sakshampan733-cloud/a-study-in-teak/assets/catalog/9116.jpg

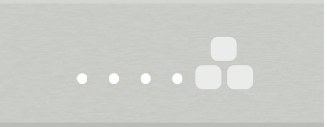
assets/catalog/9116.jpg
