sakshampan733-cloud/a-study-in-teak/assets/catalog/9126.jpg

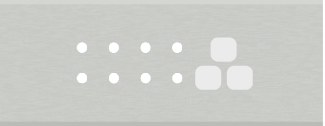
assets/catalog/9126.jpg
