sakshampan733-cloud/a-study-in-teak/assets/catalog/9148.jpg

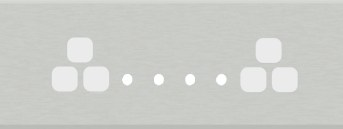
assets/catalog/9148.jpg
