sakshampan733-cloud/a-study-in-teak/assets/catalog/9156.jpg

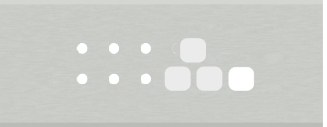
assets/catalog/9156.jpg
