sakshampan733-cloud/a-study-in-teak/assets/catalog/9188.jpg

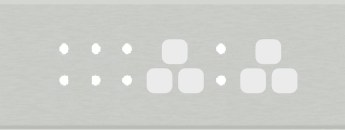
assets/catalog/9188.jpg
