sakshampan733-cloud/a-study-in-teak/assets/catalog/9198.jpg

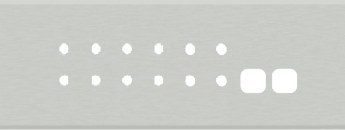
assets/catalog/9198.jpg
