sakshampan733-cloud/a-study-in-teak/assets/catalog/9212.jpg

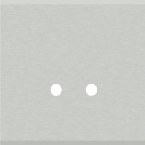
assets/catalog/9212.jpg
