sakshampan733-cloud/a-study-in-teak/assets/catalog/9323.jpg

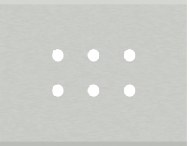
assets/catalog/9323.jpg
