sakshampan733-cloud/a-study-in-teak/assets/catalog/9424.jpg

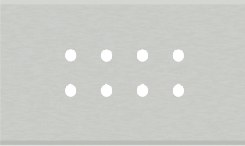
assets/catalog/9424.jpg
