sakshampan733-cloud/a-study-in-teak/assets/catalog/9818.jpg

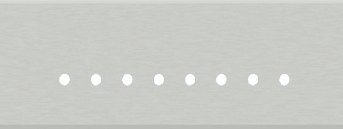
assets/catalog/9818.jpg
