sakshampan733-cloud/a-study-in-teak/assets/refs/moulding-ref-2-brownstone-head-detail.jpg

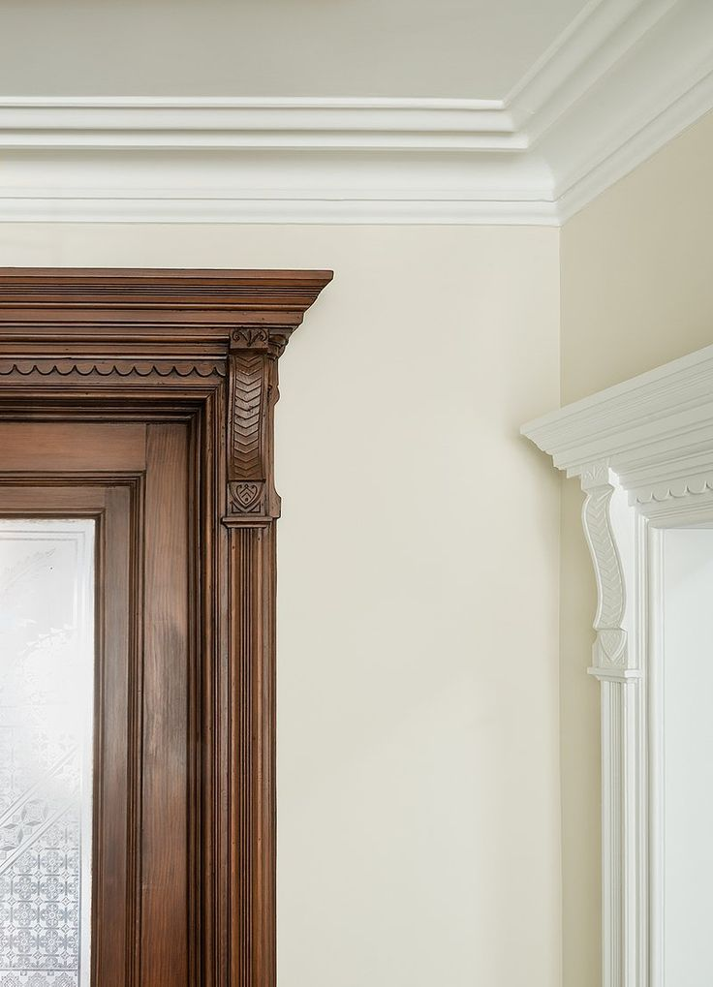
assets/refs/moulding-ref-2-brownstone-head-detail.jpg
