sakshampan733-cloud/a-study-in-teak/assets/refs/partition-ref-2-backlit-glass-grid-panels.jpg

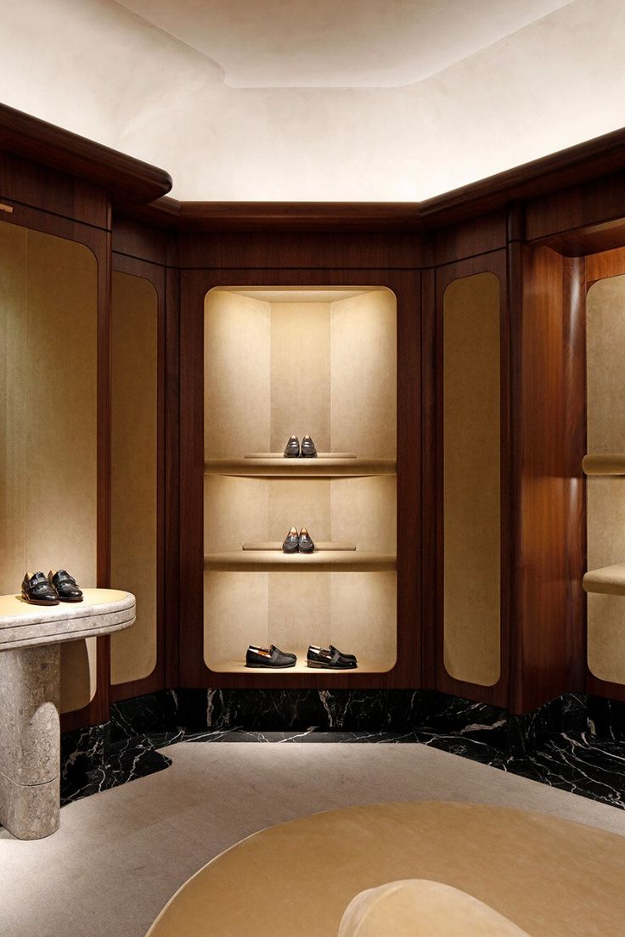
assets/refs/partition-ref-2-backlit-glass-grid-panels.jpg
