sakshampan733-cloud/a-study-in-teak/assets/refs/rightwall-iter-1-rail-2ft3.jpg

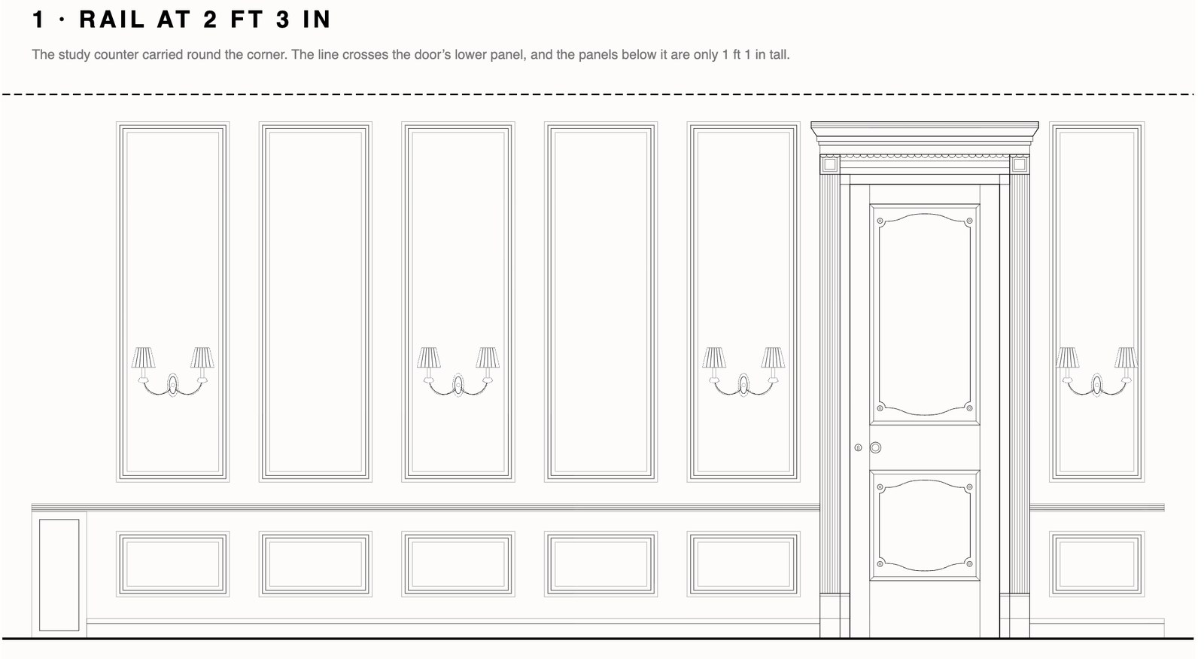
assets/refs/rightwall-iter-1-rail-2ft3.jpg
