sakshampan733-cloud/a-study-in-teak/assets/refs/veneer-9292-cream-burl.jpg

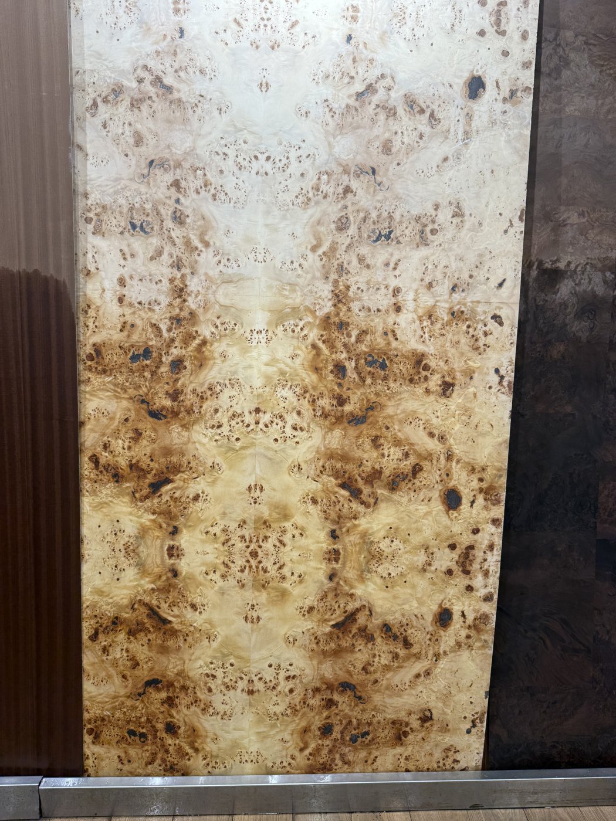
assets/refs/veneer-9292-cream-burl.jpg
