sakshampan733-cloud/a-study-in-teak/assets/refs/veneer-dark-diva-crown-OHBF-607-color-target.jpg

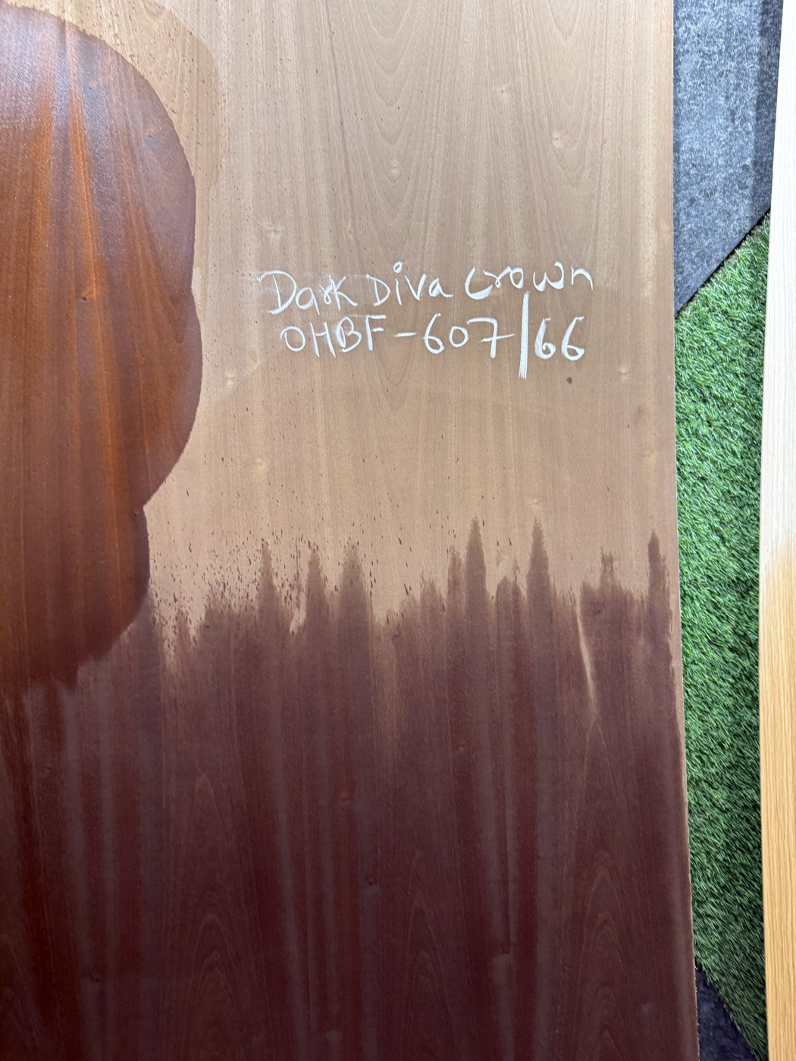
assets/refs/veneer-dark-diva-crown-OHBF-607-color-target.jpg
