sakshampan733-cloud/a-study-in-teak/assets/refs/veneer-ref-1-curved-walnut-gloss.jpg

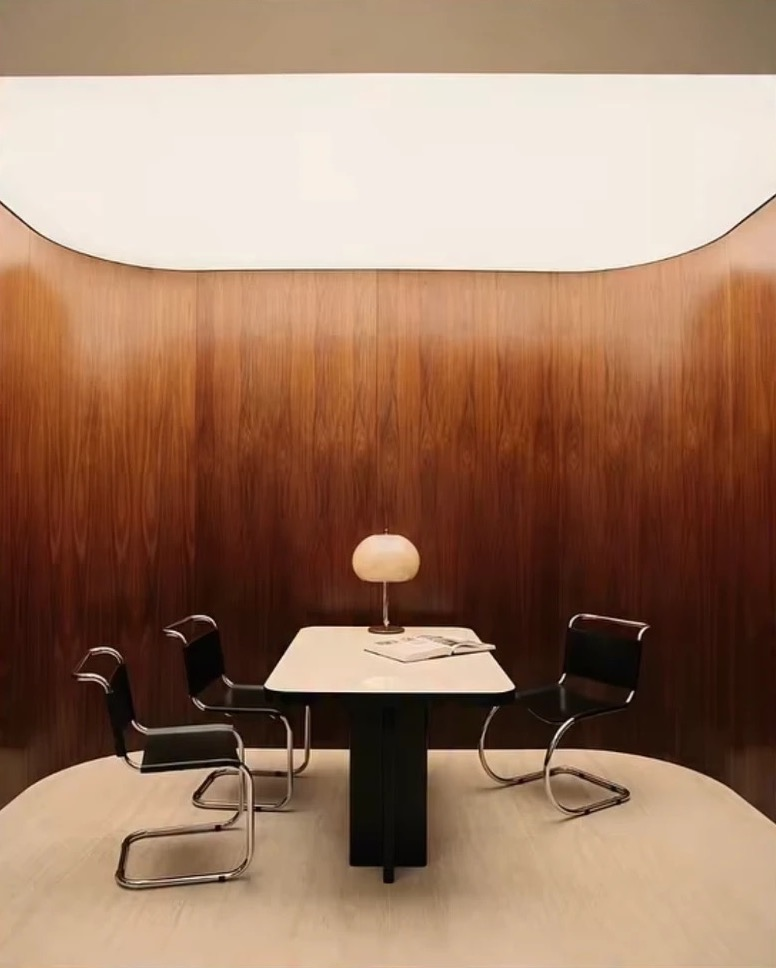
assets/refs/veneer-ref-1-curved-walnut-gloss.jpg
