sakshampan733-cloud/a-study-in-teak/assets/refs/wall-ref-1-library-pilasters.jpg

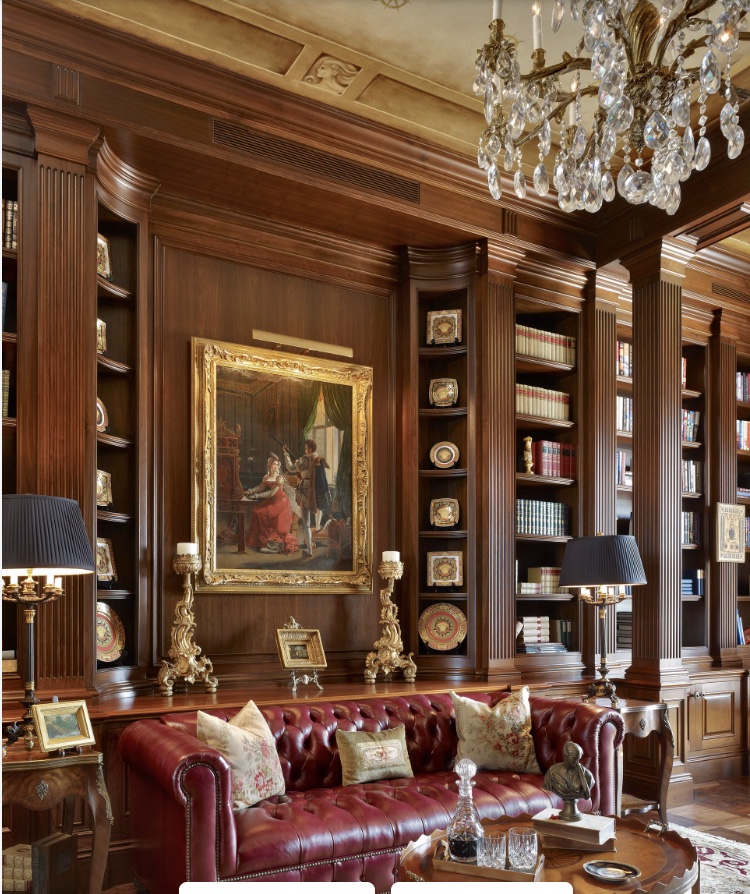
assets/refs/wall-ref-1-library-pilasters.jpg
