sakshampan733-cloud/a-study-in-teak/assets/refs/wall-ref-2-cornice-closeup.jpg

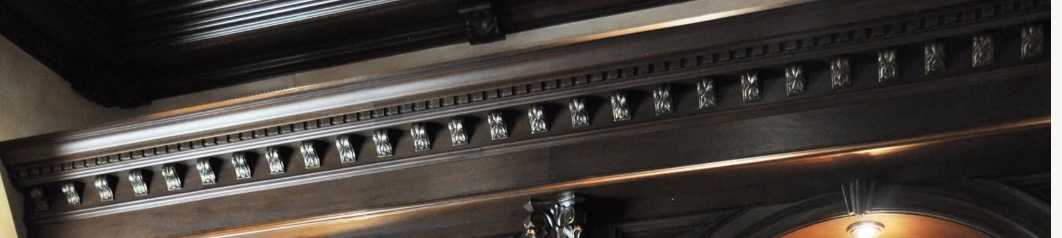
assets/refs/wall-ref-2-cornice-closeup.jpg
