sakshampan733-cloud/a-study-in-teak/assets/refs/wall-ref-3-arched-bookcases.jpg

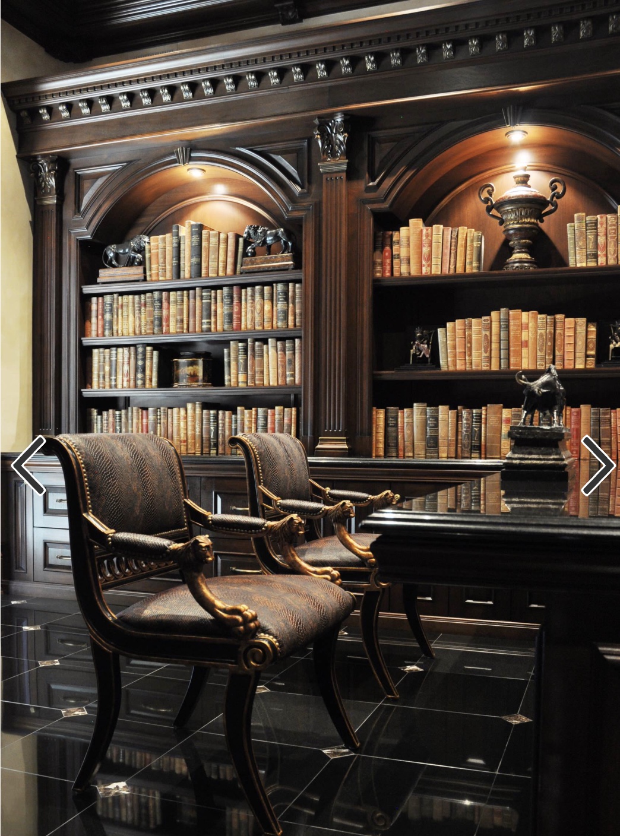
assets/refs/wall-ref-3-arched-bookcases.jpg
