sakshampan733-cloud/a-study-in-teak/assets/refs/wall-ref-4-dark-study-bands-sconces.jpg

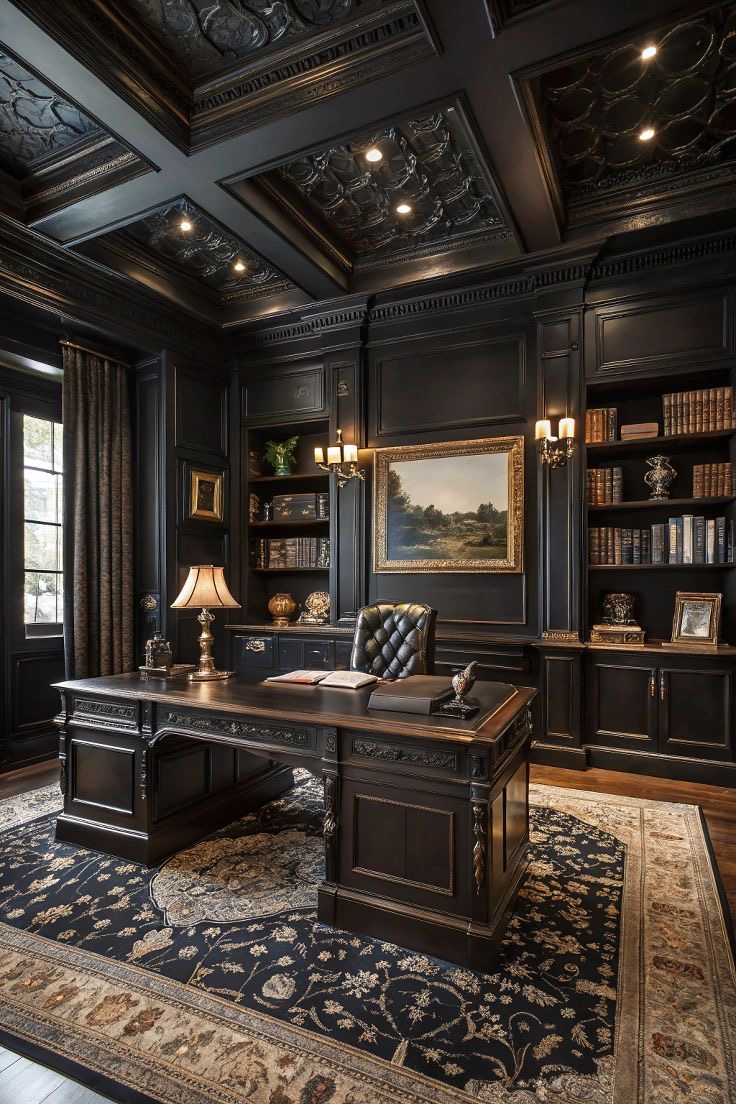
assets/refs/wall-ref-4-dark-study-bands-sconces.jpg
