sakshampan733-cloud/a-study-in-teak/assets/refs/wardrobe-ref-2-steel-leaded-doors-wide.jpg

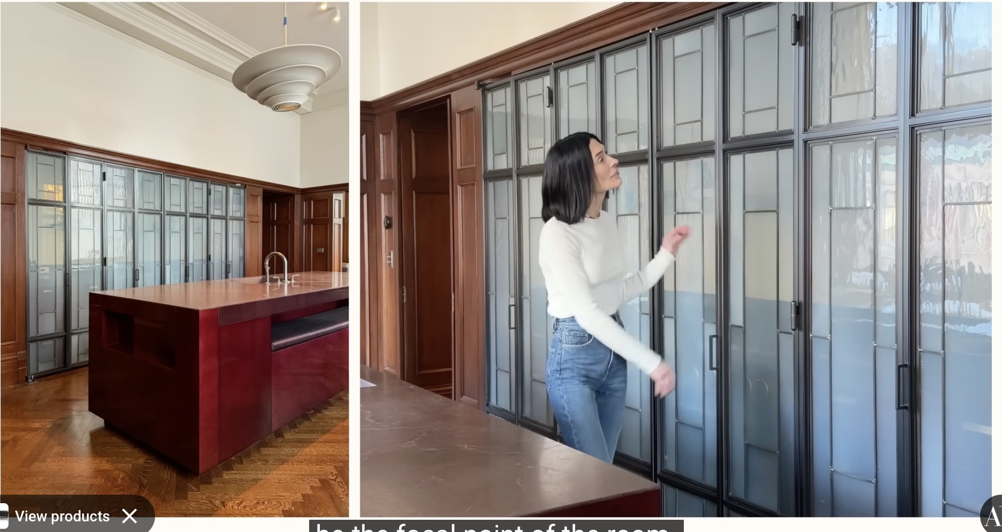
assets/refs/wardrobe-ref-2-steel-leaded-doors-wide.jpg
