sakshampan733-cloud/a-study-in-teak/assets/refs/wardrobe-ref-4-inside-finish-lit-niche.jpg

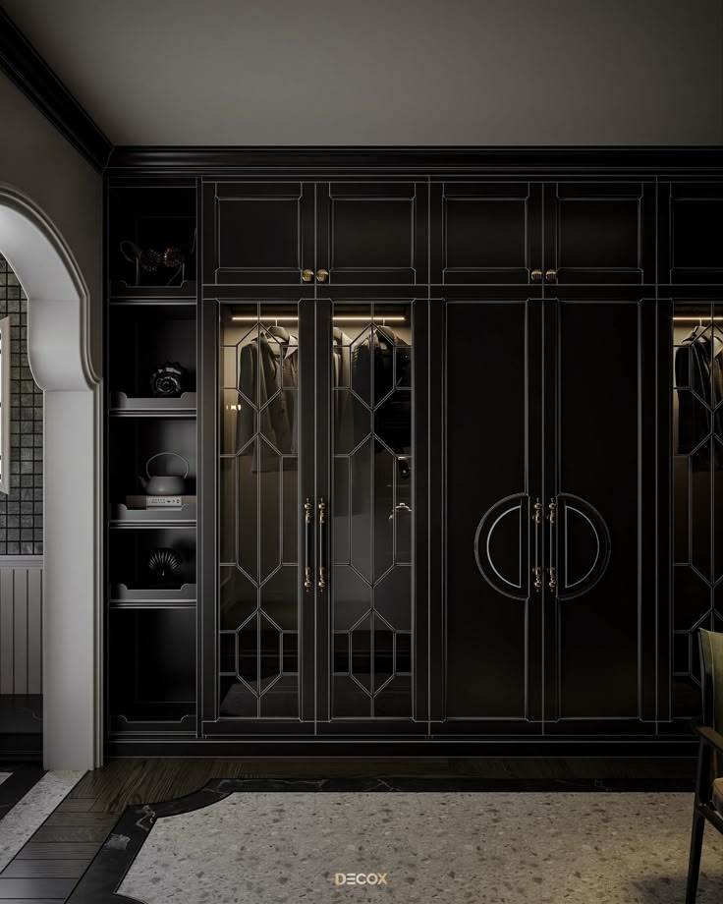
assets/refs/wardrobe-ref-4-inside-finish-lit-niche.jpg
