sakshampan733-cloud/a-study-in-teak/assets/renders/b_cove.jpg

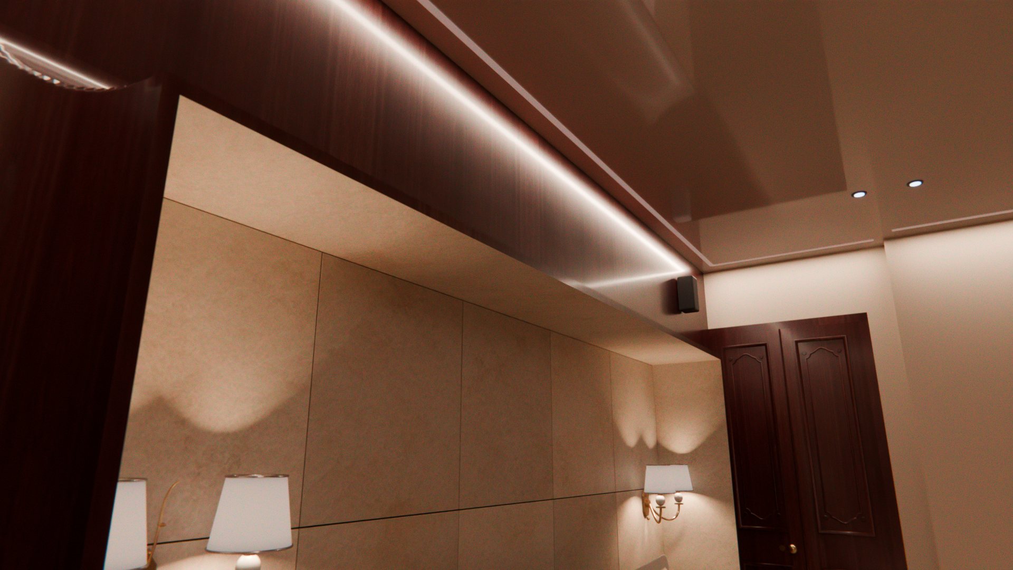
assets/renders/b_cove.jpg
