sakshampan733-cloud/a-study-in-teak/assets/renders/h_wardrobe.jpg

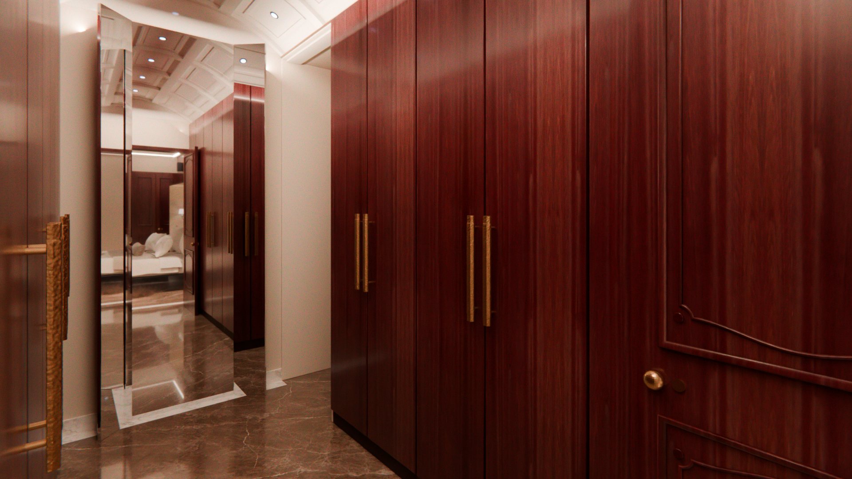
assets/renders/h_wardrobe.jpg
