sakshampan733-cloud/a-study-in-teak/assets/renders/r_desk.jpg

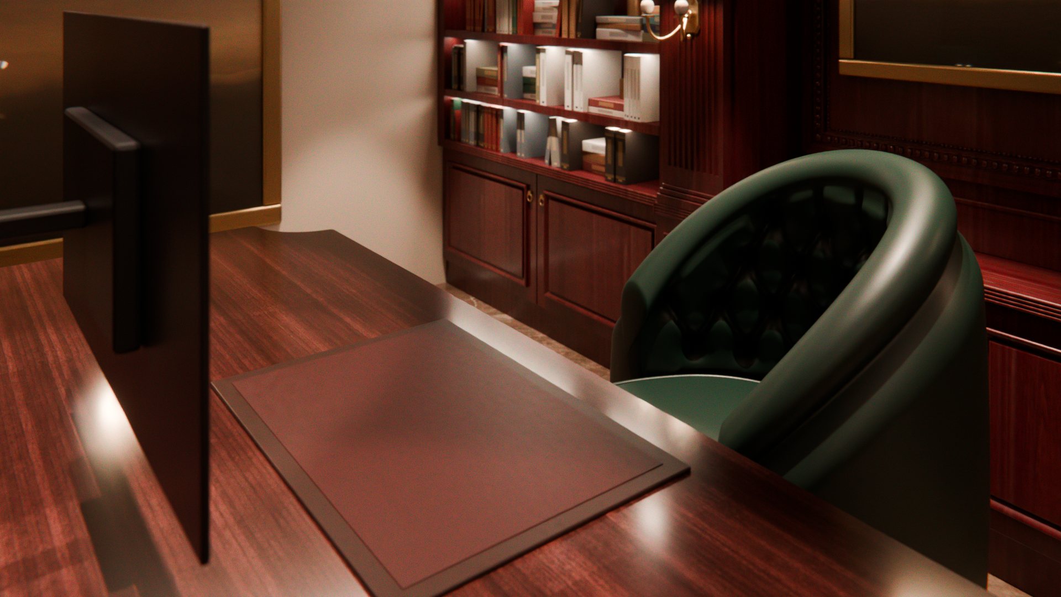
assets/renders/r_desk.jpg
