sakshampan733-cloud/a-study-in-teak/assets/renders/st_chair.jpg

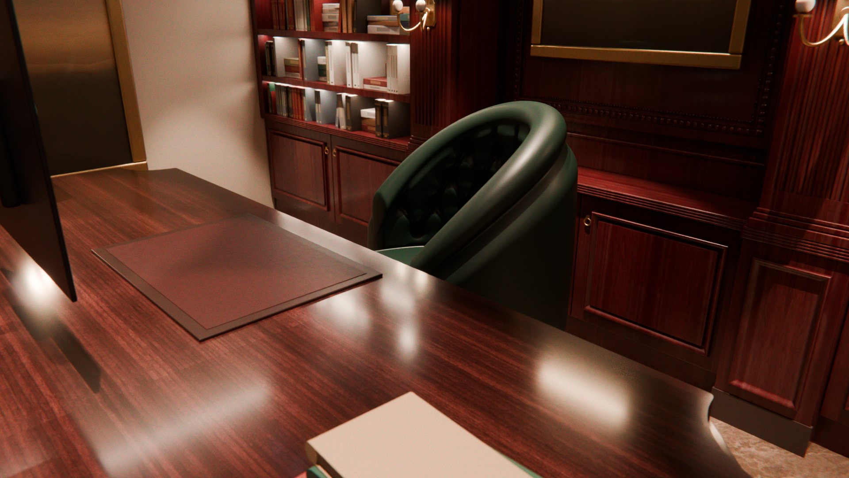
assets/renders/st_chair.jpg
