sakshampan733-cloud/a-study-in-teak/assets/renders/st_lamp.jpg

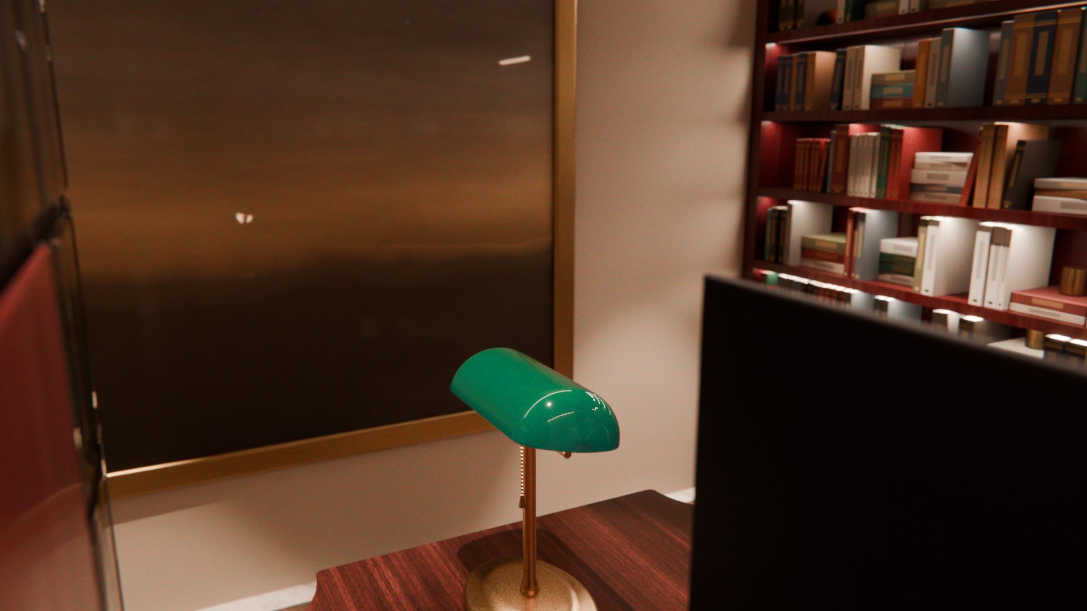
assets/renders/st_lamp.jpg
