sakshampan733-cloud/a-study-in-teak/assets/renders/st_wall.jpg

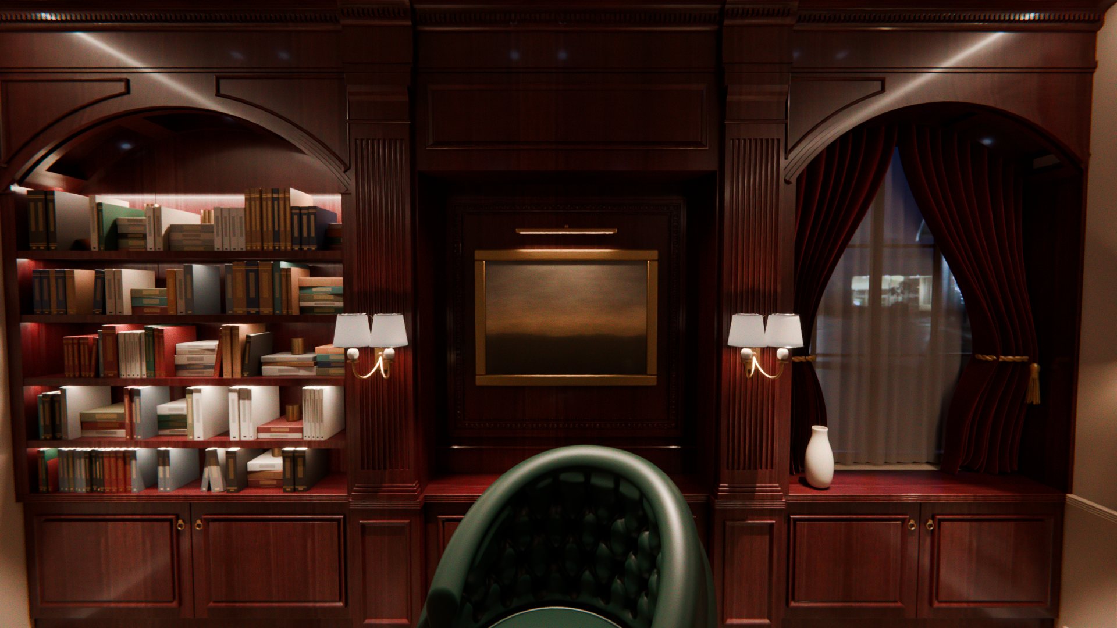
assets/renders/st_wall.jpg
