sakshampan733-cloud/a-study-in-teak/assets/renders/window.jpg

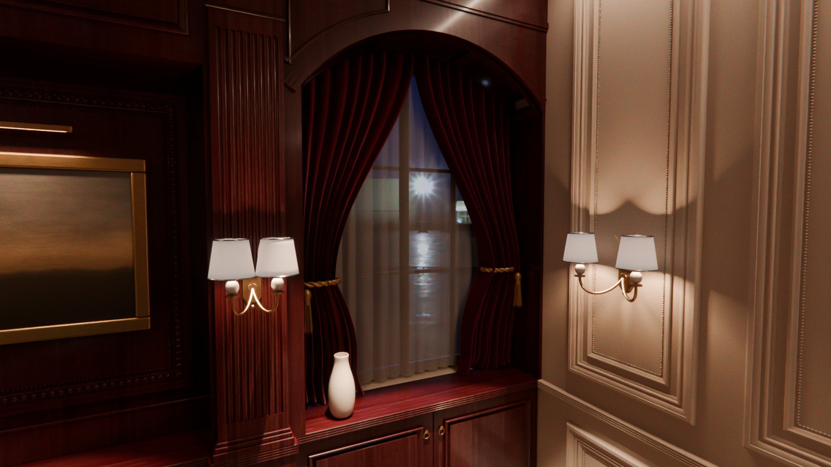
assets/renders/window.jpg
