sakshampan733-cloud/a-study-in-teak/assets/video/dressing-endbay-foldin.jpg

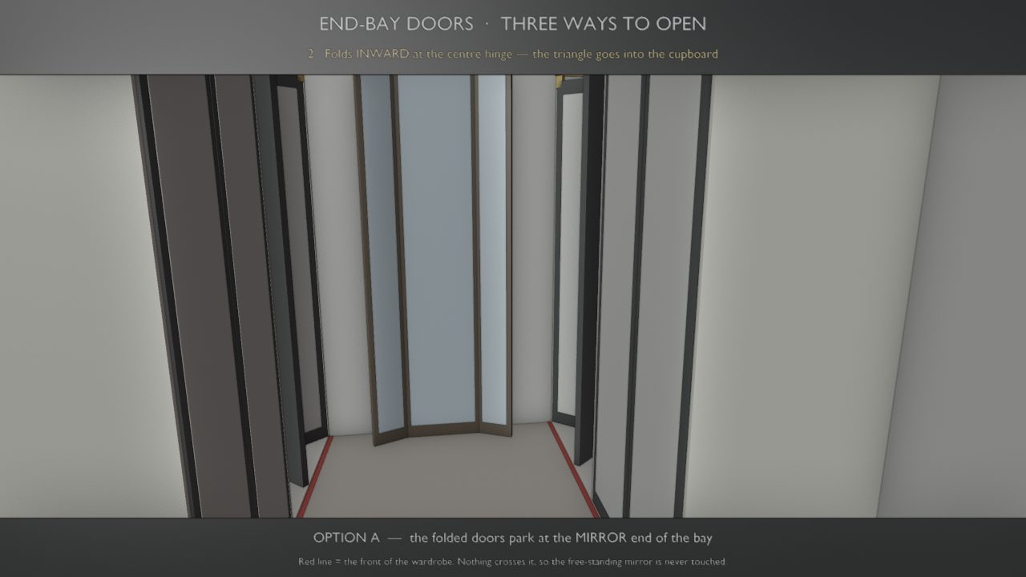
assets/video/dressing-endbay-foldin.jpg
