sakshampan733-cloud/a-study-in-teak/v2/media/blur/desk-ref-1.jpg

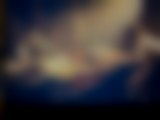
v2/media/blur/desk-ref-1.jpg
