sakshampan733-cloud/a-study-in-teak/cad/partitionglass-model.dxf

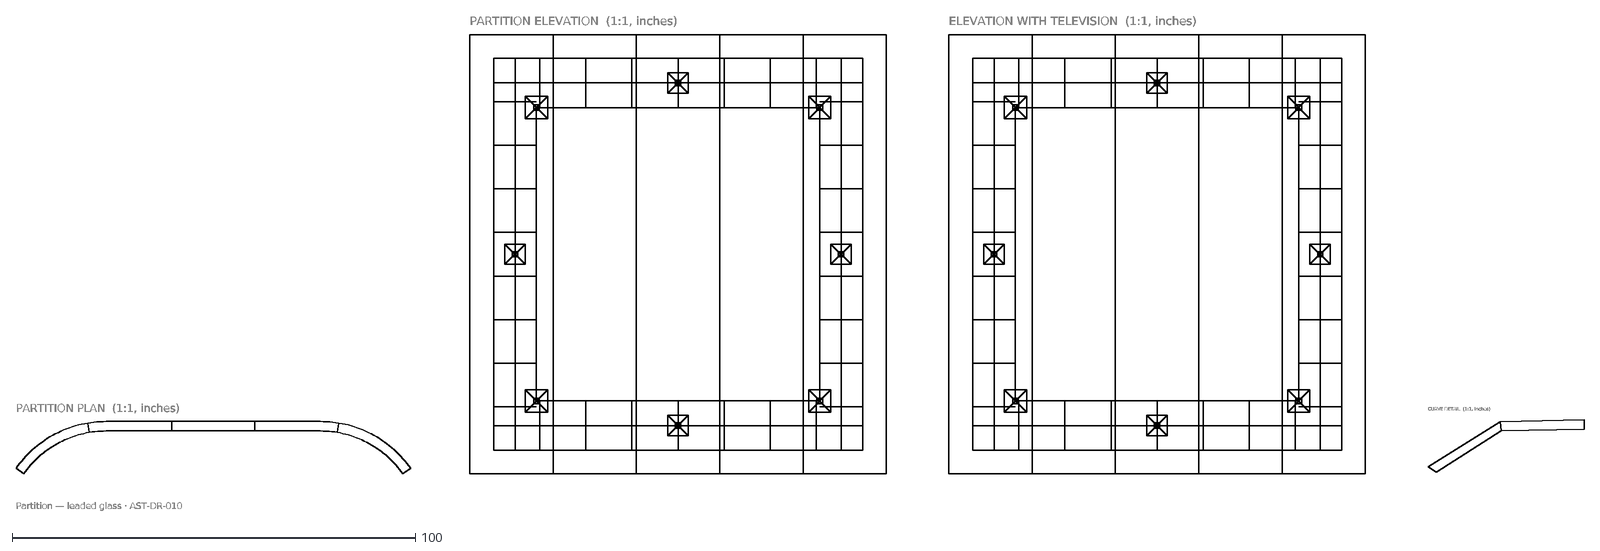
[picture p43: CAD file, 2026-10-09]
cad/partitionglass-model.dxf
PARTITION PLAN (1:1, inches)
PARTITION ELEVATION (1:1, inches)
ELEVATION WITH TELEVISION (1:1, inches)
CURVE DETAIL (1:1, inches)
Partition — leaded glass · AST-DR-010
