sakshampan733-cloud/a-study-in-teak/cad/bathroom-model.dxf

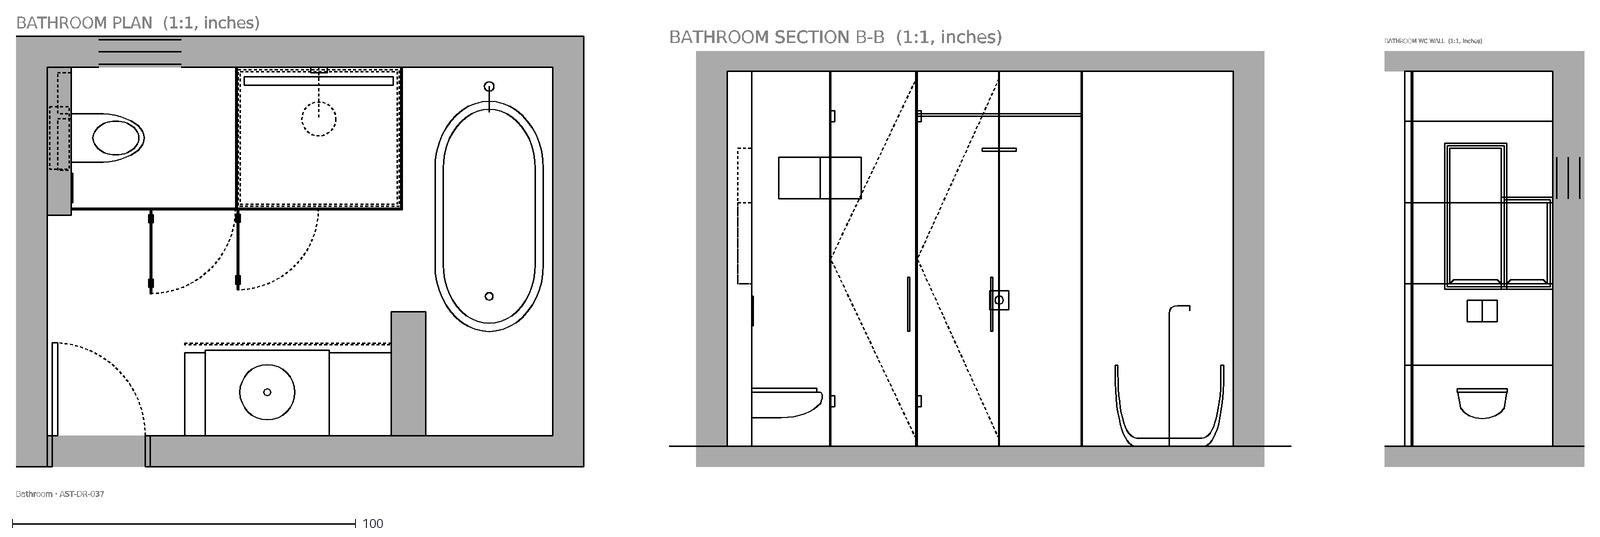
[picture p44: CAD file, 2026-10-09]
cad/bathroom-model.dxf
BATHROOM PLAN (1:1, inches)
BATHROOM SECTION B-B (1:1, inches)
BATHROOM WC WALL (1:1, inches)
Bathroom · AST-DR-037
