sakshampan733-cloud/a-study-in-teak/cad/roomshell-model.dxf

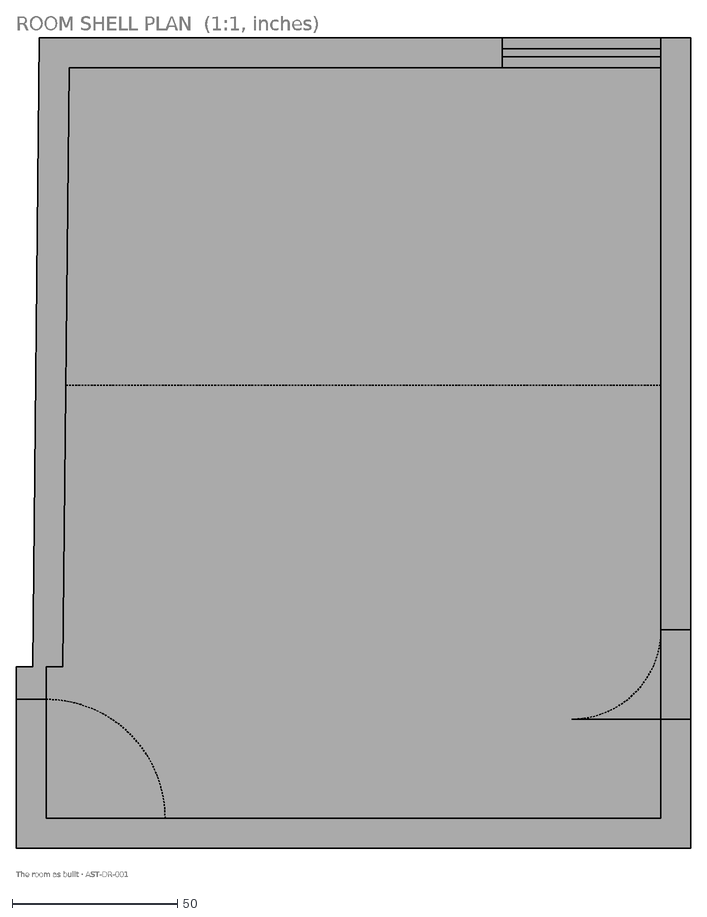
[picture p45: CAD file, 2026-10-09]
cad/roomshell-model.dxf
ROOM SHELL PLAN (1:1, inches)
The room as built · AST-DR-001
