sakshampan733-cloud/a-study-in-teak/cad/studywall-model.dxf

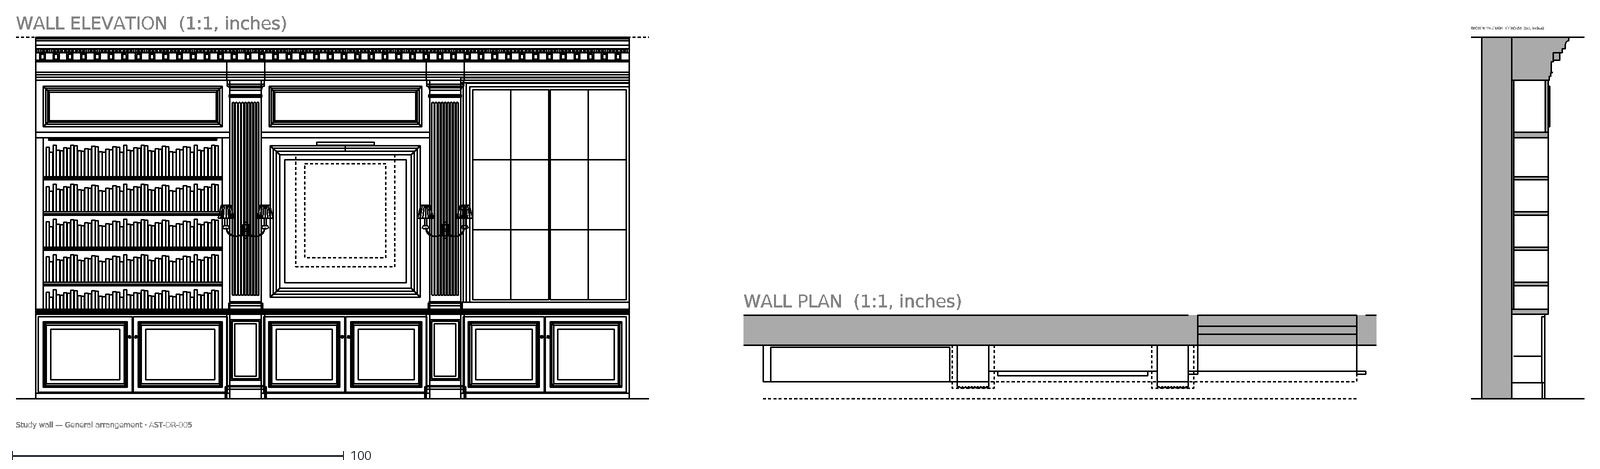
[picture p46: CAD file, 2026-10-09]
cad/studywall-model.dxf
WALL ELEVATION (1:1, inches)
WALL PLAN (1:1, inches)
SECTION THROUGH BOOKCASE (1:1, inches)
Study wall — General arrangement · AST-DR-005
