sakshampan733-cloud/a-study-in-teak/cad/bed-model.dxf

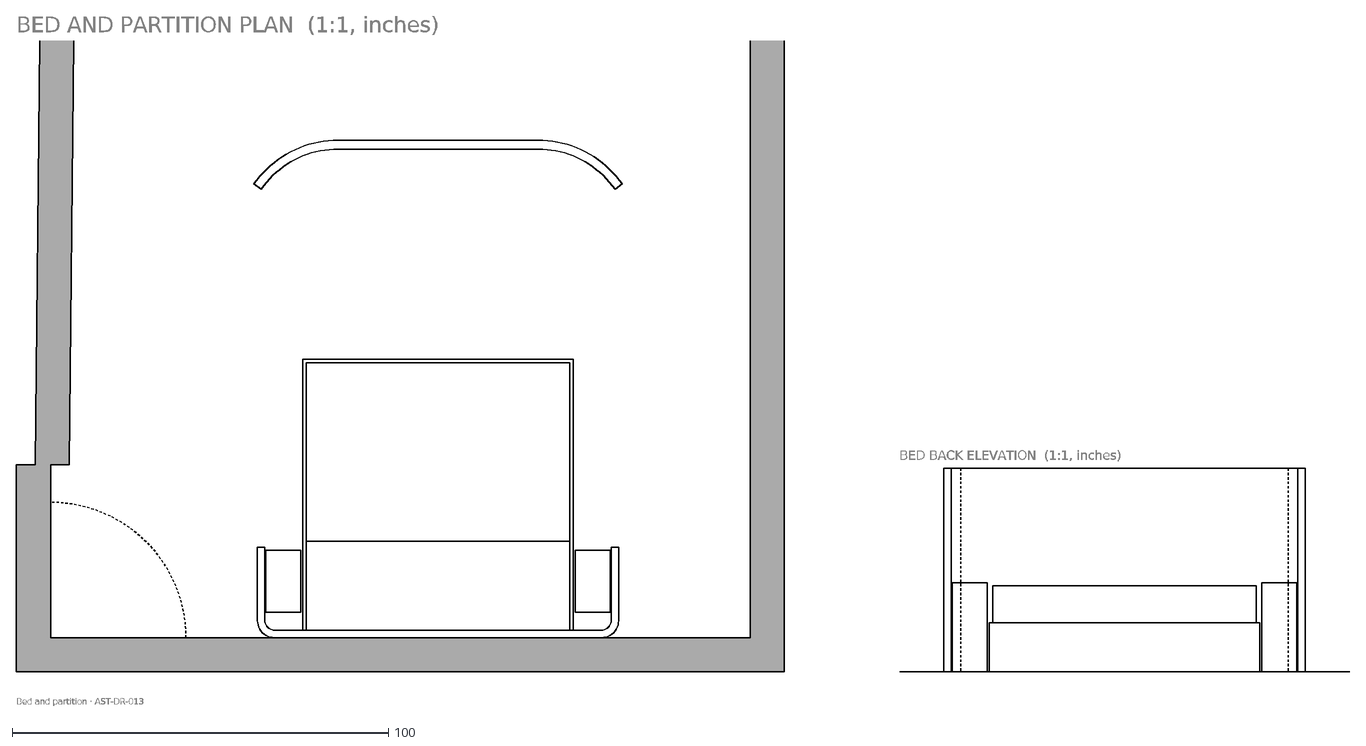
[picture p47: CAD file, 2026-10-09]
cad/bed-model.dxf
BED AND PARTITION PLAN (1:1, inches)
BED BACK ELEVATION (1:1, inches)
Bed and partition · AST-DR-013
