sakshampan733-cloud/a-study-in-teak/cad/leftwall-model.dxf

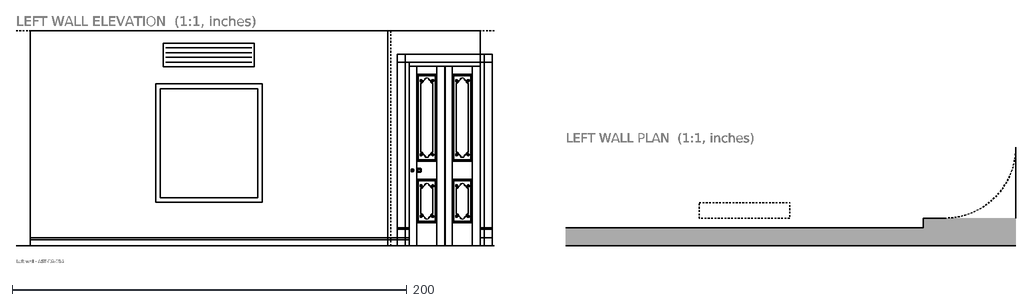
[picture p48: CAD file, 2026-10-09]
cad/leftwall-model.dxf
LEFT WALL ELEVATION (1:1, inches)
LEFT WALL PLAN (1:1, inches)
Left wall · AST-DR-014
