sakshampan733-cloud/a-study-in-teak/cad/desk-square-model.dxf

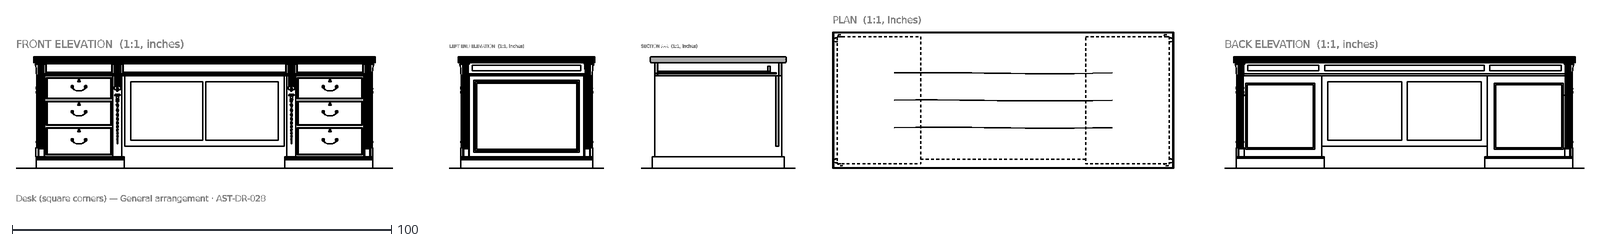
[picture p49: CAD file, 2026-10-09]
cad/desk-square-model.dxf
FRONT ELEVATION (1:1, inches)
LEFT END ELEVATION (1:1, inches)
SECTION A-A (1:1, inches)
PLAN (1:1, inches)
BACK ELEVATION (1:1, inches)
Desk (square corners) — General arrangement · AST-DR-028
