sakshampan733-cloud/a-study-in-teak/cad/desk-plain-model.dxf

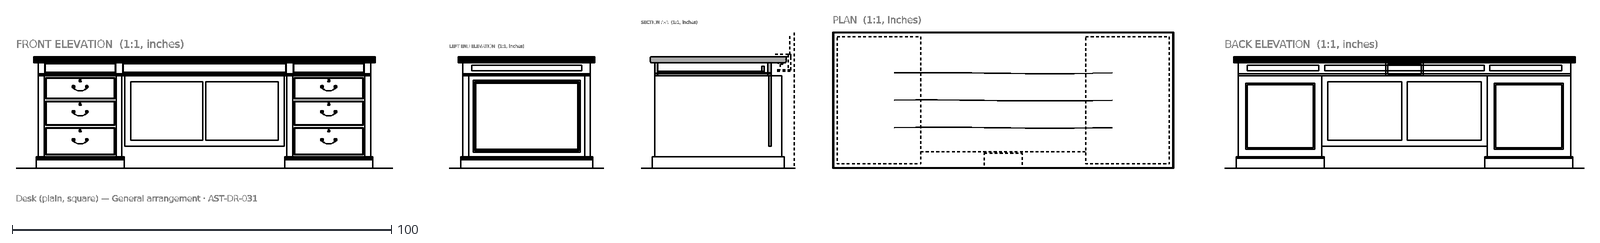
[picture p50: CAD file, 2026-10-09]
cad/desk-plain-model.dxf
FRONT ELEVATION (1:1, inches)
LEFT END ELEVATION (1:1, inches)
SECTION A-A (1:1, inches)
PLAN (1:1, inches)
BACK ELEVATION (1:1, inches)
Desk (plain, square) — General arrangement · AST-DR-031
