sakshampan733-cloud/a-study-in-teak/cad/sharedwall-model.dxf

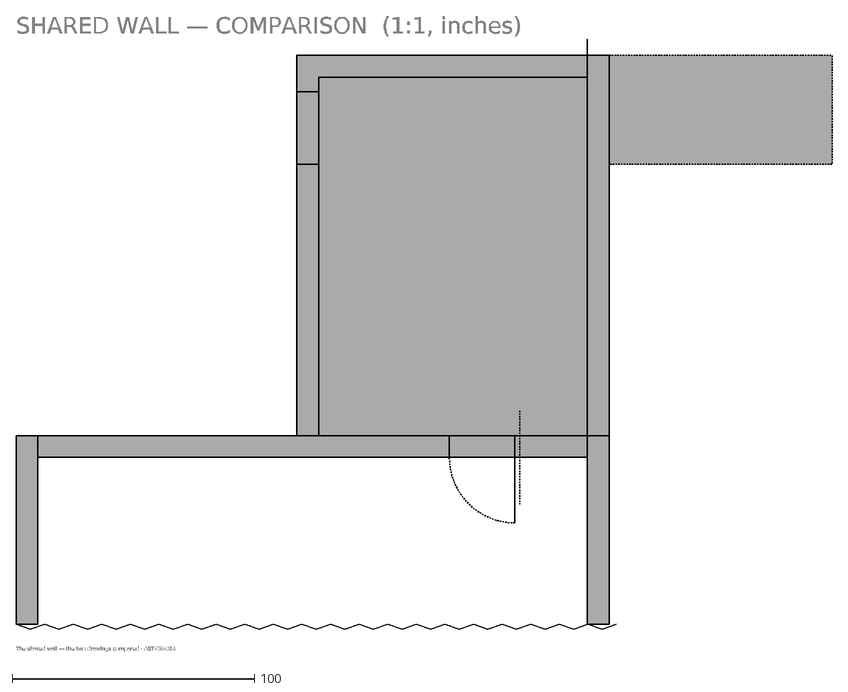
[picture p51: CAD file, 2026-10-09]
cad/sharedwall-model.dxf
SHARED WALL — COMPARISON (1:1, inches)
The shared wall — the two drawings compared · AST-DR-024
