sakshampan733-cloud/a-study-in-teak/cad/wardrobes-model.dxf

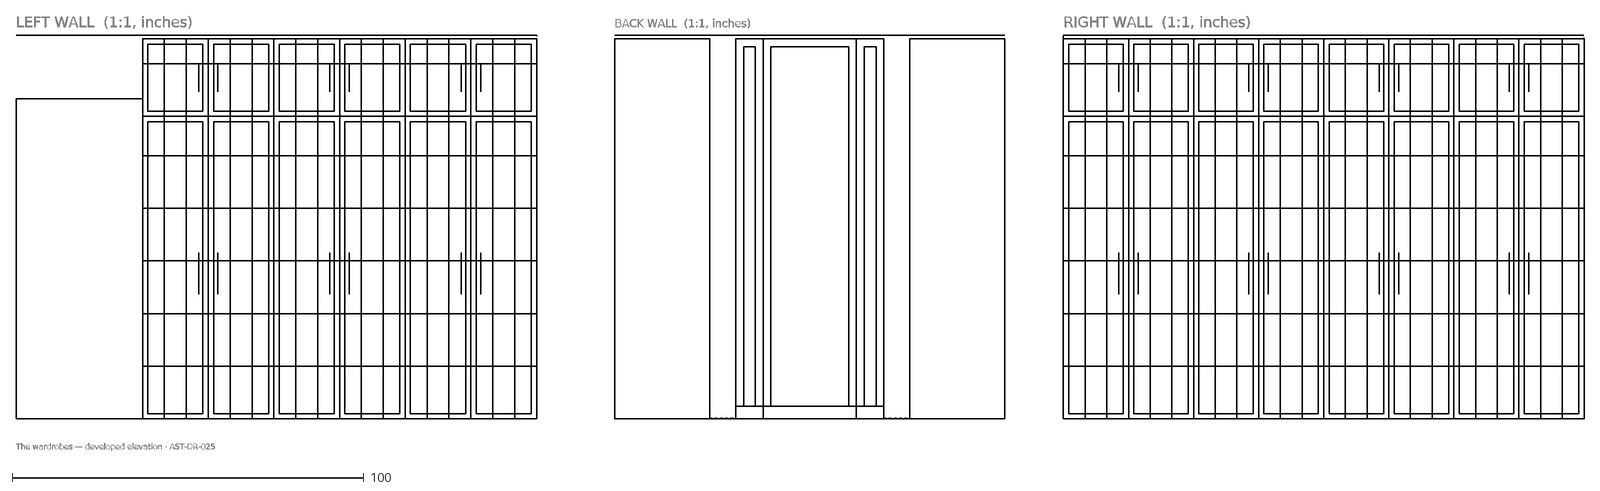
[picture p52: CAD file, 2026-10-09]
cad/wardrobes-model.dxf
LEFT WALL (1:1, inches)
BACK WALL (1:1, inches)
RIGHT WALL (1:1, inches)
The wardrobes — developed elevation · AST-DR-025
