sakshampan733-cloud/a-study-in-teak/cad/desk-model.dxf

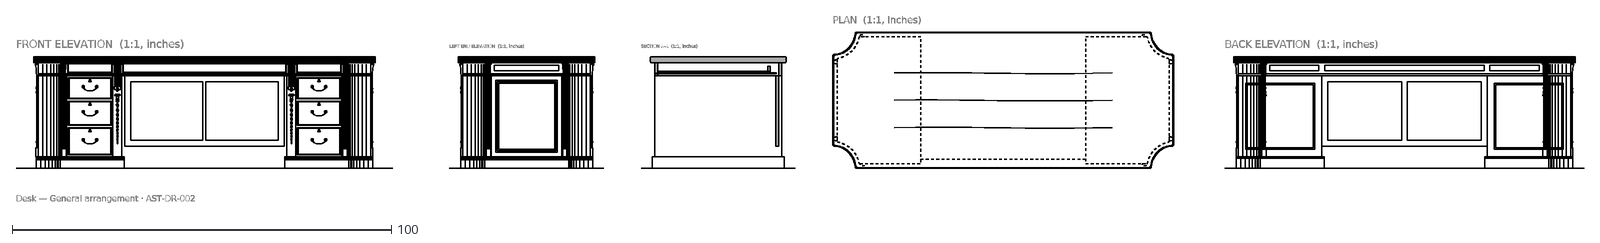
[picture p53: CAD file, 2026-10-09]
cad/desk-model.dxf
FRONT ELEVATION (1:1, inches)
LEFT END ELEVATION (1:1, inches)
SECTION A-A (1:1, inches)
PLAN (1:1, inches)
BACK ELEVATION (1:1, inches)
Desk — General arrangement · AST-DR-002
