sakshampan733-cloud/a-study-in-teak/cad/bedframe-model.dxf

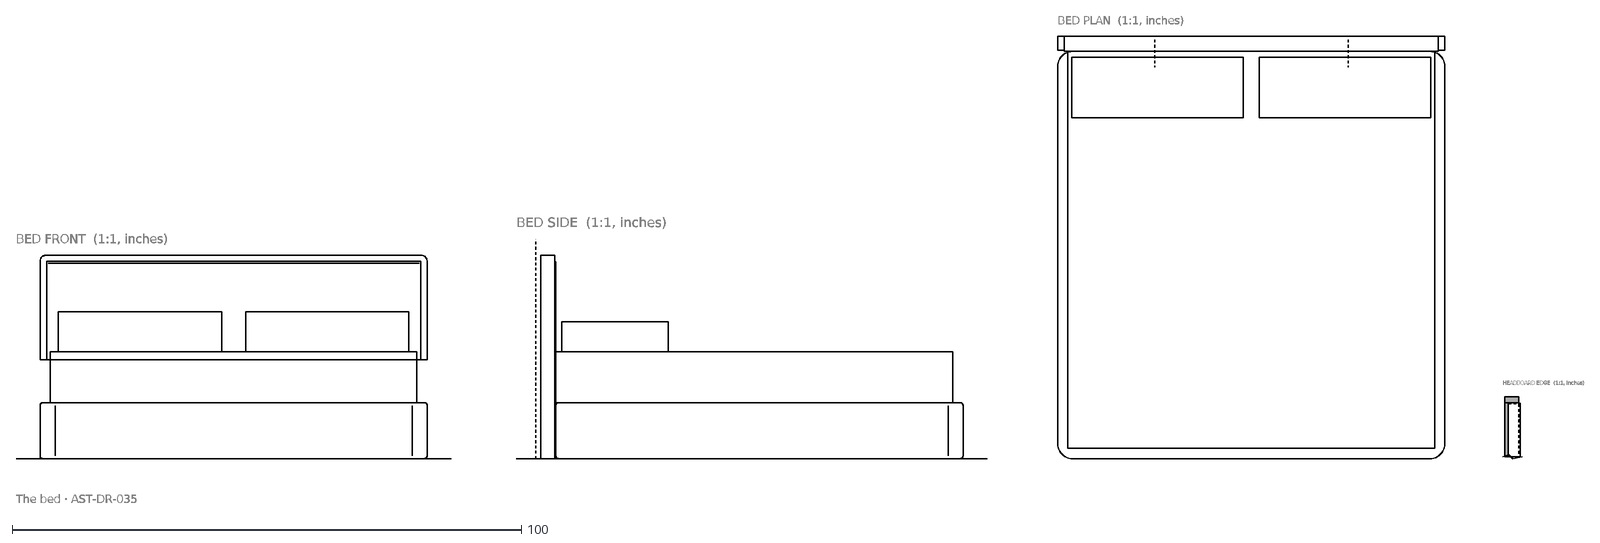
[picture p54: CAD file, 2026-10-09]
cad/bedframe-model.dxf
BED FRONT (1:1, inches)
BED SIDE (1:1, inches)
BED PLAN (1:1, inches)
HEADBOARD EDGE (1:1, inches)
The bed · AST-DR-035
