sakshampan733-cloud/a-study-in-teak/cad/print/vanity-c-a4.pdf

FRONT

FINAL · 1 FT 6 LEFT, 6 IN RIGHT · 3 FT MARBLE BANK ON THE FAUCET · THE ROW WALL-HUNG 6 IN OFF THE FLOOR, A DRAIN BELOW

SECTION A–A

ON THE FAUCET AXIS

2'-1" DEEP

1'-6" 2⅜"
A

B

C

E

F

G

DETAIL 2 · THE BIG DRAWER

PLAN · INNER DRAWER DASHED

7⅞"

9⅜"

DETAIL 1 · THE MARBLE EDGE

SECTION · ONE MITRED CORNER, FRONTS FLUSH

¾" ¾"

1½"

3" STRIP

MARBLE SLAB ¾", MITRED

BWP PLY SUB-TOP ¾"

FIXED MARBLE STRIP ¾" × 3"

CARCASS TOP ¾"

TOP DRAWER, FLUSH

FRONTS

SIZES ARE THE FRONT ITSELF · ⅛" GAP ALL ROUND

No. | WHAT | W × H | FT-IN
1 | Pull-out cabinet, cup pull | 1'-2¾" × 1'-10¼" | 1'-2¾" × 1'-10¼"
2 | Pull-out cabinet, cup pull | 4¼" × 1'-10¼" | 4¼" × 1'-10¼"
3 | Top drawer, push-open · marble | 1'-3¾" × 6½" | 1'-3¾" × 6½"
4 | Top drawer, push-open · marble | 1'-3¾" × 6½" | 1'-3¾" × 6½"
5 | Big drawer, U-box, push-open · marble | 2'-8¾" × 1'-2⅝" | 2'-8¾" × 1'-2⅝"
5a | Inner drawer, finger scoop | 2'-6½" × 4¼" | 2'-6½" × 4¼"

MATERIALS

THE ROOM'S PALETTE — NOTHING NEW

Top | Beige-gold marble, the bathroom stone. ¾" slab
| on a ¾" BWP sub-top, mitred at the front edge into
| a fixed ¾" marble strip: one corner, fronts flush.
Bank | The same beige marble on the face frame and on
| every drawer front, bonded to BWP boxes. It stops
| 6 in off the floor, level with the ends: a drain below.
Ends | Two pull-out cabinets, 9292 burl veneer, polished
| dark and red (the owner's photo), gloss, edges sealed.
Hanging | ¾" ply cleat 2'-3½"–2'-5⅞" and concealed steel brackets
| into the wall: the stone is heavy. Nothing on the floor.
Ledges | The two veneer tops: solid nosing, sealed.
Runners | Drawers: undermount, push-to-open. Pull-outs:
| heavy full-extension runners, cup pull.
Fittings | Chrome — already bought.

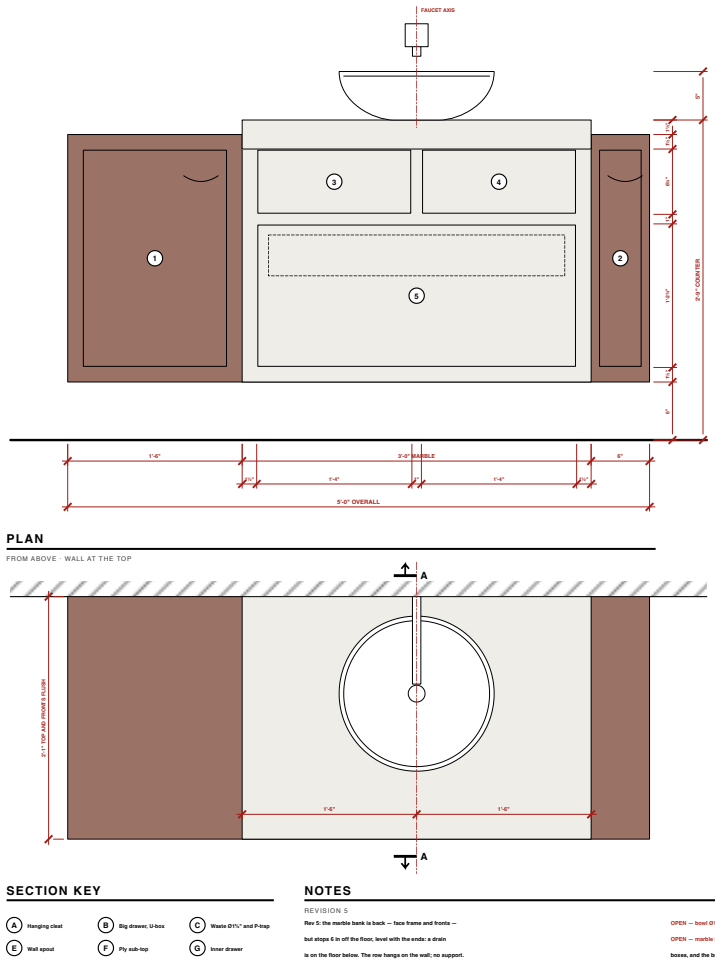
[picture p128: figure]
3'-0" MARBLE; 5'-0" OVERALL; 2'-9" COUNTER 5"; FAUCET AXIS; PLAN; FROM ABOVE · WALL AT THE TOP; 2'-1" TOP AND FRONTS FLUSH; SECTION KEY; Hanging cleat; Big drawer, U-box; Waste Ø1⅝" and P-trap; Wall spout; Ply sub-top; Inner drawer; NOTES; REVISION 5

Rev 5: the marble bank is back — face frame and fronts —

but stops 6 in off the floor, level with the ends: a drain

is on the floor below. The row hangs on the wall; no support.

Top drawers 6½ in; the big drawer 14½ in, a 4 in inner one.

OPEN — bowl Ø1'-4" × 5" and the spout are assumed.

OPEN — marble front thickness and its bond to the drawer

boxes, and the brackets' size: stone supplier to confirm.

Rev 3: top and front meet in one mitred corner, flush.

A S T U D Y I N T E A K

Particulars of the room

VANITY — SCHEME C

Final · marble bank and top · dark red burl pull-outs · wall-hung, 6 in clear

SCALE

AS NOTED @ A3

DATE

08.10.2026

REV

5 — marble bank 6 in off the floor (a drain below), wall-hung; ends in dark red burl

DWG

AST-DR-021

PROJECT

# A Study in Teak — Vanity — Scheme C

SHEET

# General arrangement — the whole sheet

each view follows at its own scale, pages 2 to 10

SCALE

# NTS

DATE
08.10.2026

REV

DRAWING

# AST-DR-021 · 1 of 10

ALL DIMENSIONS IN FEET & INCHES. PRINT ON A4 AT 100% / “ACTUAL SIZE” — NOT “FIT TO PAGE” — AND CHECK THE SCALE BAR. DO NOT SCALE; WORK TO FIGURED DIMENSIONS. VERIFY ON SITE.

## FRONT

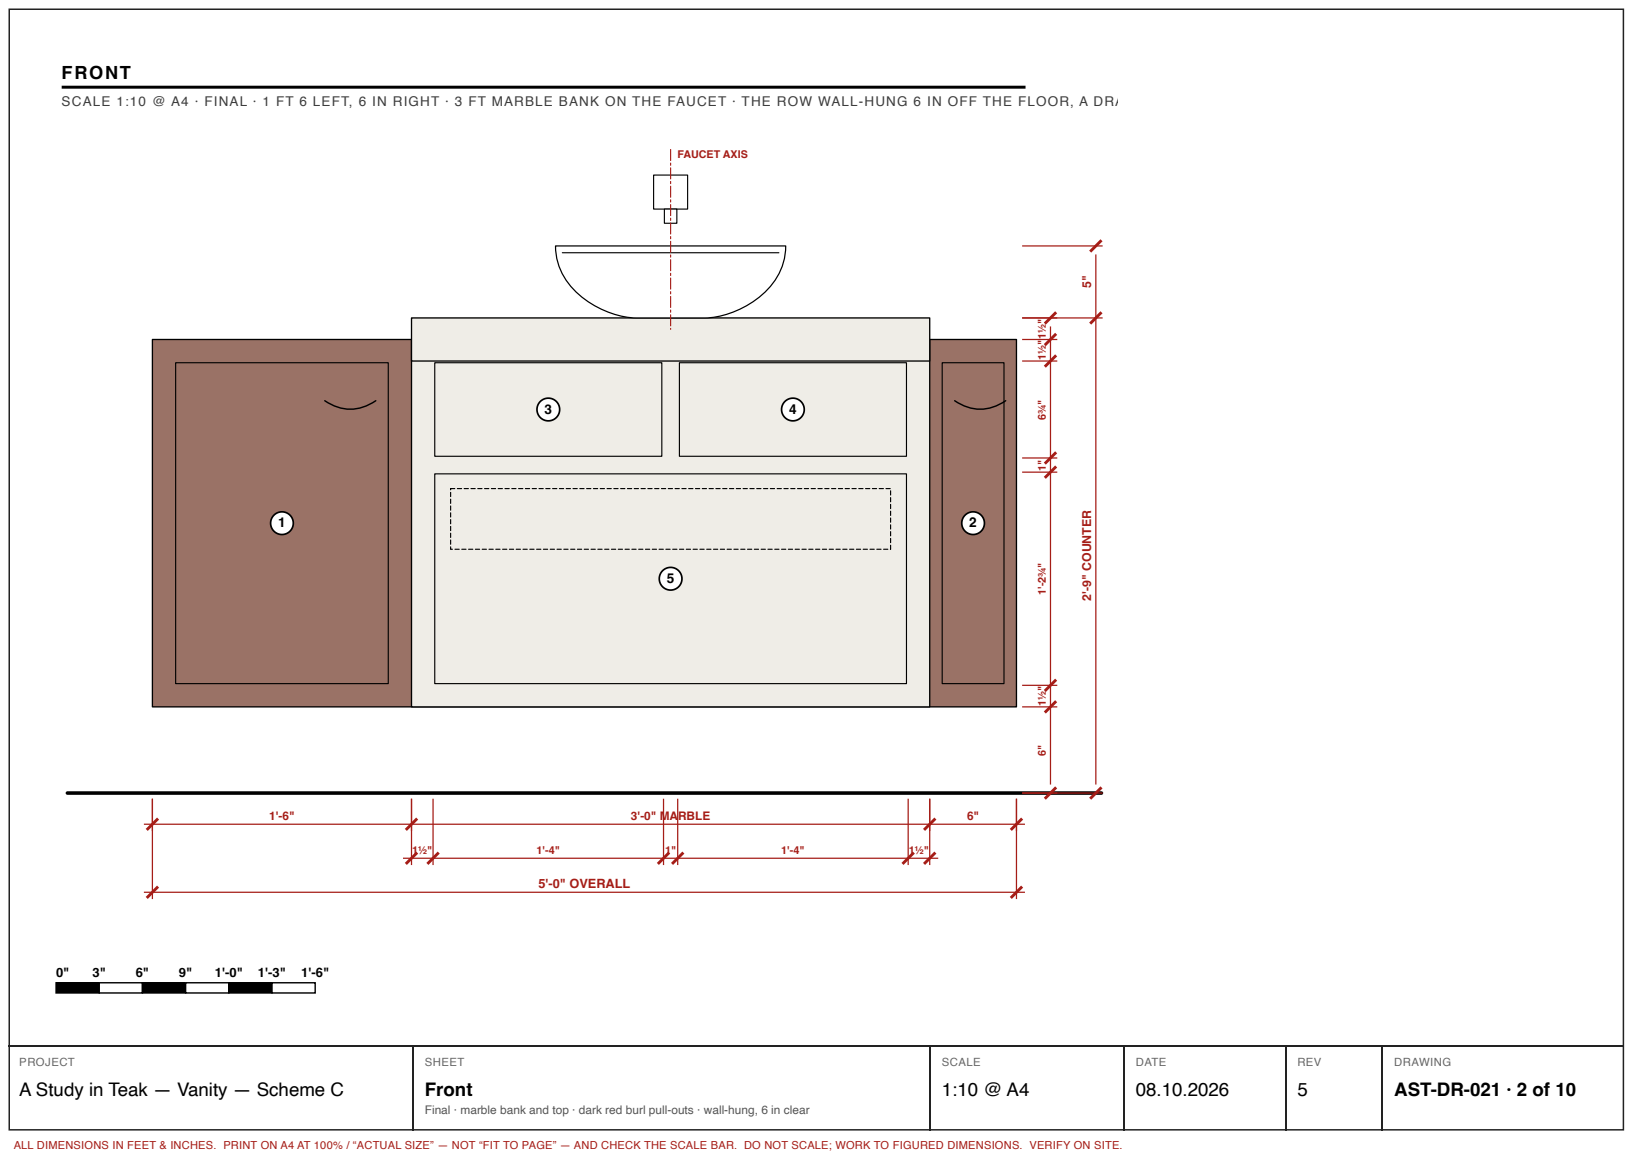
[picture p129: page 2]
3'-0" MARBLE; 5'-0" OVERALL; 2'-9" COUNTER 5"; FAUCET AXIS; Front

SCALE 1:10 @ A4 · FINAL · 1 FT 6 LEFT, 6 IN RIGHT · 3 FT MARBLE BANK ON THE FAUCET · THE ROW WALL-HUNG 6 IN OFF THE FLOOR, A DRA

AST-DR-021 · 2 of 10

Final · marble bank and top · dark red burl pull-outs · wall-hung, 6 in clear

## SECTION A–A

E

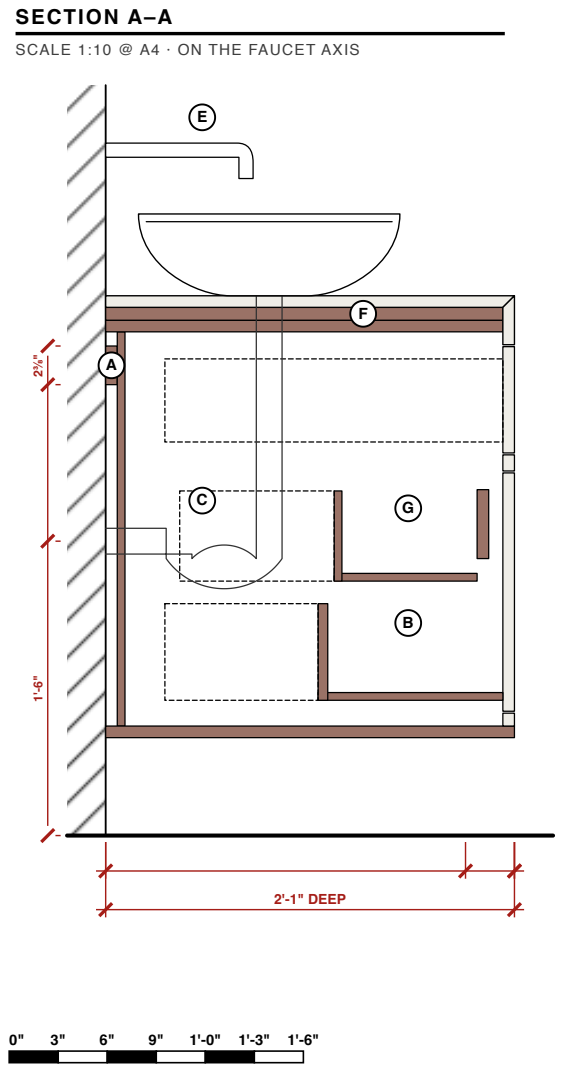
[picture p130: page 3]
2'-1" DEEP; Section A–A

SCALE 1:10 @ A4 · ON THE FAUCET AXIS

AST-DR-021 · 3 of 10

# DETAIL 1 · THE MARBLE EDGE

# SCALE 1:1 (FULL SIZE) @ A4 · SECTION · ONE MITRED CORNER, FRONTS FLUSH

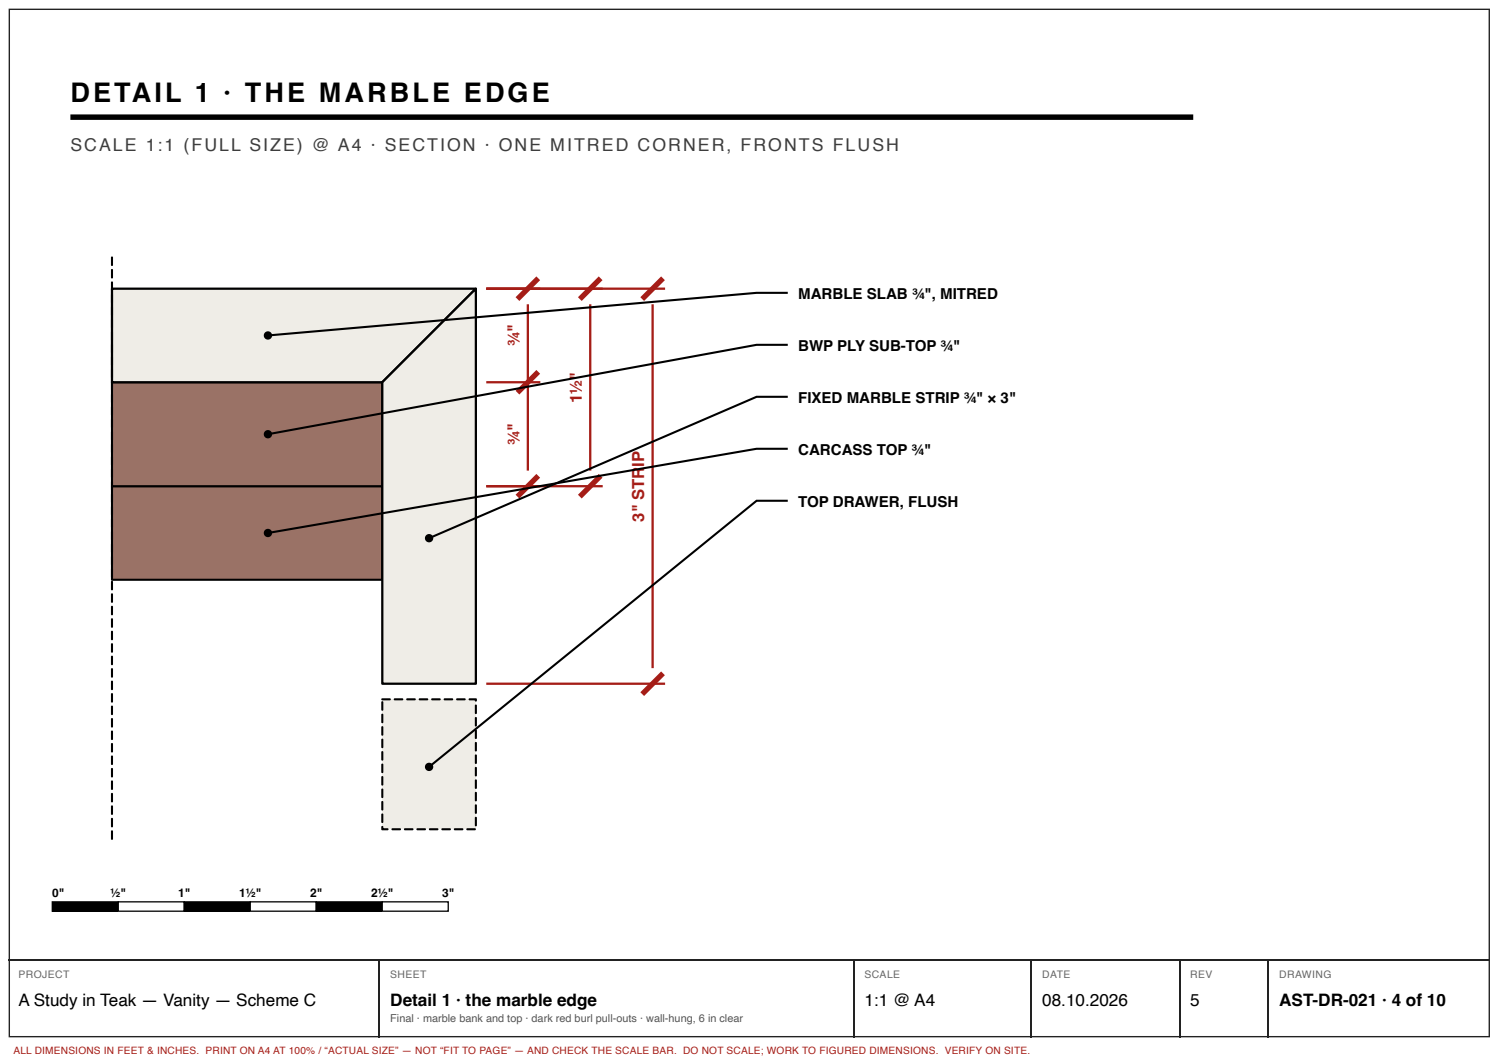
[picture p131: page 4]
RIP; CARCASS TOP ¾"

MARBLE SLAB ¾", MITRED

BWP PLY SUB-TOP ¾"

FIXED MARBLE STRIP ¾" × 3"

TOP DRAWER, FLUSH

Detail 1 · the marble edge

AST-DR-021 · 4 of 10

# FRONTS

# SIZES ARE THE FRONT ITSELF · ⅛" GAP ALL ROUND

No. | WHAT | W × H | FT-IN
1 | Pull-out cabinet, cup pull | 1'-2¾" × 1'-10¼" | 1'-2¾" × 1'-10¼"
2 | Pull-out cabinet, cup pull | 4¼" × 1'-10¼" | 4¼" × 1'-10¼"
3 | Top drawer, push-open · marble | 1'-3¾" × 6½" | 1'-3¾" × 6½"
4 | Top drawer, push-open · marble | 1'-3¾" × 6½" | 1'-3¾" × 6½"
5 | Big drawer, U-box, push-open · marble | 2'-8¾" × 1'-2⅝" | 2'-8¾" × 1'-2⅝"
5a | Inner drawer, finger scoop | 2'-6½" × 4¼" | 2'-6½" × 4¼"

# Fronts

# AST-DR-021 · 5 of 10

# MATERIALS

# THE ROOM'S PALETTE — NOTHING NEW

Top | Beige-gold marble, the bathroom stone. ¾" slab
| on a ¾" BWP sub-top, mitred at the front edge into
| a fixed ¾" marble strip: one corner, fronts flush.
Bank | The same beige marble on the face frame and on
| every drawer front, bonded to BWP boxes. It stops
| 6 in off the floor, level with the ends: a drain below.
Ends | Two pull-out cabinets, 9292 burl veneer, polished
| dark and red (the owner's photo), gloss, edges sealed.
Hanging | ¾" ply cleat 2'-3½"–2'-5⅞" and concealed steel brackets
| into the wall: the stone is heavy. Nothing on the floor.
Ledges | The two veneer tops: solid nosing, sealed.
Runners | Drawers: undermount, push-to-open. Pull-outs:
| heavy full-extension runners, cup pull.
Fittings | Chrome — already bought.

# Materials

# AST-DR-021 · 6 of 10

# PLAN

### SCALE 1:8 (1½" = 1'-0") @ A4 · FROM ABOVE · WALL AT THE TOP

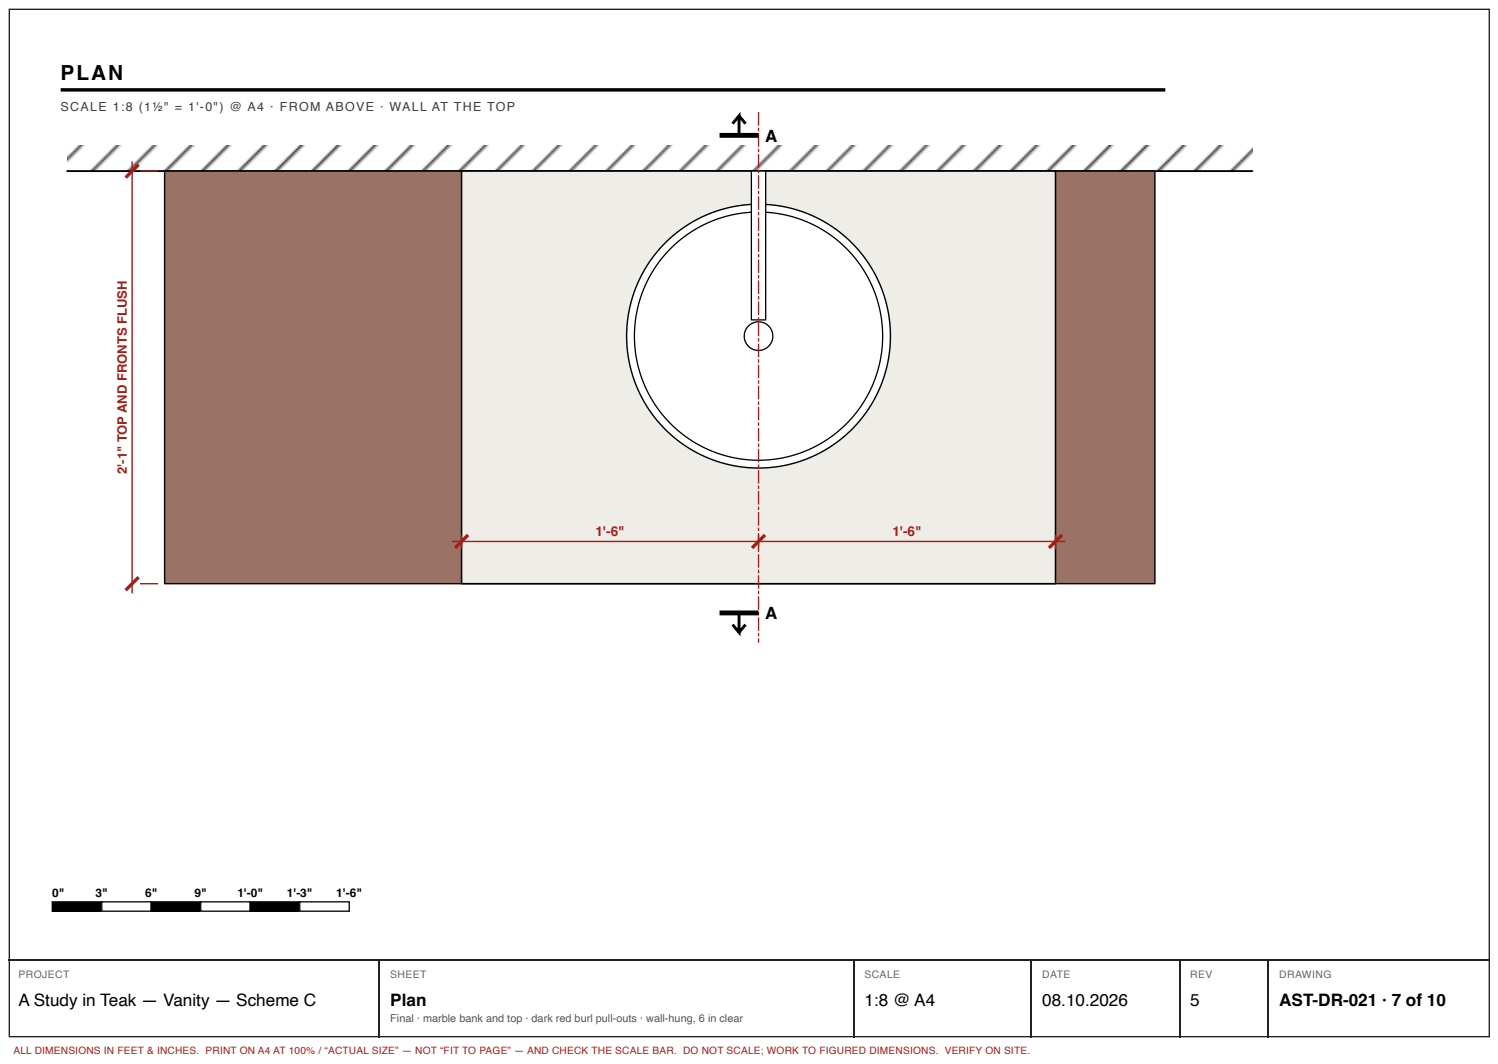
[picture p132: page 7]
Plan

2'-1" TOP AND FRONTS FLUSH

AST-DR-021 · 7 of 10

# DETAIL 2 · THE BIG DRAWER

## SCALE 1:8 (1½" = 1'-0") @ A4 · PLAN · INNER DRAWER DASHED

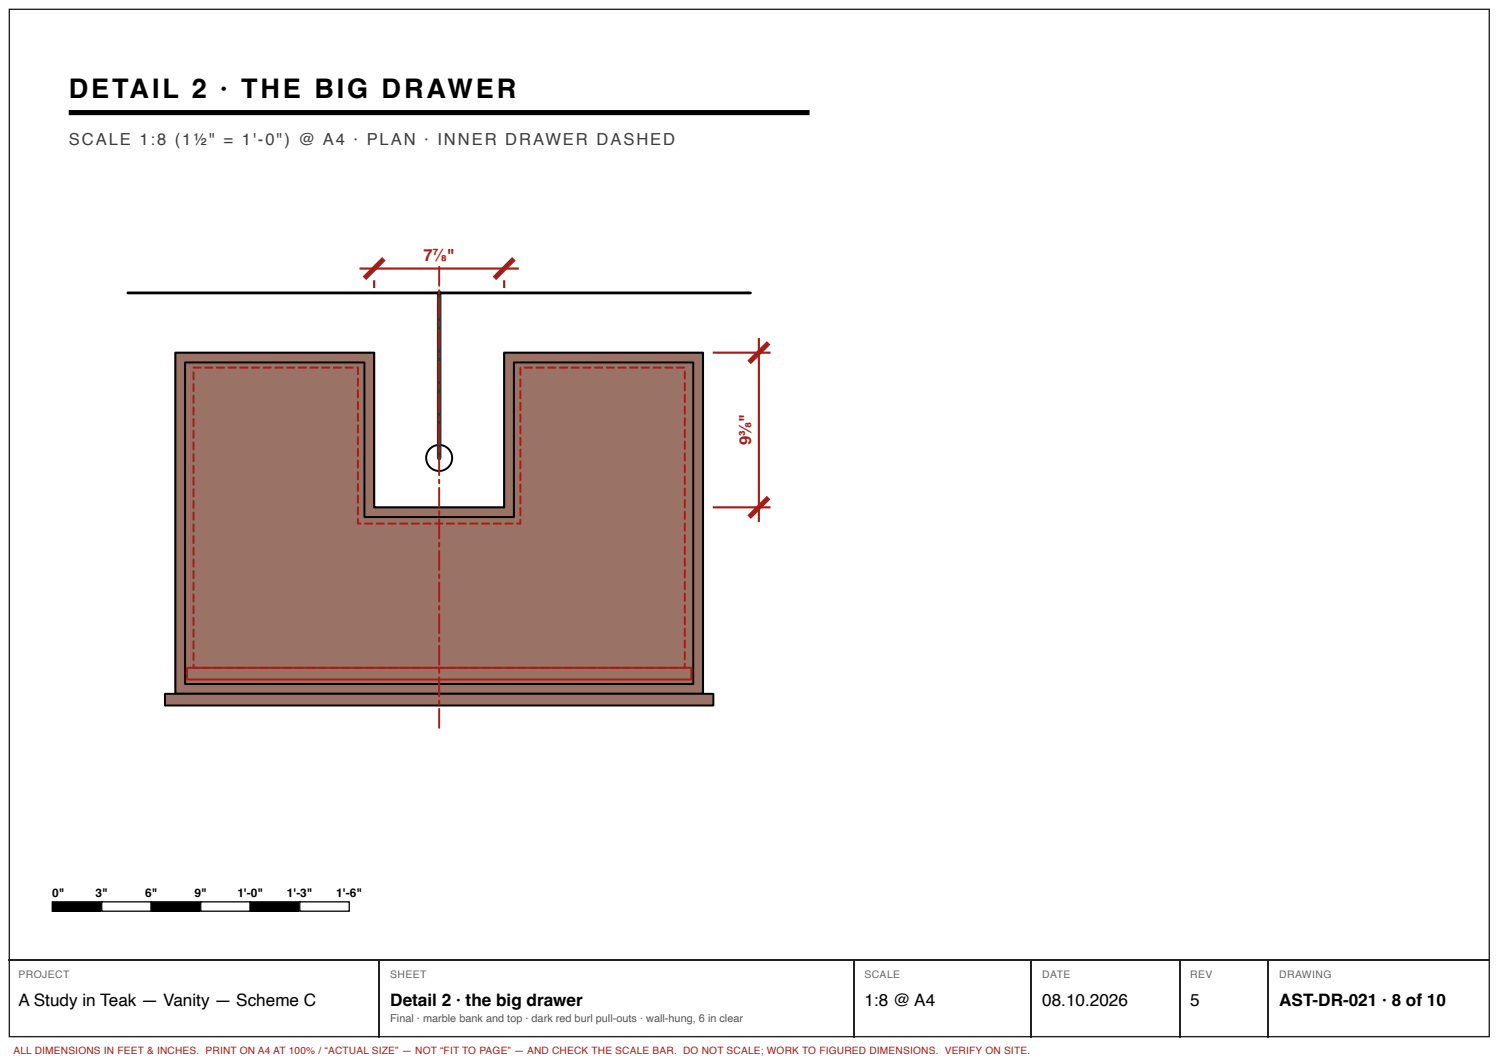
[picture p133: page 8]

Detail 2 · the big drawer

AST-DR-021 · 8 of 10

# S E C T I O N K E Y

A | Hanging cleat | B | Big drawer, U-box | C | Waste Ø1⅝" and P-trap

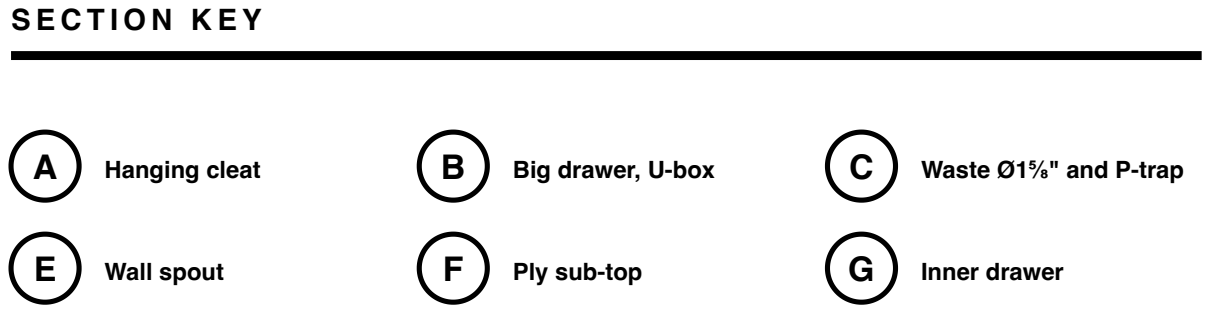
[picture p134: page 9]
Wall spout; Ply sub-top; Inner drawer; Section key

AST-DR-021 · 9 of 10

# NOTES

### REVISION 5

### Rev 5: the marble bank is back — face frame and fronts —

### but stops 6 in off the floor, level with the ends: a drain

is on the floor below. The row hangs on the wall; no support.

Top drawers 6½ in; the big drawer 14½ in, a 4 in inner one.

OPEN — bowl Ø1'-4" × 5" and the spout are assumed.

### OPEN — marble front thickness and its bond to the drawer

boxes, and the brackets' size: stone supplier to confirm.

Rev 3: top and front meet in one mitred corner, flush.

# Notes

# AST-DR-021 · 10 of 10
