sakshampan733-cloud/a-study-in-teak/cad/print/wardrobe-interiors.pdf

WARDROBE INTERIORS — DOORS OFF

SEEN FROM THE ROOM · EVERY BAY 3'-⅝" WIDE, 9 FT HIGH, 2 FT 3 IN DEEP

LEFT RUN — L1 TO L3, L3 BESIDE THE MIRROR

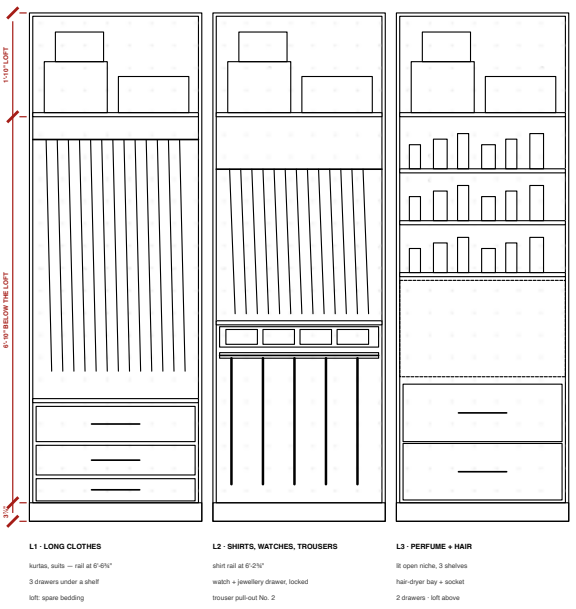
[picture p146: figure]
L1 · LONG CLOTHES; kurtas, suits — rail at 6'-6¾"; 3 drawers under a shelf; loft: spare bedding; L2 · SHIRTS, WATCHES, TROUSERS; shirt rail at 6'-2¾"; watch + jewellery drawer, locked; trouser pull-out No. 2; L3 · PERFUME + HAIR; lit open niche, 3 shelves; hair-dryer bay + socket; 2 drawers · loft above

3⅞" 6'-10" BELOW THE LOFT 1'-10" LOFT

RIGHT RUN — R 0" TO R ⅛", R ⅛" THE TUNNEL DOOR

1 · THE LIT BACK

PLAN AT A BAY'S BACK CORNER · NOT THE TUNNEL DOOR

⅜" 1¾"

⅛"

2⅛" IN ALL

THE WALL

⅜" PLY BACKER

PAINTED WHITE, TO THROW THE LIGHT

LED STRIP, 3⅞" APART

WARM WHITE 8'-10¼" K, DIMMABLE

1⅝" AIR GAP

SO THE GLOW IS EVEN, NO DOTS

⅛" OPAL ACRYLIC — NOT GLASS

IN A GROOVE IN EACH SIDE, LIFTS OUT

SHELF, ⅞"

STOPS AT THE ACRYLIC

SIDE PANEL, ¾" PLY

THE SAME VENEER BOTH FACES

INSIDE (OWNER, 7 OCT)

The inside is a laminate the owner has chosen; its sample is still to

come. Until then it is drawn and modelled as the SAME VENEER as the

doors, on every face inside — sides, shelves, drawer fronts, the loft.

The back of every bay glows: an opal acrylic panel lit from behind

(detail 1) — the tunnel door R ⅛" excepted. One dimmer for both runs.

LED strips also down the door edges, as before (not drawn).

NOTES

REVISION 1

The layout the owner approved in chat (7 Oct), set out as built. Every bay has a loft at

### 7 ft 2 in — one open 1 ft 10 in space, no middle shelf; a step stool reaches it. Rails at

6'-6¾" (L1) and 6'-2¾" (L2). Two trouser pull-outs: No. 1 in R ⅛", No. 2 in L2. Shelves ⅞" thick,

soft-close runners everywhere, no glass inside. Shoe trays in R ⅛" tilt out as the owner's

photo; 5 spare trays for later. L3's open niche is lit for the perfumes (about ⅜" to ½").

Doors, end bays and the tunnel door: AST-DR-025, -026 and the hidden-door drawings.

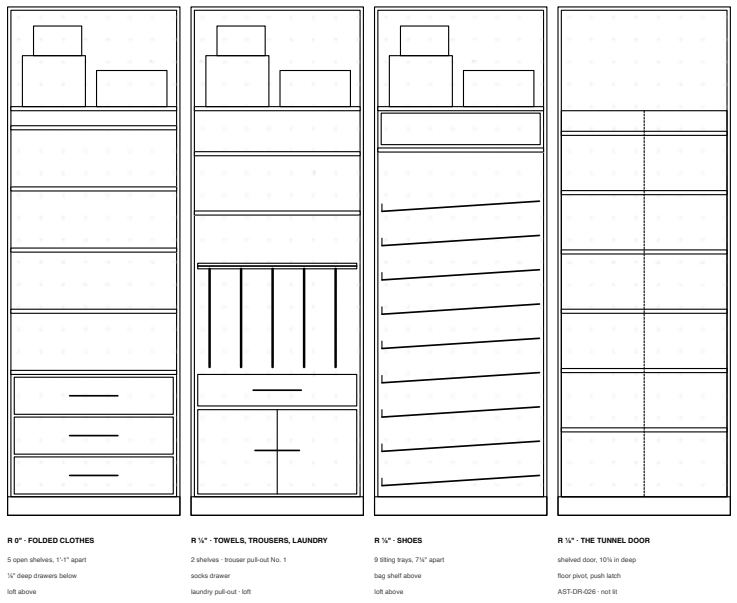
[picture p147: figure]
R 0" · FOLDED CLOTHES; 5 open shelves, 1'-1" apart; ⅛" deep drawers below; loft above; R ⅛" · TOWELS, TROUSERS, LAUNDRY; 2 shelves · trouser pull-out No. 1; socks drawer; laundry pull-out · loft; R ⅛" · SHOES; 9 tilting trays, 7¼" apart; bag shelf above; R ⅛" · THE TUNNEL DOOR; shelved door, 10¼ in deep; floor pivot, push latch; AST-DR-026 · not lit

TO MEASURE ON SITE

The bay widths: 3'-⅝" each as drawn, set out to the

real runs on site. The sockets: L3's hair-dryer bay

and one LED driver per run, in the plinth.

A S T U D Y I N T E A K

Particulars of the room

WARDROBE INTERIORS

Both runs, doors off · The lit back

SCALE
AS NOTED @ A3

DATE
07.10.2026

REV

1 — the approved layout; the same veneer inside, backlit backs

DWG
AST-DR-048

PROJECT

## A Study in Teak — Wardrobe Interiors

SHEET

## General arrangement — the whole sheet

each view follows at its own scale, pages 2 to 6

SCALE

## NTS

DATE
07.10.2026

REV

DRAWING

## AST-DR-048 · 1 of 6

ALL DIMENSIONS IN FEET & INCHES. PRINT ON A3 AT 100% / “ACTUAL SIZE” — NOT “FIT TO PAGE” — AND CHECK THE SCALE BAR. DO NOT SCALE; WORK TO FIGURED DIMENSIONS. VERIFY ON SITE.

# WARDROBE INTERIORS — DOORS OFF

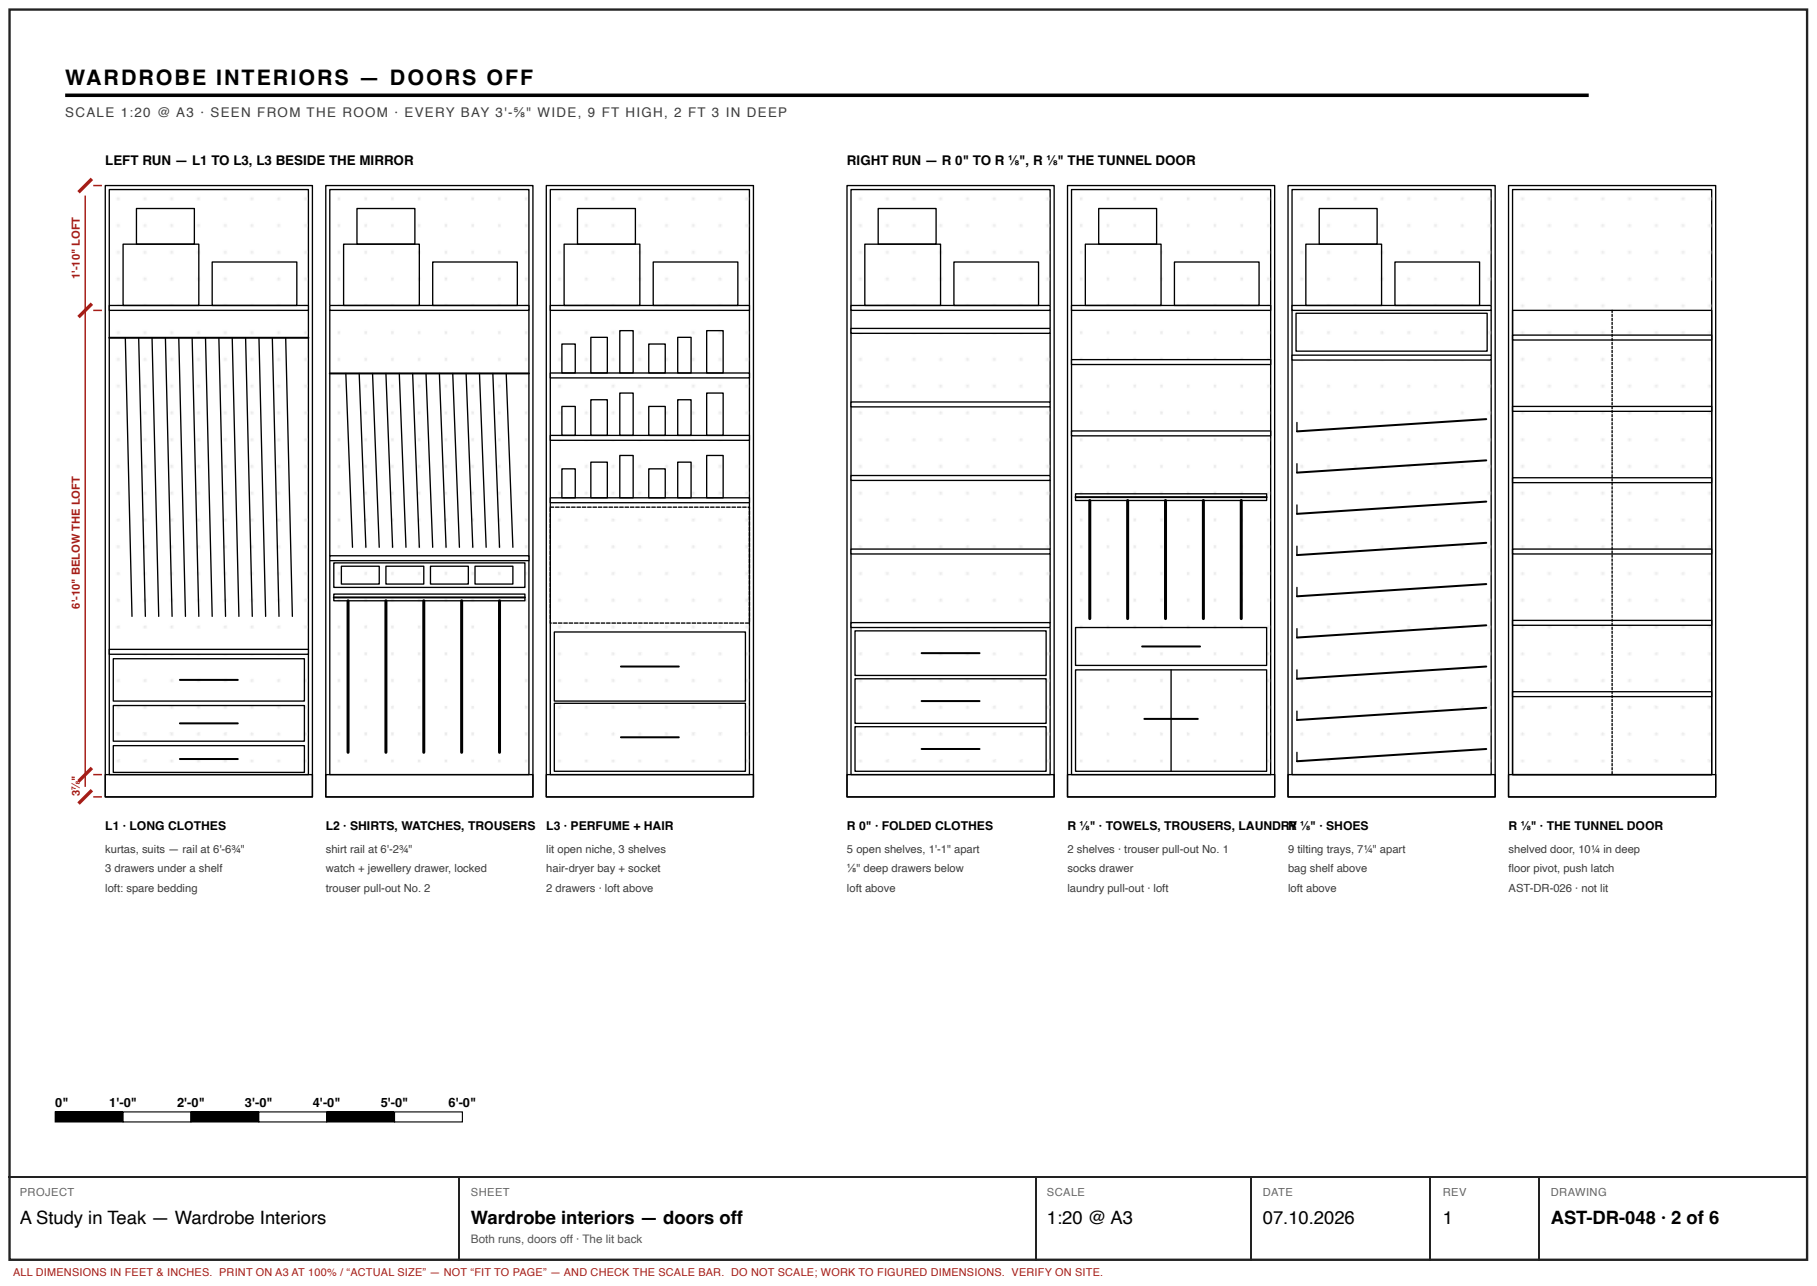
[picture p148: page 2]
L1 · LONG CLOTHES; L3 · PERFUME + HAIR; 3⅞" 6'-10" BELO; R 0" · FOLDED CLOTHES; R ⅛" · SHOES

SCALE 1:20 @ A3 · SEEN FROM THE ROOM · EVERY BAY 3'-⅝" WIDE, 9 FT HIGH, 2 FT 3 IN DEEP

LEFT RUN — L1 TO L3, L3 BESIDE THE MIRROR

RIGHT RUN — R 0" TO R ⅛", R ⅛" THE TUNNEL DOOR

W THE LOFT 1'-10" LOFT

L2 · SHIRTS, WATCHES, TROUSERS

R ⅛" · TOWELS, TROUSERS, LAUNDRY

R ⅛" · THE TUNNEL DOOR

kurtas, suits — rail at 6'-6¾"
3 drawers under a shelf
loft: spare bedding

shirt rail at 6'-2¾"
watch + jewellery drawer, locked
trouser pull-out No. 2

lit open niche, 3 shelves
hair-dryer bay + socket
2 drawers · loft above

5 open shelves, 1'-1" apart
⅛" deep drawers below
loft above

2 shelves · trouser pull-out No. 1
socks drawer
laundry pull-out · loft

9 tilting trays, 7¼" apart
bag shelf above

shelved door, 10¼ in deep
floor pivot, push latch
AST-DR-026 · not lit

Wardrobe interiors — doors off

AST-DR-048 · 2 of 6

Both runs, doors off · The lit back

# 1 · THE LIT BACK

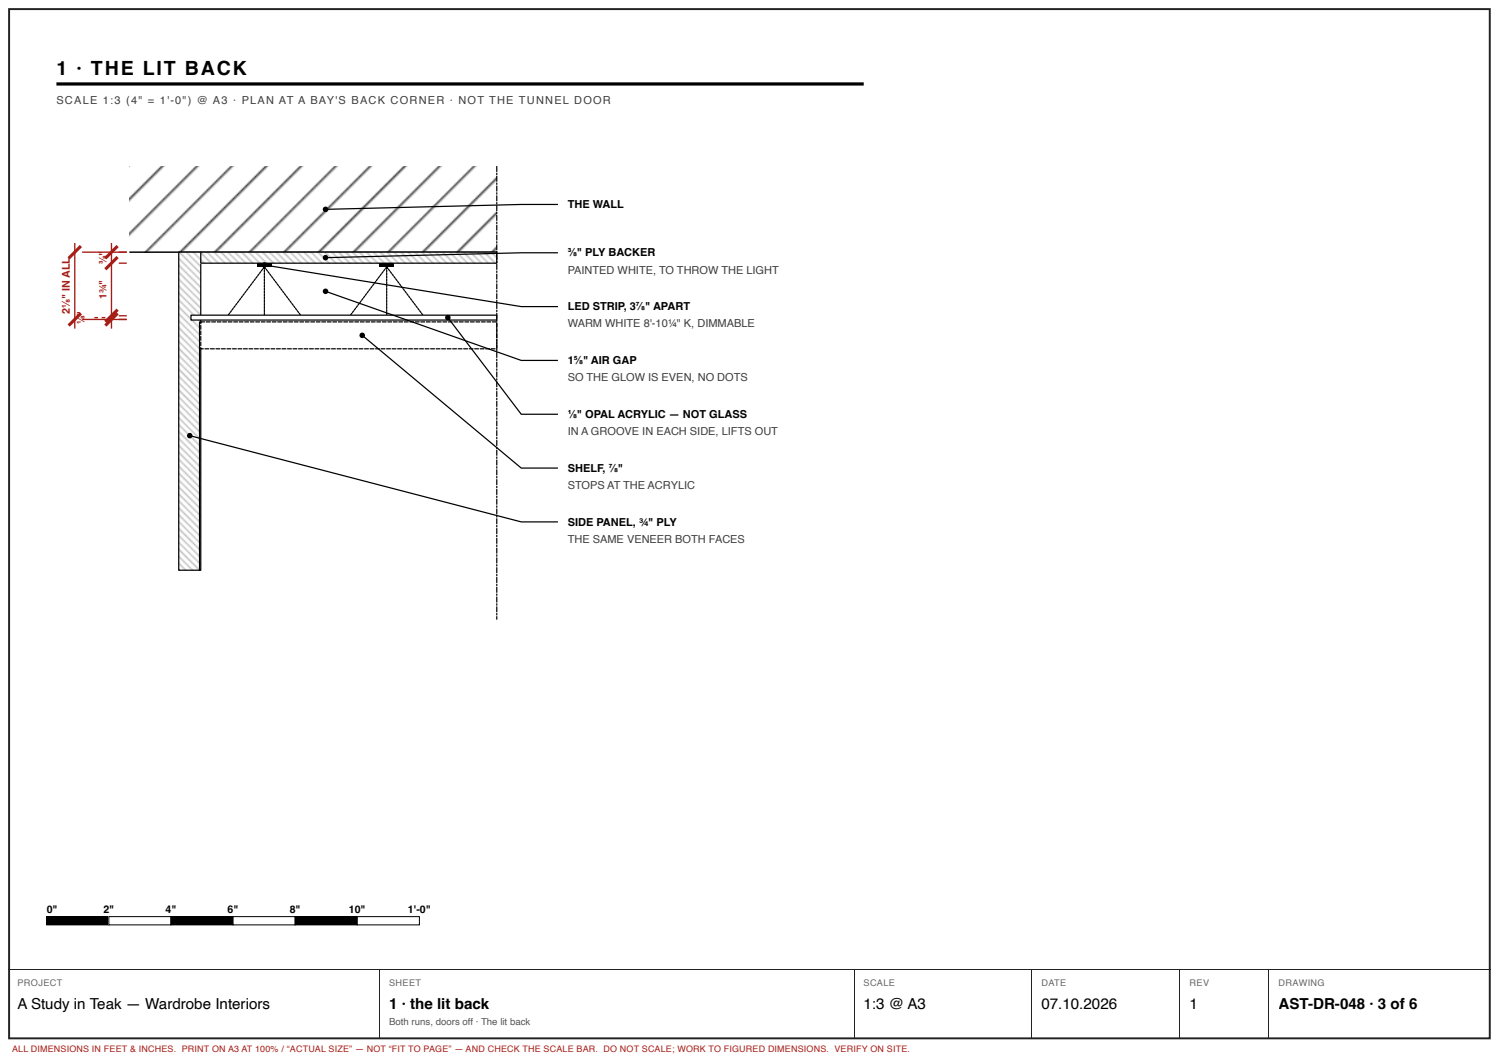
[picture p149: page 3]
ALL; THE WALL

SCALE 1:3 (4" = 1'-0") @ A3 · PLAN AT A BAY'S BACK CORNER · NOT THE TUNNEL DOOR

⅜" PLY BACKER
PAINTED WHITE, TO THROW THE LIGHT

LED STRIP, 3⅞" APART
WARM WHITE 8'-10¼" K, DIMMABLE

1⅝" AIR GAP
SO THE GLOW IS EVEN, NO DOTS

⅛" OPAL ACRYLIC — NOT GLASS
IN A GROOVE IN EACH SIDE, LIFTS OUT

SHELF, ⅞"
STOPS AT THE ACRYLIC

SIDE PANEL, ¾" PLY
THE SAME VENEER BOTH FACES

1 · the lit back

AST-DR-048 · 3 of 6

# NOTES

# REVISION 1

# The layout the owner approved in chat (7 Oct), set out as built. Every bay has a loft at

# 7 ft 2 in — one open 1 ft 10 in space, no middle shelf; a step stool reaches it. Rails at

6'-6¾" (L1) and 6'-2¾" (L2). Two trouser pull-outs: No. 1 in R ⅛", No. 2 in L2. Shelves ⅞" thick,

soft-close runners everywhere, no glass inside. Shoe trays in R ⅛" tilt out as the owner's

photo; 5 spare trays for later. L3's open niche is lit for the perfumes (about ⅜" to ½").

Doors, end bays and the tunnel door: AST-DR-025, -026 and the hidden-door drawings.

## Notes

## AST-DR-048 · 4 of 6

# TO MEASURE ON SITE

# The bay widths: 3'-⅝" each as drawn, set out to the

# real runs on site. The sockets: L3's hair-dryer bay

and one LED driver per run, in the plinth.

## To measure on site

## AST-DR-048 · 5 of 6

# INSIDE (OWNER, 7 OCT)

## The inside is a laminate the owner has chosen; its sample is still to

## come. Until then it is drawn and modelled as the SAME VENEER as the

doors, on every face inside — sides, shelves, drawer fronts, the loft.

## The back of every bay glows: an opal acrylic panel lit from behind

(detail 1) — the tunnel door R ⅛" excepted. One dimmer for both runs.

LED strips also down the door edges, as before (not drawn).

## Inside (owner, 7 oct)

## AST-DR-048 · 6 of 6
