sakshampan733-cloud/a-study-in-teak/cad/print/tvunit-a4.pdf

PLAN

CUT THROUGH THE UPPER DRAWERS · THE PARTITION AT THE TOP, THE BED BELOW · TOP AND PLINTH DASHED

1'-5¾" | 1'-5¾" | 1'-5¾" | 1'-5¾"
10½" | 5'-10⅞" STRAIGHT FRONT | 10½"

1'-4"

▼ THE FOOT OF THE BED, 2 ft 6⅜ in FROM THE FRONTS — 1 ft 4⅝ in WITH A DRAWER OUT

GLASS-BLOCK PARTITION

AS BUILT IN THE 3D — NOT CHANGED

TV ABOVE (DASHED) | WOOD COLUMN, 1 FT

BACK PANEL, VENEERED BOTH FACES

IT READS THROUGH THE GLASS FROM THE DESK

DRAWER BOX ON 1'-1¾" RUNNERS

FULL EXTENSION, SOFT CLOSE

ROUND END, FIXED

DETAIL 1

DOORS HINGE ON THE DRAWER SIDE

THEY SWING CLEAR OF THE ROUND ENDS

A

A

FRONT

SEEN FROM THE BED · THE GLASS BROKEN OFF ABOVE

CABINET | DRAWERS | DRAWERS | CABINET

2⅜" 7⅛" 7⅛" 1"

1'-5¾" — KEPT LOW

BULLNOSE TOP, 1 IN

CABINET — ONE DOOR, TWO DRAWERS TALL

ONE ADJUSTABLE SHELF

DRAWERS, TWO HIGH

SLIM BRASS BAR, AS BEFORE

ROUND END — FIXED

BENT PLY, VENEERED

PLINTH, DARK, 2 IN BACK

SECTION A–A

THROUGH A DRAWER STACK

2⅜" 7⅛" 7⅛" 1"

3¾" | 1'-4"

BULLNOSE TOP

1", SOLID TEAK LIP

BRASS BAR

ON TWO POSTS

FRONT, ¾"

EDGES EASED 5

1'-1¾" RUNNER

UNDERMOUNT

PLINTH

SET BACK 2 IN

GLASS | BACK, 9

DETAIL 1 · THE ROUND END

PLAN

R ⅜"½ in

SCRIBED TO THE CHANNEL

AT THE PARTITION'S TIP

TOP OVERSAILS ⅜"

DASHED

¾" BENT PLY

3 × 6, VENEERED BOTH FACES

SHELF

INTO THE ROUND END

⅛" GAP

THE DOOR SWINGS CLEAR

DOOR, FLAT

UPRIGHT BRASS BAR

NOTES

REVISION 1

From the owner's sketch. The run of 4 × 2 drawers that followed the

partition's curve could not open at its curved ends. Now the unit is a pill:

a straight front across the middle, a quarter-round at each end wrapping

back to the partition's tip, and nothing that moves is curved.

Four equal bays, 17¾ in: two stacks of two drawers in the middle, and at

each end one cabinet two drawers tall behind a flat door (owner).

Doors hinge on the drawer side, so they open away from the round ends.

ASSUMED

TELL ME IF ANY OF THESE IS WRONG

Height 1 ft 5¾ in and depth 1 ft 3¾ in, as the last run.

The same veneer as before: the 9292 burl in the Dark Diva

colour, the grain running on across all four bays.

The slim brass bar kept; an upright one on each door.

Every edge eased ¼"; the top a full bullnose.

Concealed soft-close hinges; one shelf in each cabinet.

TO DECIDE

Fronts: eased edges as drawn, or rounder —

each front a small pill of its own?

Pulls: the brass bar, or push-to-open with none.

With a drawer out, 1 ft 4⅝ in is left to the bed's

foot — fine to pass, tight to kneel at.

A S T U D Y I N T E A K

Particulars of the room

TV UNIT — DRAWERS

Plan · Front · Section A–A · Round end

SCALE

AS NOTED @ A3

DATE

03.10.2026

REV

1 — a pill in plan: two drawer stacks, two cabinets

DWG

AST-DR-036

PROJECT

# A Study in Teak — Tv Unit — Drawers

SHEET

# General arrangement — the whole sheet

each view follows at its own scale, pages 2 to 8

SCALE

# NTS

DATE
03.10.2026

REV

DRAWING

# AST-DR-036 · 1 of 8

ALL DIMENSIONS IN FEET & INCHES. PRINT ON A4 AT 100% / “ACTUAL SIZE” — NOT “FIT TO PAGE” — AND CHECK THE SCALE BAR. DO NOT SCALE; WORK TO FIGURED DIMENSIONS. VERIFY ON SITE.

## PLAN

A

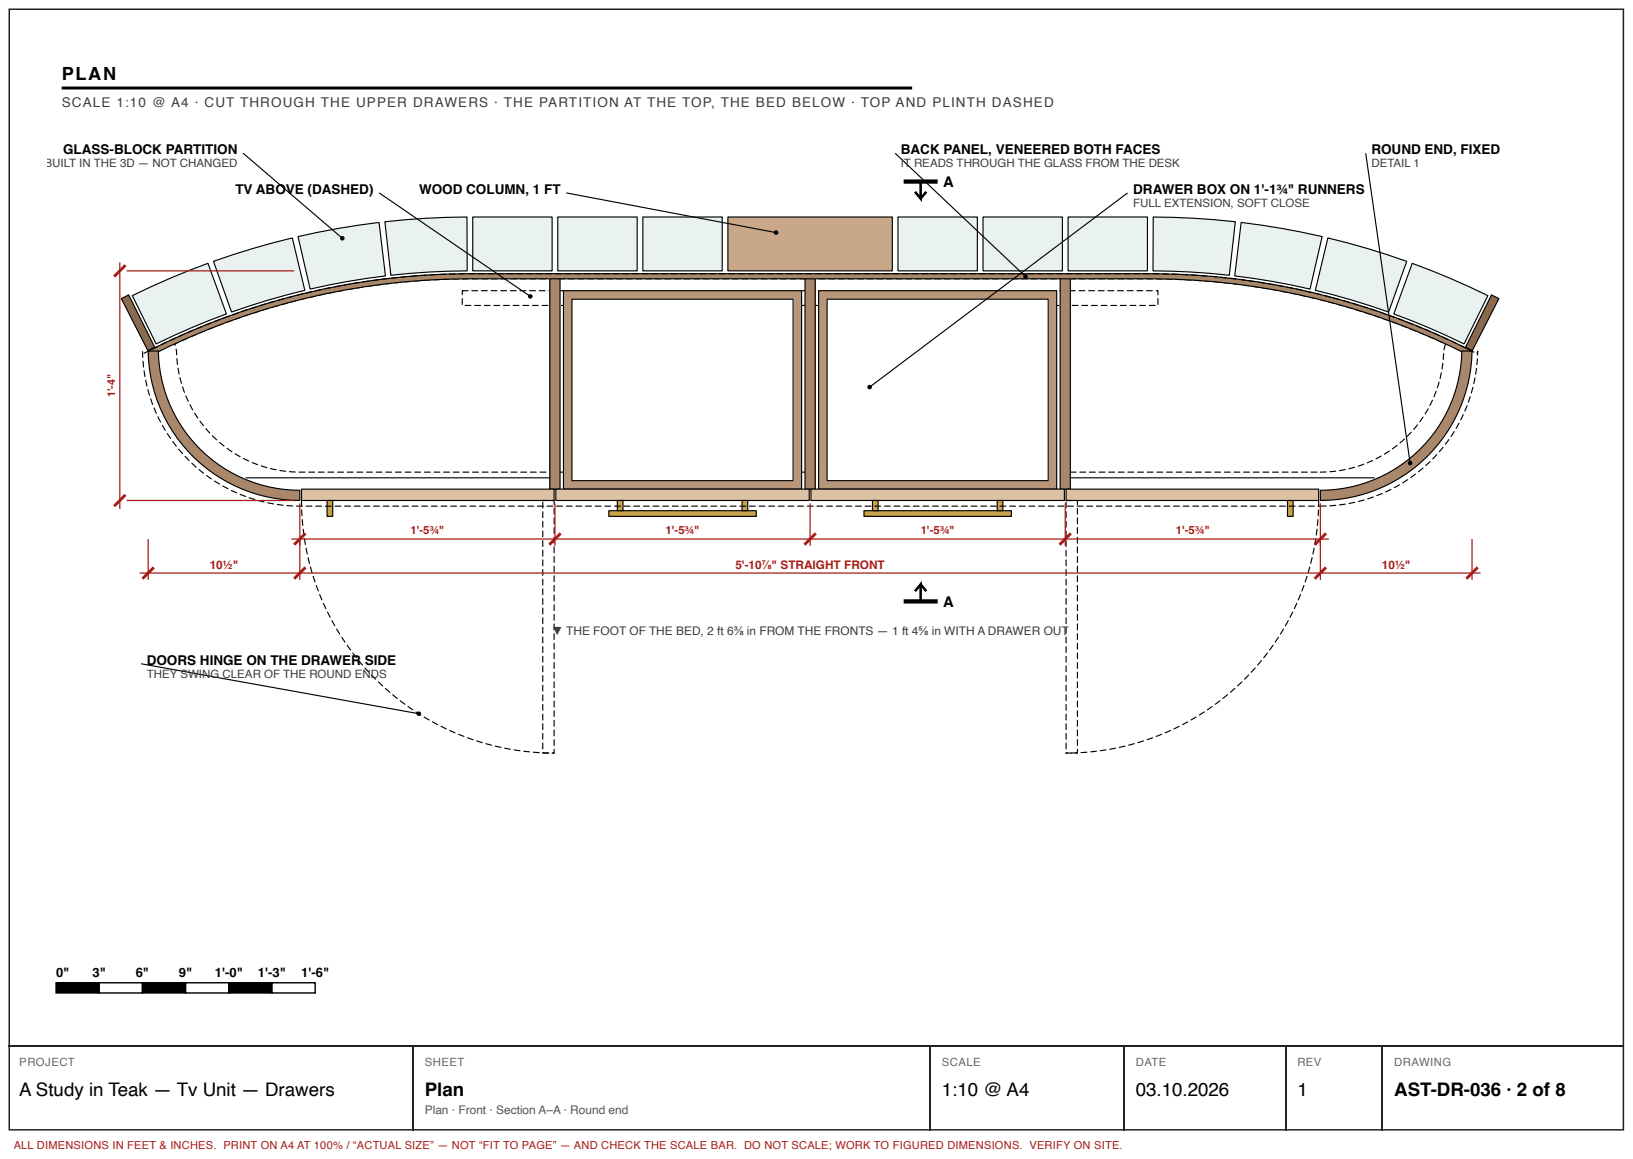
[picture p150: page 2]
5'-10⅞" STRAIGHT FRONT; TV ABOVE (DASHED); WOOD COLUMN, 1 FT; Plan

SCALE 1:10 @ A4 · CUT THROUGH THE UPPER DRAWERS · THE PARTITION AT THE TOP, THE BED BELOW · TOP AND PLINTH DASHED

GLASS-BLOCK PARTITION
BUILT IN THE 3D — NOT CHANGED

BACK PANEL, VENEERED BOTH FACES
IT READS THROUGH THE GLASS FROM THE DESK

ROUND END, FIXED
DETAIL 1

DRAWER BOX ON 1'-1¾" RUNNERS
FULL EXTENSION, SOFT CLOSE

▼ THE FOOT OF THE BED, 2 ft 6⅜ in FROM THE FRONTS — 1 ft 4⅝ in WITH A DRAWER OUT

DOORS HINGE ON THE DRAWER SIDE
THEY SWING CLEAR OF THE ROUND ENDS

AST-DR-036 · 2 of 8

Plan · Front · Section A–A · Round end

# SECTION A–A

### SCALE 1:5 @ A4 · THROUGH A DRAWER STACK

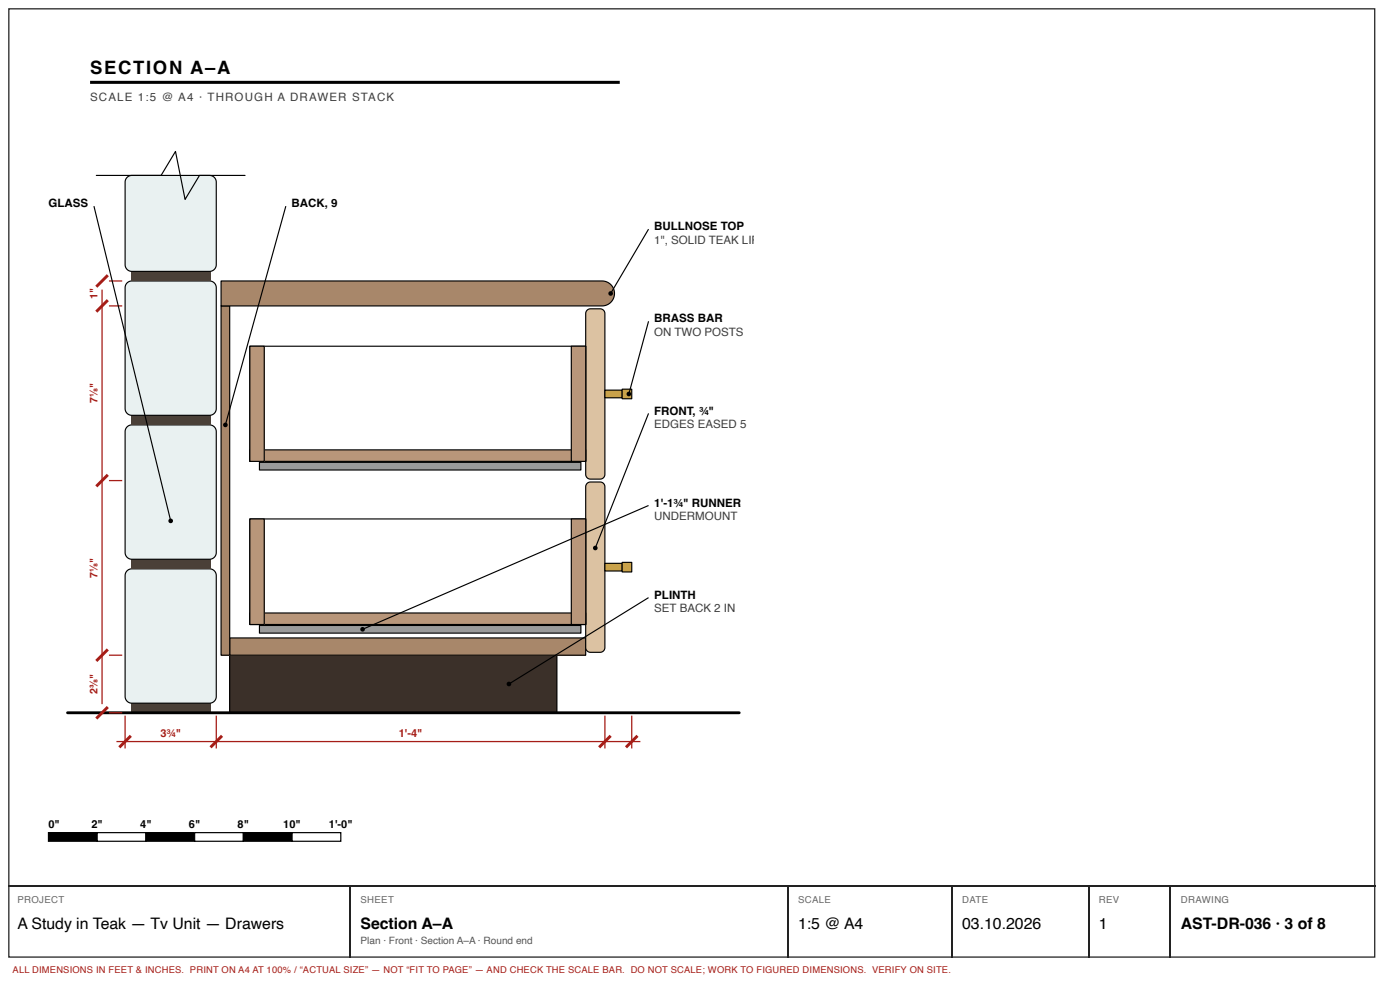
[picture p151: page 3]
FRONT, ¾" EDGES EASED 5; 1'-1¾" RUNNER UNDERMOUNT; GLASS; BACK, 9; Section A–A

BULLNOSE TOP
1", SOLID TEAK LIP

BRASS BAR
ON TWO POSTS

PLINTH
SET BACK 2 IN

AST-DR-036 · 3 of 8

## FRONT

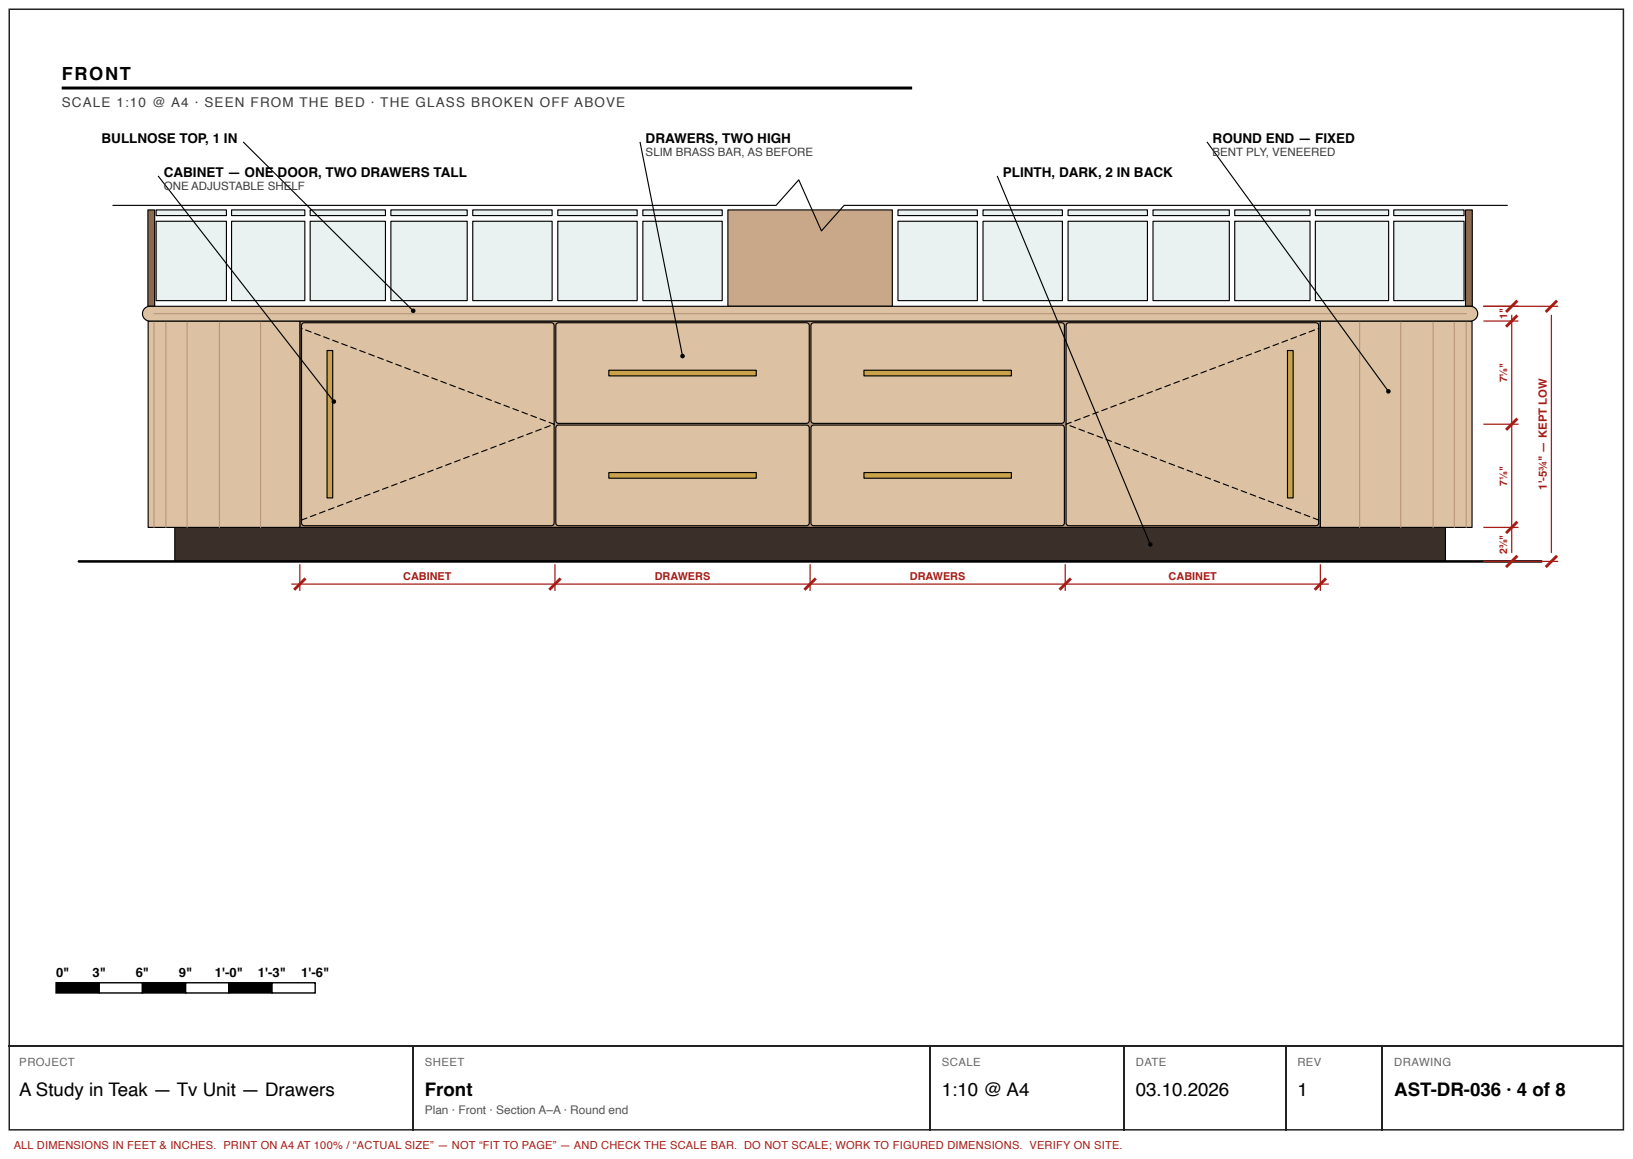
[picture p152: page 4]
CABINET; DRAWERS; 1'-5¾" — KEPT LOW; Front

SCALE 1:10 @ A4 · SEEN FROM THE BED · THE GLASS BROKEN OFF ABOVE

BULLNOSE TOP, 1 IN

DRAWERS, TWO HIGH
SLIM BRASS BAR, AS BEFORE

ROUND END — FIXED
BENT PLY, VENEERED

CABINET — ONE DOOR, TWO DRAWERS TALL
ONE ADJUSTABLE SHELF

PLINTH, DARK, 2 IN BACK

AST-DR-036 · 4 of 8

# DETAIL 1 · THE ROUND END

## SCALE 1:3 (4" = 1'-0") @ A4 · PLAN

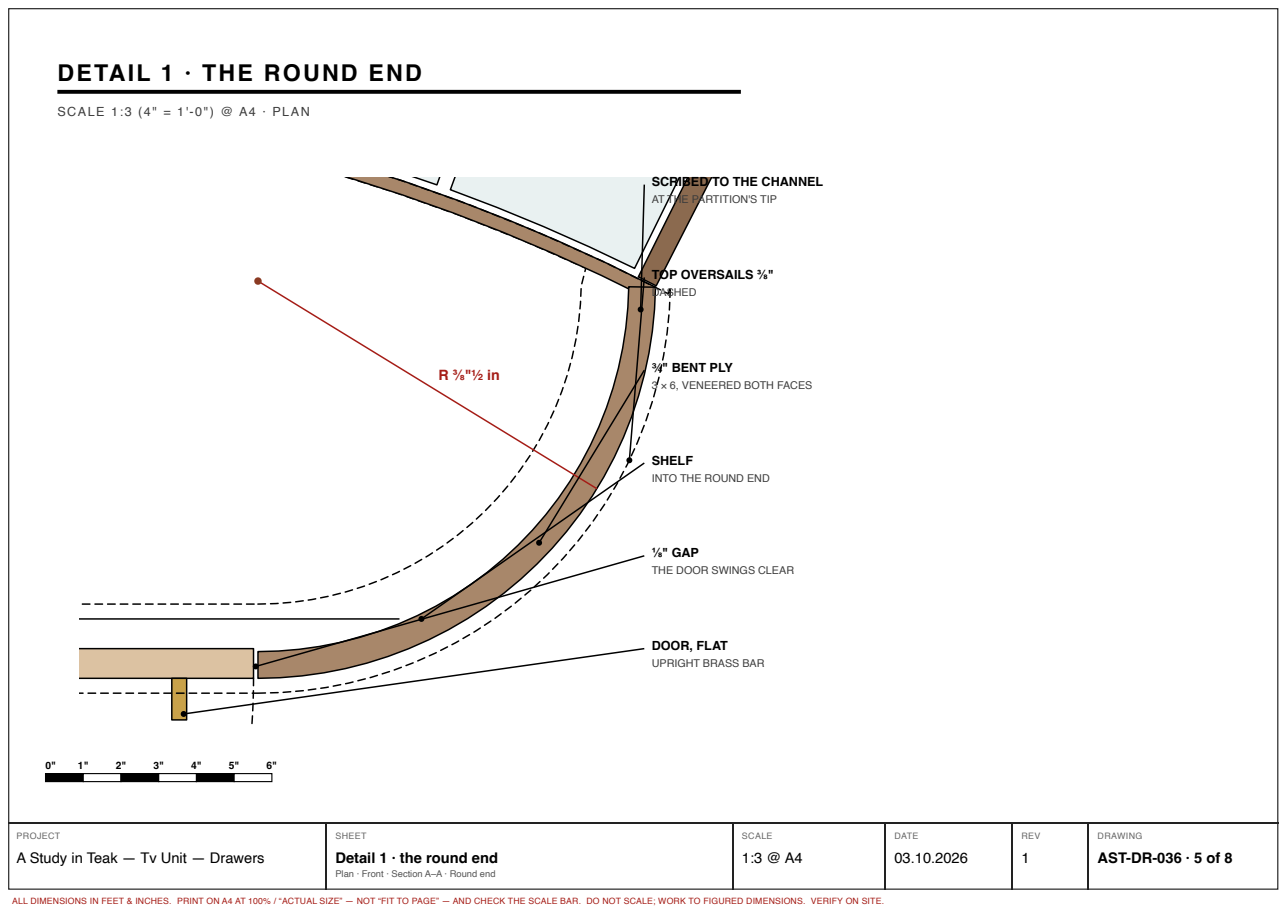
[picture p153: page 5]
TOP OVERSAILS ⅜"; DASHED

SCRIBED TO THE CHANNEL
AT THE PARTITION'S TIP

¾" BENT PLY
3 × 6, VENEERED BOTH FACES

SHELF
INTO THE ROUND END

⅛" GAP
THE DOOR SWINGS CLEAR

DOOR, FLAT
UPRIGHT BRASS BAR

Detail 1 · the round end

AST-DR-036 · 5 of 8

# N O T E S

# REVISION 1

# From the owner's sketch. The run of 4 × 2 drawers that followed the

# partition's curve could not open at its curved ends. Now the unit is a pill:

# a straight front across the middle, a quarter-round at each end wrapping

back to the partition's tip, and nothing that moves is curved.

# Four equal bays, 17¾ in: two stacks of two drawers in the middle, and at

each end one cabinet two drawers tall behind a flat door (owner).

Doors hinge on the drawer side, so they open away from the round ends.

# Notes

# AST-DR-036 · 6 of 8

# A S S U M E D

# TELL ME IF ANY OF THESE IS WRONG

Height 1 ft 5¾ in and depth 1 ft 3¾ in, as the last run.

# The same veneer as before: the 9292 burl in the Dark Diva

colour, the grain running on across all four bays.

The slim brass bar kept; an upright one on each door.

Every edge eased ¼"; the top a full bullnose.

Concealed soft-close hinges; one shelf in each cabinet.

# Assumed

# AST-DR-036 · 7 of 8

# T O D E C I D E

# Fronts: eased edges as drawn, or rounder —

# each front a small pill of its own?

Pulls: the brass bar, or push-to-open with none.

# With a drawer out, 1 ft 4⅝ in is left to the bed's

foot — fine to pass, tight to kneel at.

# To decide

# AST-DR-036 · 8 of 8
