sakshampan733-cloud/a-study-in-teak/cad/print/tvunit.pdf

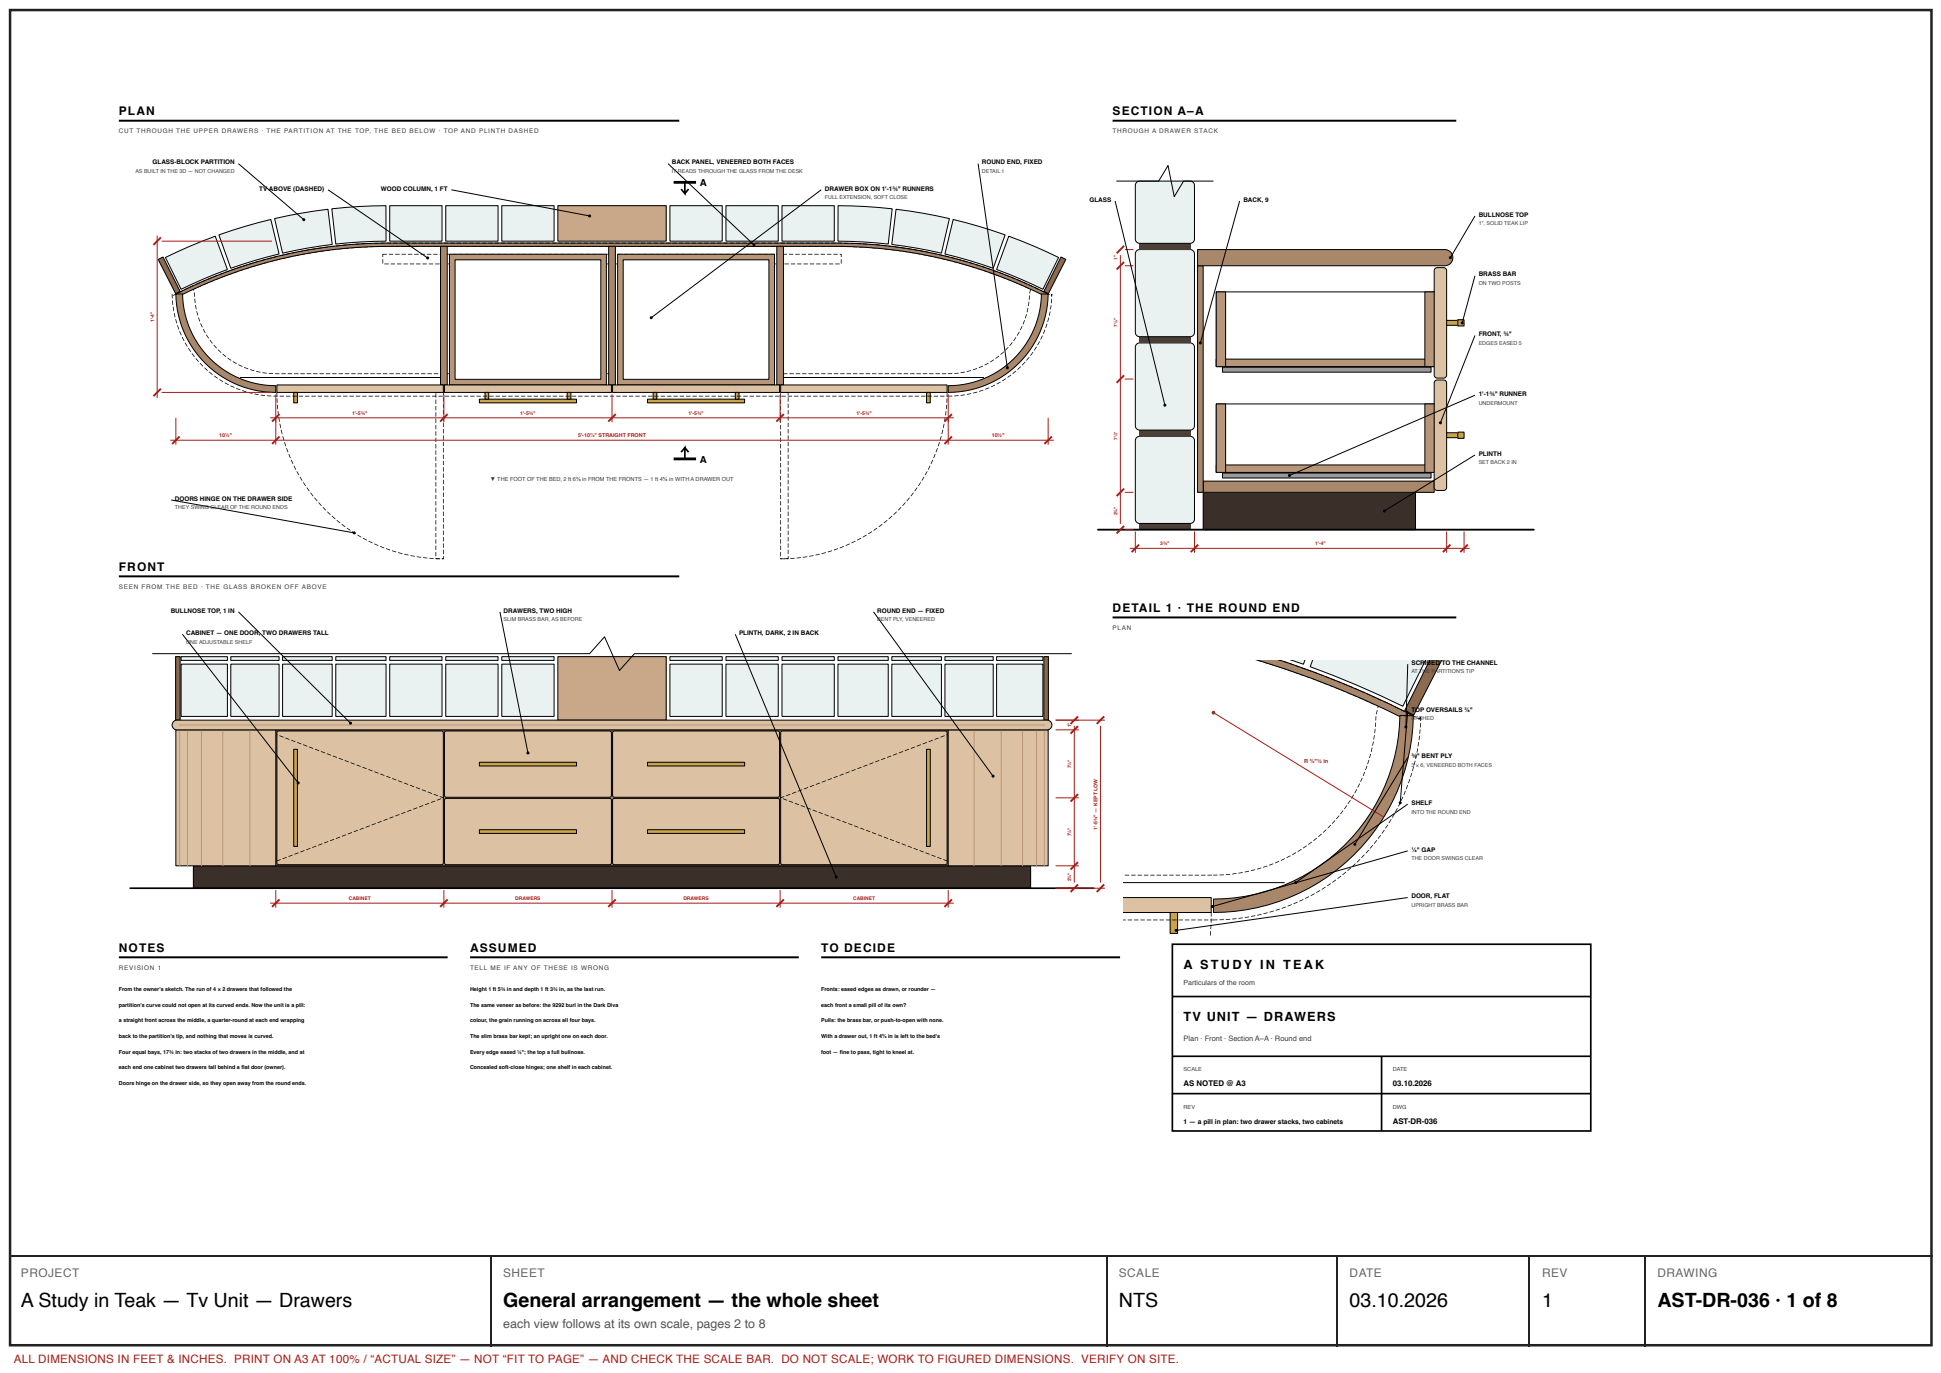
[picture p154: page 1]
PLAN; 5'-10⅞" STRAIGHT FRONT; TV ABOVE (DASHED); WOOD COLUMN, 1 FT; FRONT; CABINET; DRAWERS; 1'-5¾" — KEPT LOW; SECTION A–A; FRONT, ¾"; EDGES EASED 5; 1'-1¾" RUNNER; UNDERMOUNT; GLASS; BACK, 9; TOP OVERSAILS ⅜"; DASHED; ⅛" GAP; NOTES; REVISION 1; ASSUMED; TO DECIDE; SCALE; AS NOTED @ A3; DATE; REV; DWG; AST-DR-036; SCALE NTS; DATE 03.10.2026

CUT THROUGH THE UPPER DRAWERS · THE PARTITION AT THE TOP, THE BED BELOW · TOP AND PLINTH DASHED

THROUGH A DRAWER STACK

GLASS-BLOCK PARTITION

BACK PANEL, VENEERED BOTH FACES
IT READS THROUGH THE GLASS FROM THE DESK

ROUND END, FIXED
DETAIL 1

AS BUILT IN THE 3D — NOT CHANGED

DRAWER BOX ON 1'-1¾" RUNNERS
FULL EXTENSION, SOFT CLOSE

BULLNOSE TOP
1", SOLID TEAK LIP

BRASS BAR
ON TWO POSTS

PLINTH
SET BACK 2 IN

▼ THE FOOT OF THE BED, 2 ft 6⅜ in FROM THE FRONTS — 1 ft 4⅝ in WITH A DRAWER OUT

DOORS HINGE ON THE DRAWER SIDE
THEY SWING CLEAR OF THE ROUND ENDS

SEEN FROM THE BED · THE GLASS BROKEN OFF ABOVE

BULLNOSE TOP, 1 IN

DRAWERS, TWO HIGH
SLIM BRASS BAR, AS BEFORE

ROUND END — FIXED
BENT PLY, VENEERED

DETAIL 1 · THE ROUND END

CABINET — ONE DOOR, TWO DRAWERS TALL
ONE ADJUSTABLE SHELF

PLINTH, DARK, 2 IN BACK

SCRIBED TO THE CHANNEL
AT THE PARTITION'S TIP

¾" BENT PLY
3 × 6, VENEERED BOTH FACES

SHELF
INTO THE ROUND END

THE DOOR SWINGS CLEAR

DOOR, FLAT
UPRIGHT BRASS BAR

TELL ME IF ANY OF THESE IS WRONG

Particulars of the room

From the owner's sketch. The run of 4 × 2 drawers that followed the

Height 1 ft 5¾ in and depth 1 ft 3¾ in, as the last run.

Fronts: eased edges as drawn, or rounder —

partition's curve could not open at its curved ends. Now the unit is a pill:

The same veneer as before: the 9292 burl in the Dark Diva

each front a small pill of its own?

TV UNIT — DRAWERS

a straight front across the middle, a quarter-round at each end wrapping

colour, the grain running on across all four bays.

Pulls: the brass bar, or push-to-open with none.

back to the partition's tip, and nothing that moves is curved.

The slim brass bar kept; an upright one on each door.

With a drawer out, 1 ft 4⅝ in is left to the bed's

Plan · Front · Section A–A · Round end

Four equal bays, 17¾ in: two stacks of two drawers in the middle, and at

Every edge eased ¼"; the top a full bullnose.

foot — fine to pass, tight to kneel at.

each end one cabinet two drawers tall behind a flat door (owner).

Concealed soft-close hinges; one shelf in each cabinet.

Doors hinge on the drawer side, so they open away from the round ends.

1 — a pill in plan: two drawer stacks, two cabinets

PROJECT
A Study in Teak — Tv Unit — Drawers

SHEET
General arrangement — the whole sheet

DRAWING
AST-DR-036 · 1 of 8

each view follows at its own scale, pages 2 to 8

ALL DIMENSIONS IN FEET & INCHES. PRINT ON A3 AT 100% / “ACTUAL SIZE” — NOT “FIT TO PAGE” — AND CHECK THE SCALE BAR. DO NOT SCALE; WORK TO FIGURED DIMENSIONS. VERIFY ON SITE.

## PLAN

A

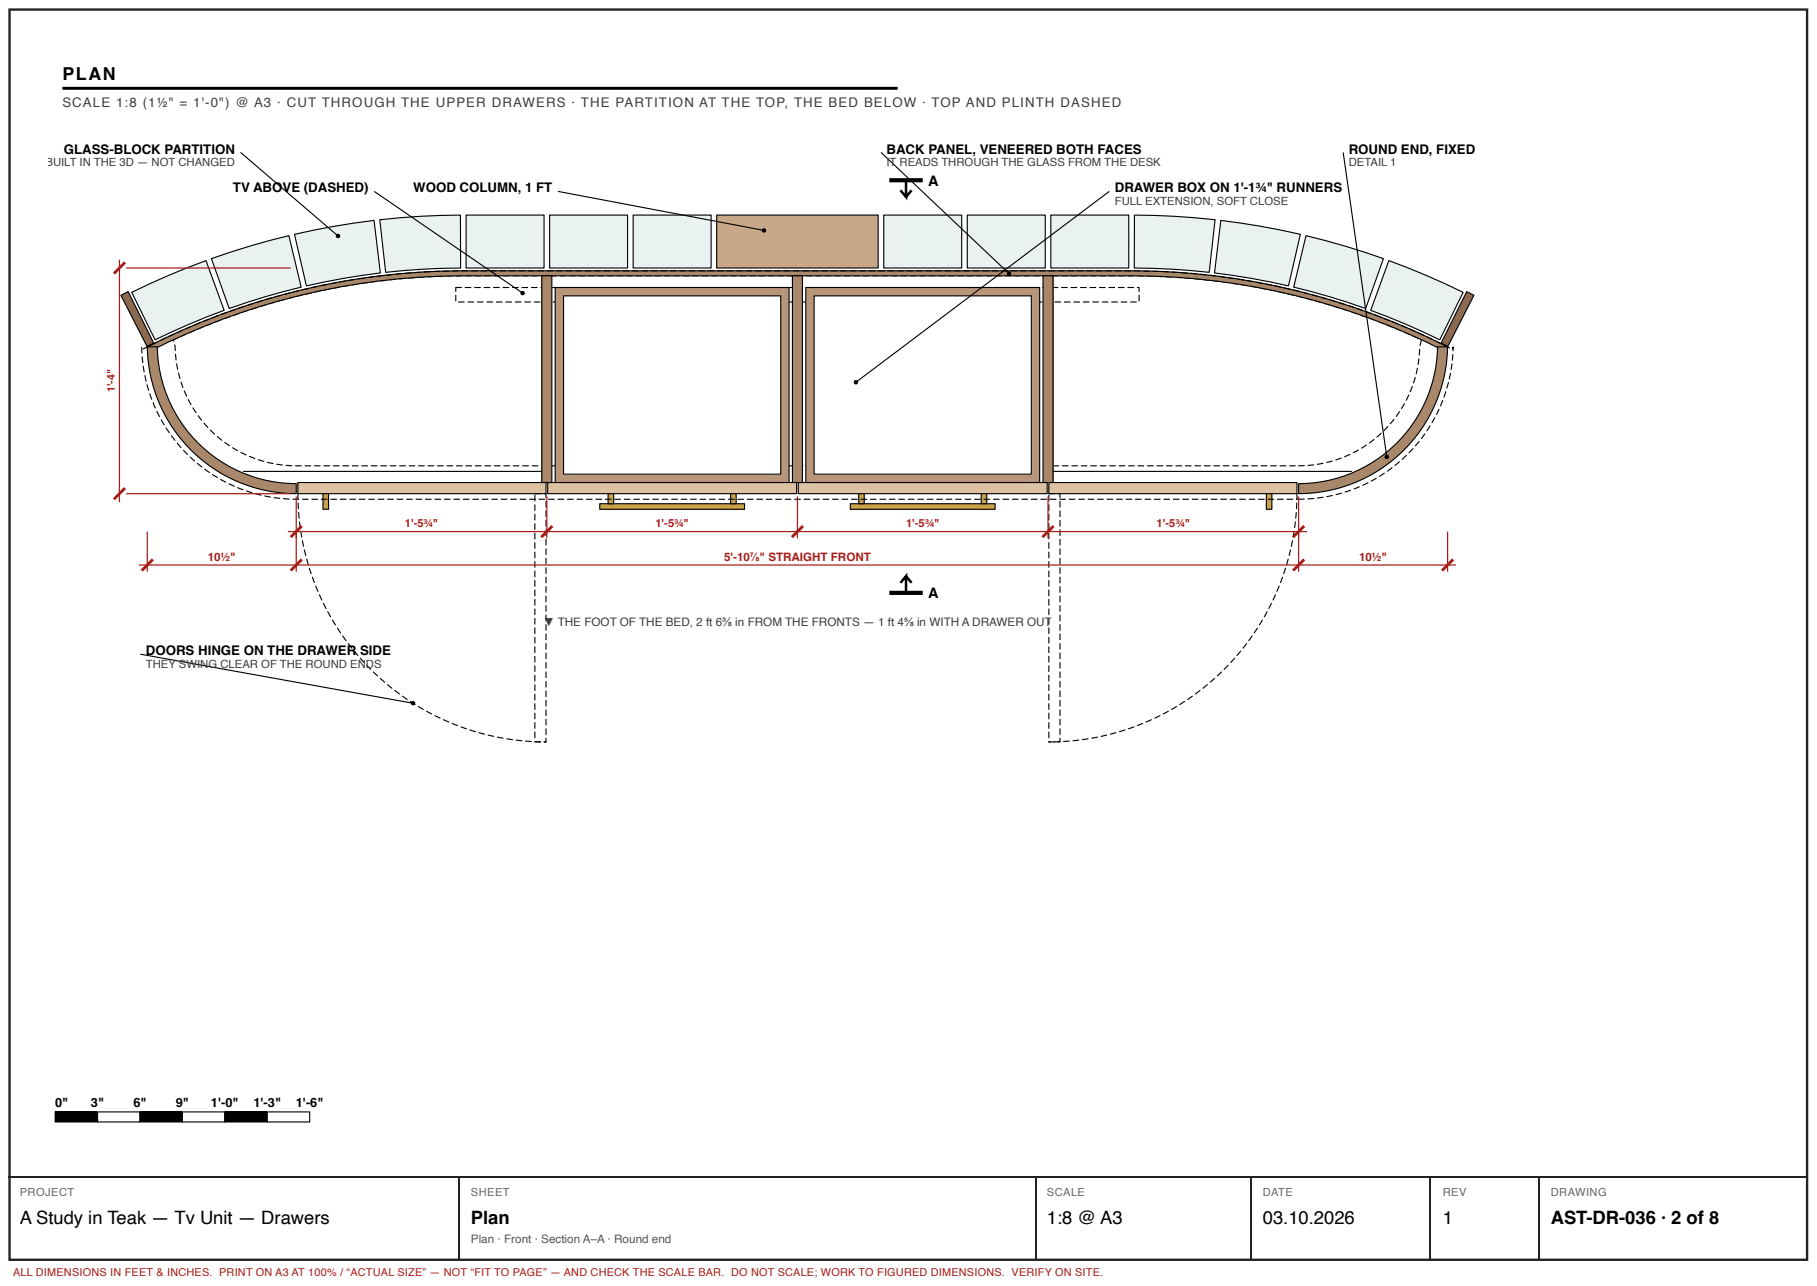
[picture p155: page 2]
5'-10⅞" STRAIGHT FRONT; TV ABOVE (DASHED); WOOD COLUMN, 1 FT; Plan

SCALE 1:8 (1½" = 1'-0") @ A3 · CUT THROUGH THE UPPER DRAWERS · THE PARTITION AT THE TOP, THE BED BELOW · TOP AND PLINTH DASHED

GLASS-BLOCK PARTITION
BUILT IN THE 3D — NOT CHANGED

BACK PANEL, VENEERED BOTH FACES
IT READS THROUGH THE GLASS FROM THE DESK

ROUND END, FIXED
DETAIL 1

DRAWER BOX ON 1'-1¾" RUNNERS
FULL EXTENSION, SOFT CLOSE

▼ THE FOOT OF THE BED, 2 ft 6⅜ in FROM THE FRONTS — 1 ft 4⅝ in WITH A DRAWER OUT

DOORS HINGE ON THE DRAWER SIDE
THEY SWING CLEAR OF THE ROUND ENDS

AST-DR-036 · 2 of 8

Plan · Front · Section A–A · Round end

# SECTION A–A

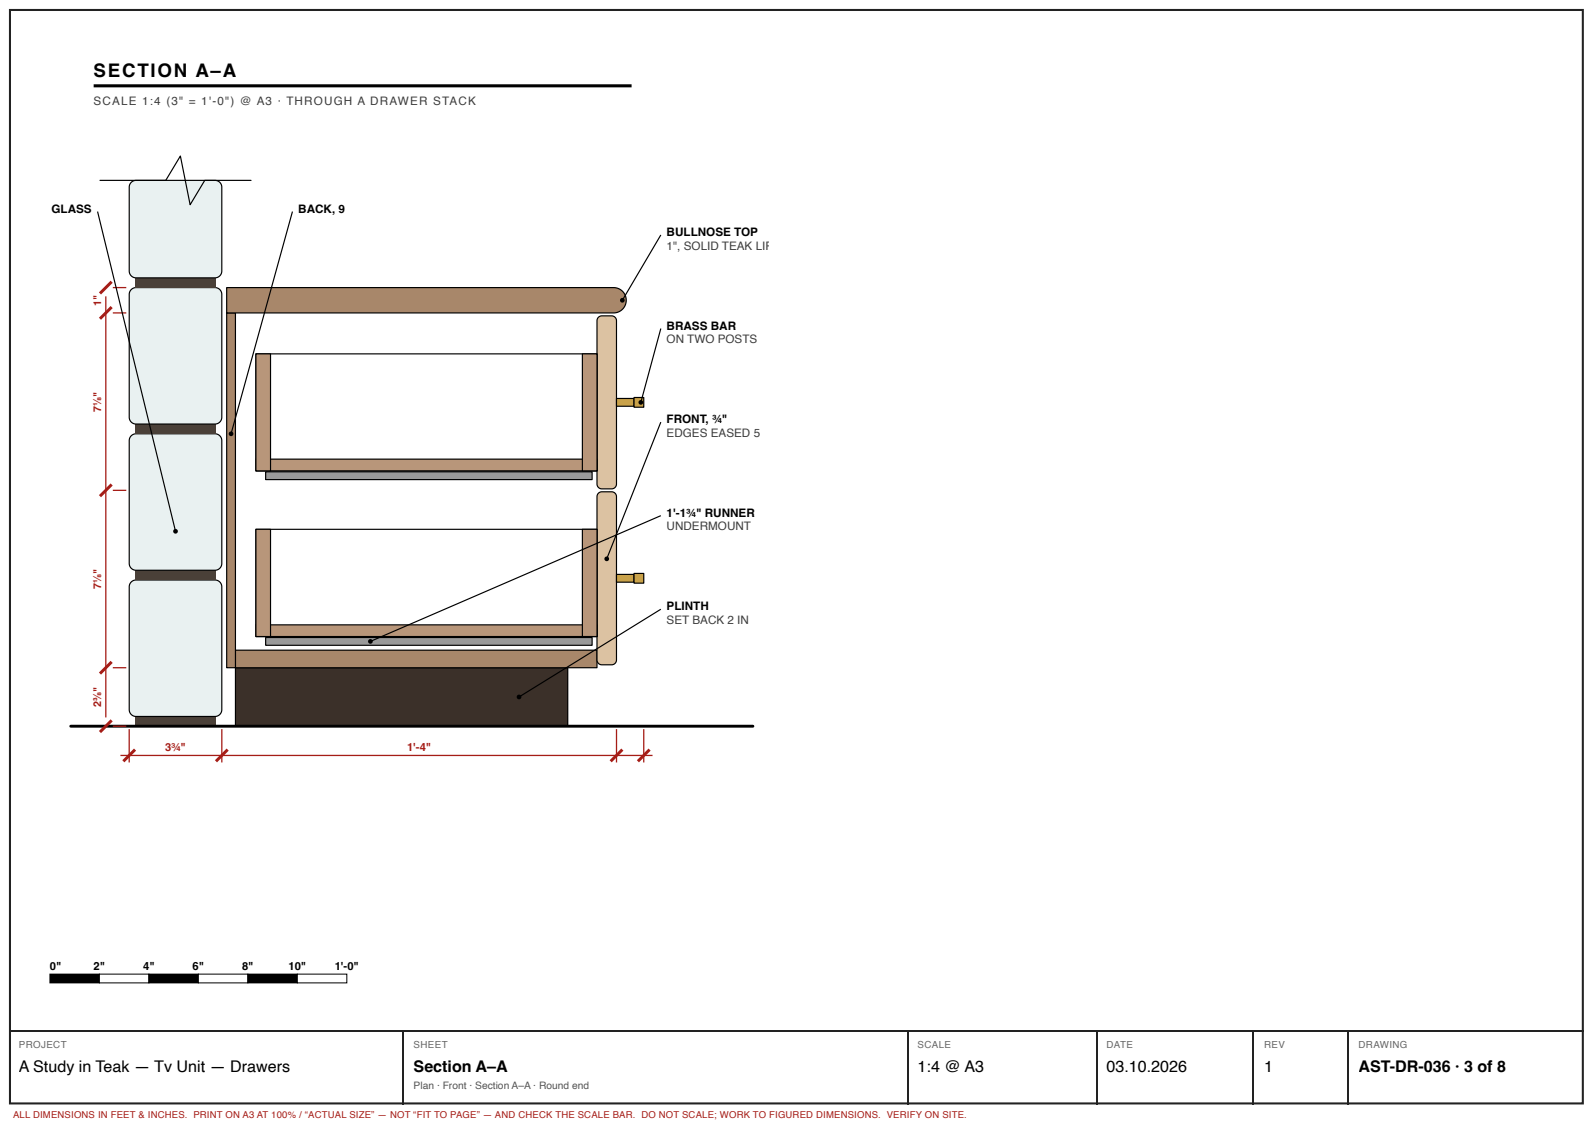
[picture p156: page 3]
FRONT, ¾" EDGES EASED 5; 1'-1¾" RUNNER UNDERMOUNT; GLASS; BACK, 9; Section A–A

SCALE 1:4 (3" = 1'-0") @ A3 · THROUGH A DRAWER STACK

BULLNOSE TOP
1", SOLID TEAK LIP

BRASS BAR
ON TWO POSTS

PLINTH
SET BACK 2 IN

AST-DR-036 · 3 of 8

## FRONT

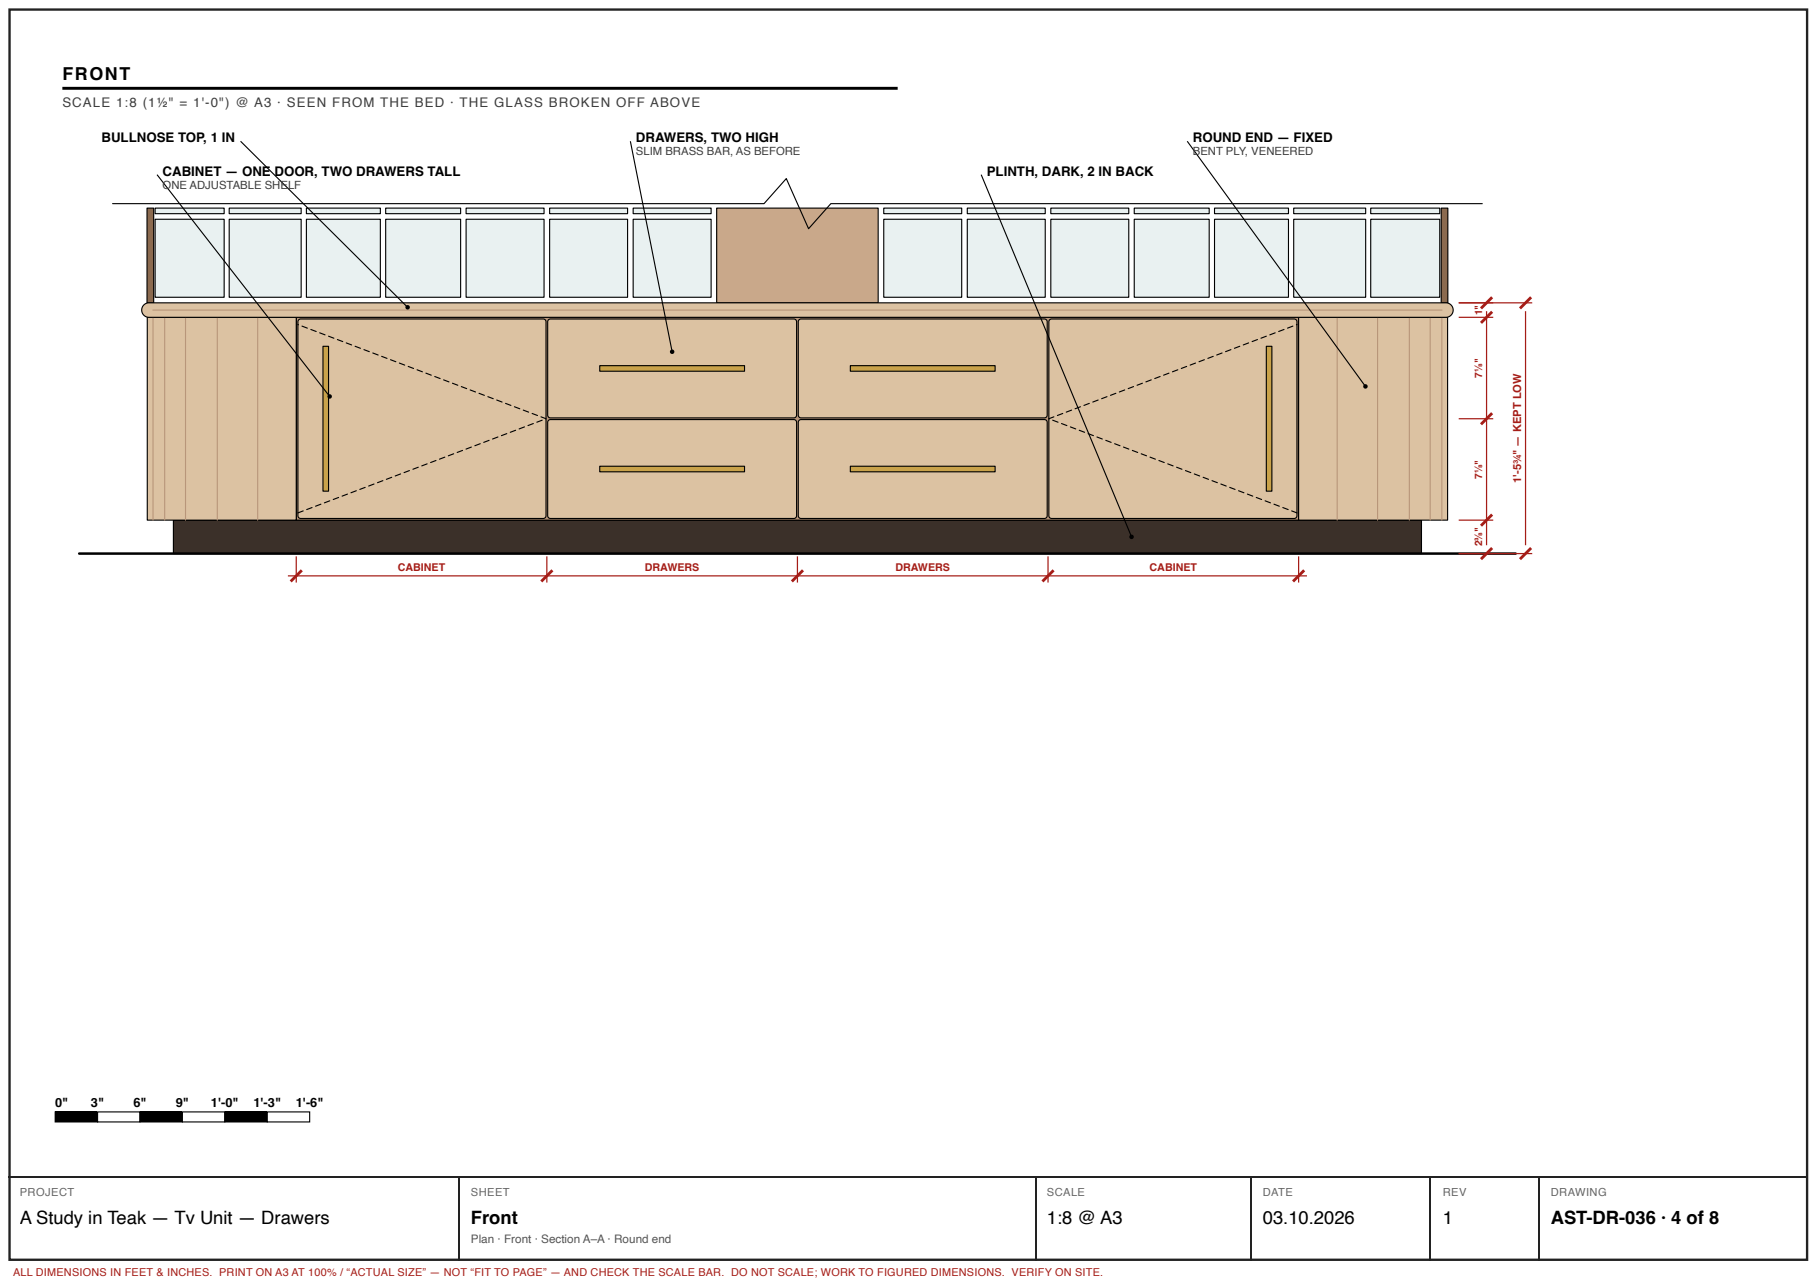
[picture p157: page 4]
CABINET; DRAWERS; KEPT LO; Front

SCALE 1:8 (1½" = 1'-0") @ A3 · SEEN FROM THE BED · THE GLASS BROKEN OFF ABOVE

BULLNOSE TOP, 1 IN

DRAWERS, TWO HIGH
SLIM BRASS BAR, AS BEFORE

ROUND END — FIXED
BENT PLY, VENEERED

CABINET — ONE DOOR, TWO DRAWERS TALL
ONE ADJUSTABLE SHELF

PLINTH, DARK, 2 IN BACK

AST-DR-036 · 4 of 8

# DETAIL 1 · THE ROUND END

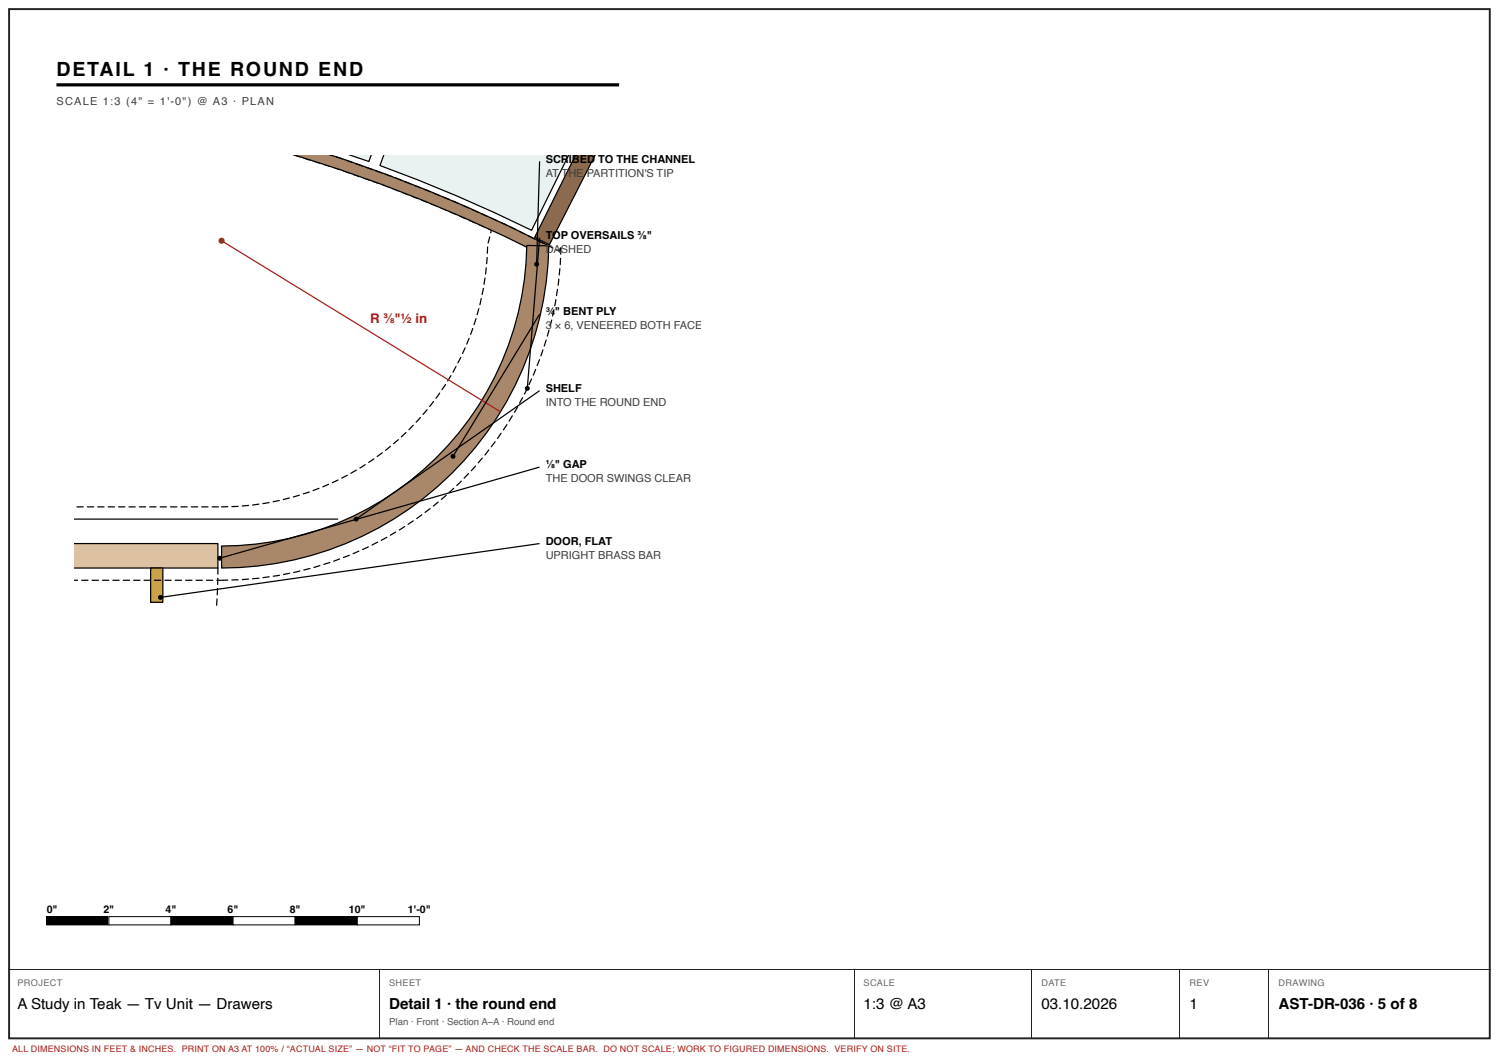
[picture p158: page 5]
SCALE 1:3 (4" = 1'-0") @ A3 · PLAN; TOP OVERSAILS ⅜" DASHED

SCRIBED TO THE CHANNEL
AT THE PARTITION'S TIP

¾" BENT PLY
3 × 6, VENEERED BOTH FACE

SHELF
INTO THE ROUND END

⅛" GAP
THE DOOR SWINGS CLEAR

DOOR, FLAT
UPRIGHT BRASS BAR

Detail 1 · the round end

AST-DR-036 · 5 of 8

# NOTES

# REVISION 1

# From the owner's sketch. The run of 4 × 2 drawers that followed the

# partition's curve could not open at its curved ends. Now the unit is a pill:

# a straight front across the middle, a quarter-round at each end wrapping

back to the partition's tip, and nothing that moves is curved.

# Four equal bays, 17¾ in: two stacks of two drawers in the middle, and at

each end one cabinet two drawers tall behind a flat door (owner).

Doors hinge on the drawer side, so they open away from the round ends.

## Notes

## AST-DR-036 · 6 of 8

# ASSUMED

# TELL ME IF ANY OF THESE IS WRONG

Height 1 ft 5¾ in and depth 1 ft 3¾ in, as the last run.

# The same veneer as before: the 9292 burl in the Dark Diva

colour, the grain running on across all four bays.

The slim brass bar kept; an upright one on each door.

Every edge eased ¼"; the top a full bullnose.

Concealed soft-close hinges; one shelf in each cabinet.

## Assumed

## AST-DR-036 · 7 of 8

# TO DECIDE

# Fronts: eased edges as drawn, or rounder —

# each front a small pill of its own?

Pulls: the brass bar, or push-to-open with none.

# With a drawer out, 1 ft 4⅝ in is left to the bed's

foot — fine to pass, tight to kneel at.

## To decide

## AST-DR-036 · 8 of 8
