sakshampan733-cloud/a-study-in-teak/cad/print/bedwall-a4.pdf

ELEVATION — THE BED WALL

SEEN FROM THE ROOM · DRESSING CORNER LEFT, ENTRANCE CORNER RIGHT

2'-0"

7" COVE

9'-4" NICHE

7" COVE

3'-0"

15'-6" BED WALL

4" 6'-2" PANELS

7" COVE

2'-0"

9'-1" CEILING

DARK DIVA VENEER — WHOLE WALL, DARKER POLISH

### 6 IN COVE + 1 IN EDGE ROUND THE NICHE — 3 IN OUT TO ⅝" IN

PARCHMENT PLASTER — BACK IN 5 × 3 PANELS

THE NICHE'S SIDES AND SOFFIT PLAIN PARCHMENT TOO

LONG WHITE CUSHION

NO HEADBOARD — AST-DR-035

ENTRANCE DOOR OPEN (DASHED)

LIES IN FRONT OF THE 3 IN ZONE

SIDE TABLE

WALL LAMP, EACH SIDE

BRASS TWIN-ARM, AS THE RIGHT WALL

A

PLAN

CUT AT 4 FT · THE BED WALL AT THE TOP, THE ROOM BELOW

3"

1'-4"

7"

CLASH — SEE DETAIL 2

DOOR LEAF vs THE 3 IN FACE

ENTRANCE DOOR, 3 FT

OPENS FLAT ALONG THIS WALL

DRESSING DOOR

2 FT 3 IN FROM THE CORNER

BED 6 FT × 6 FT 6

A

SECTION A–A

THROUGH THE BED

2'-0" 7" 6'-6" NICHE

3" | 6"

7" 4" 10" 1'-4⅝"

6'-11¾" WALL TO FOOT

COVE OVER THE NICHE, 6 IN RADIUS

BENT PLY ON FORMERS, VENEERED

PARCHMENT PLASTER

BACK, SIDES AND SOFFIT, ON ½" BOARD

LONG WHITE CUSHION

LOOSE · LEANS ON THE PLASTER

DETAIL 2 · THE ENTRANCE CORNER

PLAN · THE DOOR vs THE 3 IN FACE

⅛" IN
0" IN

1

2

3

4

### 1 AS SKETCHED — the open leaf hits the 3 in face: its hinge pin

stands only 2 in off the wall (red).

2 FIX A — projecting (parliament) hinges throw the pin out 1¼ in;

the leaf clears and still opens flat (dashed).

3 Floor stop — keeps the knob off the veneer.

4 FIX B — 1½ in at this corner instead of 3 in: ordinary hinges clear.

ASSUMED

TELL ME IF ANY OF THESE IS WRONG

Niche 9 ft 4 in wide — the old bed-back span — and ⅝" in deep.

Five panels across and three up, as sketched:

each about 1 ft 10⅜ × 2 ft ⅝ in — nearly square.

The 4 in white marble skirting runs along the build-out

and into the niche.

The build-out runs to the ceiling.

Side tables ⅝" in wide, ⅝" in deep, 1" in high, all wood.

Bed and cushion heights: AST-DR-035.
NOTES

REVISION 4

From the owner's sketches and photo. The whole wall is built out 3 in in Dark Diva

veneer, polished darker, on a ply carcase. Round the niche it sweeps forward in a

6 in concave cove to ⅝" in at the niche's edge — up both sides and across the top.

The niche — bed and both tables — is ⅝" in deep, all parchment plaster: its back in

5 × 3 panels, its two sides and soffit plain (owner).

The build-out is set square to the bed's centre line and scribed at both corners,

so it also hides the room's 2 in splay. The niche is the old bed-back span, centred

on the TV; the cove stops where the open door's leaf ends. Cove light: in the ceiling.

No headboard: a long white cushion along the back (owner). A brass wall lamp each side.

The bed is drawn on AST-DR-035.

PROBLEMS FOUND

TO DECIDE

1 · DOOR — not its 3 ft, which is kept clear, but the DEPTH: D1's hinge pin

is 2 in off this wall, so a 3 in face there stops it opening flat (detail 2).

Projecting hinges (A), or 1½ in deep at that corner (B).

2 · The bed comes 3½ in further out (its frame runs 2 in past the mattress

all round): 2 ft 6⅜ in left to the TV drawers instead of 2 ft 9¾ in.

3 · Lamp sockets and switches go through the plaster panels — fix their

places (list item B2) before the panels are made.

DECIDED: the cove light stays in the ceiling; no other light on this wall

but the two wall lamps over the side tables (owner).

A S T U D Y I N T E A K

Particulars of the room

BED WALL — THE NICHE

Elevation · Plan · Section · The entrance corner

SCALE

AS NOTED @ A3

DATE

03.10.2026

REV

4 — niche 16 in deep, the side tables inside it; no headboard

DWG

AST-DR-034

PROJECT

# A Study in Teak — Bed Wall — the Niche

SHEET

# General arrangement — the whole sheet

each view follows at its own scale, pages 2 to 8

SCALE

# NTS

DATE
03.10.2026

REV

DRAWING

# AST-DR-034 · 1 of 8

ALL DIMENSIONS IN FEET & INCHES. PRINT ON A4 AT 100% / “ACTUAL SIZE” — NOT “FIT TO PAGE” — AND CHECK THE SCALE BAR. DO NOT SCALE; WORK TO FIGURED DIMENSIONS. VERIFY ON SITE.

## ELEVATION — THE BED WALL

A

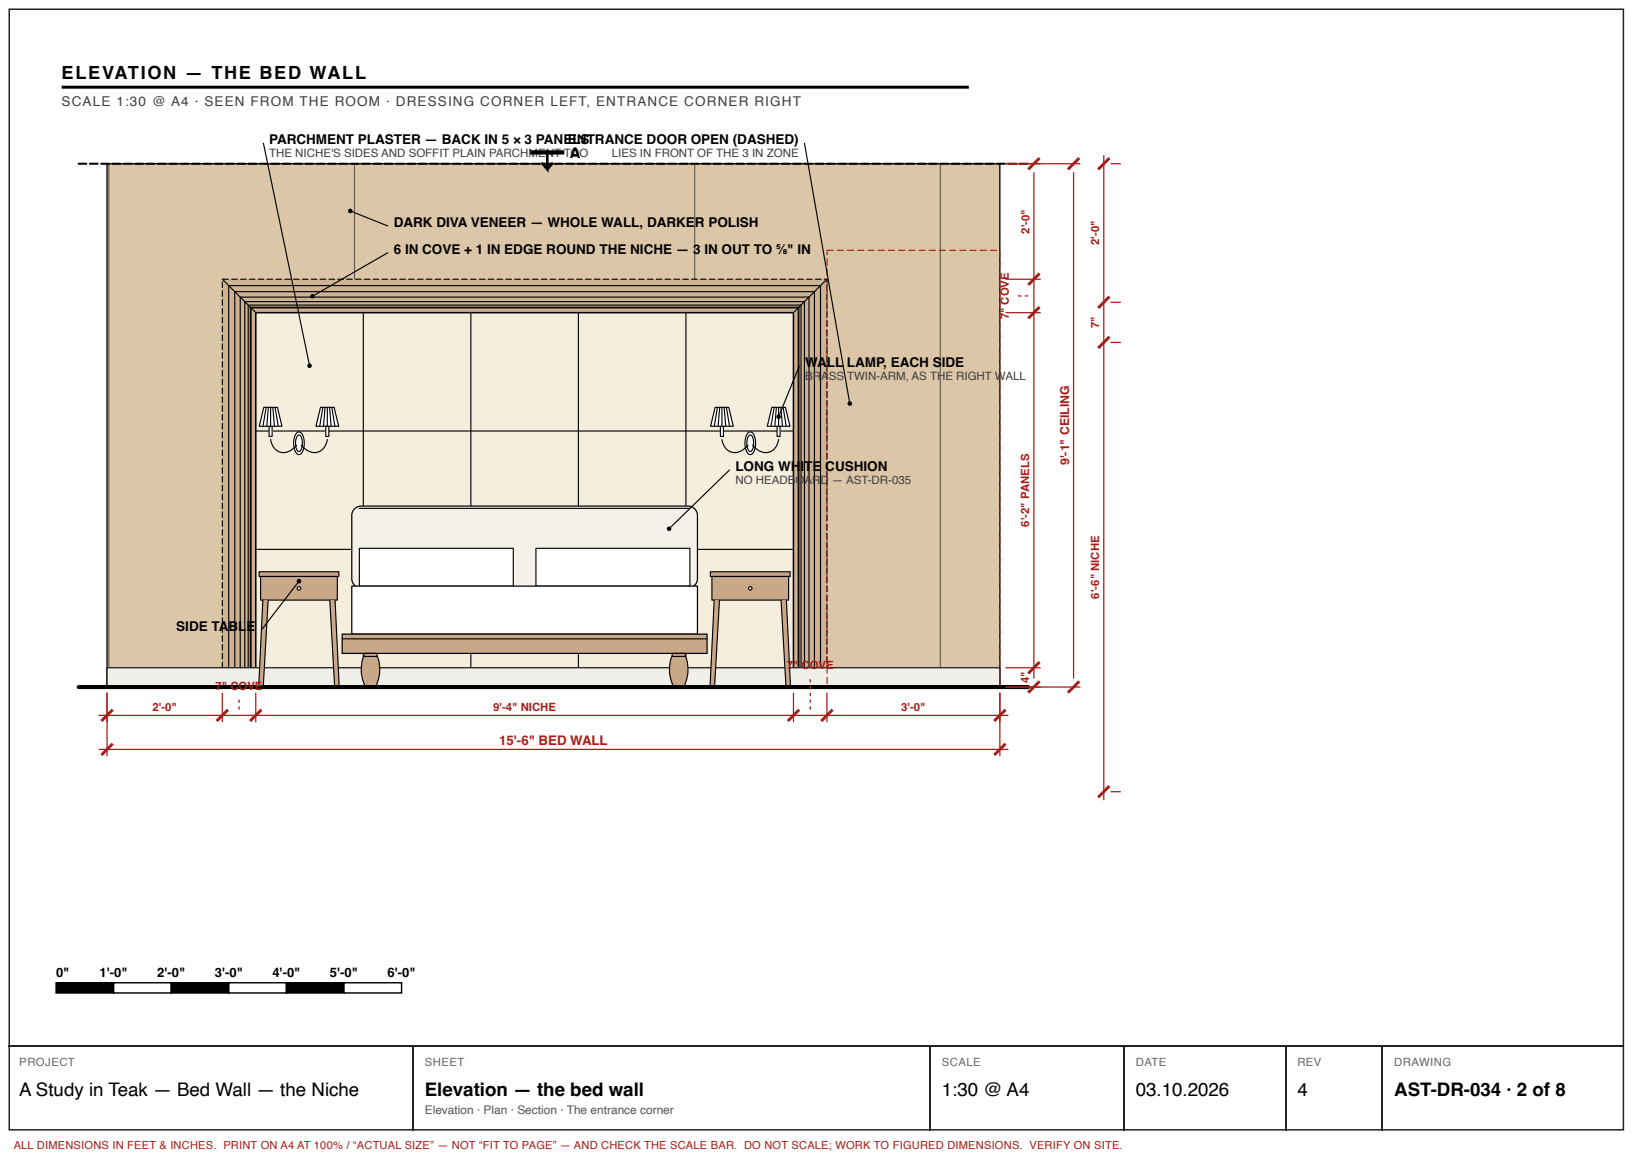
[picture p159: page 2]
7" COVE; 9'-4" NICHE; 15'-6" BED WALL; 4" 6'-2" PANELS; 9'-1" CEILING; SIDE TABLE; 2'-0" 7" 6'-6" NICHE

SCALE 1:30 @ A4 · SEEN FROM THE ROOM · DRESSING CORNER LEFT, ENTRANCE CORNER RIGHT

PARCHMENT PLASTER — BACK IN 5 × 3 PANELS
THE NICHE'S SIDES AND SOFFIT PLAIN PARCHMENT TOO

ENTRANCE DOOR OPEN (DASHED)

LIES IN FRONT OF THE 3 IN ZONE

DARK DIVA VENEER — WHOLE WALL, DARKER POLISH
6 IN COVE + 1 IN EDGE ROUND THE NICHE — 3 IN OUT TO ⅝" IN

WALL LAMP, EACH SIDE
BRASS TWIN-ARM, AS THE RIGHT WALL

LONG WHITE CUSHION
NO HEADBOARD — AST-DR-035

Elevation — the bed wall

AST-DR-034 · 2 of 8

Elevation · Plan · Section · The entrance corner

# SECTION A–A

### SCALE 1:24 (½" = 1'-0") @ A4 · THROUGH THE BED

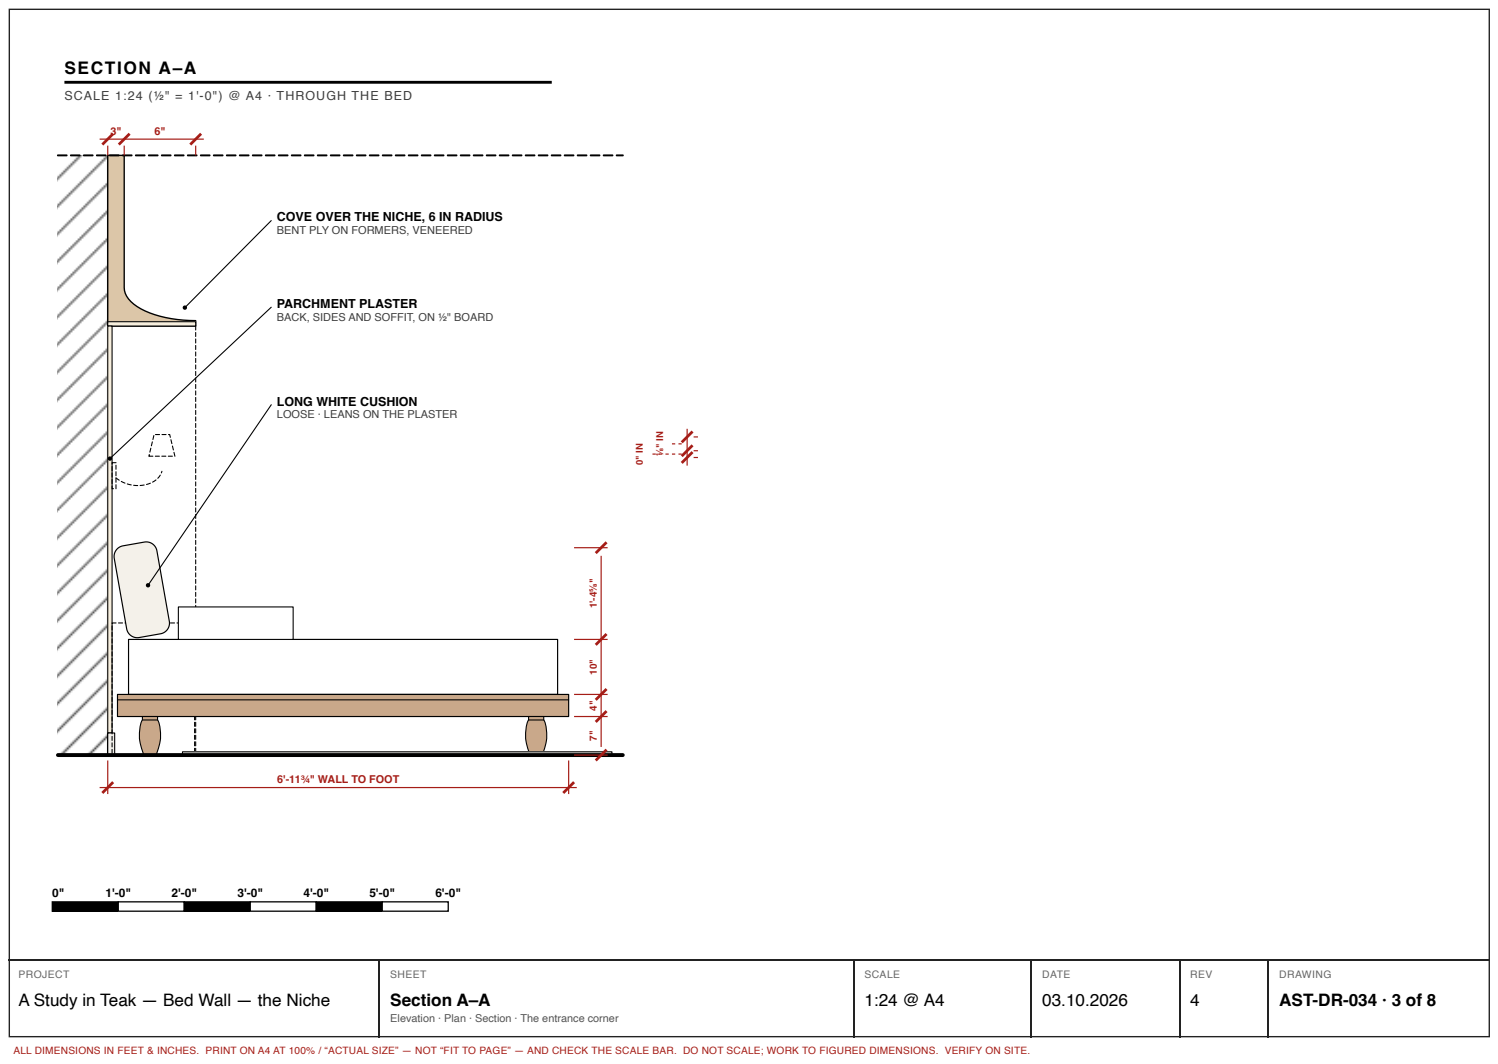
[picture p160: page 3]
Section A–A

COVE OVER THE NICHE, 6 IN RADIUS
BENT PLY ON FORMERS, VENEERED

PARCHMENT PLASTER
BACK, SIDES AND SOFFIT, ON ½" BOARD

LONG WHITE CUSHION
LOOSE · LEANS ON THE PLASTER

6'-11¾" WALL TO FOOT

AST-DR-034 · 3 of 8

# P R O B L E M S F O U N D

# TO DECIDE

# 1 · DOOR — not its 3 ft, which is kept clear, but the DEPTH: D1's hinge pin

is 2 in off this wall, so a 3 in face there stops it opening flat (detail 2).

Projecting hinges (A), or 1½ in deep at that corner (B).

# 2 · The bed comes 3½ in further out (its frame runs 2 in past the mattress

all round): 2 ft 6⅜ in left to the TV drawers instead of 2 ft 9¾ in.

# 3 · Lamp sockets and switches go through the plaster panels — fix their

places (list item B2) before the panels are made.

# DECIDED: the cove light stays in the ceiling; no other light on this wall

but the two wall lamps over the side tables (owner).

# Problems found

# AST-DR-034 · 4 of 8

# DETAIL 2 · THE ENTRANCE CORNER

### SCALE 1:15 @ A4 · PLAN · THE DOOR vs THE 3 IN FACE

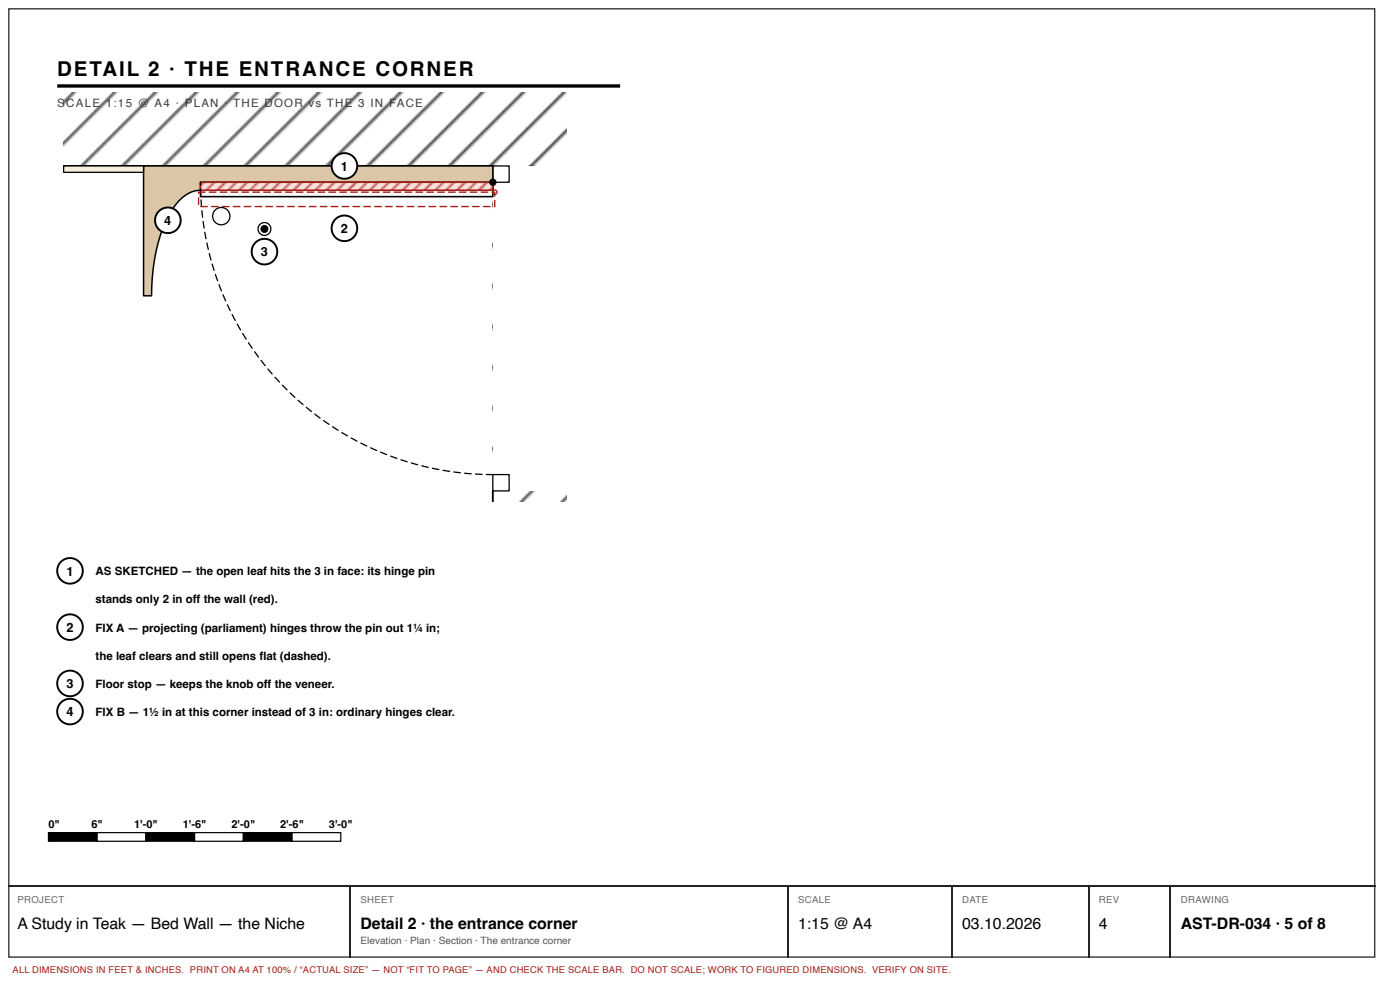
[picture p161: page 5]

1 AS SKETCHED — the open leaf hits the 3 in face: its hinge pin

stands only 2 in off the wall (red).

2 FIX A — projecting (parliament) hinges throw the pin out 1¼ in;

the leaf clears and still opens flat (dashed).

3 Floor stop — keeps the knob off the veneer.

4 FIX B — 1½ in at this corner instead of 3 in: ordinary hinges clear.

Detail 2 · the entrance corner

AST-DR-034 · 5 of 8

# PLAN

### SCALE 1:24 (½" = 1'-0") @ A4 · CUT AT 4 FT · THE BED WALL AT THE TOP, THE ROOM BELOW

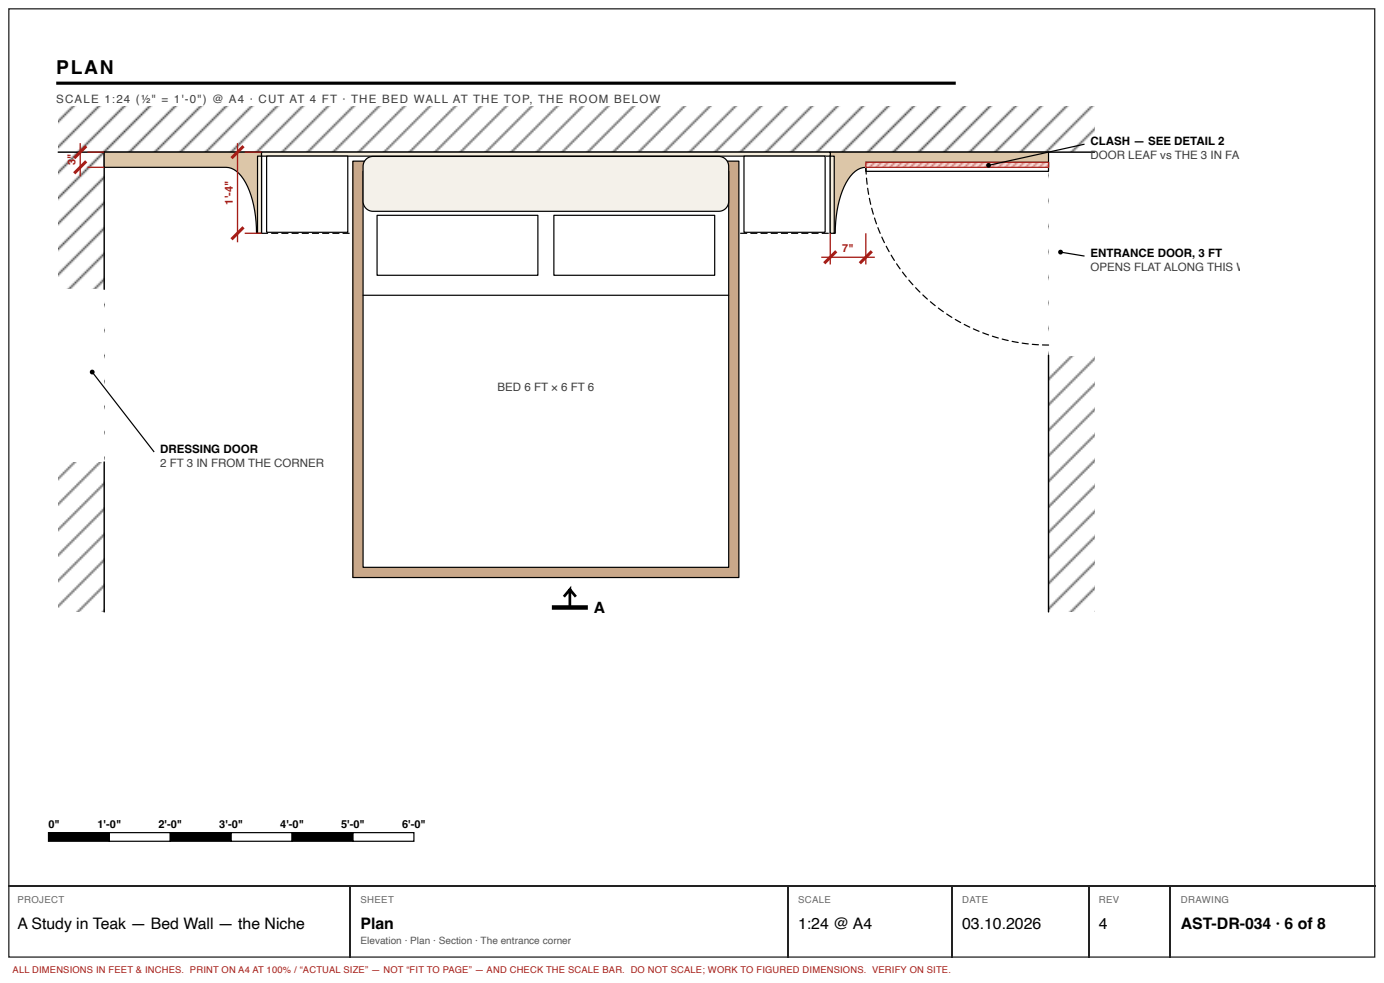
[picture p162: page 6]
Plan

CLASH — SEE DETAIL 2
DOOR LEAF vs THE 3 IN FA

ENTRANCE DOOR, 3 FT
OPENS FLAT ALONG THIS W

BED 6 FT × 6 FT 6

DRESSING DOOR
2 FT 3 IN FROM THE CORNER

AST-DR-034 · 6 of 8

# A SS U M E D

# TELL ME IF ANY OF THESE IS WRONG

Niche 9 ft 4 in wide — the old bed-back span — and ⅝" in deep.

# Five panels across and three up, as sketched:

each about 1 ft 10⅜ × 2 ft ⅝ in — nearly square.

# The 4 in white marble skirting runs along the build-out

and into the niche.

The build-out runs to the ceiling.

Side tables ⅝" in wide, ⅝" in deep, 1" in high, all wood.

Bed and cushion heights: AST-DR-035.

# Assumed

# AST-DR-034 · 7 of 8

# N O TES

# REVISION 4

# From the owner's sketches and photo. The whole wall is built out 3 in in Dark Diva

# veneer, polished darker, on a ply carcase. Round the niche it sweeps forward in a

6 in concave cove to ⅝" in at the niche's edge — up both sides and across the top.

# The niche — bed and both tables — is ⅝" in deep, all parchment plaster: its back in

5 × 3 panels, its two sides and soffit plain (owner).

The build-out is set square to the bed's centre line and scribed at both corners,

# so it also hides the room's 2 in splay. The niche is the old bed-back span, centred

on the TV; the cove stops where the open door's leaf ends. Cove light: in the ceiling.

No headboard: a long white cushion along the back (owner). A brass wall lamp each side.

The bed is drawn on AST-DR-035.

# Notes

# AST-DR-034 · 8 of 8
