sakshampan733-cloud/a-study-in-teak/cad/print/desk-plain-a4.pdf

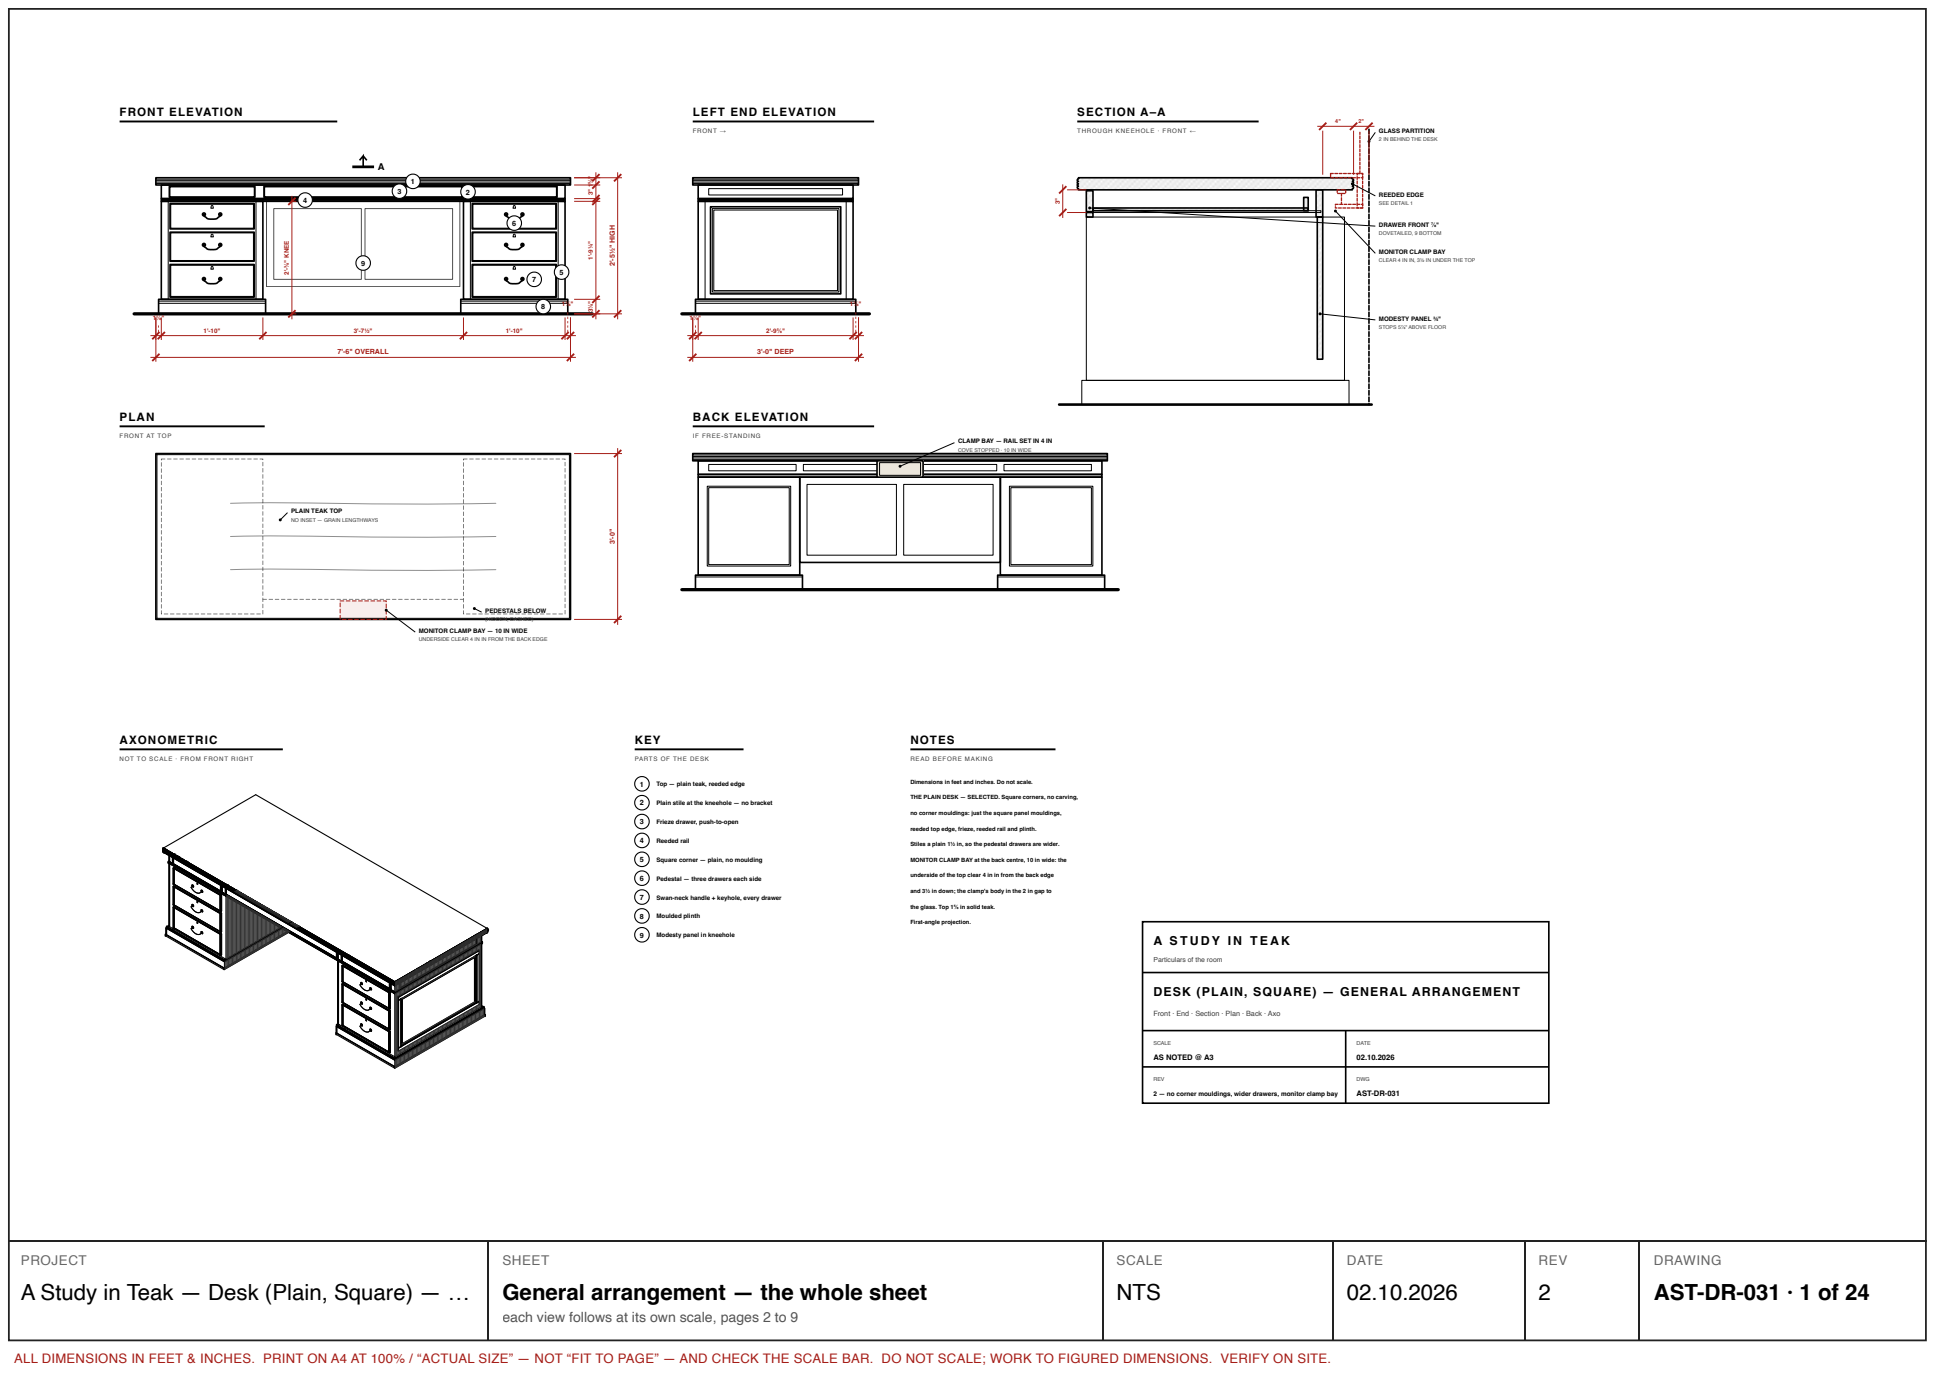
[picture p170: page 1]
FRONT ELEVATION; 7'-6" OVERALL; 2'-5½" HIGH; 2'-⅜" KNEE; FRONT →; 3'-0" DEEP; SECTION A–A; DRAWER FRONT ⅞"; DOVETAILED, 9 BOTTOM; GLASS PARTITION; REEDED EDGE; SEE DETAIL 1; PLAN; PEDESTALS BELOW; (HIDDEN, DASHED); BACK ELEVATION; AXONOMETRIC; KEY; 4 Reeded rail; 8 Moulded plinth; NOTES; SCALE; AS NOTED @ A3; DATE; REV; DWG; AST-DR-031; SCALE NTS; DATE 02.10.2026

LEFT END ELEVATION

THROUGH KNEEHOLE · FRONT ←

2 IN BEHIND THE DESK

MONITOR CLAMP BAY

CLEAR 4 IN IN, 3½ IN UNDER THE TOP

MODESTY PANEL ¾"
STOPS 5⅞" ABOVE FLOOR

FRONT AT TOP

IF FREE-STANDING

CLAMP BAY — RAIL SET IN 4 IN

COVE STOPPED · 10 IN WIDE

PLAIN TEAK TOP
NO INSET — GRAIN LENGTHWAYS

MONITOR CLAMP BAY — 10 IN WIDE

UNDERSIDE CLEAR 4 IN IN FROM THE BACK EDGE

NOT TO SCALE · FROM FRONT RIGHT

PARTS OF THE DESK

READ BEFORE MAKING

1 Top — plain teak, reeded edge

Dimensions in feet and inches. Do not scale.

2 Plain stile at the kneehole — no bracket

THE PLAIN DESK — SELECTED. Square corners, no carving,

no corner mouldings: just the square panel mouldings,

3 Frieze drawer, push-to-open

reeded top edge, frieze, reeded rail and plinth.

Stiles a plain 1½ in, so the pedestal drawers are wider.

5 Square corner — plain, no moulding

MONITOR CLAMP BAY at the back centre, 10 in wide: the

6 Pedestal — three drawers each side

underside of the top clear 4 in in from the back edge

and 3½ in down; the clamp's body in the 2 in gap to

7 Swan-neck handle + keyhole, every drawer

the glass. Top 1⅝ in solid teak.

First-angle projection.

9 Modesty panel in kneehole

Particulars of the room

DESK (PLAIN, SQUARE) — GENERAL ARRANGEMENT

Front · End · Section · Plan · Back · Axo

2 — no corner mouldings, wider drawers, monitor clamp bay

PROJECT
A Study in Teak — Desk (Plain, Square) — …

SHEET
General arrangement — the whole sheet

DRAWING
AST-DR-031 · 1 of 24

each view follows at its own scale, pages 2 to 9

ALL DIMENSIONS IN FEET & INCHES. PRINT ON A4 AT 100% / “ACTUAL SIZE” — NOT “FIT TO PAGE” — AND CHECK THE SCALE BAR. DO NOT SCALE; WORK TO FIGURED DIMENSIONS. VERIFY ON SITE.

# FRONT ELEVATION

A

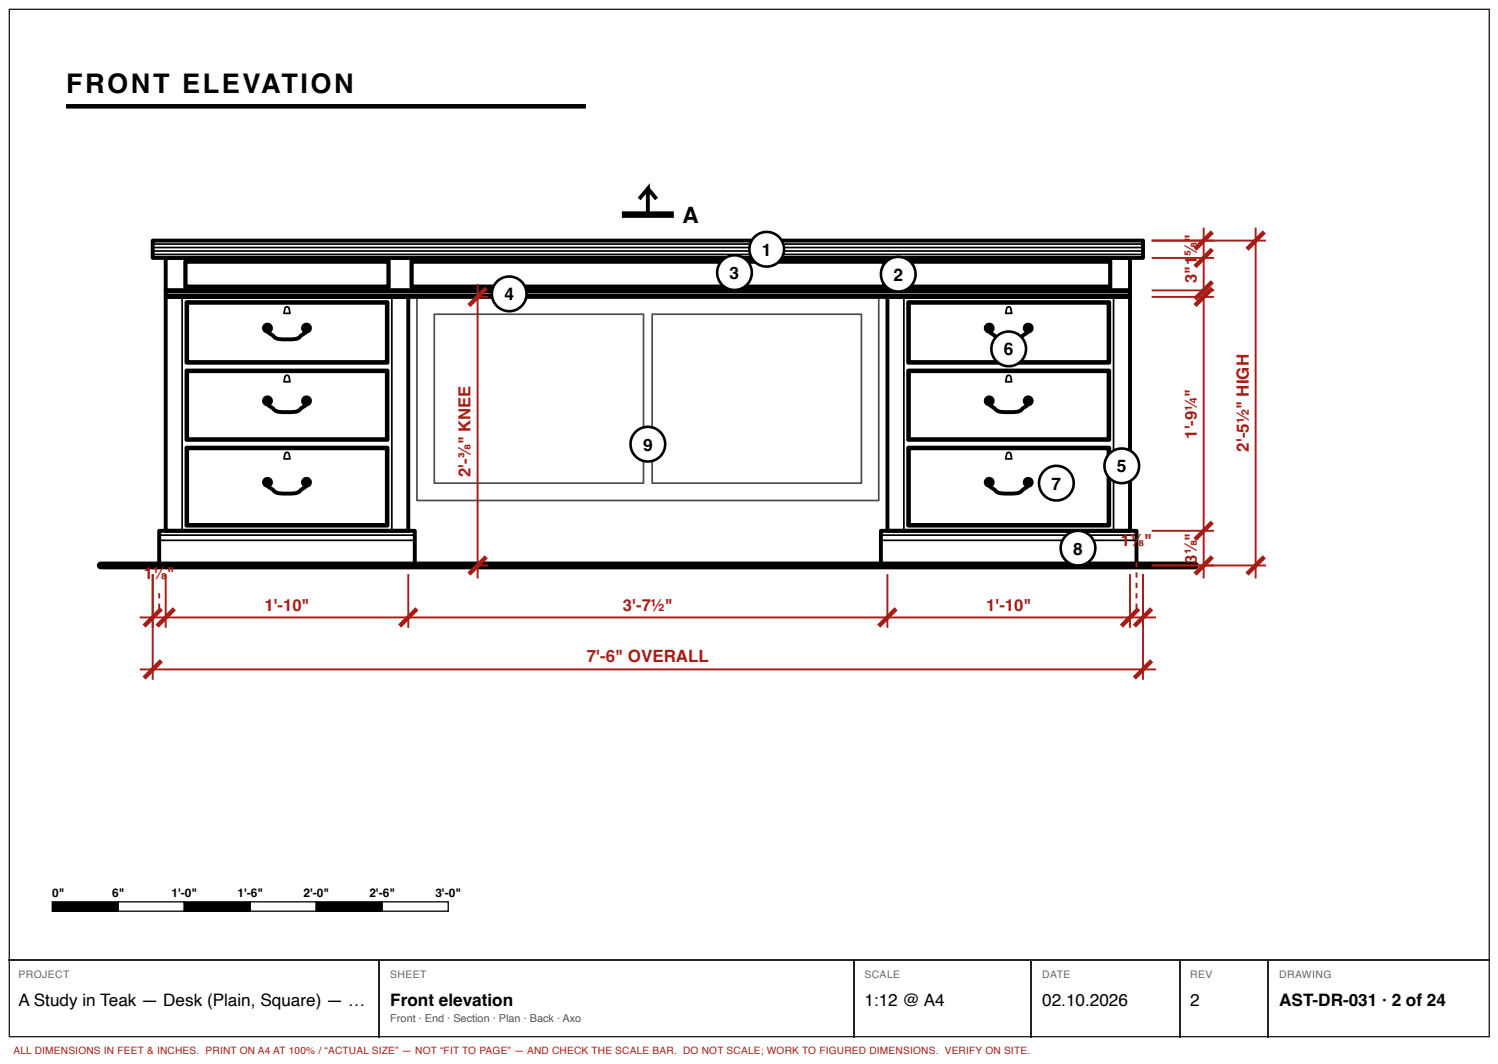
[picture p171: page 2]
7'-6" OVERALL; ½" HIG; Front elevation

AST-DR-031 · 2 of 24

Front · End · Section · Plan · Back · Axo

# LEFT END ELEVATION

# SCALE 1:10 @ A4 · FRONT →

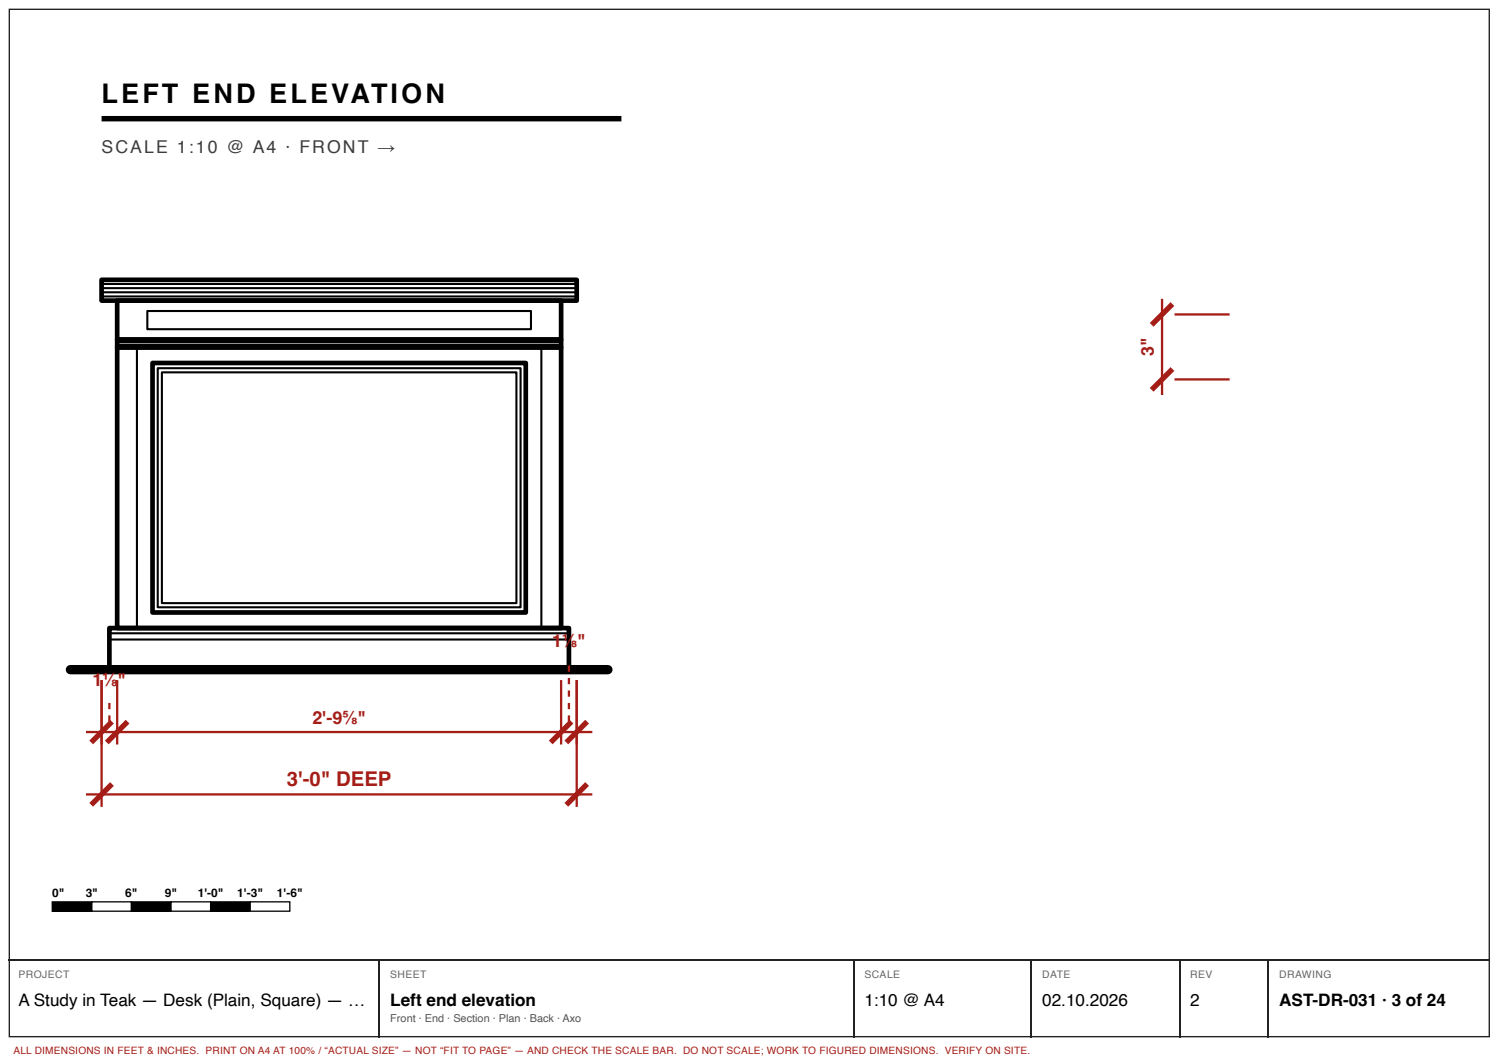
[picture p172: page 3]
3'-0" DEEP

Left end elevation

AST-DR-031 · 3 of 24

Front · End · Section · Plan · Back · Axo

# SECTION A–A

### SCALE 1:8 (1½" = 1'-0") @ A4 · THROUGH KNEEHOLE · FRONT ←

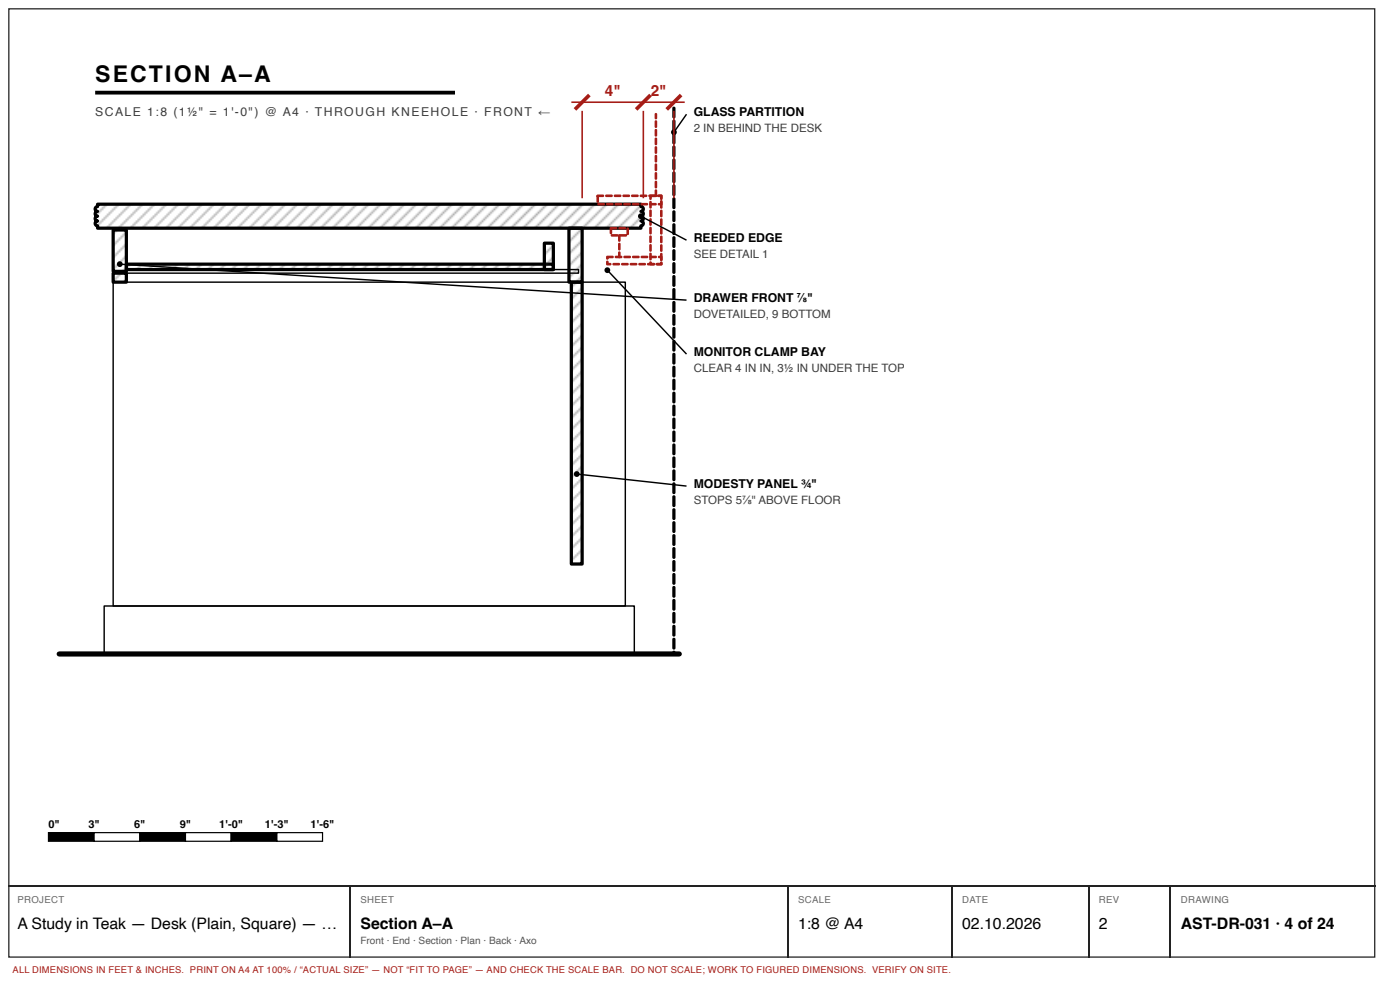
[picture p173: page 4]
DRAWER FRONT ⅞"; DOVETAILED, 9 BOTTOM; REEDED EDGE SEE DETAIL 1; Section A–A

GLASS PARTITION
2 IN BEHIND THE DESK

MONITOR CLAMP BAY
CLEAR 4 IN IN, 3½ IN UNDER THE TOP

MODESTY PANEL ¾"
STOPS 5⅞" ABOVE FLOOR

AST-DR-031 · 4 of 24

Front · End · Section · Plan · Back · Axo

# PLAN

## SCALE 1:12 (1" = 1'-0") @ A4 · FRONT AT TOP

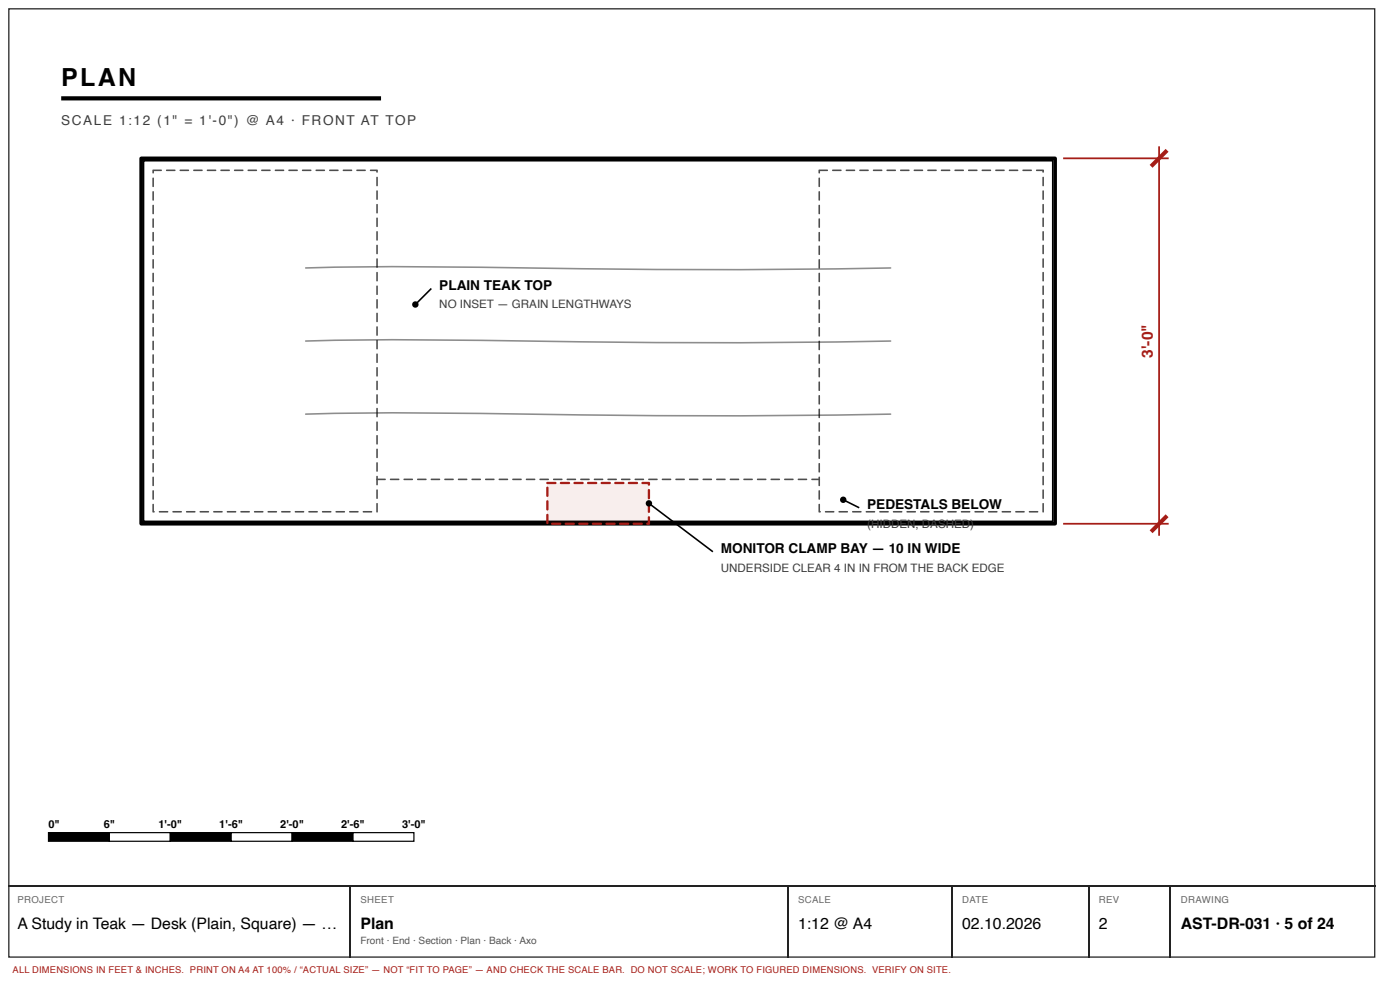
[picture p174: page 5]
PEDESTALS BELOW; (HIDDEN, DASHED); Plan

PLAIN TEAK TOP
NO INSET — GRAIN LENGTHWAYS

MONITOR CLAMP BAY — 10 IN WIDE
UNDERSIDE CLEAR 4 IN IN FROM THE BACK EDGE

AST-DR-031 · 5 of 24

Front · End · Section · Plan · Back · Axo

# BACK ELEVATION

# SCALE 1:10 @ A4 · IF FREE-STANDING

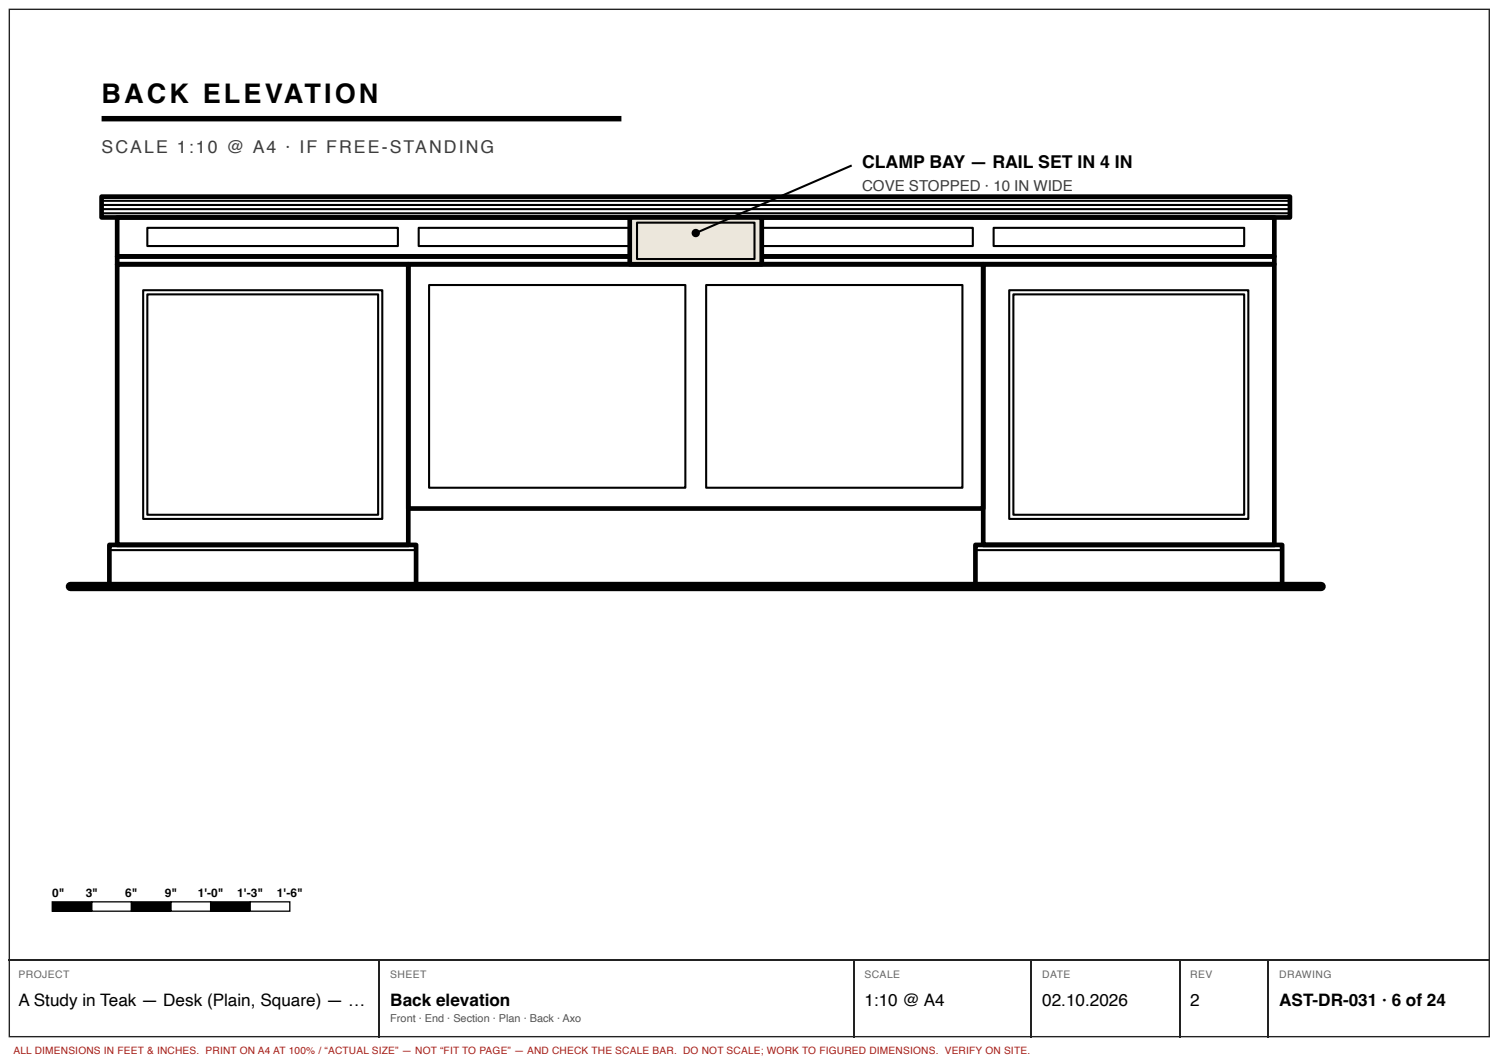
[picture p175: page 6]
Back elevation

CLAMP BAY — RAIL SET IN 4 IN
COVE STOPPED · 10 IN WIDE

AST-DR-031 · 6 of 24

Front · End · Section · Plan · Back · Axo

# AXONOMETRIC

## NOT TO SCALE · NOT TO SCALE · FROM FRONT RIGHT

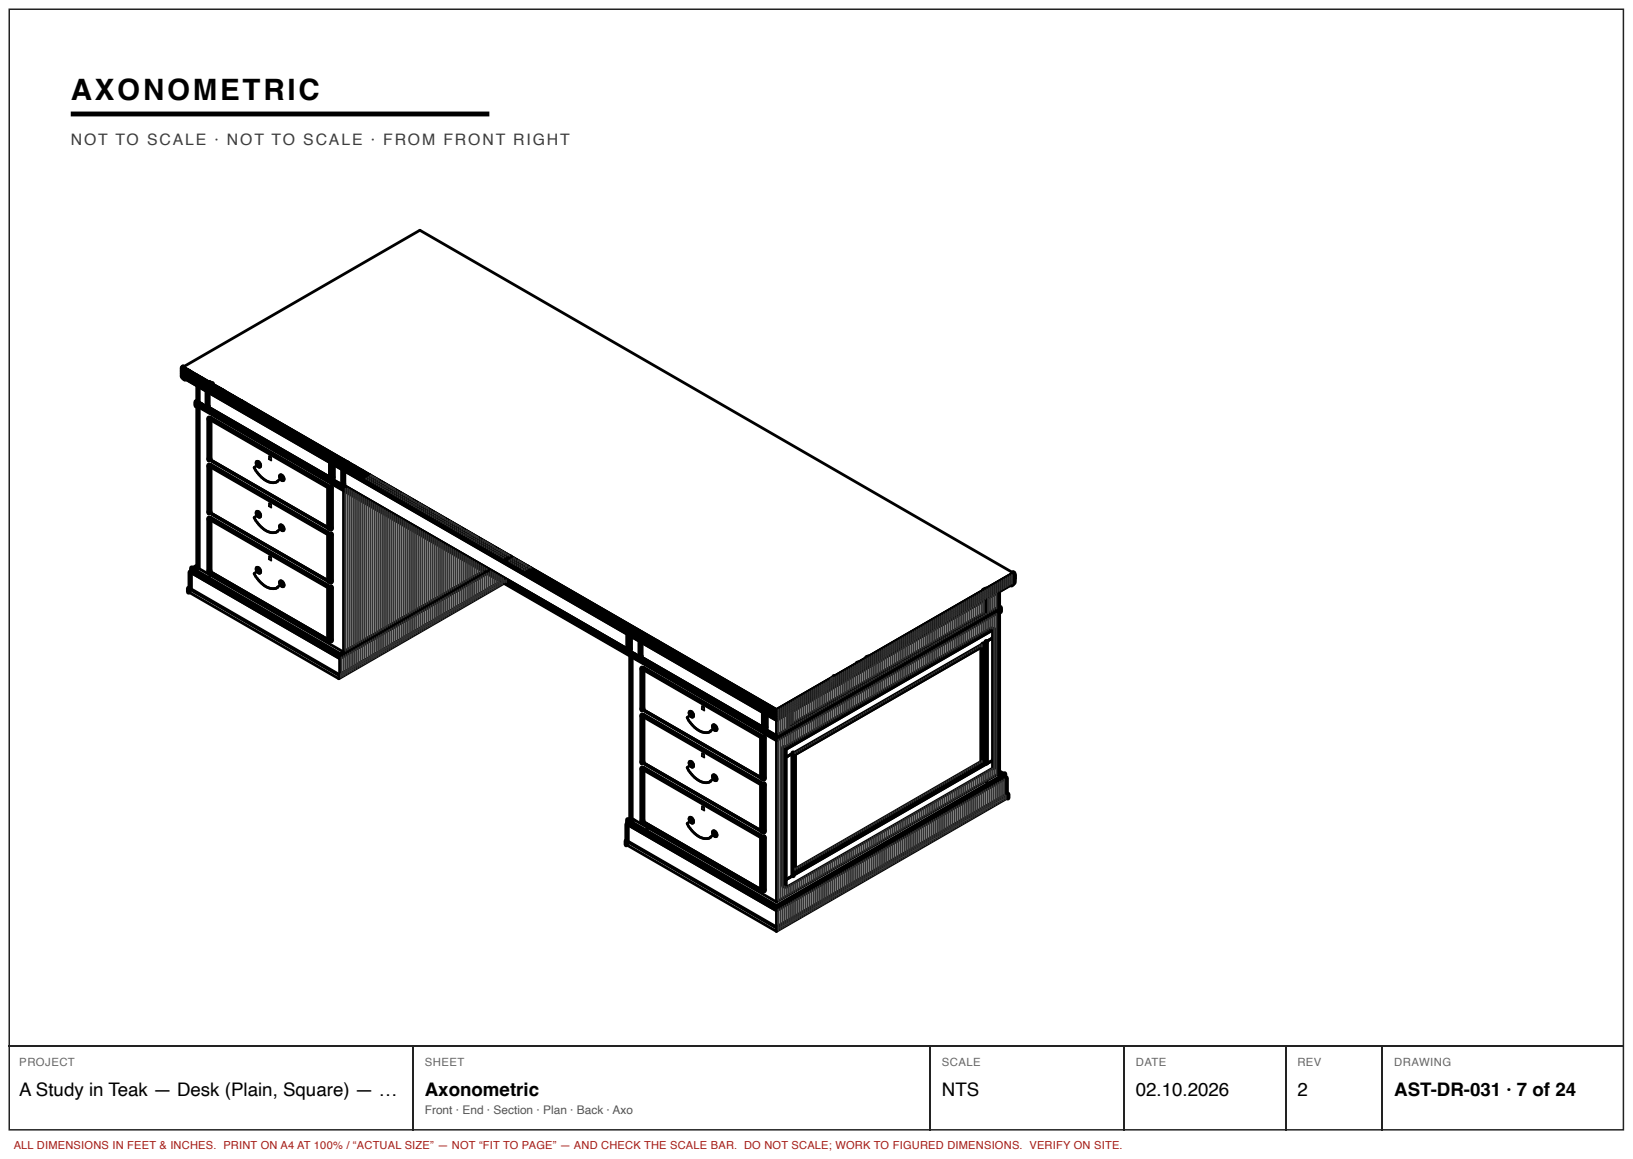
[picture p176: page 7]
Axonometric

AST-DR-031 · 7 of 24

Front · End · Section · Plan · Back · Axo

# K EY

# PARTS OF THE DESK

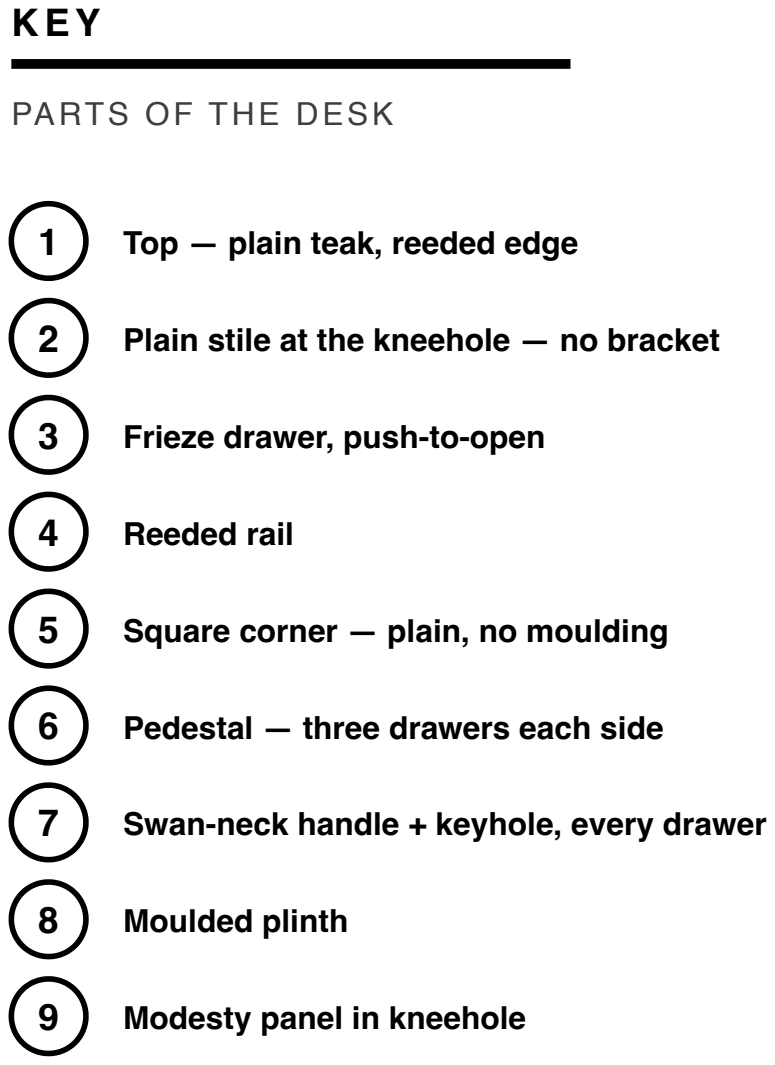
[picture p177: page 8]
4 Reeded rail; 8 Moulded plinth; Key

1 Top — plain teak, reeded edge

2 Plain stile at the kneehole — no bracket

3 Frieze drawer, push-to-open

5 Square corner — plain, no moulding

6 Pedestal — three drawers each side

7 Swan-neck handle + keyhole, every drawer

9 Modesty panel in kneehole

AST-DR-031 · 8 of 24

Front · End · Section · Plan · Back · Axo

# N O TES

# READ BEFORE MAKING

Dimensions in feet and inches. Do not scale.

THE PLAIN DESK — SELECTED. Square corners, no carving,

no corner mouldings: just the square panel mouldings,

reeded top edge, frieze, reeded rail and plinth.

Stiles a plain 1½ in, so the pedestal drawers are wider.

# MONITOR CLAMP BAY at the back centre, 10 in wide: the

# underside of the top clear 4 in in from the back edge

# and 3½ in down; the clamp's body in the 2 in gap to

the glass. Top 1⅝ in solid teak.

First-angle projection.

# Notes

Front · End · Section · Plan · Back · Axo

# AST-DR-031 · 9 of 24

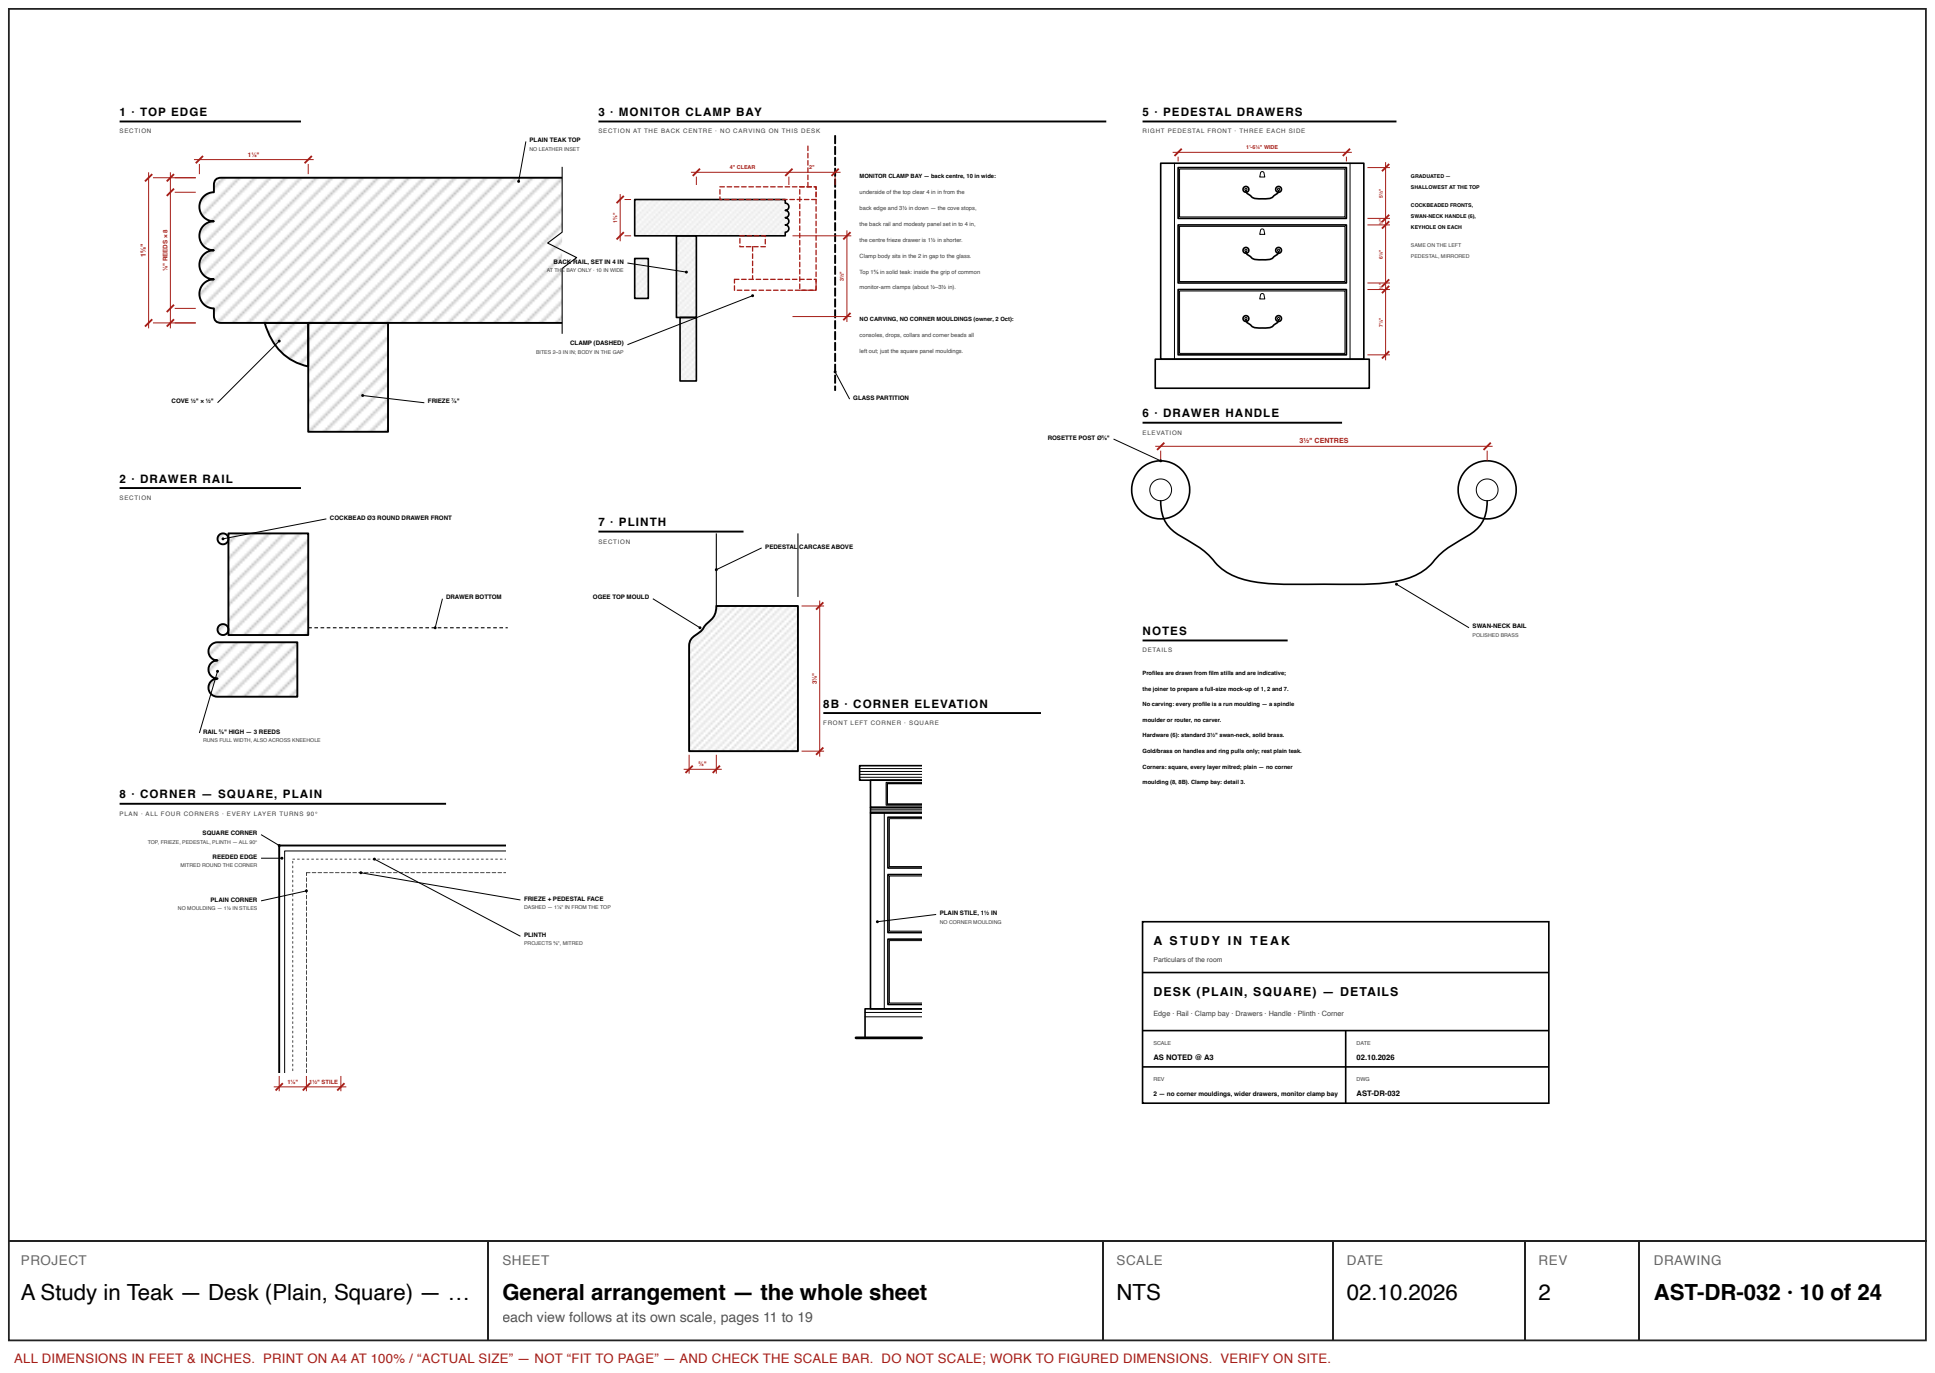
[picture p178: page 10]
1 · TOP EDGE; SECTION; ⅛" REEDS × 8; COVE ½" × ½"; FRIEZE ⅞"; 2 · DRAWER RAIL; DRAWER BOTTOM; 4" CLEAR; CLAMP (DASHED); GLASS PARTITION; 5 · PEDESTAL DRAWERS; 1'-6¼" WIDE; GRADUATED —; COCKBEADED FRONTS,; PEDESTAL, MIRRORED; 6 · DRAWER HANDLE; ELEVATION; 3½" CENTRES; POLISHED BRASS; 7 · PLINTH; SQUARE CORNER; REEDED EDGE; PLAIN CORNER; PLINTH; PROJECTS ⅝", MITRED; 1½" STILE; 8B · CORNER ELEVATION; NOTES; DETAILS; SCALE; AS NOTED @ A3; DATE; REV; DWG; AST-DR-032

3 · MONITOR CLAMP BAY

PLAIN TEAK TOP

NO LEATHER INSET

SECTION AT THE BACK CENTRE · NO CARVING ON THIS DESK

RIGHT PEDESTAL FRONT · THREE EACH SIDE

MONITOR CLAMP BAY — back centre, 10 in wide:

SHALLOWEST AT THE TOP

underside of the top clear 4 in in from the

back edge and 3½ in down — the cove stops,

the back rail and modesty panel set in to 4 in,

SWAN-NECK HANDLE (6),

the centre frieze drawer is 1½ in shorter.

KEYHOLE ON EACH

BACK RAIL, SET IN 4 IN

Clamp body sits in the 2 in gap to the glass.

SAME ON THE LEFT

AT THE BAY ONLY · 10 IN WIDE

Top 1⅝ in solid teak: inside the grip of common

monitor-arm clamps (about ½–3½ in).

NO CARVING, NO CORNER MOULDINGS (owner, 2 Oct):

consoles, drops, collars and corner beads all

BITES 2–3 IN IN; BODY IN THE GAP

left out; just the square panel mouldings.

ROSETTE POST Ø⅝"

COCKBEAD Ø3 ROUND DRAWER FRONT

PEDESTAL CARCASE ABOVE

OGEE TOP MOULD

SWAN-NECK BAIL

Profiles are drawn from film stills and are indicative;

the joiner to prepare a full-size mock-up of 1, 2 and 7.

No carving: every profile is a run moulding — a spindle

moulder or router, no carver.

RAIL ⅝" HIGH — 3 REEDS

FRONT LEFT CORNER · SQUARE

Hardware (6): standard 3½" swan-neck, solid brass.

RUNS FULL WIDTH, ALSO ACROSS KNEEHOLE

Gold/brass on handles and ring pulls only; rest plain teak.

Corners: square, every layer mitred; plain — no corner

8 · CORNER — SQUARE, PLAIN

moulding (8, 8B). Clamp bay: detail 3.

PLAN · ALL FOUR CORNERS · EVERY LAYER TURNS 90°

TOP, FRIEZE, PEDESTAL, PLINTH — ALL 90°

MITRED ROUND THE CORNER

NO MOULDING — 1½ IN STILES

FRIEZE + PEDESTAL FACE
DASHED — 1⅛" IN FROM THE TOP

PLAIN STILE, 1½ IN

NO CORNER MOULDING

Particulars of the room

DESK (PLAIN, SQUARE) — DETAILS

Edge · Rail · Clamp bay · Drawers · Handle · Plinth · Corner

2 — no corner mouldings, wider drawers, monitor clamp bay

General arrangement — the whole sheet

AST-DR-032 · 10 of 24

each view follows at its own scale, pages 11 to 19

## 1 · TOP EDGE

1⅛"

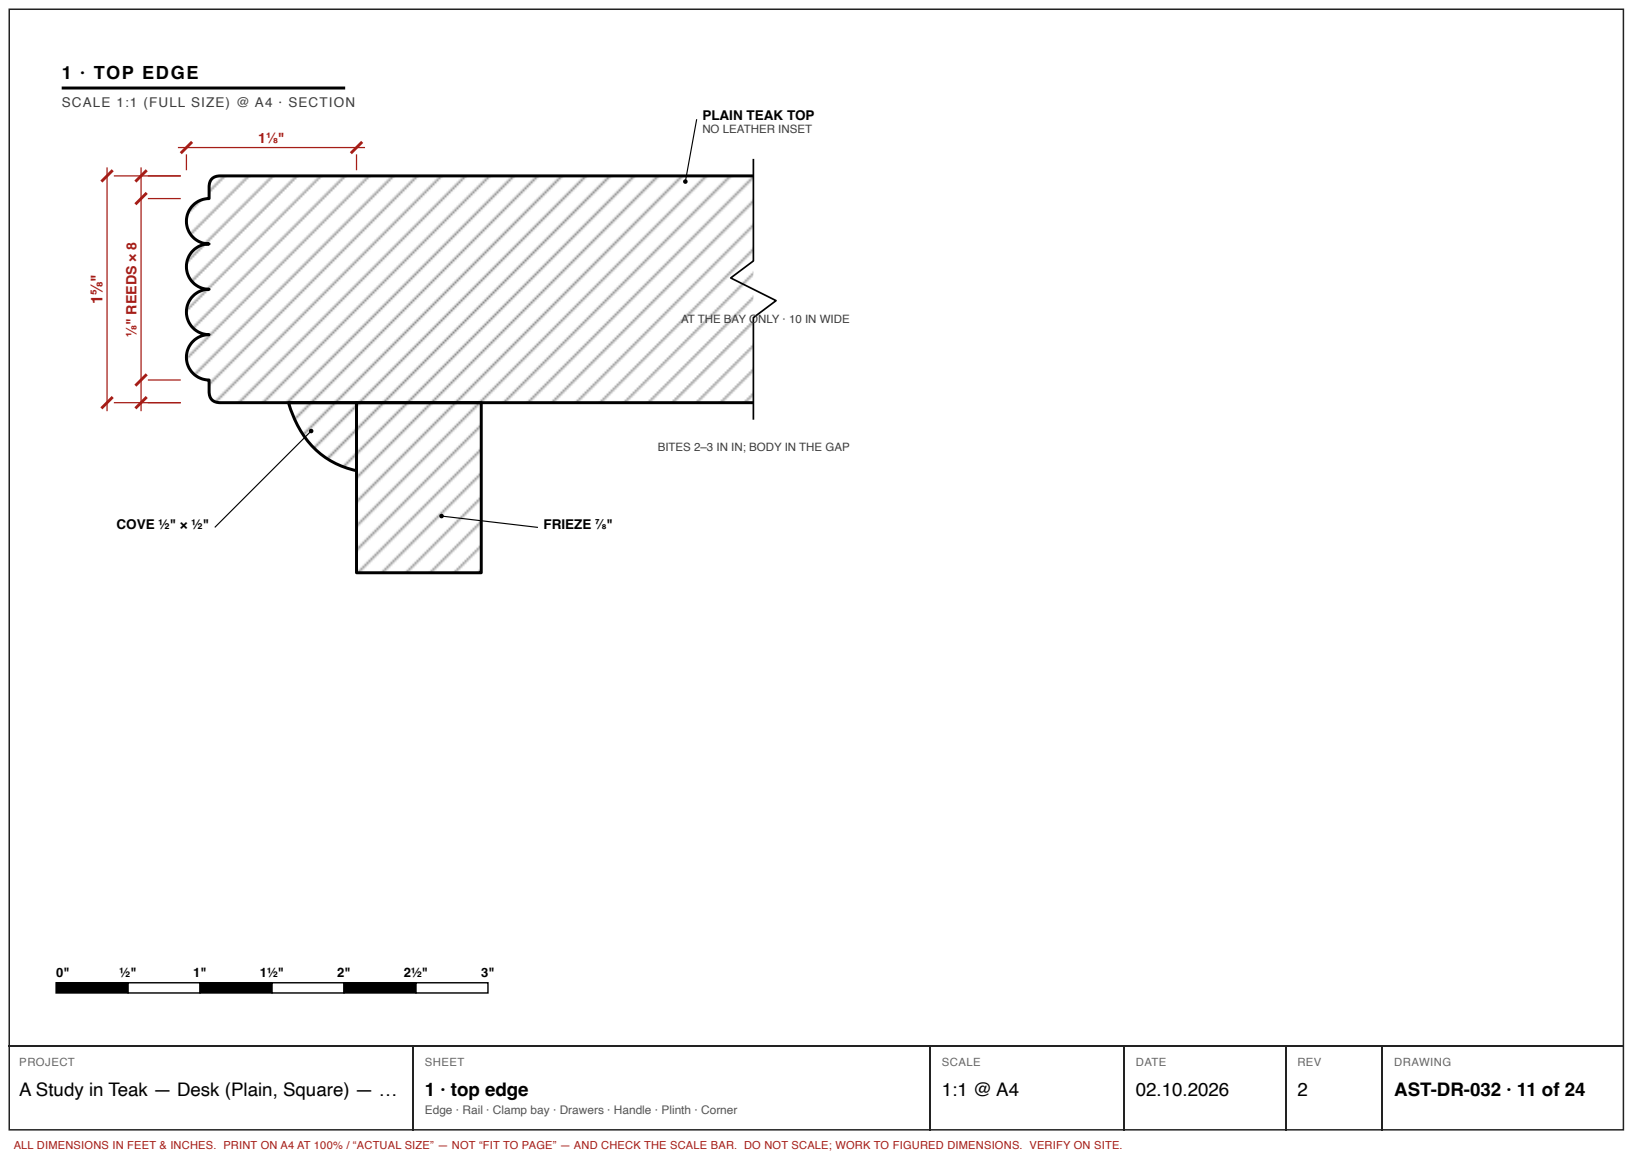
[picture p179: page 11]
⅛" REEDS × 8; COVE ½" × ½"; FRIEZE ⅞"; 1 · top edge

SCALE 1:1 (FULL SIZE) @ A4 · SECTION

PLAIN TEAK TOP
NO LEATHER INSET

AT THE BAY ONLY · 10 IN WIDE

BITES 2–3 IN IN; BODY IN THE GAP

AST-DR-032 · 11 of 24

Edge · Rail · Clamp bay · Drawers · Handle · Plinth · Corner

# 3 · MONITOR CLAMP BAY

### SCALE 1:3 (4" = 1'-0") @ A4 · SECTION AT THE BACK CENTRE · NO CARVING ON THIS DESK

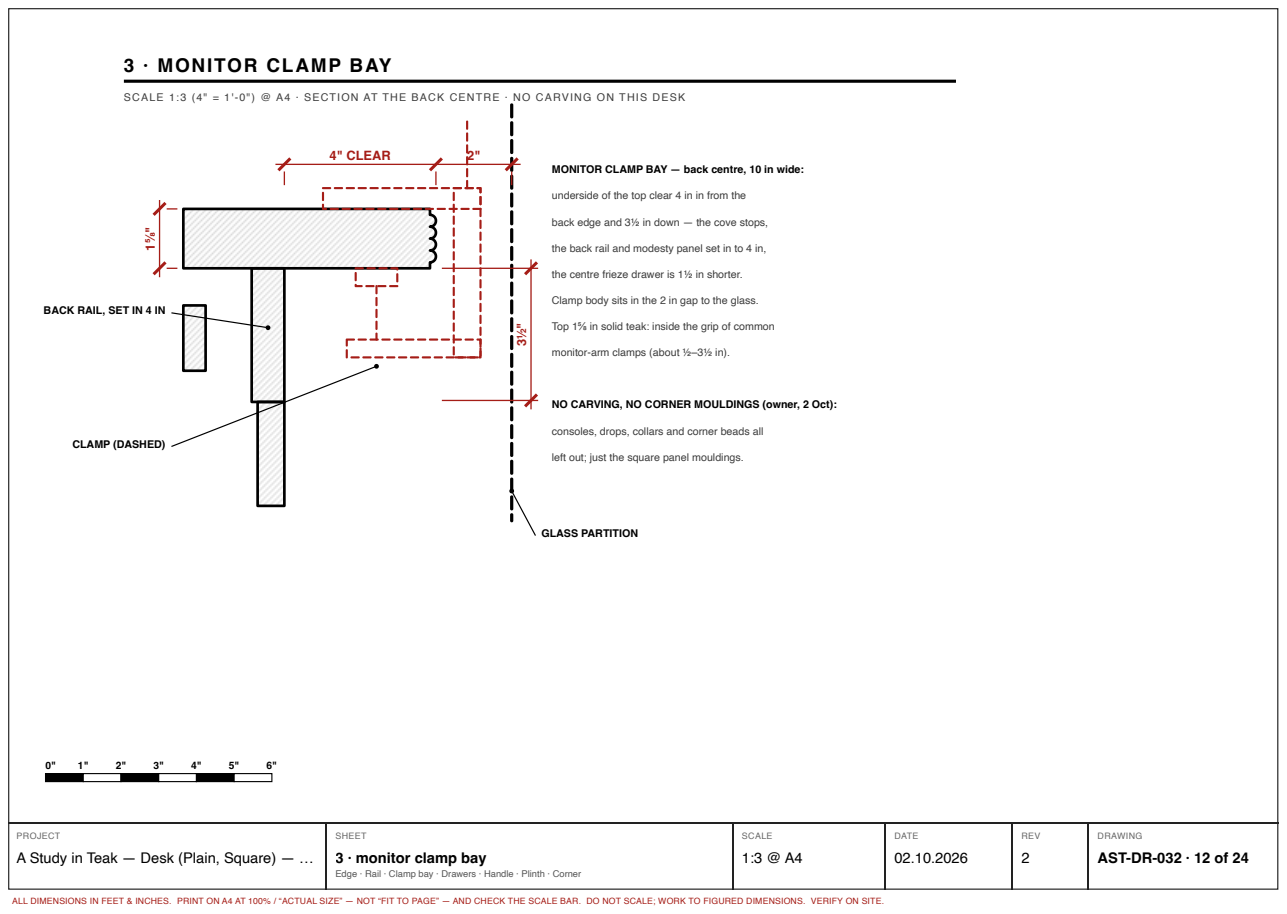
[picture p180: page 12]
4" CLEAR; CLAMP (DASHED); GLASS PARTITION

MONITOR CLAMP BAY — back centre, 10 in wide:

underside of the top clear 4 in in from the

back edge and 3½ in down — the cove stops,

the back rail and modesty panel set in to 4 in,

the centre frieze drawer is 1½ in shorter.

Clamp body sits in the 2 in gap to the glass.

BACK RAIL, SET IN 4 IN

Top 1⅝ in solid teak: inside the grip of common

monitor-arm clamps (about ½–3½ in).

NO CARVING, NO CORNER MOULDINGS (owner, 2 Oct):

consoles, drops, collars and corner beads all

left out; just the square panel mouldings.

3 · monitor clamp bay

AST-DR-032 · 12 of 24

Edge · Rail · Clamp bay · Drawers · Handle · Plinth · Corner

# 5 · PEDESTAL DRAWERS

## SCALE 1:6 (2" = 1'-0") @ A4 · RIGHT PEDESTAL FRONT · THREE EACH SIDE

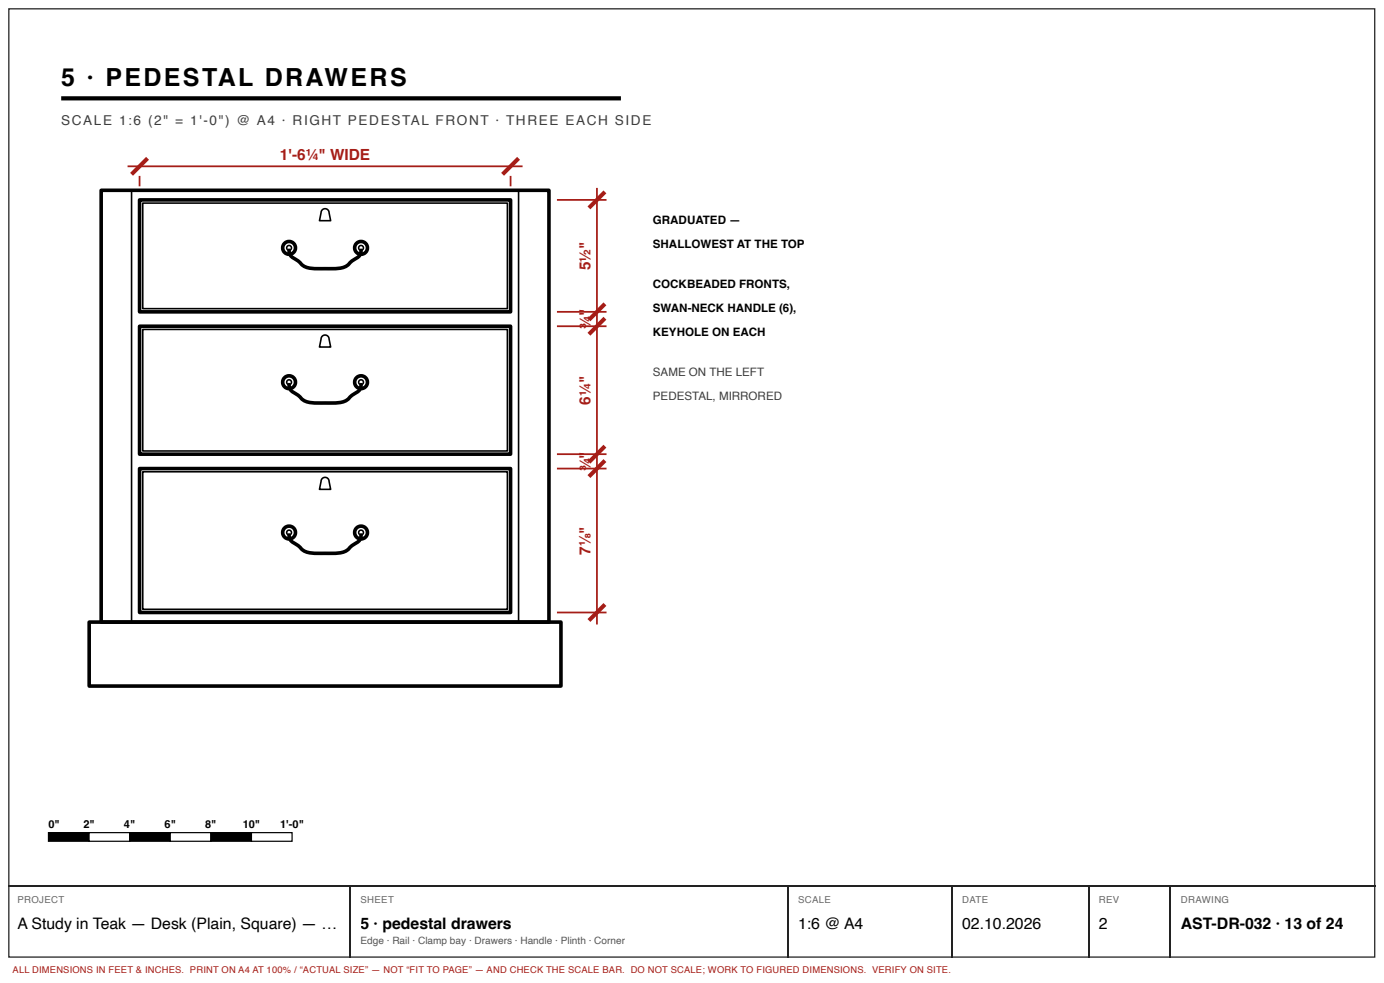
[picture p181: page 13]
1'-6¼" WIDE; GRADUATED —; COCKBEADED FRONTS,; PEDESTAL, MIRRORED; 5 · pedestal drawers

SHALLOWEST AT THE TOP

SWAN-NECK HANDLE (6),

KEYHOLE ON EACH

SAME ON THE LEFT

AST-DR-032 · 13 of 24

Edge · Rail · Clamp bay · Drawers · Handle · Plinth · Corner

## 2 · DRAWER RAIL

DRAWER BOTTO; 2 · drawer rail

SCALE 1:1 (FULL SIZE) @ A4 · SECTION

COCKBEAD Ø3 ROUND DRAWER FRONT

RAIL ⅝" HIGH — 3 REEDS
RUNS FULL WIDTH, ALSO ACROSS KNEEHOLE

AST-DR-032 · 14 of 24

Edge · Rail · Clamp bay · Drawers · Handle · Plinth · Corner

## 6 · DRAWER HANDLE

## 3½" CENTRES

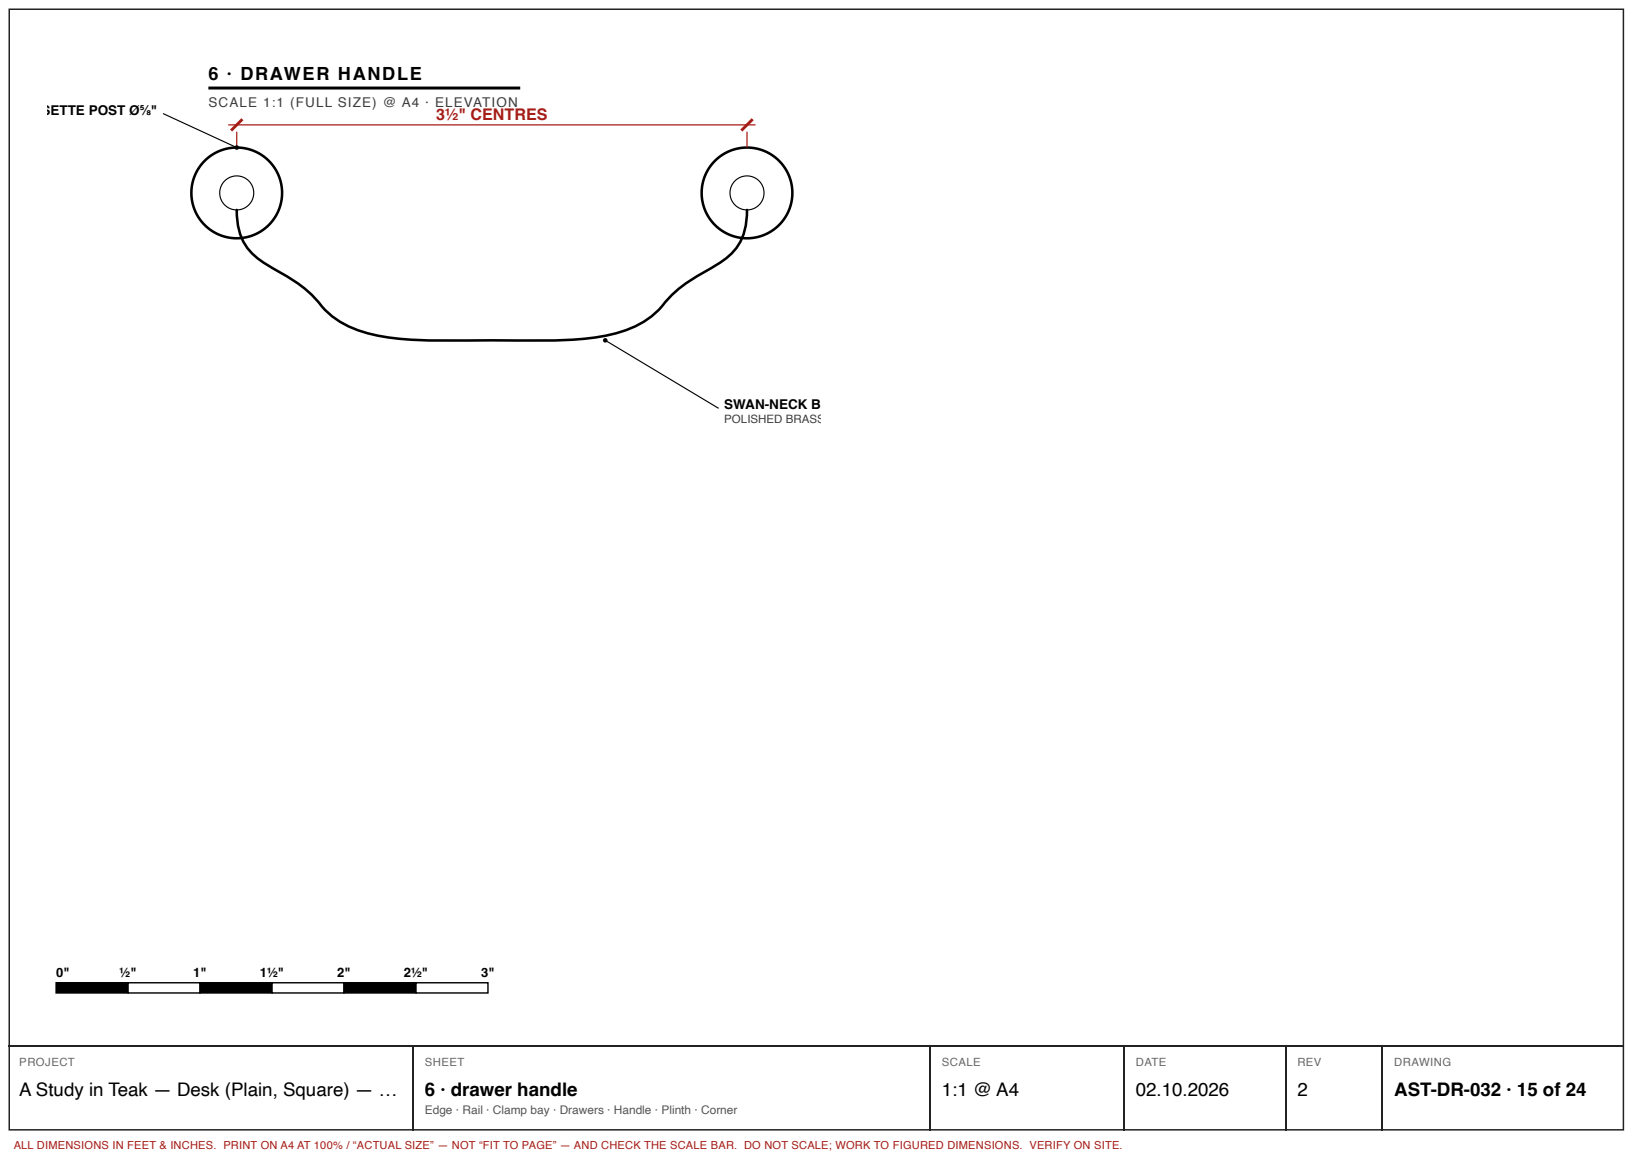
[picture p182: page 15]
SWAN-NECK B POLISHED BRASS; 6 · drawer handle

SETTE POST Ø⅝"

SCALE 1:1 (FULL SIZE) @ A4 · ELEVATION

AST-DR-032 · 15 of 24

Edge · Rail · Clamp bay · Drawers · Handle · Plinth · Corner

# 7 · PLINTH

# SCALE 1:1 (FULL SIZE) @ A4 · SECTION

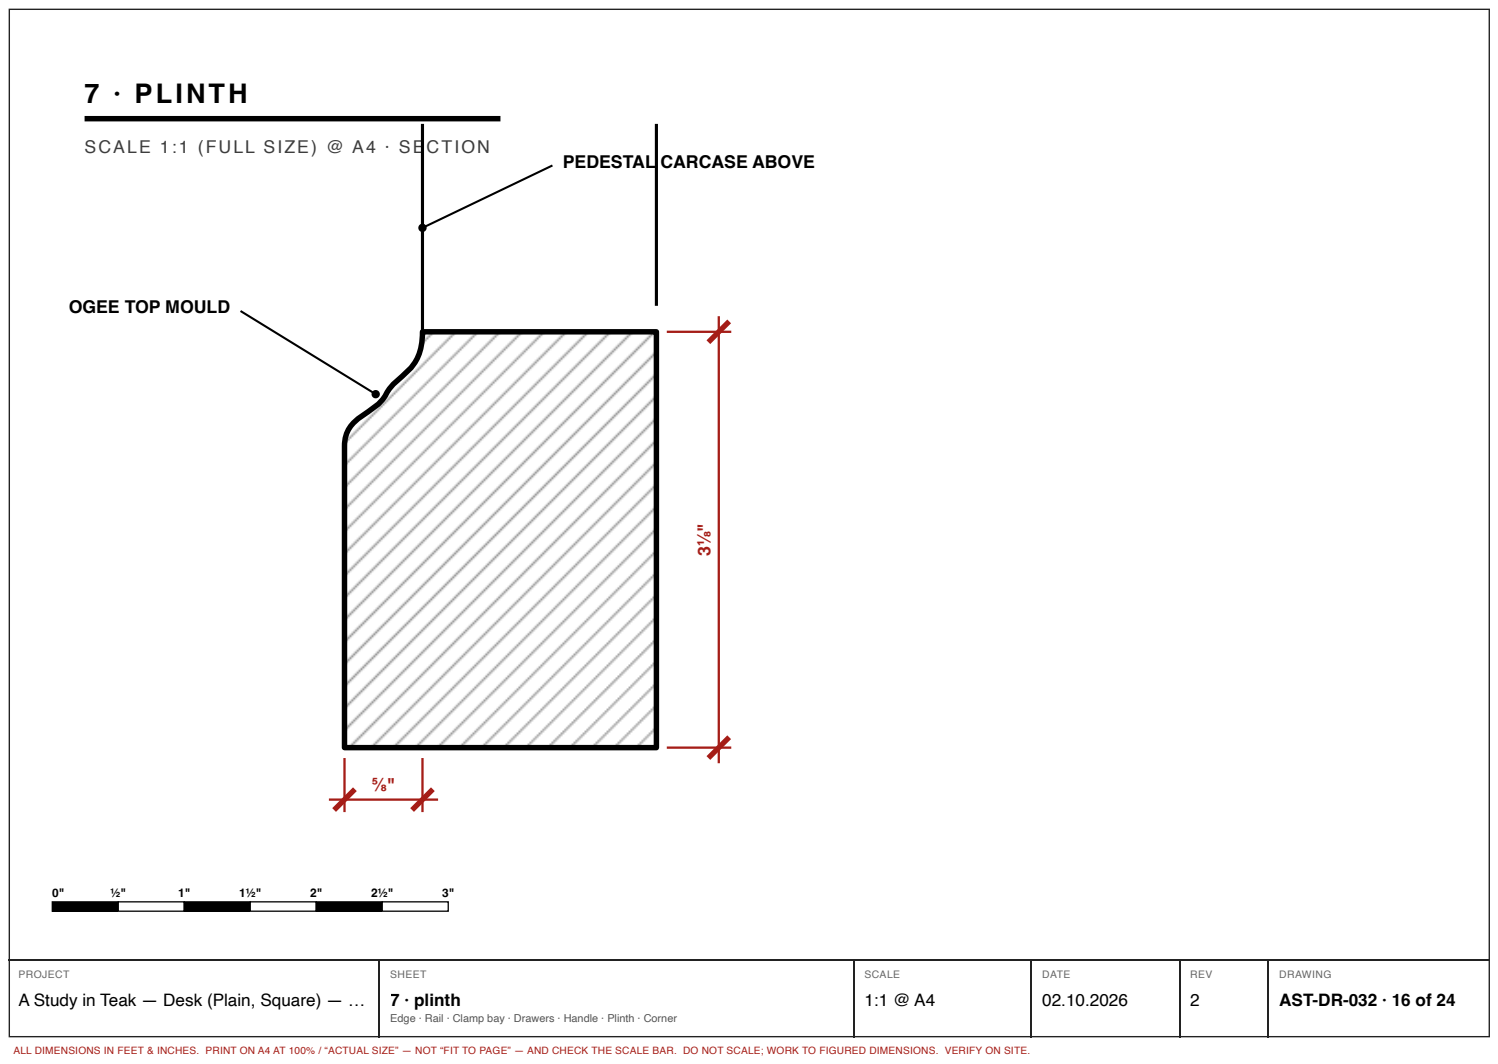
[picture p183: page 16]
7 · plinth

PEDESTAL CARCASE ABOVE

OGEE TOP MOULD

AST-DR-032 · 16 of 24

Edge · Rail · Clamp bay · Drawers · Handle · Plinth · Corner

# NOTES

# DETAILS

Profiles are drawn from film stills and are indicative;

the joiner to prepare a full-size mock-up of 1, 2 and 7.

# No carving: every profile is a run moulding — a spindle

moulder or router, no carver.

Hardware (6): standard 3½" swan-neck, solid brass.

Gold/brass on handles and ring pulls only; rest plain teak.

# Corners: square, every layer mitred; plain — no corner

moulding (8, 8B). Clamp bay: detail 3.

# Notes

Edge · Rail · Clamp bay · Drawers · Handle · Plinth · Corner

# AST-DR-032 · 17 of 24

# 8B · CORNER ELEVATION

### SCALE 1:8 (1½" = 1'-0") @ A4 · FRONT LEFT CORNER · SQ

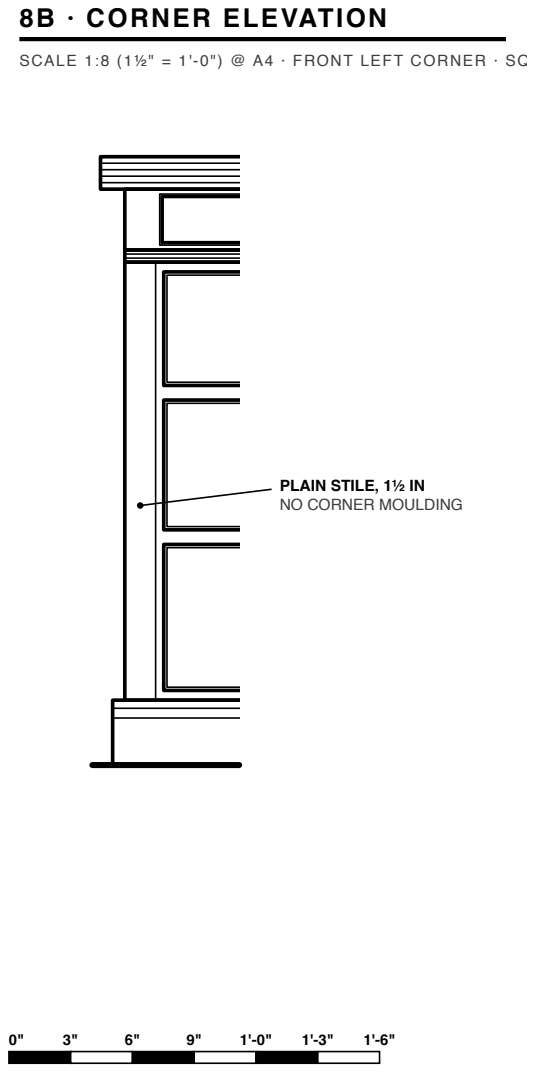
[picture p184: page 18]
8B · corner elevation

PLAIN STILE, 1½ IN
NO CORNER MOULDING

AST-DR-032 · 18 of 24

Edge · Rail · Clamp bay · Drawers · Handle · Plinth · Corner

# 8 · CORNER — SQUARE, PLAIN

### SCALE 1:3 (4" = 1'-0") @ A4 · PLAN · ALL FOUR CORNERS · EVERY LAYER TURNS 90°

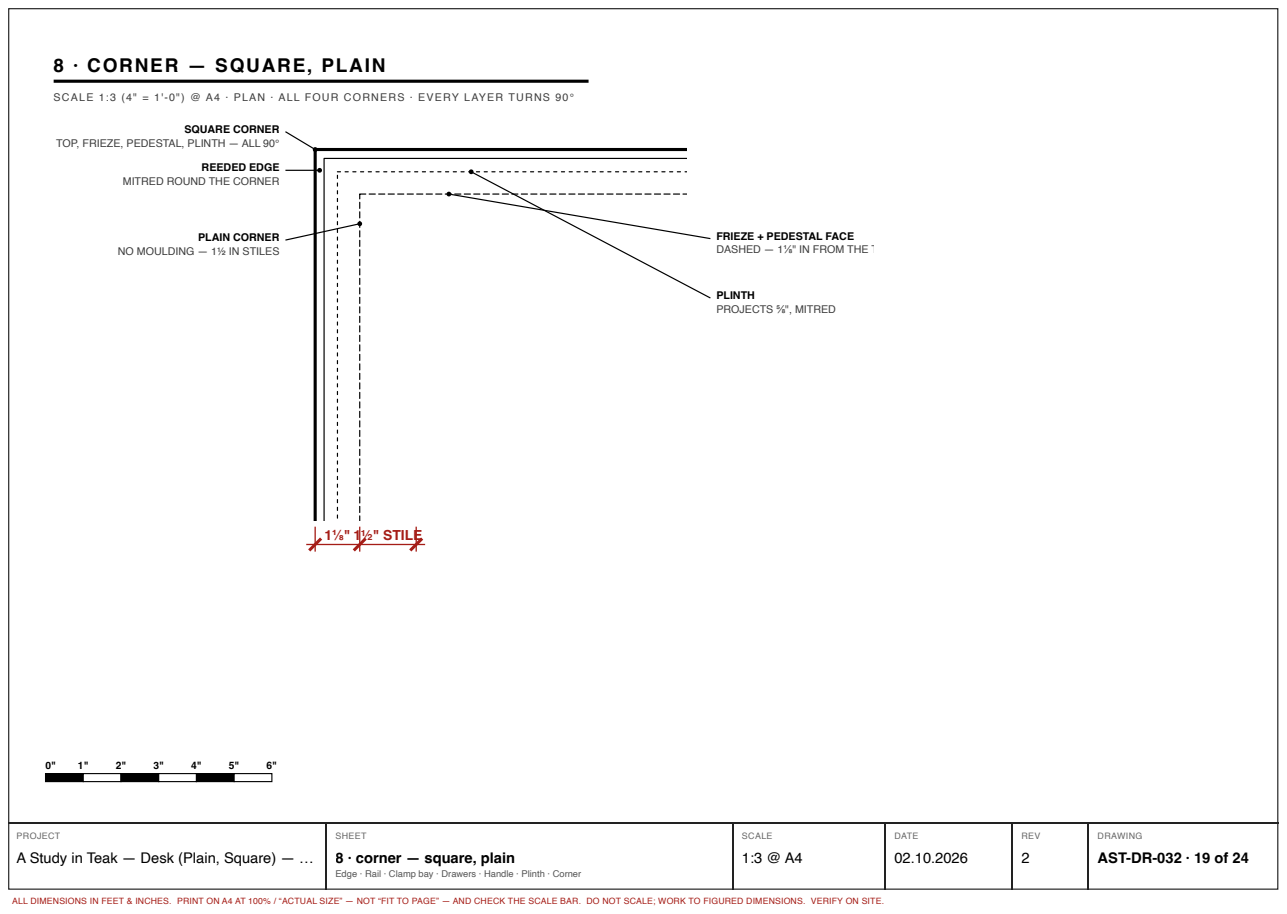
[picture p185: page 19]
SQUARE CORNER; REEDED EDGE; PLAIN CORNER; PLINTH PROJECTS ⅝", MITRED; 1⅛" 1½" STILE

TOP, FRIEZE, PEDESTAL, PLINTH — ALL 90°

MITRED ROUND THE CORNER

FRIEZE + PEDESTAL FACE
DASHED — 1⅛" IN FROM THE T

NO MOULDING — 1½ IN STILES

8 · corner — square, plain

AST-DR-032 · 19 of 24

Edge · Rail · Clamp bay · Drawers · Handle · Plinth · Corner

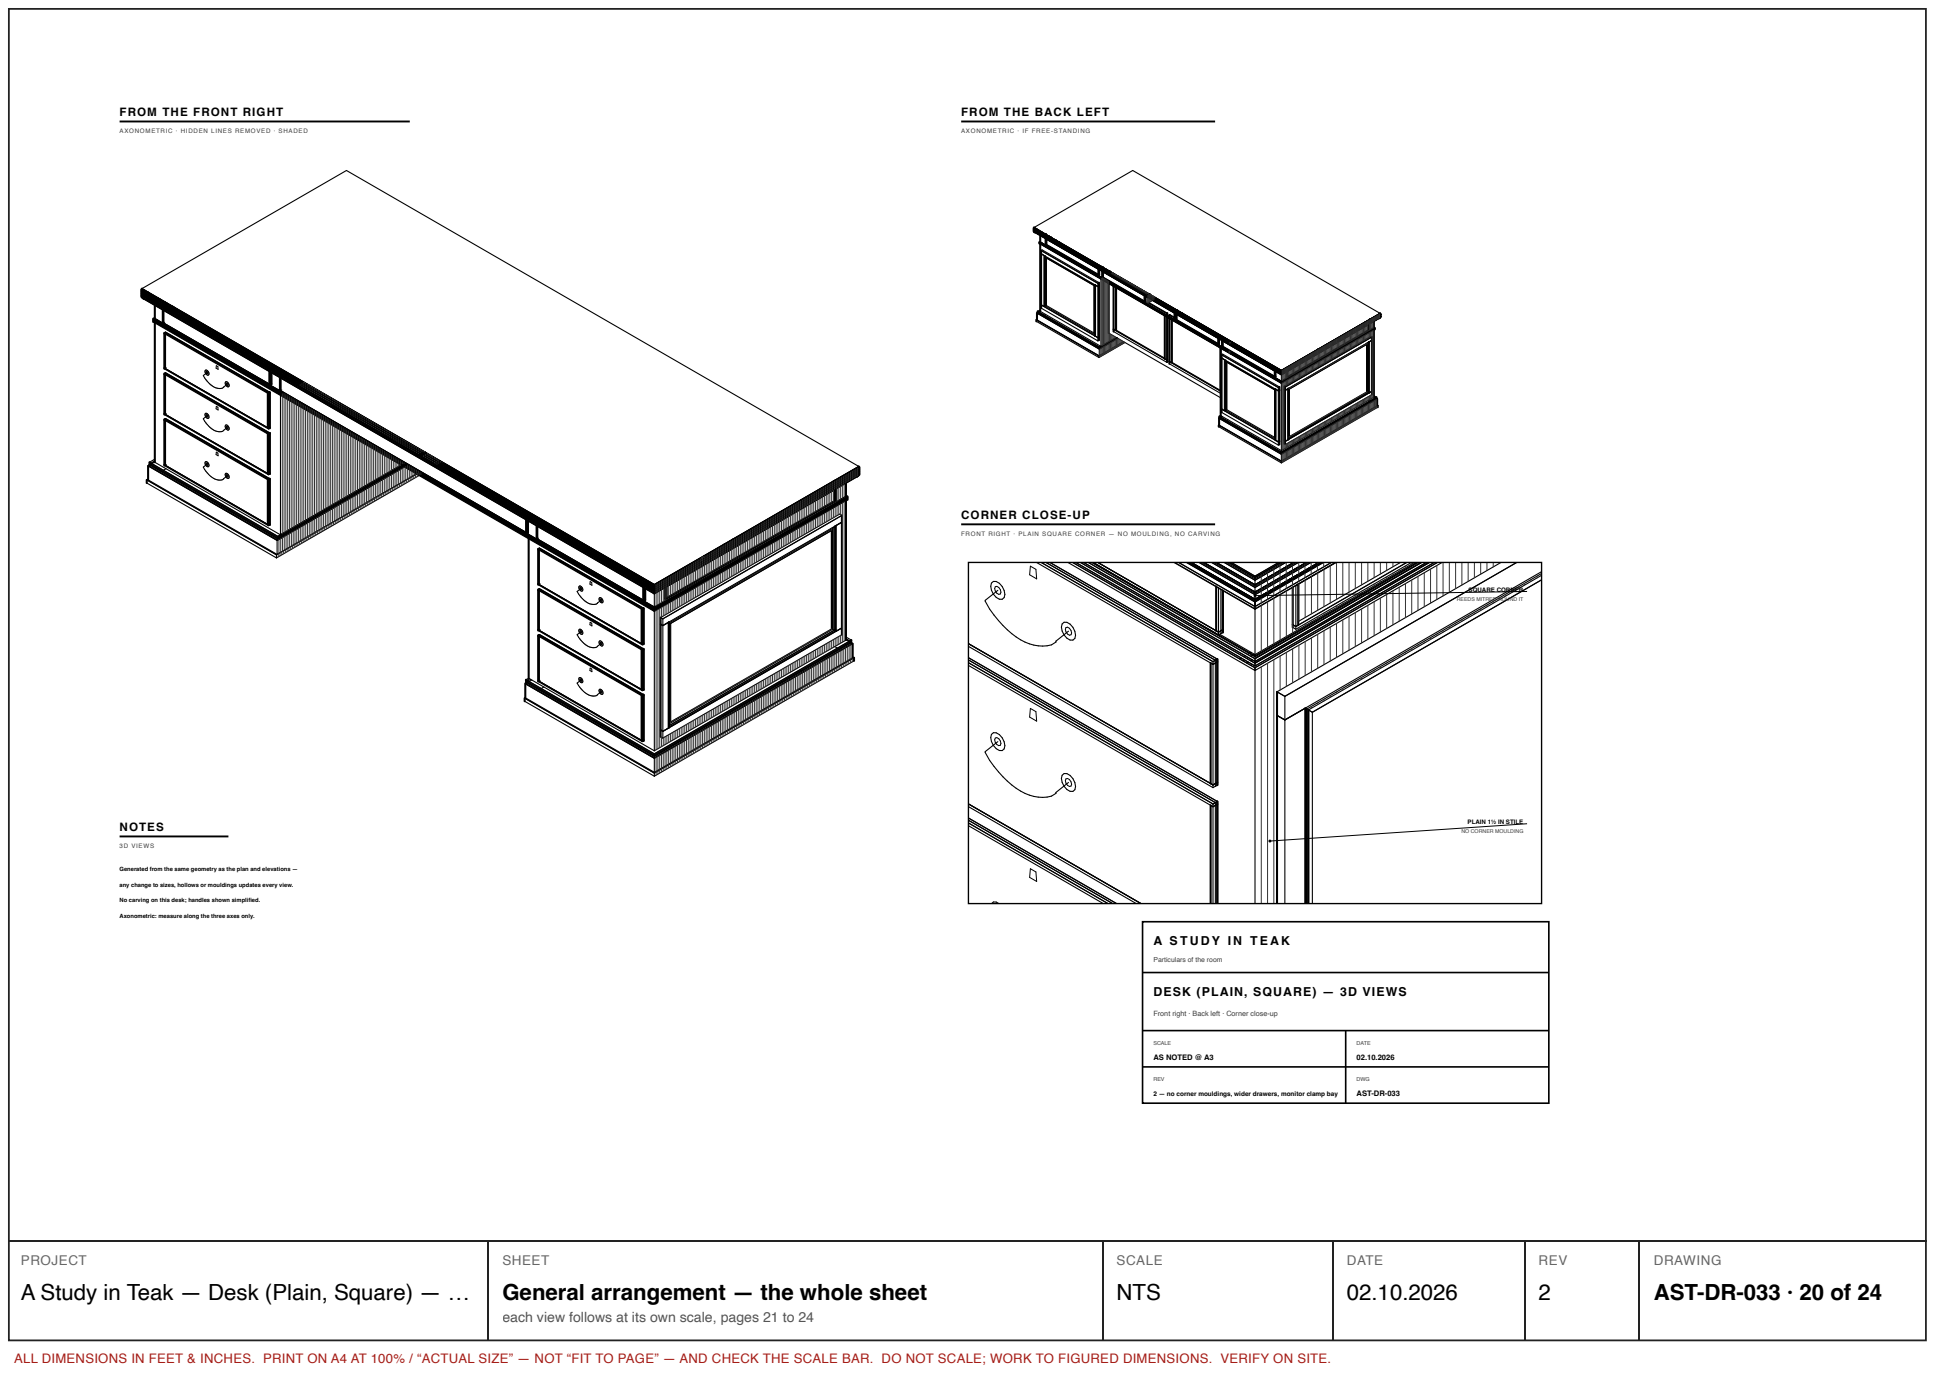
[picture p186: page 20]
SQUARE CORNER; PLAIN 1½ IN STILE NOTES; NO CORNER MOULDING; 3D VIEWS; SCALE; AS NOTED @ A3; DATE; REV; DWG; AST-DR-033

FROM THE FRONT RIGHT

FROM THE BACK LEFT

AXONOMETRIC · HIDDEN LINES REMOVED · SHADED

AXONOMETRIC · IF FREE-STANDING

CORNER CLOSE-UP

FRONT RIGHT · PLAIN SQUARE CORNER — NO MOULDING, NO CARVING

REEDS MITRED ROUND IT

Generated from the same geometry as the plan and elevations —

any change to sizes, hollows or mouldings updates every view.

No carving on this desk; handles shown simplified.

Axonometric: measure along the three axes only.

Particulars of the room

DESK (PLAIN, SQUARE) — 3D VIEWS

Front right · Back left · Corner close-up

2 — no corner mouldings, wider drawers, monitor clamp bay

General arrangement — the whole sheet

AST-DR-033 · 20 of 24

each view follows at its own scale, pages 21 to 24

## FROM THE FRONT RIGHT

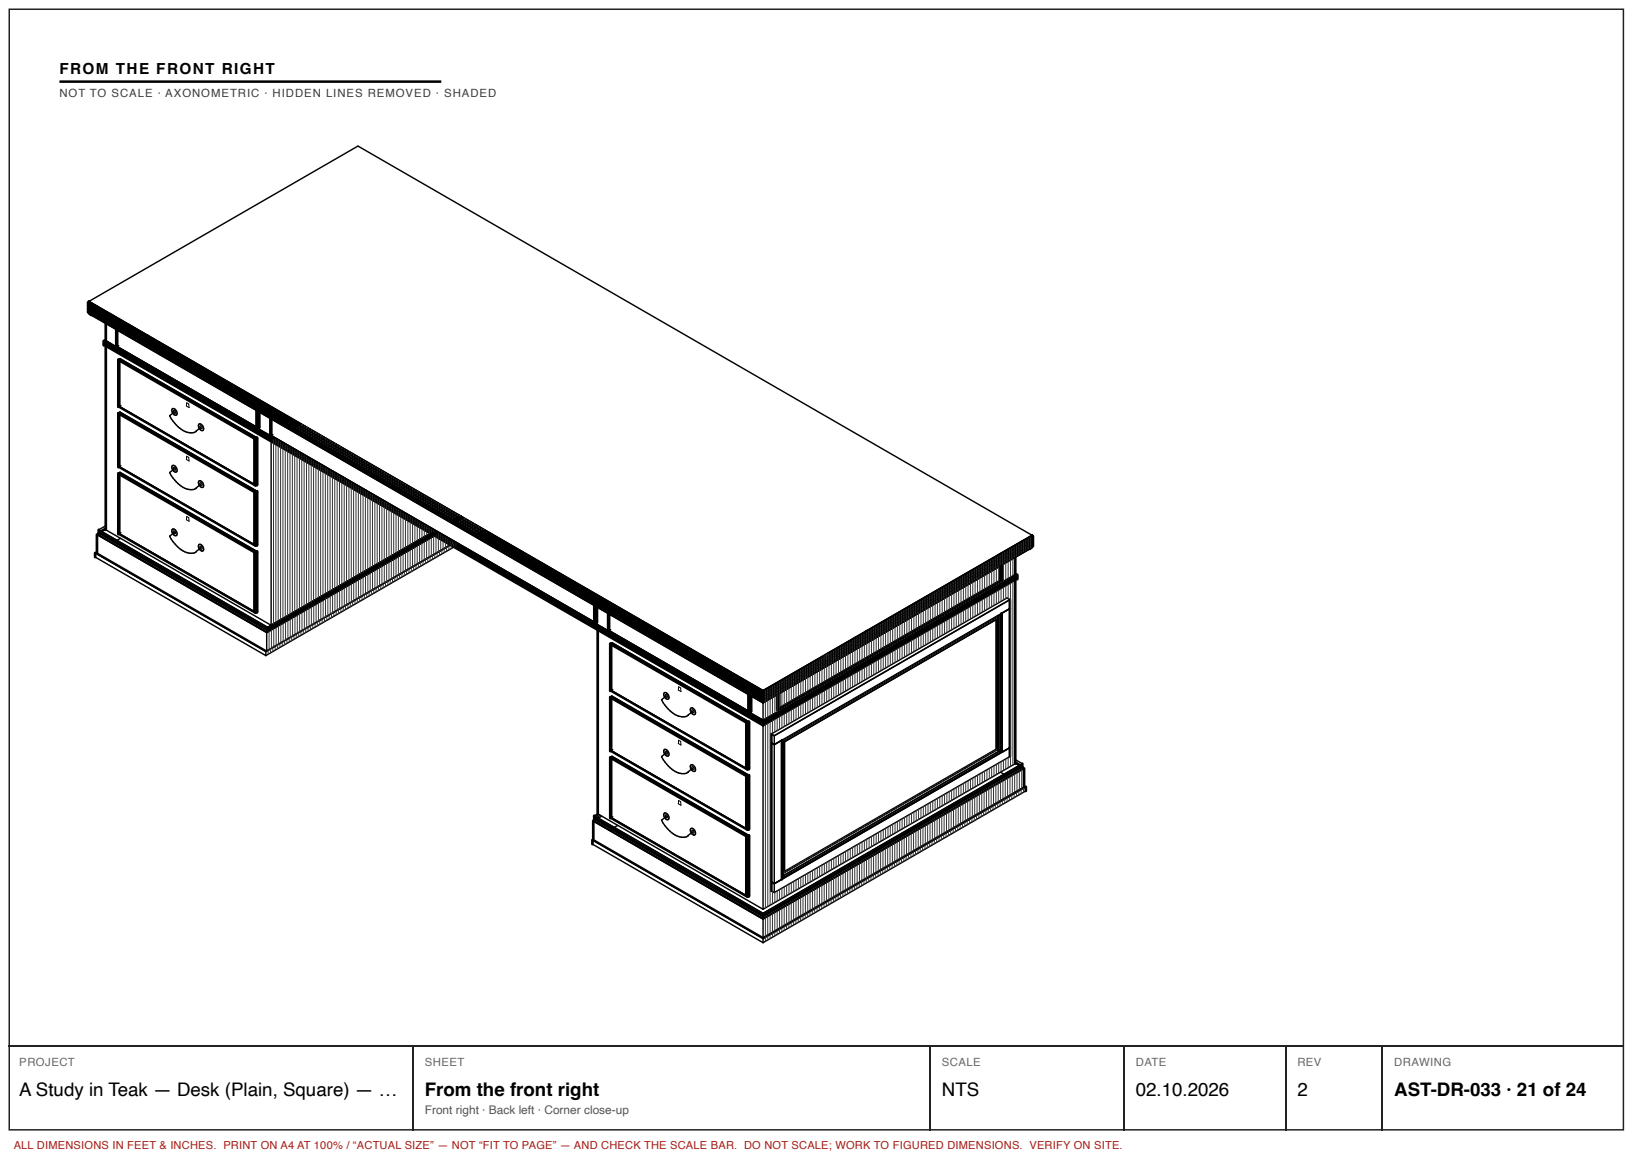
[picture p187: page 21]

NOT TO SCALE · AXONOMETRIC · HIDDEN LINES REMOVED · SHADED

From the front right

AST-DR-033 · 21 of 24

Front right · Back left · Corner close-up

# FROM THE BACK LEFT

## NOT TO SCALE · AXONOMETRIC · IF FREE-STANDING

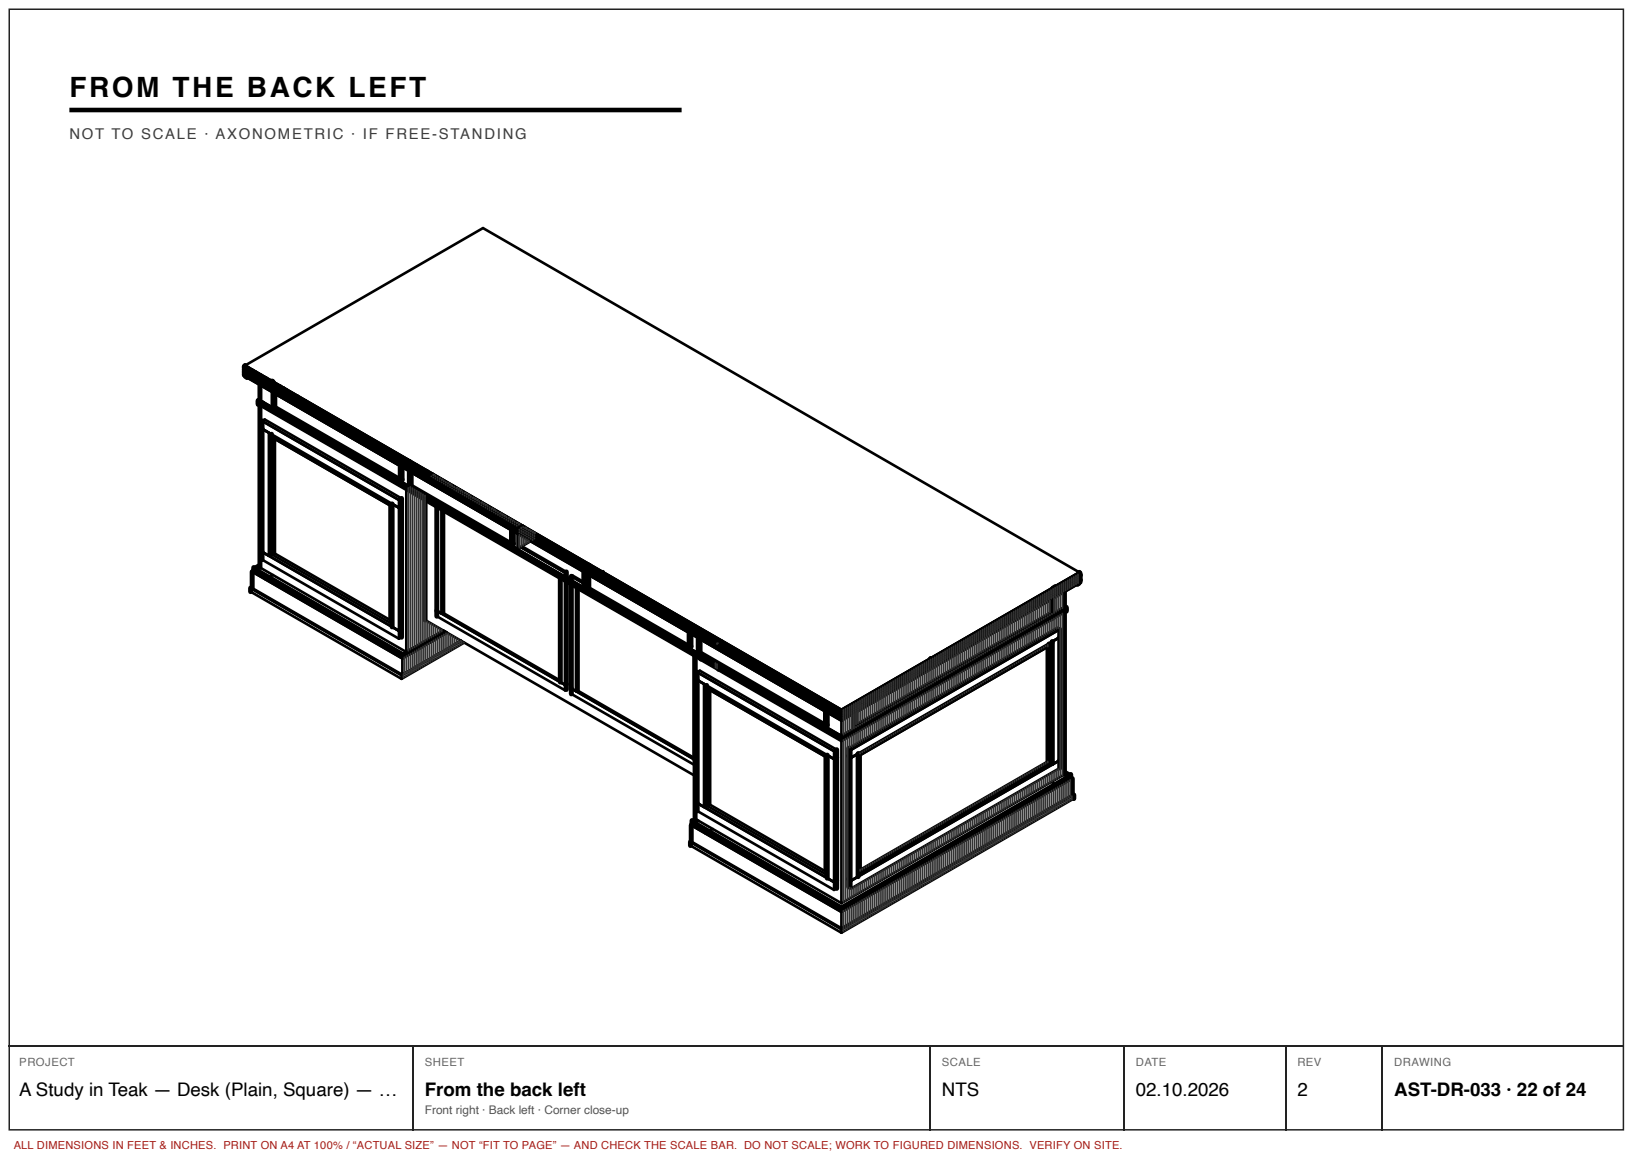
[picture p188: page 22]

From the back left

AST-DR-033 · 22 of 24

Front right · Back left · Corner close-up

# CORNER CLOSE-UP

### NOT TO SCALE · FRONT RIGHT · PLAIN SQUARE CORNER — NO MOULDING, NO CARVING

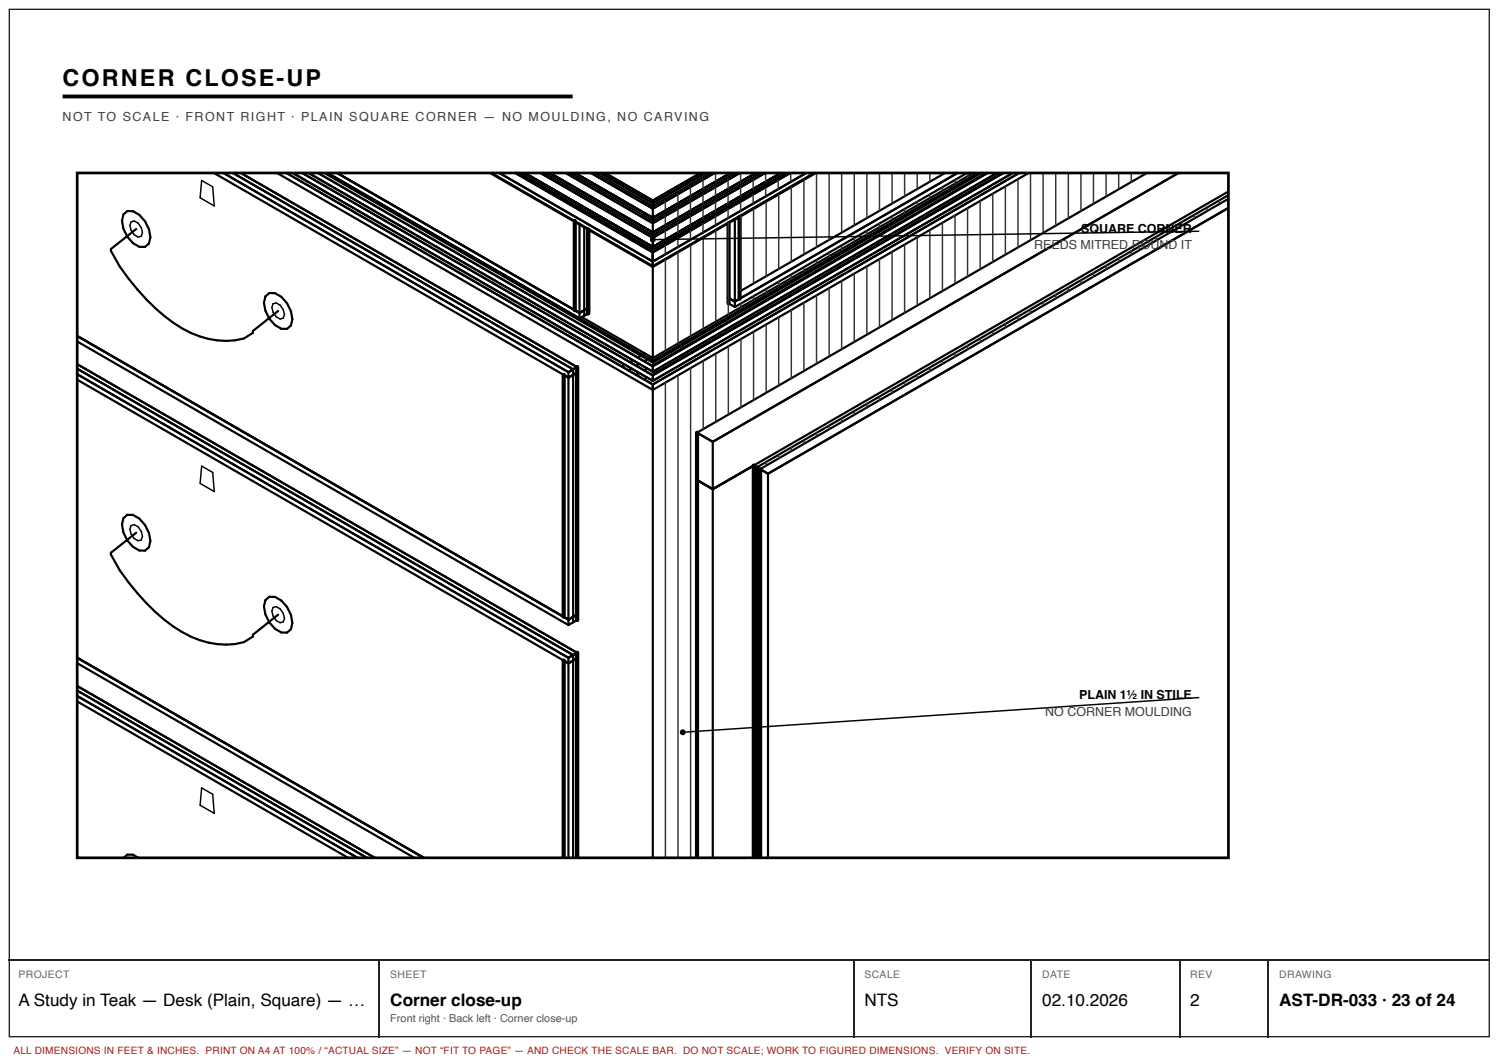
[picture p189: page 23]
SQUARE CORNER

REEDS MITRED ROUND IT

PLAIN 1½ IN STILE
NO CORNER MOULDING

Corner close-up

AST-DR-033 · 23 of 24

Front right · Back left · Corner close-up

# N O T E S

# 3D VIEWS

# Generated from the same geometry as the plan and elevations —

any change to sizes, hollows or mouldings updates every view.

No carving on this desk; handles shown simplified.

Axonometric: measure along the three axes only.

# Notes

Front right · Back left · Corner close-up

# AST-DR-033 · 24 of 24
