sakshampan733-cloud/a-study-in-teak/cad/print/architrave-a4.pdf

DRESSING DOOR

D2 · 2 FT 6 · THE CARVED HEAD

MAIN AND BATHROOM

D1 3 FT · D3 2 FT 6 · PLAIN CASING

1 · THE HEAD

DRESSING DOOR · LEFT END · LINING, MOULDING, SCALLOPS, CROWN

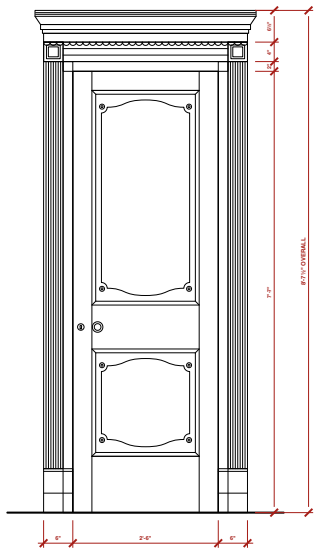
[picture p207: figure]
8'-7½" OVERALL
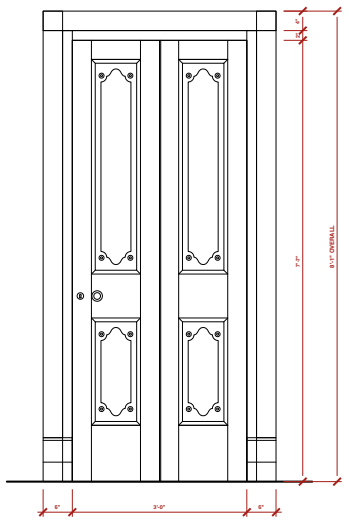
[picture p208: figure]
8'-1" OVERALL
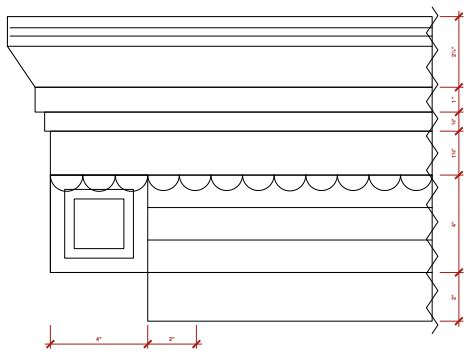
[picture p209: figure]

2 · SECTION

THROUGH THE HEAD

1⅛" | 3¼"

1'-½" HEAD

3 · JAMB

SECTION · 6 IN ON THE FACE

4" | 2"

4 · PLINTH

AT THE FOOT

9"

NOTES

REVISION 8

The lining is 2 in on the face. The moulding lays 4 in outside it,

all round — so the jambs are 6 in wide, and over the opening the

moulding head sits 6 in ABOVE the leaf, not on top of it.

The jambs are reeded. Across the head the moulding is STEPPED,

not reeded — the reference has no reeding there.

A plinth block takes each jamb down over the marble skirting.

Above the moulding, and only above it: a course of scallops, two

small mouldings, and a crown that mitres back at each end.

A 4 in square block at each corner, with a small sunk moulding

inside it, ties head to jamb; the scallops run in three runs so a

joint lands on each block edge. The crown lands at 8'-7½".

The carved head is the DRESSING door's alone. Main and bathroom

take the same lining and moulding, run straight across and stopped. RELIEF

DATUM 0 = FACE OF THE PLASTER · LINING AND MOULDING ARE COMMON TO ALL THREE DOORS · THE REST IS THE DRESSING DOOR'S CARVED HEAD

Lining, 2 in on the face | ¼" OUT
Moulding, 4 in, reeded | 1⅛" OUT
Reed grooves in the moulding face | 3 IN
Corner block, flush with the moulding | 1⅛" OUT
Its sunk panel, two steps | 0¼" AND 0⅜" IN
Scallop course | 1⅝" OUT
Scallops, cut back from its face | 5 IN
Small mouldings, over the scallops | 2" AND 2⅝" OUT
Crown, the widest member | 4⅜" OUT
Plinth block, so the moulding dies on it | 1⅜" OUT

A S T U D Y I N T E A K

Particulars of the room

DOOR CASINGS

Carved head — dressing only · Plain elsewhere · Sections

SCALE

AS NOTED @ A3

DATE

19.09.2026

REV

8 — carved head: dressing door only

DWG

AST-DR-011

PROJECT

# A Study in Teak — Door Casings

SHEET

# General arrangement — the whole sheet

each view follows at its own scale, pages 2 to 8

SCALE

# NTS

DATE
19.09.2026

REV

DRAWING

# AST-DR-011 · 1 of 8

ALL DIMENSIONS IN FEET & INCHES. PRINT ON A4 AT 100% / “ACTUAL SIZE” — NOT “FIT TO PAGE” — AND CHECK THE SCALE BAR. DO NOT SCALE; WORK TO FIGURED DIMENSIONS. VERIFY ON SITE.

## DRESSING DOOR

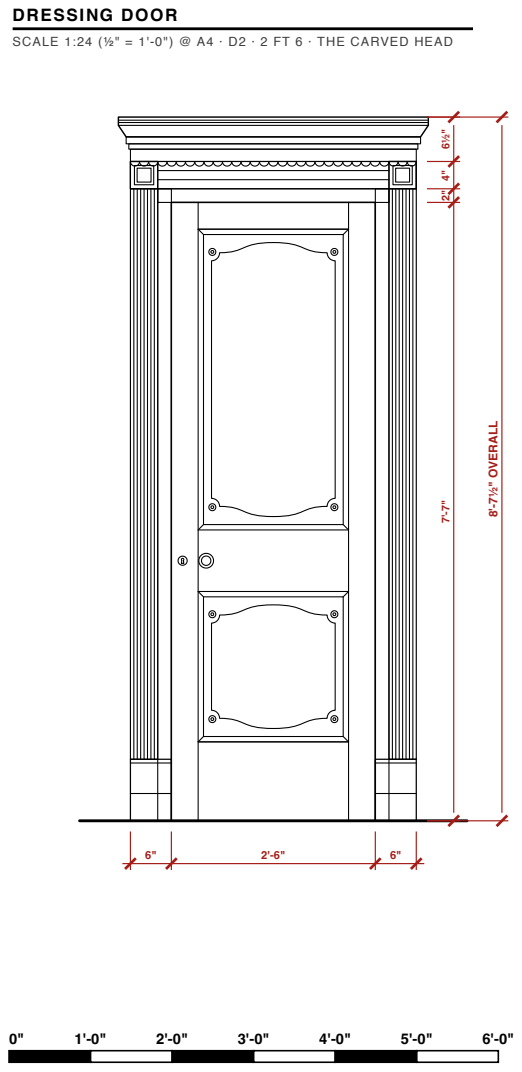
[picture p210: page 2]
8'-7½" OVERALL; Dressing door

SCALE 1:24 (½" = 1'-0") @ A4 · D2 · 2 FT 6 · THE CARVED HEAD

AST-DR-011 · 2 of 8

Carved head — dressing only · Plain elsewhere · Sections

## 1 · THE HEAD

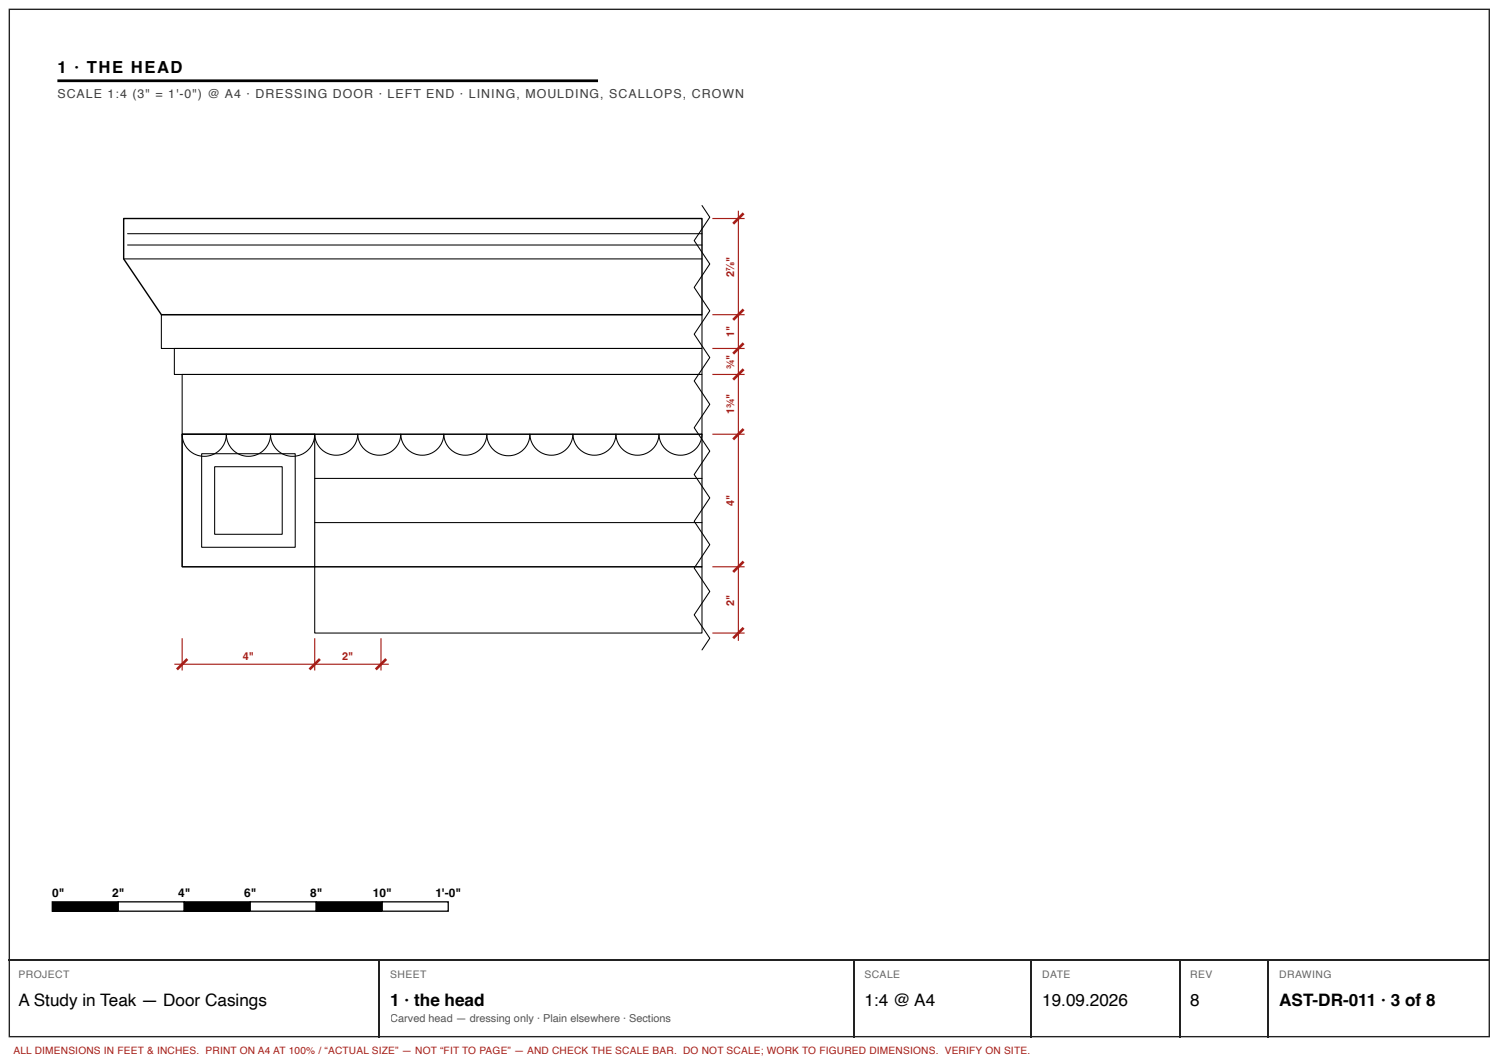
[picture p211: page 3]
1 · the head

SCALE 1:4 (3" = 1'-0") @ A4 · DRESSING DOOR · LEFT END · LINING, MOULDING, SCALLOPS, CROWN

AST-DR-011 · 3 of 8

# 2 · SECTION

### SCALE 1:3 (4" = 1'-0") @ A4 · THROUGH THE HEAD

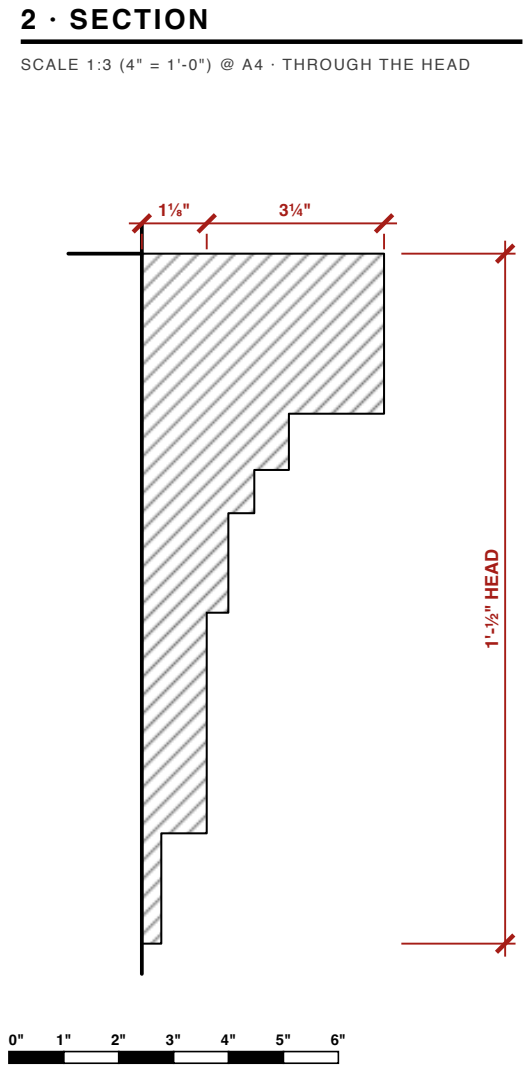
[picture p212: page 4]
1'-½" HEAD; 2 · section

AST-DR-011 · 4 of 8

# 3 · JAMB

# SCALE 1:2 (6" = 1'-0") @ A4 · SECTION · 6 IN ON THE FAC

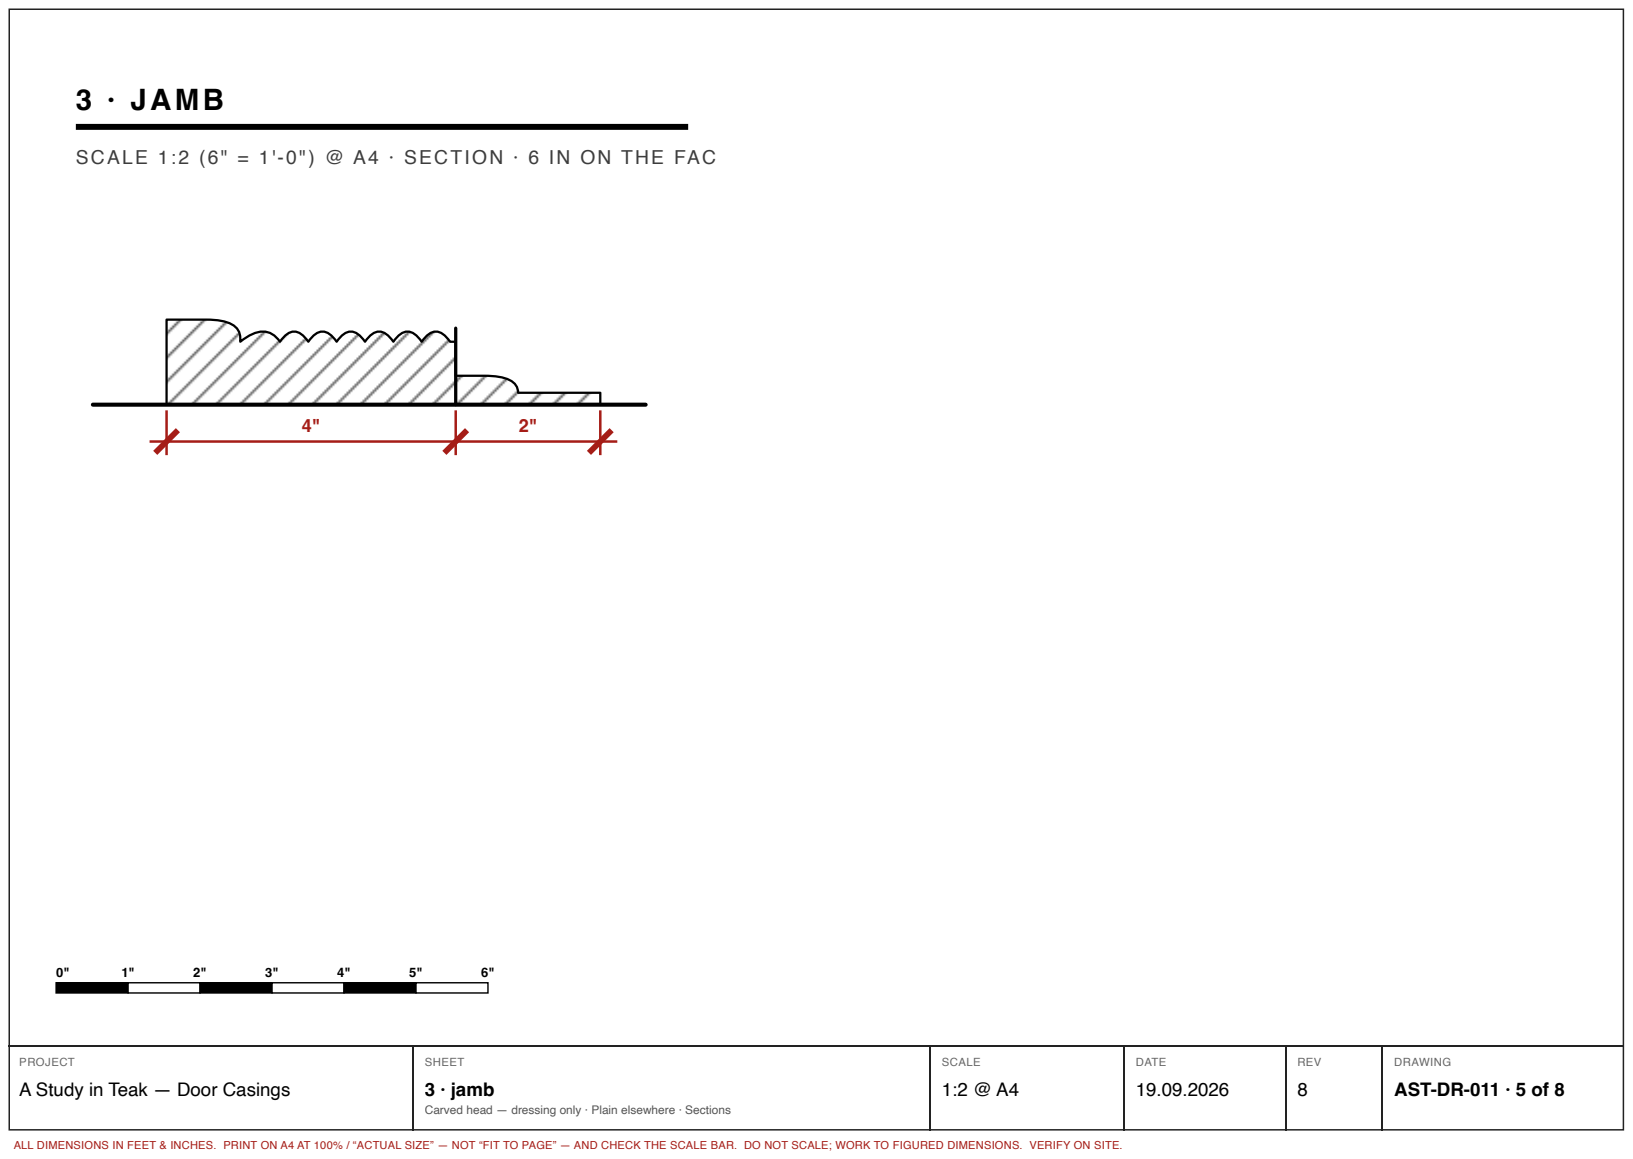
[picture p213: page 5]
3 · jamb

AST-DR-011 · 5 of 8

# N O T E S

# REVISION 8

The lining is 2 in on the face. The moulding lays 4 in outside it,

# all round — so the jambs are 6 in wide, and over the opening the

moulding head sits 6 in ABOVE the leaf, not on top of it.

The jambs are reeded. Across the head the moulding is STEPPED,

not reeded — the reference has no reeding there.

A plinth block takes each jamb down over the marble skirting.

# Notes

# NTS

# AST-DR-011 · 6 of 8

# 4 · PLI N T H

# SCALE 1:4 (3" = 1'-0") @ A4 · AT THE FOOT

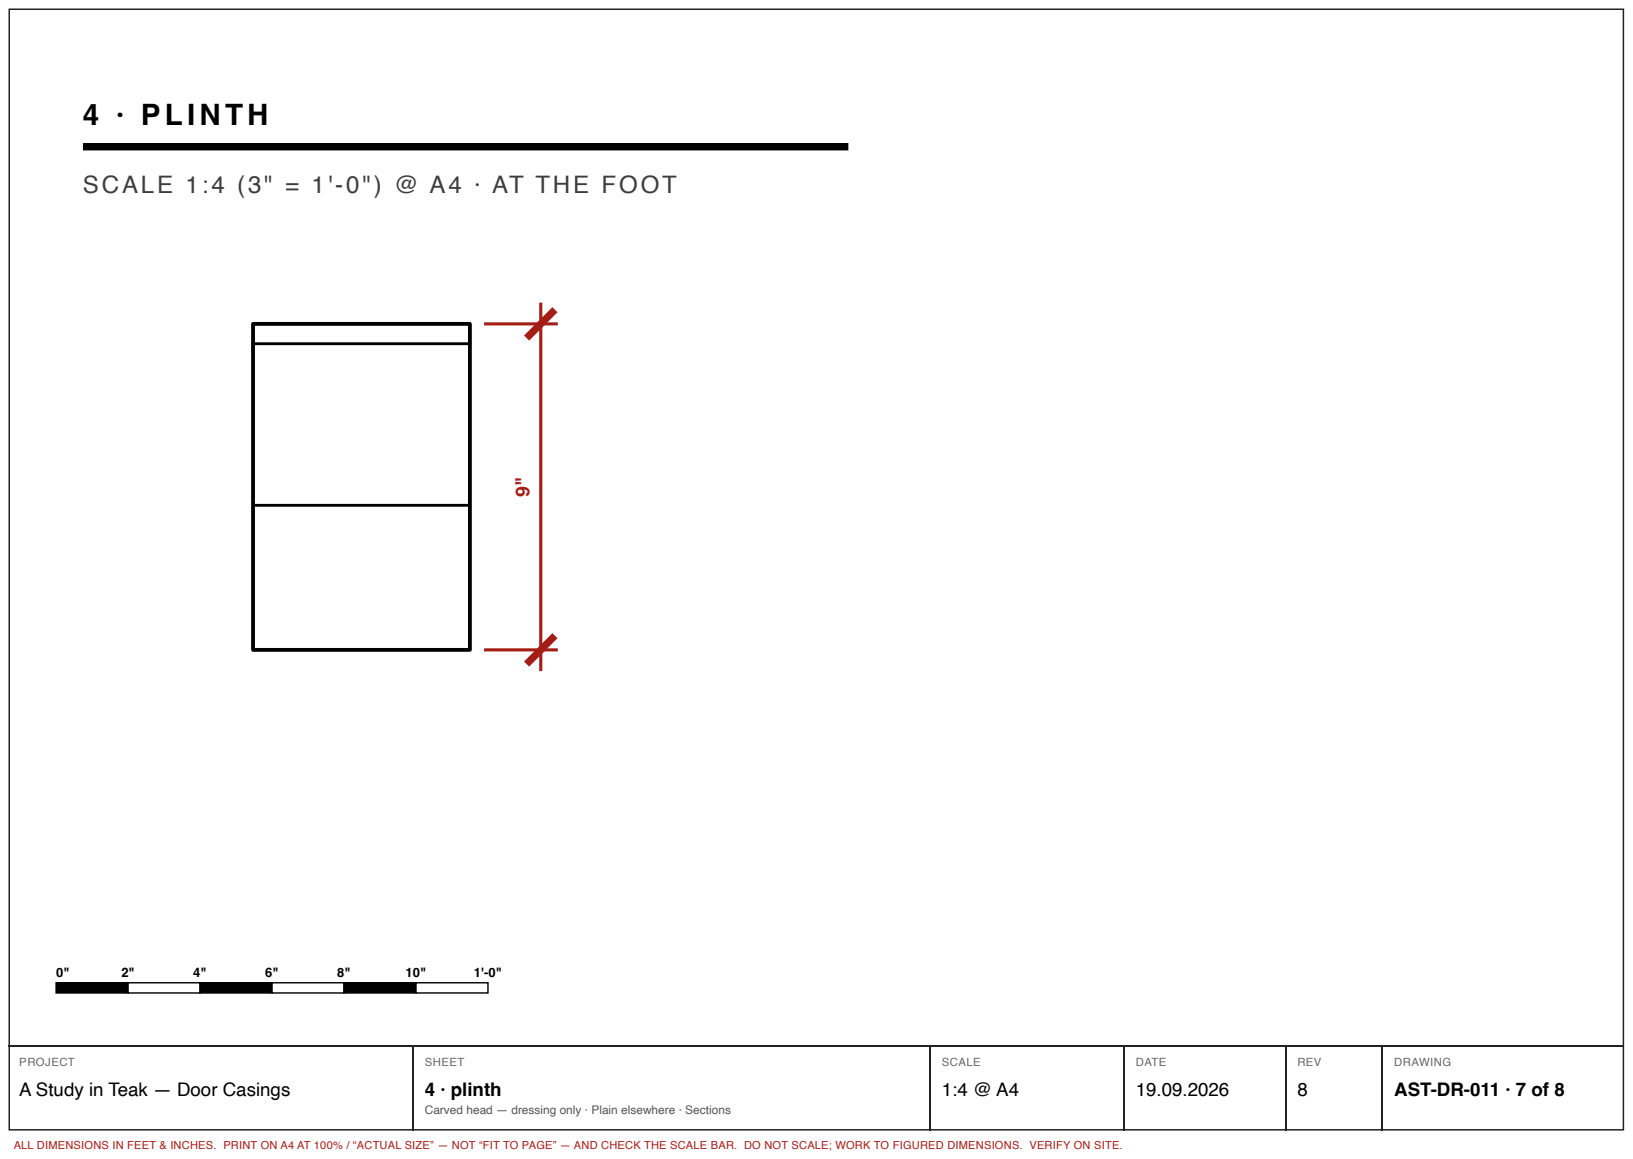
[picture p214: page 7]
4 · plinth

AST-DR-011 · 7 of 8

# RELIEF

DATUM 0 = FACE OF THE PLASTER · LINING AND MOULDING ARE COMMON TO ALL THREE DOORS · THE REST IS THE DRESSING DOOR'S CARVED HEAD

Lining, 2 in on the face | ¼" OUT
Moulding, 4 in, reeded | 1⅛" OUT

## Reed grooves in the moulding face

Corner block, flush with the moulding | 1⅛" OUT
Its sunk panel, two steps | 0¼" AND 0⅜" IN

# Relief

# NTS

# AST-DR-011 · 8 of 8
