sakshampan733-cloud/a-study-in-teak/cad/print/casingb.pdf

DRESSING DOOR

OPTION B · D2 · 2 FT 6 · THE CARVED HEAD

MAIN AND BATHROOM

D1 3 FT · D3 2 FT 6 · PLAIN CASING

1 · THE CORBEL

ELEVATION · THE DRESSING DOOR ONLY

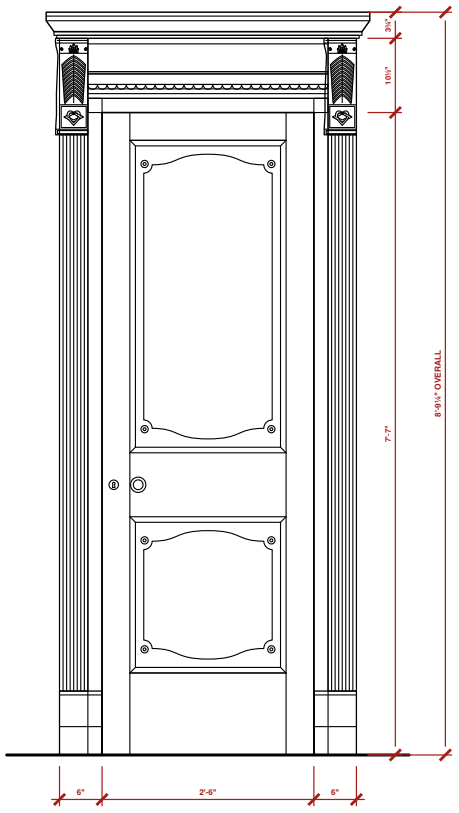
[picture p232: figure]
8'-9¼" OVERALL
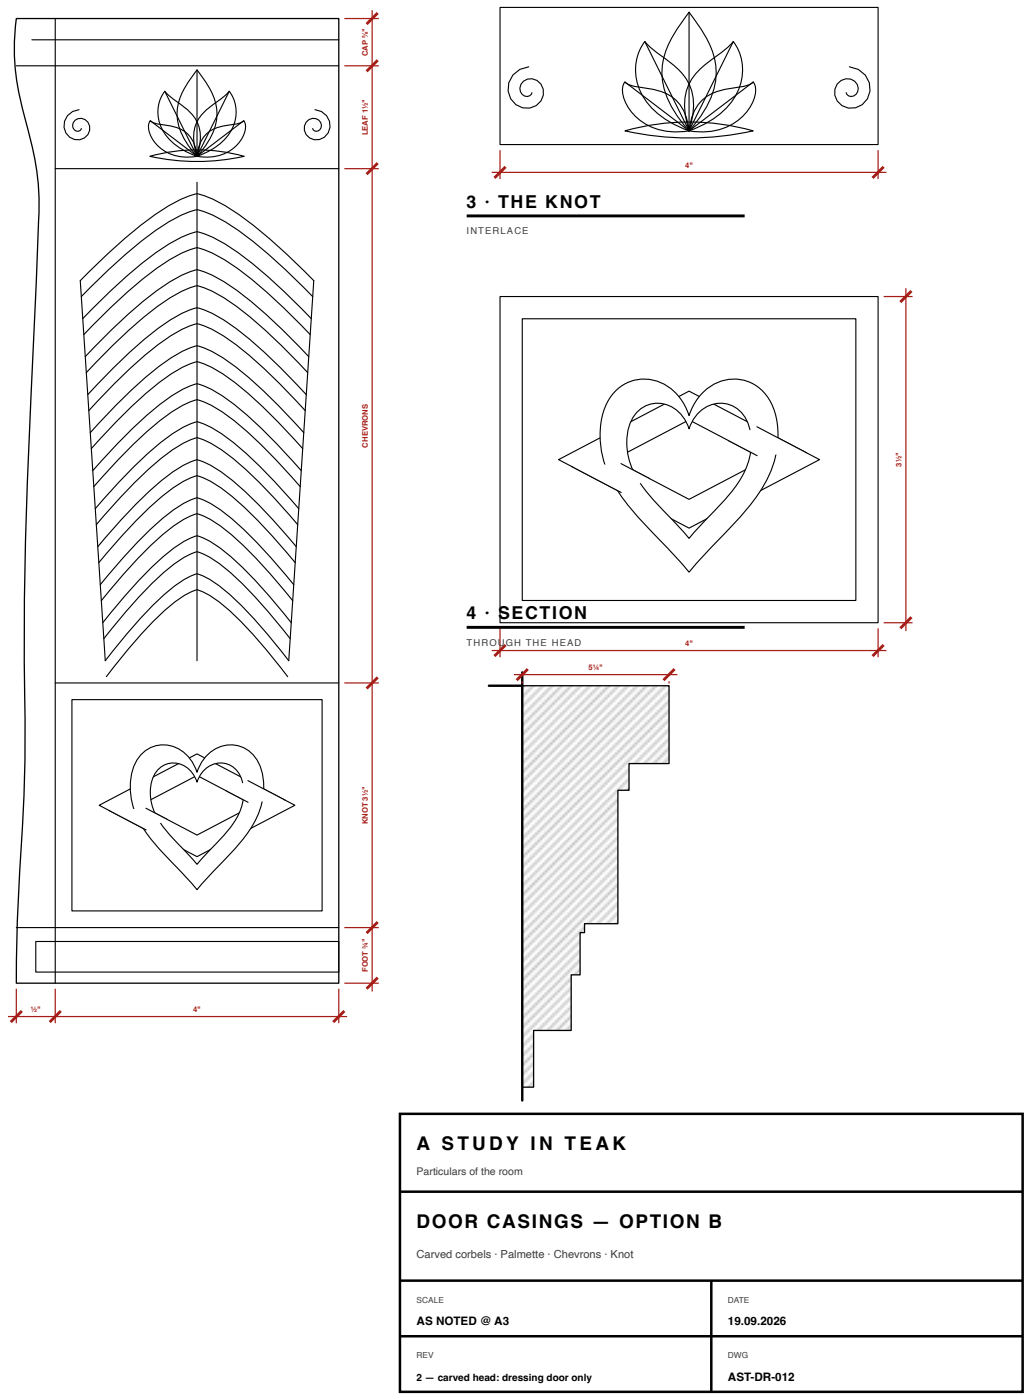
[picture p233: figure]
3 · THE KNOT; INTERLACE; 4 · SECTION; THROUGH THE HEAD; Particulars of the room; DOOR CASINGS — OPTION B; SCALE; AS NOTED @ A3; DATE; REV; 2 — carved head: dressing door only; DWG; AST-DR-012
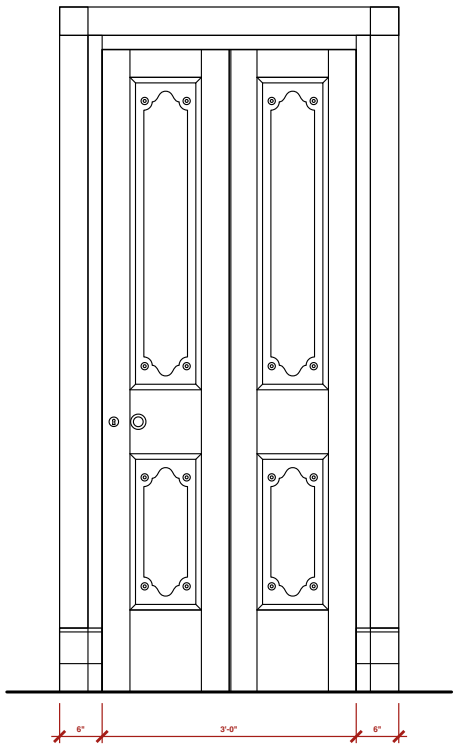
[picture p234: figure]

CAP ⅝" LEAF 1½" CHEVRONS KNOT 3½" FOOT ¾"

2 · THE LEAF

PALMETTE

NOTES

OPTION B · REVISION 2

This is the alternative to AST-DR-011. Below the corbels the two

are the same casing: a 2 in lining with a 4 in reeded moulding

outside it, a plinth block at the foot, the same leaf.

What changes is the head. Option A closes the corner with a

moulded square block. Option B carries it on a carved corbel and

lets the architrave, scallops and frieze die into it.

Each corbel is one piece, standing ½" proud of the casing on the

wall side with a serpentine edge: a palmette under a small cap,

eleven chevrons on a spine, and a shield knot woven through a

lozenge at the foot. Dressing door only — the others go plain.

The crown lands at 8'-9¼" — 3 in higher than Option A — leaving

about 4 in of wall to the ceiling.

Carved corbels · Palmette · Chevrons · Knot

PROJECT

## A Study in Teak — Door Casings — Option B

SHEET

## General arrangement — the whole sheet

each view follows at its own scale, pages 2 to 8

SCALE

## NTS

DATE
19.09.2026

REV

DRAWING

## AST-DR-012 · 1 of 8

ALL DIMENSIONS IN FEET & INCHES. PRINT ON A3 AT 100% / “ACTUAL SIZE” — NOT “FIT TO PAGE” — AND CHECK THE SCALE BAR. DO NOT SCALE; WORK TO FIGURED DIMENSIONS. VERIFY ON SITE.

# DRESSING DOOR

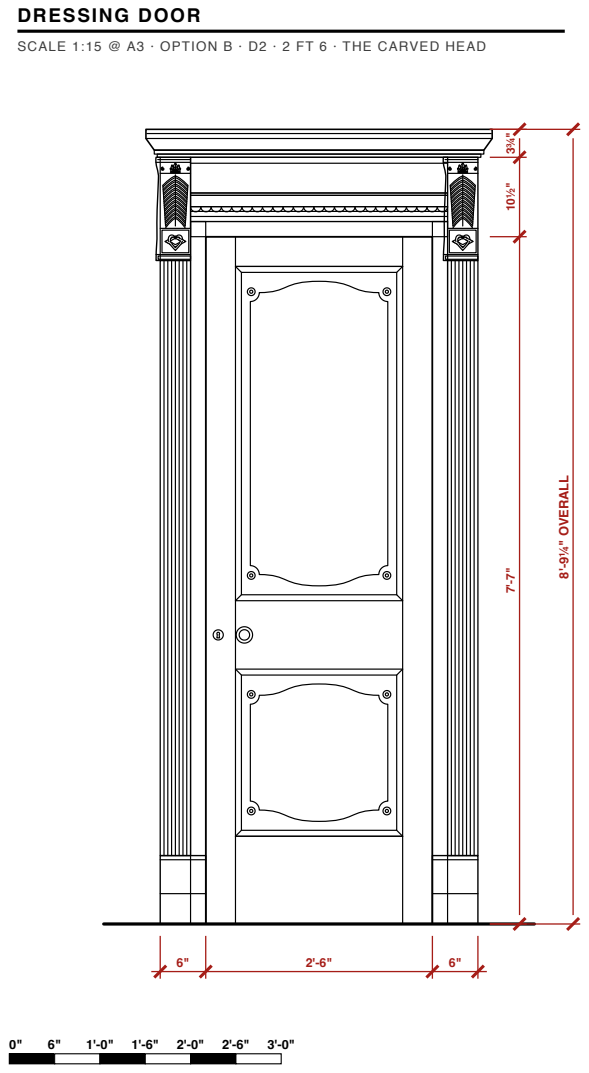
[picture p235: page 2]
VER; ALL; Dressing door

SCALE 1:15 @ A3 · OPTION B · D2 · 2 FT 6 · THE CARVED HEAD

AST-DR-012 · 2 of 8

Carved corbels · Palmette · Chevrons · Knot

### MAIN AND BATHROOM

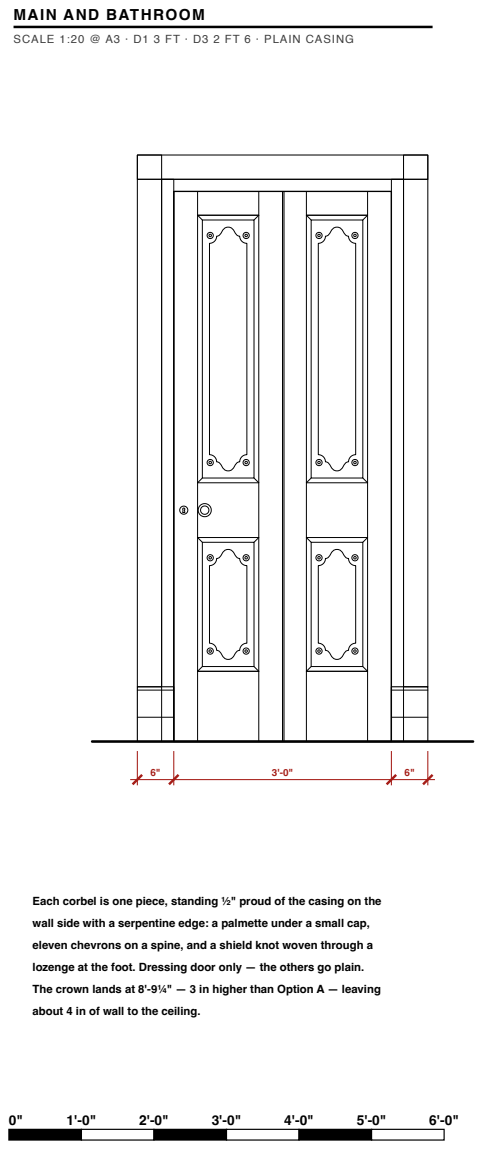
[picture p236: page 3]

SCALE 1:20 @ A3 · D1 3 FT · D3 2 FT 6 · PLAIN CASING

Each corbel is one piece, standing ½" proud of the casing on the

wall side with a serpentine edge: a palmette under a small cap,

eleven chevrons on a spine, and a shield knot woven through a

lozenge at the foot. Dressing door only — the others go plain.

The crown lands at 8'-9¼" — 3 in higher than Option A — leaving

about 4 in of wall to the ceiling.

Main and bathroom

AST-DR-012 · 3 of 8

### 1 · THE CORBEL

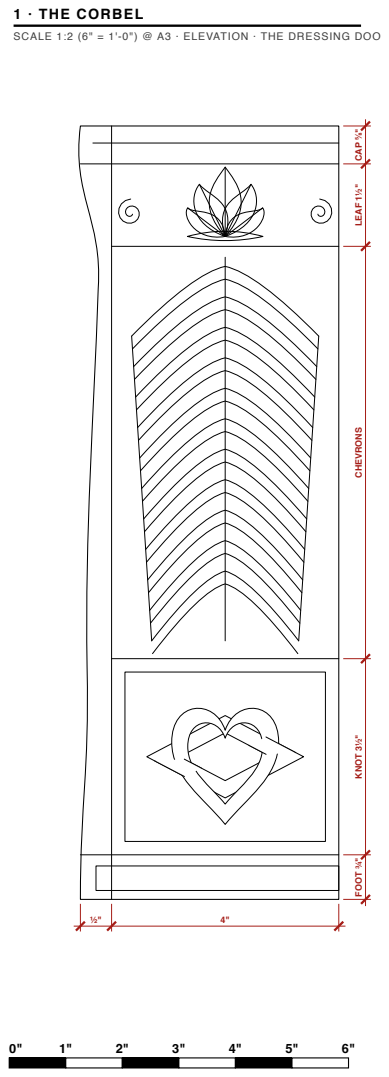
[picture p237: page 4]
1 · the corbel

SCALE 1:2 (6" = 1'-0") @ A3 · ELEVATION · THE DRESSING DOO

CAP ⅝" LEAF 1½" CHEVRONS KNOT 3½" FOOT ¾"

AST-DR-012 · 4 of 8

# 2 · THE LEAF

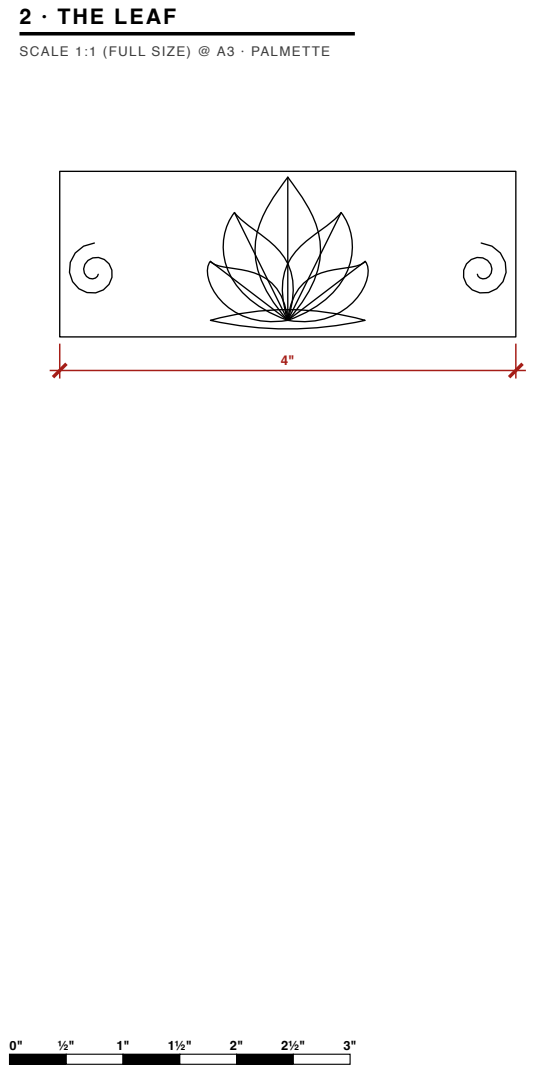
[picture p238: page 5]
2 · the leaf

SCALE 1:1 (FULL SIZE) @ A3 · PALMETTE

AST-DR-012 · 5 of 8

# 3 · THE KNOT

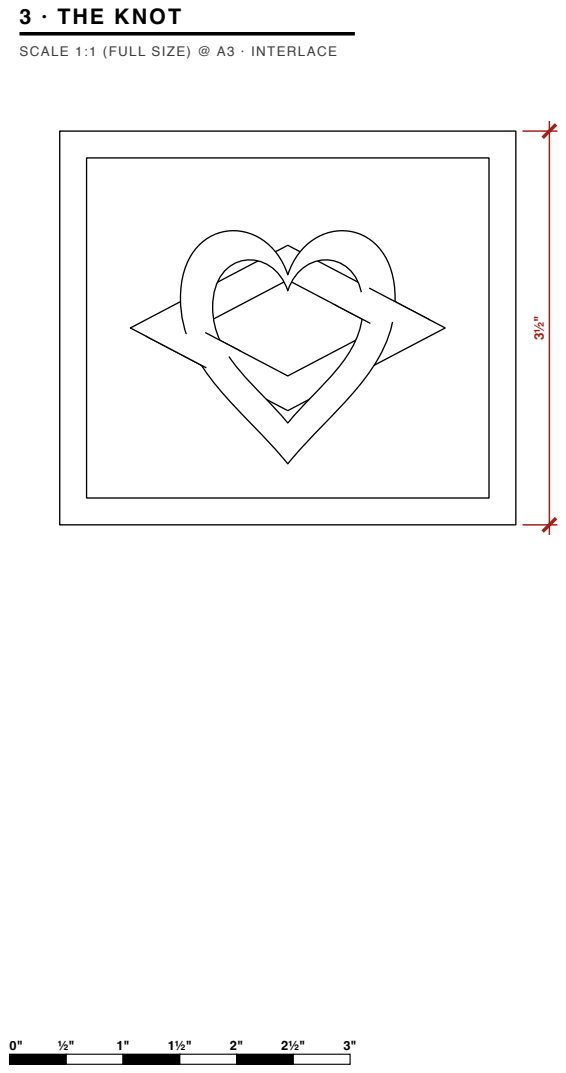
[picture p239: page 6]
3 · the knot

SCALE 1:1 (FULL SIZE) @ A3 · INTERLACE

AST-DR-012 · 6 of 8

4"

# 4 · SECTION

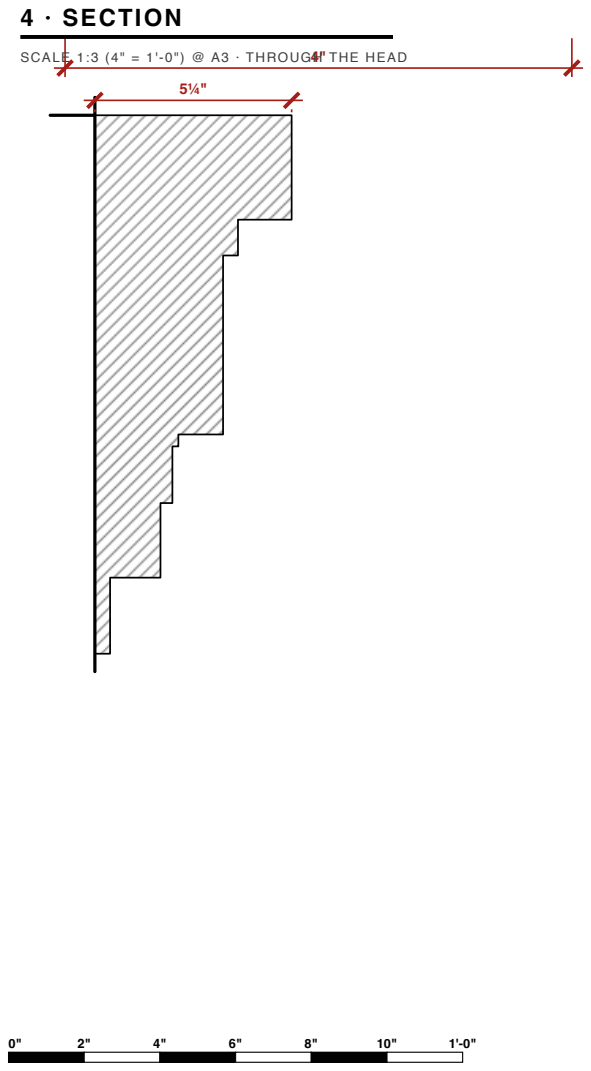
[picture p240: page 7]
4 · section

SCALE 1:3 (4" = 1'-0") @ A3 · THROUGH THE HEAD

AST-DR-012 · 7 of 8

# NOTES

# OPTION B · REVISION 2

# This is the alternative to AST-DR-011. Below the corbels the two

# are the same casing: a 2 in lining with a 4 in reeded moulding

outside it, a plinth block at the foot, the same leaf.

# What changes is the head. Option A closes the corner with a

# moulded square block. Option B carries it on a carved corbel and

lets the architrave, scallops and frieze die into it.

## Notes

## NTS

## AST-DR-012 · 8 of 8
