sakshampan733-cloud/a-study-in-teak/cad/print/desk-a4.pdf

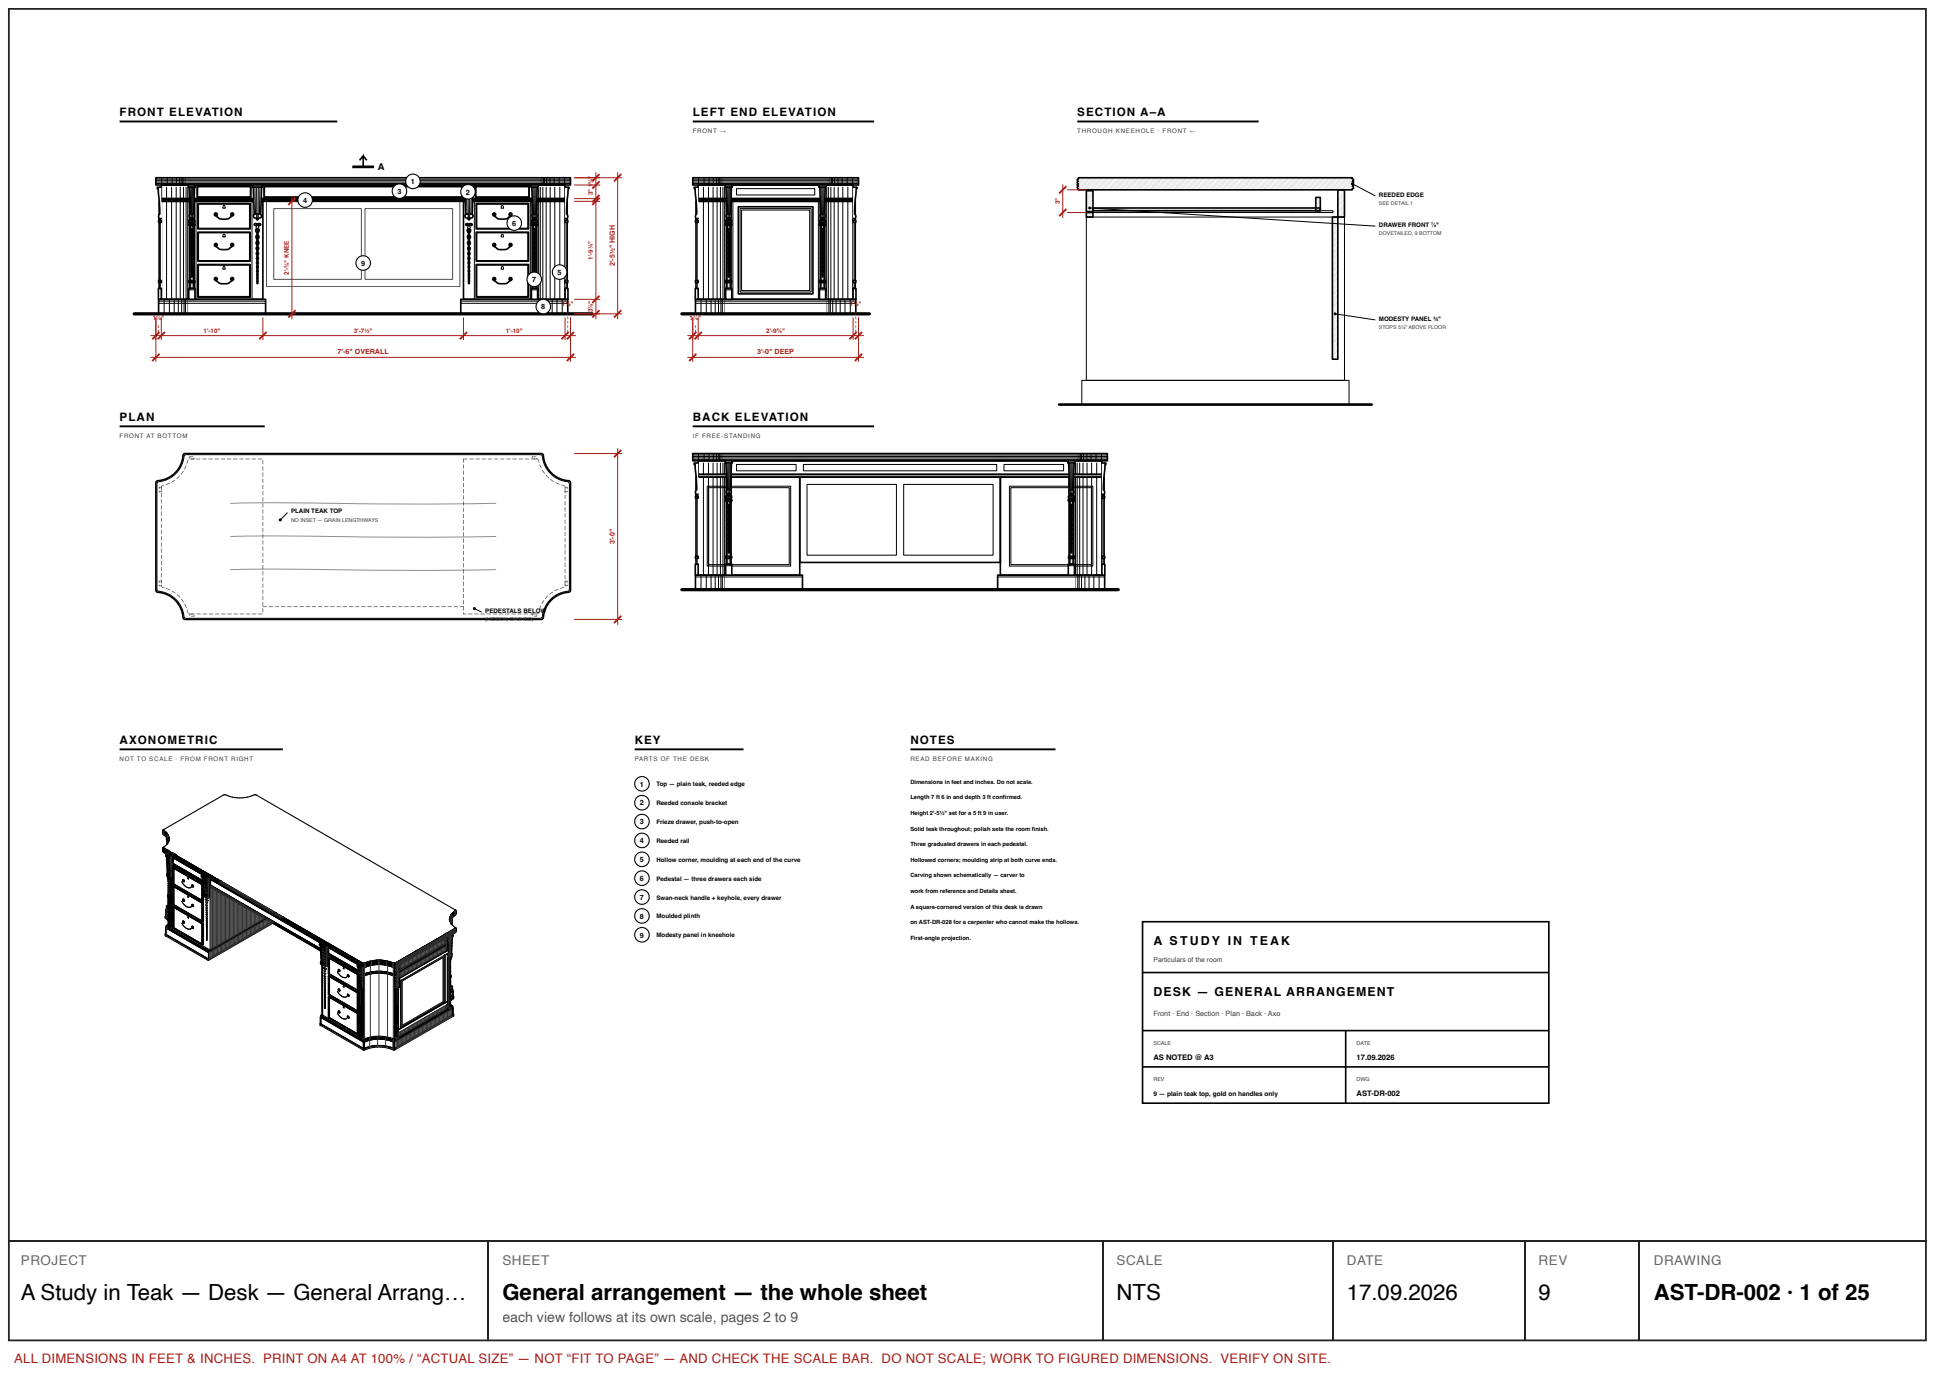
[picture p241: page 1]
FRONT ELEVATION; 7'-6" OVERALL; 2'-5½" HIGH; 2'-⅜" KNEE; FRONT →; 3'-0" DEEP; SECTION A–A; DRAWER FRONT ⅞"; DOVETAILED, 9 BOTTOM; REEDED EDGE; SEE DETAIL 1; PLAN; PEDESTALS BELOW; (HIDDEN, DASHED); BACK ELEVATION; AXONOMETRIC; KEY; 4 Reeded rail; 8 Moulded plinth; NOTES; First-angle projection.; SCALE; AS NOTED @ A3; DATE; REV; DWG; AST-DR-002; SCALE NTS; DATE 17.09.2026

LEFT END ELEVATION

THROUGH KNEEHOLE · FRONT ←

MODESTY PANEL ¾"
STOPS 5⅞" ABOVE FLOOR

FRONT AT BOTTOM

IF FREE-STANDING

PLAIN TEAK TOP
NO INSET — GRAIN LENGTHWAYS

NOT TO SCALE · FROM FRONT RIGHT

PARTS OF THE DESK

READ BEFORE MAKING

1 Top — plain teak, reeded edge

Dimensions in feet and inches. Do not scale.

2 Reeded console bracket

Length 7 ft 6 in and depth 3 ft confirmed.

Height 2'-5½" set for a 5 ft 9 in user.

3 Frieze drawer, push-to-open

Solid teak throughout; polish sets the room finish.

Three graduated drawers in each pedestal.

5 Hollow corner, moulding at each end of the curve

Hollowed corners; moulding strip at both curve ends.

6 Pedestal — three drawers each side

Carving shown schematically — carver to

work from reference and Details sheet.

7 Swan-neck handle + keyhole, every drawer

A square-cornered version of this desk is drawn

on AST-DR-028 for a carpenter who cannot make the hollows.

9 Modesty panel in kneehole

Particulars of the room

DESK — GENERAL ARRANGEMENT

Front · End · Section · Plan · Back · Axo

9 — plain teak top, gold on handles only

PROJECT
A Study in Teak — Desk — General Arrang…

SHEET
General arrangement — the whole sheet

DRAWING
AST-DR-002 · 1 of 25

each view follows at its own scale, pages 2 to 9

ALL DIMENSIONS IN FEET & INCHES. PRINT ON A4 AT 100% / “ACTUAL SIZE” — NOT “FIT TO PAGE” — AND CHECK THE SCALE BAR. DO NOT SCALE; WORK TO FIGURED DIMENSIONS. VERIFY ON SITE.

# FRONT ELEVATION

A

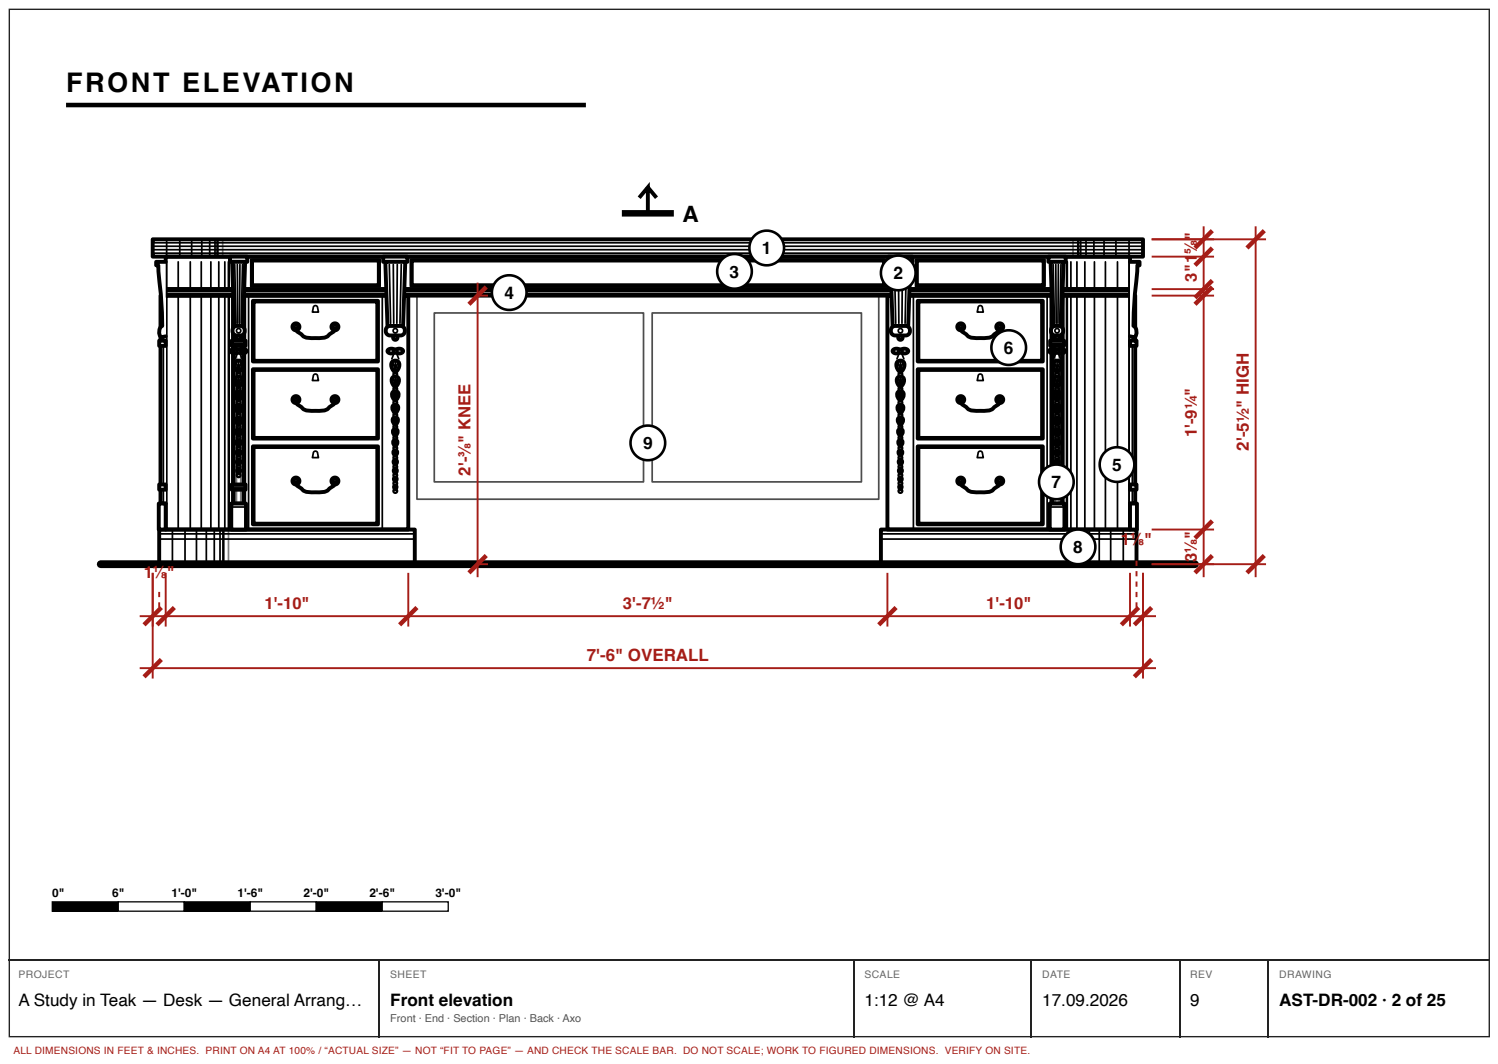
[picture p242: page 2]
7'-6" OVERALL; ½" HIG; Front elevation

A Study in Teak — Desk — General Arrang…

AST-DR-002 · 2 of 25

Front · End · Section · Plan · Back · Axo

# LEFT END ELEVATION

# SCALE 1:10 @ A4 · FRONT →

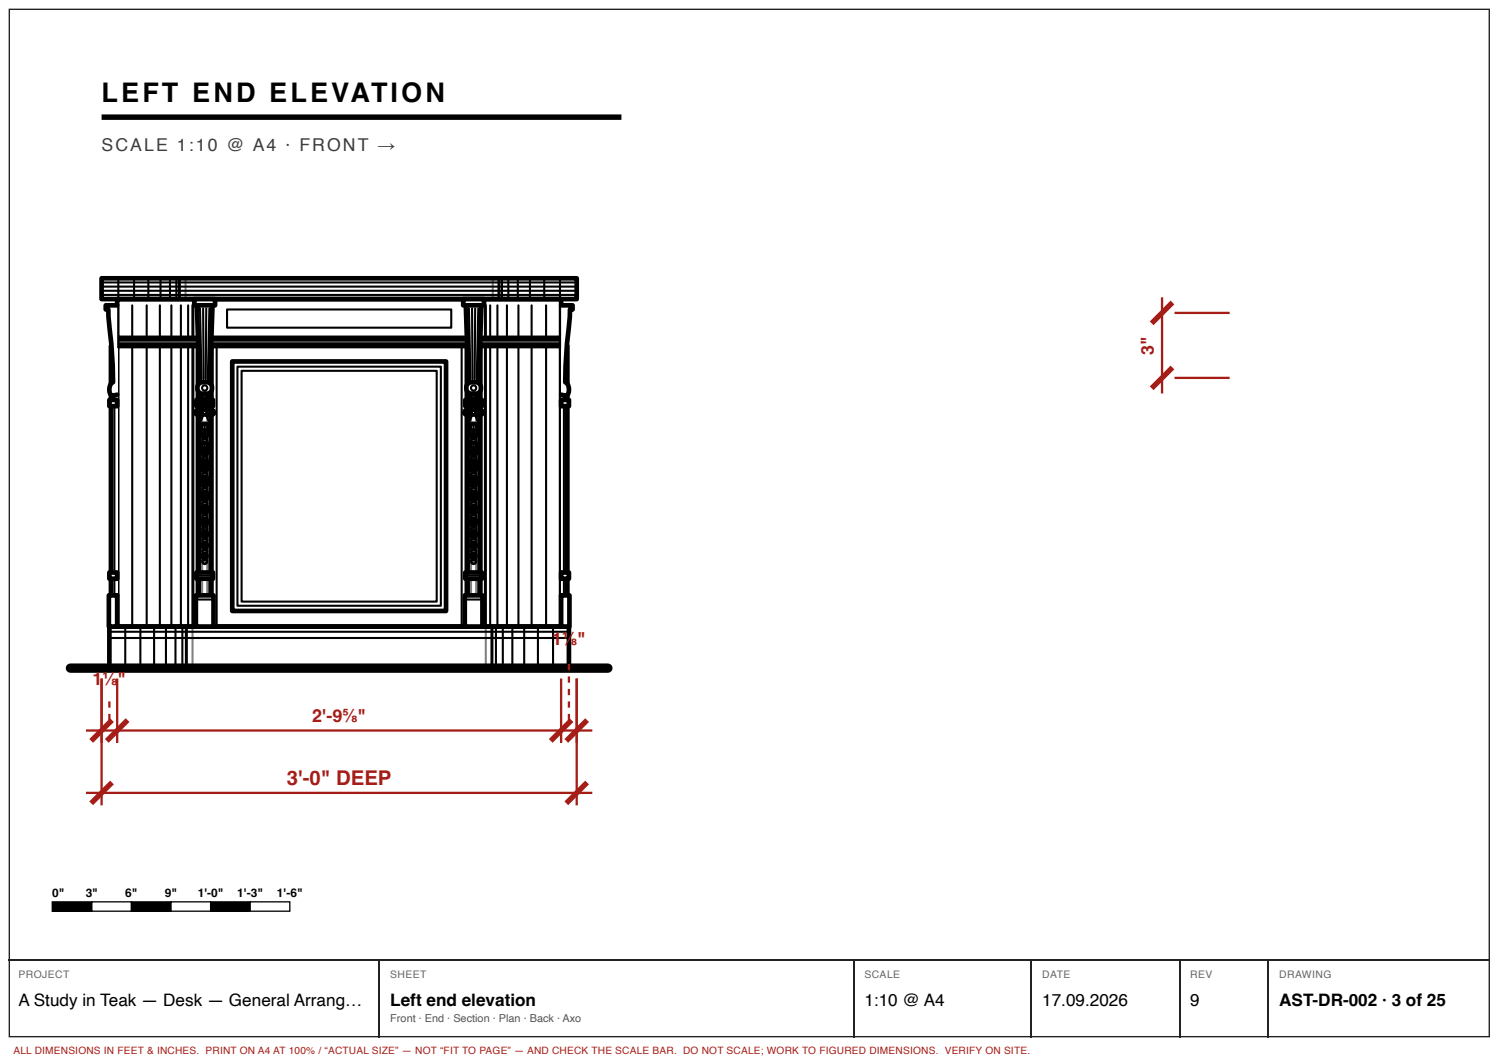
[picture p243: page 3]
3'-0" DEEP

A Study in Teak — Desk — General Arrang…

Left end elevation

AST-DR-002 · 3 of 25

Front · End · Section · Plan · Back · Axo

# SECTION A–A

### SCALE 1:8 (1½" = 1'-0") @ A4 · THROUGH KNEEHOLE · FRONT ←

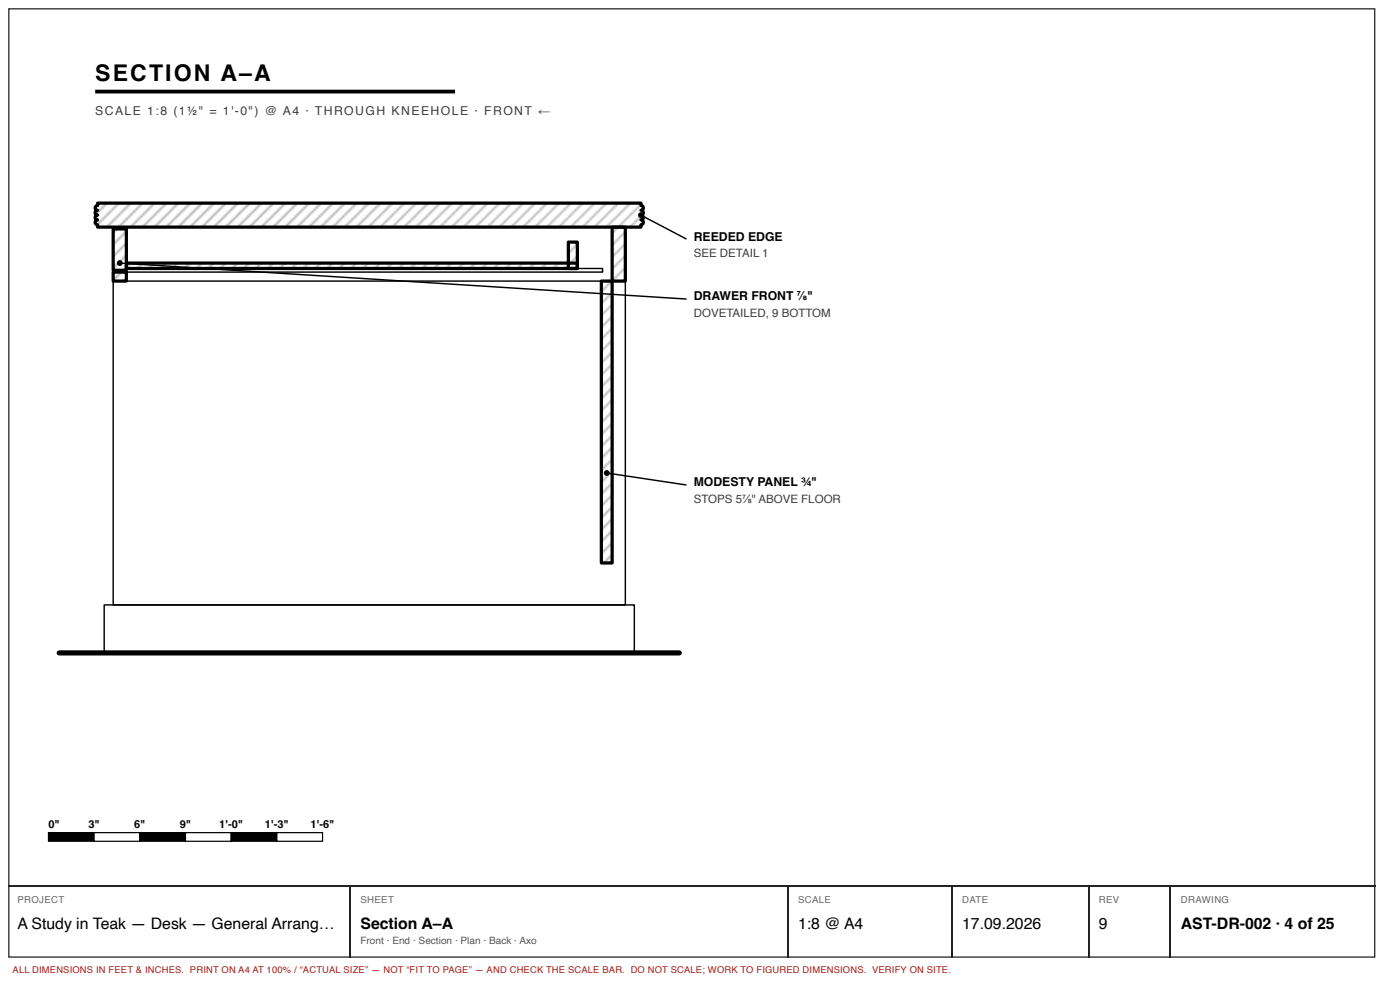
[picture p244: page 4]
DRAWER FRONT ⅞"; DOVETAILED, 9 BOTTOM; REEDED EDGE SEE DETAIL 1; Section A–A

MODESTY PANEL ¾"
STOPS 5⅞" ABOVE FLOOR

A Study in Teak — Desk — General Arrang…

AST-DR-002 · 4 of 25

Front · End · Section · Plan · Back · Axo

# PLAN

## SCALE 1:12 (1" = 1'-0") @ A4 · FRONT AT BOTTOM

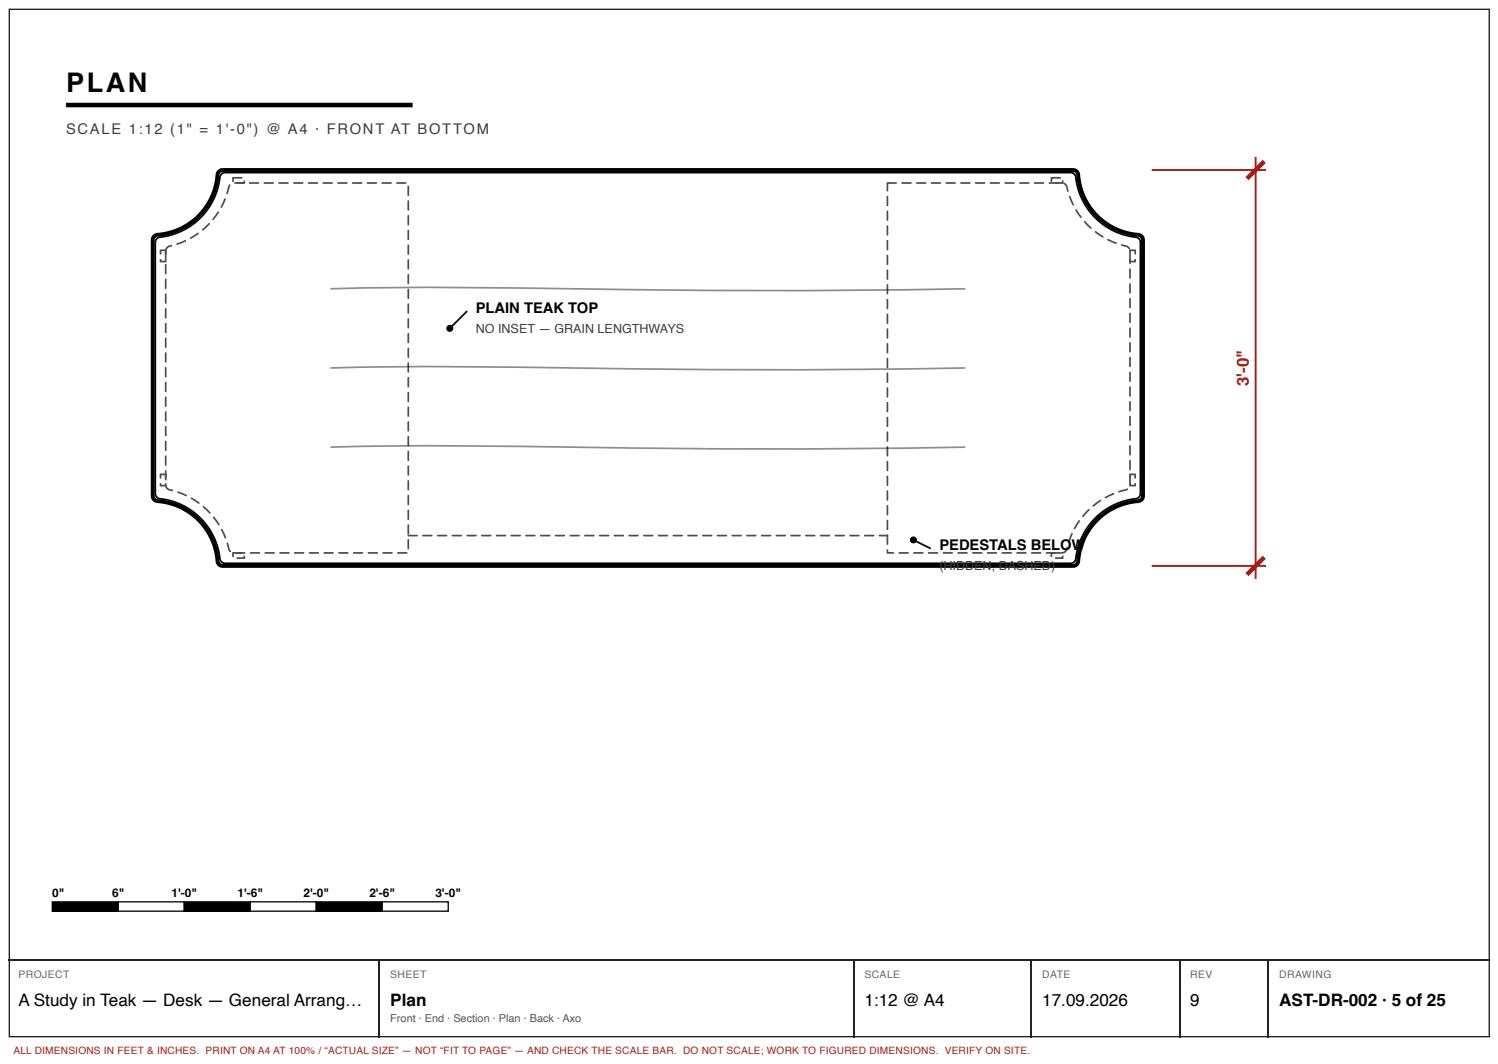
[picture p245: page 5]
PEDESTALS BELOW; (HIDDEN, DASHED); Plan

PLAIN TEAK TOP
NO INSET — GRAIN LENGTHWAYS

A Study in Teak — Desk — General Arrang…

AST-DR-002 · 5 of 25

Front · End · Section · Plan · Back · Axo

# BACK ELEVATION

# SCALE 1:10 @ A4 · IF FREE-STANDING

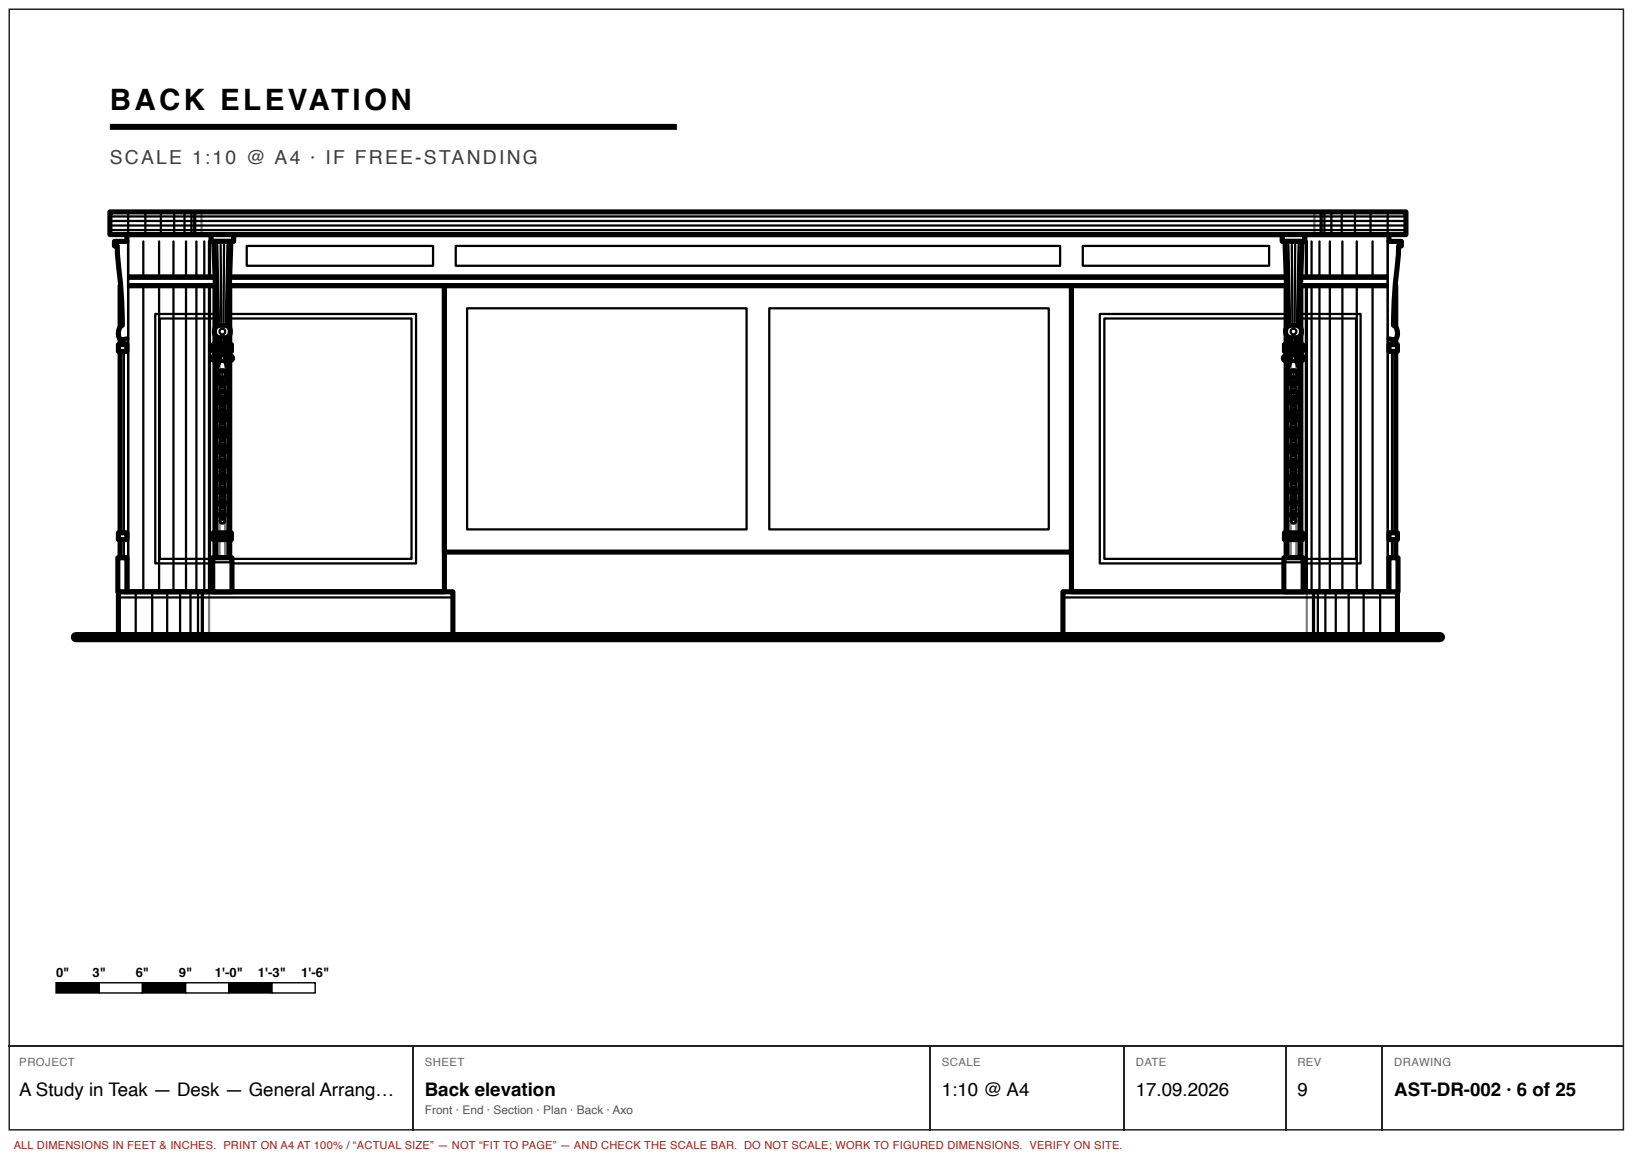
[picture p246: page 6]
Back elevation

A Study in Teak — Desk — General Arrang…

AST-DR-002 · 6 of 25

Front · End · Section · Plan · Back · Axo

# AXONOMETRIC

## NOT TO SCALE · NOT TO SCALE · FROM FRONT RIGHT

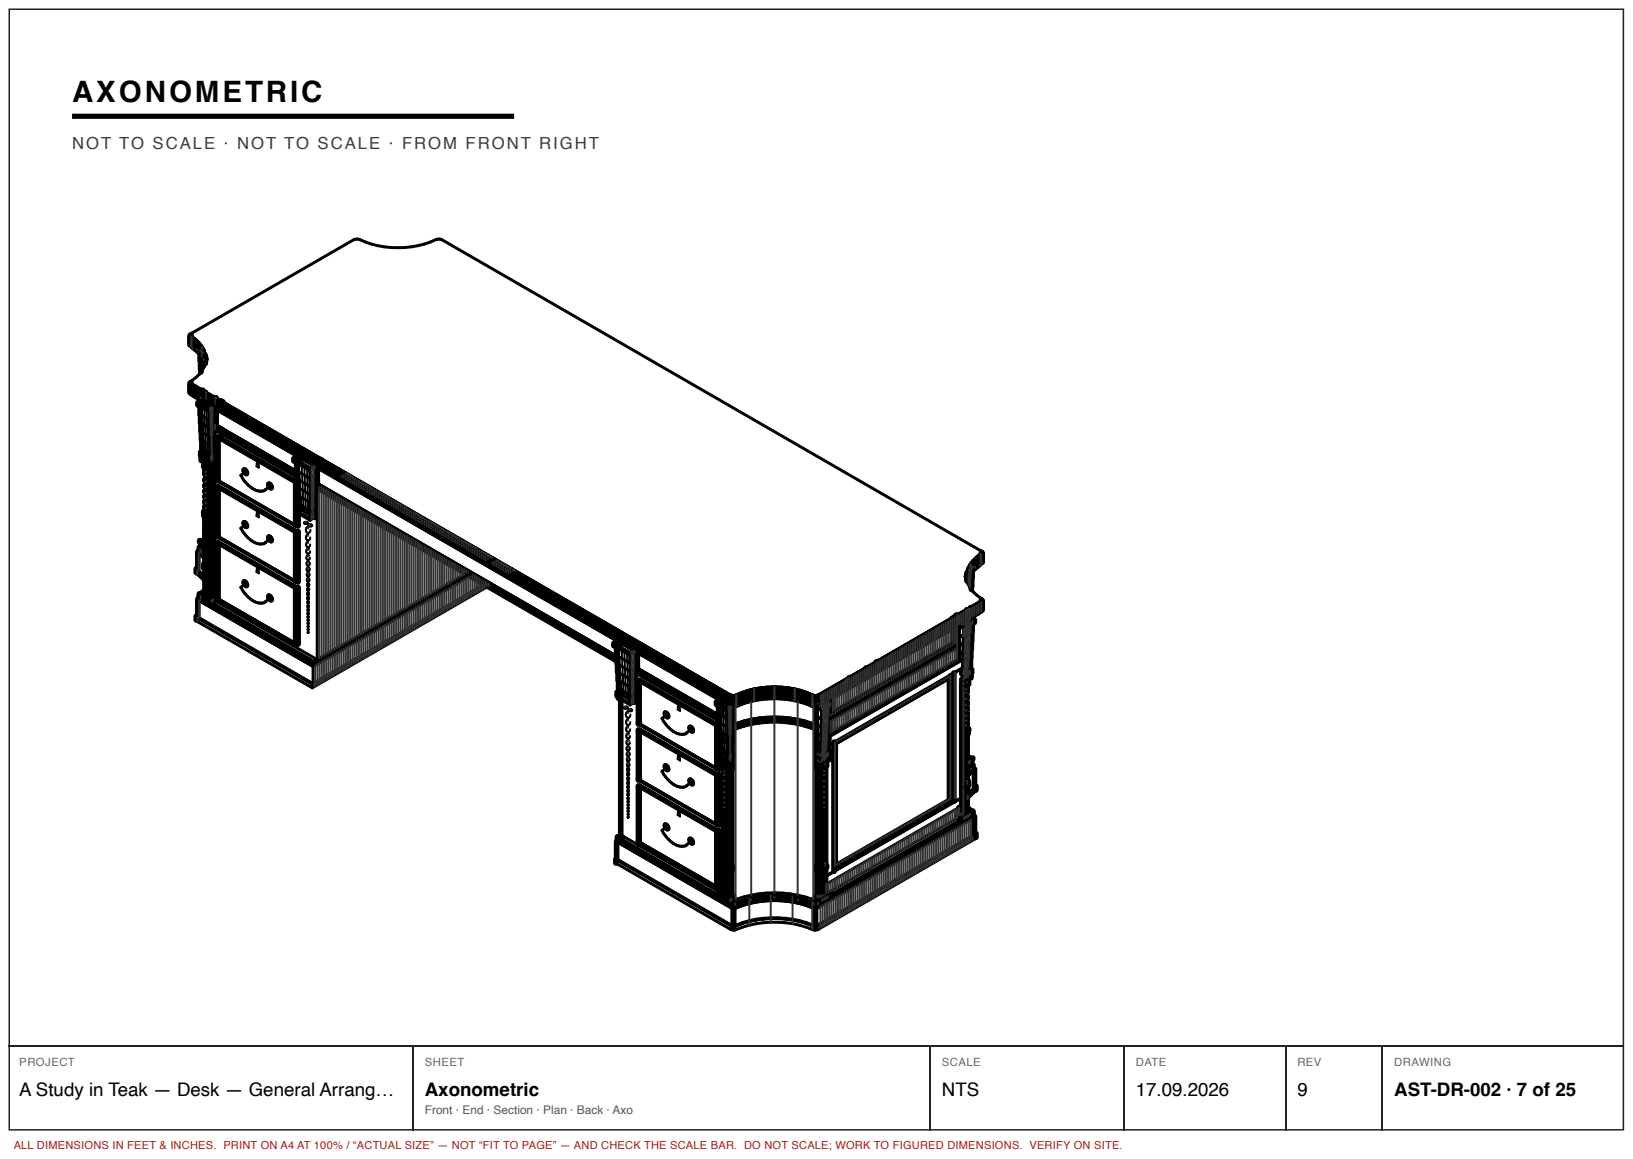
[picture p247: page 7]
Axonometric

A Study in Teak — Desk — General Arrang…

AST-DR-002 · 7 of 25

Front · End · Section · Plan · Back · Axo

# K EY

# PARTS OF THE DESK

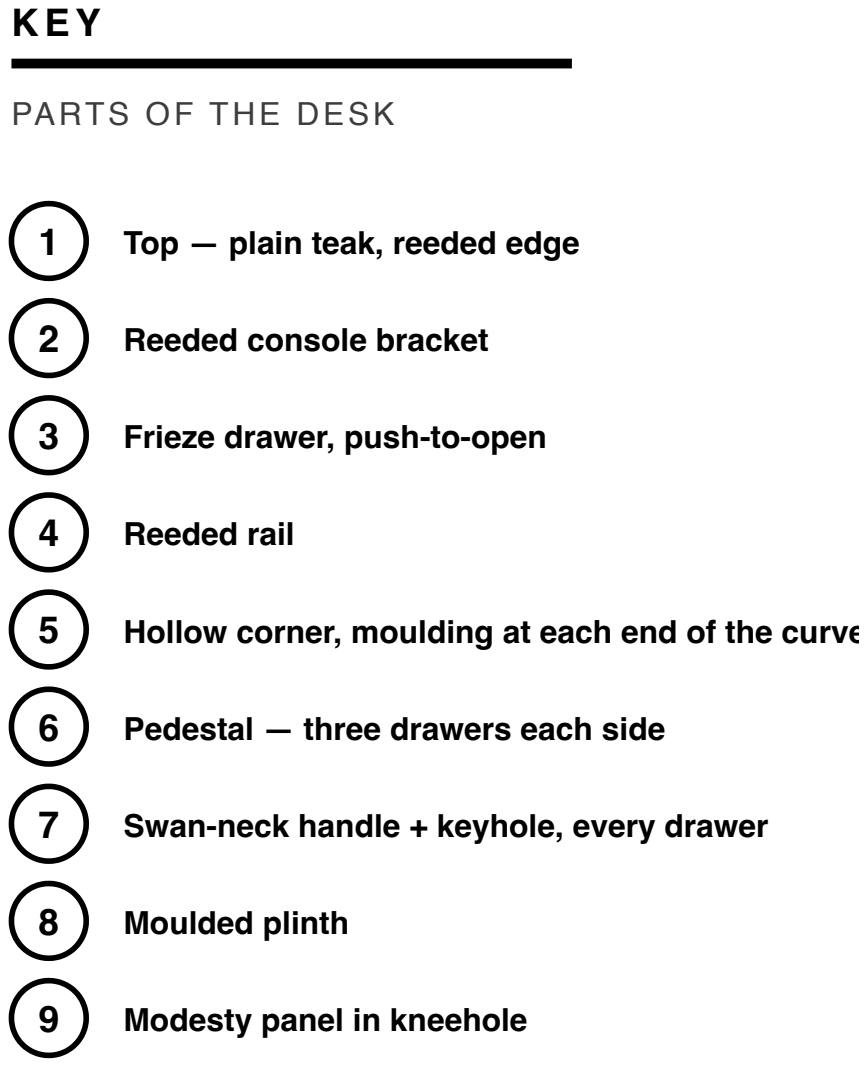
[picture p248: page 8]
4 Reeded rail; 8 Moulded plinth; Key

1 Top — plain teak, reeded edge

2 Reeded console bracket

3 Frieze drawer, push-to-open

5 Hollow corner, moulding at each end of the curve

6 Pedestal — three drawers each side

7 Swan-neck handle + keyhole, every drawer

9 Modesty panel in kneehole

A Study in Teak — Desk — General Arrang…

AST-DR-002 · 8 of 25

Front · End · Section · Plan · Back · Axo

# NOTES

# READ BEFORE MAKING

Dimensions in feet and inches. Do not scale.

Length 7 ft 6 in and depth 3 ft confirmed.

Height 2'-5½" set for a 5 ft 9 in user.

Solid teak throughout; polish sets the room finish.

Three graduated drawers in each pedestal.

Hollowed corners; moulding strip at both curve ends.

# Carving shown schematically — carver to

work from reference and Details sheet.

# A square-cornered version of this desk is drawn

on AST-DR-028 for a carpenter who cannot make the hollows.

First-angle projection.

# A Study in Teak — Desk — General Arrang…

# Notes

Front · End · Section · Plan · Back · Axo

# AST-DR-002 · 9 of 25

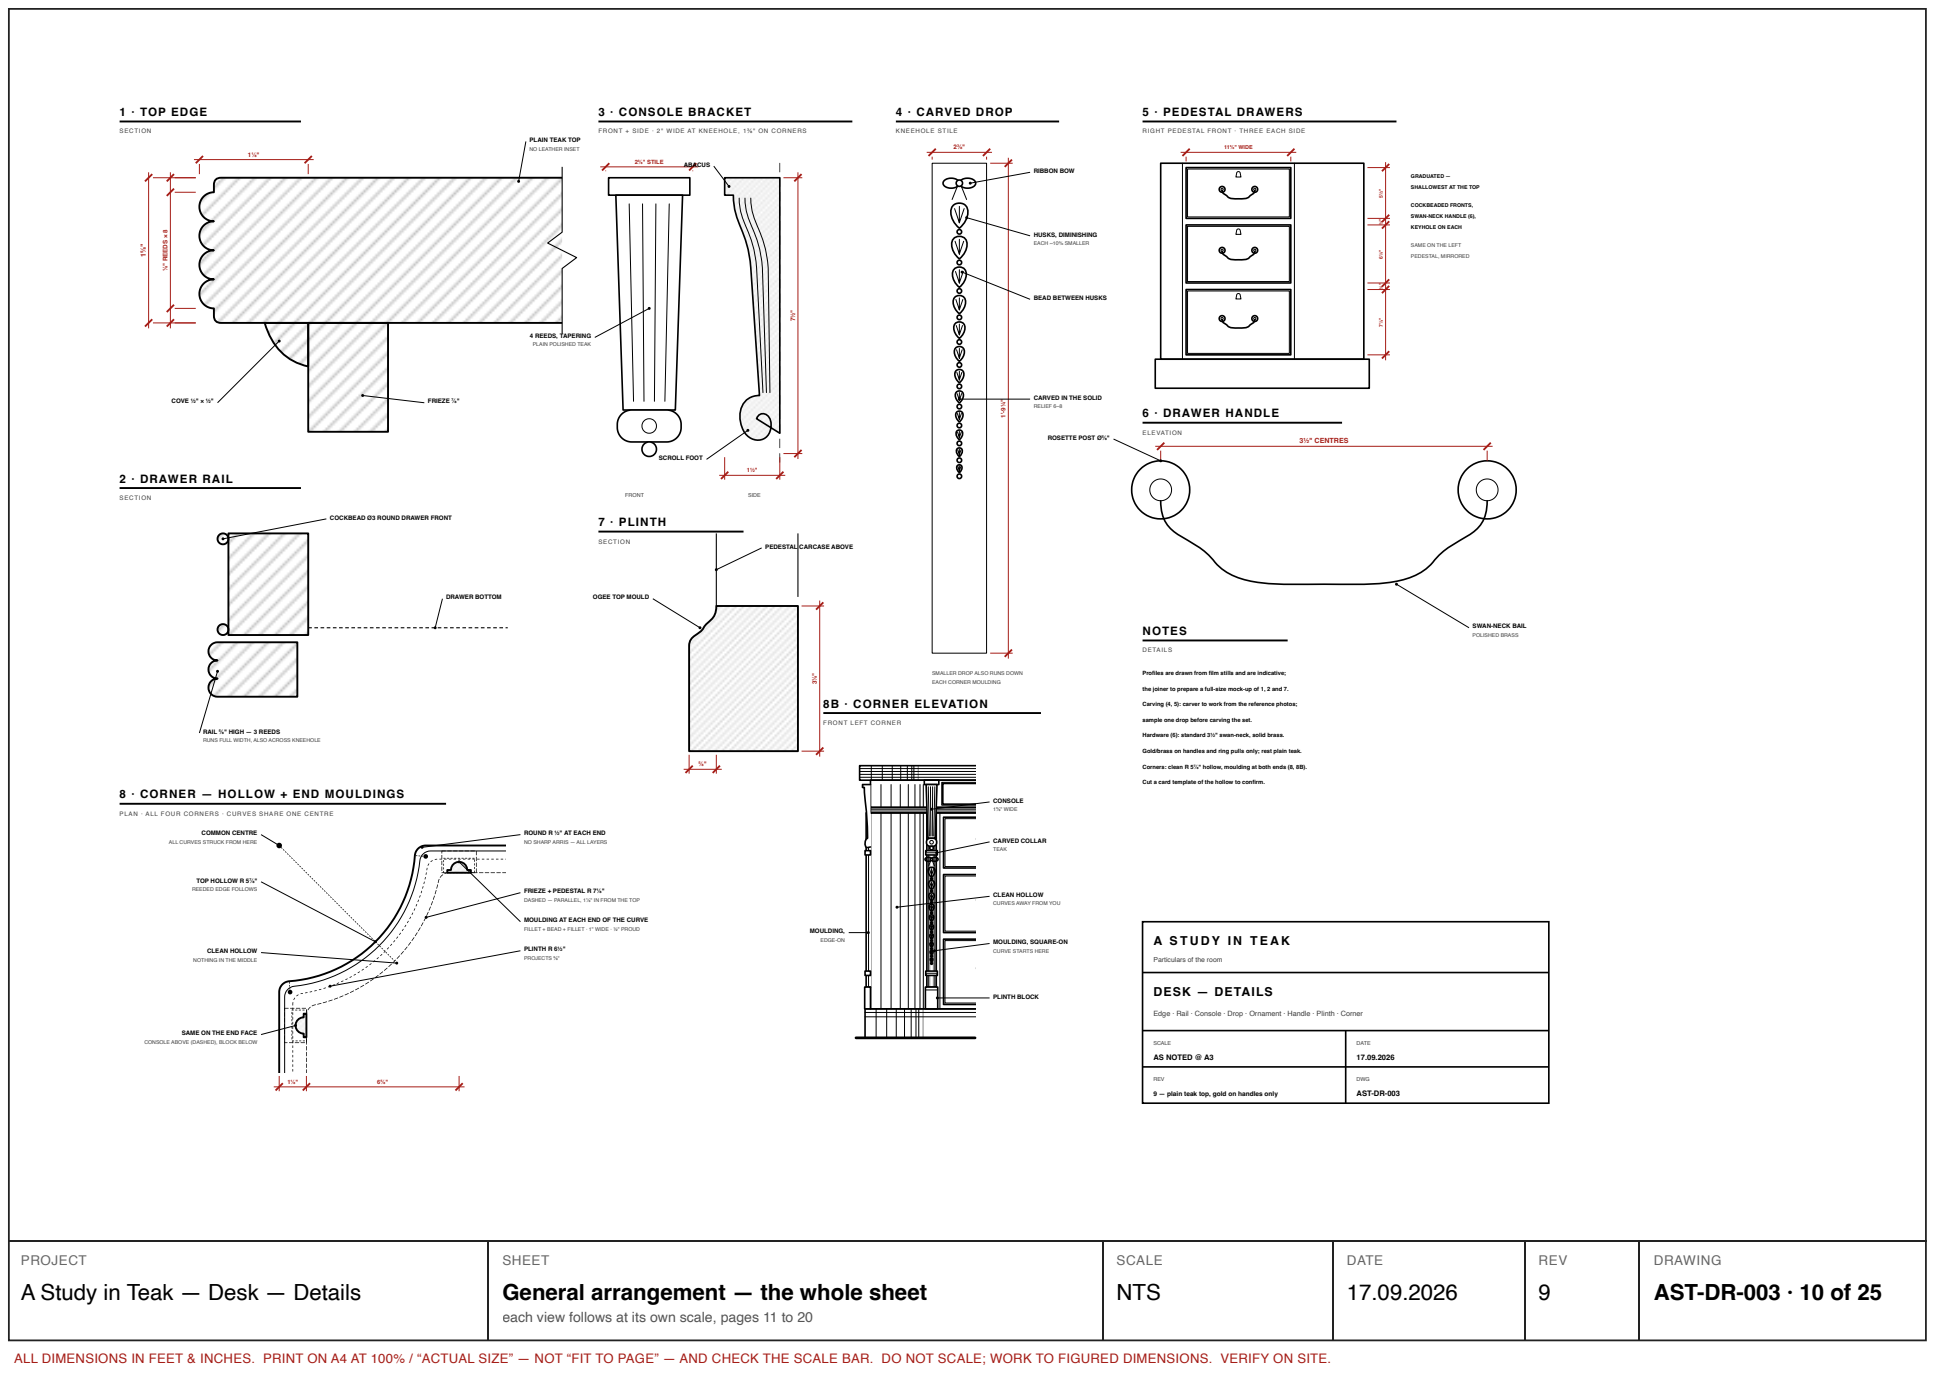
[picture p249: page 10]
1 · TOP EDGE; SECTION; ⅛" REEDS × 8; COVE ½" × ½"; FRIEZE ⅞"; 2 · DRAWER RAIL; DRAWER BOTTOM; 3 · CONSOLE BRACKET; 2⅜" STILE; FRONT; SIDE; ABACUS; SCROLL FOOT; 4 · CARVED DROP; KNEEHOLE STILE; RIBBON BOW; HUSKS, DIMINISHING; EACH ~10% SMALLER; 5 · PEDESTAL DRAWERS; 11⅜" WIDE; GRADUATED —; COCKBEADED FRONTS,; PEDESTAL, MIRRORED; 6 · DRAWER HANDLE; ELEVATION; 3½" CENTRES; POLISHED BRASS; 7 · PLINTH; COMMON CENTRE; TOP HOLLOW R 5⅞"; FRIEZE + PEDESTAL R 7⅛"; PLINTH R 6½"; PROJECTS ⅝"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

FRONT + SIDE · 2" WIDE AT KNEEHOLE, 1⅜" ON CORNERS

PLAIN TEAK TOP

NO LEATHER INSET

RIGHT PEDESTAL FRONT · THREE EACH SIDE

SHALLOWEST AT THE TOP

SWAN-NECK HANDLE (6),

KEYHOLE ON EACH

SAME ON THE LEFT

BEAD BETWEEN HUSKS

4 REEDS, TAPERING
PLAIN POLISHED TEAK

CARVED IN THE SOLID
RELIEF 6–8

ROSETTE POST Ø⅝"

COCKBEAD Ø3 ROUND DRAWER FRONT

PEDESTAL CARCASE ABOVE

OGEE TOP MOULD

SWAN-NECK BAIL

SMALLER DROP ALSO RUNS DOWN

EACH CORNER MOULDING

Profiles are drawn from film stills and are indicative;

the joiner to prepare a full-size mock-up of 1, 2 and 7.

Carving (4, 5): carver to work from the reference photos;

sample one drop before carving the set.

RAIL ⅝" HIGH — 3 REEDS

FRONT LEFT CORNER

Hardware (6): standard 3½" swan-neck, solid brass.

RUNS FULL WIDTH, ALSO ACROSS KNEEHOLE

Gold/brass on handles and ring pulls only; rest plain teak.

Corners: clean R 5⅞" hollow, moulding at both ends (8, 8B).

8 · CORNER — HOLLOW + END MOULDINGS

Cut a card template of the hollow to confirm.

PLAN · ALL FOUR CORNERS · CURVES SHARE ONE CENTRE

ROUND R ½" AT EACH END
NO SHARP ARRIS — ALL LAYERS

ALL CURVES STRUCK FROM HERE

REEDED EDGE FOLLOWS

DASHED — PARALLEL, 1⅛" IN FROM THE TOP

CURVES AWAY FROM YOU

MOULDING AT EACH END OF THE CURVE

FILLET + BEAD + FILLET · 1" WIDE · ½" PROUD

MOULDING, SQUARE-ON

CLEAN HOLLOW
NOTHING IN THE MIDDLE

CURVE STARTS HERE

Particulars of the room

Edge · Rail · Console · Drop · Ornament · Handle · Plinth · Corner

CONSOLE ABOVE (DASHED), BLOCK BELOW

SAME ON THE END FACE

9 — plain teak top, gold on handles only

A Study in Teak — Desk — Details

General arrangement — the whole sheet

AST-DR-003 · 10 of 25

each view follows at its own scale, pages 11 to 20

## 1 · TOP EDGE

1⅛"

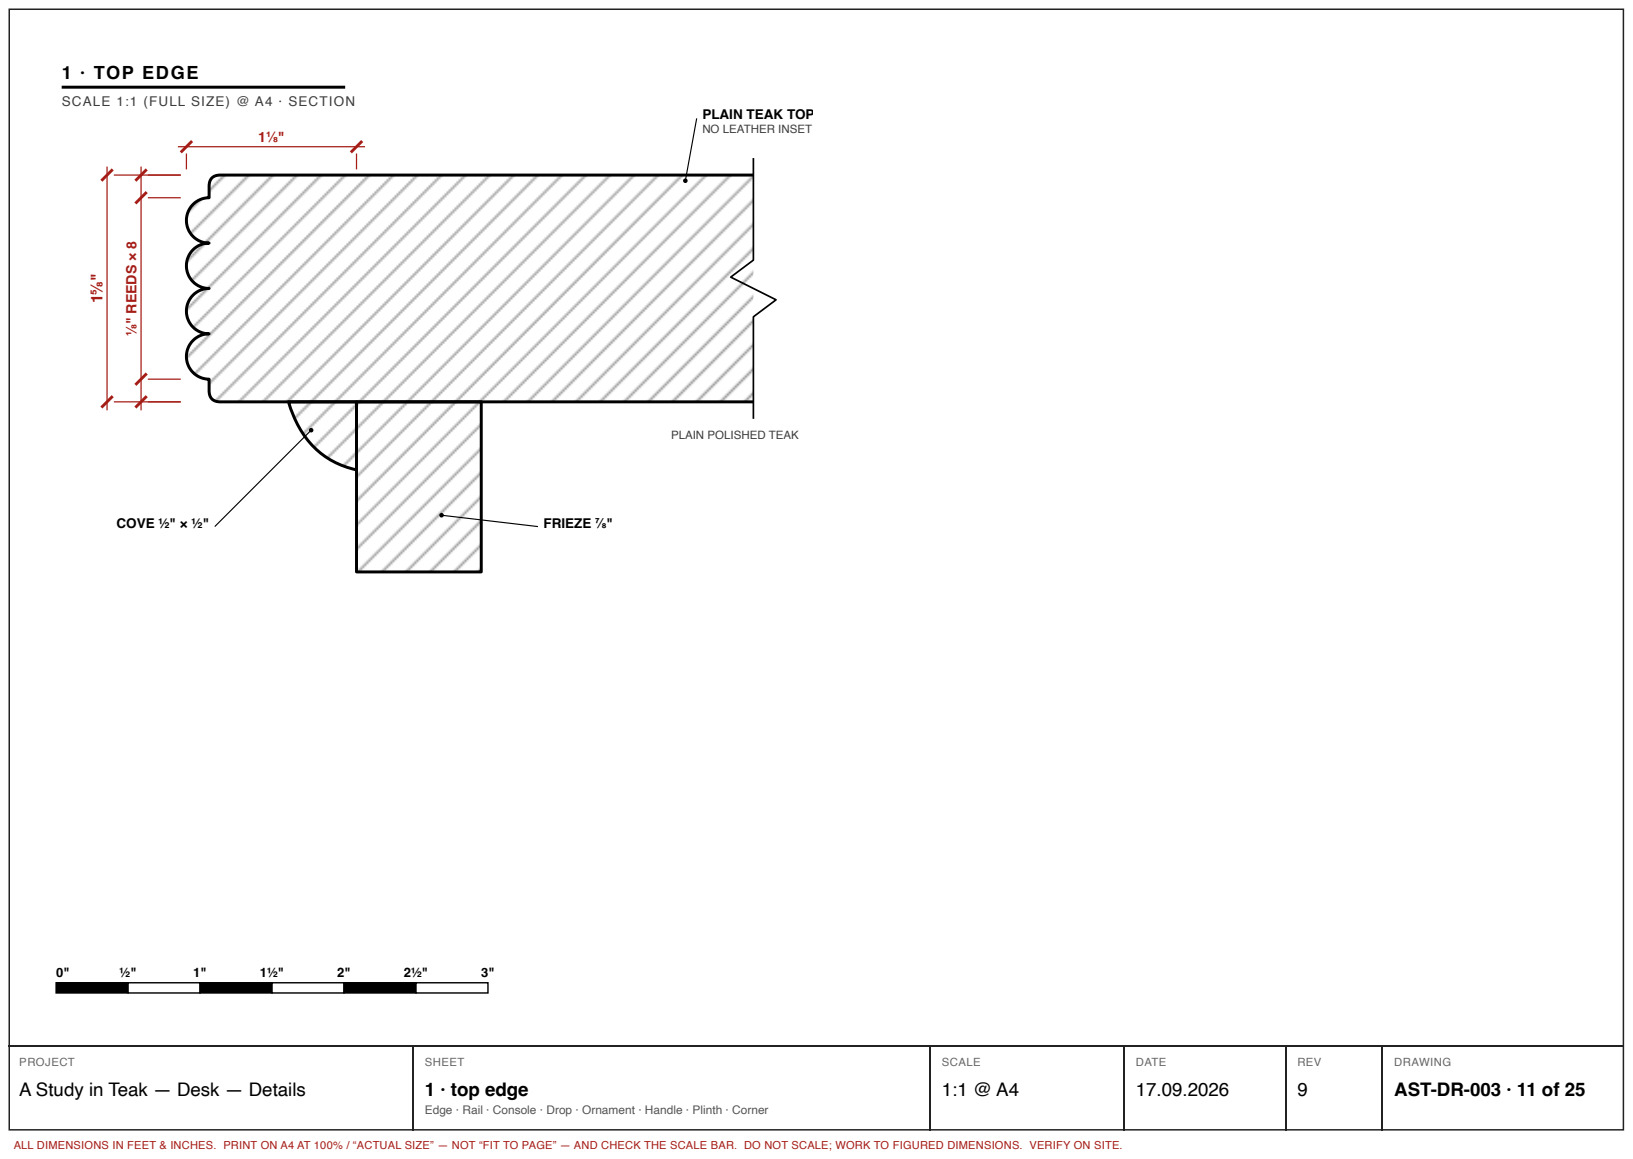
[picture p250: page 11]
⅛" REEDS × 8; COVE ½" × ½"; FRIEZE ⅞"; 1 · top edge

SCALE 1:1 (FULL SIZE) @ A4 · SECTION

PLAIN TEAK TOP
NO LEATHER INSET

PLAIN POLISHED TEAK

AST-DR-003 · 11 of 25

Edge · Rail · Console · Drop · Ornament · Handle · Plinth · Corner

# 3 · CONSOLE BRACKET

### SCALE 1:2 (6" = 1'-0") @ A4 · FRONT + SIDE · 2" WIDE AT KNEEHOL

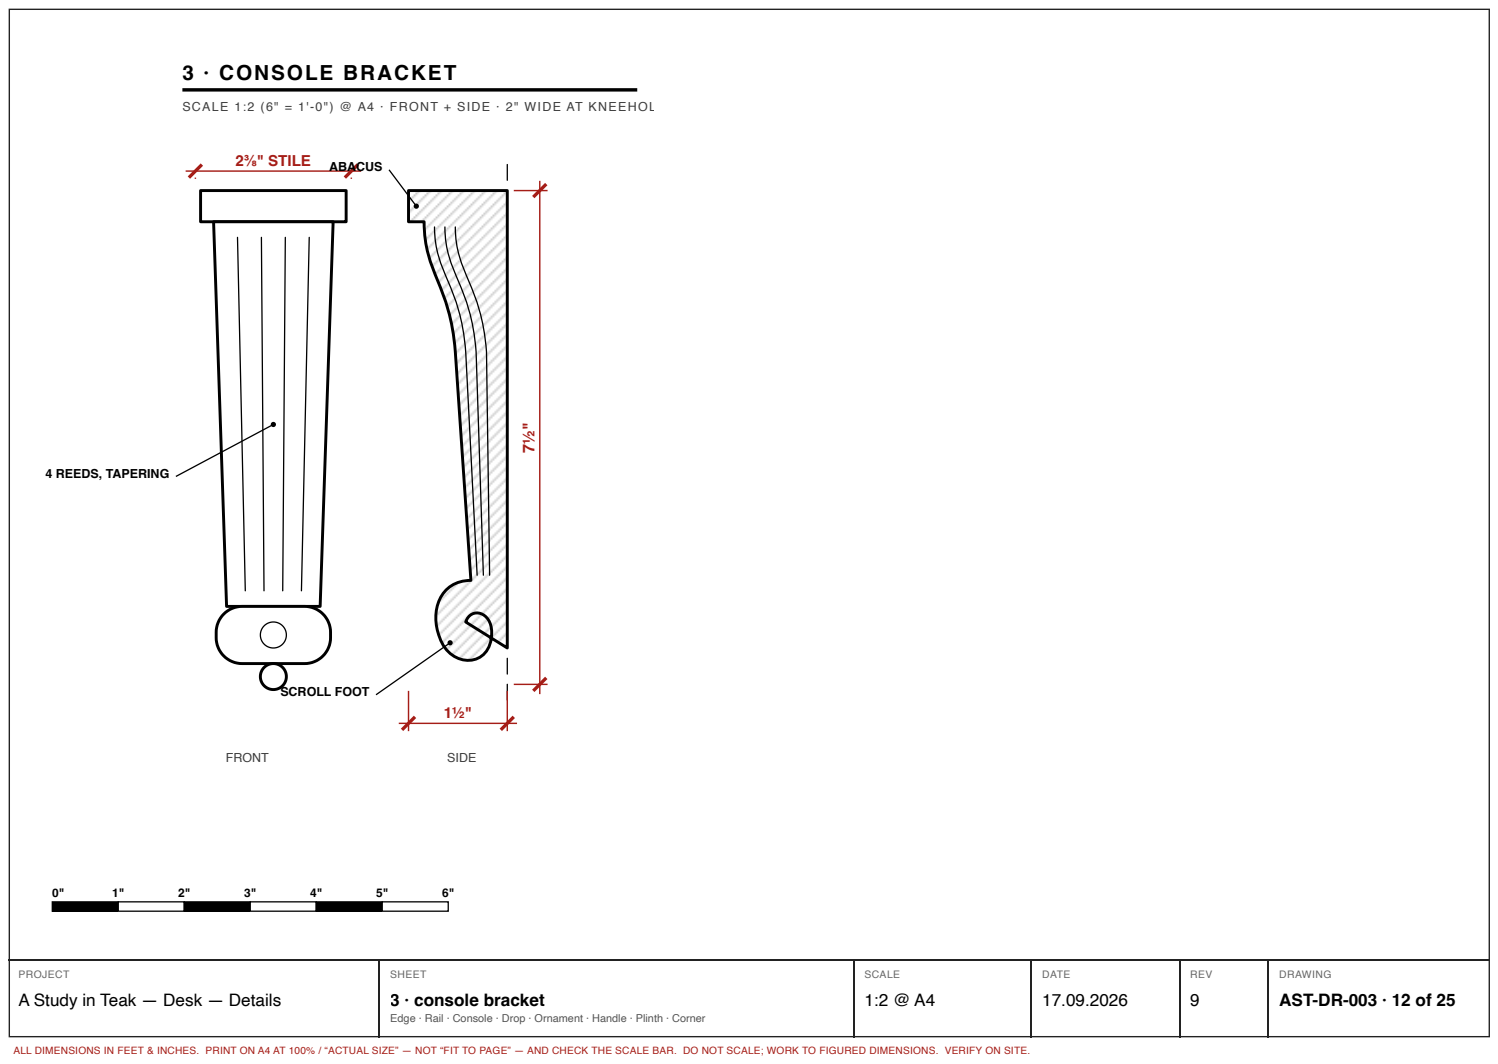
[picture p251: page 12]
2⅜" STILE; FRONT; SIDE; ABACUS; SCROLL FOOT; 4 REEDS, TAPERING; 3 · console bracket

AST-DR-003 · 12 of 25

### 4 · CARVED DROP

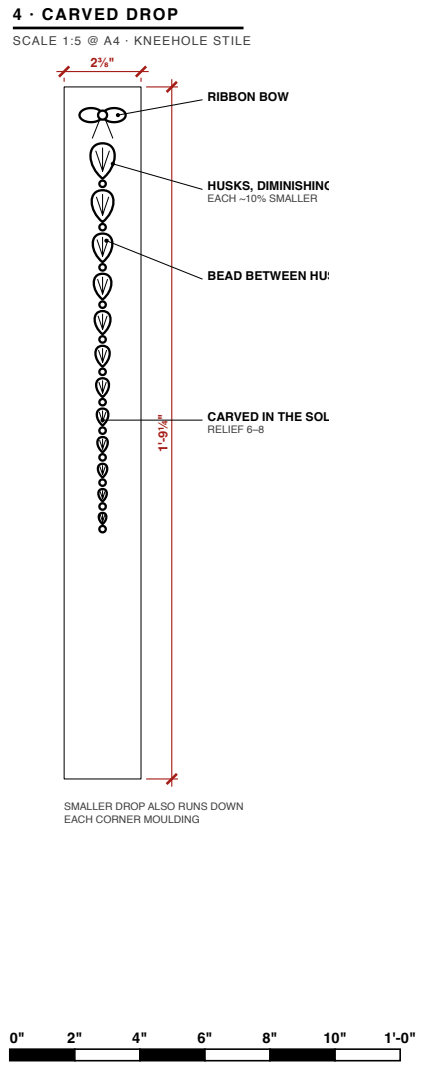
[picture p252: page 13]
RIBBON BOW; HUSKS, DIMINISHING EACH ~10% SMALLER; 4 · carved drop

SCALE 1:5 @ A4 · KNEEHOLE STILE

BEAD BETWEEN HUS

CARVED IN THE SOL
RELIEF 6–8

SMALLER DROP ALSO RUNS DOWN
EACH CORNER MOULDING

AST-DR-003 · 13 of 25

# 5 · PEDESTAL DRAWERS

## SCALE 1:6 (2" = 1'-0") @ A4 · RIGHT PEDESTAL FRONT · THREE EACH SIDE

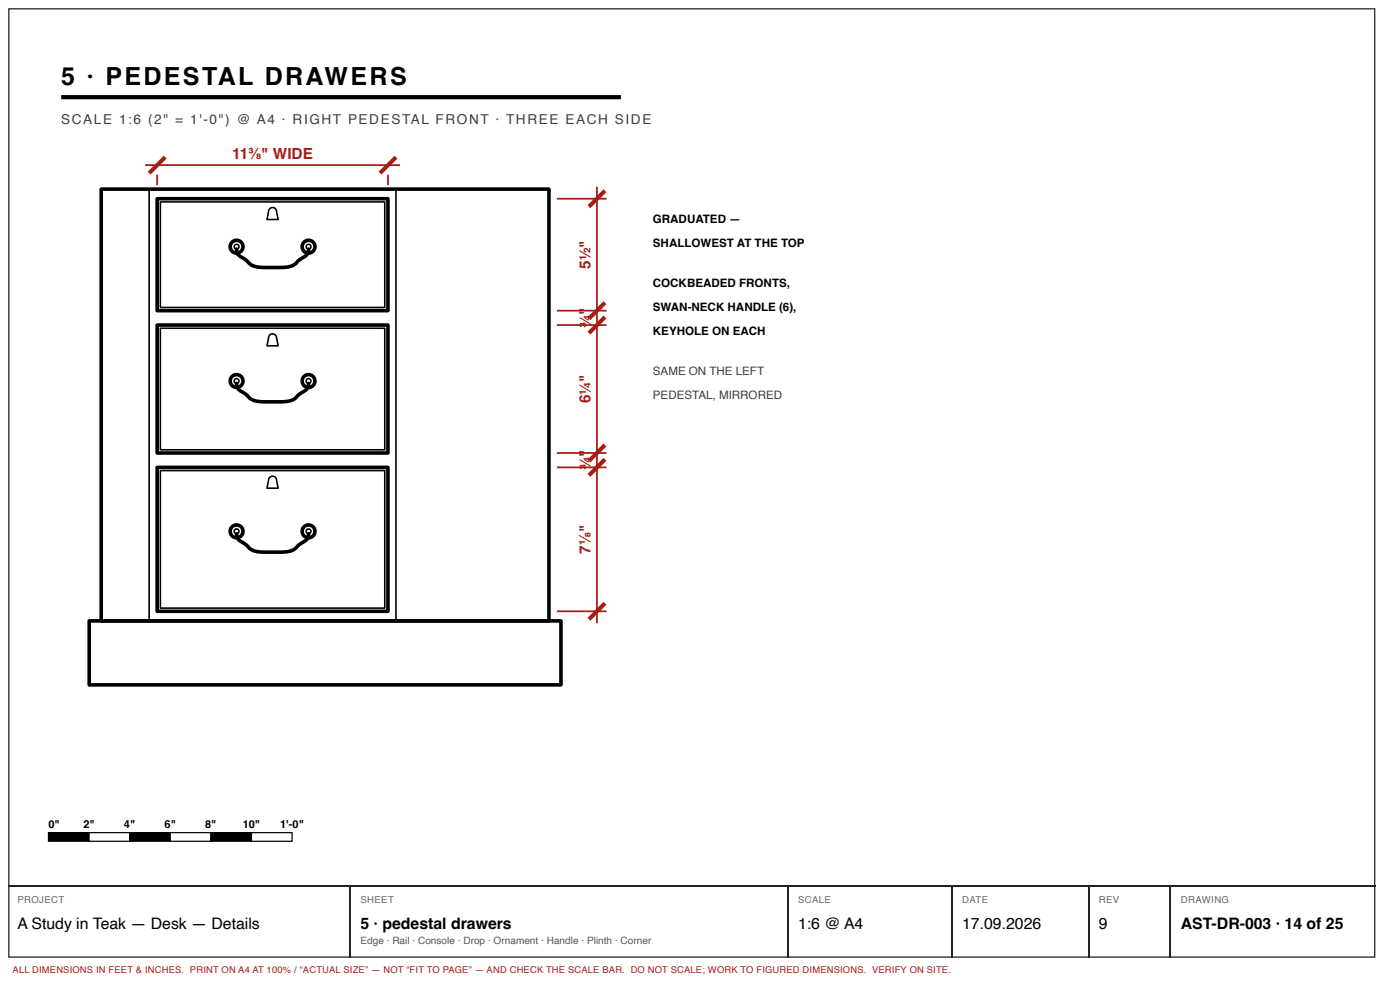
[picture p253: page 14]
11⅜" WIDE; GRADUATED —; COCKBEADED FRONTS,; PEDESTAL, MIRRORED; 5 · pedestal drawers

SHALLOWEST AT THE TOP

SWAN-NECK HANDLE (6),

KEYHOLE ON EACH

SAME ON THE LEFT

AST-DR-003 · 14 of 25

## 2 · DRAWER RAIL

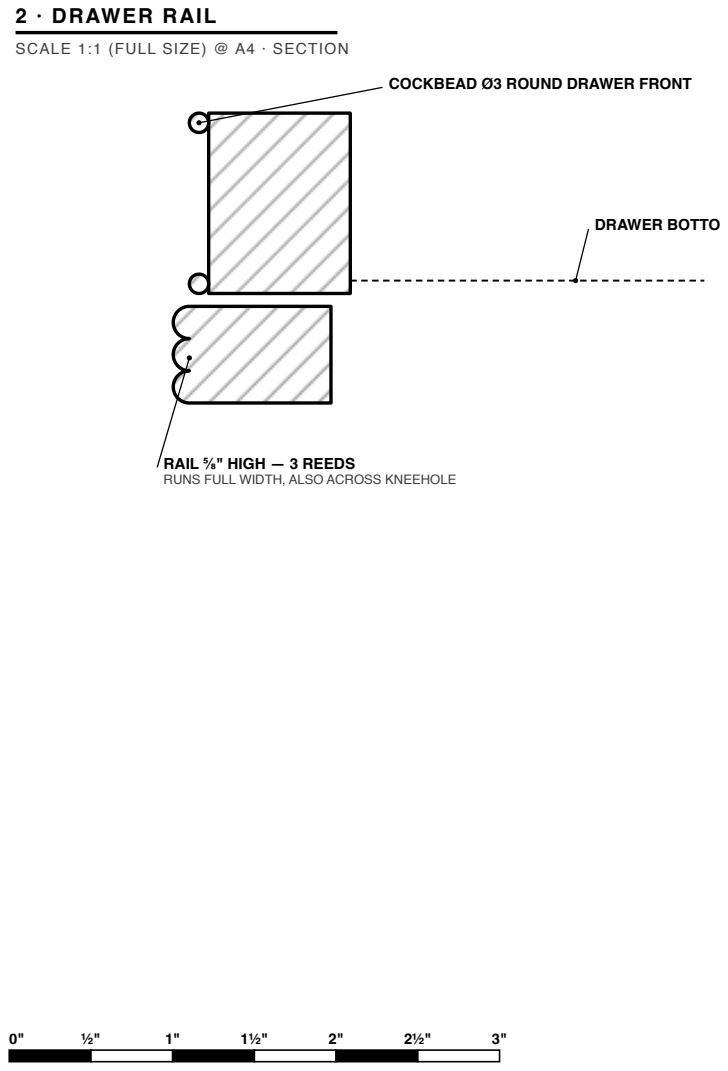
[picture p254: page 15]
DRAWER BOTTO; 2 · drawer rail

SCALE 1:1 (FULL SIZE) @ A4 · SECTION

COCKBEAD Ø3 ROUND DRAWER FRONT

RAIL ⅝" HIGH — 3 REEDS
RUNS FULL WIDTH, ALSO ACROSS KNEEHOLE

AST-DR-003 · 15 of 25

## 6 · DRAWER HANDLE

## 3½" CENTRES

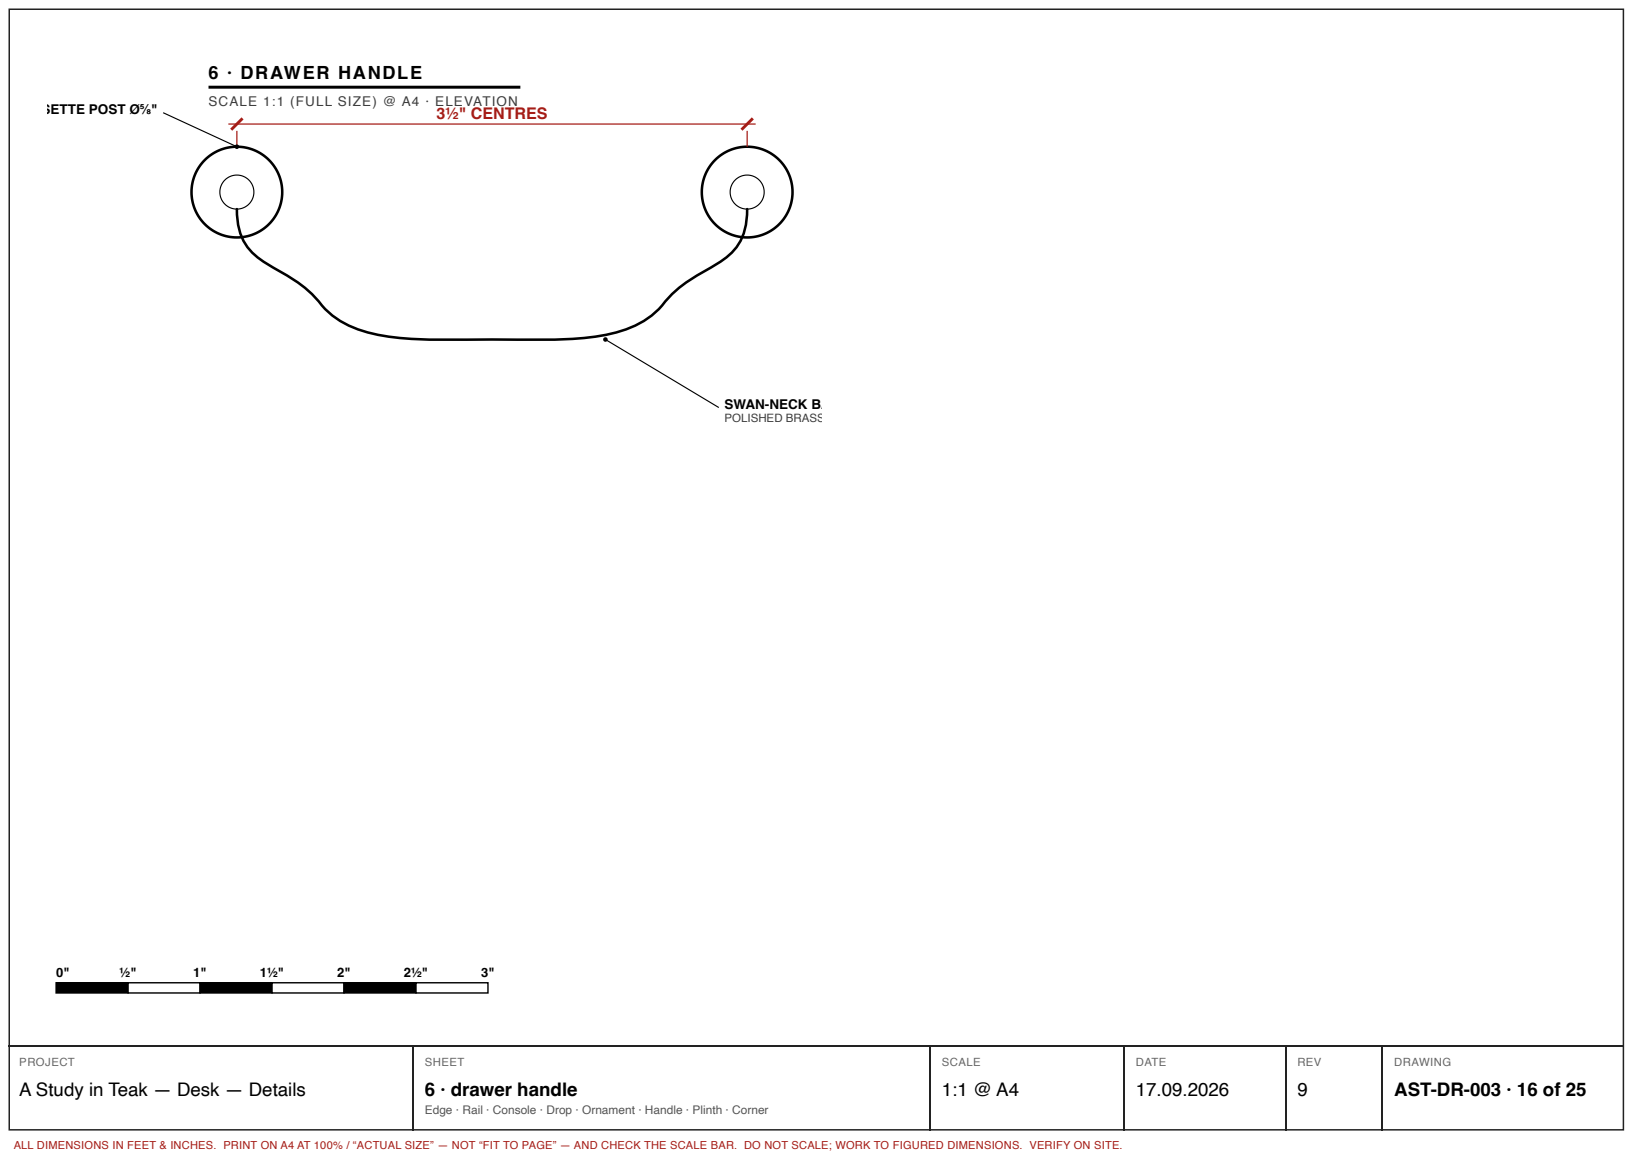
[picture p255: page 16]
6 · drawer handle

SETTE POST Ø⅝"

SCALE 1:1 (FULL SIZE) @ A4 · ELEVATION

SWAN-NECK BA
POLISHED BRASS

AST-DR-003 · 16 of 25

# 7 · PLINTH

# SCALE 1:1 (FULL SIZE) @ A4 · SECTION

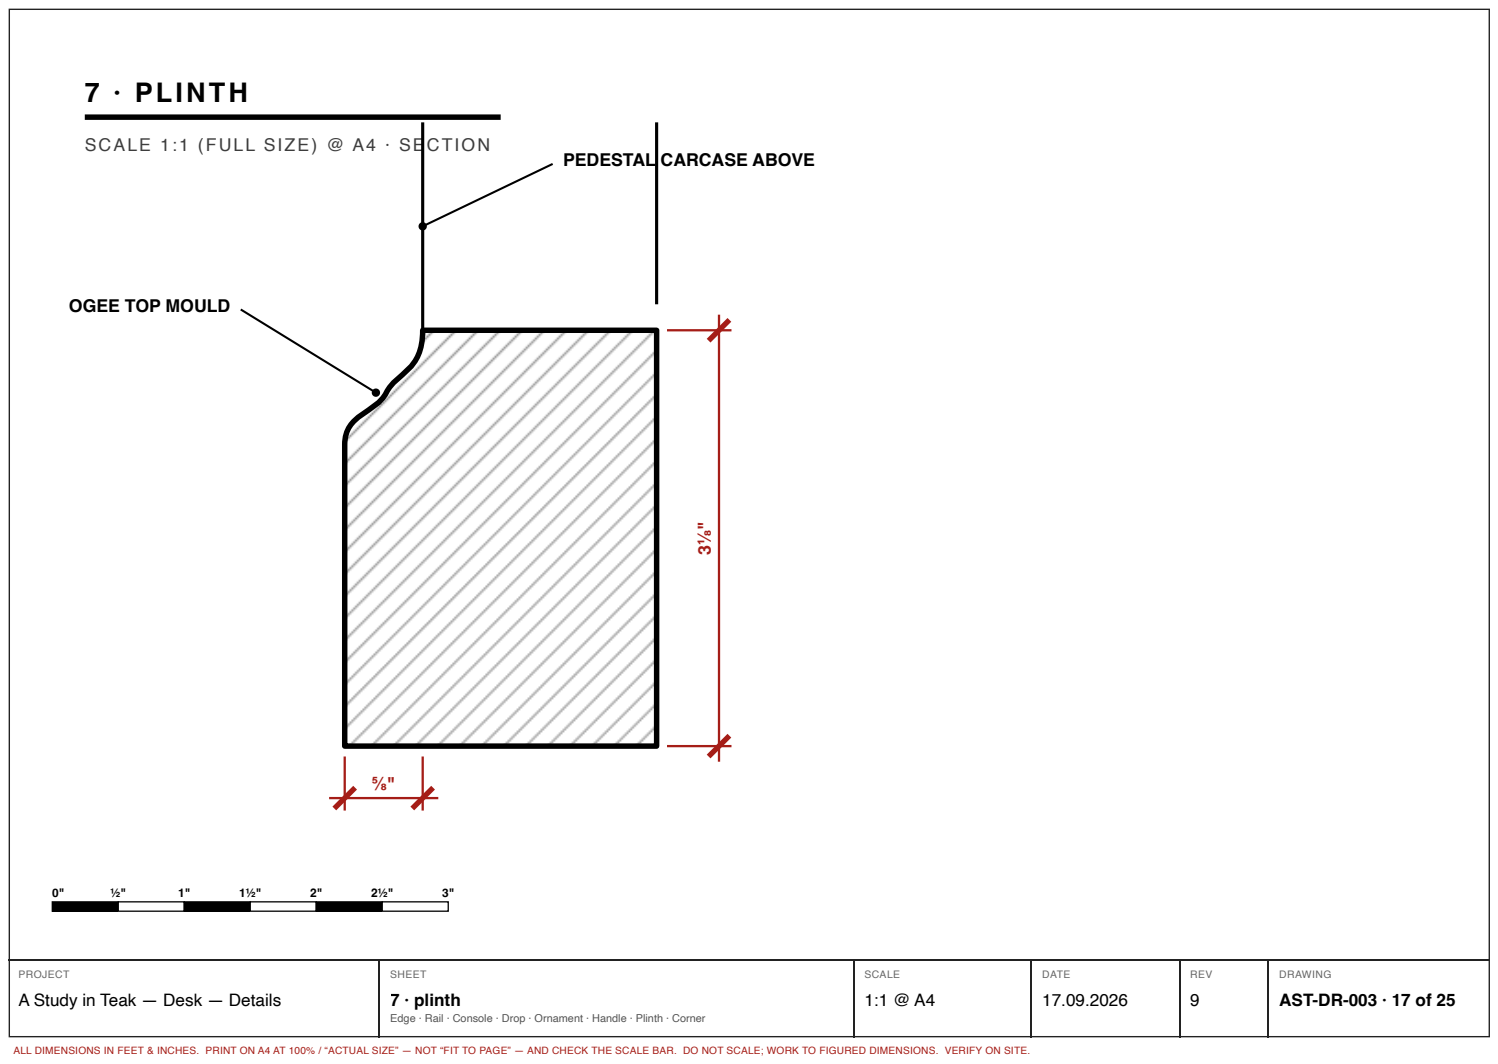
[picture p256: page 17]
7 · plinth

PEDESTAL CARCASE ABOVE

OGEE TOP MOULD

AST-DR-003 · 17 of 25

# NOTES

# DETAILS

Profiles are drawn from film stills and are indicative;

the joiner to prepare a full-size mock-up of 1, 2 and 7.

Carving (4, 5): carver to work from the reference photos;

sample one drop before carving the set.

Hardware (6): standard 3½" swan-neck, solid brass.

Gold/brass on handles and ring pulls only; rest plain teak.

Corners: clean R 5⅞" hollow, moulding at both ends (8, 8B).

Cut a card template of the hollow to confirm.

# Notes

# AST-DR-003 · 18 of 25

# 8B · CORNER ELEVATION

### SCALE 1:8 (1½" = 1'-0") @ A4 · FRONT LEFT CORNER

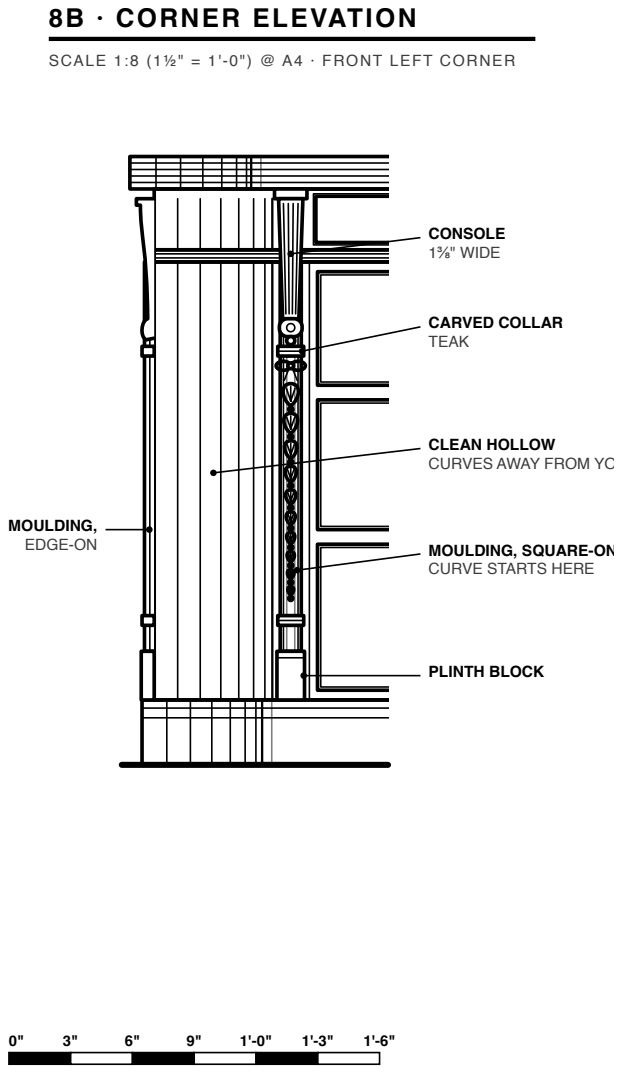
[picture p257: page 19]
MOULDING, EDGE-ON; CONSOLE 1⅜" WIDE; CARVED COLLAR TEAK; PLINTH BLOCK; 8B · corner elevation

CLEAN HOLLOW
CURVES AWAY FROM YO

MOULDING, SQUARE-ON
CURVE STARTS HERE

AST-DR-003 · 19 of 25

# 8 · CORNER — HOLLOW + END MOULDINGS

### SCALE 1:3 (4" = 1'-0") @ A4 · PLAN · ALL FOUR CORNERS · CURVES SHARE ONE CENTRE

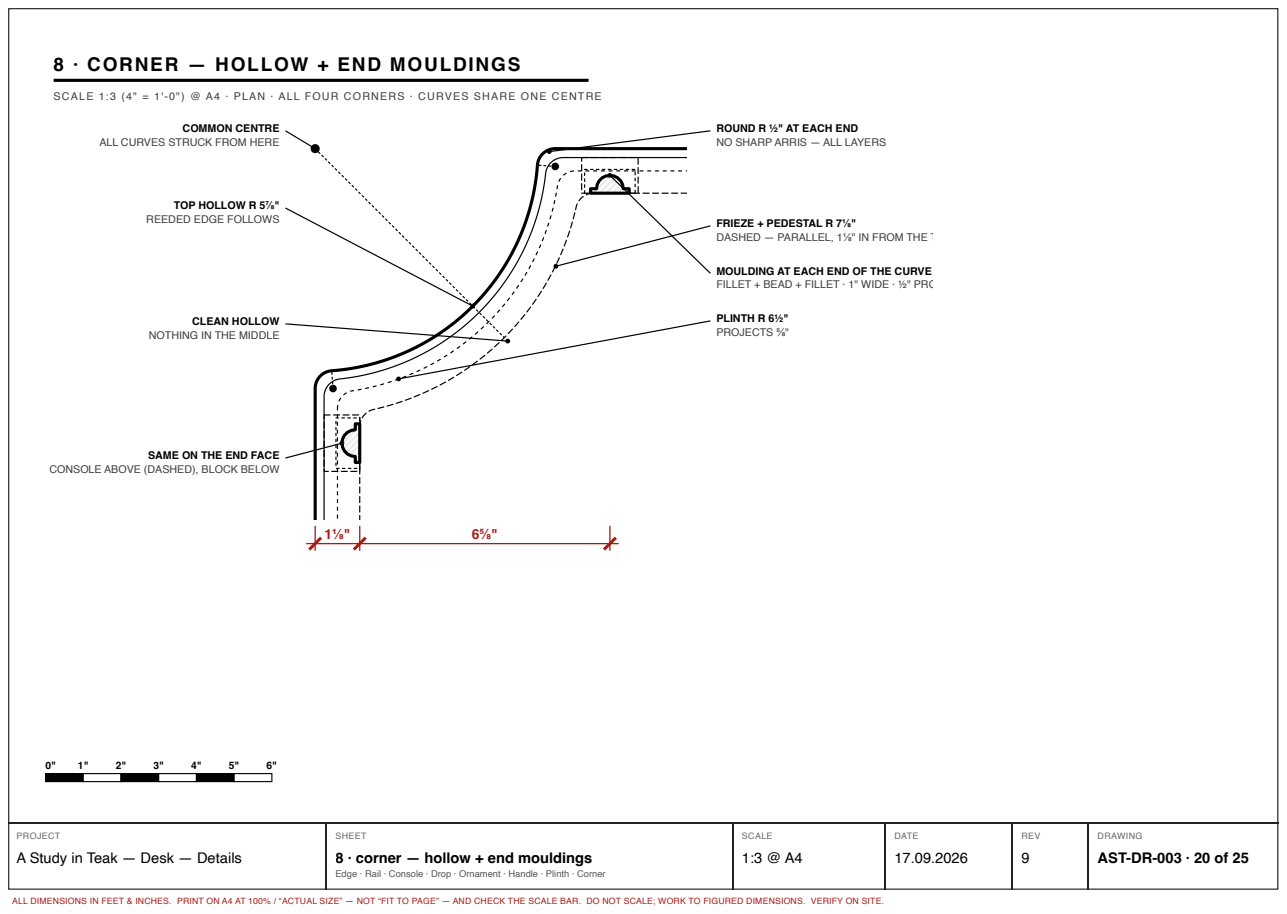
[picture p258: page 20]
COMMON CENTRE; CLEAN HOLLOW; PLINTH R 6½" PROJECTS ⅝"

ROUND R ½" AT EACH END
NO SHARP ARRIS — ALL LAYERS

ALL CURVES STRUCK FROM HERE

TOP HOLLOW R 5⅞"
REEDED EDGE FOLLOWS

FRIEZE + PEDESTAL R 7⅛"
DASHED — PARALLEL, 1⅛" IN FROM THE T

MOULDING AT EACH END OF THE CURVE
FILLET + BEAD + FILLET · 1" WIDE · ½" PRO

NOTHING IN THE MIDDLE

SAME ON THE END FACE

CONSOLE ABOVE (DASHED), BLOCK BELOW

8 · corner — hollow + end mouldings

AST-DR-003 · 20 of 25

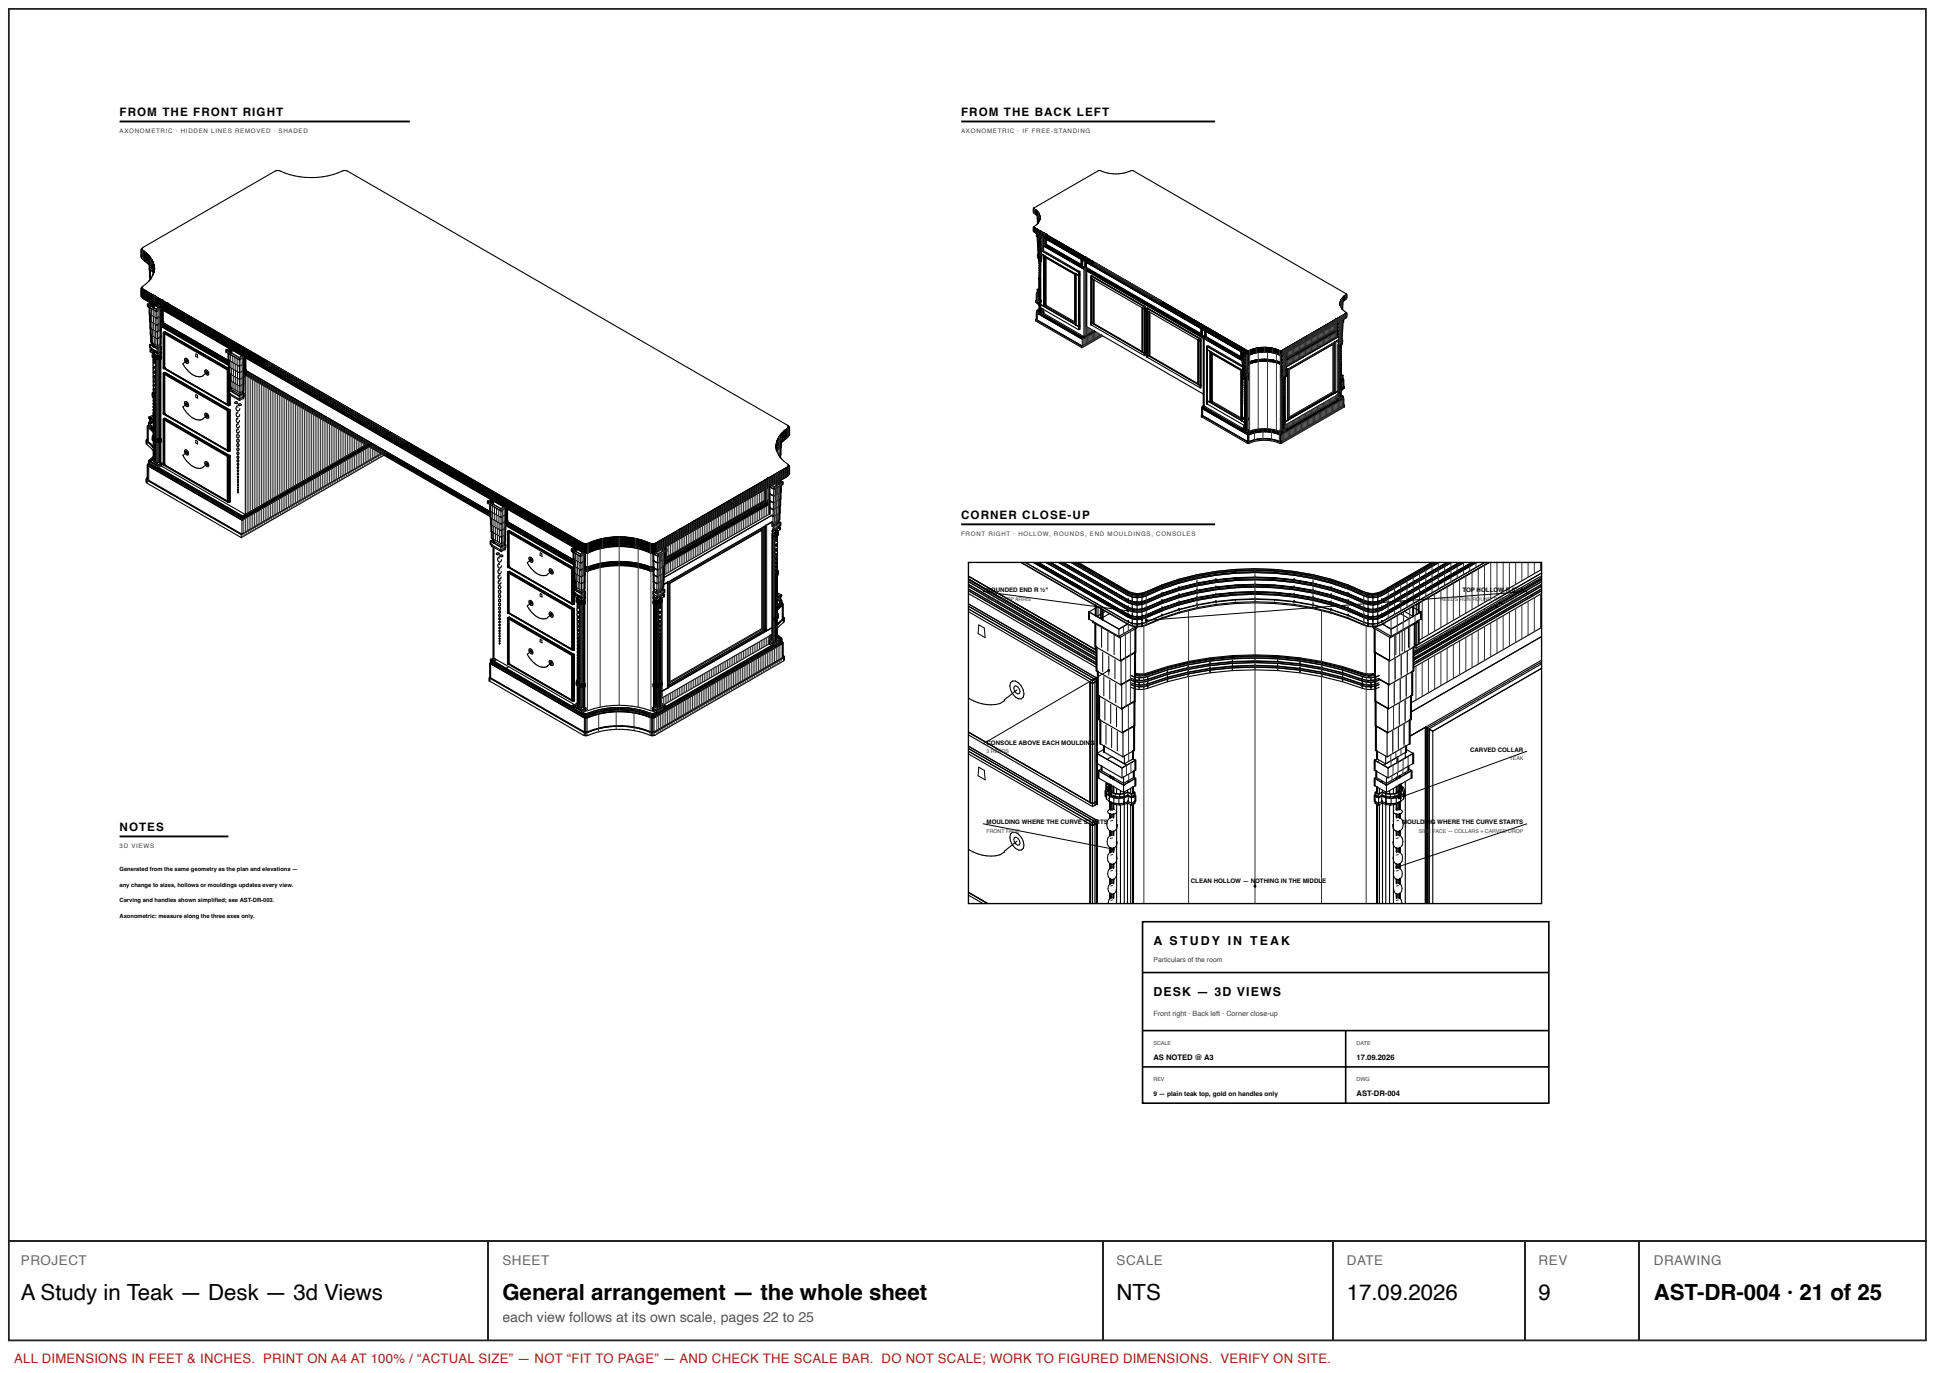
[picture p259: page 21]
TOP HOLLOW R 5⅞"; ROUNDED END R ½"; 3 REEDS; CARVED COLLAR; TEAK; NOTES; 3D VIEWS; DESK — 3D VIEWS; SCALE; AS NOTED @ A3; DATE; REV; DWG; AST-DR-004

FROM THE FRONT RIGHT

FROM THE BACK LEFT

AXONOMETRIC · HIDDEN LINES REMOVED · SHADED

AXONOMETRIC · IF FREE-STANDING

CORNER CLOSE-UP

FRONT RIGHT · HOLLOW, ROUNDS, END MOULDINGS, CONSOLES

NO SHARP ARRIS

REEDS RUN ROUND THE CURVE

CONSOLE ABOVE EACH MOULDING

MOULDING WHERE THE CURVE STARTS
FRONT FACE

SIDE FACE — COLLARS + CARVED DROP

Generated from the same geometry as the plan and elevations —

any change to sizes, hollows or mouldings updates every view.

CLEAN HOLLOW — NOTHING IN THE MIDDLE

Carving and handles shown simplified; see AST-DR-003.

Axonometric: measure along the three axes only.

Particulars of the room

Front right · Back left · Corner close-up

9 — plain teak top, gold on handles only

A Study in Teak — Desk — 3d Views

General arrangement — the whole sheet

AST-DR-004 · 21 of 25

each view follows at its own scale, pages 22 to 25

## FROM THE FRONT RIGHT

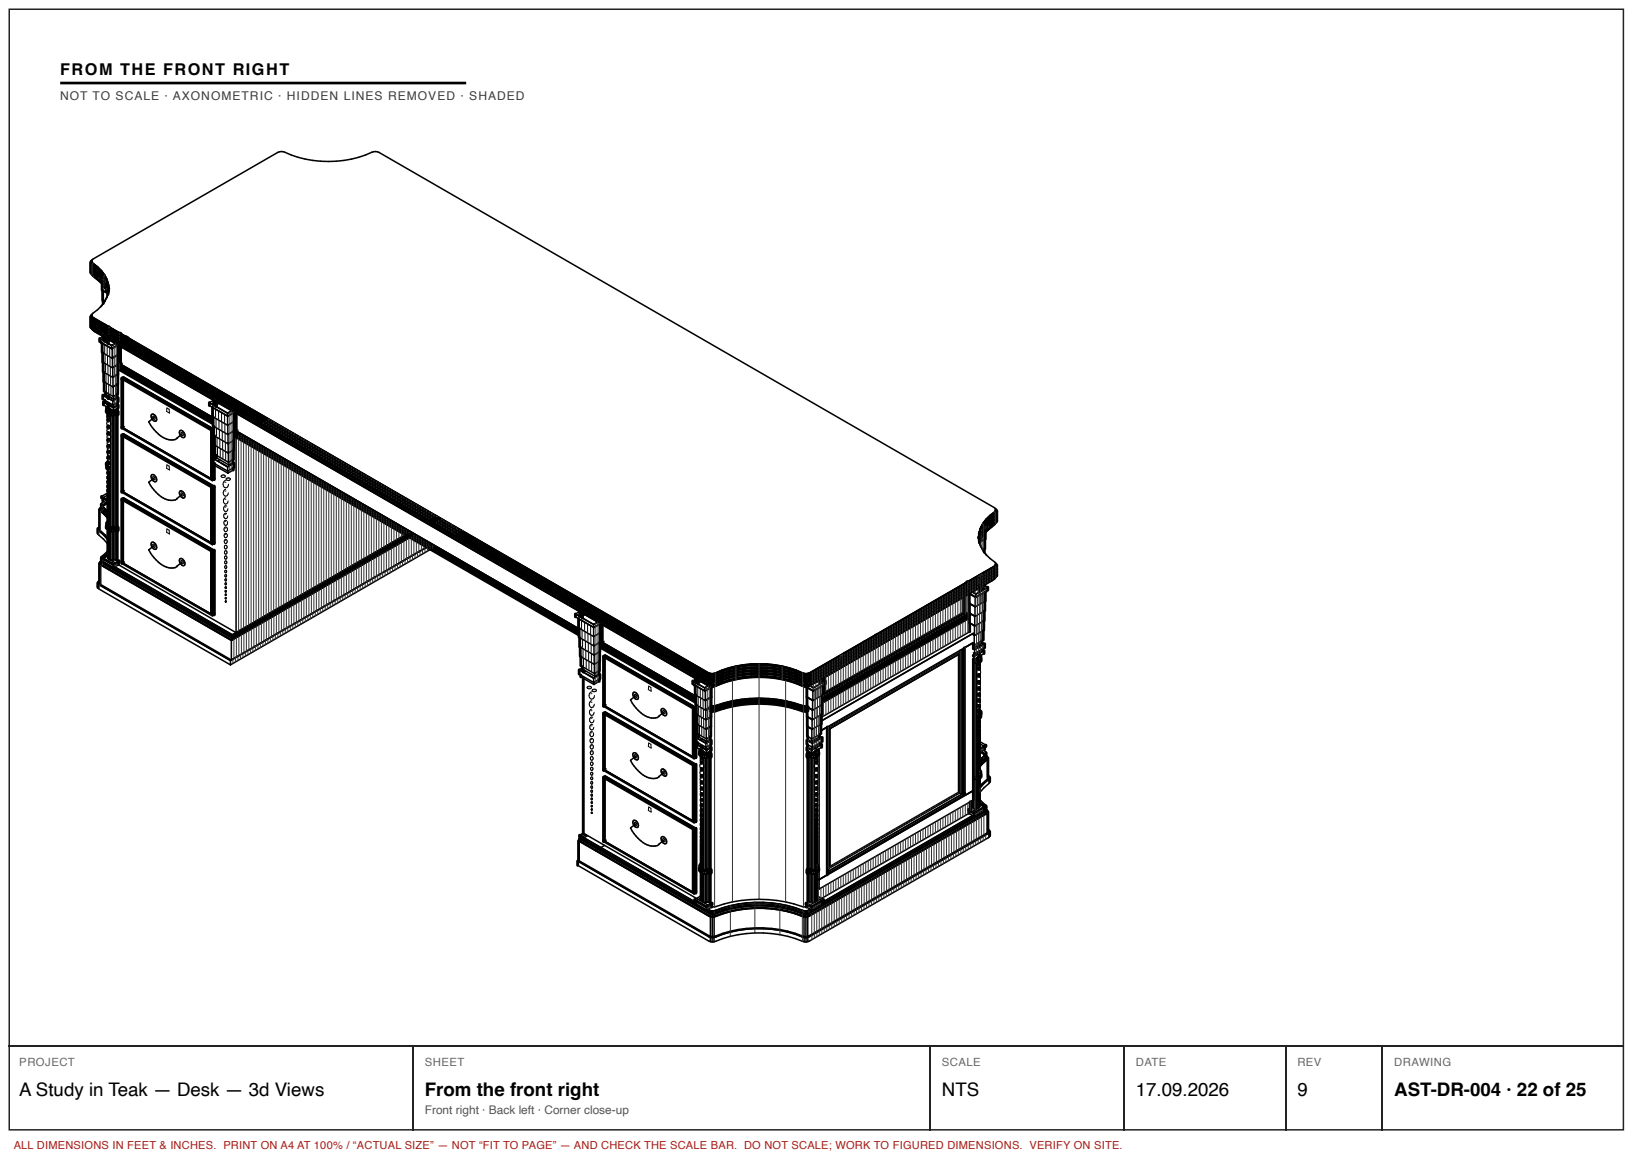
[picture p260: page 22]

NOT TO SCALE · AXONOMETRIC · HIDDEN LINES REMOVED · SHADED

A Study in Teak — Desk — 3d Views

From the front right

AST-DR-004 · 22 of 25

Front right · Back left · Corner close-up

# FROM THE BACK LEFT

## NOT TO SCALE · AXONOMETRIC · IF FREE-STANDING

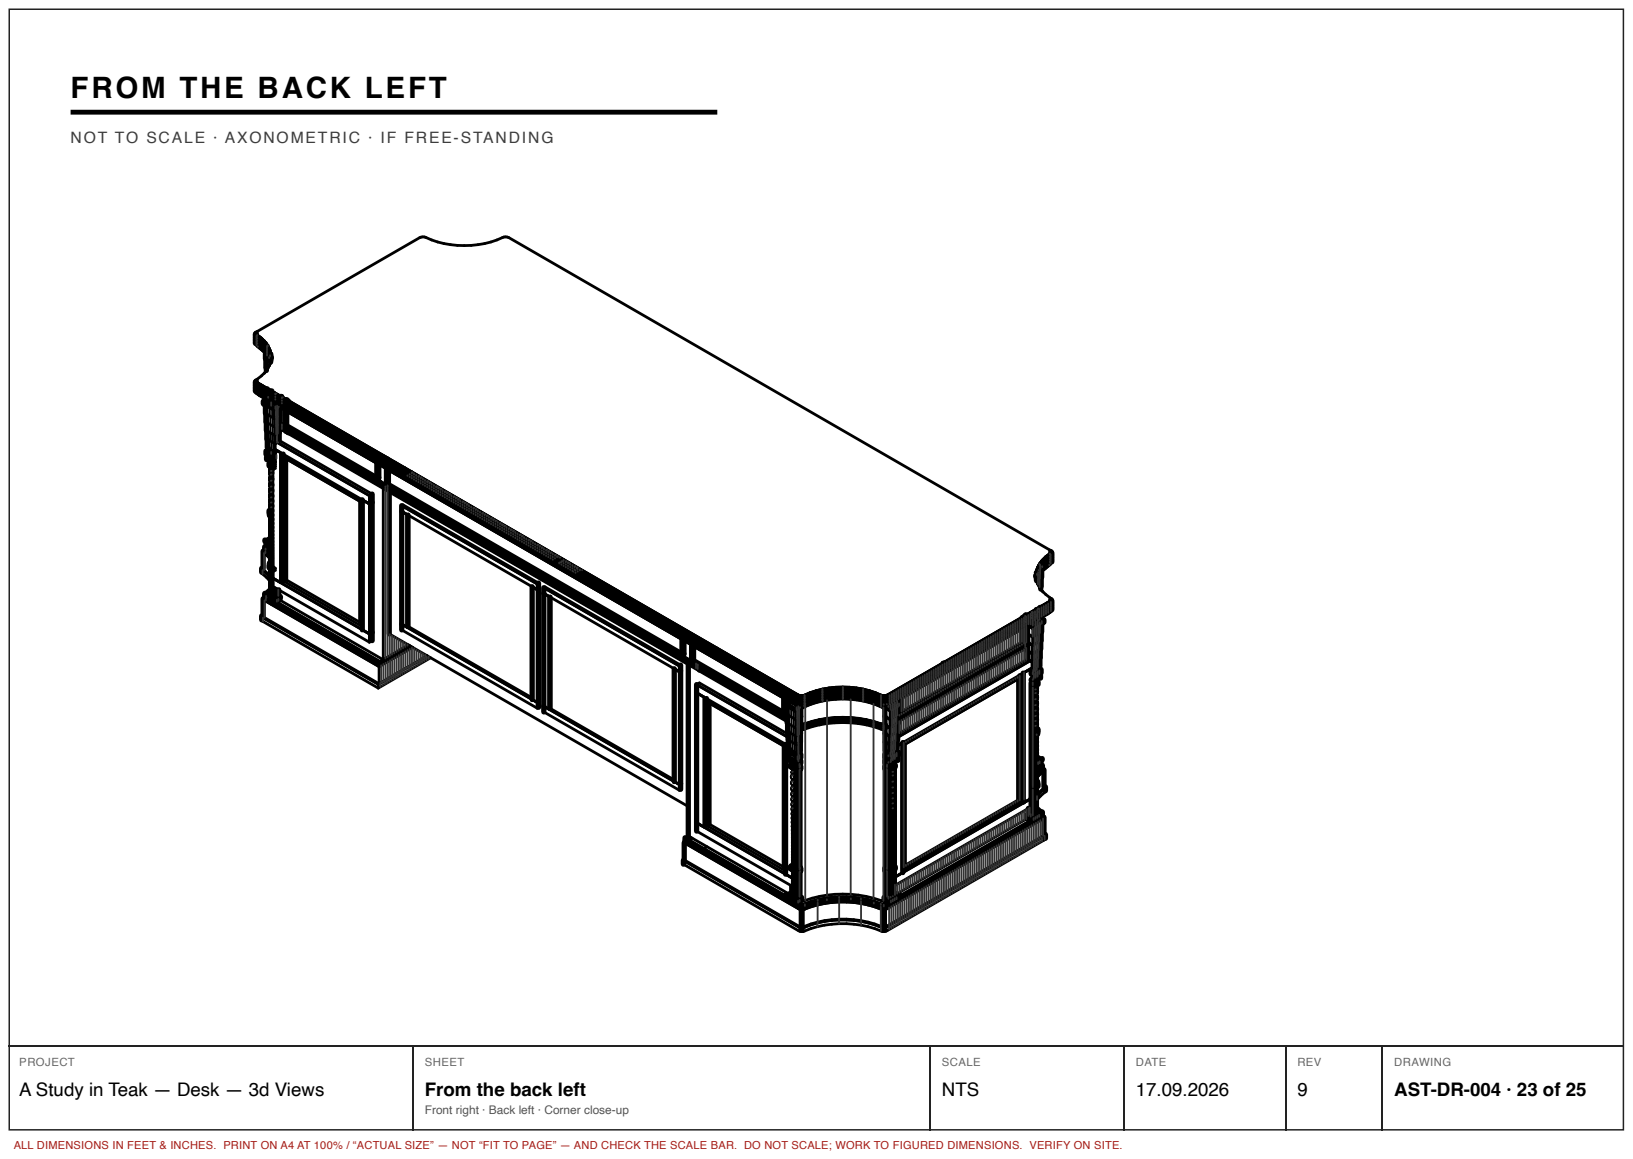
[picture p261: page 23]

A Study in Teak — Desk — 3d Views

From the back left

AST-DR-004 · 23 of 25

Front right · Back left · Corner close-up

# CORNER CLOSE-UP

### NOT TO SCALE · FRONT RIGHT · HOLLOW, ROUNDS, END MOULDINGS, CONSOLES

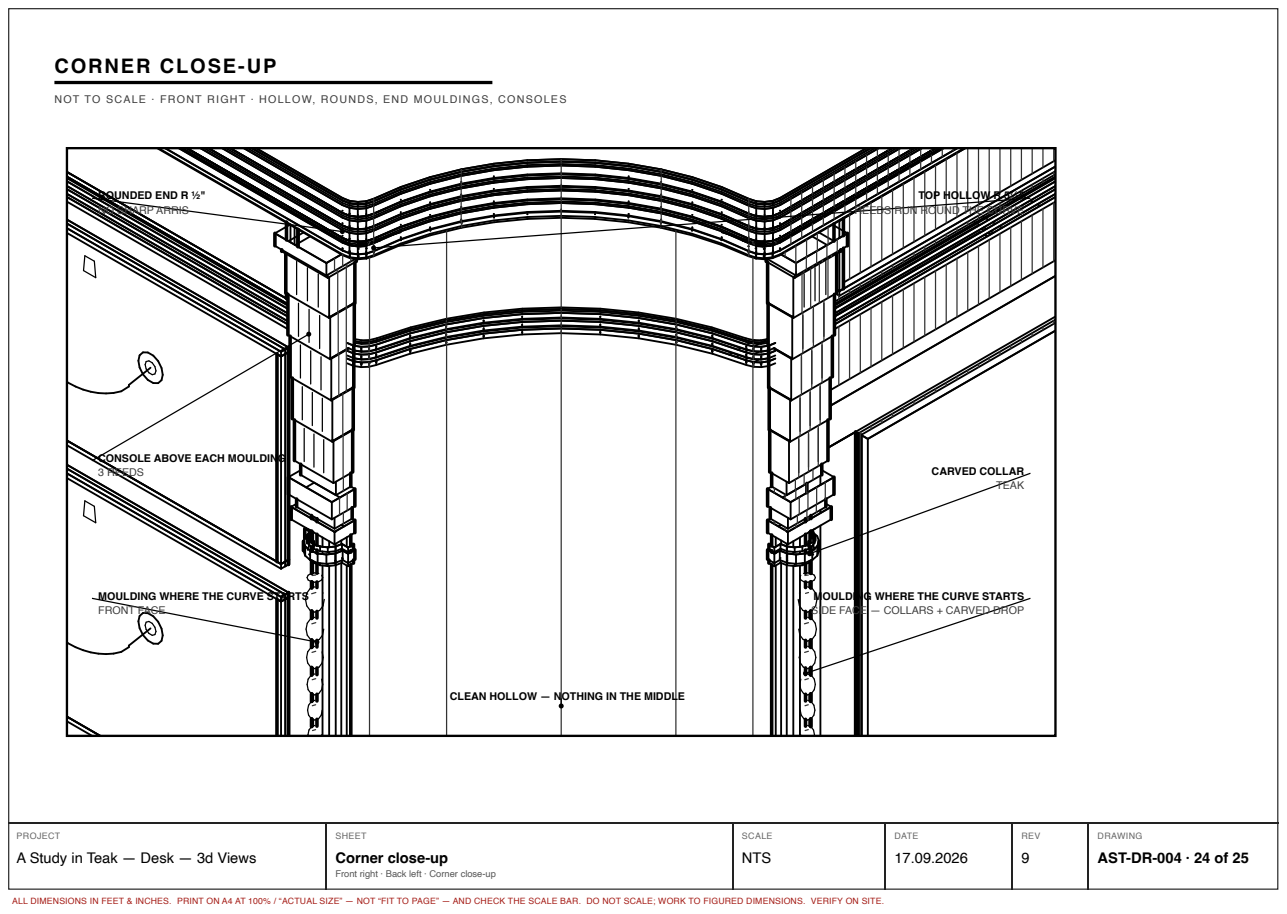
[picture p262: page 24]
TOP HOLLOW R 5⅞"; 3 REEDS; CARVED COLLAR; TEAK

ROUNDED END R ½"
NO SHARP ARRIS

REEDS RUN ROUND THE CURVE

CONSOLE ABOVE EACH MOULDING

MOULDING WHERE THE CURVE STARTS
FRONT FACE

SIDE FACE — COLLARS + CARVED DROP

CLEAN HOLLOW — NOTHING IN THE MIDDLE

A Study in Teak — Desk — 3d Views

Corner close-up

AST-DR-004 · 24 of 25

Front right · Back left · Corner close-up

# N O T E S

# 3D VIEWS

# Generated from the same geometry as the plan and elevations —

any change to sizes, hollows or mouldings updates every view.

Carving and handles shown simplified; see AST-DR-003.

Axonometric: measure along the three axes only.

# A Study in Teak — Desk — 3d Views

# Notes

Front right · Back left · Corner close-up

# AST-DR-004 · 25 of 25
