sakshampan733-cloud/a-study-in-teak/cad/print/desk-square.pdf

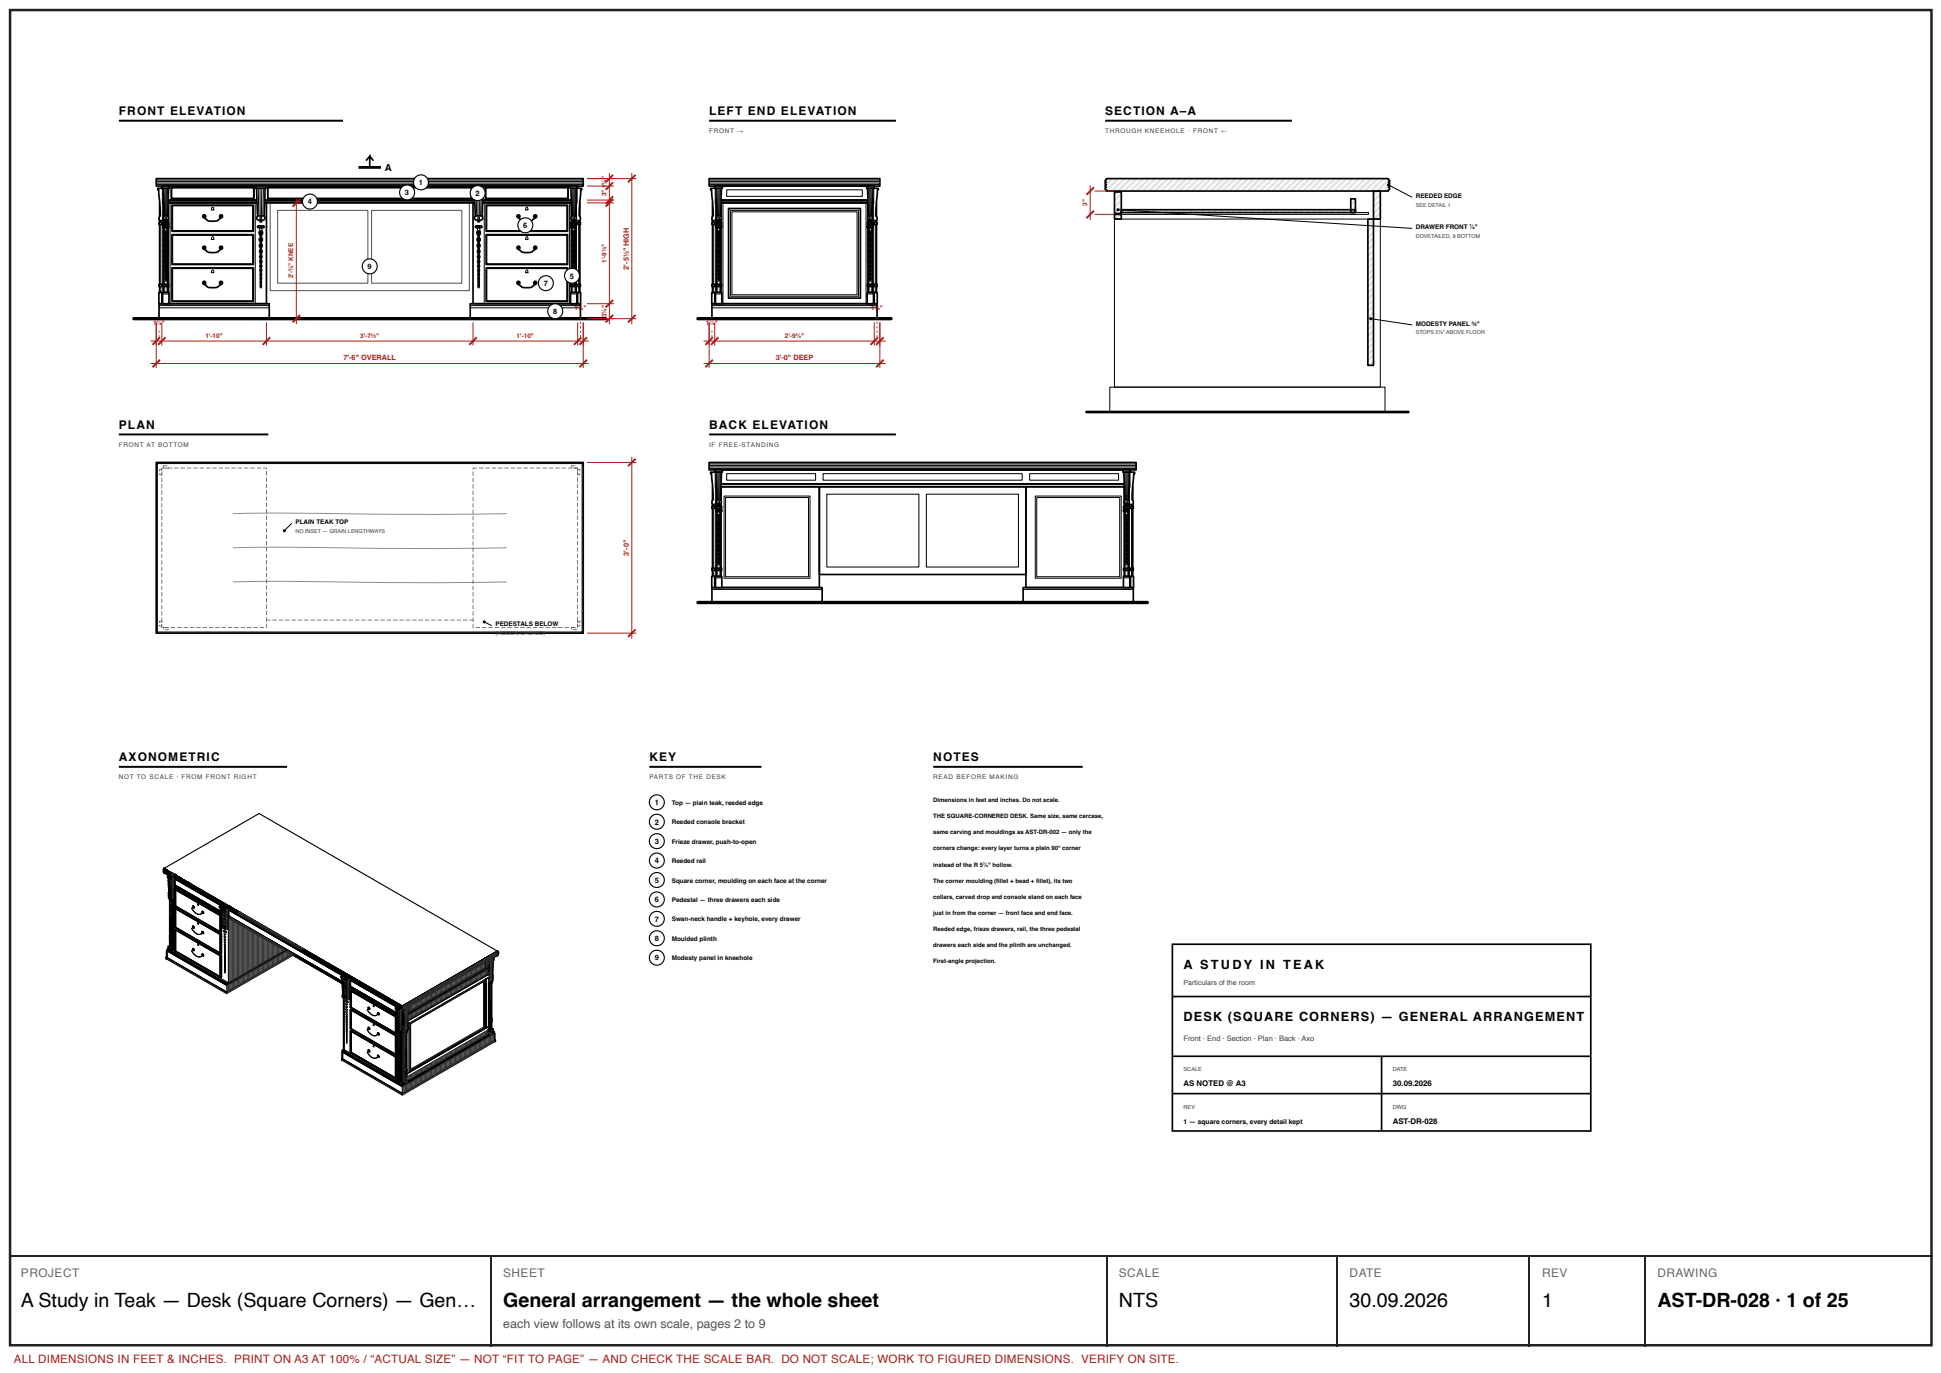
[picture p283: page 1]
FRONT ELEVATION; 7'-6" OVERALL; 2'-5½" HIGH; 2'-⅜" KNEE; FRONT →; 3'-0" DEEP; SECTION A–A; DRAWER FRONT ⅞"; DOVETAILED, 9 BOTTOM; REEDED EDGE; SEE DETAIL 1; PLAN; PEDESTALS BELOW; (HIDDEN, DASHED); BACK ELEVATION; AXONOMETRIC; KEY; 4 Reeded rail; 8 Moulded plinth; NOTES; First-angle projection.; SCALE; AS NOTED @ A3; DATE; REV; DWG; AST-DR-028; SCALE NTS; DATE 30.09.2026

LEFT END ELEVATION

THROUGH KNEEHOLE · FRONT ←

MODESTY PANEL ¾"
STOPS 5⅞" ABOVE FLOOR

FRONT AT BOTTOM

IF FREE-STANDING

PLAIN TEAK TOP
NO INSET — GRAIN LENGTHWAYS

NOT TO SCALE · FROM FRONT RIGHT

PARTS OF THE DESK

READ BEFORE MAKING

1 Top — plain teak, reeded edge

Dimensions in feet and inches. Do not scale.

2 Reeded console bracket

THE SQUARE-CORNERED DESK. Same size, same carcase,

same carving and mouldings as AST-DR-002 — only the

3 Frieze drawer, push-to-open

corners change: every layer turns a plain 90° corner

instead of the R 5⅞" hollow.

5 Square corner, moulding on each face at the corner

The corner moulding (fillet + bead + fillet), its two

6 Pedestal — three drawers each side

collars, carved drop and console stand on each face

7 Swan-neck handle + keyhole, every drawer

just in from the corner — front face and end face.

Reeded edge, frieze drawers, rail, the three pedestal

drawers each side and the plinth are unchanged.

9 Modesty panel in kneehole

Particulars of the room

DESK (SQUARE CORNERS) — GENERAL ARRANGEMENT

Front · End · Section · Plan · Back · Axo

1 — square corners, every detail kept

PROJECT
A Study in Teak — Desk (Square Corners) — Gen…

SHEET
General arrangement — the whole sheet

DRAWING
AST-DR-028 · 1 of 25

each view follows at its own scale, pages 2 to 9

ALL DIMENSIONS IN FEET & INCHES. PRINT ON A3 AT 100% / “ACTUAL SIZE” — NOT “FIT TO PAGE” — AND CHECK THE SCALE BAR. DO NOT SCALE; WORK TO FIGURED DIMENSIONS. VERIFY ON SITE.

# FRONT ELEVATION

A

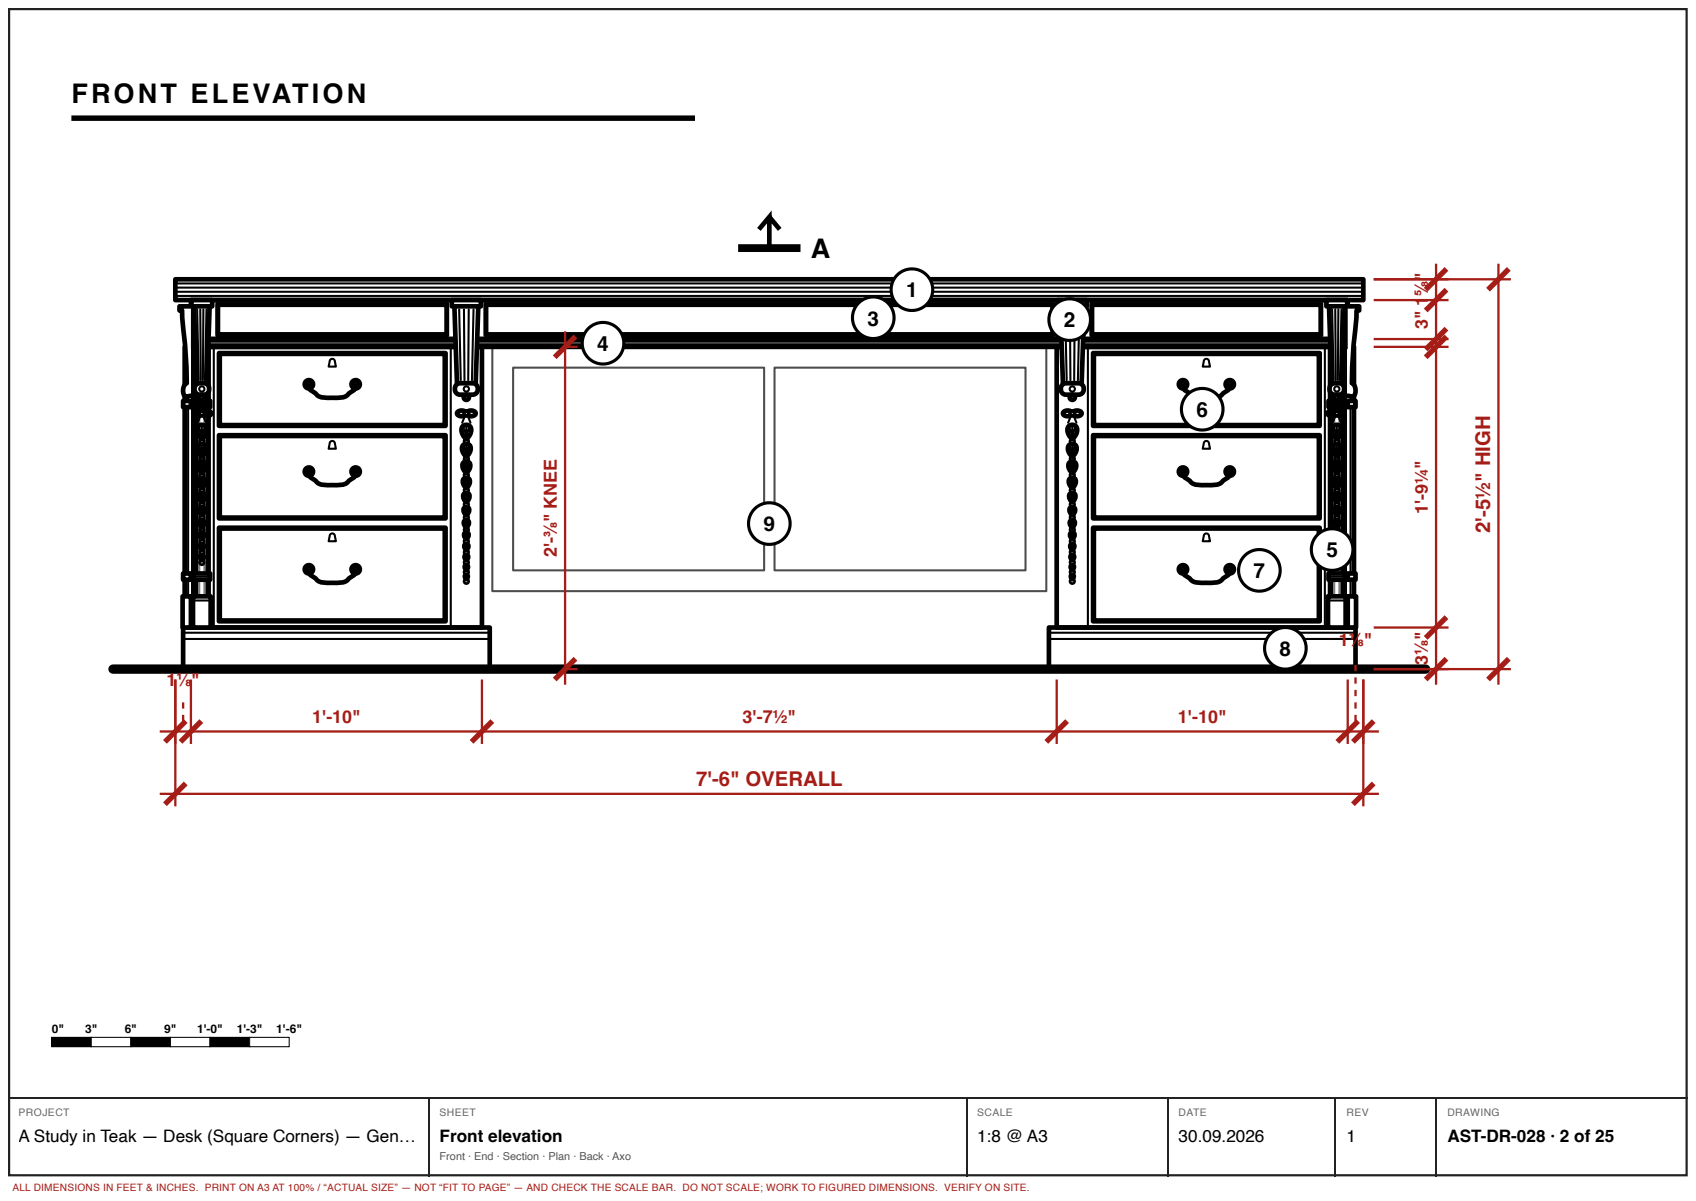
[picture p284: page 2]
7'-6" OVERALL; ½" HIG; Front elevation

A Study in Teak — Desk (Square Corners) — Gen…

AST-DR-028 · 2 of 25

Front · End · Section · Plan · Back · Axo

# LEFT END ELEVATION

# SCALE 1:8 (1½" = 1'-0") @ A3 · FRONT →

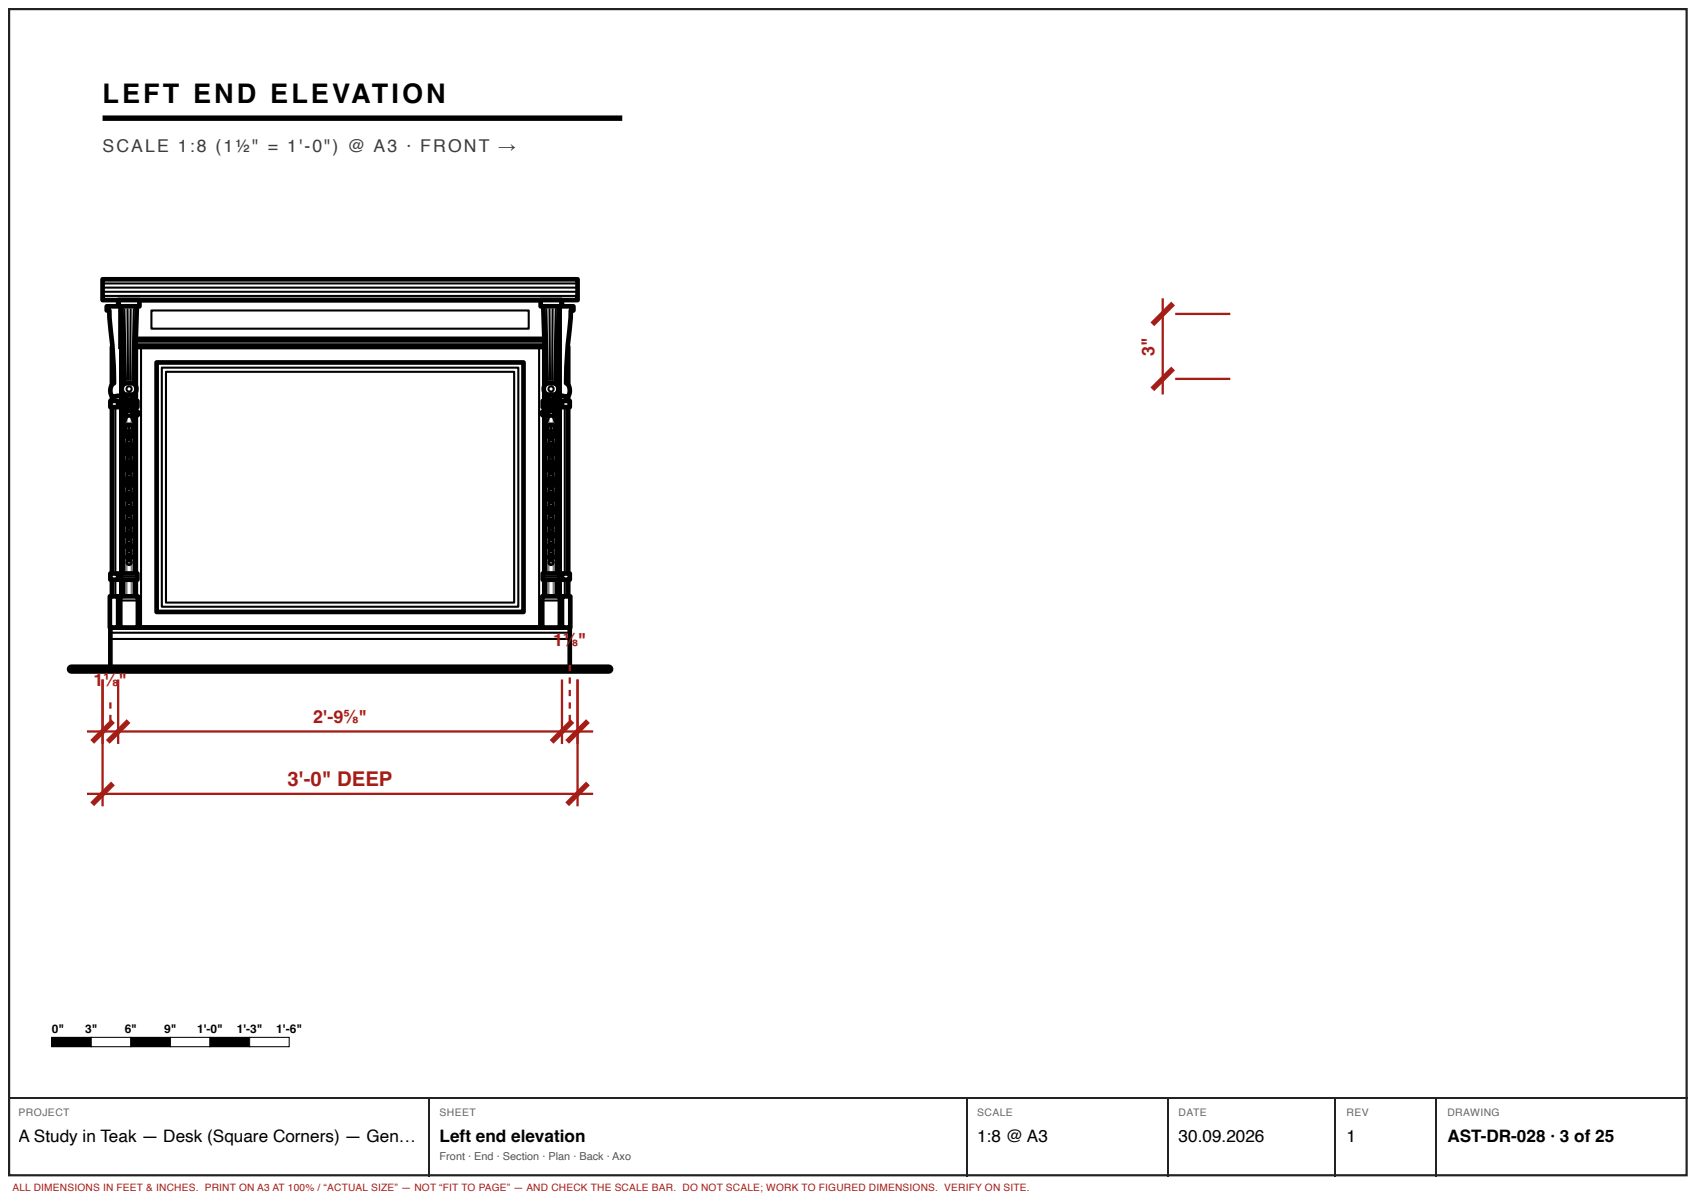
[picture p285: page 3]
3'-0" DEEP

A Study in Teak — Desk (Square Corners) — Gen…

Left end elevation

AST-DR-028 · 3 of 25

Front · End · Section · Plan · Back · Axo

# SECTION A–A

## SCALE 1:5 @ A3 · THROUGH KNEEHOLE · FRONT ←

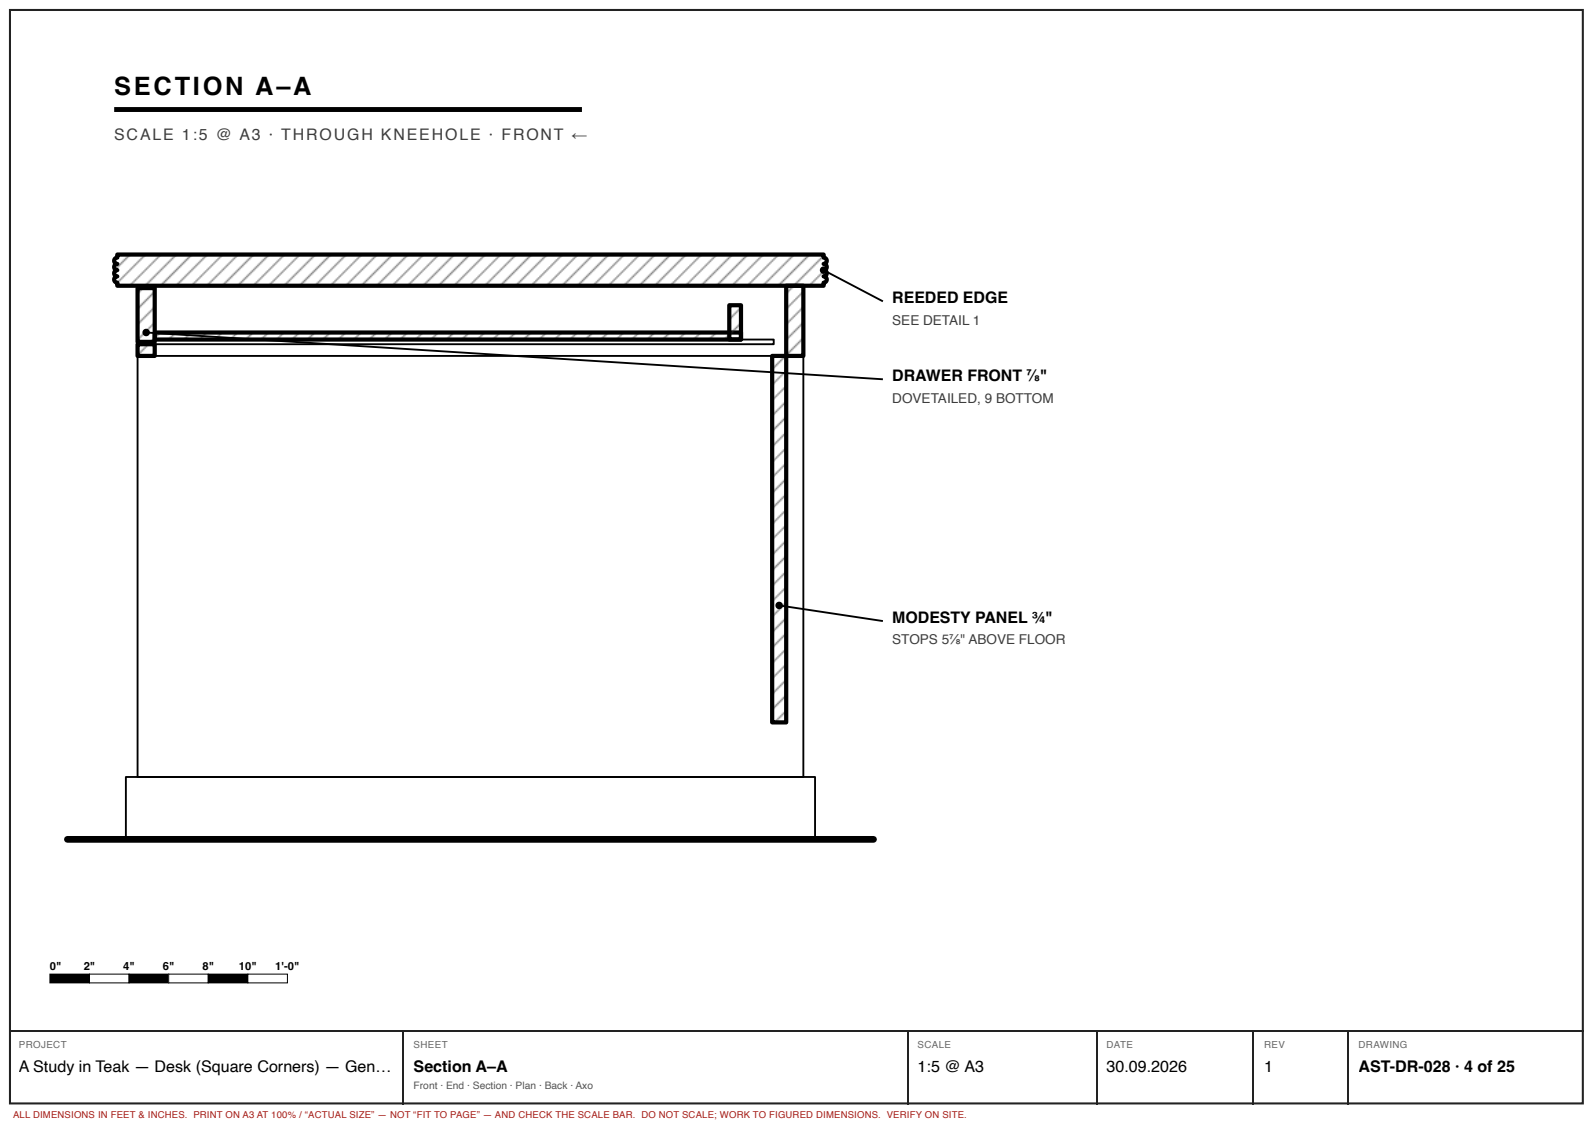
[picture p286: page 4]
DRAWER FRONT ⅞"; DOVETAILED, 9 BOTTOM; REEDED EDGE; SEE DETAIL 1; Section A–A

MODESTY PANEL ¾"
STOPS 5⅞" ABOVE FLOOR

A Study in Teak — Desk (Square Corners) — Gen…

AST-DR-028 · 4 of 25

Front · End · Section · Plan · Back · Axo

# PLAN

# SCALE 1:8 (1½" = 1'-0") @ A3 · FRONT AT BOTTOM

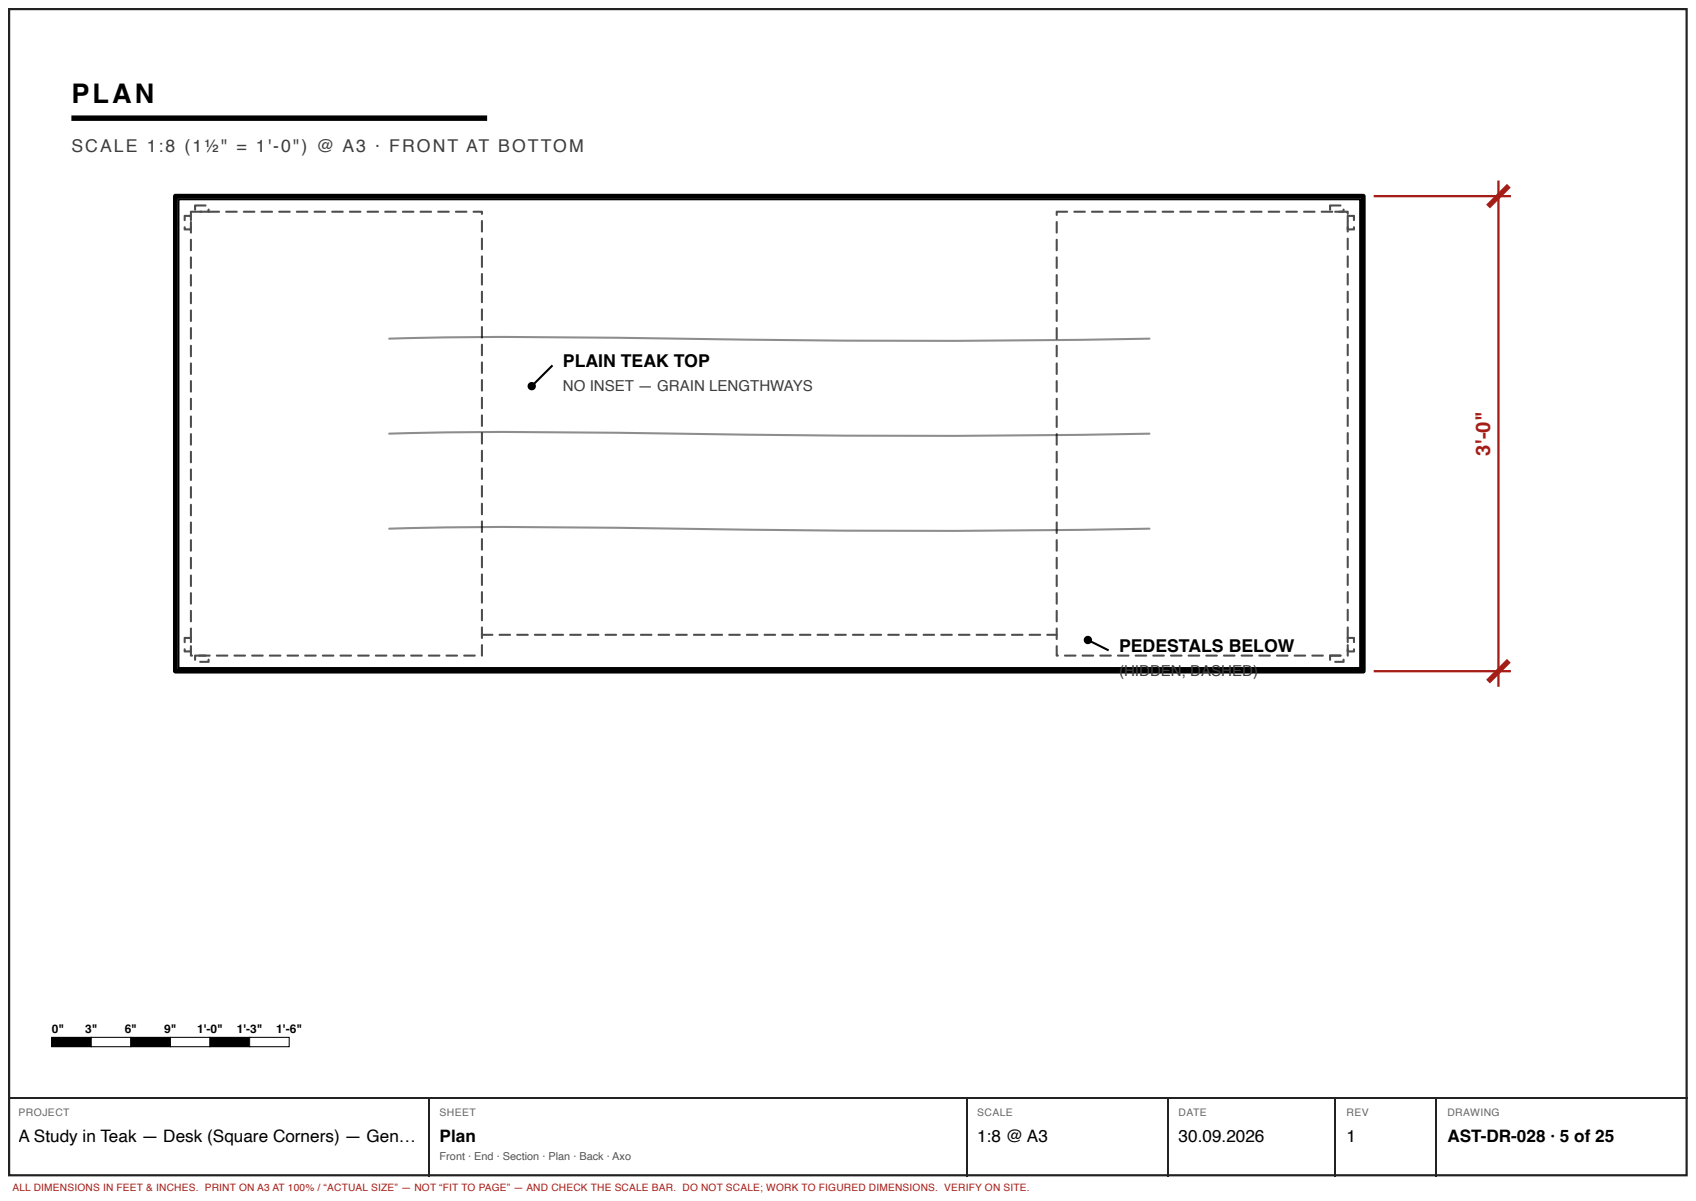
[picture p287: page 5]
PEDESTALS BELOW; (HIDDEN, DASHED); Plan

PLAIN TEAK TOP
NO INSET — GRAIN LENGTHWAYS

A Study in Teak — Desk (Square Corners) — Gen…

AST-DR-028 · 5 of 25

Front · End · Section · Plan · Back · Axo

# BACK ELEVATION

# SCALE 1:8 (1½" = 1'-0") @ A3 · IF FREE-STANDING

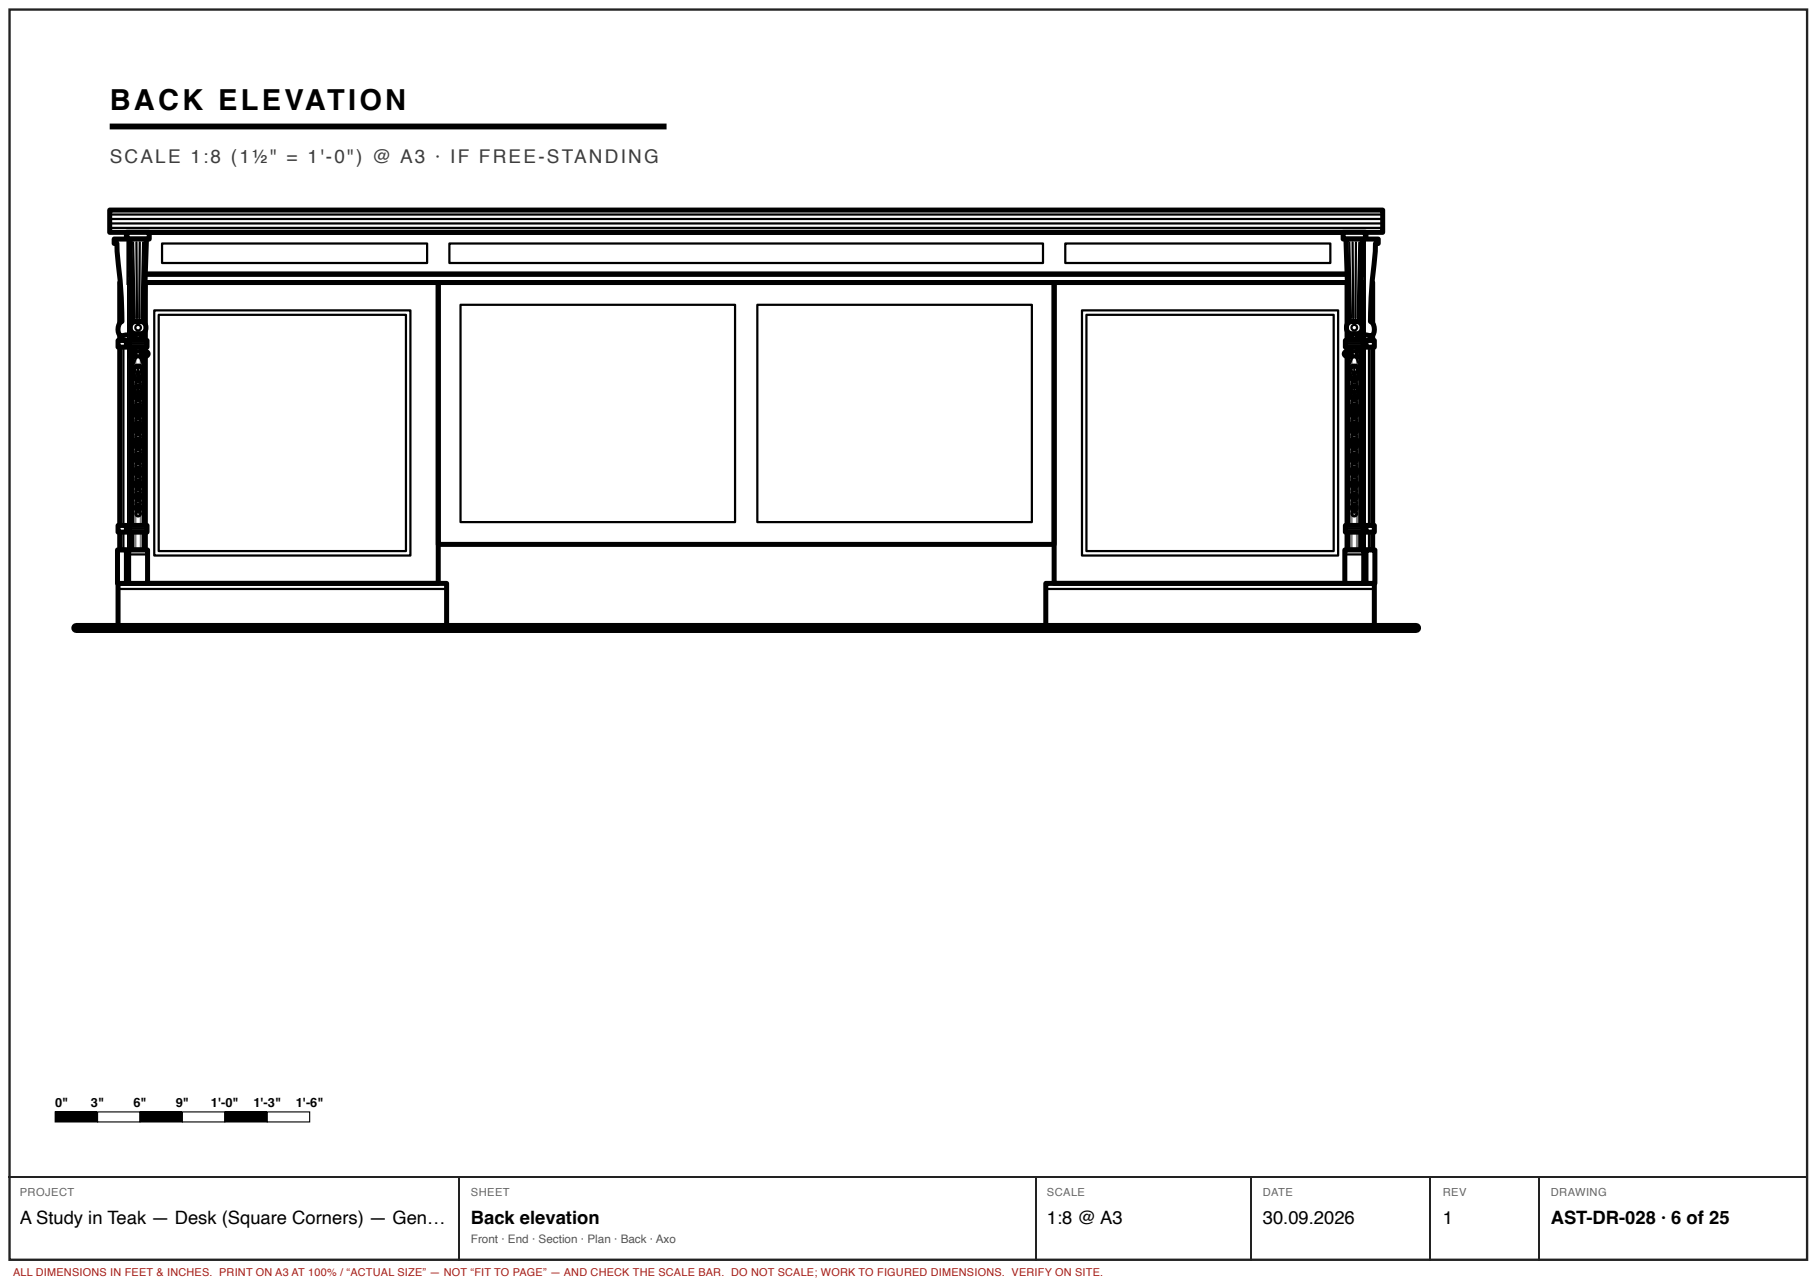
[picture p288: page 6]
Back elevation

A Study in Teak — Desk (Square Corners) — Gen…

AST-DR-028 · 6 of 25

Front · End · Section · Plan · Back · Axo

# AXONOMETRIC

## NOT TO SCALE · NOT TO SCALE · FROM FRONT RIGHT

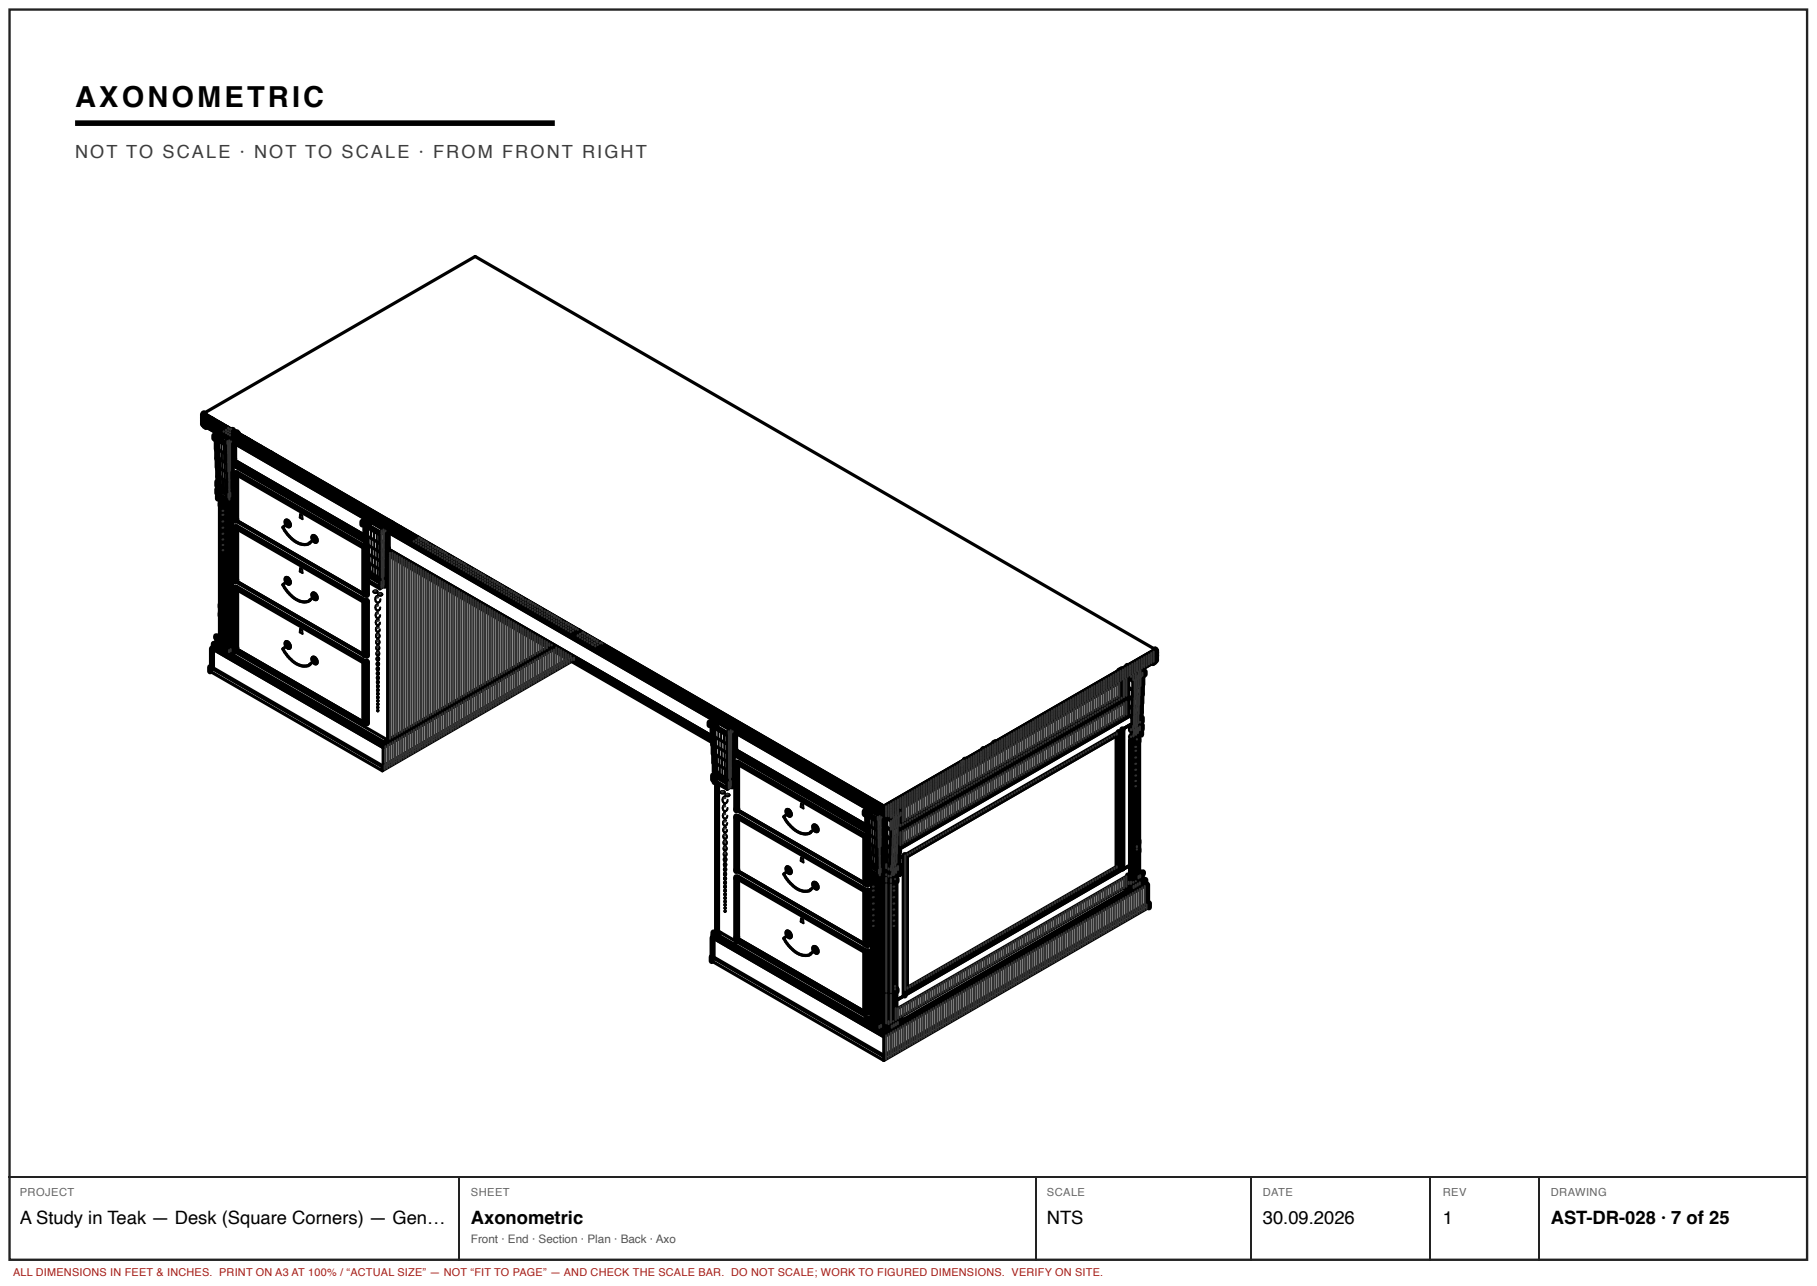
[picture p289: page 7]
Axonometric

A Study in Teak — Desk (Square Corners) — Gen…

AST-DR-028 · 7 of 25

Front · End · Section · Plan · Back · Axo

# KEY

# PARTS OF THE DESK

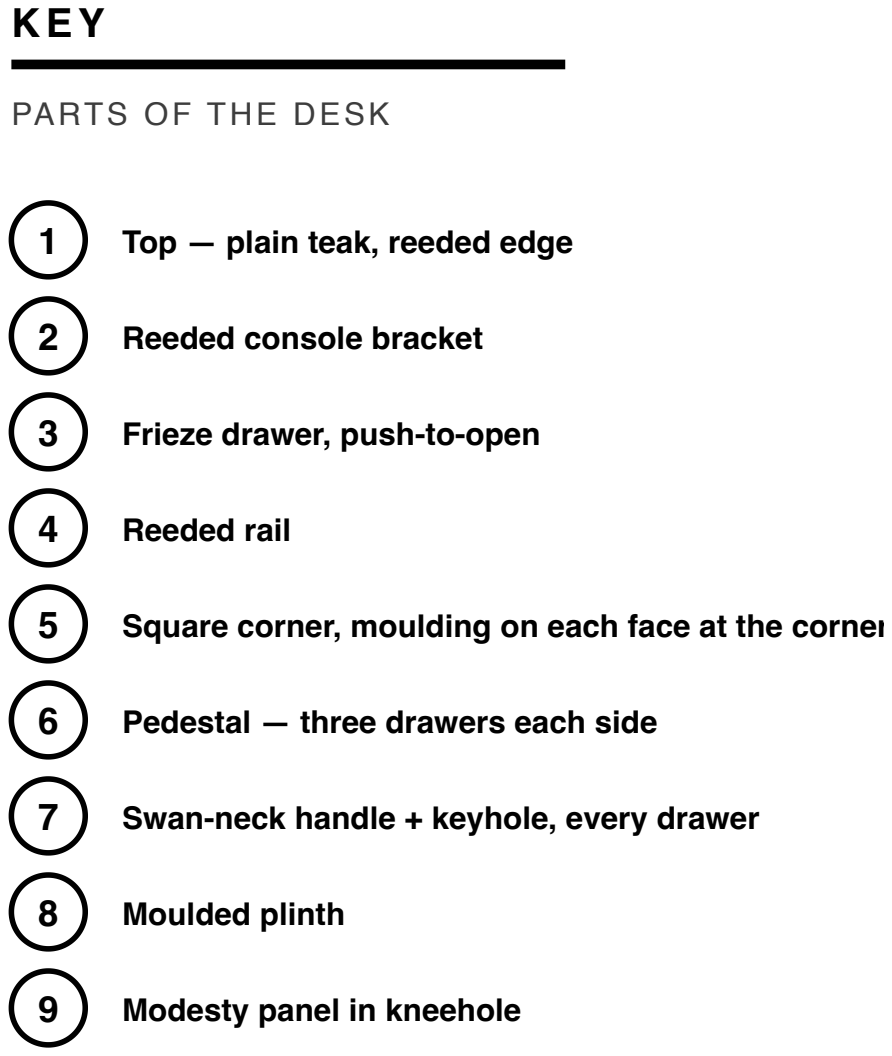
[picture p290: page 8]
4 Reeded rail; 8 Moulded plinth; Key

1 Top — plain teak, reeded edge

2 Reeded console bracket

3 Frieze drawer, push-to-open

5 Square corner, moulding on each face at the corner

6 Pedestal — three drawers each side

7 Swan-neck handle + keyhole, every drawer

9 Modesty panel in kneehole

A Study in Teak — Desk (Square Corners) — Gen…

AST-DR-028 · 8 of 25

Front · End · Section · Plan · Back · Axo

# NOTES

# READ BEFORE MAKING

Dimensions in feet and inches. Do not scale.

THE SQUARE-CORNERED DESK. Same size, same carcase,

# same carving and mouldings as AST-DR-002 — only the

# corners change: every layer turns a plain 90° corner

instead of the R 5⅞" hollow.

# The corner moulding (fillet + bead + fillet), its two

# collars, carved drop and console stand on each face

just in from the corner — front face and end face.

# Reeded edge, frieze drawers, rail, the three pedestal

drawers each side and the plinth are unchanged.

First-angle projection.

## A Study in Teak — Desk (Square Corners) — Gen…

## Notes

Front · End · Section · Plan · Back · Axo

## AST-DR-028 · 9 of 25

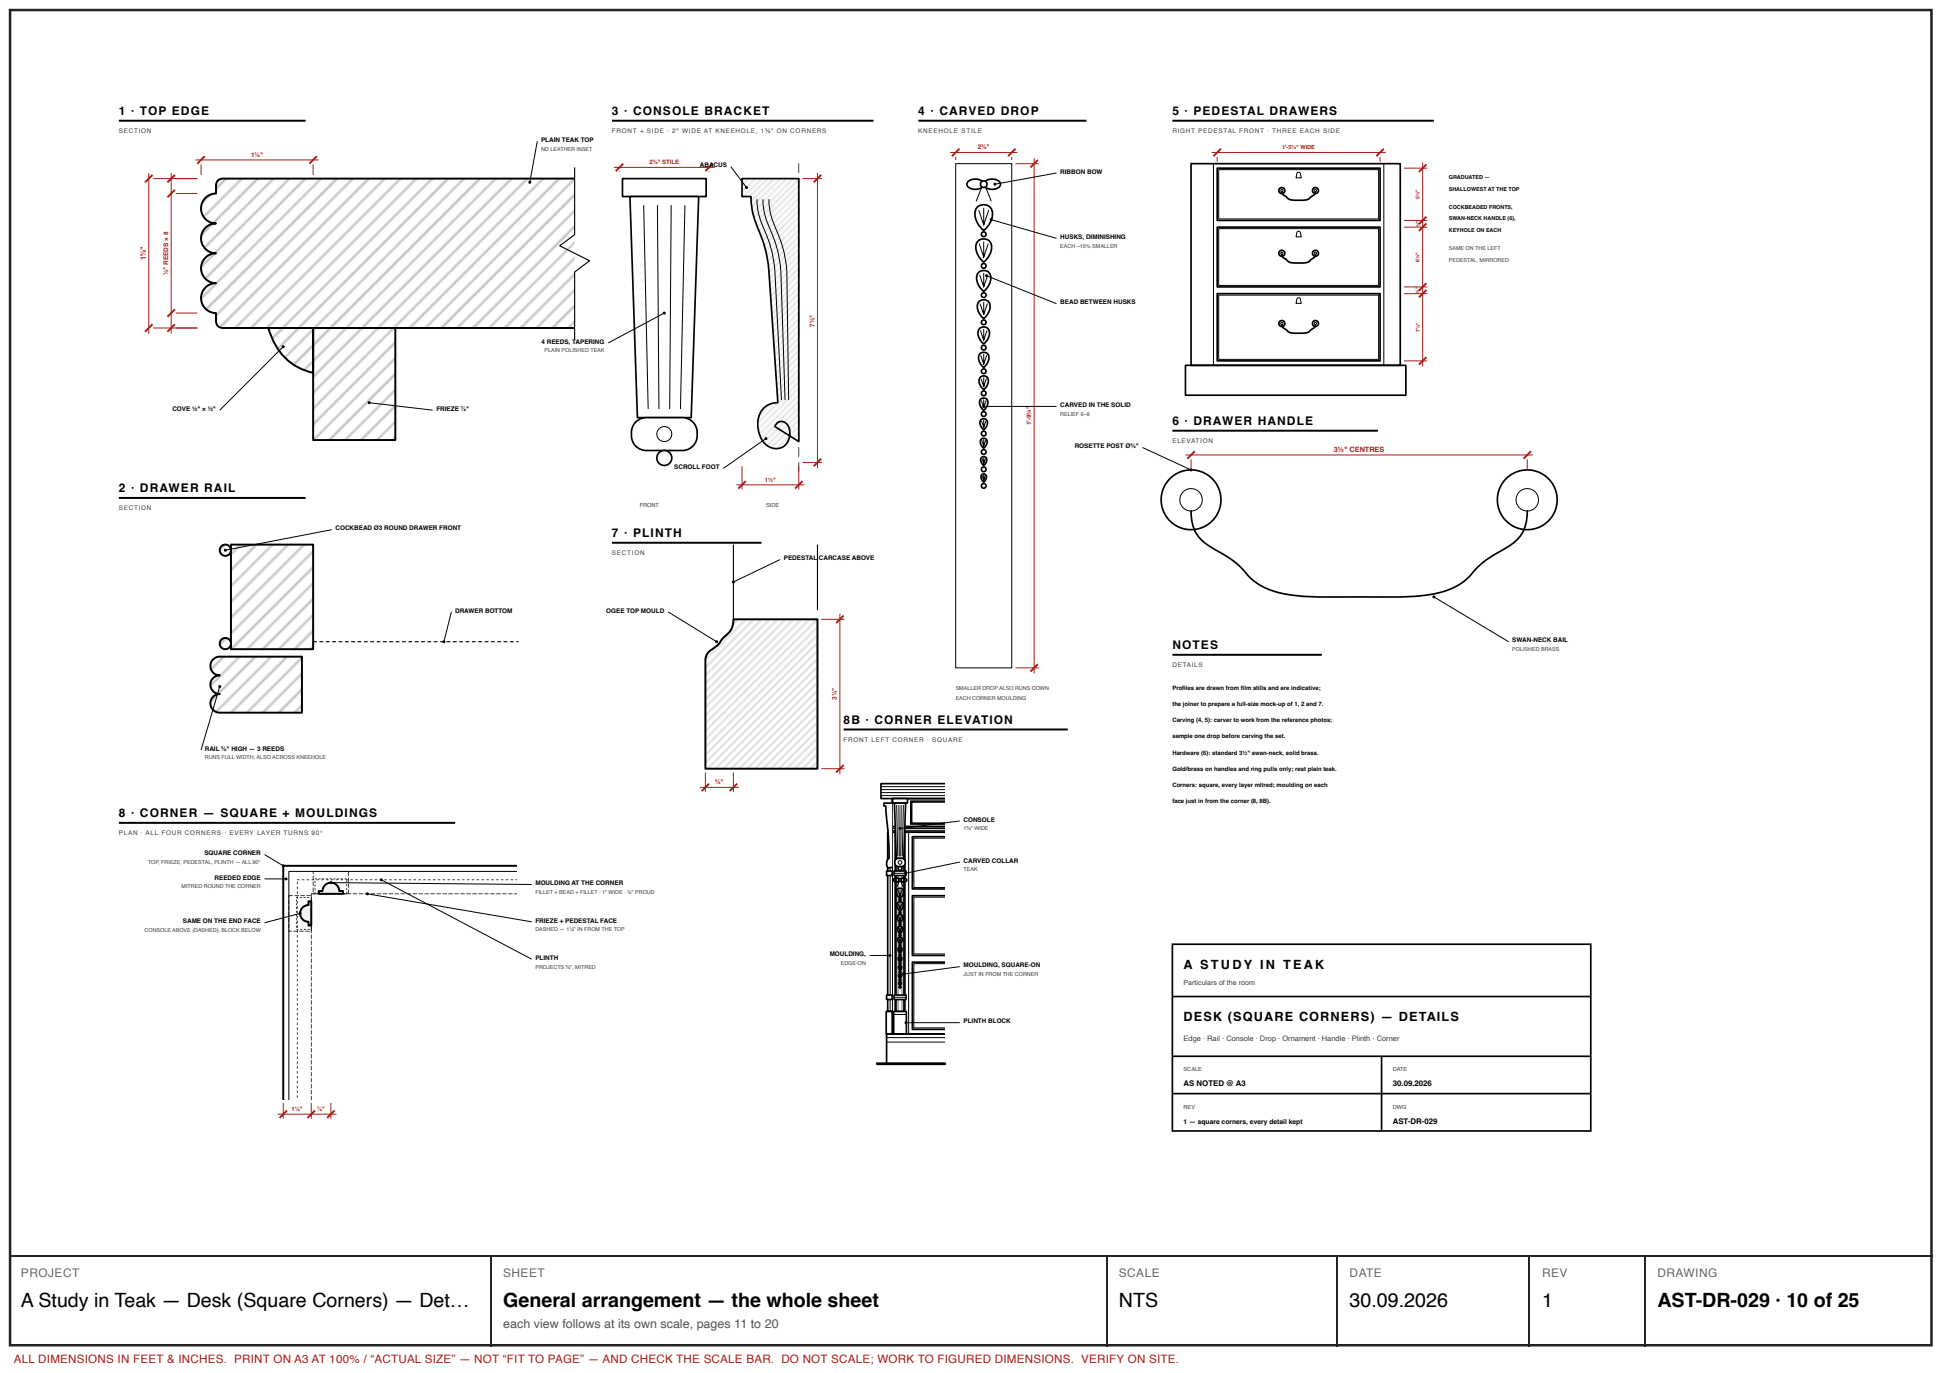
[picture p291: page 10]
1 · TOP EDGE; SECTION; ⅛" REEDS × 8; COVE ½" × ½"; FRIEZE ⅞"; 2 · DRAWER RAIL; DRAWER BOTTOM; 3 · CONSOLE BRACKET; 2⅜" STILE; FRONT; SIDE; ABACUS; SCROLL FOOT; 4 · CARVED DROP; KNEEHOLE STILE; RIBBON BOW; HUSKS, DIMINISHING; EACH ~10% SMALLER; 5 · PEDESTAL DRAWERS; 1'-5⅛" WIDE; GRADUATED —; COCKBEADED FRONTS,; PEDESTAL, MIRRORED; 6 · DRAWER HANDLE; ELEVATION; 3½" CENTRES; 7 · PLINTH; SQUARE CORNER; REEDED EDGE; MITRED ROUND THE CORNER; MOULDING AT THE CORNER; PLINTH; PROJECTS ⅝", MITRED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

PLAIN TEAK TOP
NO LEATHER INSET

FRONT + SIDE · 2" WIDE AT KNEEHOLE, 1⅜" ON CORNERS

RIGHT PEDESTAL FRONT · THREE EACH SIDE

SHALLOWEST AT THE TOP

SWAN-NECK HANDLE (6),

KEYHOLE ON EACH

SAME ON THE LEFT

BEAD BETWEEN HUSKS

4 REEDS, TAPERING
PLAIN POLISHED TEAK

CARVED IN THE SOLID
RELIEF 6–8

ROSETTE POST Ø⅝"

COCKBEAD Ø3 ROUND DRAWER FRONT

PEDESTAL CARCASE ABOVE

OGEE TOP MOULD

SWAN-NECK BAIL
POLISHED BRASS

SMALLER DROP ALSO RUNS DOWN
EACH CORNER MOULDING

Profiles are drawn from film stills and are indicative;

the joiner to prepare a full-size mock-up of 1, 2 and 7.

Carving (4, 5): carver to work from the reference photos;

FRONT LEFT CORNER · SQUARE

sample one drop before carving the set.

RAIL ⅝" HIGH — 3 REEDS

RUNS FULL WIDTH, ALSO ACROSS KNEEHOLE

Hardware (6): standard 3½" swan-neck, solid brass.

Gold/brass on handles and ring pulls only; rest plain teak.

Corners: square, every layer mitred; moulding on each

8 · CORNER — SQUARE + MOULDINGS

face just in from the corner (8, 8B).

PLAN · ALL FOUR CORNERS · EVERY LAYER TURNS 90°

TOP, FRIEZE, PEDESTAL, PLINTH — ALL 90°

FILLET + BEAD + FILLET · 1" WIDE · ½" PROUD

FRIEZE + PEDESTAL FACE
DASHED — 1⅛" IN FROM THE TOP

CONSOLE ABOVE (DASHED), BLOCK BELOW

SAME ON THE END FACE

MOULDING, SQUARE-ON
JUST IN FROM THE CORNER

Particulars of the room

DESK (SQUARE CORNERS) — DETAILS

Edge · Rail · Console · Drop · Ornament · Handle · Plinth · Corner

1 — square corners, every detail kept

A Study in Teak — Desk (Square Corners) — Det…

General arrangement — the whole sheet

AST-DR-029 · 10 of 25

each view follows at its own scale, pages 11 to 20

### 1 · TOP EDGE

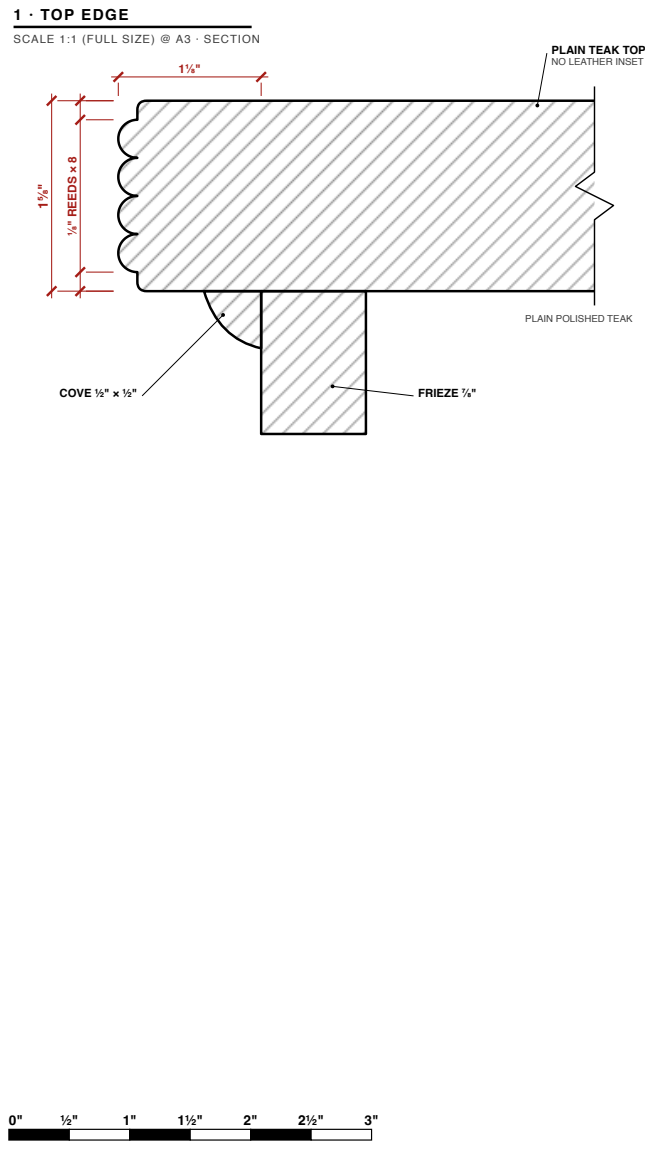
[picture p292: page 11]
⅛" REEDS × 8; COVE ½" × ½"; FRIEZE ⅞"; 1 · top edge

SCALE 1:1 (FULL SIZE) @ A3 · SECTION

PLAIN TEAK TOP
NO LEATHER INSET

PLAIN POLISHED TEAK

AST-DR-029 · 11 of 25

Edge · Rail · Console · Drop · Ornament · Handle · Plinth · Corner

## 3 · CONSOLE BRACKET

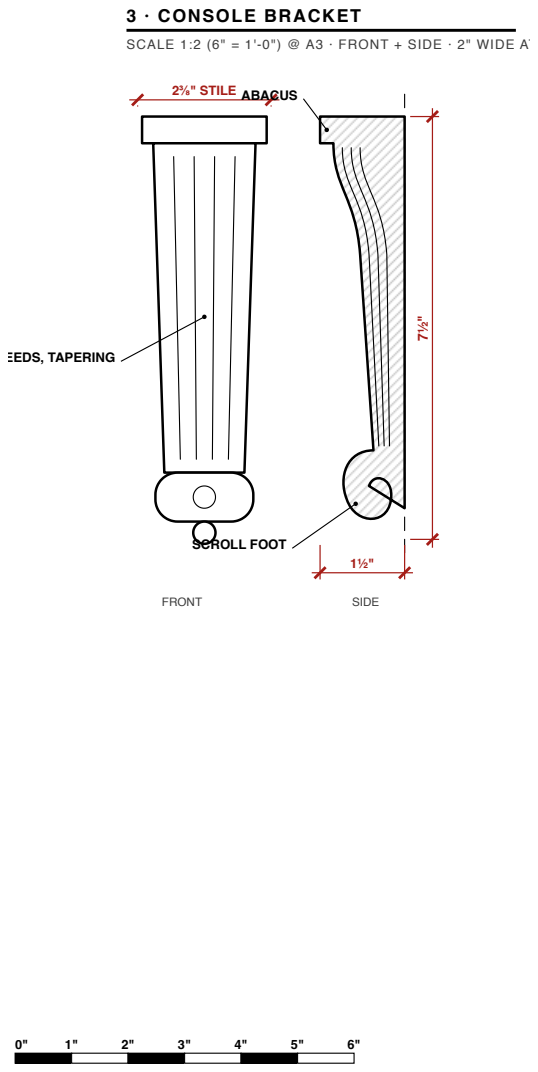
[picture p293: page 12]
2⅜" STILE; FRONT; SIDE; ABACUS; SCROLL FOOT; EEDS, TAPERING; 3 · console bracket

SCALE 1:2 (6" = 1'-0") @ A3 · FRONT + SIDE · 2" WIDE AT

AST-DR-029 · 12 of 25

# 4 · CARVED DROP

2⅜"

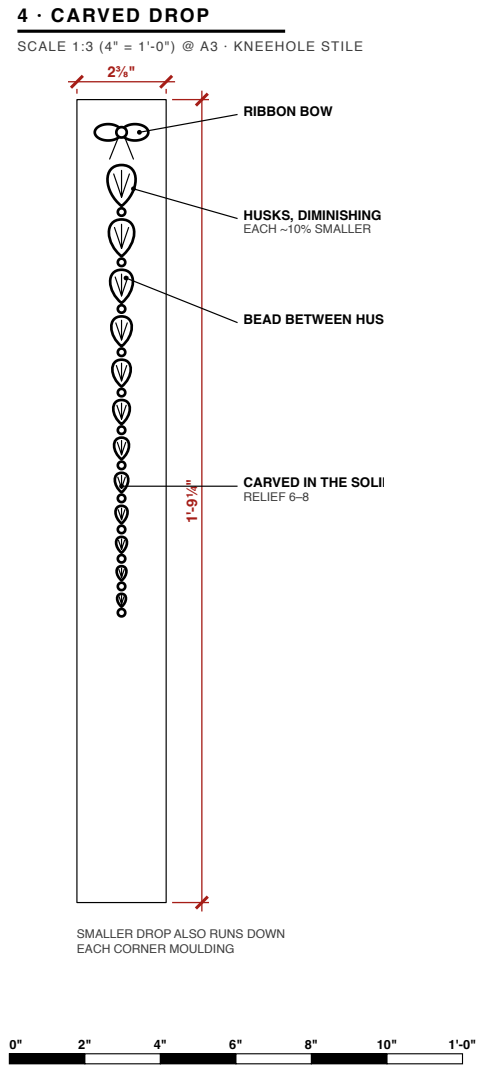
[picture p294: page 13]
RIBBON BOW; HUSKS, DIMINISHING EACH ~10% SMALLER; 4 · carved drop

SCALE 1:3 (4" = 1'-0") @ A3 · KNEEHOLE STILE

BEAD BETWEEN HUS

CARVED IN THE SOLID
RELIEF 6–8

SMALLER DROP ALSO RUNS DOWN
EACH CORNER MOULDING

AST-DR-029 · 13 of 25

# 5 · PEDESTAL DRAWERS

# SCALE 1:4 (3" = 1'-0") @ A3 · RIGHT PEDESTAL FRONT · THREE EACH SIDE

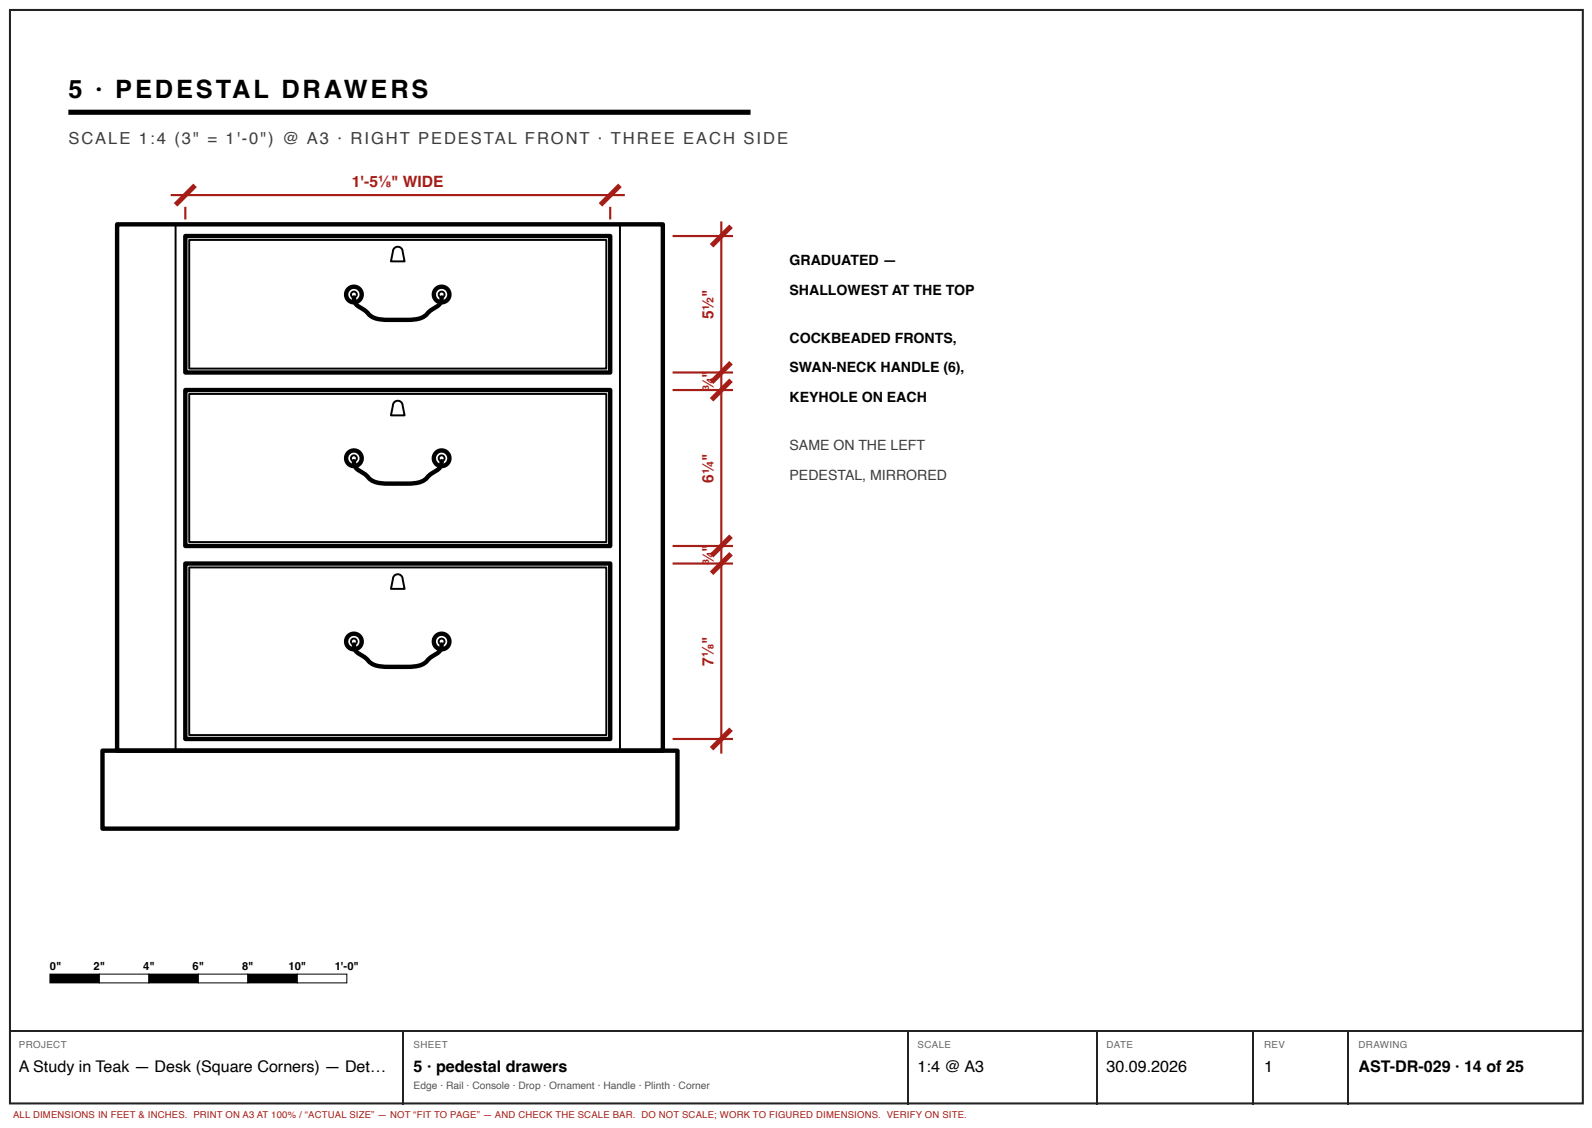
[picture p295: page 14]
1'-5⅛" WIDE; GRADUATED —; COCKBEADED FRONTS,; PEDESTAL, MIRRORED; 5 · pedestal drawers

SHALLOWEST AT THE TOP

SWAN-NECK HANDLE (6),

KEYHOLE ON EACH

SAME ON THE LEFT

AST-DR-029 · 14 of 25

### 2 · DRAWER RAIL

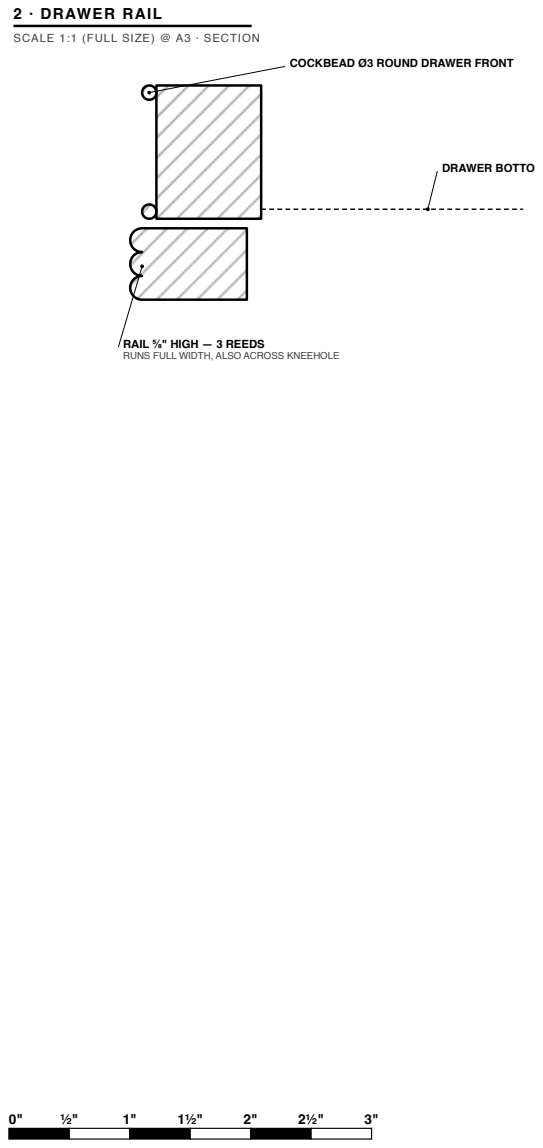
[picture p296: page 15]
DRAWER BOTTO; 2 · drawer rail

SCALE 1:1 (FULL SIZE) @ A3 · SECTION

COCKBEAD Ø3 ROUND DRAWER FRONT

RAIL ⅝" HIGH — 3 REEDS
RUNS FULL WIDTH, ALSO ACROSS KNEEHOLE

AST-DR-029 · 15 of 25

### 6 · DRAWER HANDLE

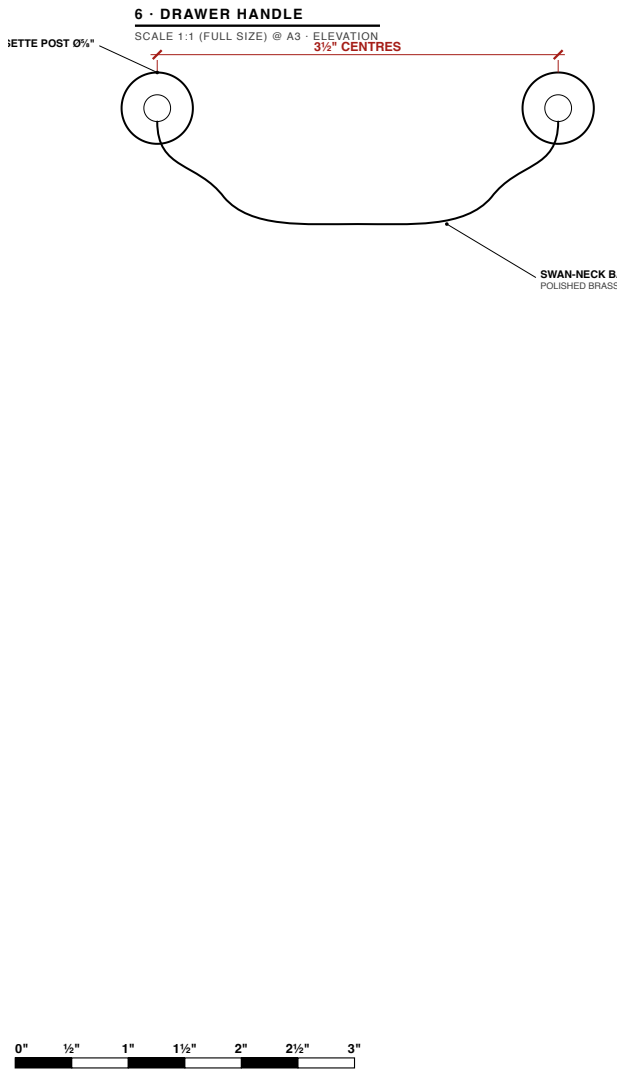
[picture p297: page 16]
3½" CENTRES; 6 · drawer handle

SETTE POST Ø⅝"

SCALE 1:1 (FULL SIZE) @ A3 · ELEVATION

SWAN-NECK BA
POLISHED BRASS

AST-DR-029 · 16 of 25

# 7 · PLINTH

## SCALE 1:1 (FULL SIZE) @ A3 · SECTION

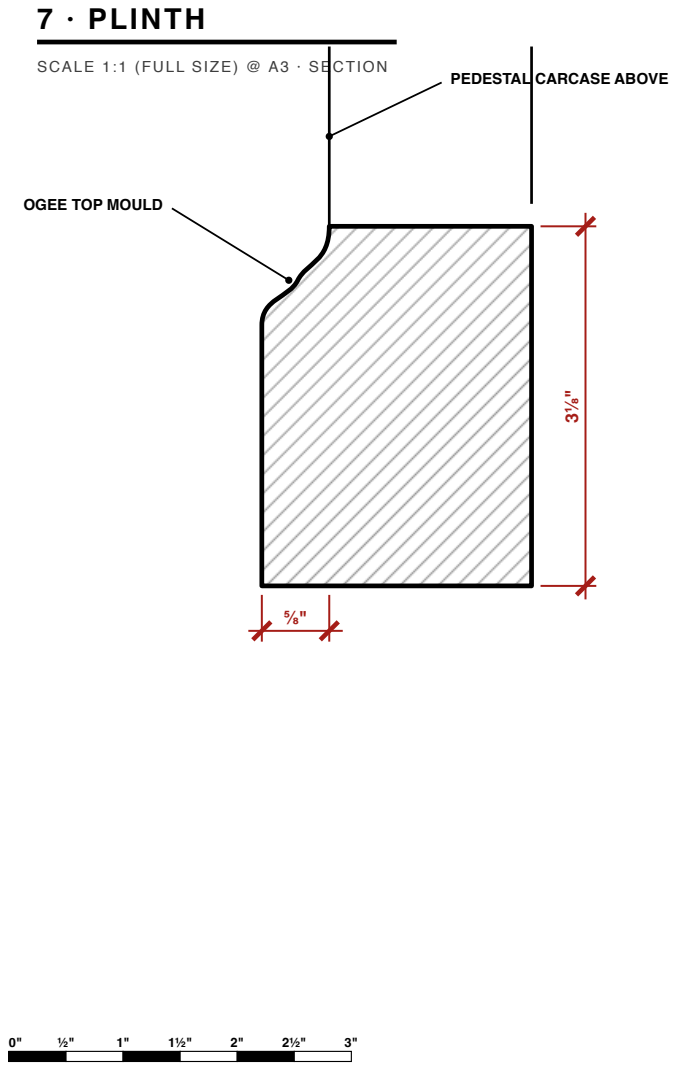
[picture p298: page 17]
7 · plinth

PEDESTAL CARCASE ABOVE

OGEE TOP MOULD

AST-DR-029 · 17 of 25

# NOTES

# DETAILS

Profiles are drawn from film stills and are indicative;

the joiner to prepare a full-size mock-up of 1, 2 and 7.

Carving (4, 5): carver to work from the reference photos;

sample one drop before carving the set.

Hardware (6): standard 3½" swan-neck, solid brass.

Gold/brass on handles and ring pulls only; rest plain teak.

# Corners: square, every layer mitred; moulding on each

face just in from the corner (8, 8B).

## Notes

## AST-DR-029 · 18 of 25

# 8B · CORNER ELEVATION

## SCALE 1:5 @ A3 · FRONT LEFT CORNER · SQUARE

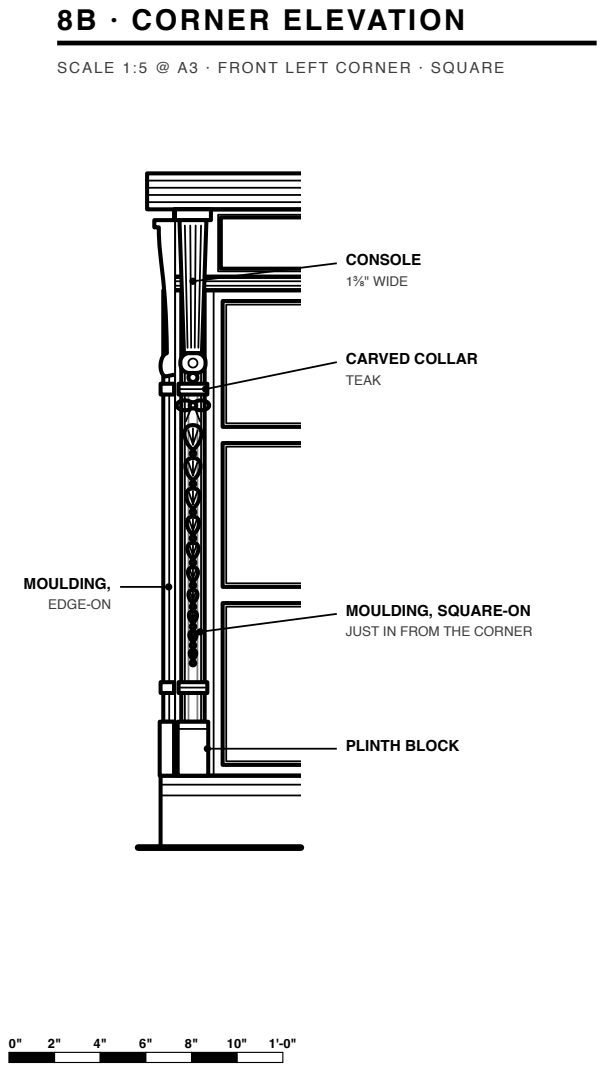
[picture p299: page 19]
MOULDING,; EDGE-ON; CONSOLE; 1⅜" WIDE; CARVED COLLAR; TEAK; PLINTH BLOCK; 8B · corner elevation

MOULDING, SQUARE-ON
JUST IN FROM THE CORNER

AST-DR-029 · 19 of 25

# 8 · CORNER — SQUARE + MOULDINGS

## SCALE 1:2 (6" = 1'-0") @ A3 · PLAN · ALL FOUR CORNERS · EVERY LAYER TURNS 90°

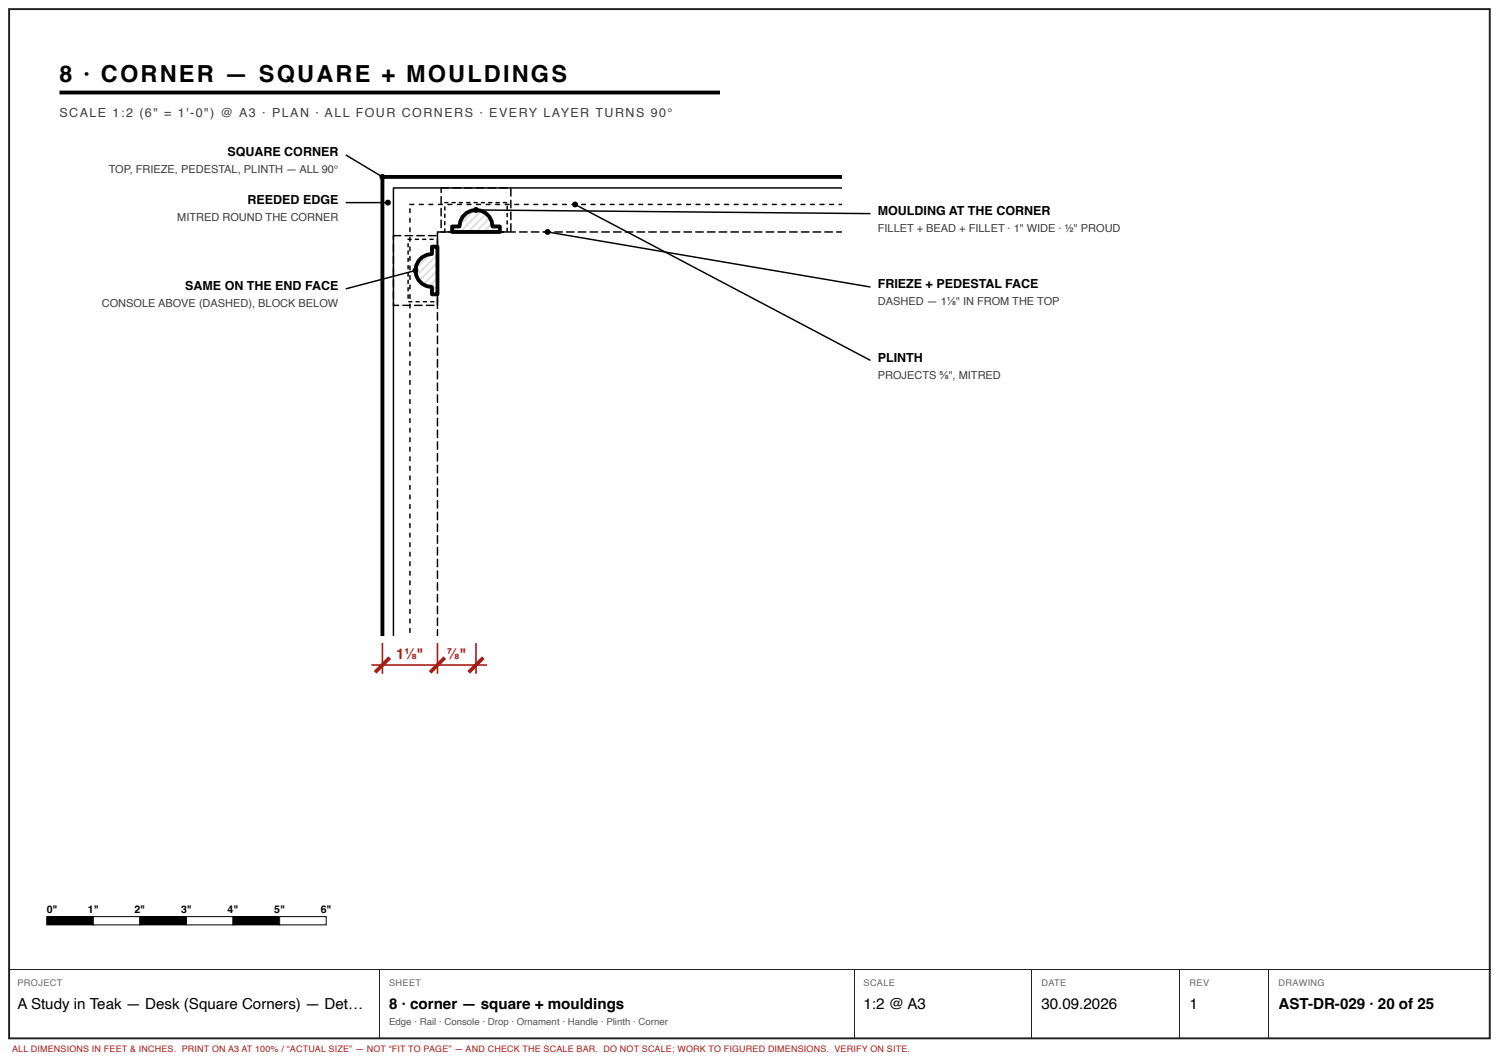
[picture p300: page 20]
SQUARE CORNER; REEDED EDGE; MITRED ROUND THE CORNER; MOULDING AT THE CORNER; PLINTH; PROJECTS ⅝", MITRED

TOP, FRIEZE, PEDESTAL, PLINTH — ALL 90°

FILLET + BEAD + FILLET · 1" WIDE · ½" PROUD

SAME ON THE END FACE

FRIEZE + PEDESTAL FACE
DASHED — 1⅛" IN FROM THE TOP

CONSOLE ABOVE (DASHED), BLOCK BELOW

8 · corner — square + mouldings

AST-DR-029 · 20 of 25

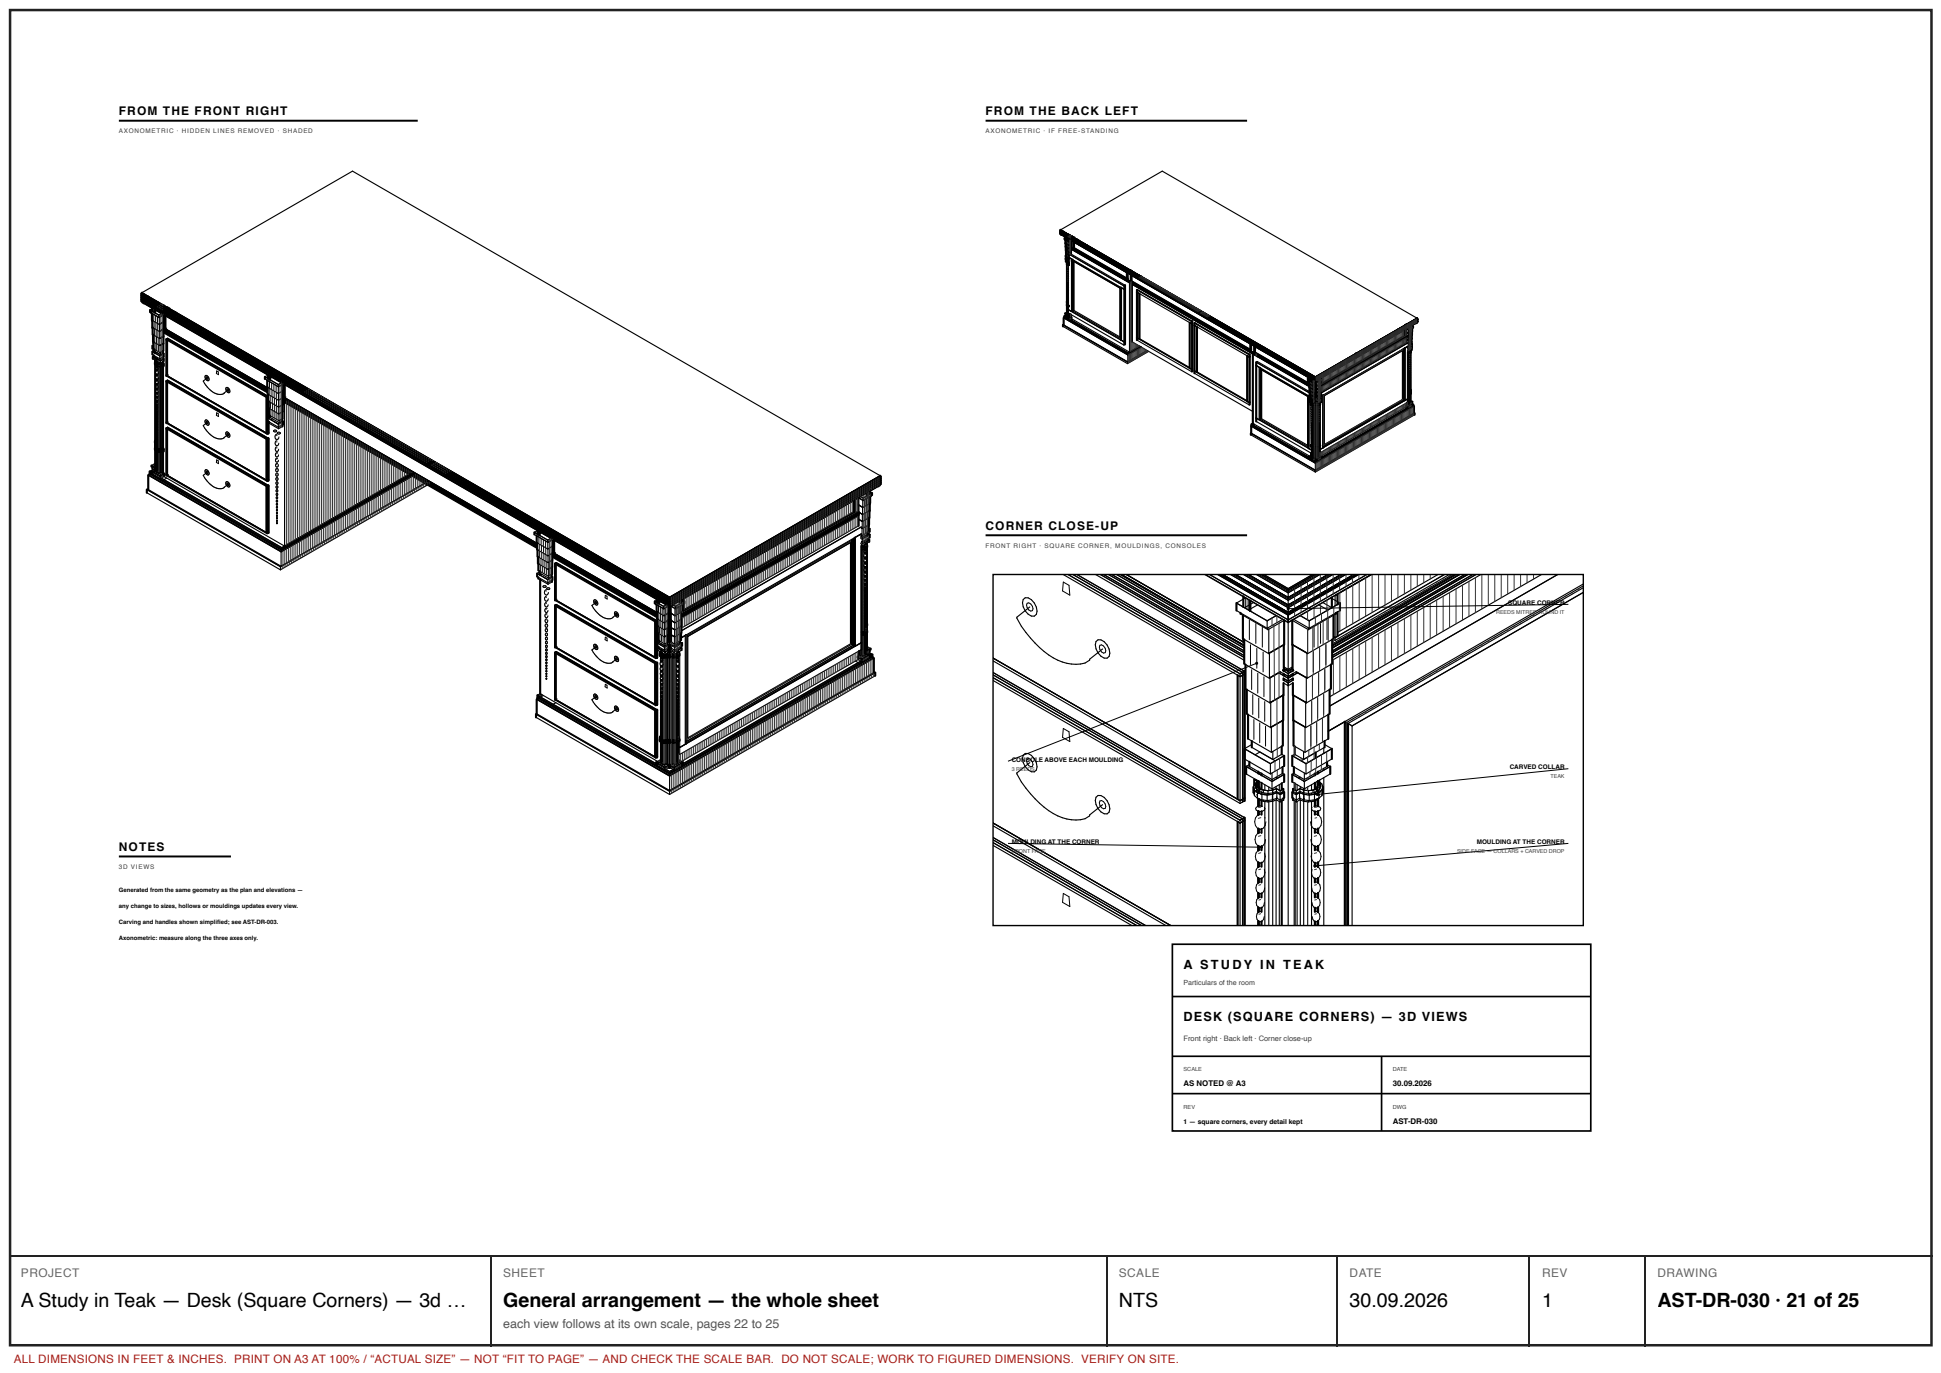
[picture p301: page 21]
3 REEDS; CARVED COLLAR; TEAK; NOTES; 3D VIEWS; SCALE; AS NOTED @ A3; DATE; REV; DWG; AST-DR-030

FROM THE FRONT RIGHT

FROM THE BACK LEFT

AXONOMETRIC · HIDDEN LINES REMOVED · SHADED

AXONOMETRIC · IF FREE-STANDING

CORNER CLOSE-UP

FRONT RIGHT · SQUARE CORNER, MOULDINGS, CONSOLES

SQUARE CORNER
REEDS MITRED ROUND IT

CONSOLE ABOVE EACH MOULDING

MOULDING AT THE CORNER
FRONT FACE

SIDE FACE — COLLARS + CARVED DROP

Generated from the same geometry as the plan and elevations —

any change to sizes, hollows or mouldings updates every view.

Carving and handles shown simplified; see AST-DR-003.

Axonometric: measure along the three axes only.

Particulars of the room

DESK (SQUARE CORNERS) — 3D VIEWS

Front right · Back left · Corner close-up

1 — square corners, every detail kept

A Study in Teak — Desk (Square Corners) — 3d …

General arrangement — the whole sheet

AST-DR-030 · 21 of 25

each view follows at its own scale, pages 22 to 25

## FROM THE FRONT RIGHT

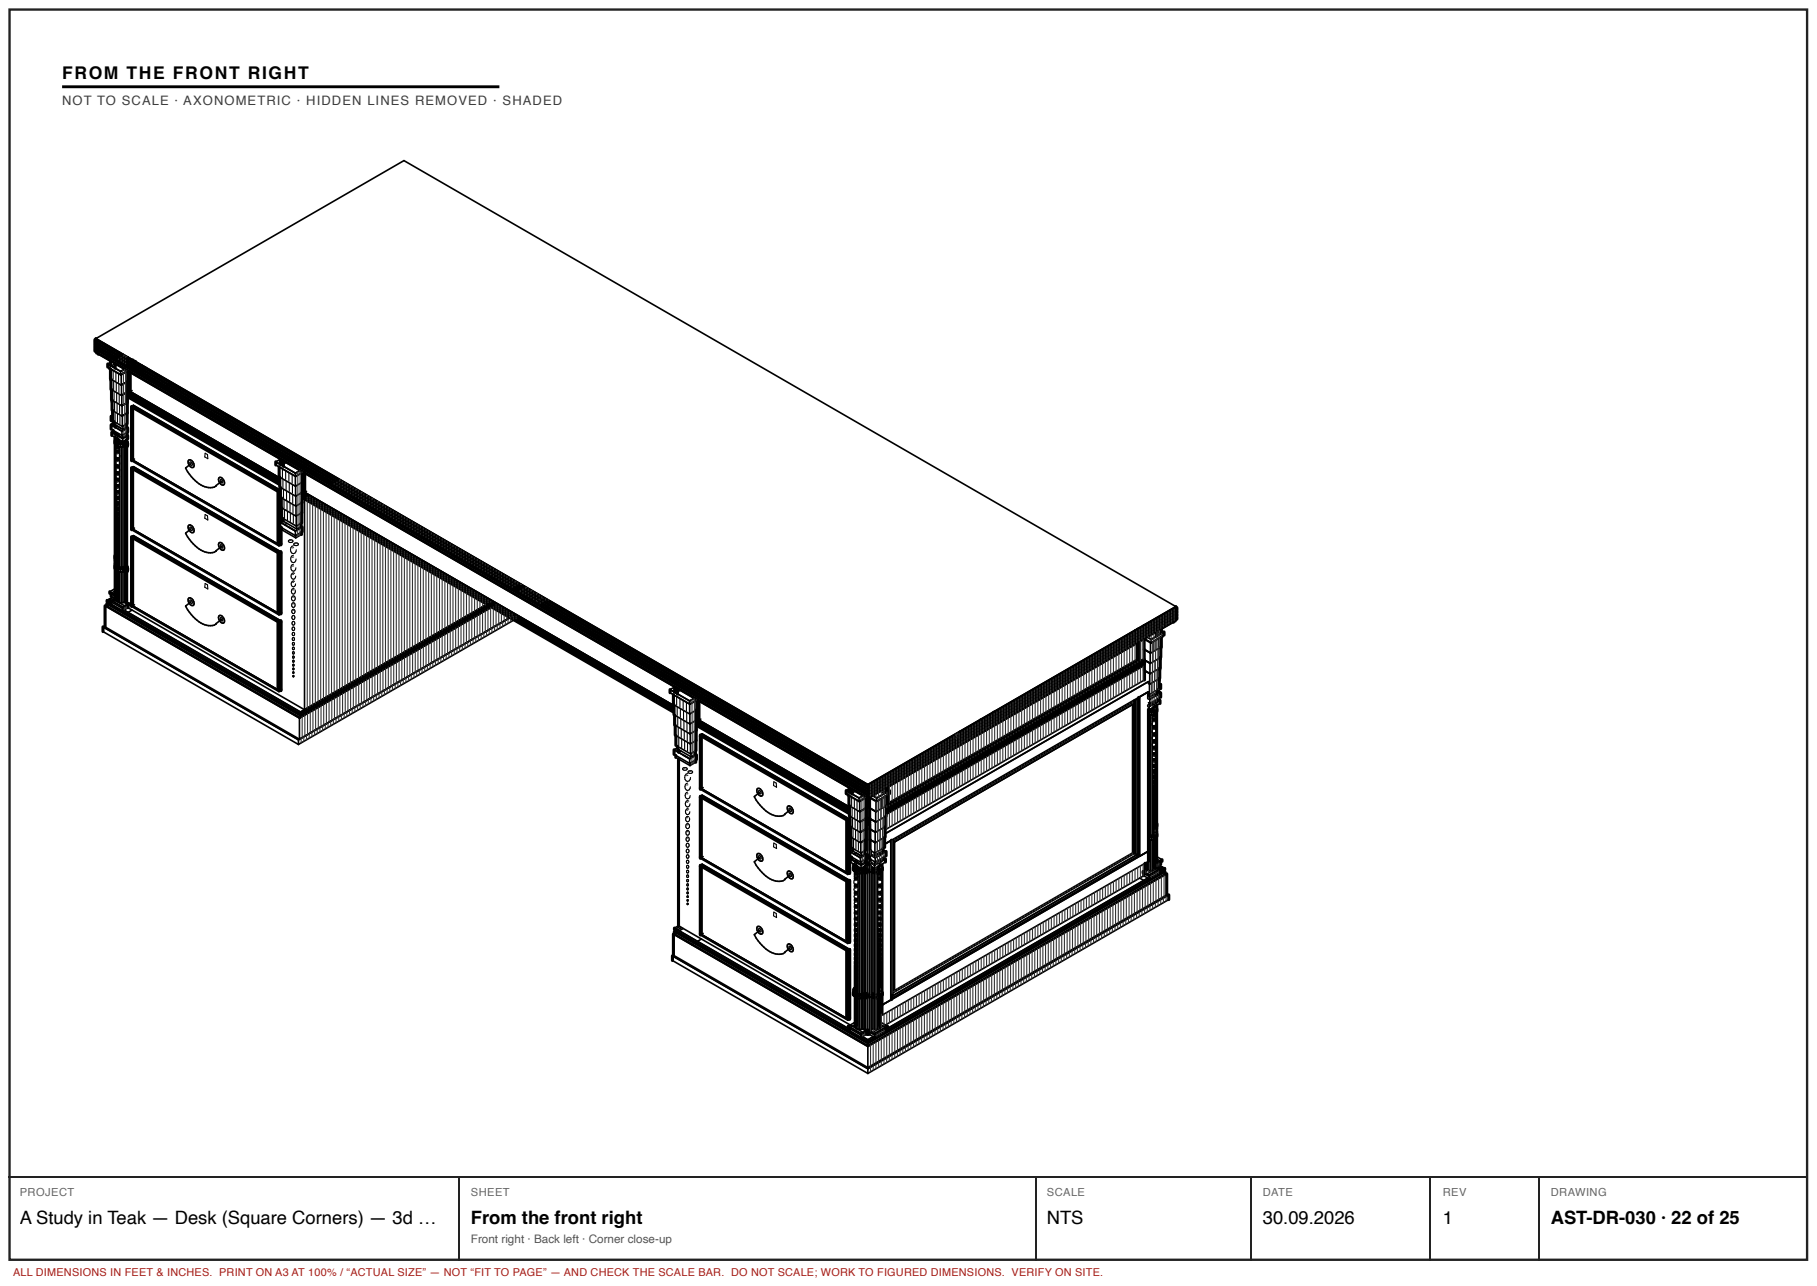
[picture p302: page 22]

NOT TO SCALE · AXONOMETRIC · HIDDEN LINES REMOVED · SHADED

A Study in Teak — Desk (Square Corners) — 3d …

From the front right

AST-DR-030 · 22 of 25

Front right · Back left · Corner close-up

# FROM THE BACK LEFT

## NOT TO SCALE · AXONOMETRIC · IF FREE-STANDING

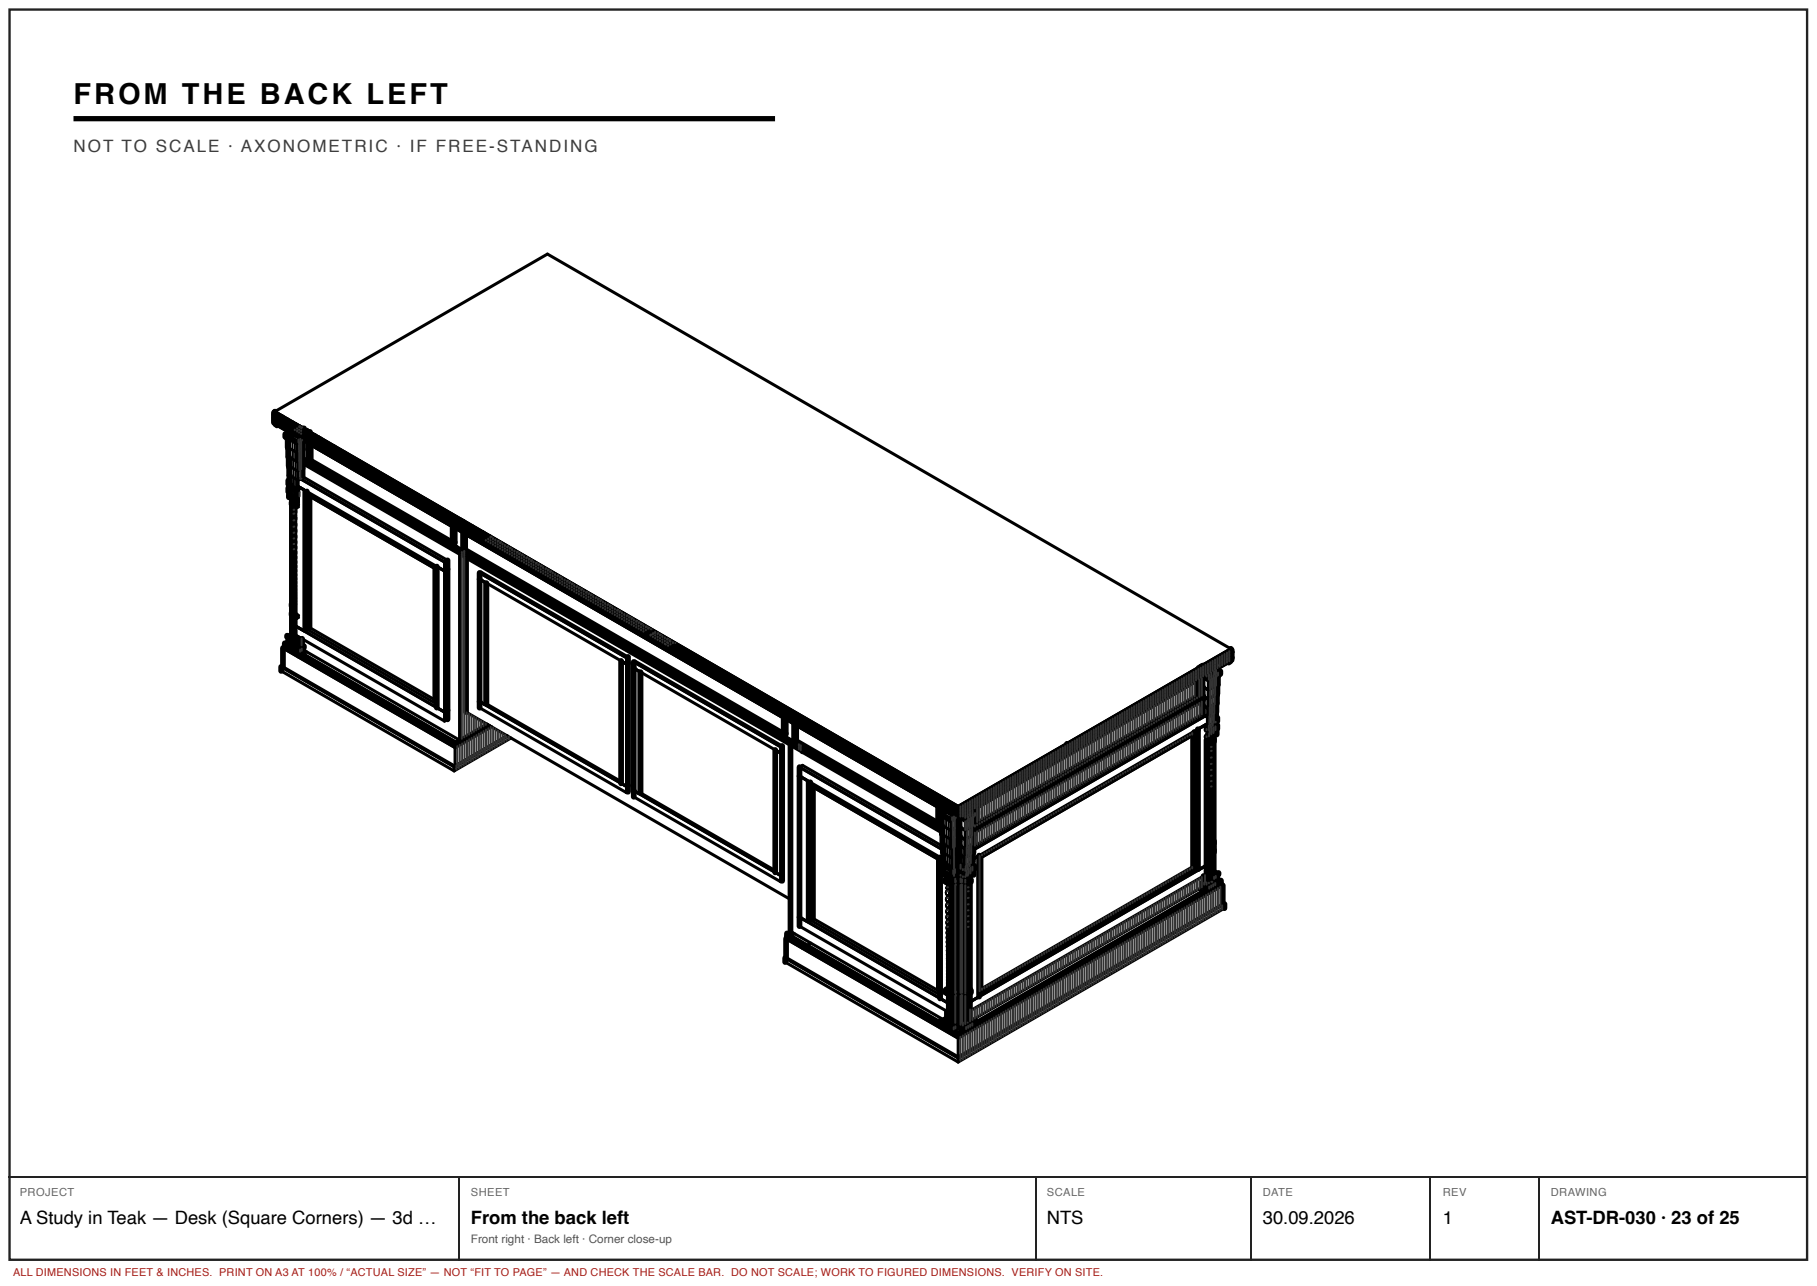
[picture p303: page 23]

A Study in Teak — Desk (Square Corners) — 3d …

From the back left

AST-DR-030 · 23 of 25

Front right · Back left · Corner close-up

# CORNER CLOSE-UP

## NOT TO SCALE · FRONT RIGHT · SQUARE CORNER, MOULDINGS, CONSOLES

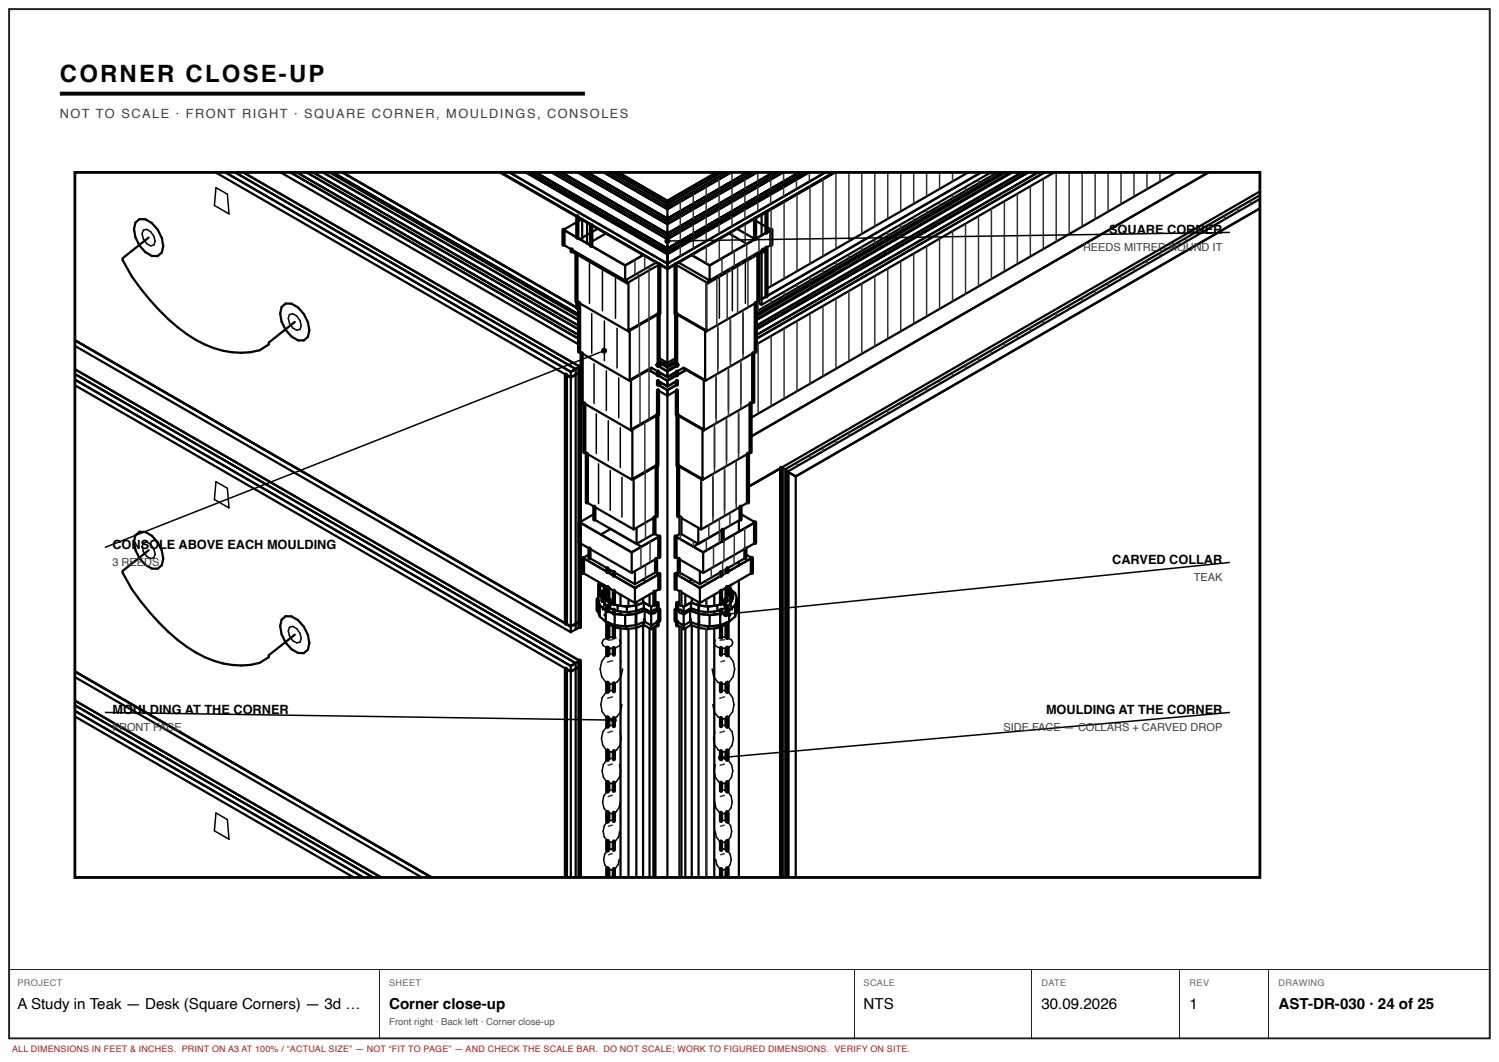
[picture p304: page 24]
3 REEDS; CARVED COLLAR; TEAK

SQUARE CORNER
REEDS MITRED ROUND IT

CONSOLE ABOVE EACH MOULDING

MOULDING AT THE CORNER
FRONT FACE

SIDE FACE — COLLARS + CARVED DROP

A Study in Teak — Desk (Square Corners) — 3d …

Corner close-up

AST-DR-030 · 24 of 25

Front right · Back left · Corner close-up

# NOTES

# 3D VIEWS

# Generated from the same geometry as the plan and elevations —

any change to sizes, hollows or mouldings updates every view.

Carving and handles shown simplified; see AST-DR-003.

Axonometric: measure along the three axes only.

## A Study in Teak — Desk (Square Corners) — 3d …

## Notes

Front right · Back left · Corner close-up

## AST-DR-030 · 25 of 25
