sakshampan733-cloud/a-study-in-teak/cad/print/door-narrow-a4.pdf

# FRONT ELEVATION — D2 · D3

A

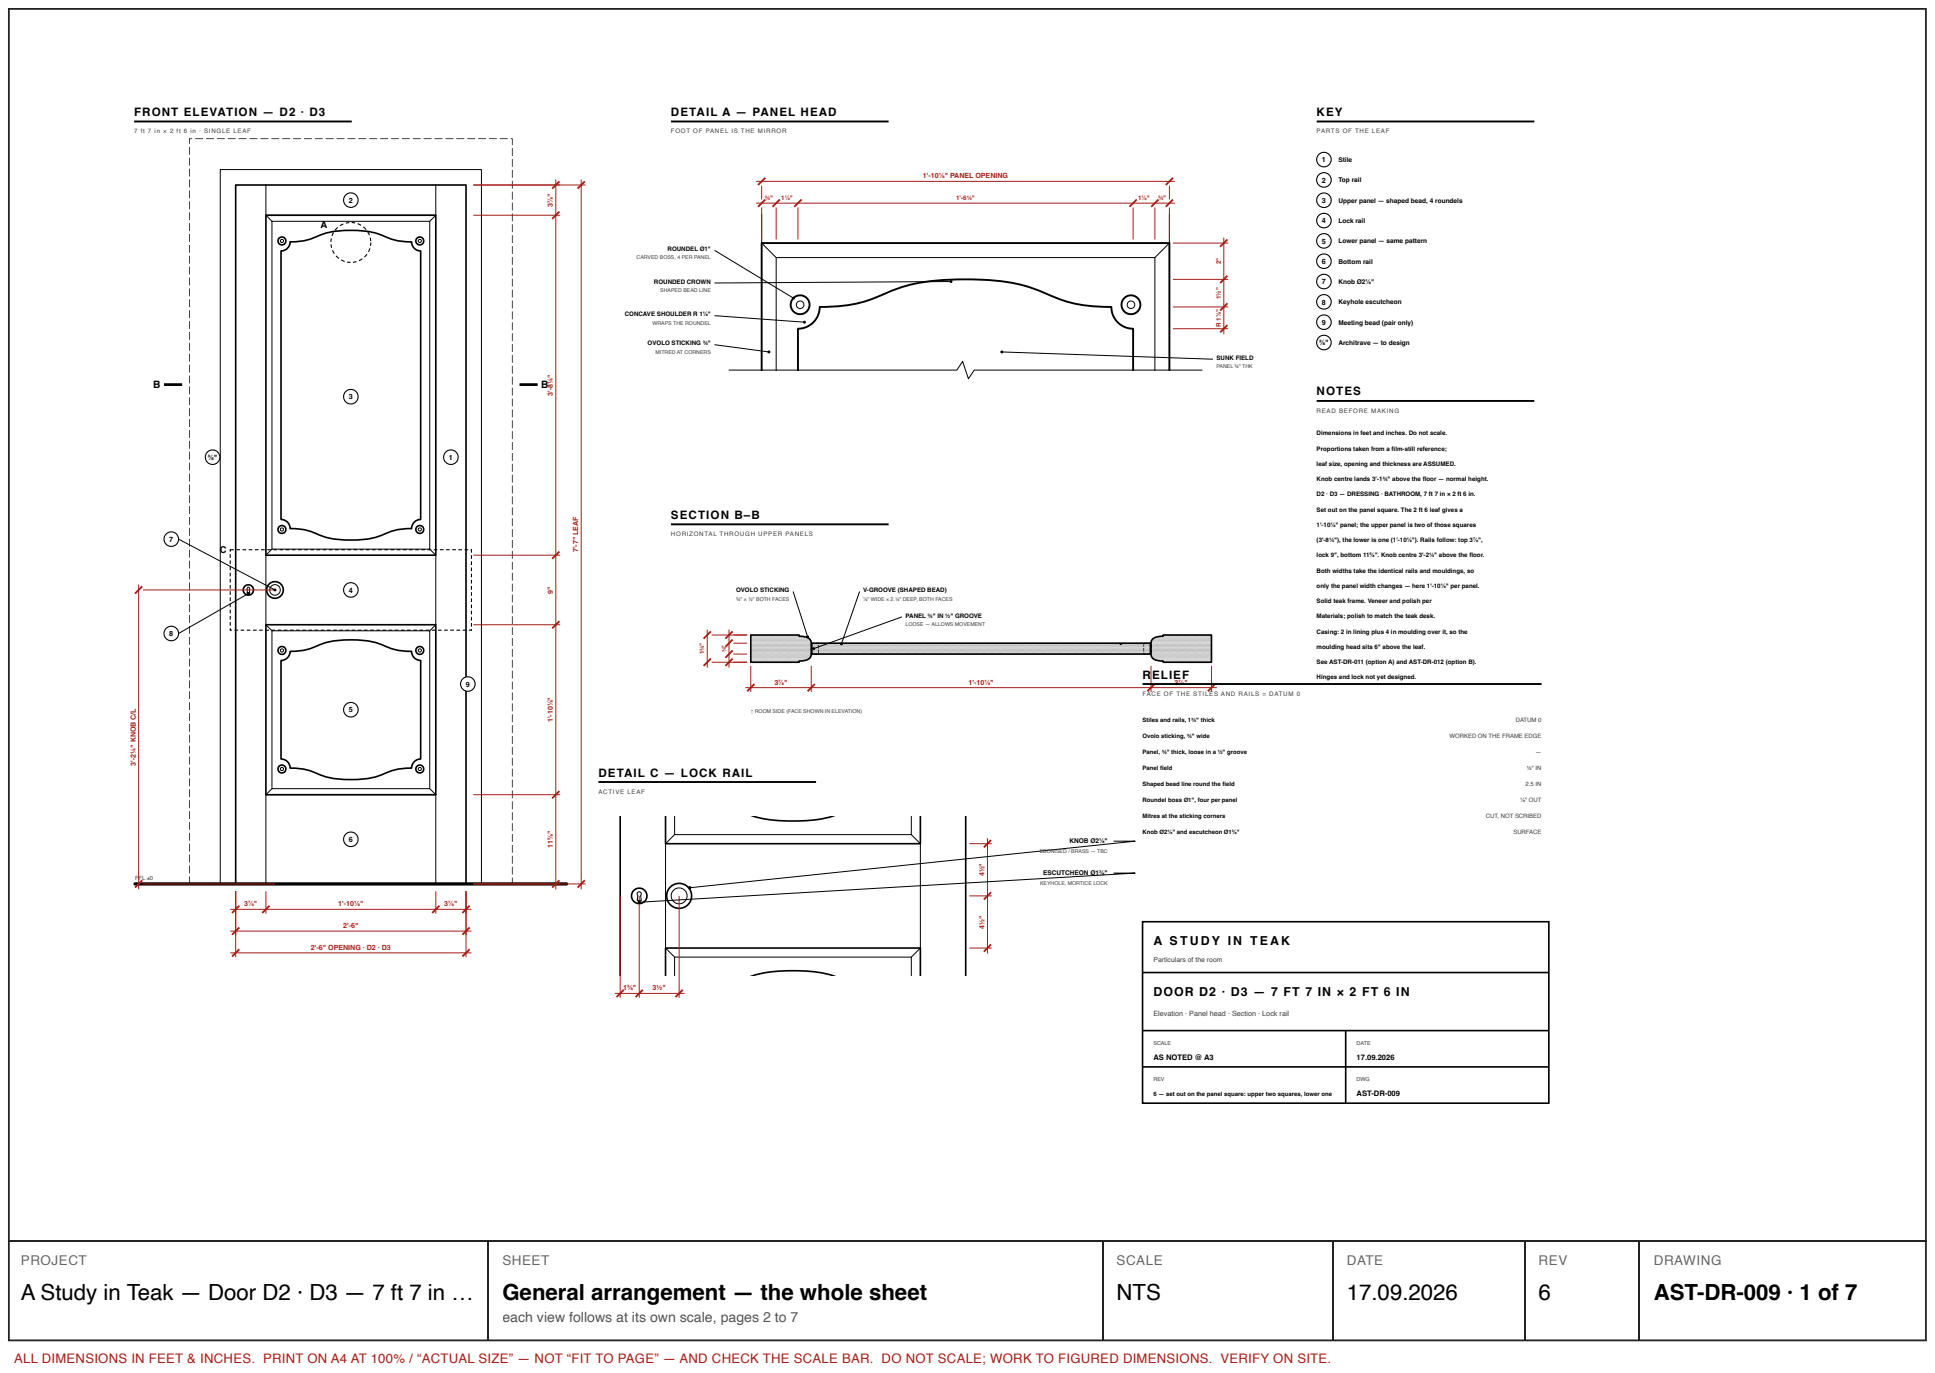
[picture p326: page 1]
FFL ±0; 2'-6" OPENING · D2 · D3; 7'-7" LEAF; 3'-2¼" KNOB C/L; 1'-10⅛" PANEL OPENING; ROUNDEL Ø1"; ROUNDED CROWN; CONCAVE SHOULDER R 1⅛"; OVOLO STICKING ¾"; SUNK FIELD; PANEL ¾" THK; SECTION B–B; OVOLO STICKING; ¾" × ½" BOTH FACES; ACTIVE LEAF; KNOB Ø2⅛"; ESCUTCHEON Ø1⅜"; KEY; 1 Stile; 2 Top rail; 4 Lock rail; 6 Bottom rail; 7 Knob Ø2⅛"; 8 Keyhole escutcheon; Architrave — to design; NOTES; RELIEF; Hinges and lock not yet designed.; Stiles and rails, 1¾" thick; DATUM 0; Ovolo sticking, ¾" wide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

DETAIL A — PANEL HEAD

7 ft 7 in × 2 ft 6 in · SINGLE LEAF

FOOT OF PANEL IS THE MIRROR

PARTS OF THE LEAF

3 Upper panel — shaped bead, 4 roundels

5 Lower panel — same pattern

CARVED BOSS, 4 PER PANEL

SHAPED BEAD LINE

WRAPS THE ROUNDEL

9 Meeting bead (pair only)

MITRED AT CORNERS

READ BEFORE MAKING

Dimensions in feet and inches. Do not scale.

Proportions taken from a film-still reference;

leaf size, opening and thickness are ASSUMED.

Knob centre lands 3'-1¾" above the floor — normal height.

D2 · D3 — DRESSING · BATHROOM, 7 ft 7 in × 2 ft 6 in.

Set out on the panel square. The 2 ft 6 leaf gives a

1'-10⅛" panel; the upper panel is two of those squares

HORIZONTAL THROUGH UPPER PANELS

(3'-8¼"), the lower is one (1'-10⅛"). Rails follow: top 3⅞",

lock 9", bottom 11⅝". Knob centre 3'-2¼" above the floor.

Both widths take the identical rails and mouldings, so

only the panel width changes — here 1'-10⅛" per panel.

V-GROOVE (SHAPED BEAD)
⅛" WIDE × 2.¼" DEEP, BOTH FACES

Solid teak frame. Veneer and polish per

PANEL ¾" IN ½" GROOVE

LOOSE — ALLOWS MOVEMENT

Materials; polish to match the teak desk.

Casing: 2 in lining plus 4 in moulding over it, so the

moulding head sits 6" above the leaf.

See AST-DR-011 (option A) and AST-DR-012 (option B).

FACE OF THE STILES AND RAILS = DATUM 0

↑ ROOM SIDE (FACE SHOWN IN ELEVATION)

DETAIL C — LOCK RAIL

EBONISED / BRASS — TBC

KEYHOLE, MORTICE LOCK

Particulars of the room

DOOR D2 · D3 — 7 FT 7 IN × 2 FT 6 IN

Elevation · Panel head · Section · Lock rail

6 — set out on the panel square: upper two squares, lower one

PROJECT
A Study in Teak — Door D2 · D3 — 7 ft 7 in …

SHEET
General arrangement — the whole sheet

DRAWING
AST-DR-009 · 1 of 7

each view follows at its own scale, pages 2 to 7

ALL DIMENSIONS IN FEET & INCHES. PRINT ON A4 AT 100% / “ACTUAL SIZE” — NOT “FIT TO PAGE” — AND CHECK THE SCALE BAR. DO NOT SCALE; WORK TO FIGURED DIMENSIONS. VERIFY ON SITE.

# DETAIL A — PANEL HEAD

# SCALE 1:4 (3" = 1'-0") @ A4 · FOOT OF PANEL IS THE MIRROR

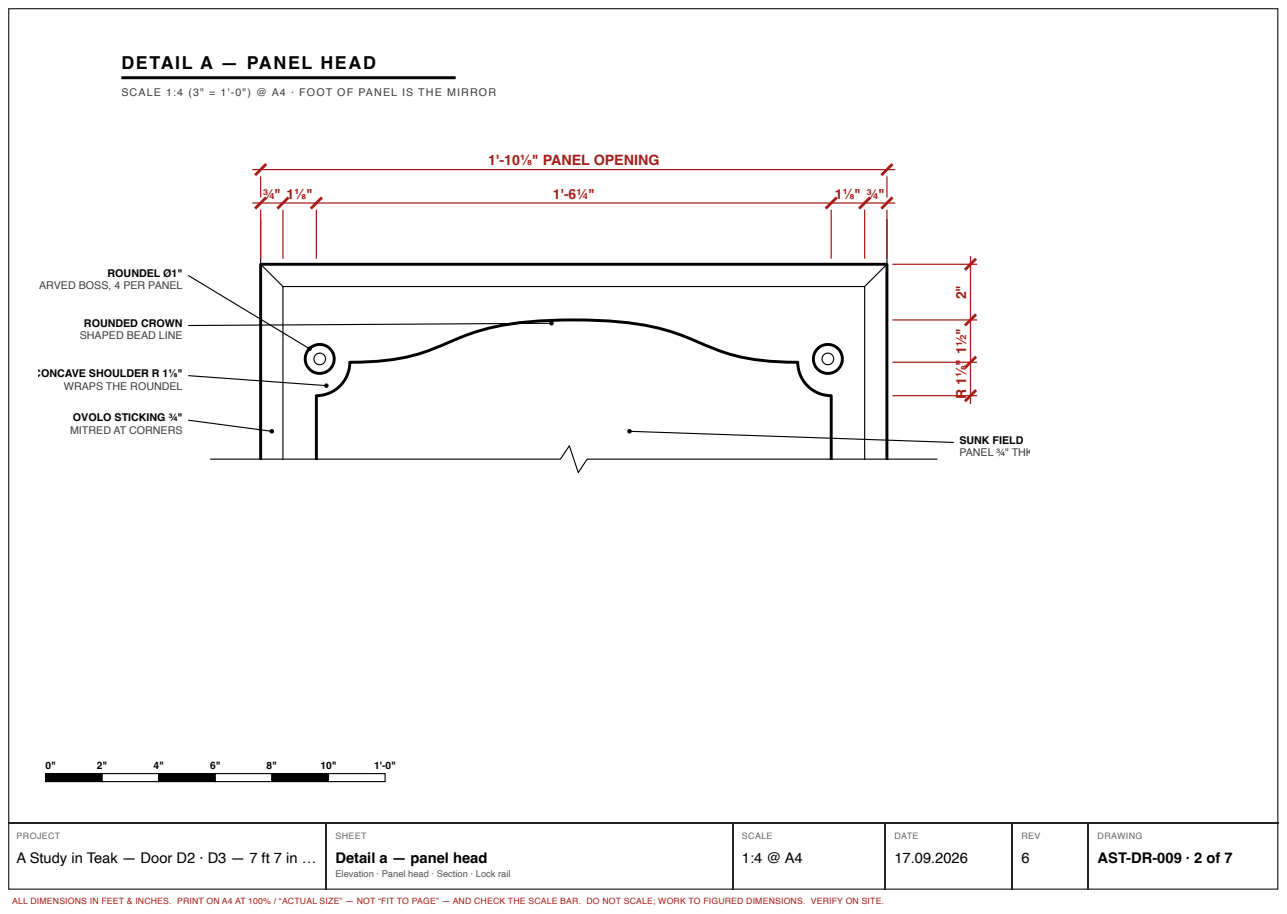
[picture p327: page 2]
1'-10⅛" PANEL OPENING; ROUNDEL Ø1"; SUNK FIELD PANEL ¾" THK

ARVED BOSS, 4 PER PANEL

ROUNDED CROWN
SHAPED BEAD LINE

CONCAVE SHOULDER R 1⅛"
WRAPS THE ROUNDEL

OVOLO STICKING ¾"
MITRED AT CORNERS

Detail a — panel head

AST-DR-009 · 2 of 7

Elevation · Panel head · Section · Lock rail

# KEY

# PARTS OF THE LEAF

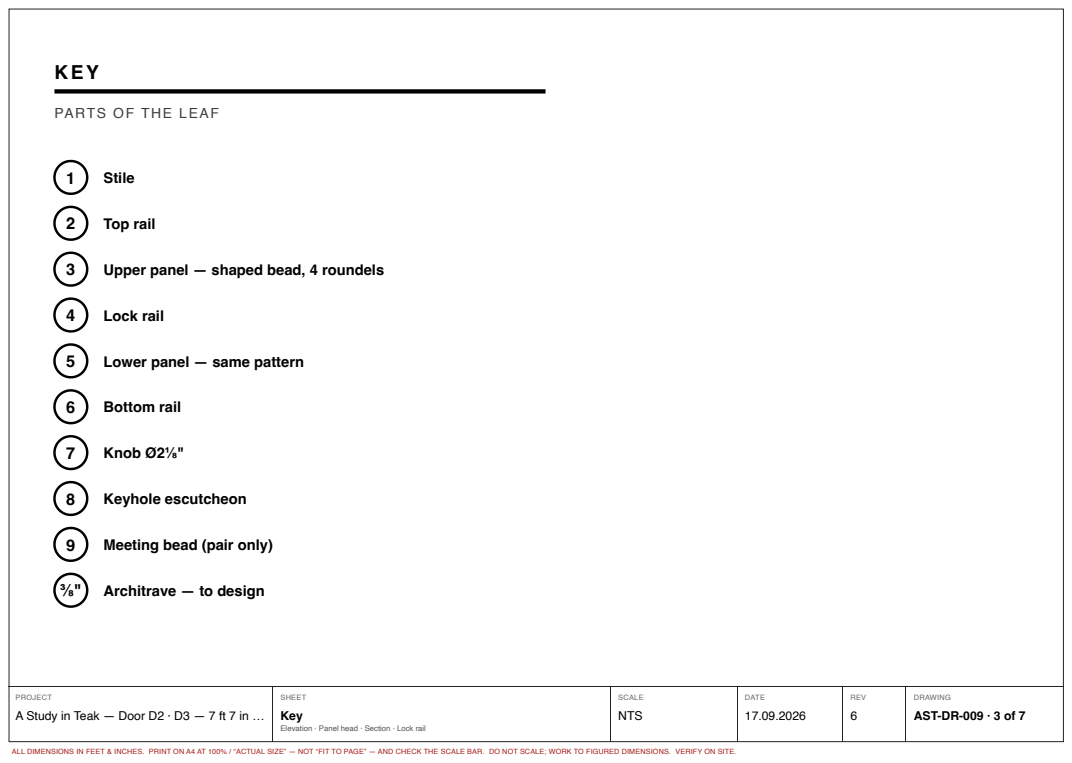
[picture p328: page 3]
1 Stile; 2 Top rail; 4 Lock rail; 6 Bottom rail; 7 Knob Ø2⅛"; 8 Keyhole escutcheon; Architrave — to design; Key

3 Upper panel — shaped bead, 4 roundels

5 Lower panel — same pattern

9 Meeting bead (pair only)

AST-DR-009 · 3 of 7

# NOTES

# READ BEFORE MAKING

Dimensions in feet and inches. Do not scale.

Proportions taken from a film-still reference;

leaf size, opening and thickness are ASSUMED.

Knob centre lands 3'-1¾" above the floor — normal height.

D2 · D3 — DRESSING · BATHROOM, 7 ft 7 in × 2 ft 6 in.

# Set out on the panel square. The 2 ft 6 leaf gives a

# 1'-10⅛" panel; the upper panel is two of those squares

(3'-8¼"), the lower is one (1'-10⅛"). Rails follow: top 3⅞",

lock 9", bottom 11⅝". Knob centre 3'-2¼" above the floor.

# Both widths take the identical rails and mouldings, so

only the panel width changes — here 1'-10⅛" per panel.

# Solid teak frame. Veneer and polish per

Materials; polish to match the teak desk.

# Casing: 2 in lining plus 4 in moulding over it, so the

moulding head sits 6" above the leaf.

See AST-DR-011 (option A) and AST-DR-012 (option B).

# Notes

# AST-DR-009 · 4 of 7

# SECTION B–B

# SCALE 1:4 (3" = 1'-0") @ A4 · HORIZONTAL THROUGH UPPER PANELS

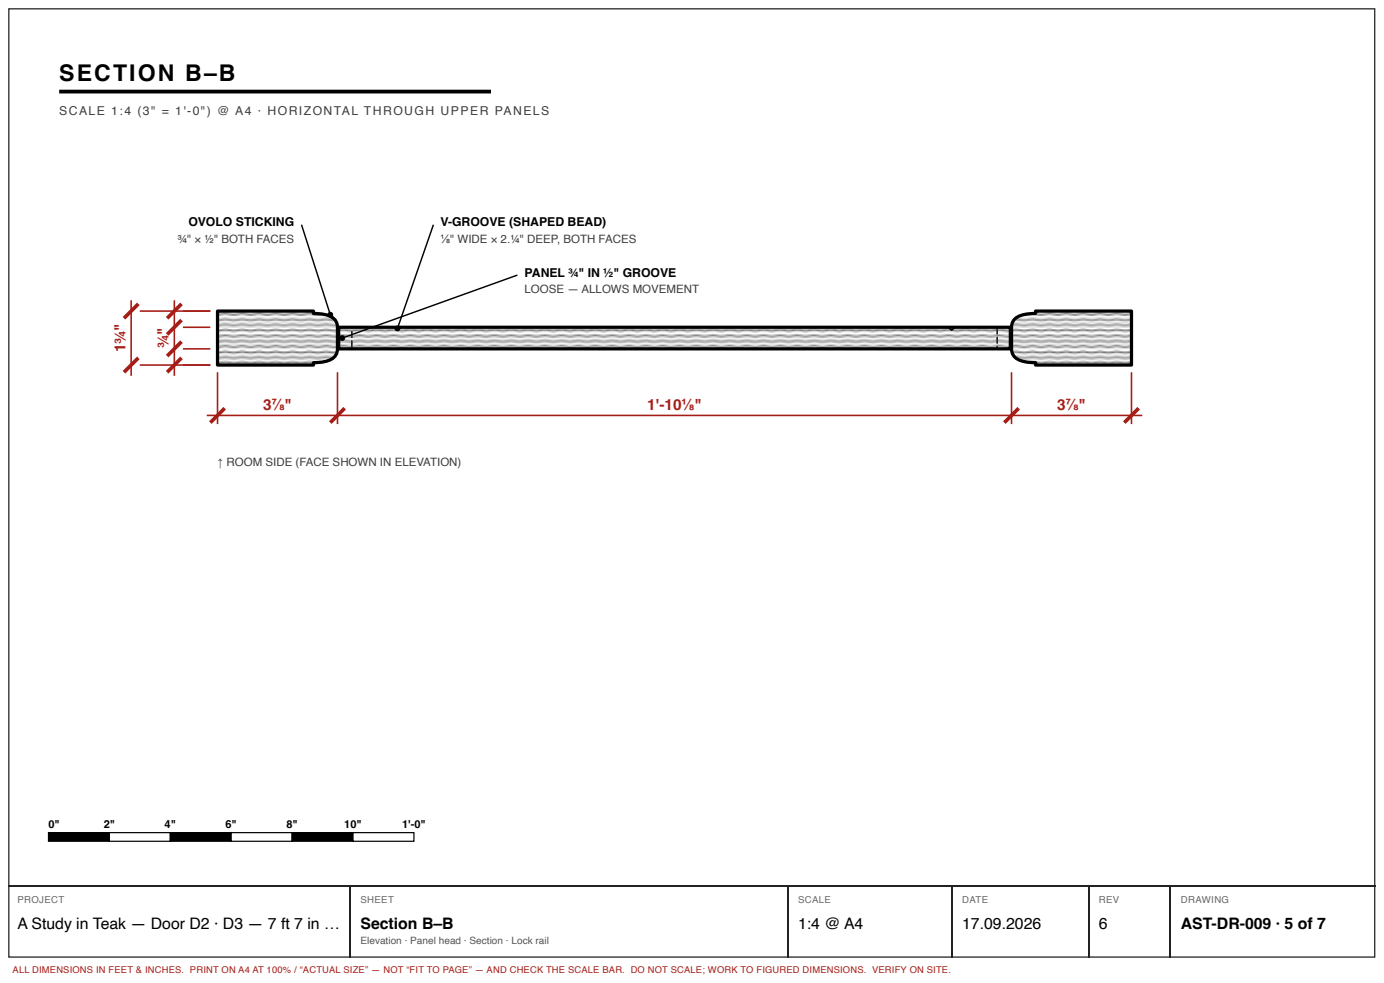
[picture p329: page 5]
OVOLO STICKING ¾" × ½" BOTH FACES; Section B–B

V-GROOVE (SHAPED BEAD)
⅛" WIDE × 2.¼" DEEP, BOTH FACES

PANEL ¾" IN ½" GROOVE
LOOSE — ALLOWS MOVEMENT

↑ ROOM SIDE (FACE SHOWN IN ELEVATION)

AST-DR-009 · 5 of 7

RELIEF | Hinges and lock not yet designed.

# FACE OF THE STILES AND RAILS = DATUM 0

Stiles and rails, 1¾" thick | DATUM 0
Ovolo sticking, ¾" wide | WORKED ON THE FRAME EDGE
Panel, ¾" thick, loose in a ½" groove | —
Panel field | ½" IN
Shaped bead line round the field | 2.5 IN
Roundel boss Ø1", four per panel | ⅛" OUT
Mitres at the sticking corners | CUT, NOT SCRIBED
Knob Ø2⅛" and escutcheon Ø1⅜" | SURFACE

# Relief

# AST-DR-009 · 6 of 7

# DETAIL C — LOCK RAIL

# SCALE 1:5 @ A4 · ACTIVE LEAF

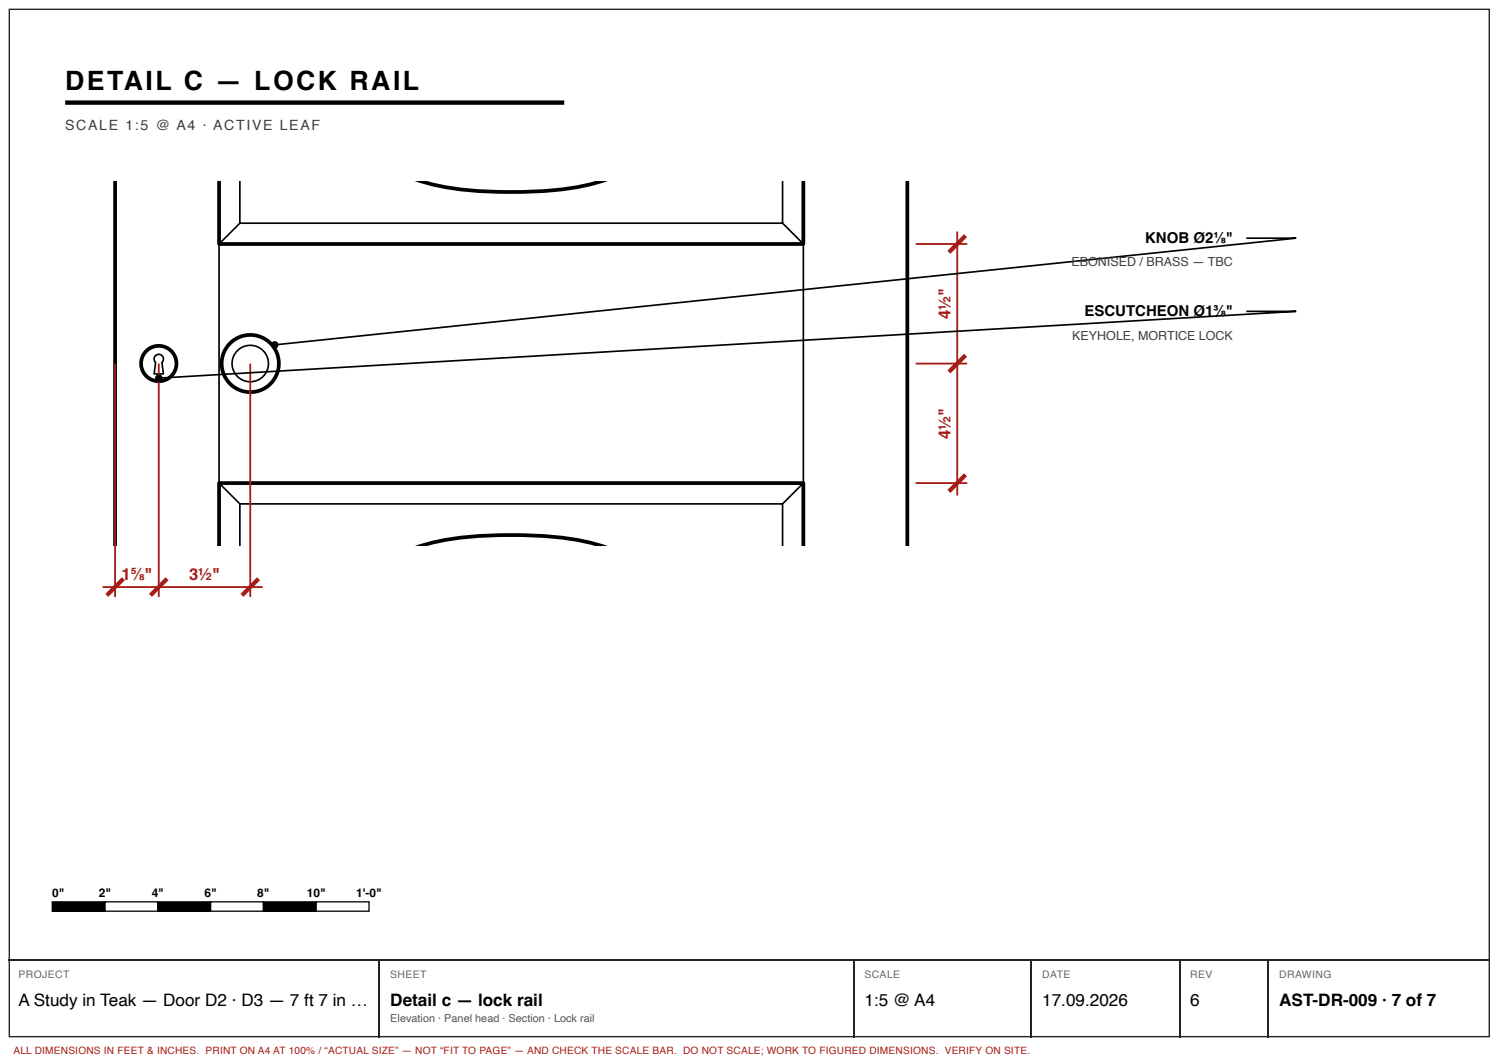
[picture p330: page 7]
KNOB Ø2⅛"; ESCUTCHEON Ø1⅜"

EBONISED / BRASS — TBC

KEYHOLE, MORTICE LOCK

Detail c — lock rail

AST-DR-009 · 7 of 7
