sakshampan733-cloud/a-study-in-teak/cad/print/doorveneer.pdf

D2 · D3

DRESSING AND BATHROOM · 2 FT 6 · AS AST-DR-009

D1

MAIN DOOR · 3 FT · AS AST-DR-001

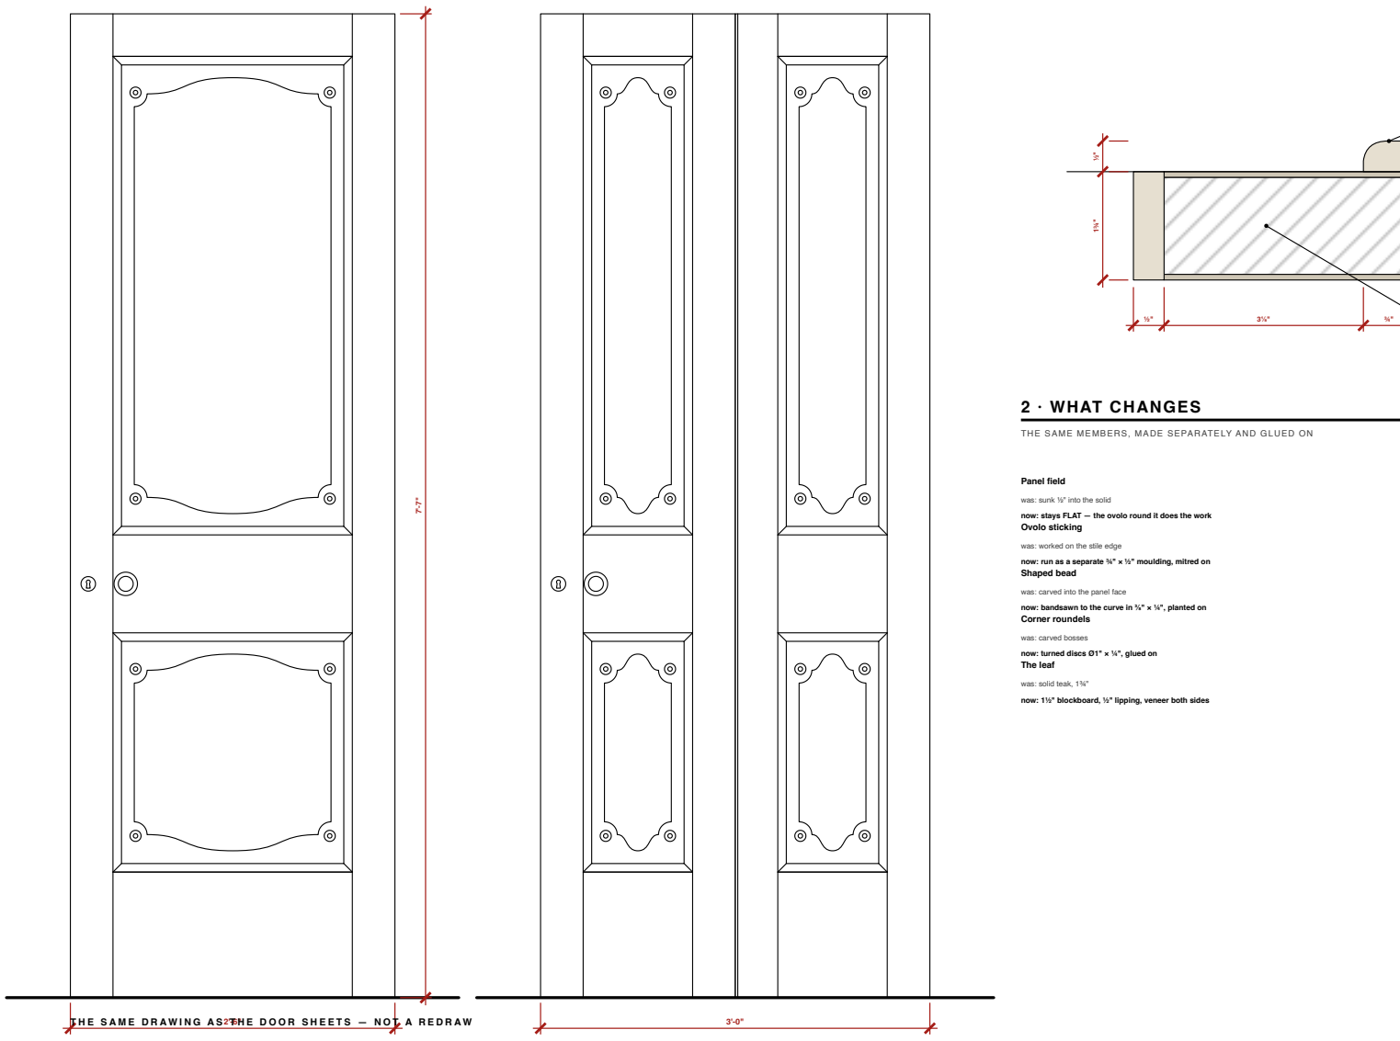
[picture p343: figure]
2 · WHAT CHANGES; Panel field; was: sunk ½" into the solid; Ovolo sticking; was: worked on the stile edge; Shaped bead; was: carved into the panel face; Corner roundels; was: carved bosses; now: turned discs Ø1" × ¼", glued on The leaf; was: solid teak, 1¾"

T H E S A M E D R AW I N G A S T H E D O O R S H E E T S — N O T A R E D R AW | 3'-0"

Both elevations are generated from the door sheets' own code, so the design cannot

drift. Nothing on this sheet changes how the door LOOKS — only how it is made.

# 1 · THROUGH THE LEAF

SECTION ACROSS A PANEL · EVERY MEMBER PLANTED ON

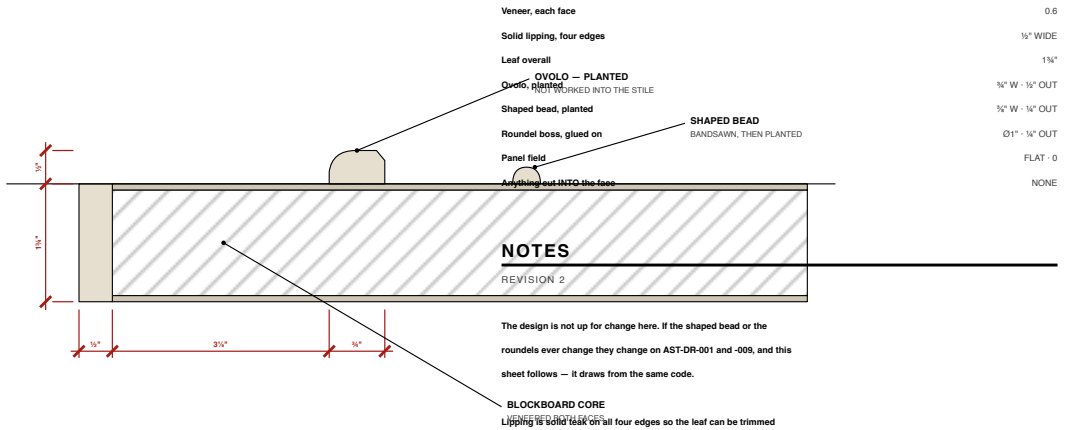
[picture p344: figure]
OVOLO — PLANTED; NOT WORKED INTO THE STILE; SHAPED BEAD; BANDSAWN, THEN PLANTED; BLOCKBOARD CORE; VENEERED BOTH FACES; Veneer, each face; Solid lipping, four edges; ½" WIDE; Leaf overall; Ovolo, planted; ¾" W · ½" OUT; Shaped bead, planted; ⅜" W · ¼" OUT; Roundel boss, glued on; Ø1" · ¼" OUT; Panel field; FLAT · 0; Anything cut INTO the face; NONE; NOTES; REVISION 2

THE SAME MEMBERS, MADE SEPARATELY AND GLUED ON

now: stays FLAT — the ovolo round it does the work

now: run as a separate ¾" × ½" moulding, mitred on

now: bandsawn to the curve in ⅜" × ¼", planted on

now: 1½" blockboard, ½" lipping, veneer both sides

# RELIEF

FACE OF THE VENEER = DATUM 0

Blockboard core | 1½"

The design is not up for change here. If the shaped bead or the

roundels ever change they change on AST-DR-001 and -009, and this

sheet follows — it draws from the same code.

Lipping is solid teak on all four edges so the leaf can be trimmed

on site and the hinges and lock screw into wood, not into board.

Veneer both faces of the core and balance it: same thickness back

and front, or the leaf will bow.

Ovolo, bead and bosses in solid teak, polished to match. They are

small enough to take solid without moving, and they give a crisper

arris than a cut face would.

Set the bead out from the panel opening, not from the leaf edge, so

the four roundels land exactly on the corners of the curve.

OPEN — glue and pin, or glue only? Pins need filling and the filler

shows through polish. Glue and cramp if the shop can.

# A S T U D Y I N T E A K

Particulars of the room

# DOORS — MADE IN VENEER

### Same design · Planted mouldings · Construction only

SCALE

### AS NOTED @ A3

DATE
23.09.2026

REV

2 — the design unchanged; only the construction differs

DWG

### AST-DR-015

# PROJECT

# A Study in Teak — Doors — Made in Veneer

# SHEET

# General arrangement — the whole sheet

# each view follows at its own scale, pages 2 to 5

# SCALE

# NTS

# DATE

23.09.2026

# REV

# DRAWING

# AST-DR-015 · 1 of 5

ALL DIMENSIONS IN FEET & INCHES. PRINT ON A3 AT 100% / “ACTUAL SIZE” — NOT “FIT TO PAGE” — AND CHECK THE SCALE BAR. DO NOT SCALE; WORK TO FIGURED DIMENSIONS. VERIFY ON SITE.

# 1 · THROUGH THE LEAF

# SCALE 1:1 (FULL SIZE) @ A3 · SECTION ACROSS A PANEL · EVERY MEMBER PLANTED ON

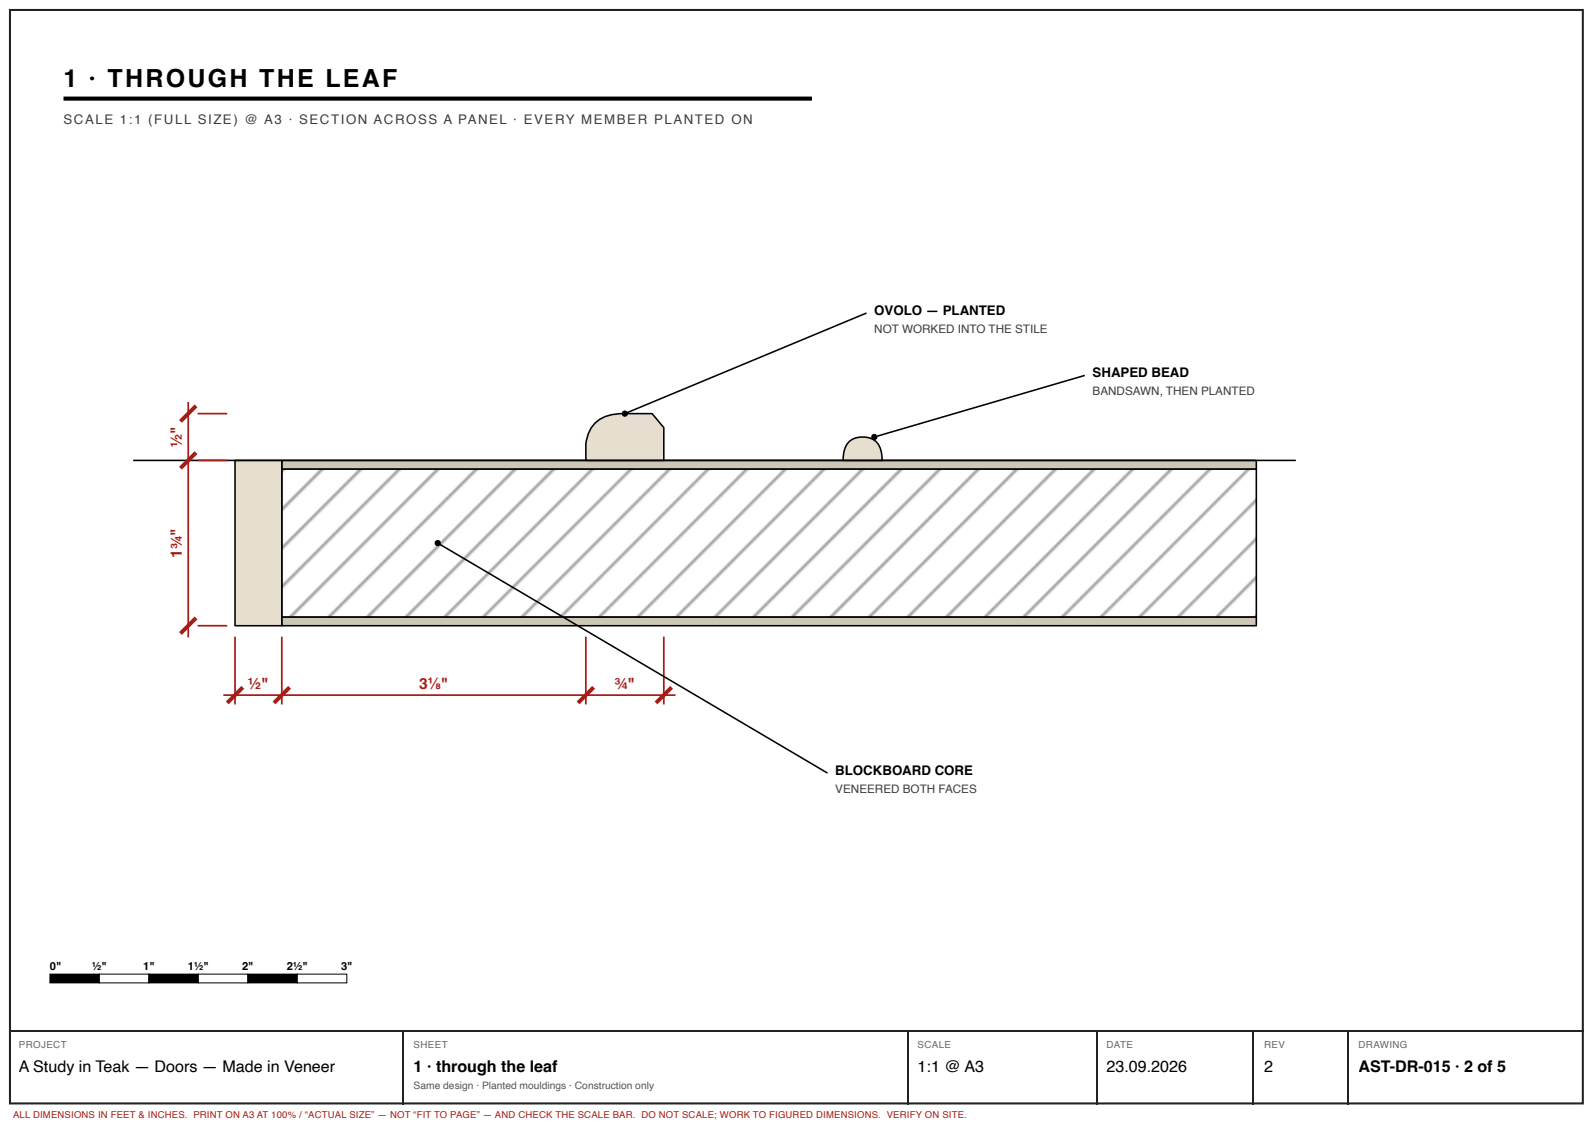
[picture p345: page 2]

OVOLO — PLANTED
NOT WORKED INTO THE STILE

SHAPED BEAD
BANDSAWN, THEN PLANTED

BLOCKBOARD CORE
VENEERED BOTH FACES

1 · through the leaf

AST-DR-015 · 2 of 5

Same design · Planted mouldings · Construction only

# RELIEF

# FACE OF THE VENEER = DATUM 0

Blockboard core | 1½"
Veneer, each face | 0.6
Solid lipping, four edges | ½" WIDE
Leaf overall | 1¾"
Ovolo, planted | ¾" W · ½" OUT
Shaped bead, planted | ⅜" W · ¼" OUT
Roundel boss, glued on | Ø1" · ¼" OUT
Panel field | FLAT · 0
Anything cut INTO the face | NONE

# Relief

# AST-DR-015 · 3 of 5

# NOTES

# REVISION 2

# The design is not up for change here. If the shaped bead or the

# roundels ever change they change on AST-DR-001 and -009, and this

sheet follows — it draws from the same code.

# Lipping is solid teak on all four edges so the leaf can be trimmed

# Veneer both faces of the core and balance it: same thickness back

and front, or the leaf will bow.

# Ovolo, bead and bosses in solid teak, polished to match. They are

# small enough to take solid without moving, and they give a crisper

arris than a cut face would.

# Set the bead out from the panel opening, not from the leaf edge, so

the four roundels land exactly on the corners of the curve.

# OPEN — glue and pin, or glue only? Pins need filling and the filler

shows through polish. Glue and cramp if the shop can.

# Notes

# AST-DR-015 · 4 of 5

# 2 · WHAT CHANGES

# THE SAME MEMBERS, MADE SEPARATELY AND GLUED ON

# Panel field

# was: sunk ½" into the solid

# now: stays FLAT — the ovolo round it does the work

# Ovolo sticking

# was: worked on the stile edge

# now: run as a separate ¾" × ½" moulding, mitred on

# Shaped bead

# was: carved into the panel face

# now: bandsawn to the curve in ⅜" × ¼", planted on

# Corner roundels

# was: carved bosses

# now: turned discs Ø1" × ¼", glued on

# The leaf

# was: solid teak, 1¾"

# now: 1½" blockboard, ½" lipping, veneer both sides

# on site and the hinges and lock screw into wood, not into board

# 2 · what changes

# AST-DR-015 · 5 of 5
