sakshampan733-cloud/a-study-in-teak/cad/print/leftwall-a4.pdf

# ELEVATION — LEFT WALL

SEEN FROM THE ROOM · STUDY CORNER LEFT, BED CORNER RIGHT

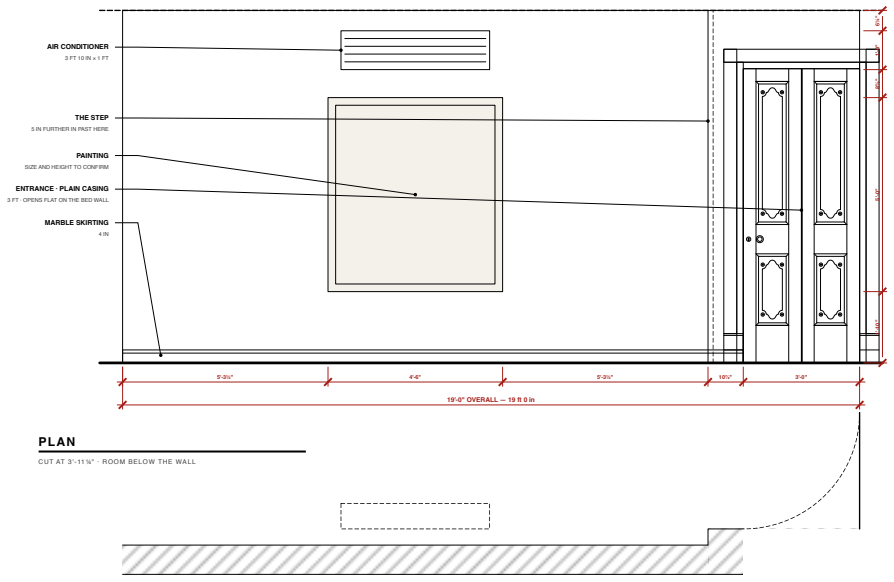
[picture p346: figure]
19'-0" OVERALL — 19 ft 0 in; AIR CONDITIONER; THE STEP; 5 IN FURTHER IN PAST HERE; PAINTING; SIZE AND HEIGHT TO CONFIRM; ENTRANCE · PLAIN CASING; 3 FT · OPENS FLAT ON THE BED WALL; MARBLE SKIRTING; PLAN; CUT AT 3'-11¼" · ROOM BELOW THE WALL

# NOTES

REVISION 5

This wall stays plain. Paint, the marble skirting, one painting and the

air conditioner over it — nothing is built into it and nothing is panelled.

It is the quiet side of the room, opposite the panelled right wall, and it

is the wall that carries the splay and the step, so anything fitted to it

would have to be scribed twice.

The painting is centred on the 15 ft 1⅛ in of wall before the step, the only

uninterrupted run. Centre line 7 ft 6½ in from the study corner, 1 ft 10 in off the floor.

OPEN — the painting is drawn 4 ft 6 in × 5 ft 0 in, centred at 4 ft 4 in.

Still assumed. Send the real size and it is a one-line change.

Sized to the wall it has: 8⅝ in clear under the air conditioner, and

8 in wider than the unit, so the AC sits within its width.

The air conditioner is 3 ft 10 in × 1 ft 0 in — MEASURED. Its depth (7⅞ in)

and its height off the ceiling (6¼ in) are still assumed.

The AC needs a power point and a drain run before the wall is painted —

decide the side the pipework leaves on.

The entrance takes the PLAIN casing: same 2 in lining and 4 in moulding as

every opening, running straight across the head and stopping. The carved

head on AST-DR-011 is the DRESSING door's alone.

OPEN — the profile of that 4 in plain band is not settled. Drawn flat.

# A S T U D Y I N T E A K

### Particulars of the room

# LEFT WALL

### Elevation · Plan · The plain wall

SCALE

1:30 @ A3

DATE

23.09.2026

REV

5 — the painting widened to 4 ft 6 in

DWG

### AST-DR-014

# PROJECT

# A Study in Teak — Left Wall

# SHEET

# General arrangement — the whole sheet

# each view follows at its own scale, pages 2 to 4

# SCALE

# NTS

# DATE

23.09.2026

# REV

# DRAWING

# AST-DR-014 · 1 of 4

ALL DIMENSIONS IN FEET & INCHES. PRINT ON A4 AT 100% / “ACTUAL SIZE” — NOT “FIT TO PAGE” — AND CHECK THE SCALE BAR. DO NOT SCALE; WORK TO FIGURED DIMENSIONS. VERIFY ON SITE.

# ELEVATION — LEFT WALL

# SCALE 1:30 @ A4 · SEEN FROM THE ROOM · STUDY CORNER LEFT, BED CORNER RIGHT

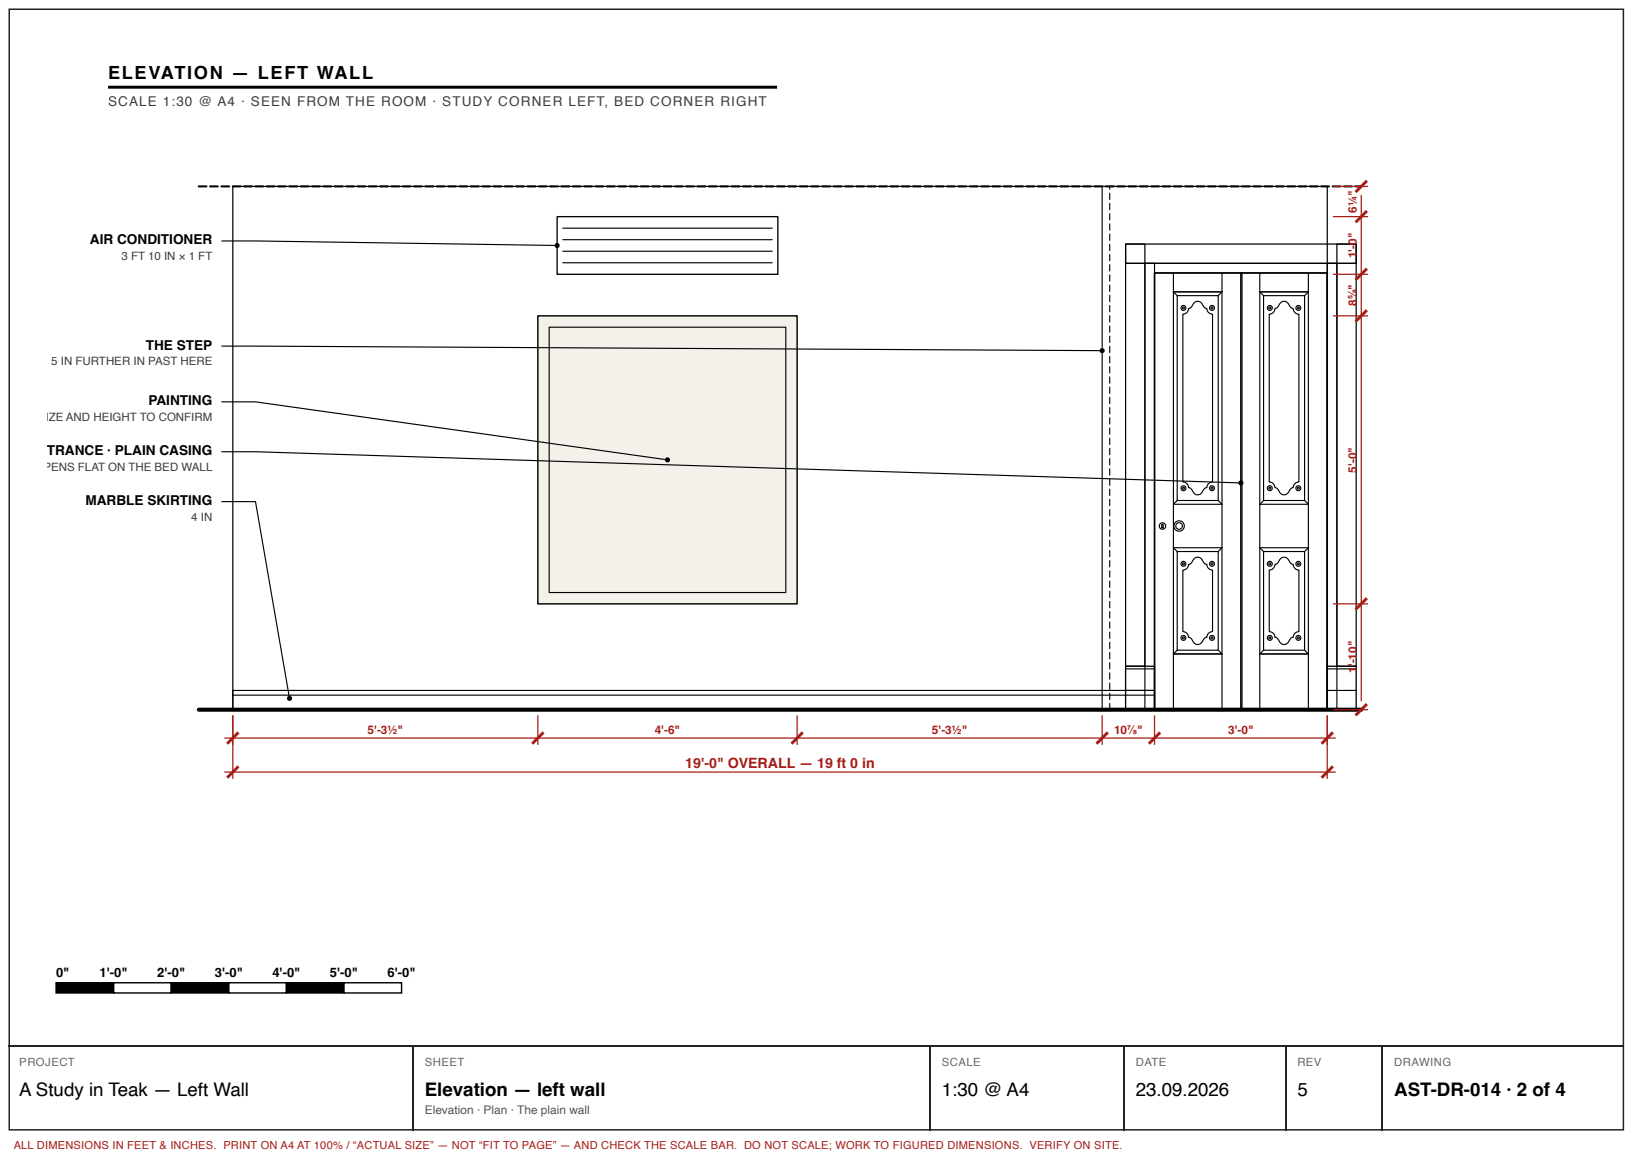
[picture p347: page 2]
THE STEP; PAINTING; MARBLE SKIRTING

AIR CONDITIONER

5 IN FURTHER IN PAST HERE

IZE AND HEIGHT TO CONFIRM

TRANCE · PLAIN CASING
PENS FLAT ON THE BED WALL

19'-0" OVERALL — 19 ft 0 in

Elevation — left wall

AST-DR-014 · 2 of 4

Elevation · Plan · The plain wall

# PLAN

# SCALE 1:25 @ A4 · CUT AT 3'-11¼" · ROOM BELOW THE WALL

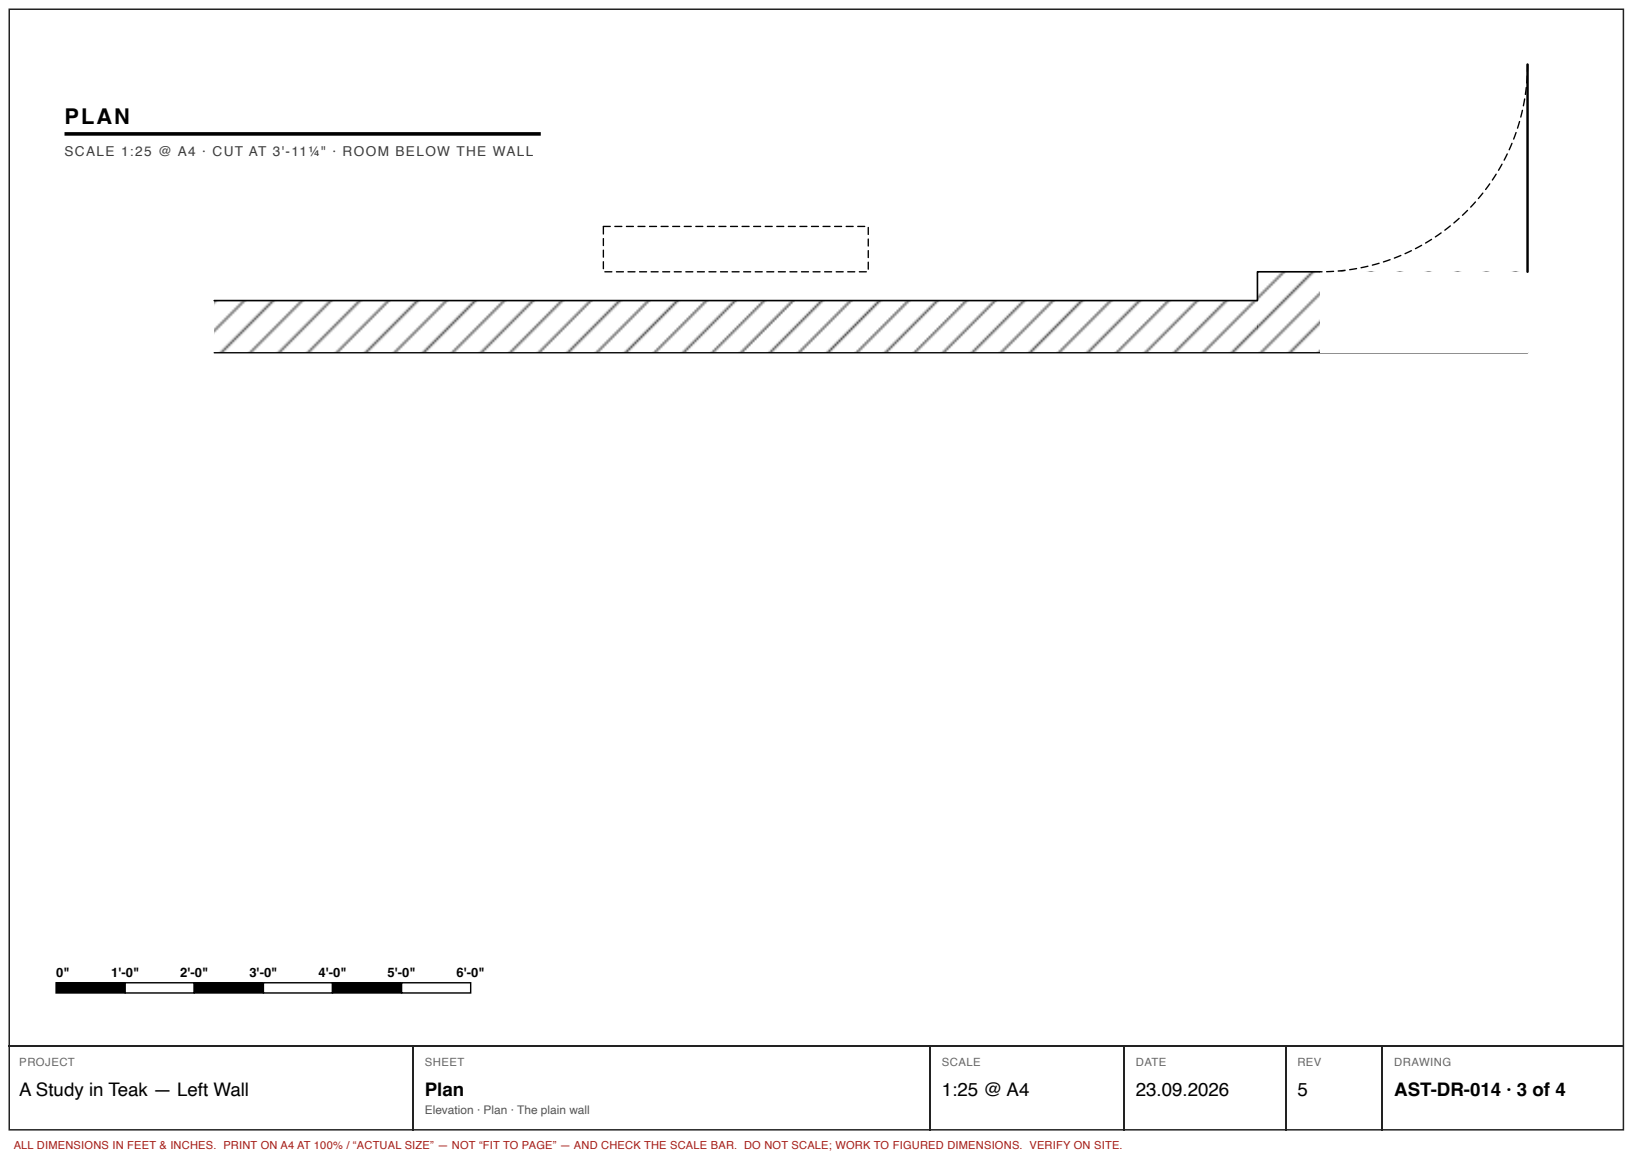
[picture p348: page 3]
Plan

AST-DR-014 · 3 of 4

# NOTES

# REVISION 5

# This wall stays plain. Paint, the marble skirting, one painting and the

air conditioner over it — nothing is built into it and nothing is panelled.

# It is the quiet side of the room, opposite the panelled right wall, and it

# is the wall that carries the splay and the step, so anything fitted to it

would have to be scribed twice.

# The painting is centred on the 15 ft 1⅛ in of wall before the step, the only

uninterrupted run. Centre line 7 ft 6½ in from the study corner, 1 ft 10 in off the floor.

OPEN — the painting is drawn 4 ft 6 in × 5 ft 0 in, centred at 4 ft 4 in.

Still assumed. Send the real size and it is a one-line change.

# Sized to the wall it has: 8⅝ in clear under the air conditioner, and

8 in wider than the unit, so the AC sits within its width.

# The air conditioner is 3 ft 10 in × 1 ft 0 in — MEASURED. Its depth (7⅞ in)

and its height off the ceiling (6¼ in) are still assumed.

# The AC needs a power point and a drain run before the wall is painted —

decide the side the pipework leaves on.

# The entrance takes the PLAIN casing: same 2 in lining and 4 in moulding a

# every opening, running straight across the head and stopping. The carved

head on AST-DR-011 is the DRESSING door's alone.

OPEN — the profile of that 4 in plain band is not settled. Drawn flat.

# Notes

# NTS

# AST-DR-014 · 4 of 4
