sakshampan733-cloud/a-study-in-teak/cad/print/mirror-a4.pdf

# DRESSING MIRROR — TRIFOLD

CONFIRMED · CENTRE GLASS 2 ft 0 in · WINGS AS WIDE AS THE 3 FT 6 IN ALLOWS · 45° · WHOLE FRAME INSIDE 3 FT 6 IN

## PLAN — FROM ABOVE

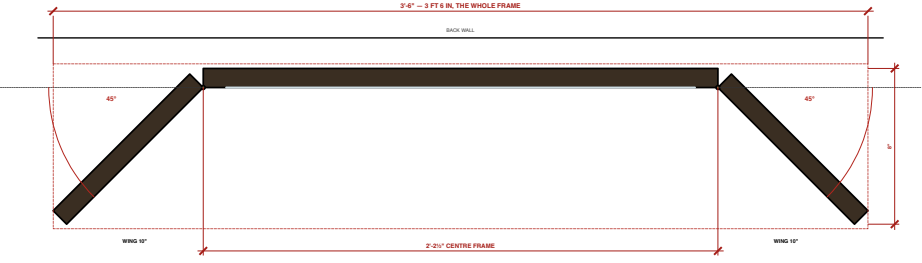
[picture p352: figure]
BACK WALL; 2'-2½" CENTRE FRAME; WING 10"

3'-6" — 3 FT 6 IN, THE WHOLE FRAME

## FRONT VIEW

3'-6" — 3 FT 6 IN

9'-0" — 9 FT

| FRAME | GLASS
Centre | 2 ft 2½ in | 2 ft 0 in
Each wing | 10 in | 7½ in
Height | 9 ft 0 in | 8 ft 9½ in
Wings | 45° forward, fixed stop
Whole frame across | 3 ft 6 in
Stands off the wall | 8 in
Floor either side | 7½ in

# NOTES

CONFIRMED

CONFIRMED by the owner: wings at 45°, and the whole frame — wings angled — inside 3 ft 6 in across

(the red dashed box). All three panels 9 ft tall, level with the wardrobes.

FINAL: centre glass 2 ft 0 in; the wings take everything the 3 ft 6 in frame has left at 45° —

about 7½ in of glass each. Only two things would give bigger wings: a slimmer frame (¾ in

frame → about 9¼ in), or a steeper angle (60° → about 11¼ in).

The wings need a fixed stop at 45°. Opened any flatter, the frame gets wider than 3 ft 6 in.

Hinges: two continuous piano hinges on the back, one at each joint, in the frame finish.

Free-standing, centred on the far wall. 7½ in of floor either side, clear of the folding

end-bay doors, which come out only about 3 in at this depth. Frame finish still open.

# A S T U D Y I N T E A K

### Particulars of the room

# DRESSING MIRROR

### Trifold · confirmed

SCALE

### 1:5 AND 1:25 @ A3

DATE

26.09.2026

REV

5 — FINAL: centre glass 2 ft 0 in, wings at 45°

DWG

### AST-DR-027

# PROJECT

# A Study in Teak — Dressing Mirror

# SHEET

# General arrangement — the whole sheet

# each view follows at its own scale, pages 2 to 3

# SCALE

# NTS

# DATE

26.09.2026

# REV

# DRAWING

# AST-DR-027 · 1 of 3

ALL DIMENSIONS IN FEET & INCHES. PRINT ON A4 AT 100% / “ACTUAL SIZE” — NOT “FIT TO PAGE” — AND CHECK THE SCALE BAR. DO NOT SCALE; WORK TO FIGURED DIMENSIONS. VERIFY ON SITE.

# DRESSING MIRROR — TRIFOLD

CONFIRMED · CENTRE GLASS 2 ft 0 in · WINGS AS WIDE AS THE 3 FT 6 IN ALLOWS · 45° · WHOLE FRAME INSIDE 3 FT 6 IN

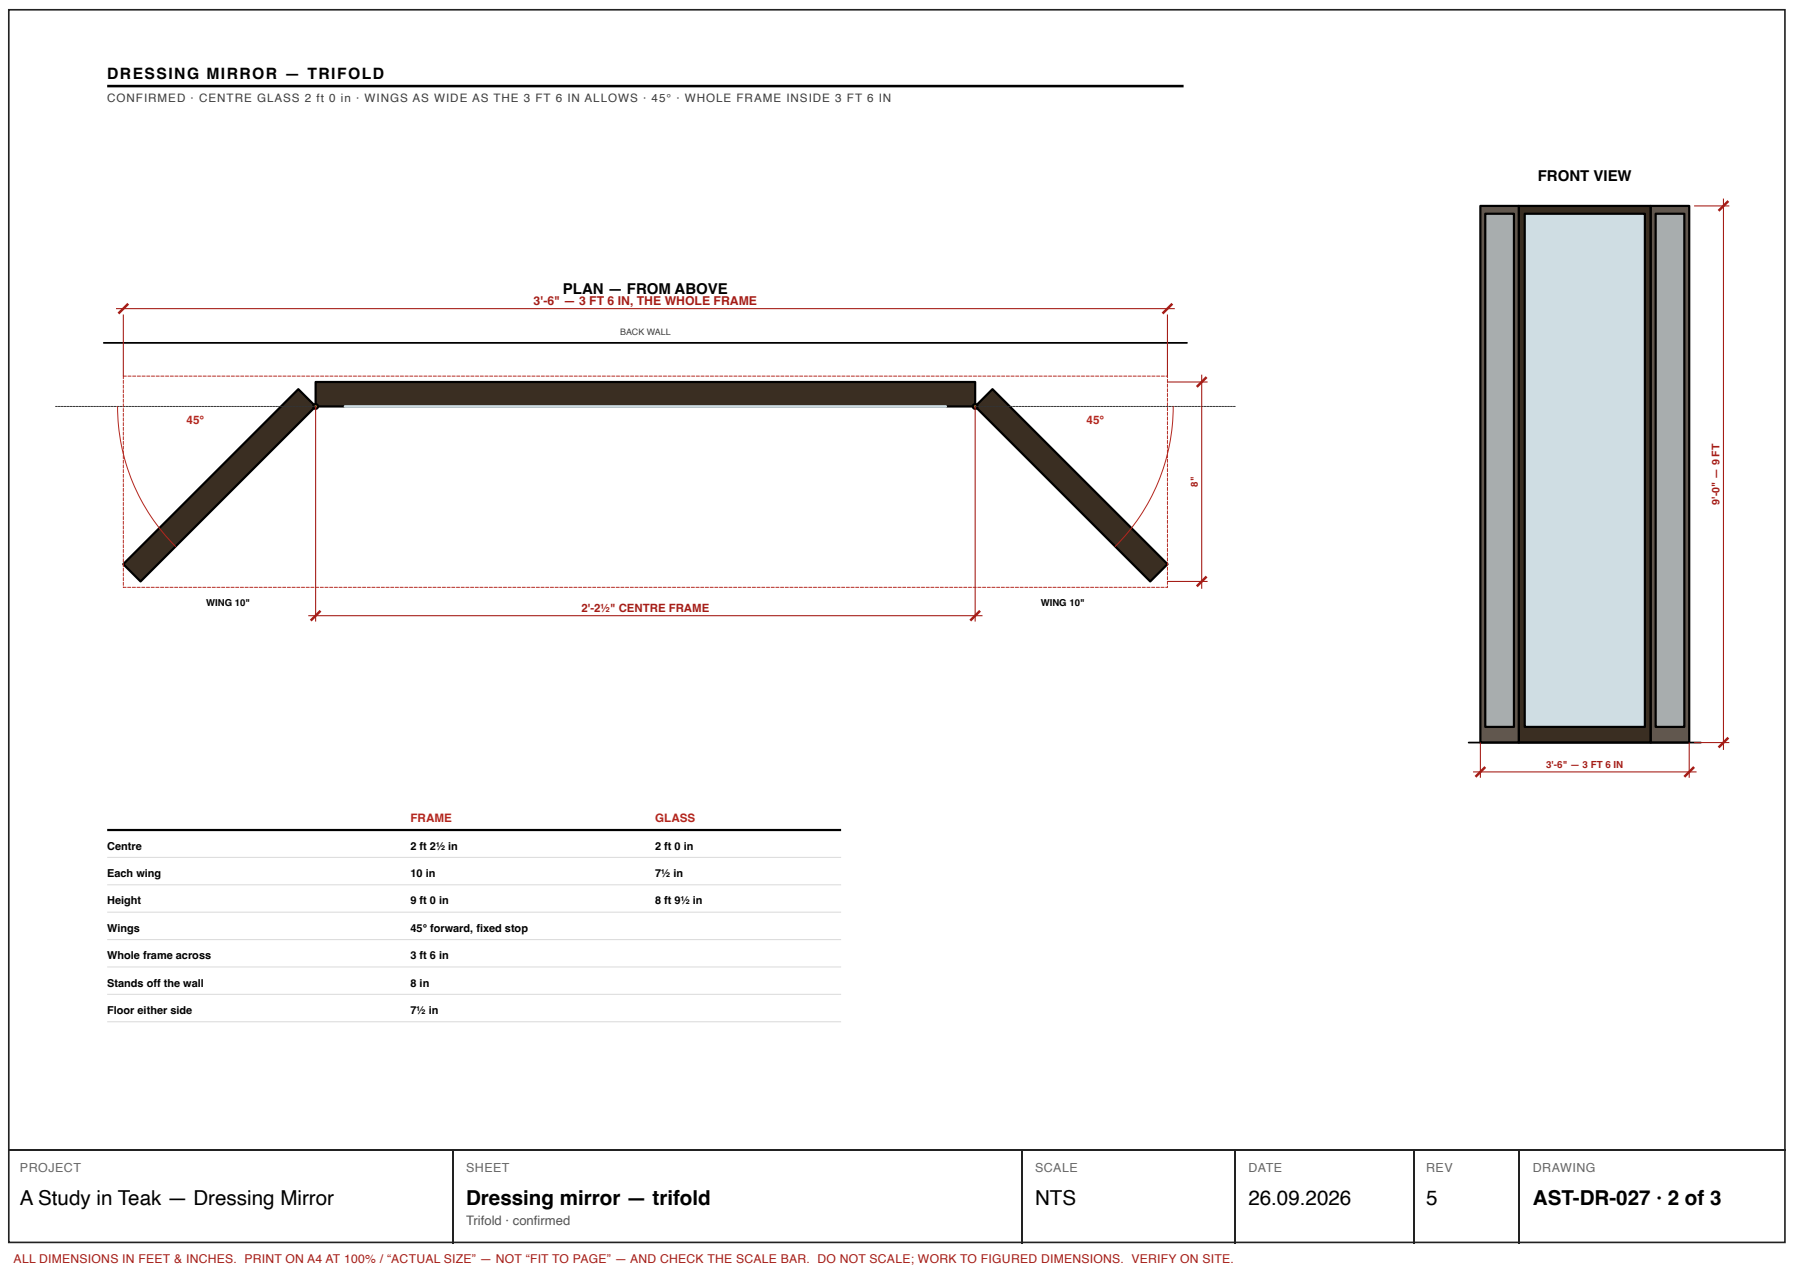
[picture p353: page 2]
BACK WALL; 2'-2½" CENTRE FRAME; WING 10"; FRONT VIEW; FRAME; GLASS; Centre; Each wing; Height; Wings; 45° forward, fixed stop; Whole frame across; Stands off the wall; Floor either side; Trifold · confirmed

PLAN — FROM ABOVE
3'-6" — 3 FT 6 IN, THE WHOLE FRAME

Dressing mirror — trifold

AST-DR-027 · 2 of 3

# NOTES

# CONFIRMED

CONFIRMED by the owner: wings at 45°, and the whole frame — wings angled — inside 3 ft 6 in across

(the red dashed box). All three panels 9 ft tall, level with the wardrobes.

FINAL: centre glass 2 ft 0 in; the wings take everything the 3 ft 6 in frame has left at 45° —

# about 7½ in of glass each. Only two things would give bigger wings: a slimmer frame (¾ in

frame → about 9¼ in), or a steeper angle (60° → about 11¼ in).

# The wings need a fixed stop at 45°. Opened any flatter, the frame

# Hinges: two continuous piano hinges on the back, one at each jo

Free-standing, centred on the far wall. 7½ in of floor either side,

# end-bay doors, which come out only about 3 in at this depth. Fra

# Notes

# Trifold · confirmed

# AST-DR-027 · 3 of 3
