sakshampan733-cloud/a-study-in-teak/cad/print/rightwall-a4.pdf

ELEVATION — RIGHT WALL; 13'-3" PANELLED; 2'-3" DOOR; CEILING; COVE LIGHT ABOVE; TALL PANEL ×6; WALL COLOUR; WALL LAMP ×4; PANELS 1, 3, 5 AND THE RETURN; RAIL = STUDY COUNTER; SAME 2'-1⅜"–2'-3" BAND; STUDY CUPBOARDS; END, 11" DEEP; SHORT PANEL ×6; SKIRTING; PLAN; CUT AT 3'-3⅜" · ROOM BELOW, WALL ABOVE; DRESSING DOOR 2′6″ × 7′7″; INWARD, HINGED RIGHT; LAMP ABOVE, 9" OFF THE WALL; SECTION A–A; THROUGH PANEL 1; 4'-2¾" TO LAMP CENTRE; CEILING COVE LIGHT; NOTHING FIXED AT THE TOP; PANEL MOULDING; DET. 1; WALL LAMP; DET. 4; RAIL; DET. 2; MARBLE SKIRTING; 4 IN · LAID; NOTES; REVISION 18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

SEEN FROM THE ROOM · STUDY WALL ON THE LEFT · OPTION C

18'-11" OVERALL · STUDY WALL CORNER TO THE DRESSING CORNER

Option C: 5 equal panels, lamps in 1, 3, 5 and the return.

One narrow panel on the wall past the door.

Moulding, rail and skirting painted the wall colour.

SELECTED after four schemes: the rail is the study counter

band carried round the corner, and it dies into the casing.

Skirting is white marble, 4 in, already laid.

Casing 2 in lining + 4 in moulding = 6 in, 3'-6" overall;

crown at 8 ft 8 in, and the tall panels stop on that

### 2 ft 4 in corner to frame, measured both sides; leaf 2 ft 3

in a 2 in frame. OPEN: that puts the frame 14 ft 0 from the
1 · PANEL MOULDING | study corner, 6 in off the taped 13 ft 6. Retape that end.
W | ¾" HITE MARBLE, ALREADY LAID · SQUARE WITH A SMALL TOP CHAMFER

18 — SELECTED: the rail at 2 ft 3 in, carrying the study counter round

PROJECT

# A Study in Teak — Right Wall — Panel Mou…

SHEET

# General arrangement — the whole sheet

each view follows at its own scale, pages 2 to 9

SCALE

# NTS

DATE
20.09.2026

REV

DRAWING

# AST-DR-007 · 1 of 9

ALL DIMENSIONS IN FEET & INCHES. PRINT ON A4 AT 100% / “ACTUAL SIZE” — NOT “FIT TO PAGE” — AND CHECK THE SCALE BAR. DO NOT SCALE; WORK TO FIGURED DIMENSIONS. VERIFY ON SITE.

## ELEVATION — RIGHT WALL

13'-3" PANELLED; 2'-3" DOOR; DRESSING; CEILING; TALL PANEL ×6 WALL COLOUR; WALL LAMP ×4; SAME 2'-1⅜"–2'-3" BAND; STUDY CUPBOARDS END, 11" DEEP; SHORT PANEL ×6; SKIRTING

SCALE 1:30 @ A4 · SEEN FROM THE ROOM · STUDY WALL ON THE LEFT · OPTION C

COVE LIGHT ABOVE

PANELS 1, 3, 5 AND THE RETURN

RAIL = STUDY COUNTER

18'-11" OVERALL · STUDY WALL CORNER TO THE DRESSING CORNER

Elevation — right wall

AST-DR-007 · 2 of 9

Elevation · Plan · Section · Details

## SECTION A–A

PANEL MOULDING; DET. 1; WALL LAMP; DET. 4; RAIL DET. 2; MARBLE SKIRTING 4 IN · LAID; Section A–A

SCALE 1:24 (½" = 1'-0") @ A4 · THROUGH PANEL 1

CEILING COVE LIG
NOTHING FIXED AT THE

4'-2¾" TO LAMP CENTRE

AST-DR-007 · 3 of 9

## PLAN

DRESSING DOOR 2′6″ × 7′7″; STUDY CUPBOARDS; Plan

SCALE 1:30 @ A4 · CUT AT 3'-3⅜" · ROOM BELOW, WALL ABOVE

INWARD, HINGED RIGHT

LAMP ABOVE, 9" OFF THE WALL

AST-DR-007 · 4 of 9

# NOTES

# REVISION 18

Option C: 5 equal panels, lamps in 1, 3, 5 and the return.

One narrow panel on the wall past the door.

Moulding, rail and skirting painted the wall colour.

# SELECTED after four schemes: the rail is the study counter

band carried round the corner, and it dies into the casing.

Skirting is white marble, 4 in, already laid.

Casing 2 in lining + 4 in moulding = 6 in, 3'-6" overall;

# crown at 8 ft 8 in, and the tall panels stop on that

line, not the leaf head at 7 ft 7 in.

# 2 ft 4 in corner to frame, measured both sides; leaf 2 ft 3

# in a 2 in frame. OPEN: that puts the frame 14 ft 0 from the

study corner, 6 in off the taped 13 ft 6. Retape that end.

# Notes

# NTS

# AST-DR-007 · 5 of 9

## 1 · PANEL MOULDING

1 · panel moulding

SCALE 1:1 (FULL SIZE) @ A4 · SECTION

WALL FACE BELOW · MITRED CORNERS

AST-DR-007 · 6 of 9

# 2 · RAIL

# SCALE 1:1 (FULL SIZE) @ A4 · SECT

2 · rail

MATCHES THE COUNTER EDGE

AST-DR-007 · 7 of 9

# 3 · SKIRTING

# SCALE 1:2 (6" = 1'-0") @ A4 · MARBLE · SECTION

¾" HITE MARBLE, ALREADY LAID · SQUARE WITH A SMALL TOP CHAMFER; 3 · skirting

AST-DR-007 · 8 of 9

# 4 · WA LL L A M P

# SCALE 1:4 (3" = 1'-0") @ A4 · ELEVATION · ×4

4 · wall lamp

BRASS, FABRIC SHADES · CENTRED IN PANEL

AST-DR-007 · 9 of 9
