sakshampan733-cloud/a-study-in-teak/cad/print/roomshell-a4.pdf

# THE ROOM AS BUILT

PLAN · SHELL ONLY, NO FURNITURE · CEILING 9'-1" LEVEL THROUGHOUT

### 14'-11" — STUDY WALL

# NOTES

REVISION 6

The room is not square. It widens about 2 in from the

4'-0" WINDOW; 15'-6" — BED WALL; 5" STEP; 14'-2" 2'-3" DOOR 2'-6"; 18'-11" — RIGHT WALL; 19'-0" — LEFT WALL; 15'-0" — AT THE PARTITION LINE; WINDOW; HARD INTO THE CORNER — NO RETURN; RIGHT WALL; PANELLING AND THE DRESSING DOOR; PARTITION LINE; SHELL REFERENCE ONLY · TO CONFIRM; DRESSING DOOR; 2 FT 6 × 8 FT · OPENS IN, HINGED RIGHT; BED WALL; PARCHMENT; THE STEP; KICKS OUT PAST THE DOOR · TO CONFIRM; ENTRANCE · 3 FT; OPENS FLAT ON THE BED WALL

study wall to the bed wall — roughly half a degree.

Diagonals measured 24 ft 5 in and 23 ft 11 in.

Right wall — 13 ft 6 in to the door frame and 18 ft 11 in

overall are drawn exactly; the 3 ft frame and 2 ft 4 in

return do not both fit with a 2 in lining. See AST-DR-007.

The right wall is taken as the straight reference; the left

wall carries the splay and the step.

Ceiling 9 ft 1 in, level throughout. The main room ceiling

is plain, so the splay never shows from above.

Floor, marble border and skirting are laid. Skirting runs

on three walls only: bed, left and right.

Every fitted piece to be built ⅝"–¾" undersize and scribed

on site to the wall it actually meets.

Furniture, partition and joinery are NOT shown.

Bathroom and dressing lie beyond the right wall — to come.

# A S T U D Y I N T E A K

### Particulars of the room

# THE ROOM AS BUILT

### Shell plan · measured on site

SCALE

1:40 @ A3

DATE

19.09.2026

REV

6 — the partition line at 11 ft from the bed wall, 8 ft from the study wall

DWG

### AST-DR-000

# PROJECT

# A Study in Teak — The Room As Built

# SHEET

# General arrangement — the whole sheet

# each view follows at its own scale, pages 2 to 3

# SCALE

# NTS

# DATE

19.09.2026

# REV

# DRAWING

# AST-DR-000 · 1 of 3

ALL DIMENSIONS IN FEET & INCHES. PRINT ON A4 AT 100% / “ACTUAL SIZE” — NOT “FIT TO PAGE” — AND CHECK THE SCALE BAR. DO NOT SCALE; WORK TO FIGURED DIMENSIONS. VERIFY ON SITE.

# THE ROOM AS BUILT

# SCALE 1:60 @ A4 · PLAN · SHELL ONLY, NO FURNITURE · CEILING 9'-1" LEVEL THROUGHOUT

4'-0" WINDOW; 14'-11" — STUDY WALL; 15'-6" — BED WALL; 5" STEP; 14'-2" 2'-3" DOOR 2'-6"; 18'-11" — RIGHT WALL; 19'-0" — LEFT WALL; BED WALL; PARCHMENT; THE STEP; ENTRANCE · 3 FT

WINDOW
HARD INTO THE CORNER — NO

RIGHT WALL
PANELLING AND THE DRESSING

15'-0" — AT THE PARTITION LINE

PARTITION LINE
SHELL REFERENCE ONLY · TO C

T PAST THE DOOR · TO CONFIRM

DRESSING DOOR
2 FT 6 × 8 FT · OPENS IN, HINGED

OPENS FLAT ON THE BED WALL

The room as built

AST-DR-000 · 2 of 3

Shell plan · measured on site

# NOTES

# REVISION 6

# The room is not square. It widens about 2 in from the

study wall to the bed wall — roughly half a degree.

Diagonals measured 24 ft 5 in and 23 ft 11 in.

# Right wall — 13 ft 6 in to the door frame and 18 ft 11 in

# overall are drawn exactly; the 3 ft frame and 2 ft 4 in

return do not both fit with a 2 in lining. See AST-DR-007.

# The right wall is taken as the straight reference; the left

wall carries the splay and the step.

# Ceiling 9 ft 1 in, level throughout. The main room ceiling

is plain, so the splay never shows from above.

# Floor, marble border and skirting are laid. Skirting runs

on three walls only: bed, left and right.

# Every fitted piece to be built ⅝"–¾" undersize and scribed

on site to the wall it actually meets.

Furniture, partition and joinery are NOT shown.

Bathroom and dressing lie beyond the right wall — to come.

# Notes

# Shell plan · measured on site

# NTS

# AST-DR-000 · 3 of 3
