sakshampan733-cloud/a-study-in-teak/cad/print/studywall-a4.pdf

ELEVATION — STUDY WALL

BOOKCASE · PANEL FOR PAINTING · WINDOW

PLAN

14'-11" WALL; 9'-1" CEILING; BAND PANELS; SAME SIZE WHERE THEY FIT; FLAT HEAD, NO ARCH; STRIP LIGHT UNDER RAIL; TWIN SCONCE ×2; ON THE PILASTERS — REF. 3; REEDED TOP; MATCHES THE DESK; CUPBOARDS, ALL 3 BAYS; TOP LEVEL WITH THE WINDOW SILL; MODILLION BLOCKS + DENTILS; REF. 2 — NO LEAF CARVING; MOULDED CAPITAL; NO CARVING — REF. 1; FLUTED PILASTER ×2; ON A PANELLED PEDESTAL — REF. 1; MOULDED PANEL; PAINTING OPTIONAL — REF. 1; PEDESTAL STEPS FORWARD; COUNTER WRAPS IT — REF. 3

CUT AT 3'-11¼" · ROOM BELOW, WALL ABOVE

11" 2"

WINDOW 4'-0" WIDE

HARD INTO THE CORNER — NO RETURN ON THE RIGHT

SECTION A–A

THROUGH BOOKCASE

CROWN

MODILLION

COUNTER

10" DEEP + 1"

11"

0"

NOTES

REVISION 9

Wall 14 ft 11 in, ceiling 9 ft 1 in (measured).

Centre panel set equal to the window bay so the two

pilasters frame a matched pair; the bookcase takes

the remainder as the anchor at the end of the wall.

Window measured: 4 ft wide, 5 ft 5 in tall, hard into

the right corner. Sill 2 ft 3 in — CONFIRMED.

OPEN: sill 2 ft 3 + height 5 ft 5 + your 1 ft 3 to the

ceiling makes 8 ft 11, two inches short of the 9 ft 1

ceiling. Sill and height are drawn as measured, so the

head falls 1 ft 5 down, not 1 ft 3. Laser it.

Counter top is set to the sill at 2'-3", so the two are

one surface; this datum runs on round to the right

wall rail.

Cupboards under all three bays. Gold on handles only.

A S T U D Y I N T E A K

Particulars of the room

STUDY WALL — GENERAL ARRANGEMENT

Elevation · Plan · Section

SCALE

AS NOTED @ A3

DATE

19.09.2026

REV

9 — sill datum confirmed at 686

DWG

AST-DR-005

PROJECT

# A Study in Teak — Study Wall — General A…

SHEET

# General arrangement — the whole sheet

each view follows at its own scale, pages 2 to 5

SCALE

# NTS

DATE
19.09.2026

REV

DRAWING

# AST-DR-005 · 1 of 14

ALL DIMENSIONS IN FEET & INCHES. PRINT ON A4 AT 100% / “ACTUAL SIZE” — NOT “FIT TO PAGE” — AND CHECK THE SCALE BAR. DO NOT SCALE; WORK TO FIGURED DIMENSIONS. VERIFY ON SITE.

## ELEVATION — STUDY WALL

14'-11" WALL; BAND PANELS; TWIN SCONCE ×2

SCALE 1:30 @ A4 · BOOKCASE · PANEL FOR PAINTING · WINDOW

MODILLION BLOCKS + D
REF. 2 — NO LEAF CARVING

MOULDED CAPITAL
NO CARVING — REF. 1

SAME SIZE WHERE THEY FIT

FLAT HEAD, NO ARCH
STRIP LIGHT UNDER RAIL

9'-1" CEILING
FLUTED PILASTER ×2
ON A PANELLED PEDESTAL —

ON THE PILASTERS — REF. 3

MOULDED PANEL
PAINTING OPTIONAL — REF. 1

REEDED TOP
MATCHES THE DESK

PEDESTAL STEPS FORW
COUNTER WRAPS IT — REF. 3

CUPBOARDS, ALL 3 BAYS
TOP LEVEL WITH THE WINDOW SILL

A Study in Teak — Study Wall — General A…

Elevation — study wall

AST-DR-005 · 2 of 14

Elevation · Plan · Section

# SECTION A–A

### SCALE 1:24 (½" = 1'-0") @ A4 · THROUGH BOOKCASE

CROWN; MODILLION; COUNTER 10" DEEP + 1; Section A–A

A Study in Teak — Study Wall — General A…

AST-DR-005 · 3 of 14

Elevation · Plan · Section

# PLAN

### SCALE 1:24 (½" = 1'-0") @ A4 · CUT AT 3'-11¼" · ROOM BELOW, WALL ABOVE

Plan

WINDOW 4'-0" WIDE
HARD INTO THE CORNER — NO RETURN ON THE

A Study in Teak — Study Wall — General A…

AST-DR-005 · 4 of 14

Elevation · Plan · Section

# NOTES

# REVISION 9

Wall 14 ft 11 in, ceiling 9 ft 1 in (measured).

# Centre panel set equal to the window bay so the two

# pilasters frame a matched pair; the bookcase takes

the remainder as the anchor at the end of the wall.

# Window measured: 4 ft wide, 5 ft 5 in tall, hard into

the right corner. Sill 2 ft 3 in — CONFIRMED.

# OPEN: sill 2 ft 3 + height 5 ft 5 + your 1 ft 3 to the

# ceiling makes 8 ft 11, two inches short of the 9 ft 1

# ceiling. Sill and height are drawn as measured, so the

head falls 1 ft 5 down, not 1 ft 3. Laser it.

# Counter top is set to the sill at 2'-3", so the two are

# one surface; this datum runs on round to the right

wall rail.

Cupboards under all three bays. Gold on handles only.

# A Study in Teak — Study Wall — General A…

# Notes

Elevation · Plan · Section

# NTS

# AST-DR-005 · 5 of 14

1 · PILASTER; ABACUS; OVOLO; NECK; ASTRAGAL; 9 STOPPED FLUTES; ROUNDED ENDS; MOULDED BASE; COUNTER CAP; PEDESTAL, 2" FORWARD; 2 · PILASTER SECTION; PLAN; FILLET 7; 3 · CORNICE; SECTION; CYMA CROWN; DENTIL; MODILLION; ARCHITRAVE; STEPPED; 4 · MODILLION + DENTILS; FRONT · PLAIN; 4⅛" CENTRES; NO CARVING; DENTILS ⅝" × 1¼"; ½" GAP; 5 · PAINTING PANEL; PROUD 1"; PANEL FRAME; RAISED FIELD; BAND PANEL; 7 · COUNTER EDGE; 4 REEDS × 8; CUPBOARD DOOR ⅞"; NOTES; DETAILS; SCALE; AS NOTED @ A3; DATE; REV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

CAPITAL AND BASE · ELEVATION · REF. 1

FACE OF CASE

FLUTE ⅝" WIDE, HALF-ROUND

BOLECTION MOULDING · SECTION

ON THE COUNTER

PLAIN BLOCK, SUNK PANEL

WRAPS THE PEDESTAL

1" WIDER EACH SIDE

BOLECTION — LAPS FRAME AND FIELD

SECTION · SAME REEDS AS THE DESK

6 · BAND PANEL + SCONCE

ELEVATION · SAME PANEL OVER EVERY BAY

No carving on pilasters or modillions — mouldings only.

Flute and modillion spacing to be set out on site

so they finish symmetrically on the wall.

Mock up profiles 3, 5 and 7 full size before cutting.

1'-3¾" HIGH, EVERY BAY

AS DESK TOP

Particulars of the room

RAISED PANEL, BRASS DROP HANDLE

STUDY WALL — DETAILS

Pilaster · Cornice · Modillion · Panel · Band · Counter

TWIN SCONCE
BRASS, FABRIC SHADES

9 — sill datum confirmed at 686

A Study in Teak — Study Wall — Details

General arrangement — the whole sheet

AST-DR-006 · 6 of 14

each view follows at its own scale, pages 7 to 14

## 1 · PILASTER

ABACUS; OVOLO; NECK; ASTRAGAL; 9 STOPPED FLUTES ROUNDED ENDS; 1 · pilaster

SCALE 1:6 (2" = 1'-0") @ A4 · CAPITAL AND BASE · ELEVATION · REF. 1

MOULDED BASE
ON THE COUNTER

COUNTER CAP
WRAPS THE PEDESTAL

PEDESTAL, 2" FORW
1" WIDER EACH SIDE

AST-DR-006 · 7 of 14

Pilaster · Cornice · Modillion · Panel · Band · Counter

## 2 · PILASTER SECTION

9½"

SCALE 1:2 (6" = 1'-0") @ A4 · PLAN; 2 · pilaster section

FACE OF CASE

FLUTE ⅝" WIDE, HALF-ROUND
FILLET 7

AST-DR-006 · 8 of 14

# 3 · CORNICE

### SCALE 1:4 (3" = 1'-0") @ A4 · SECTION

CYMA CROWN; DENTIL; MODILLION; ARCHITRAVE STEPPED; 3 · cornice

AST-DR-006 · 9 of 14

# 4 · MODILLION + DENTILS

# SCALE 1:1 (FULL SIZE) @ A4 · FRONT · PLAIN

4⅛" CENTRES; DENTILS ⅝" × 1¼"; ½" GAP; 4 · modillion + dentils

PLAIN BLOCK, SUNK PANEL
NO CARVING

AST-DR-006 · 10 of 14

# 5 · PAINTING PANEL

# SCALE 1:1 (FULL SIZE) @ A4 · BOLECTION MOULDING · SECTION

PANEL FRAME; RAISED FIELD; 5 · painting panel

BOLECTION — LAPS FRAME AND FIELD
PROUD 1"

AST-DR-006 · 11 of 14

# 6 · BAND PANEL + SCONCE

## SCALE 1:15 @ A4 · ELEVATION · SAME PANEL OVER EVERY BAY


BAND PANEL
1'-3¾" HIGH, EVERY BAY

TWIN SCONCE
BRASS, FABRIC SHADES

6 · band panel + sconce

AST-DR-006 · 12 of 14

## 7 · COUNTER EDGE

7 · counter edge

SCALE 1:2 (6" = 1'-0") @ A4 · SECTION · SAME REEDS AS THE DESK

4 REEDS × 8
AS DESK TOP

CUPBOARD DOOR ⅞"
RAISED PANEL, BRASS DROP

AST-DR-006 · 13 of 14

# N O T E S

# DETAILS

No carving on pilasters or modillions — mouldings only.

# Flute and modillion spacing to be set out on site

so they finish symmetrically on the wall.

Mock up profiles 3, 5 and 7 full size before cutting.

# Notes

# NTS

# AST-DR-006 · 14 of 14
