sakshampan733-cloud/a-study-in-teak/cad/print/wardrobes-a4.pdf

# DRESSING ROOM — THE WARDROBES

DEVELOPED ELEVATION · THE THREE WALLS UNFOLDED, LEFT TO RIGHT AS YOU WALK IN

L E F T WA L L | B A C K WA L L | R I G H T WA L L
BATHROOM DOOR, THEN 3 BAYS | THE MIRROR, BACK TO THE WALL | 4 BAYS — THE FAR ONE IS THE TUNNEL

7½" CLEAR; RUN END; 9'-4" — 3 BAYS; 3'-6" MIRROR; 12'-4" — 4 BAYS, ONE OF THEM THE TUNNEL; 1'-10" TRANSOM 7'-2" DOOR; 9'-1" CEILING; TRANSOM BAND; OPENS — SO IT STORES; D3 · BATHROOM DOOR; 3 FT ZONE · LEAF NOT YET FIXED; THE MIRROR; THE HIDDEN DOOR; BAY T · SAME DOORS · SHELVED BEHIND; BRASS BAR PULL; ON EVERY LEAF

### K EY PL A N

MIRROR AT THE TOP · FREE-STANDING

BAYS | DOOR S BELOW | DOOR S ABOVE | BAY WI D T H
LEFT WALL | 3 | 6 | 6 | 3'-1⅜"
RIGHT WALL | 4 | 8 | 8 | 3'-1"
— of which tunnel | 1 | 2 | — | the far bay, right
TOTAL | 7 | ½" | ½" | 1⅛" leaves in all

### W H AT T H AT C O M ES TO

9 FT TALL · FREE-STANDING · NOT FIXED EITHER SIDE

# NOTES

REVISION 1

Depth 2 ft 3 in, as instructed. On the right that is what lets the run reach the bedroom wall: the

door frame stands 2 ft 4 in off that corner, so the end of the run clears it by 1 in.

Bays are the wall divided equally, so nothing is left over and there are no filler strips: the right

wall is 12 ft 4 in over 4 bays, the left is 9 ft 4 in over 3. Both come out at about 3 ft 1 in —

an inch over the 3 ft you asked for, which is what makes them land exactly.

Each bay is a pair of doors with a pair of transom lights over, all glazed and all opening — so the

transom is storage, not just a band of glass. 7 bays, ½" cupboards, 1⅛" leaves.

Doors as the Wardrobes brief: blackened steel T-section, 1½" face, white textured glass in linear

lead came, lit from inside, brass bar pulls, transom bar 1'-10" down from the top.

SETTLED — the mirror is a trifold, 3 ft 6 in across with its wings at 45°, free-standing and fixed

to neither run. Centred in the 4 ft 9 in gap it leaves 7½ in of floor either side, and it is 9 ft tall —

level with the top of the wardrobes. That narrow gap is why the two end bays cannot hinge open

in the ordinary way — see AST-DR-026 for the fold-slide doors that solve it.

OPEN — D3, the bathroom door. 3 ft of wall is left for it, but the leaf is still not fixed. It is

drawn as an opening only.

OPEN — the tunnel bay reads as one more cupboard, but it is a door onto a passage, so the

transom over it cannot be storage in the ordinary way. Decide whether it is a dummy.

OPEN — 4 ft 9 in is what you are left standing in once both runs are built. Open one 1 ft 6 in

leaf and there is still 3 ft 3 in. Workable, not generous — worth feeling on site first.

# A S T U D Y I N T E A K

### Particulars of the room

# THE WARDROBES

### Dressing room · developed elevation

SCALE

1:40 @ A3

DATE

25.09.2026

REV

1 — first setting out of the bays, off the owner's 2 ft 3 in depth and 3 ft bay

DWG

### AST-DR-025

# PROJECT

# A Study in Teak — The Wardrobes

# SHEET

# General arrangement — the whole sheet

# each view follows at its own scale, pages 2 to 2

# SCALE

# NTS

# DATE

25.09.2026

# REV

1

# DRAWING

# AST-DR-025 · 1 of 2

ALL DIMENSIONS IN FEET & INCHES. PRINT ON A4 AT 100% / “ACTUAL SIZE” — NOT “FIT TO PAGE” — AND CHECK THE SCALE BAR. DO NOT SCALE; WORK TO FIGURED DIMENSIONS. VERIFY ON SITE.

# NOTES

# REVISION 1

Depth 2 ft 3 in, as instructed. On the right that is what lets the run reach the bedroom wall: the

door frame stands 2 ft 4 in off that corner, so the end of the run clears it by 1 in.

Bays are the wall divided equally, so nothing is left over and there are no filler strips: the right

wall is 12 ft 4 in over 4 bays, the left is 9 ft 4 in over 3. Both come out at about 3 ft 1 in —

an inch over the 3 ft you asked for, which is what makes them land exactly.

Each bay is a pair of doors with a pair of transom lights over, all glazed and all opening — so the

transom is storage, not just a band of glass. 7 bays, ½" cupboards, 1⅛" leaves.

Doors as the Wardrobes brief: blackened steel T-section, 1½" face, white textured glass in linear

lead came, lit from inside, brass bar pulls, transom bar 1'-10" down from the top.

# SETTLED — the mirror is a trifold, 3 ft 6 in across with its wings at 45

# to neither run. Centred in the 4 ft 9 in gap it leaves 7½ in of floor eithe

# level with the top of the wardrobes. That narrow gap is why the two e

# in the ordinary way — see AST-DR-026 for the fold-slide doors that s

# OPEN — D3, the bathroom door. 3 ft of wall is left for it, but the leaf is

drawn as an opening only.

# OPEN — the tunnel bay reads as one more cupboard, but it is a door

# transom over it cannot be storage in the ordinary way. Decide wheth

# OPEN — 4 ft 9 in is what you are left standing in once both runs are b

# leaf and there is still 3 ft 3 in. Workable, not generous — worth feelin

# PROJECT

# A Study in Teak — The Wardrobes

# SHEET

# Notes

# Dressing room · developed elevation

# SCALE

# NTS

# DATE

25.09.2026

# REV

1

# DRAWING

# AST-DR-025 · 2 of 2

ALL DIMENSIONS IN FEET & INCHES. PRINT ON A4 AT 100% / “ACTUAL SIZE” — NOT “FIT TO PAGE” — AND CHECK THE SCALE BAR. DO NOT SCALE; WORK TO FIGURED DIMENSIONS. VERIFY ON SITE.
