sakshampan733-cloud/a-study-in-teak/cad/print/dressingshell.pdf

# DRESSING ROOM — SHELL AND LAYOUT

PLAN · COPIED FROM THE OWNER'S SKETCH — NOT YET A SITE MEASUREMENT

9'-3" — ROOM WIDTH; 7'-8" TUNNEL LONG; 2'-3" D2 LEAF; 2'-6" TO THE CORNER; 9'-3" — BEDROOM WALL; 9'-4" WALL 3'-0" D3 + RETURN; 12'-4" — LEFT AND RIGHT WALL; 3'-0" TUNNEL WIDE; THE TUNNEL; 3 FT WIDE · 7 FT 8 IN LONG · RUNS EAST; HIDDEN DOOR; WARDROBE — RIGHT WALL; SAME BAYS · RUNS THE FULL 12 FT 4 IN; DRESSING MIRROR; TRIFOLD · 3 FT 6 IN · WINGS AT 45°; WARDROBE — LEFT WALL; 3 FT 1 IN BAYS · 2 FT 3 IN DEEP; D3 · BATHROOM DOOR; IN THE LEFT WALL · SWINGS OUT; D2 · DRESSING DOOR; IN FROM THE BEDROOM · SWINGS IN

2'-4" CORNER TO THE FRAME — MEASURED

LAST BAY AT THE FAR END · PUSH IT AND IT OPENS

# NOTES

REVISION 3

Third pass, and this one copies the sketch rather than interpreting it. The two earlier drawings

both had the shape wrong; everything below is read straight off the owner's own clean drawing.

The BEDROOM wall is the bottom wall here, 9 ft 3 in, and it carries D2, the existing dressing

door in from the bedroom, 2 ft 4 in from the right-hand corner to the door FRAME — measured

on both sides of the wall, and the figure that now governs. The sketch's 2 ft 0 in is superseded.

The BATHROOM door, D3, is in the LEFT wall, at the bedroom end — not in the bedroom wall. The

sketch runs 9 ft 4 in of wall down from the far corner and then opens the door.

The TUNNEL runs EAST, straight out of the far end of the right wall, 3 ft wide and 7 ft 8 in long,

its far side flush with the far wall. The hidden door is the last wardrobe bay in front of it:

built and shelved like every other bay, so from the room it reads as one more cupboard.

Ceiling 9 ft 1 in, plain, over the left and right sides — the same height as the main room. A

domed centre rises to 10 ft 0 in, so the wardrobes are capped at 9 ft 0 in, clear under it.

SETTLED — D2 sits 2 ft 4 in from the corner to its frame, on both sides of the wall. That closes

this sheet against AST-DR-000 and AST-DR-007: this room's right-hand corner and the bedroom's

bed-wall corner are the same corner. Walls are taken at 9 in throughout. See AST-DR-024.

OPEN — D3's width. It is drawn 2 ft 6 in, as the owner said, but the sketch's own 9 ft 4 in against

12 ft 4 in leaves 3 ft 0 in — so a 6 in return is shown into the corner. To confirm.

SETTLED — the wardrobes are 2 ft 3 in deep, so the right-hand run reaches the bedroom wall and

clears D2's frame, 2 ft 4 in off that corner, by 1 in.

OPEN — the left run is drawn stopping at D3. Whether it ends there or returns over the door

is not decided.

OPEN — where the tunnel leads, and what is at its far end.

OPEN — the dome's own shape: how far along the room it runs, and its profile.

The mirror is the confirmed trifold, 3 ft 6 in across with its wings at 45° — see AST-DR-027.

# A S T U D Y I N T E A K

Particulars of the room

# DRESSING ROOM

### Shell and layout · third pass

SCALE
1:35 @ A3

DATE
25.09.2026

REV

3 — drawn off the owner's clean sketch: bathroom door on the LEFT wall, dressing door on the bedroom wall, tunnel running east

DWG

### AST-DR-023

# PROJECT

# A Study in Teak — Dressing Room

# SHEET

# General arrangement — the whole sheet

# each view follows at its own scale, pages 2 to 3

# SCALE

# NTS

# DATE

25.09.2026

# REV

# DRAWING

# AST-DR-023 · 1 of 3

ALL DIMENSIONS IN FEET & INCHES. PRINT ON A3 AT 100% / “ACTUAL SIZE” — NOT “FIT TO PAGE” — AND CHECK THE SCALE BAR. DO NOT SCALE; WORK TO FIGURED DIMENSIONS. VERIFY ON SITE.

# DRESSING ROOM — SHELL AND LAYOUT

# SCALE 1:30 @ A3 · PLAN · COPIED FROM THE OWNER'S SKETCH — NOT YET A SITE MEASUREMENT

9'-3" — ROOM WIDTH; 7'-8" TUNNEL LONG; 9'-3" — BEDROOM WALL; 9'-4" WALL 3'-0" D3 + RETURN; 12'-4" — LEFT; RIG; WALL; 3'-0" TUN; NEL WIDE; DRESSING MIRROR; D2 · DRESSING DOOR

TRIFOLD · 3 FT 6 IN · WINGS AT 45°

THE TUNNEL
3 FT WIDE · 7 FT 8 IN LONG · RUNS EAST

HIDDEN DOOR
LAST BAY AT THE FAR END · PUSH IT AN

WARDROBE — LEFT WALL
3 FT 1 IN BAYS · 2 FT 3 IN DEEP

WARDROBE — RIGHT WALL
SAME BAYS · RUNS THE FULL 12 FT 4 IN

D3 · BATHROOM DOOR
IN THE LEFT WALL · SWINGS OUT

ROM THE BEDROOM · SWINGS IN

2'-3" D2 LEAF 2'-6" TO THE CORNER

2'-4" CORNER TO THE FRAME — MEASURED

Dressing room — shell and layout

AST-DR-023 · 2 of 3

Shell and layout · third pass

# NOTES

# REVISION 3

Third pass, and this one copies the sketch rather than interpreting it. The two earlier drawings

both had the shape wrong; everything below is read straight off the owner's own clean drawing.

The BEDROOM wall is the bottom wall here, 9 ft 3 in, and it carries D2, the existing dressing

door in from the bedroom, 2 ft 4 in from the right-hand corner to the door FRAME — measured

on both sides of the wall, and the figure that now governs. The sketch's 2 ft 0 in is superseded.

The BATHROOM door, D3, is in the LEFT wall, at the bedroom end — not in the bedroom wall. The

sketch runs 9 ft 4 in of wall down from the far corner and then opens the door.

The TUNNEL runs EAST, straight out of the far end of the right wall, 3 ft wide and 7 ft 8 in long,

its far side flush with the far wall. The hidden door is the last wardrobe bay in front of it:

built and shelved like every other bay, so from the room it reads as one more cupboard.

Ceiling 9 ft 1 in, plain, over the left and right sides — the same height as the main room. A

domed centre rises to 10 ft 0 in, so the wardrobes are capped at 9 ft 0 in, clear under it.

# SETTLED — D2 sits 2 ft 4 in from the corner to its frame, on both sides of the

# this sheet against AST-DR-000 and AST-DR-007: this room's right-hand corne

# bed-wall corner are the same corner. Walls are taken at 9 in throughout. See

# OPEN — D3's width. It is drawn 2 ft 6 in, as the owner said, but the sketch's o

# 12 ft 4 in leaves 3 ft 0 in — so a 6 in return is shown into the corner. To confi

# SETTLED — the wardrobes are 2 ft 3 in deep, so the right-hand run reaches t

clears D2's frame, 2 ft 4 in off that corner, by 1 in.

# OPEN — the left run is drawn stopping at D3. Whether it ends there or return

is not decided.

OPEN — where the tunnel leads, and what is at its far end.

# OPEN — the dome's own shape: how far along the room it runs, and its profi

# The mirror is the confirmed trifold, 3 ft 6 in across with its wings at 45° — se

# Notes

# Shell and layout · third pass

# NTS

# AST-DR-023 · 3 of 3
