sakshampan733-cloud/a-study-in-teak/cad/print/vanity-b-a4.pdf

FRONT

A 1 FT VENEER CUPBOARD LEFT · 4 FT OF MARBLE CENTRED ON THE FAUCET

SECTION A–A; ON THE FAUCET AXIS; 2'-0" DEEP; DETAIL 1 · THE MARBLE EDGE; SECTION; MARBLE SLAB ¾"; BWP PLY SUB-TOP ¾"; MITRED APRON, ¾" × 1½"; CARCASS TOP ¾"; TOP RAIL; FRONTS; WHAT; Door, cup pull; Top drawer, push-open; Big drawer, U-box, push-open; Inner drawer, finger scoop; MATERIALS; THE ROOM'S PALETTE — NOTHING NEW
4'-0" MARBLE; 5'-0" OVERALL; 2'-9" COUNTER 5"; FAUCET AXIS; PLAN; FROM ABOVE · WALL AT THE TOP

DETAIL 2 · THE BIG DRAWER

PLAN · INNER DRAWER DASHED

7⅞"

9⅜"

SIZES ARE THE FRONT ITSELF · ⅛" GAP ALL ROUND

Top | Beige-gold marble, the bathroom stone. ¾" slab
| on a ¾" BWP sub-top, mitred 1½" apron, polished.
Carcass | ¾" BWP / marine ply, teak veneer both faces.
| Every edge sealed — it stands in a wet room.
Fronts | ¾" BWP, teak veneer, ¼" solid teak lipping.
Ledge | The 1 ft veneer top: solid teak nosing,
| sealed like a worktop. Marble stops at the bank.
Runners | Undermount, full extension. Drawers push-to-open —
| no handles on them; the doors keep cup pulls.
Fittings | Chrome — already bought. Door cup pulls to match.
Hanging | ¾" ply cleat on the wall, 2'-3½"–2'-5⅞" high.
Inner | A U-box on its own runners, above the big
| drawer's low sides — see AST-DR-022.

SECTION KEY; Hanging cleat; Big drawer, U-box; Waste Ø1⅝" and P-trap; Support, set back 3"; Wall spout; Ply sub-top; NOTES; REVISION 1

G Inner drawer

Taking 1 ft off the left moves the marble's centre 6 in

right — onto the faucet. Bowl, drawer split and support

all sit on that one line. The top drawers split on it,

so the waste drops between them: only the big one is a U.

OPEN — bowl Ø1'-4" × 5" and the spout are assumed.

With the bowl on a 2'-9" counter its rim is at 3'-2".

OPEN — the support's design: reference photos to come.

A S T U D Y I N T E A K

Particulars of the room

VANITY — SCHEME B

1 ft cupboard left · 4 ft marble on the faucet

SCALE

AS NOTED @ A3

DATE

23.09.2026

REV

1 — as sketched

DWG

AST-DR-020

PROJECT

# A Study in Teak — Vanity — Scheme B

SHEET

# General arrangement — the whole sheet

each view follows at its own scale, pages 2 to 10

SCALE

# NTS

DATE
23.09.2026

REV

DRAWING

# AST-DR-020 · 1 of 10

ALL DIMENSIONS IN FEET & INCHES. PRINT ON A4 AT 100% / “ACTUAL SIZE” — NOT “FIT TO PAGE” — AND CHECK THE SCALE BAR. DO NOT SCALE; WORK TO FIGURED DIMENSIONS. VERIFY ON SITE.

## FRONT

4'-0" MARBLE; 5'-0" OVERALL; 2'-9" COUNTER 5"; FAUCET AXIS; Front

SCALE 1:10 @ A4 · A 1 FT VENEER CUPBOARD LEFT · 4 FT OF MARBLE CENTRED ON THE FAUCET

AST-DR-020 · 2 of 10

1 ft cupboard left · 4 ft marble on the faucet

## SECTION A–A

E

2'-0" DEEP; Section A–A

SCALE 1:10 @ A4 · ON THE FAUCET AXIS

AST-DR-020 · 3 of 10

# DETAIL 1 · THE MARBLE EDGE

# SCALE 1:1 (FULL SIZE) @ A4 · SECTION

MARBLE SLAB ¾"; MITRED APRON, ¾" × 1½"; CARCASS TOP ¾"; TOP RAIL

BWP PLY SUB-TOP ¾"

Detail 1 · the marble edge

AST-DR-020 · 4 of 10

# FRONTS

# SIZES ARE THE FRONT ITSELF · ⅛" GAP ALL ROUND

No. | WHAT | W × H | FT-IN
1 | Door, cup pull | 8¾" × 1'-10¼" | 8¾" × 1'-10¼"
2 | Top drawer, push-open | 1'-9¾" × 5¾" | 1'-9¾" × 5¾"
3 | Top drawer, push-open | 1'-9¾" × 5¾" | 1'-9¾" × 5¾"
4 | Big drawer, U-box, push-open | 3'-8¾" × 1'-3¼" | 3'-8¾" × 1'-3¼"
4a | Inner drawer, finger scoop | 3'-6⅝" × 3¾" | 3'-6⅝" × 3¾"

# Fronts

# AST-DR-020 · 5 of 10

# MATERIALS

# THE ROOM'S PALETTE — NOTHING NEW

Top | Beige-gold marble, the bathroom stone. ¾" slab
| on a ¾" BWP sub-top, mitred 1½" apron, polished.
Carcass | ¾" BWP / marine ply, teak veneer both faces.
| Every edge sealed — it stands in a wet room.
Fronts | ¾" BWP, teak veneer, ¼" solid teak lipping.
Ledge | The 1 ft veneer top: solid teak nosing,
| sealed like a worktop. Marble stops at the bank.
Runners | Undermount, full extension. Drawers push-to-open —
| no handles on them; the doors keep cup pulls.
Fittings | Chrome — already bought. Door cup pulls to match.
Hanging | ¾" ply cleat on the wall, 2'-3½"–2'-5⅞" high.
Inner | A U-box on its own runners, above the big
| drawer's low sides — see AST-DR-022.

# Materials

# AST-DR-020 · 6 of 10

# PLAN

### SCALE 1:8 (1½" = 1'-0") @ A4 · FROM ABOVE · WALL AT THE TOP

Plan

AST-DR-020 · 7 of 10

# DETAIL 2 · THE BIG DRAWER

## SCALE 1:8 (1½" = 1'-0") @ A4 · PLAN · INNER DRAWER DASHED


Detail 2 · the big drawer

AST-DR-020 · 8 of 10

# S E C T I O N K E Y

A | Hanging cleat | B | Big drawer, U-box | C | Waste Ø1⅝" and P-trap

Support, set back 3"; Wall spout; Ply sub-top; G Inner drawer; Section key

AST-DR-020 · 9 of 10

# NOTES

### REVISION 1

### Taking 1 ft off the left moves the marble's centre 6 in

### right — onto the faucet. Bowl, drawer split and support

all sit on that one line. The top drawers split on it,

so the waste drops between them: only the big one is a U.

OPEN — bowl Ø1'-4" × 5" and the spout are assumed.

With the bowl on a 2'-9" counter its rim is at 3'-2".

OPEN — the support's design: reference photos to come.

# Notes

# AST-DR-020 · 10 of 10
