sakshampan733-cloud/a-study-in-teak/cad/print/vanity.pdf

SECTION A–A; ON THE FAUCET AXIS; 2'-0" DEEP; DETAIL 1 · THE MARBLE EDGE; SECTION; MARBLE SLAB ¾"; BWP PLY SUB-TOP ¾"; MITRED APRON, ¾" × 1½"; CARCASS TOP ¾"; TOP RAIL; FRONTS; WHAT; Door, cup pull; Top drawer, push-open; Big drawer, U-box, push-open; Inner drawer, finger scoop; MATERIALS; THE ROOM'S PALETTE — NOTHING NEW

FRONT

MARBLE THE FULL 5 FT · THE BOWL SITS UNDER THE FAUCET, 6 IN RIGHT OF CENTRE

5'-0" OVERALL; 2'-9" COUNTER 5"; VANITY CENTRE; FAUCET AXIS; PLAN

FROM ABOVE · WALL AT THE TOP

DETAIL 2 · THE BIG DRAWER

PLAN · INNER DRAWER DASHED

7⅞"

9⅜"

SIZES ARE THE FRONT ITSELF · ⅛" GAP ALL ROUND

Top | Beige-gold marble, the bathroom stone. ¾" slab
| on a ¾" BWP sub-top, mitred 1½" apron, polished.
Carcass | ¾" BWP / marine ply, teak veneer both faces.
| Every edge sealed — it stands in a wet room.
Fronts | ¾" BWP, teak veneer, ¼" solid teak lipping.
Runners | Undermount, full extension. Drawers push-to-open —
| no handles on them; the doors keep cup pulls.
Fittings | Chrome — already bought. Door cup pulls to match.
Hanging | ¾" ply cleat on the wall, 2'-3½"–2'-5⅞" high.
Inner | A U-box on its own runners, above the big
| drawer's low sides — see AST-DR-022.

6" OFF CENTRE; SECTION KEY; Hanging cleat; Big drawer, U-box; Waste Ø1⅝" and P-trap; Support, set back 3"; Wall spout; Ply sub-top; NOTES; REVISION 1

G Inner drawer

Symmetric about the vanity's centre — except the bowl,

which has to sit under the faucet, 6" right of it.

The waste drops through the right-hand TOP drawer as

well as the big one: both are U-boxes (see section).

OPEN — bowl Ø1'-4" × 5" and the spout are assumed.

With the bowl on a 2'-9" counter its rim is at 3'-2".

OPEN — the support's design: reference photos to come.

A S T U D Y I N T E A K

Particulars of the room

VANITY — NORMAL

Marble full length · Door · Drawers · Door

SCALE
AS NOTED @ A3

DATE
23.09.2026

REV

1 — as sketched

DWG
AST-DR-019

PROJECT

## A Study in Teak — Vanity — Normal

SHEET

## General arrangement — the whole sheet

each view follows at its own scale, pages 2 to 10

SCALE

## NTS

DATE
23.09.2026

REV

DRAWING

## AST-DR-019 · 1 of 10

ALL DIMENSIONS IN FEET & INCHES. PRINT ON A3 AT 100% / “ACTUAL SIZE” — NOT “FIT TO PAGE” — AND CHECK THE SCALE BAR. DO NOT SCALE; WORK TO FIGURED DIMENSIONS. VERIFY ON SITE.

## FRONT

5'-0" OVERALL; OUNTER 5"; VANITY CENTRE; FAUCET AXIS; Front

SCALE 1:8 (1½" = 1'-0") @ A3 · MARBLE THE FULL 5 FT · THE BOWL SITS UNDER THE FAUCET, 6 IN RIGHT OF CENTRE

AST-DR-019 · 2 of 10

Marble full length · Door · Drawers · Door

## SECTION A–A

2'-0" DEEP; Section A–A

SCALE 1:8 (1½" = 1'-0") @ A3 · ON THE FAUCET AXIS

AST-DR-019 · 3 of 10

# DETAIL 1 · THE MARBLE EDGE

## SCALE 1:1 (FULL SIZE) @ A3 · SECTION

MARBLE SLAB ¾"; MITRED APRON, ¾" × 1½"; CARCASS TOP ¾"; TOP RAIL

BWP PLY SUB-TOP ¾"

Detail 1 · the marble edge

AST-DR-019 · 4 of 10

# FRONTS

# SIZES ARE THE FRONT ITSELF · ⅛" GAP ALL ROUND

No. | WHAT | W × H | FT-IN
1 | Door, cup pull | 11¾" × 1'-10¼" | 11¾" × 1'-10¼"
2 | Door, cup pull | 11¾" × 1'-10¼" | 11¾" × 1'-10¼"
3 | Top drawer, push-open | 1'-¾" × 5¾" | 1'-¾" × 5¾"
4 | Top drawer, push-open | 1'-¾" × 5¾" | 1'-¾" × 5¾"
5 | Big drawer, U-box, push-open | 2'-2¾" × 1'-3¼" | 2'-2¾" × 1'-3¼"
5a | Inner drawer, finger scoop | 2'-⅝" × 3¾" | 2'-⅝" × 3¾"

## Fronts

## AST-DR-019 · 5 of 10

# MATERIALS

# THE ROOM'S PALETTE — NOTHING NEW

Top | Beige-gold marble, the bathroom stone. ¾" slab
| on a ¾" BWP sub-top, mitred 1½" apron, polished.
Carcass | ¾" BWP / marine ply, teak veneer both faces.
| Every edge sealed — it stands in a wet room.
Fronts | ¾" BWP, teak veneer, ¼" solid teak lipping.
Runners | Undermount, full extension. Drawers push-to-open —
| no handles on them; the doors keep cup pulls.
Fittings | Chrome — already bought. Door cup pulls to match.
Hanging | ¾" ply cleat on the wall, 2'-3½"–2'-5⅞" high.
Inner | A U-box on its own runners, above the big
| drawer's low sides — see AST-DR-022.

## Materials

## AST-DR-019 · 6 of 10

# PLAN

## SCALE 1:5 @ A3 · FROM ABOVE · WALL AT THE TOP

6" OFF CENTRE; Plan

AST-DR-019 · 7 of 10

# DETAIL 2 · THE BIG DRAWER

# SCALE 1:5 @ A3 · PLAN · INNER DRAWER DASHED


Detail 2 · the big drawer

AST-DR-019 · 8 of 10

# SECTION KEY

A | Hanging cleat | B | Big drawer, U-box | C | Waste Ø1⅝" and P-trap

Support, set back 3"; Wall spout; Ply sub-top; G Inner drawer; Section key

AST-DR-019 · 9 of 10

# NOTES

## REVISION 1

Symmetric about the vanity's centre — except the bowl,

which has to sit under the faucet, 6" right of it.

### The waste drops through the right-hand TOP drawer as

well as the big one: both are U-boxes (see section).

OPEN — bowl Ø1'-4" × 5" and the spout are assumed.

With the bowl on a 2'-9" counter its rim is at 3'-2".

OPEN — the support's design: reference photos to come.

## Notes

## AST-DR-019 · 10 of 10
