sakshampan733-cloud/a-study-in-teak/cad/print/architrave-01.webp

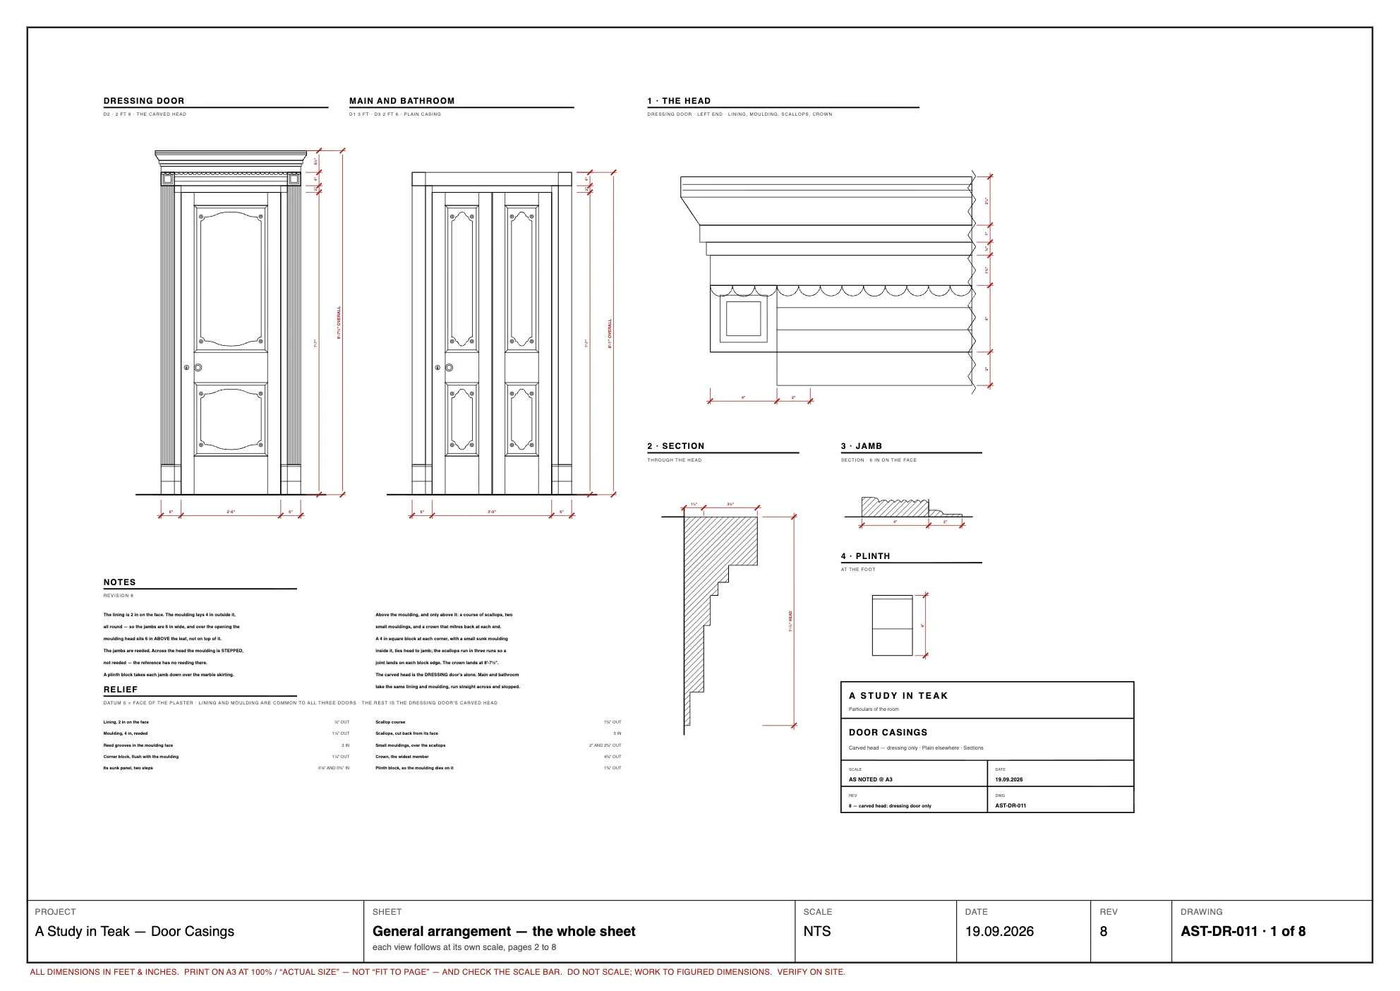
cad/print/architrave-01.webp
