sakshampan733-cloud/a-study-in-teak/cad/print/architrave-02.webp

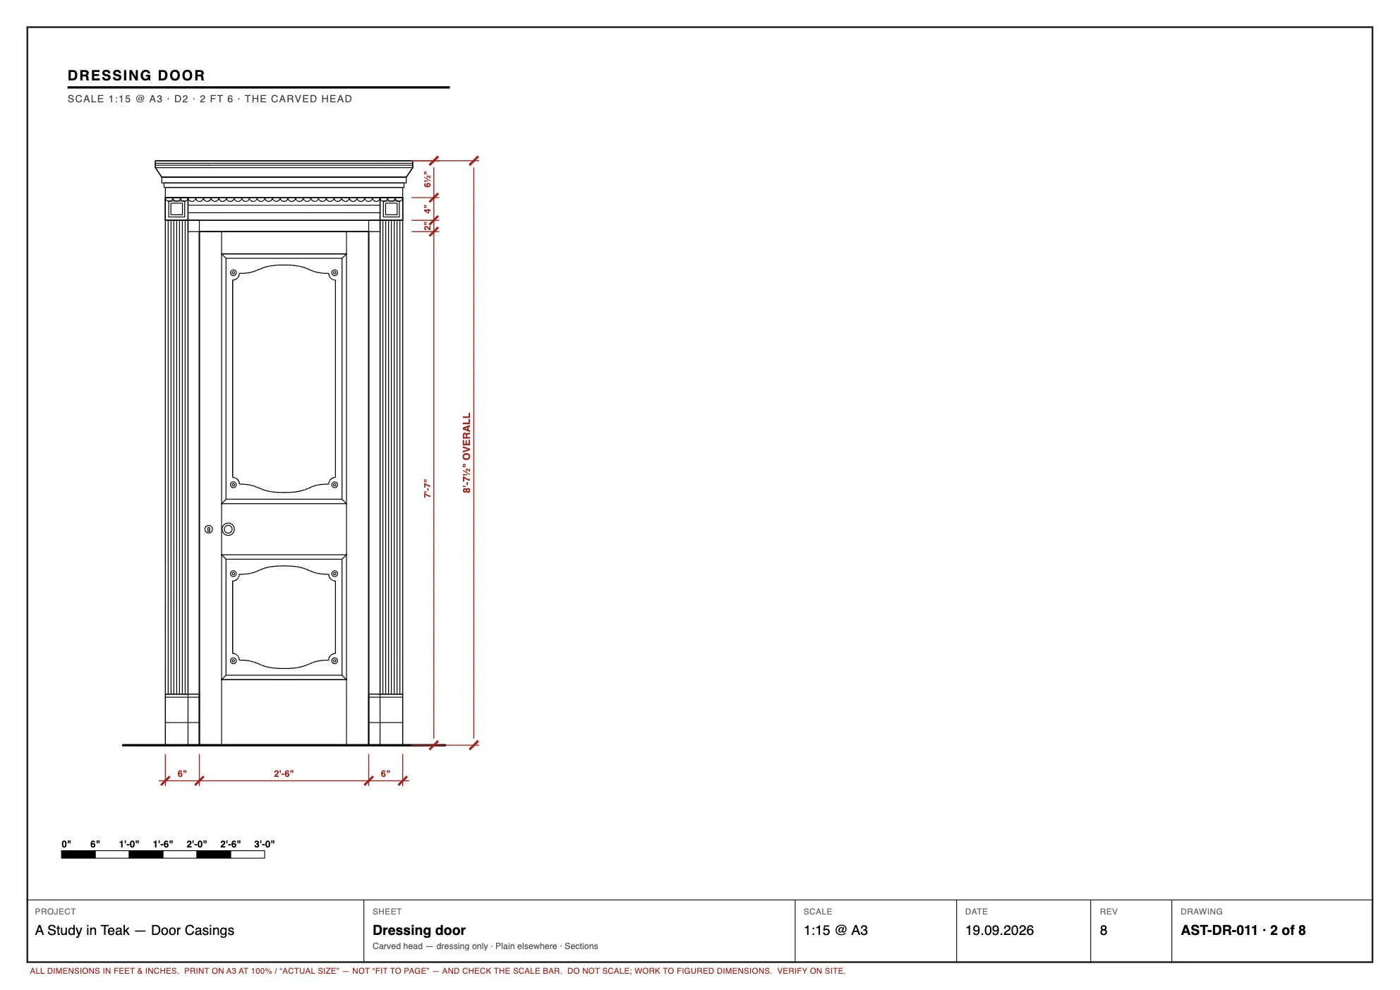
cad/print/architrave-02.webp
