sakshampan733-cloud/a-study-in-teak/cad/print/architrave-04.webp

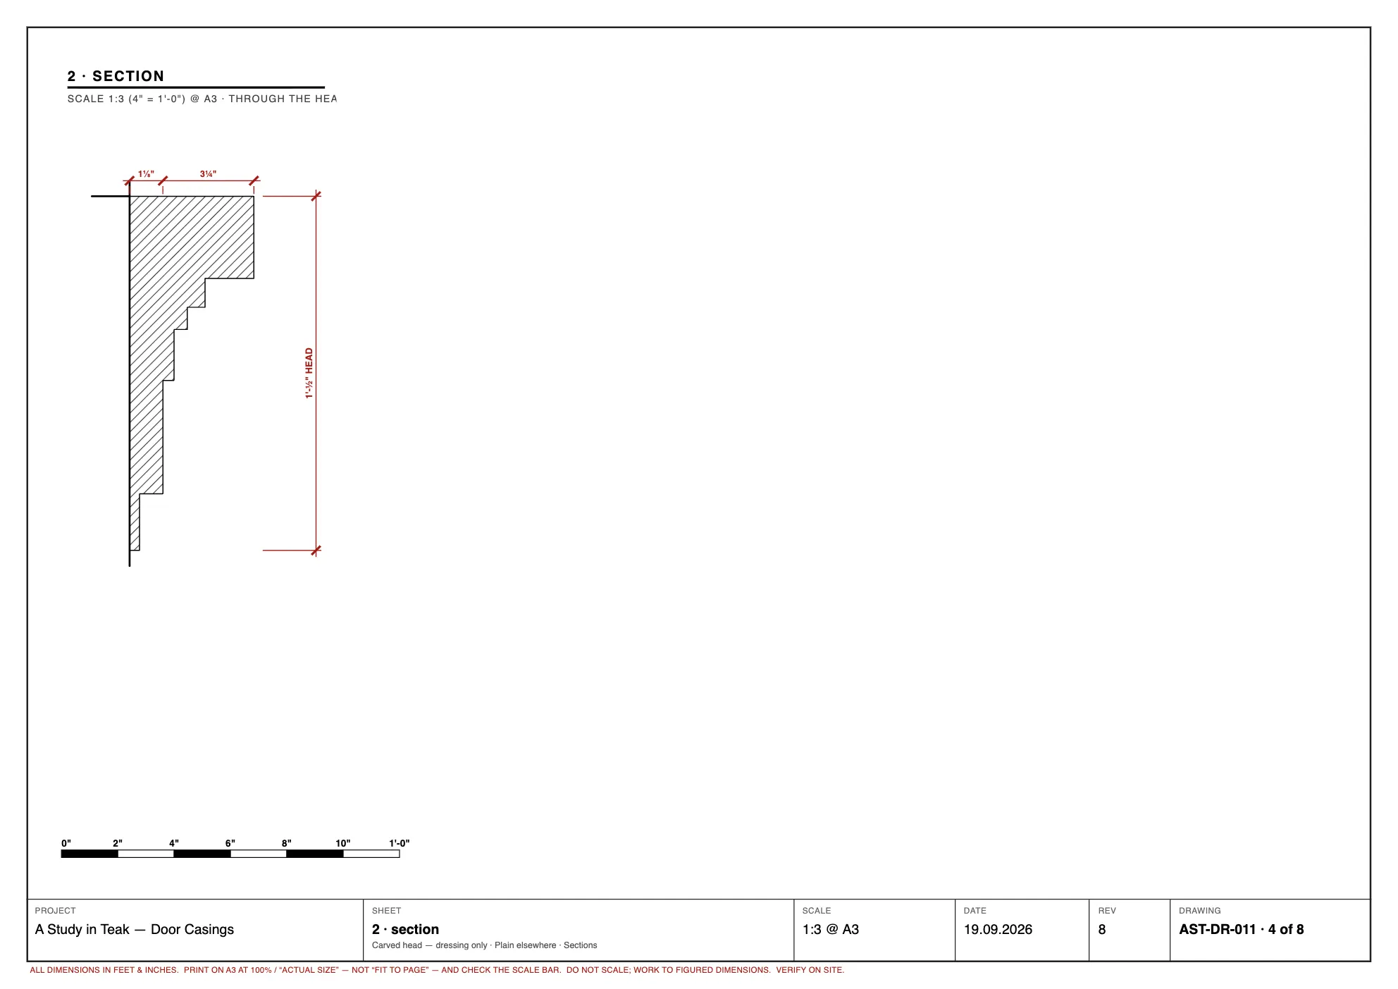
cad/print/architrave-04.webp
