sakshampan733-cloud/a-study-in-teak/cad/print/architrave-05.webp

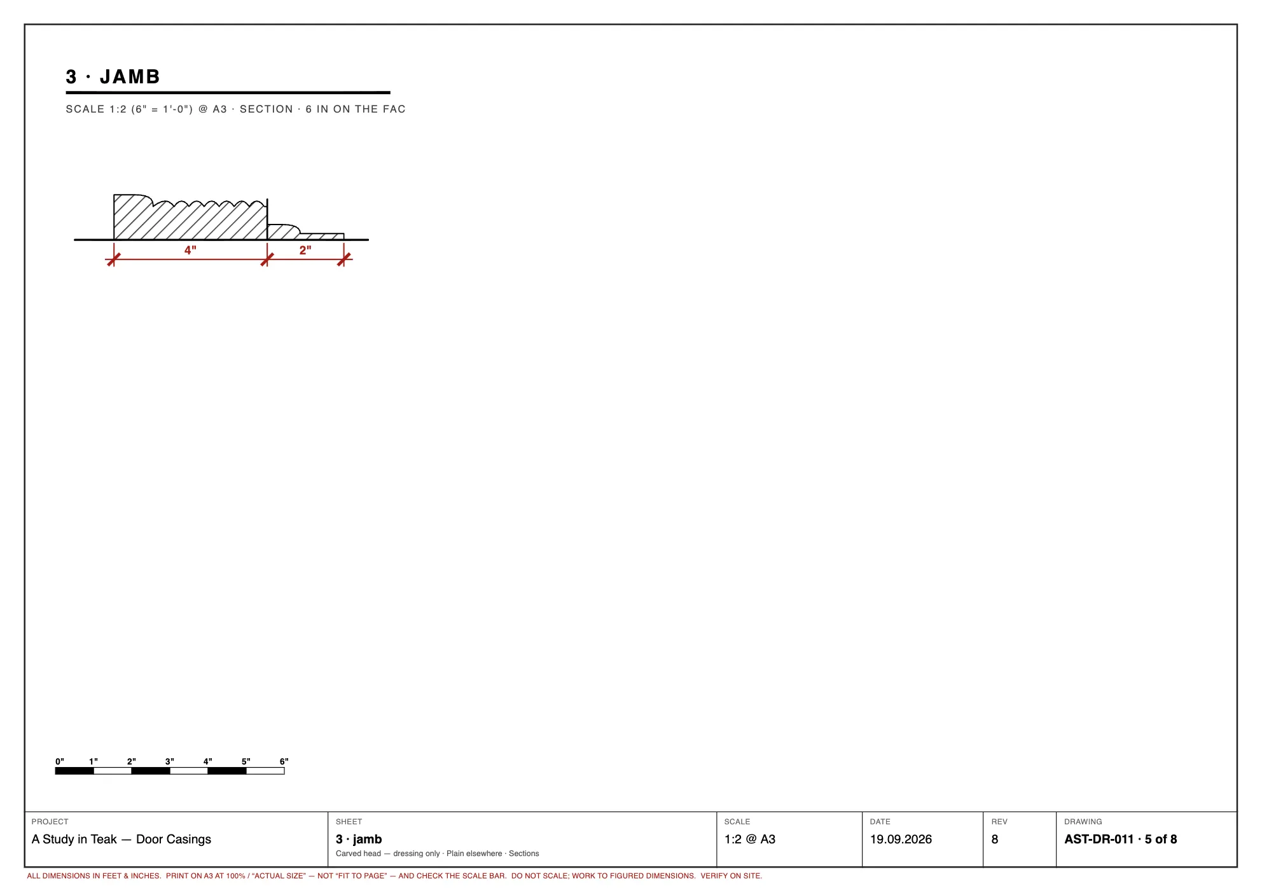
cad/print/architrave-05.webp
