sakshampan733-cloud/a-study-in-teak/cad/print/architrave-06.webp

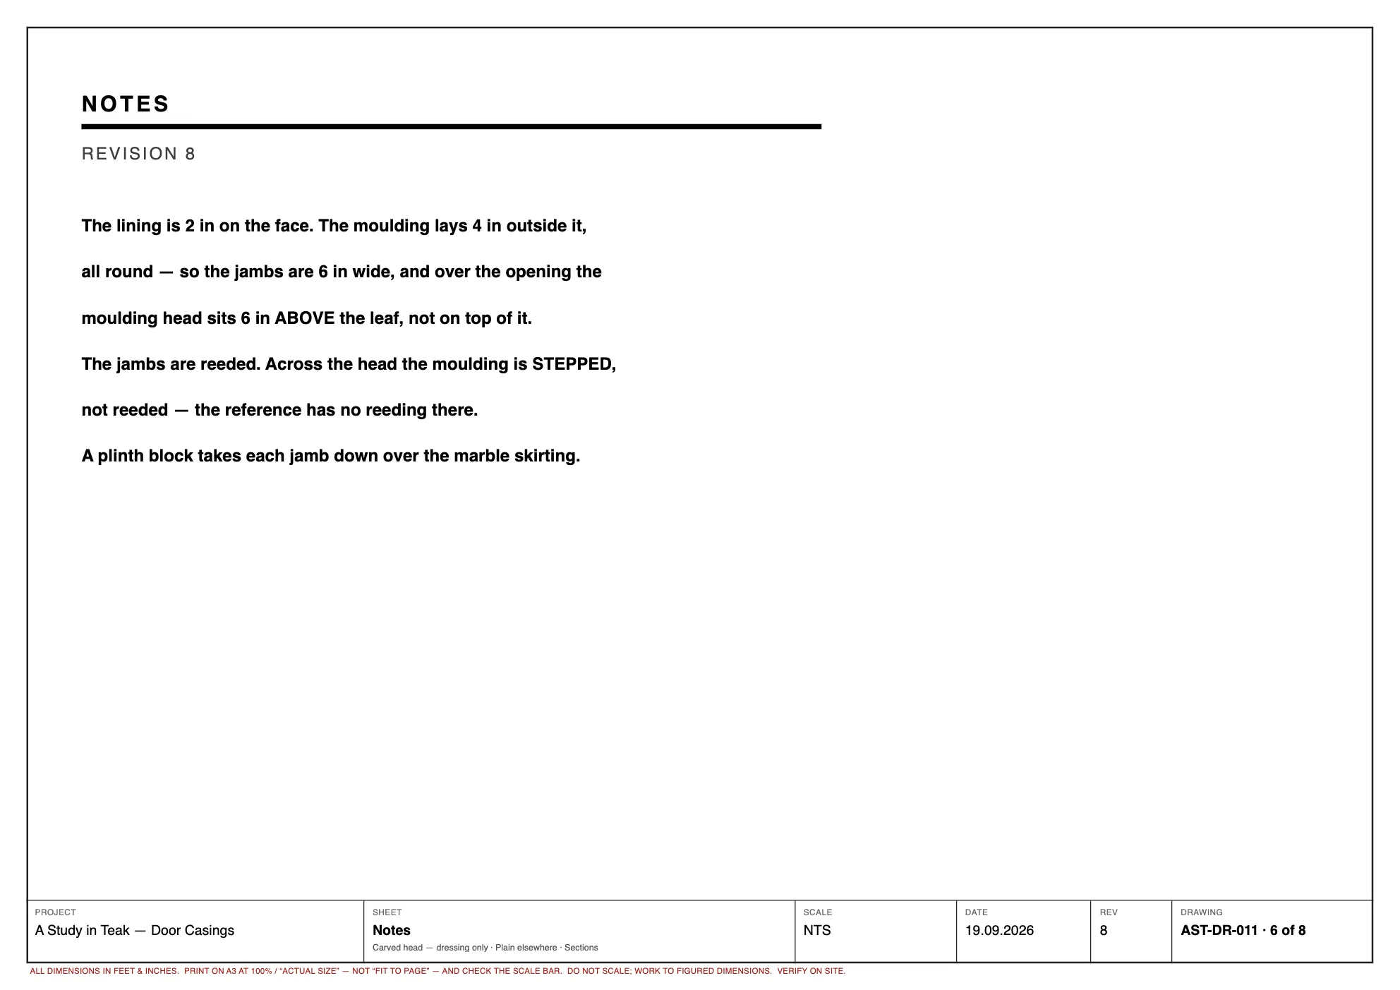
cad/print/architrave-06.webp
