sakshampan733-cloud/a-study-in-teak/cad/print/architrave-07.webp

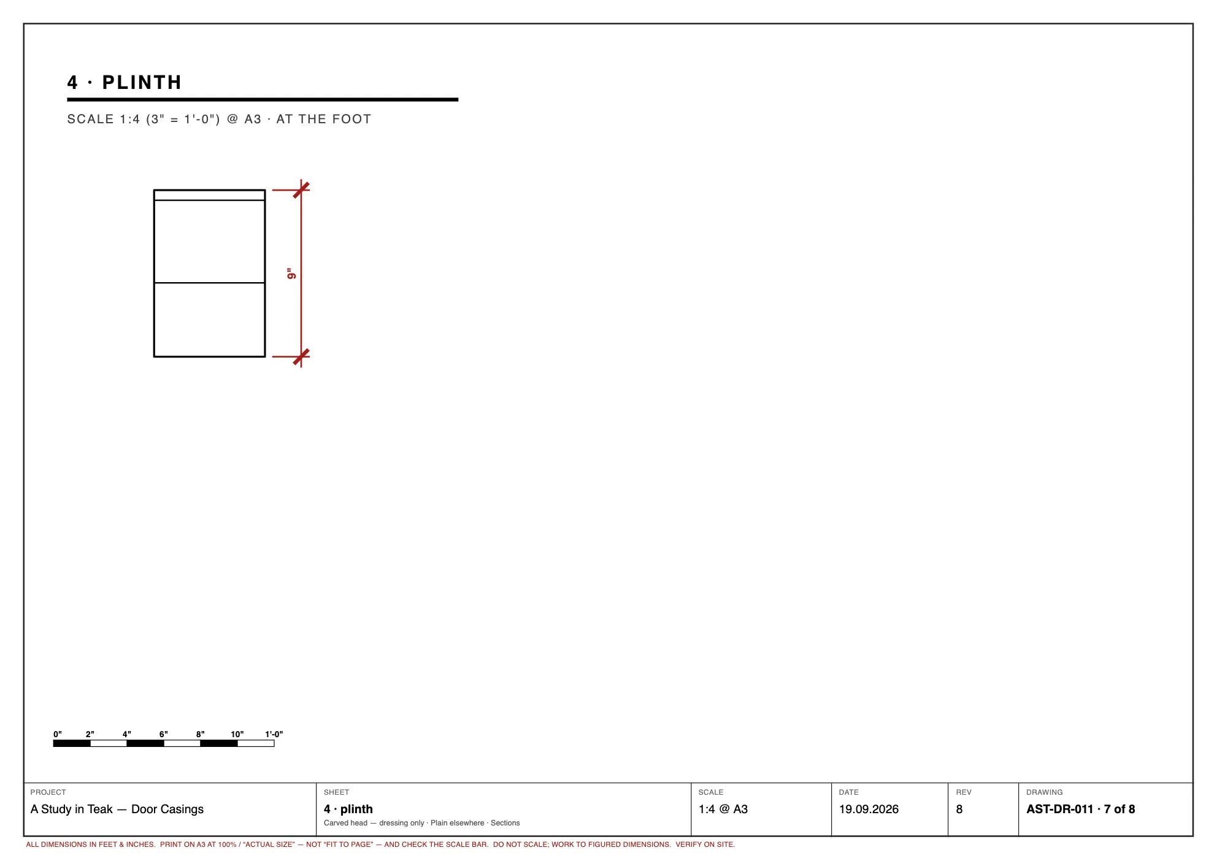
cad/print/architrave-07.webp
