sakshampan733-cloud/a-study-in-teak/cad/print/architrave-08.webp

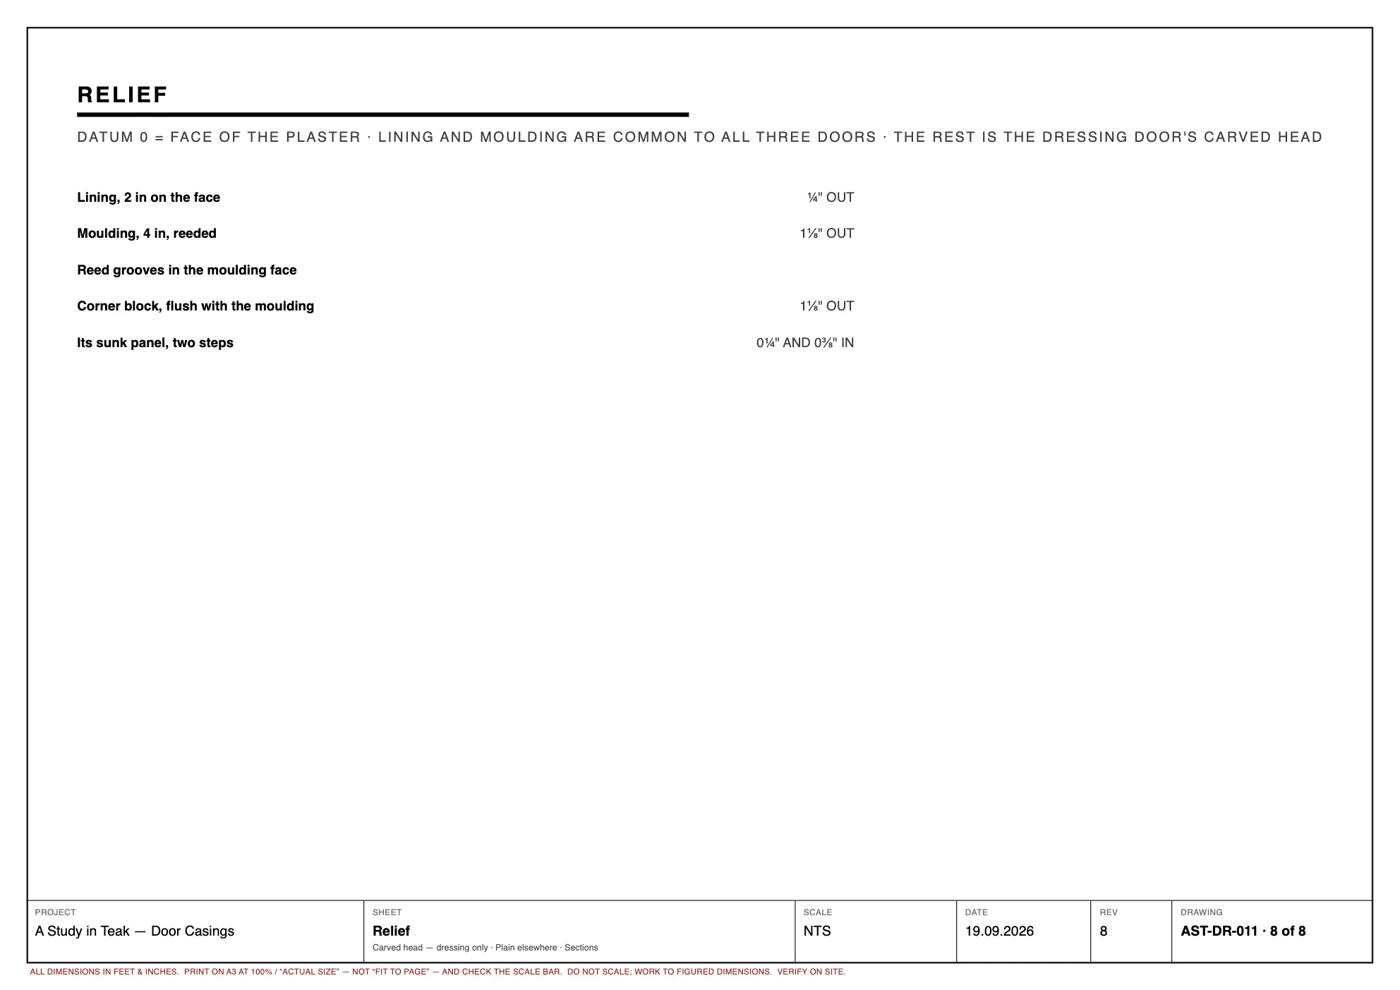
cad/print/architrave-08.webp
