sakshampan733-cloud/a-study-in-teak/cad/print/bathroom-01.webp

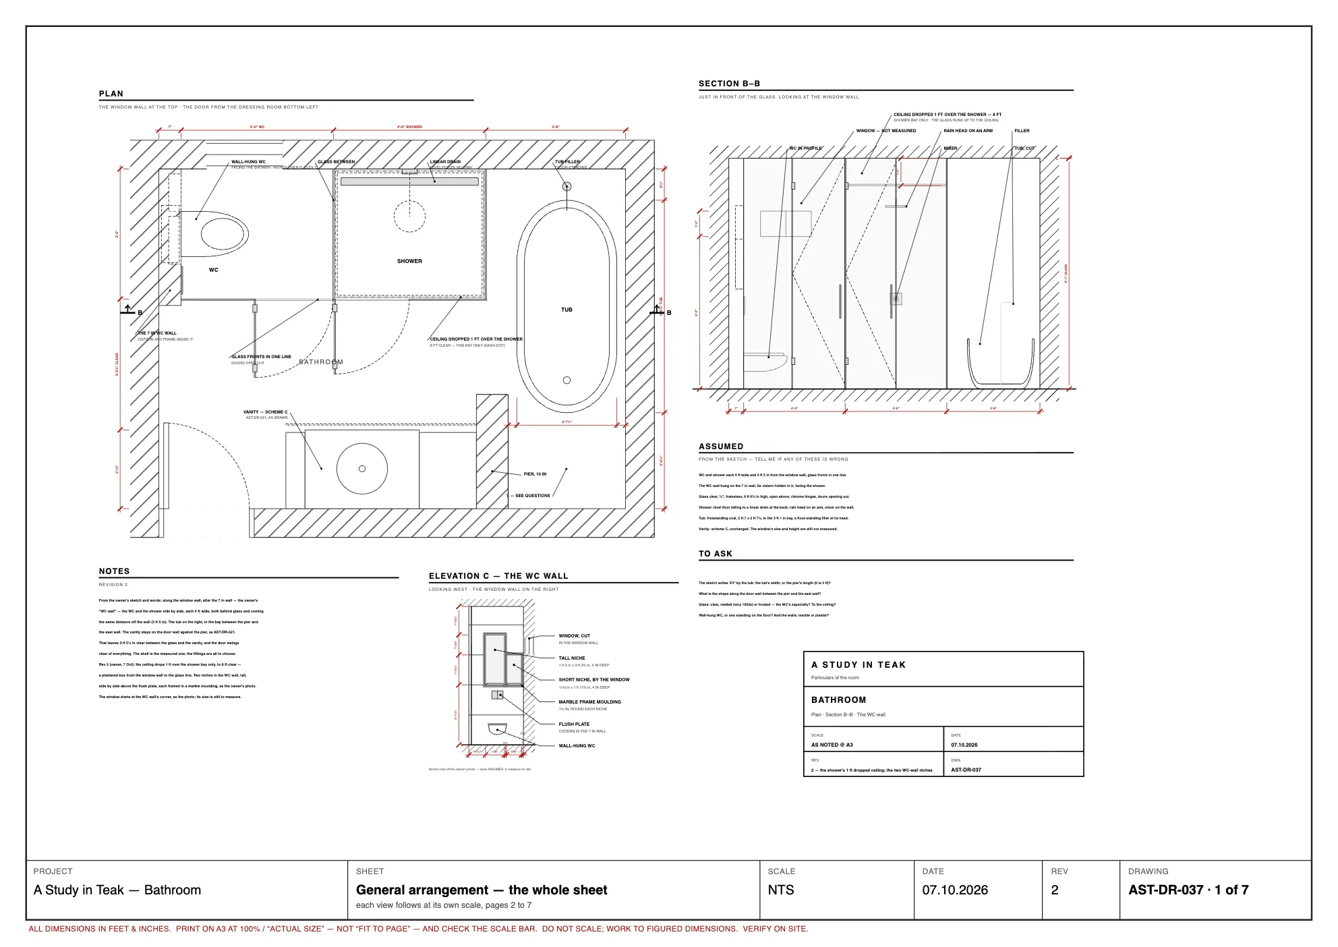
cad/print/bathroom-01.webp
