sakshampan733-cloud/a-study-in-teak/cad/print/bathroom-02.webp

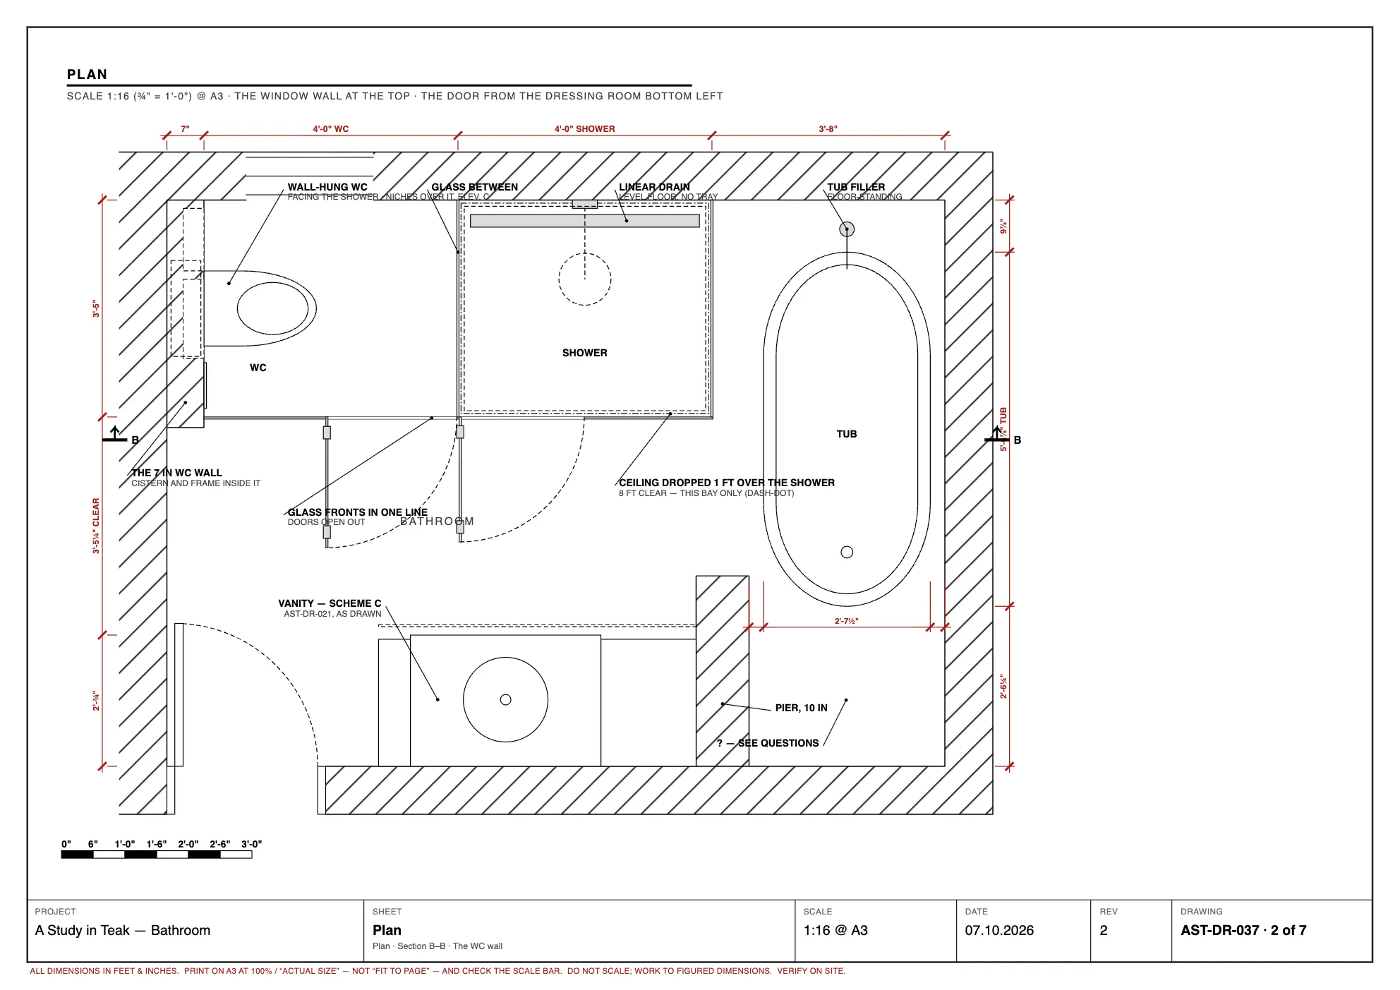
cad/print/bathroom-02.webp
