sakshampan733-cloud/a-study-in-teak/cad/print/bathroom-03.webp

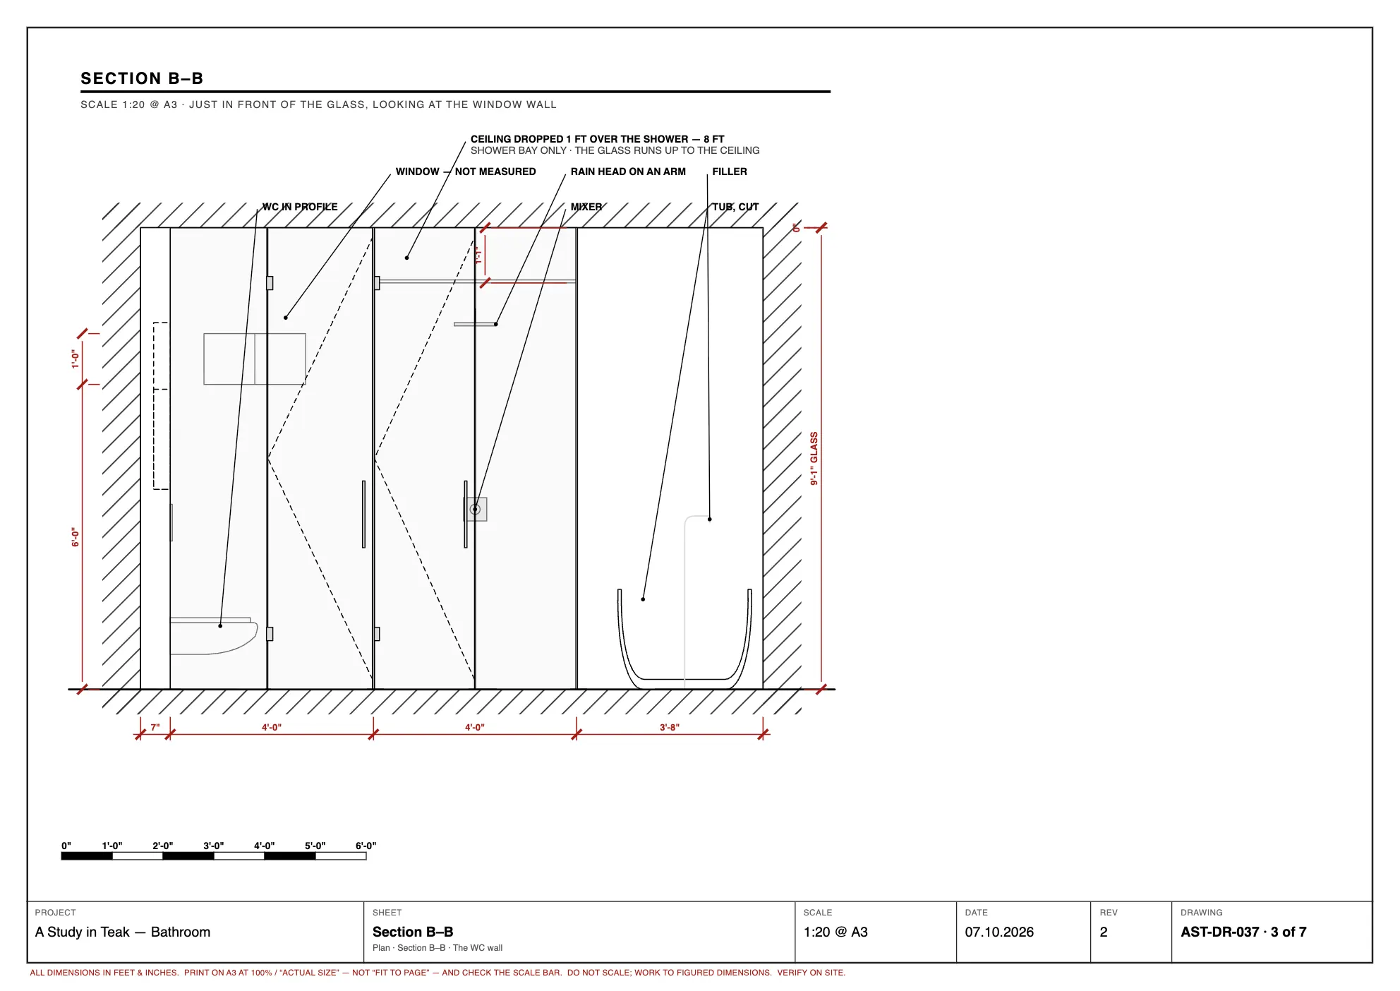
cad/print/bathroom-03.webp
