sakshampan733-cloud/a-study-in-teak/cad/print/bathroom-04.webp

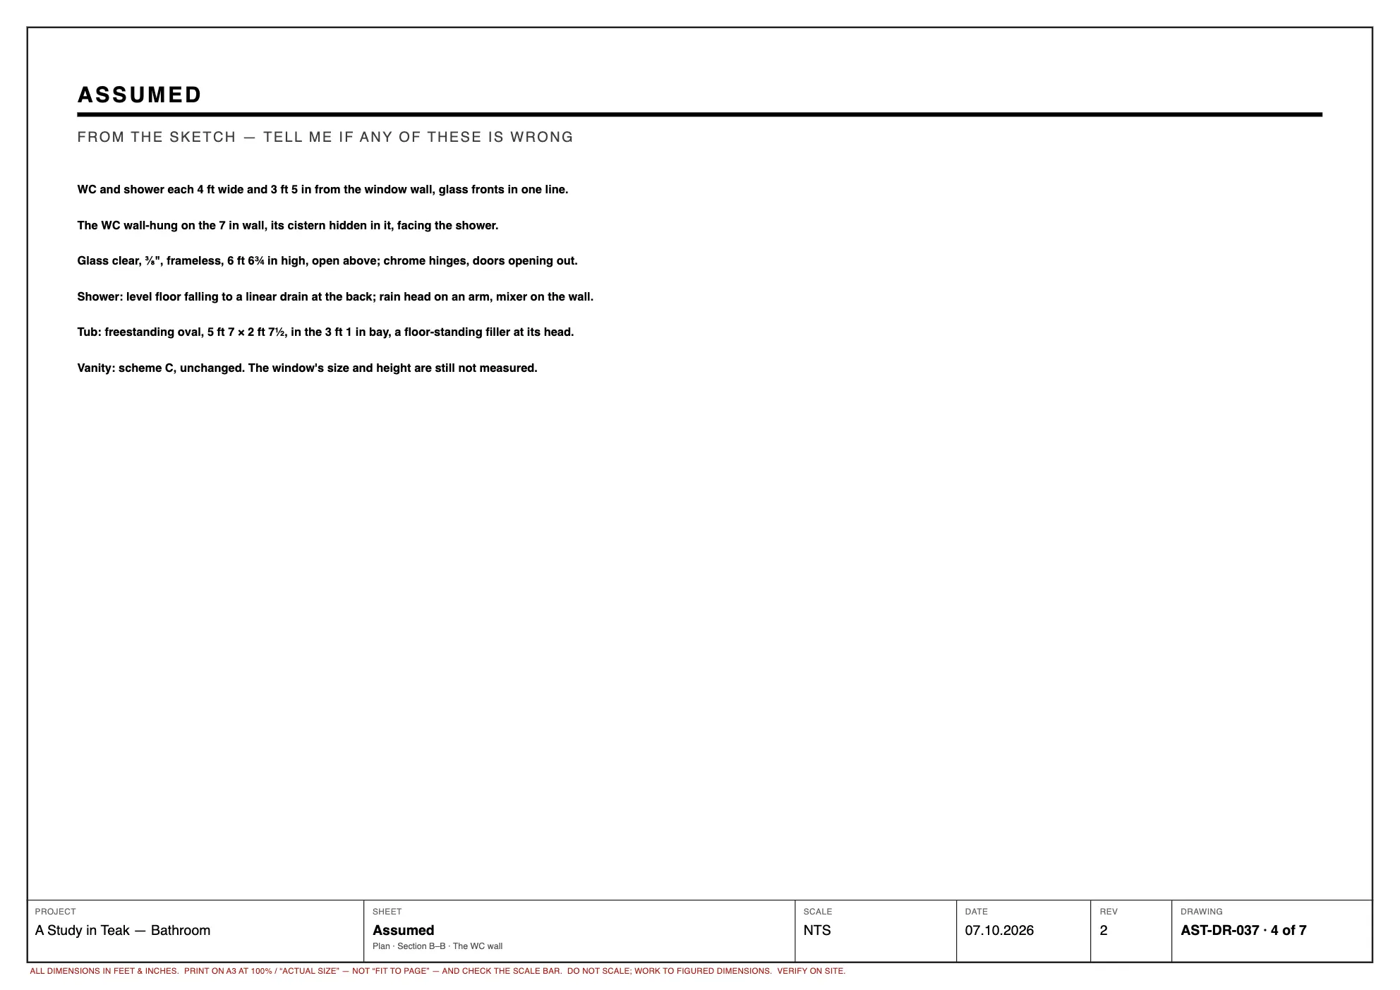
cad/print/bathroom-04.webp
