sakshampan733-cloud/a-study-in-teak/cad/print/bathroom-05.webp

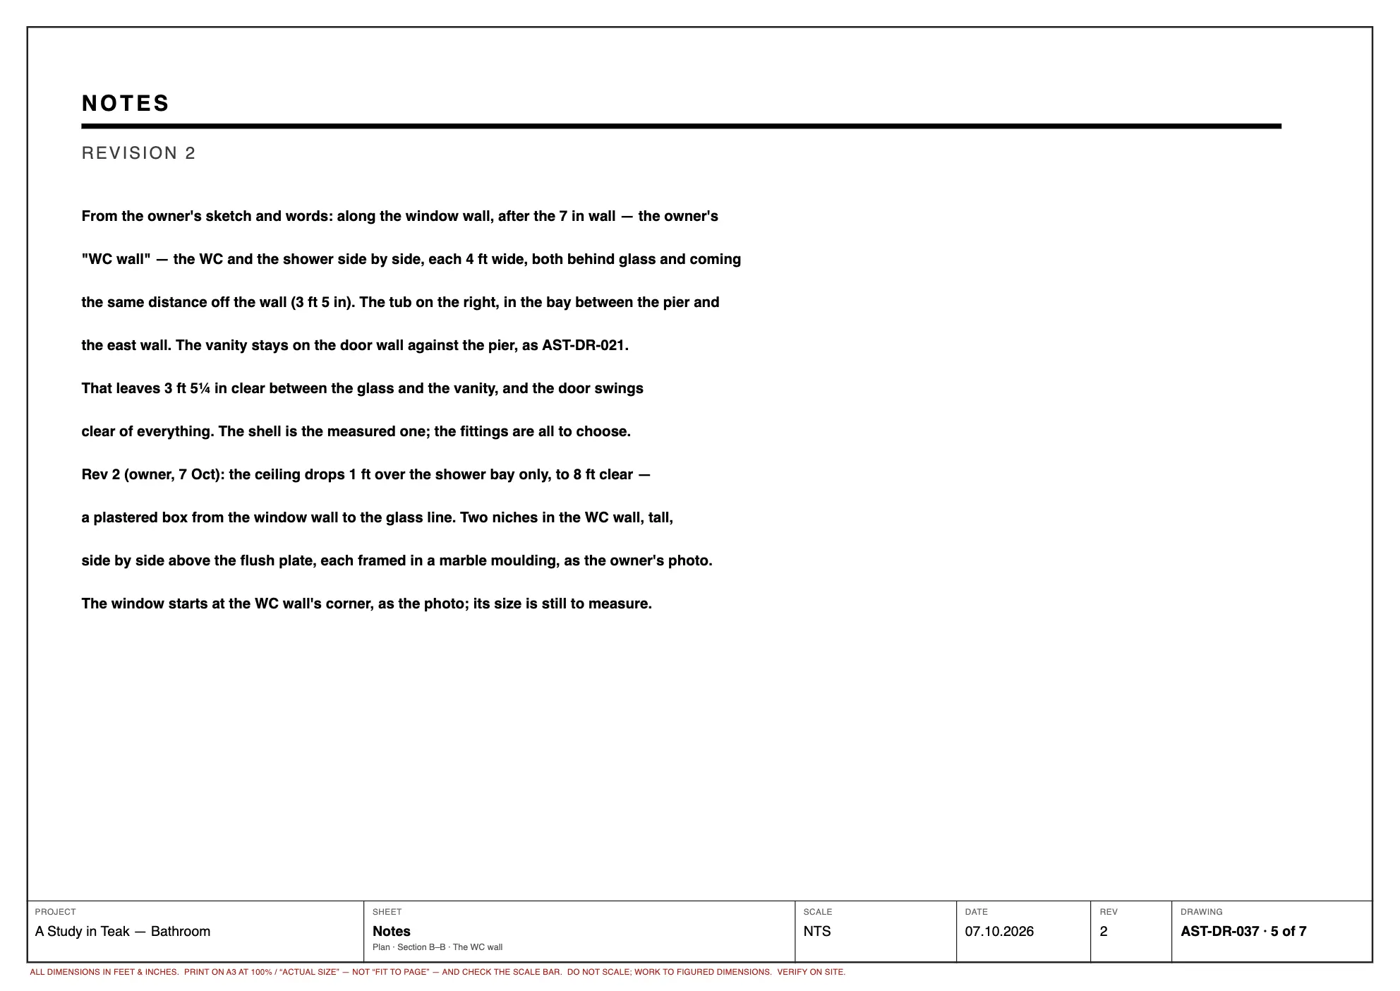
cad/print/bathroom-05.webp
