sakshampan733-cloud/a-study-in-teak/cad/print/bathroom-06.webp

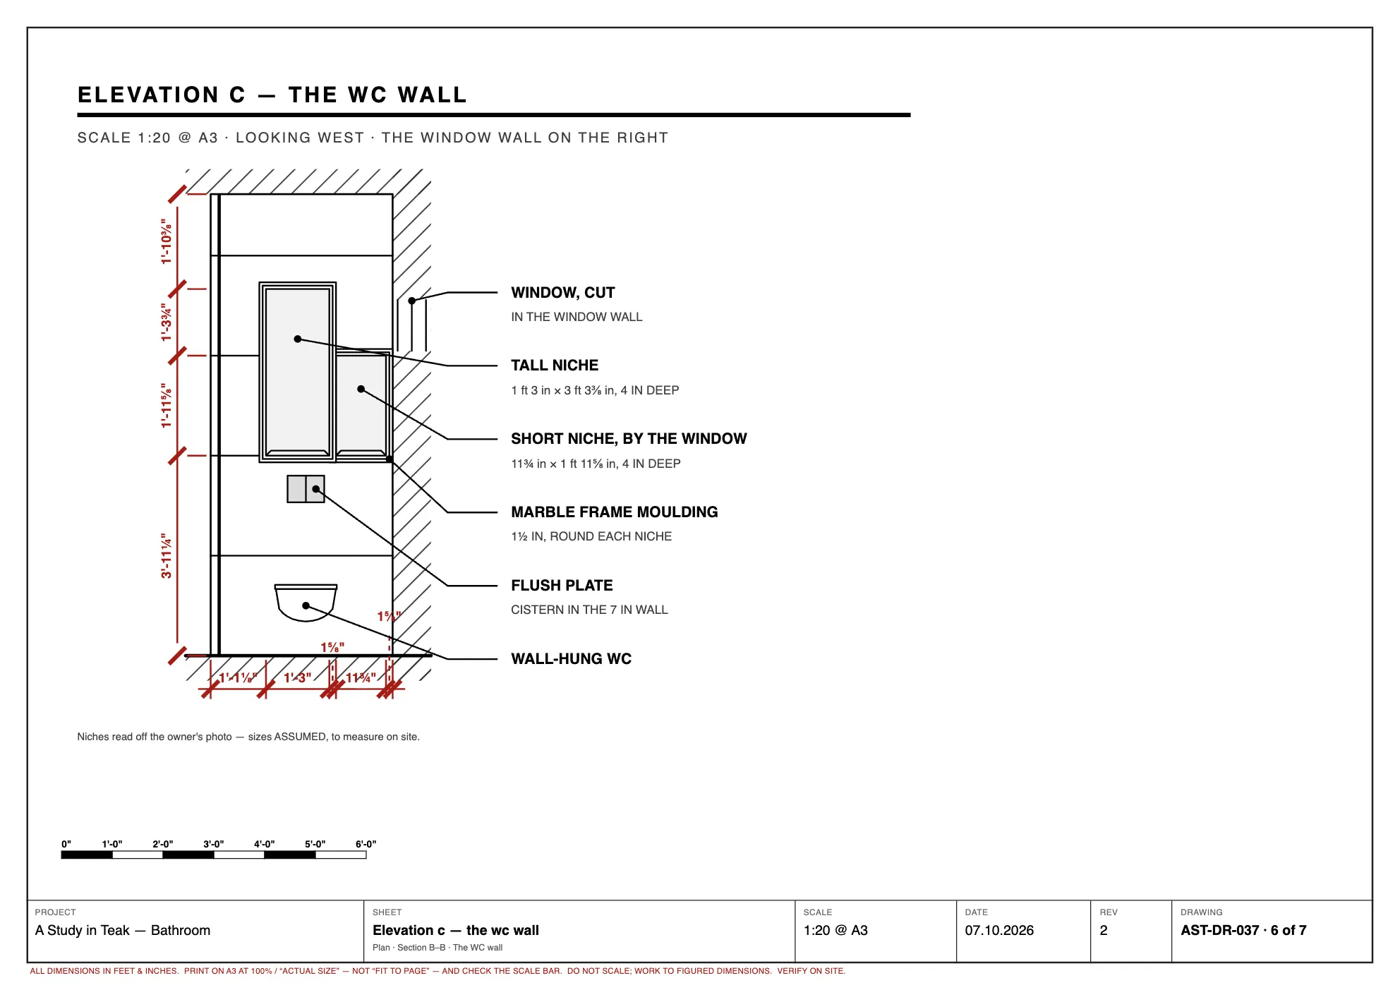
cad/print/bathroom-06.webp
