sakshampan733-cloud/a-study-in-teak/cad/print/bedframe-01.webp

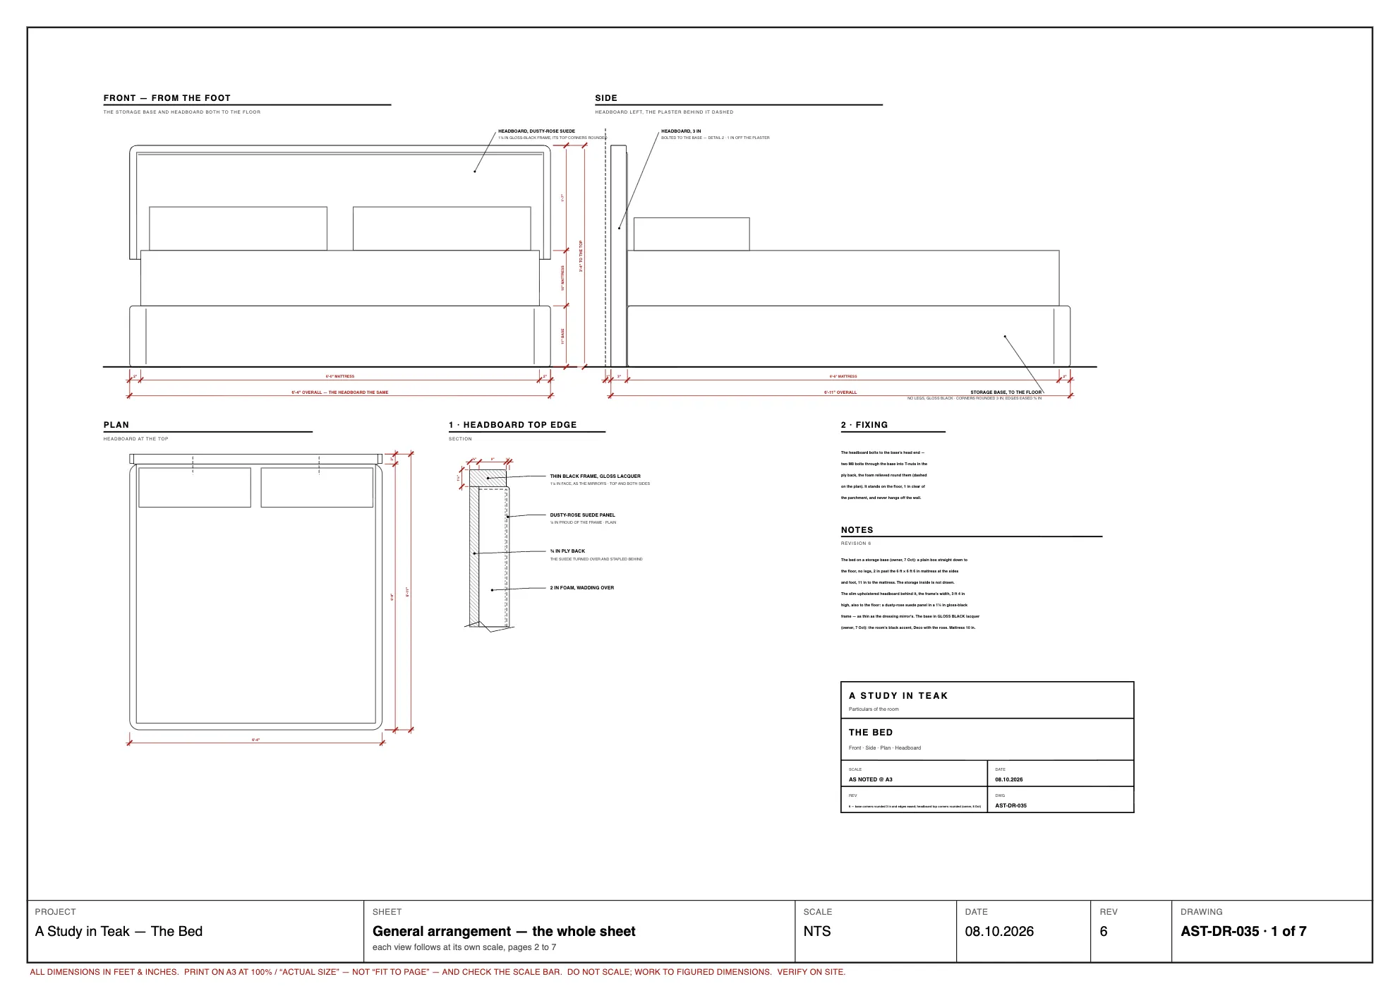
cad/print/bedframe-01.webp
