sakshampan733-cloud/a-study-in-teak/cad/print/bedframe-02.webp

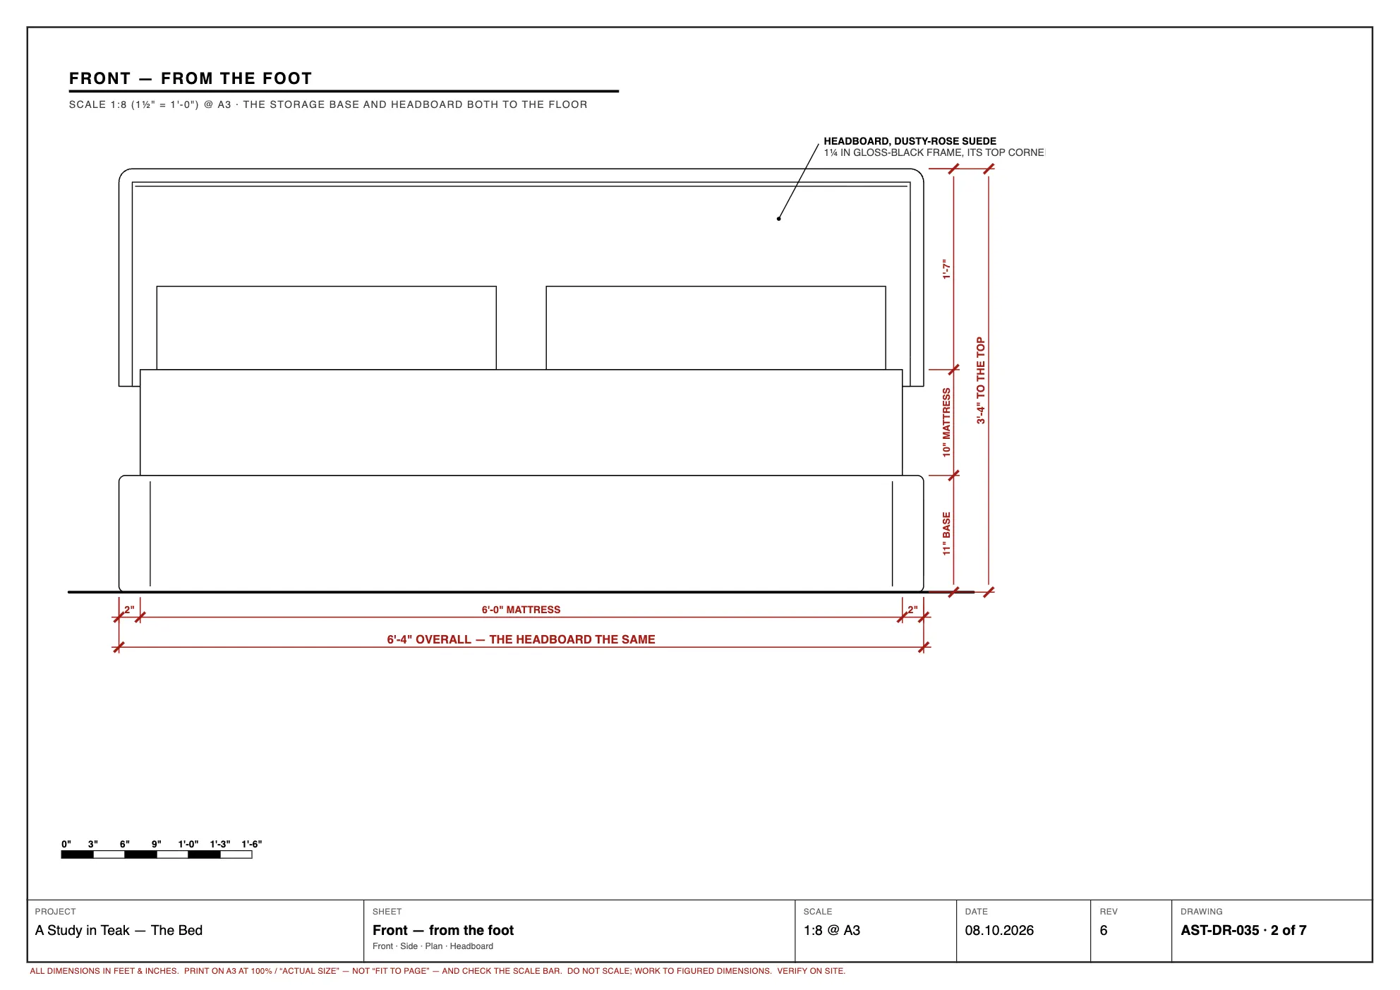
cad/print/bedframe-02.webp
