sakshampan733-cloud/a-study-in-teak/cad/print/bedframe-03.webp

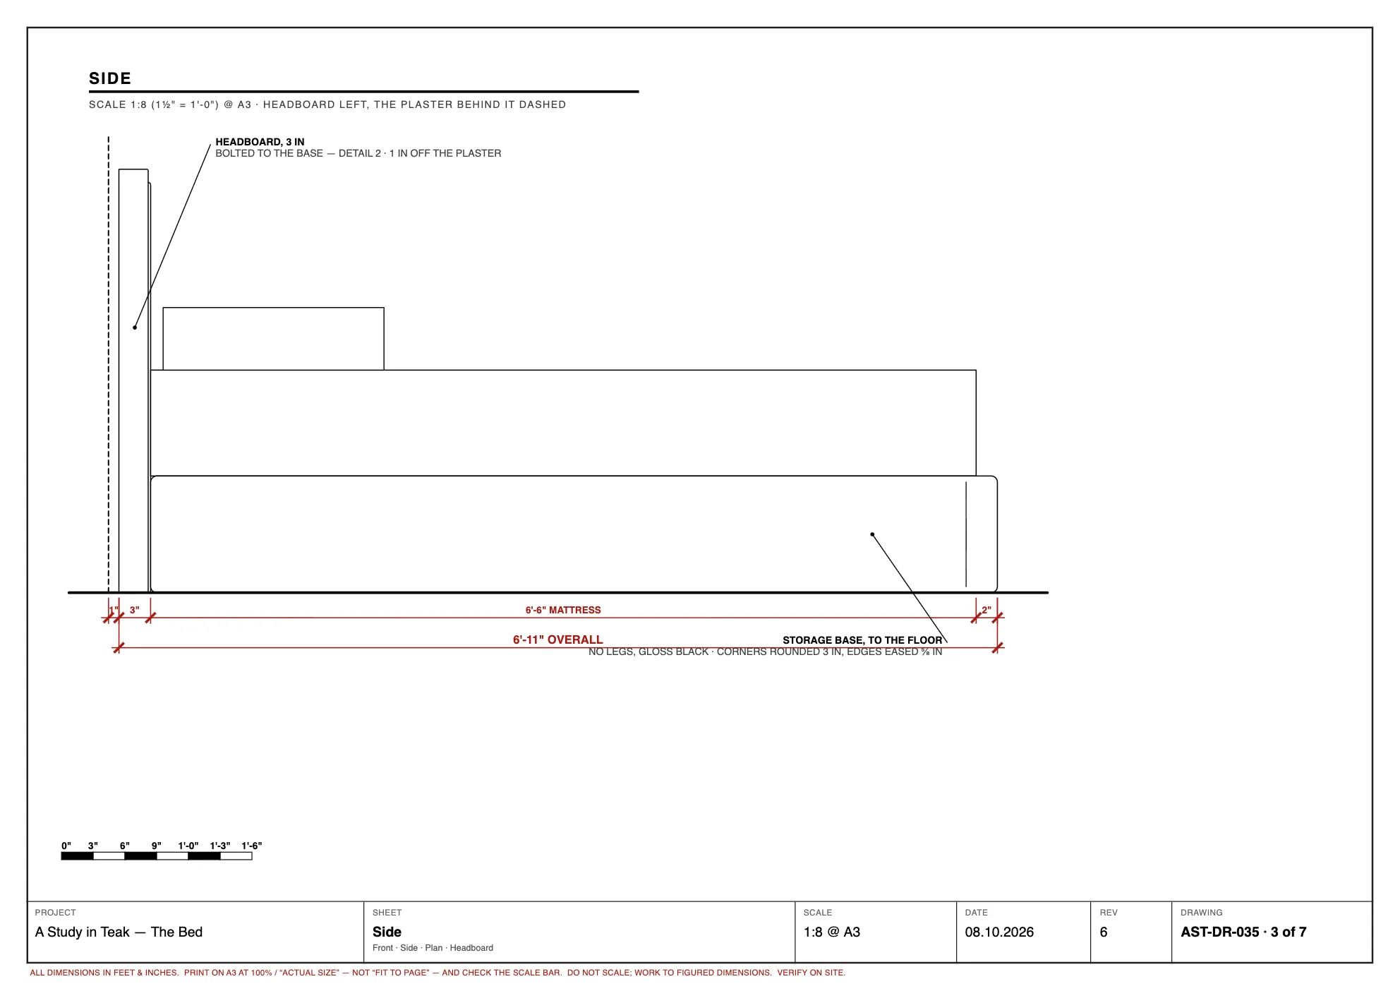
cad/print/bedframe-03.webp
