sakshampan733-cloud/a-study-in-teak/cad/print/bedframe-04.webp

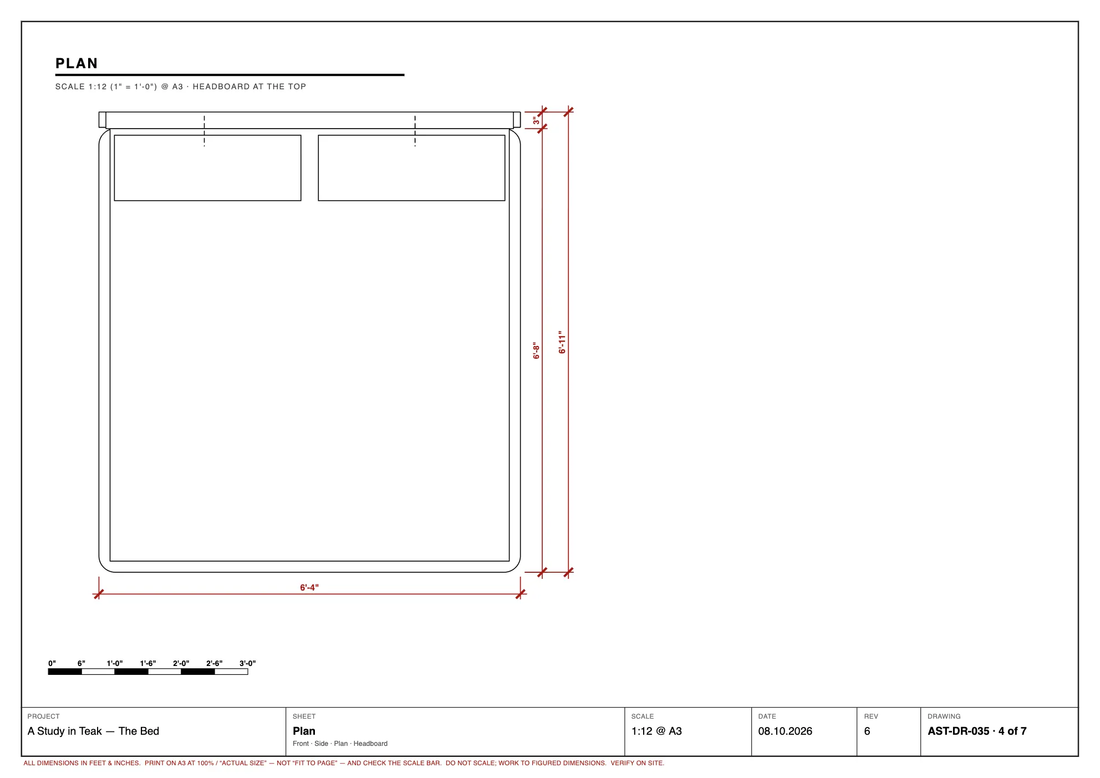
cad/print/bedframe-04.webp
