sakshampan733-cloud/a-study-in-teak/cad/print/bedframe-05.webp

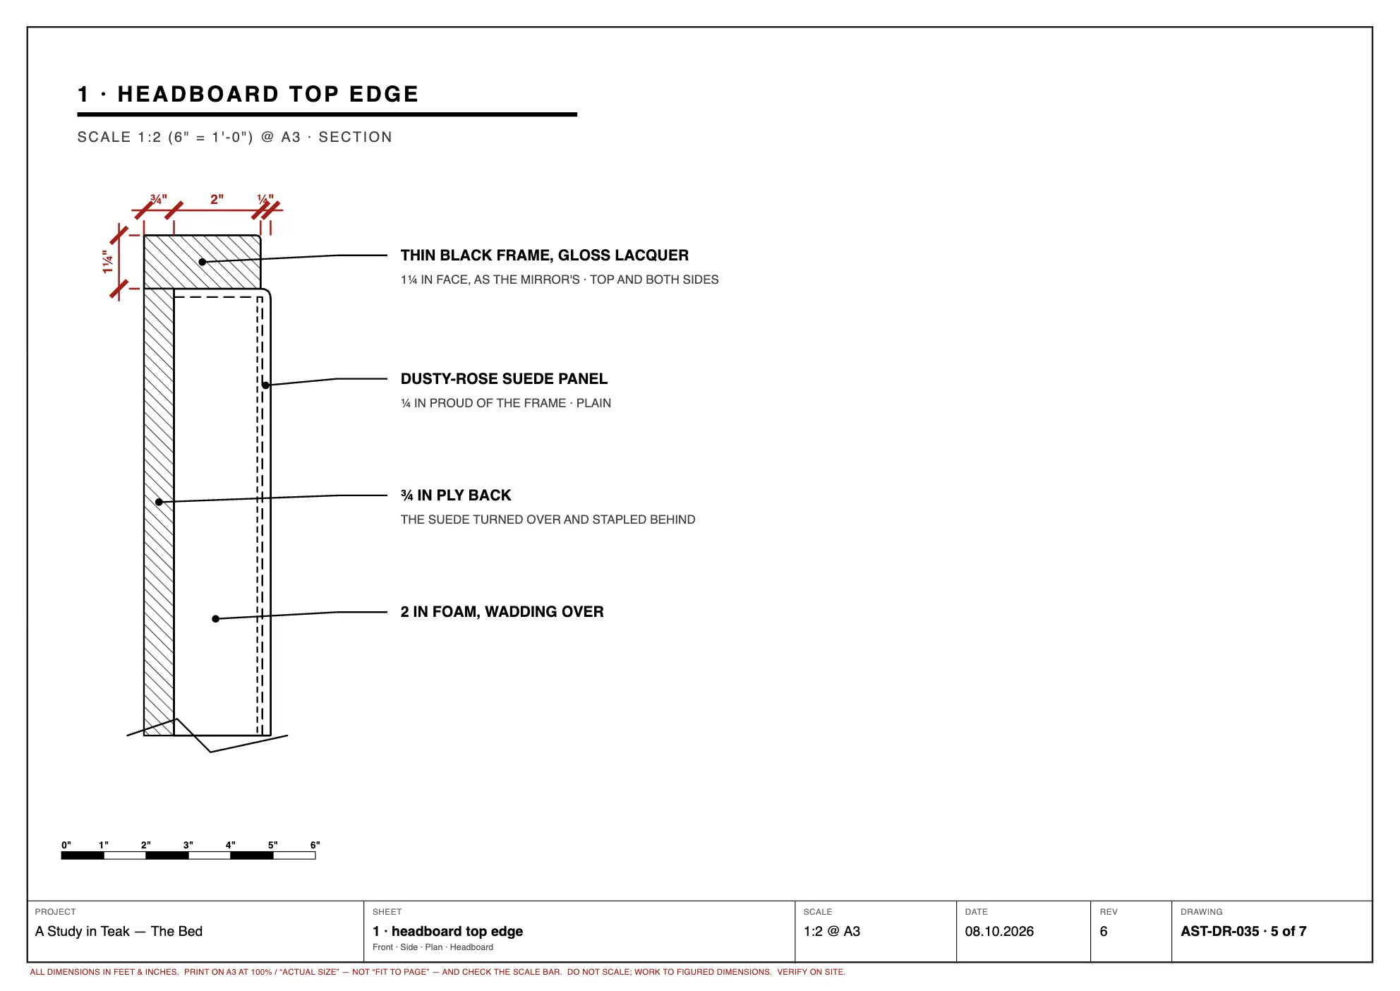
cad/print/bedframe-05.webp
