sakshampan733-cloud/a-study-in-teak/cad/print/bedframe-06.webp

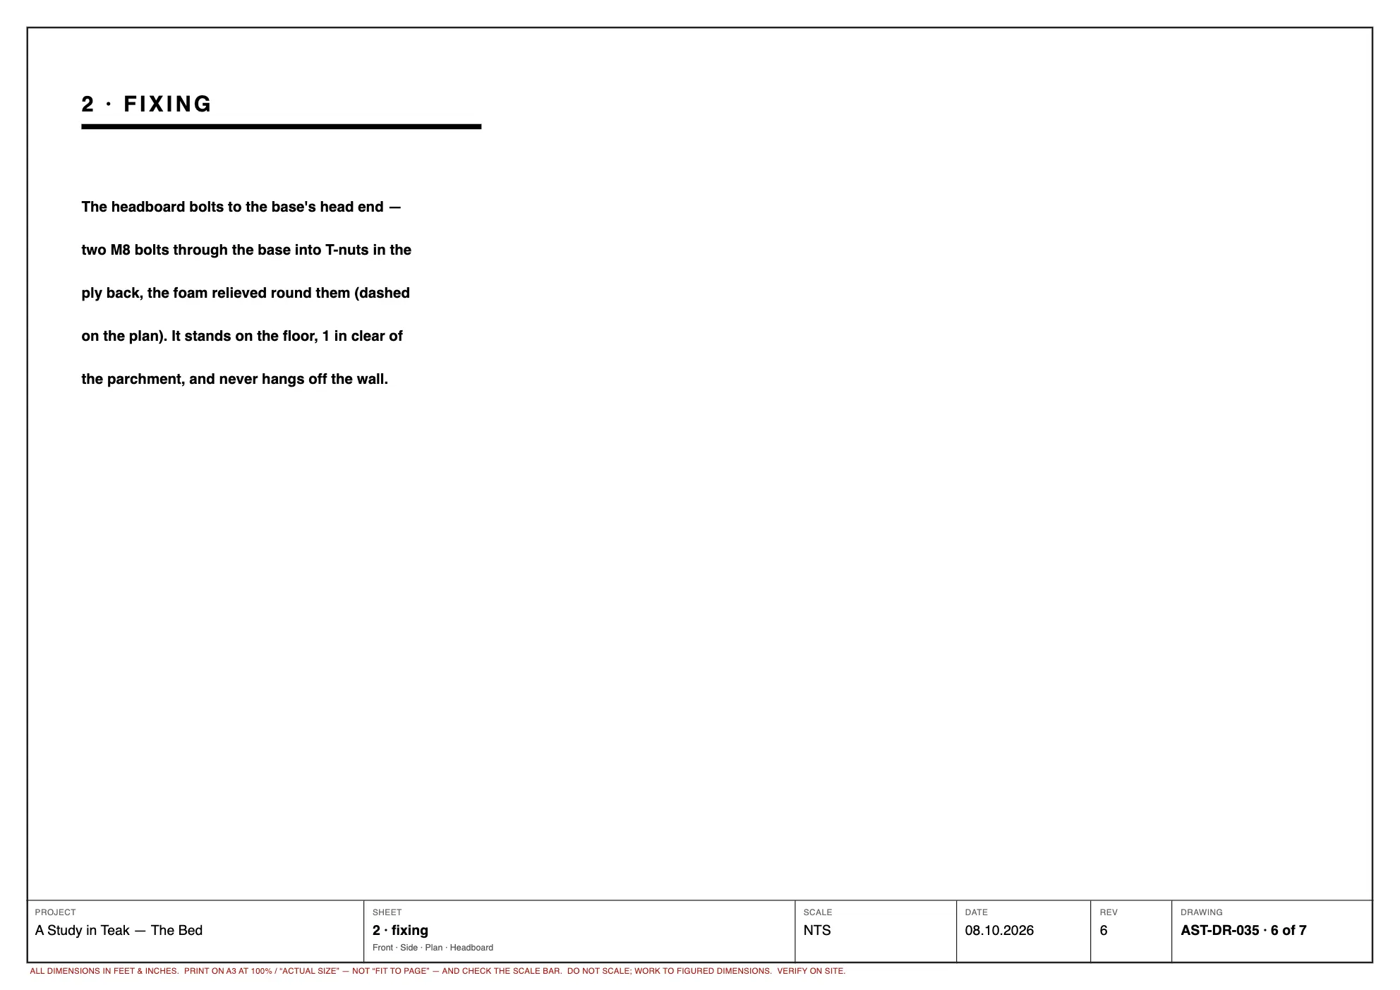
cad/print/bedframe-06.webp
