sakshampan733-cloud/a-study-in-teak/cad/print/bedframe-07.webp

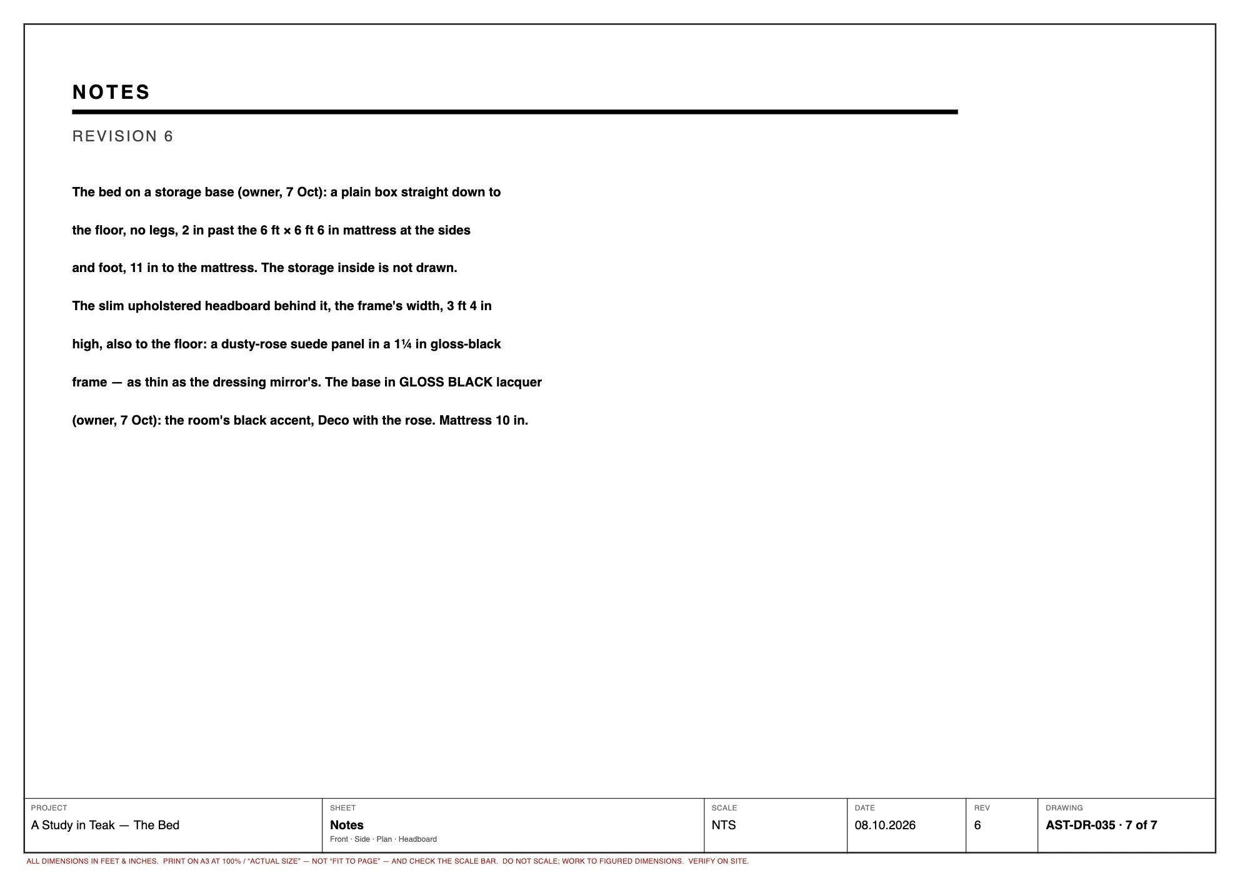
cad/print/bedframe-07.webp
