sakshampan733-cloud/a-study-in-teak/cad/print/bedwall-01.webp

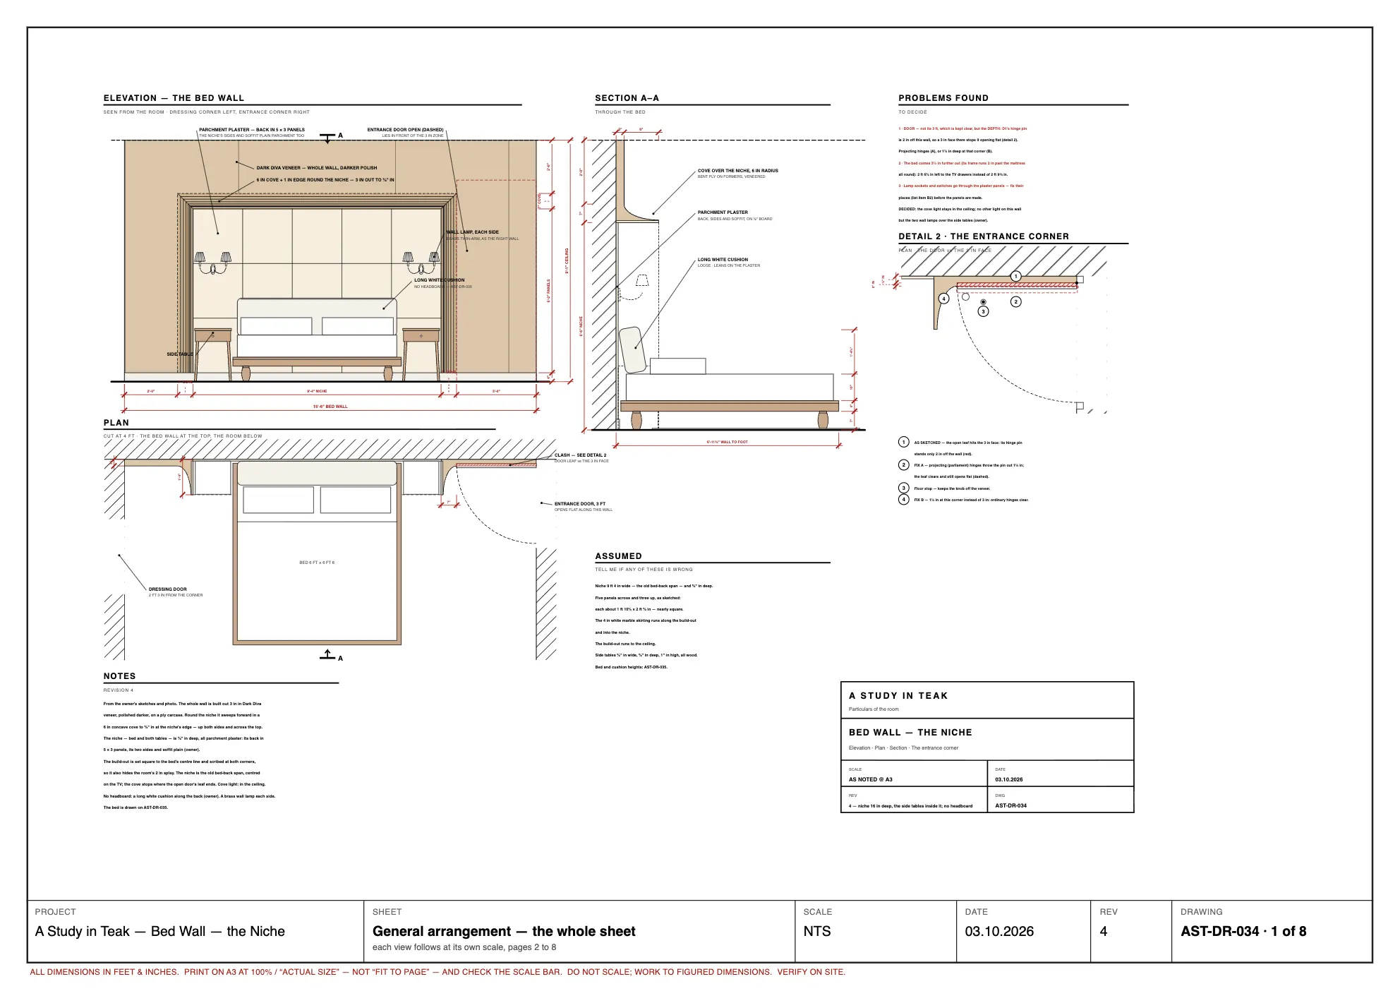
cad/print/bedwall-01.webp
