sakshampan733-cloud/a-study-in-teak/cad/print/bedwall-04.webp

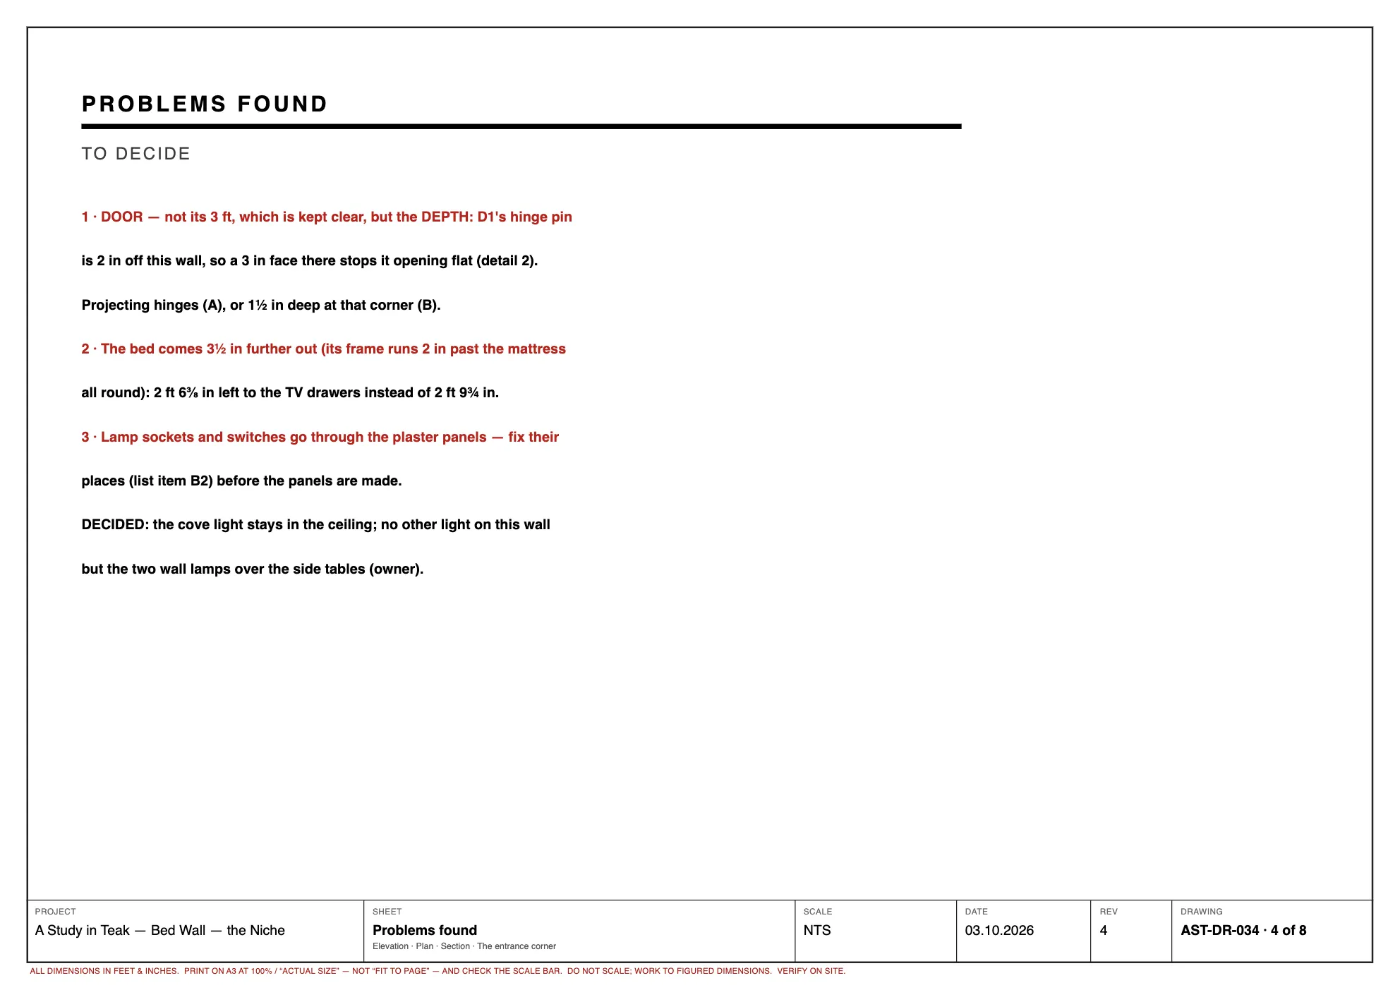
cad/print/bedwall-04.webp
