sakshampan733-cloud/a-study-in-teak/cad/print/bedwall-06.webp

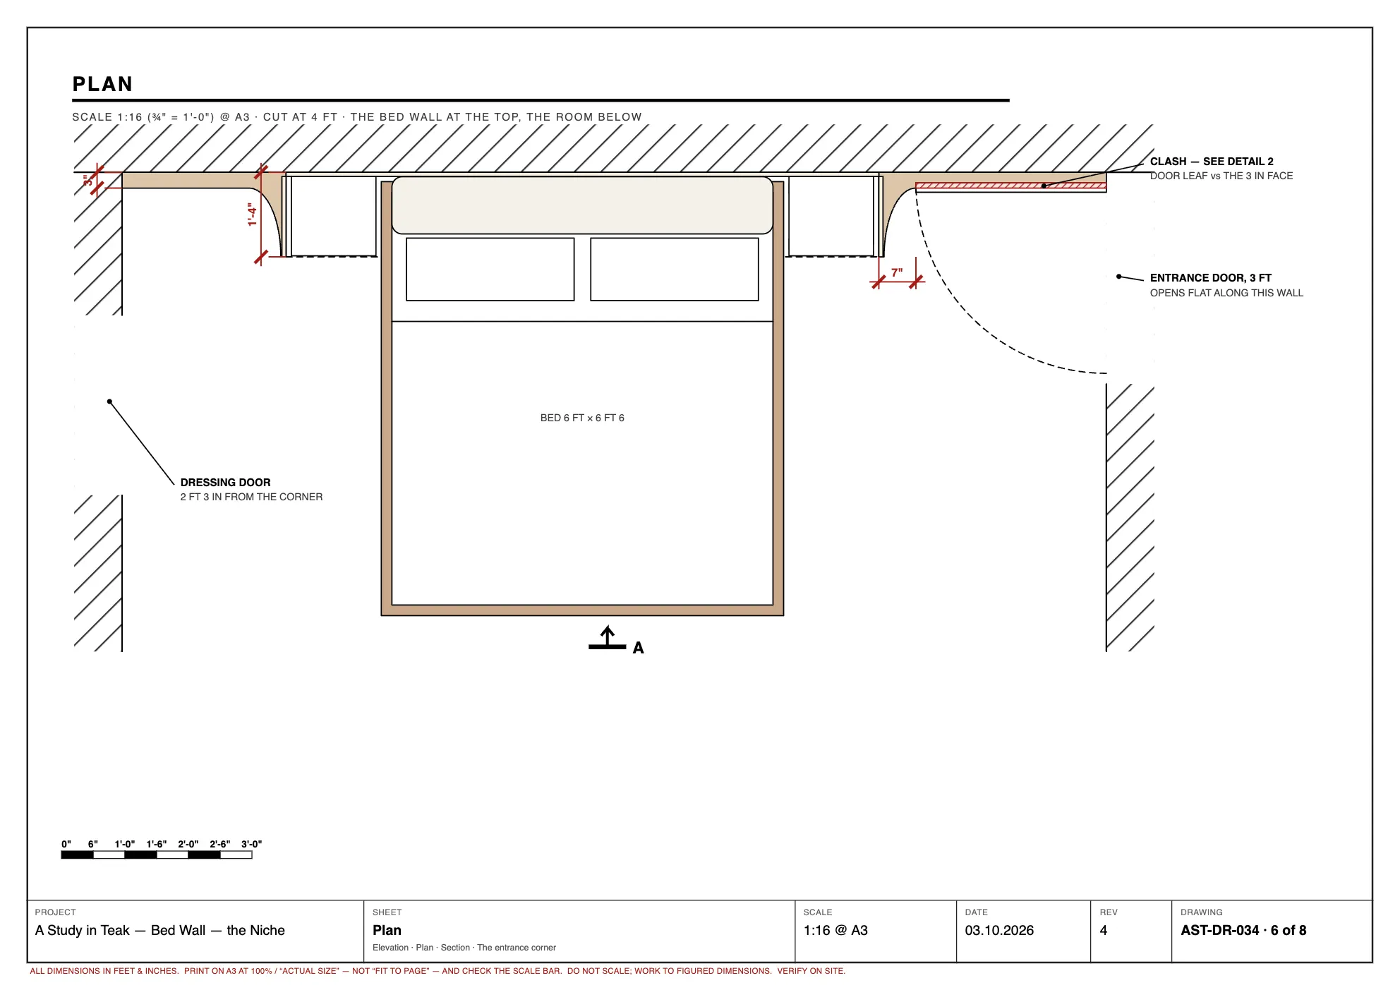
cad/print/bedwall-06.webp
