sakshampan733-cloud/a-study-in-teak/cad/print/bedwall-07.webp

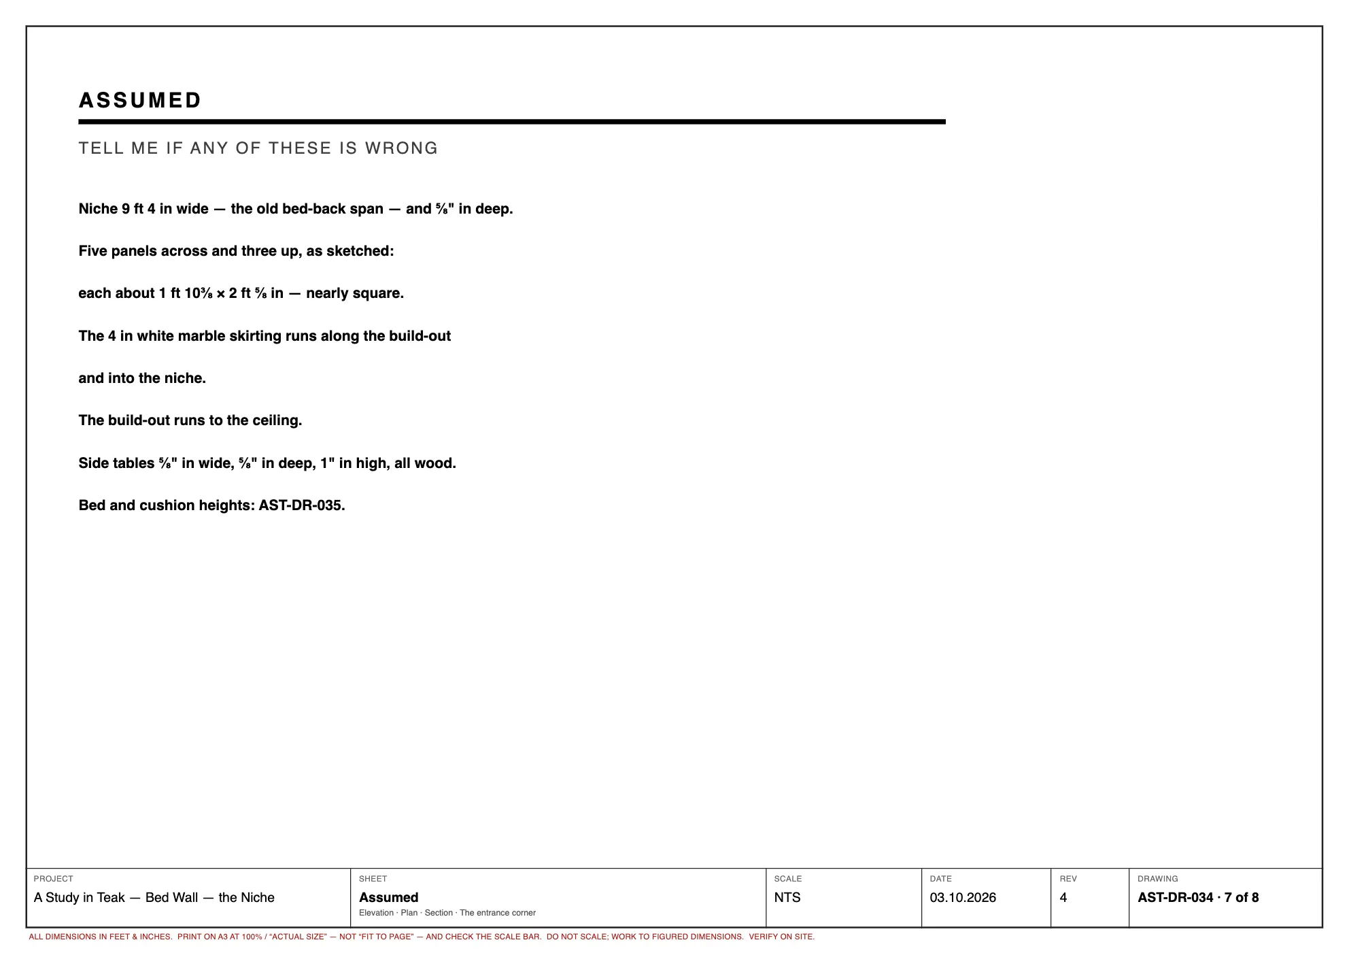
cad/print/bedwall-07.webp
