sakshampan733-cloud/a-study-in-teak/cad/print/bedwall-08.webp

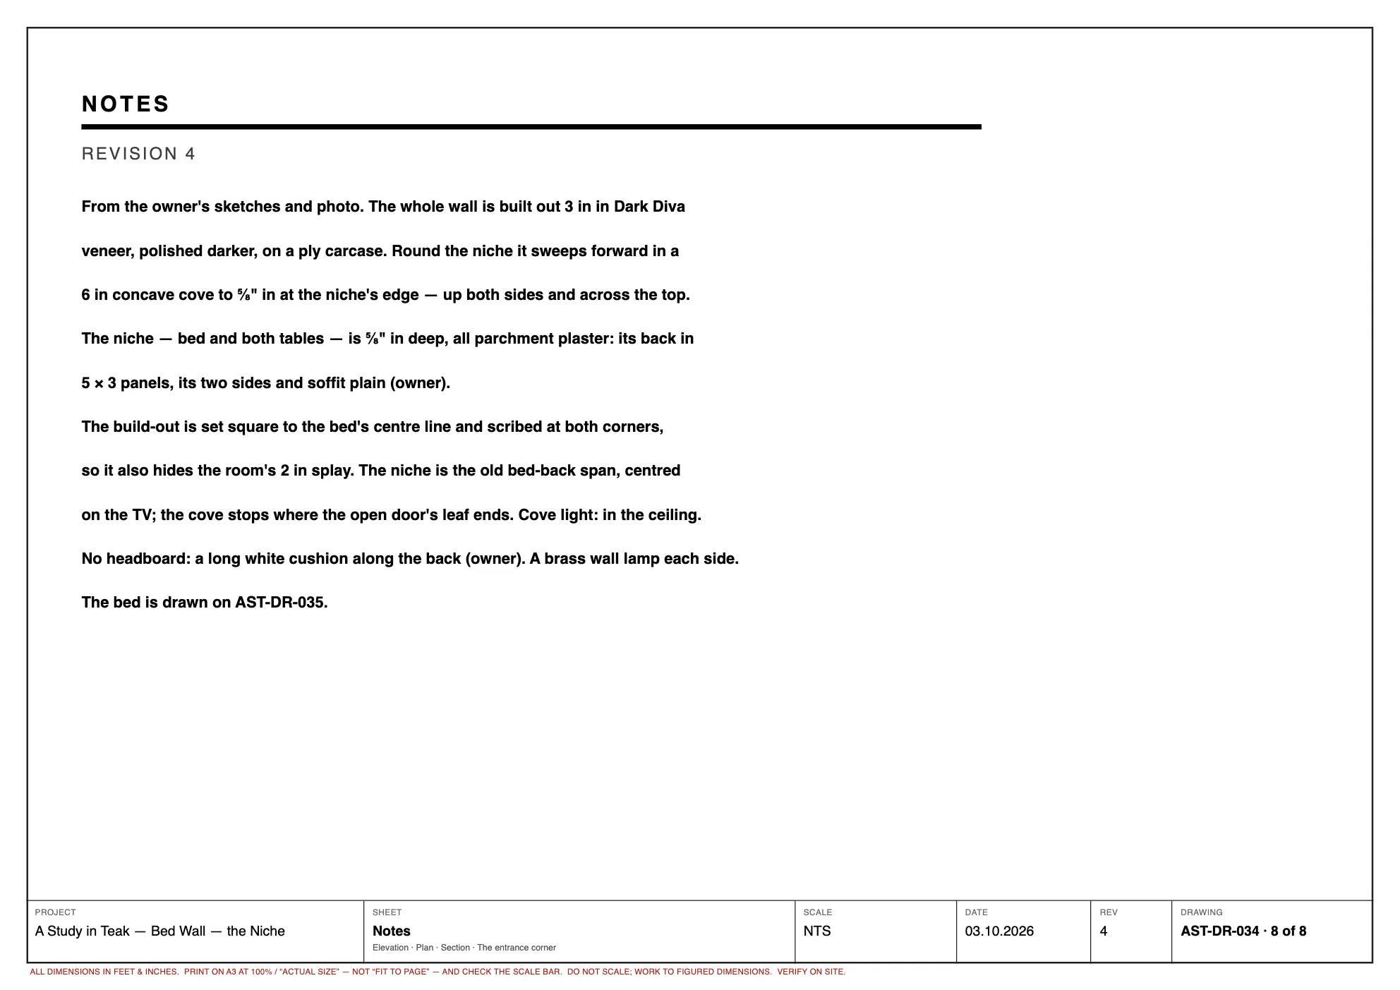
cad/print/bedwall-08.webp
