sakshampan733-cloud/a-study-in-teak/cad/print/casingb-01.webp

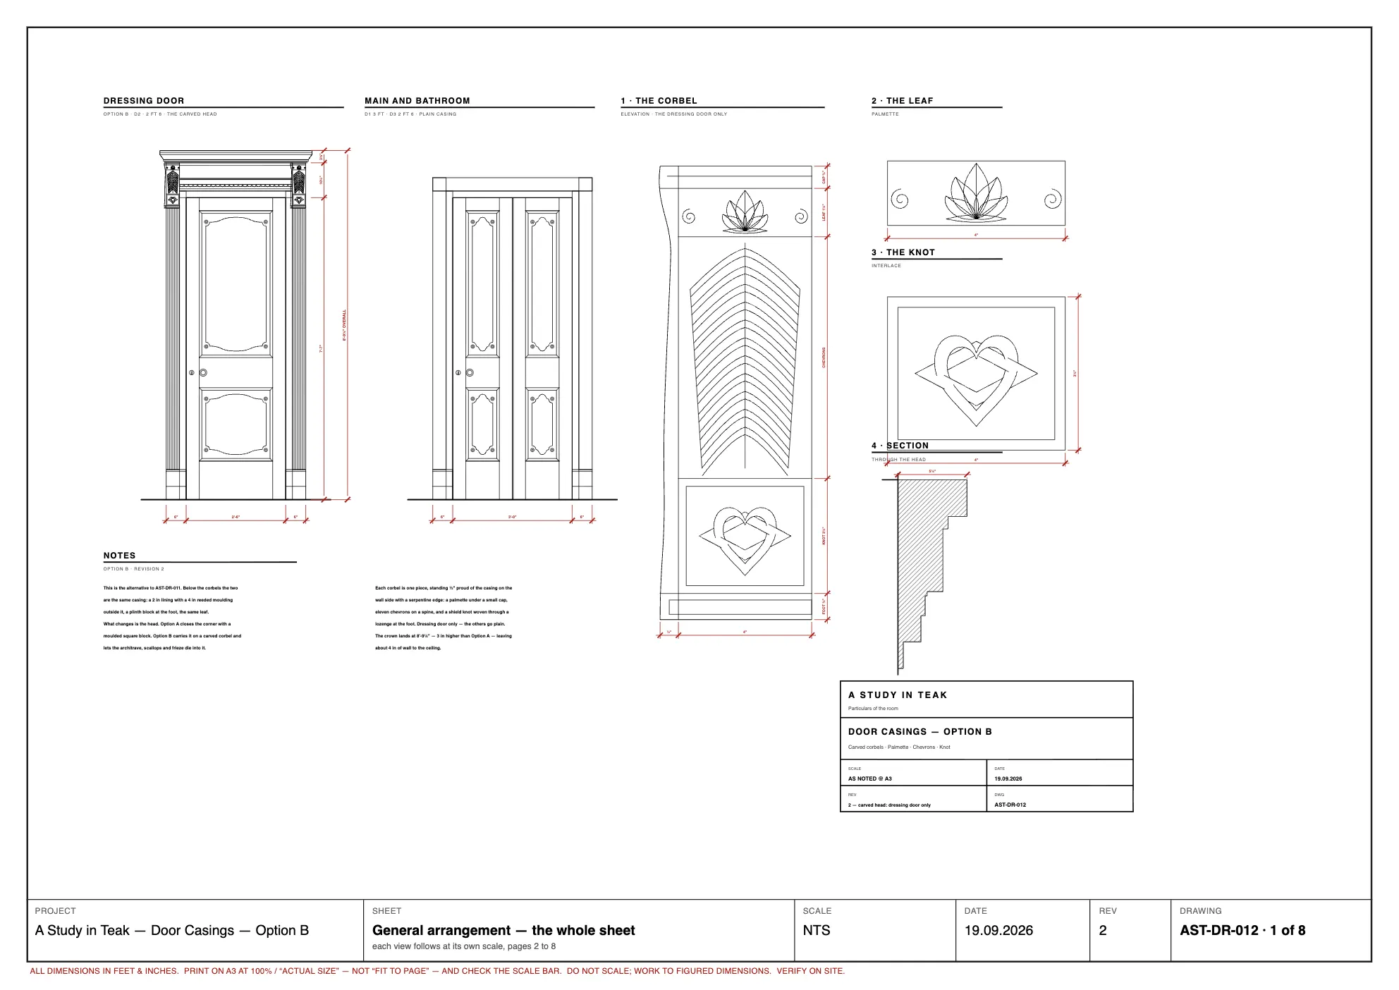
cad/print/casingb-01.webp
