sakshampan733-cloud/a-study-in-teak/cad/print/casingb-03.webp

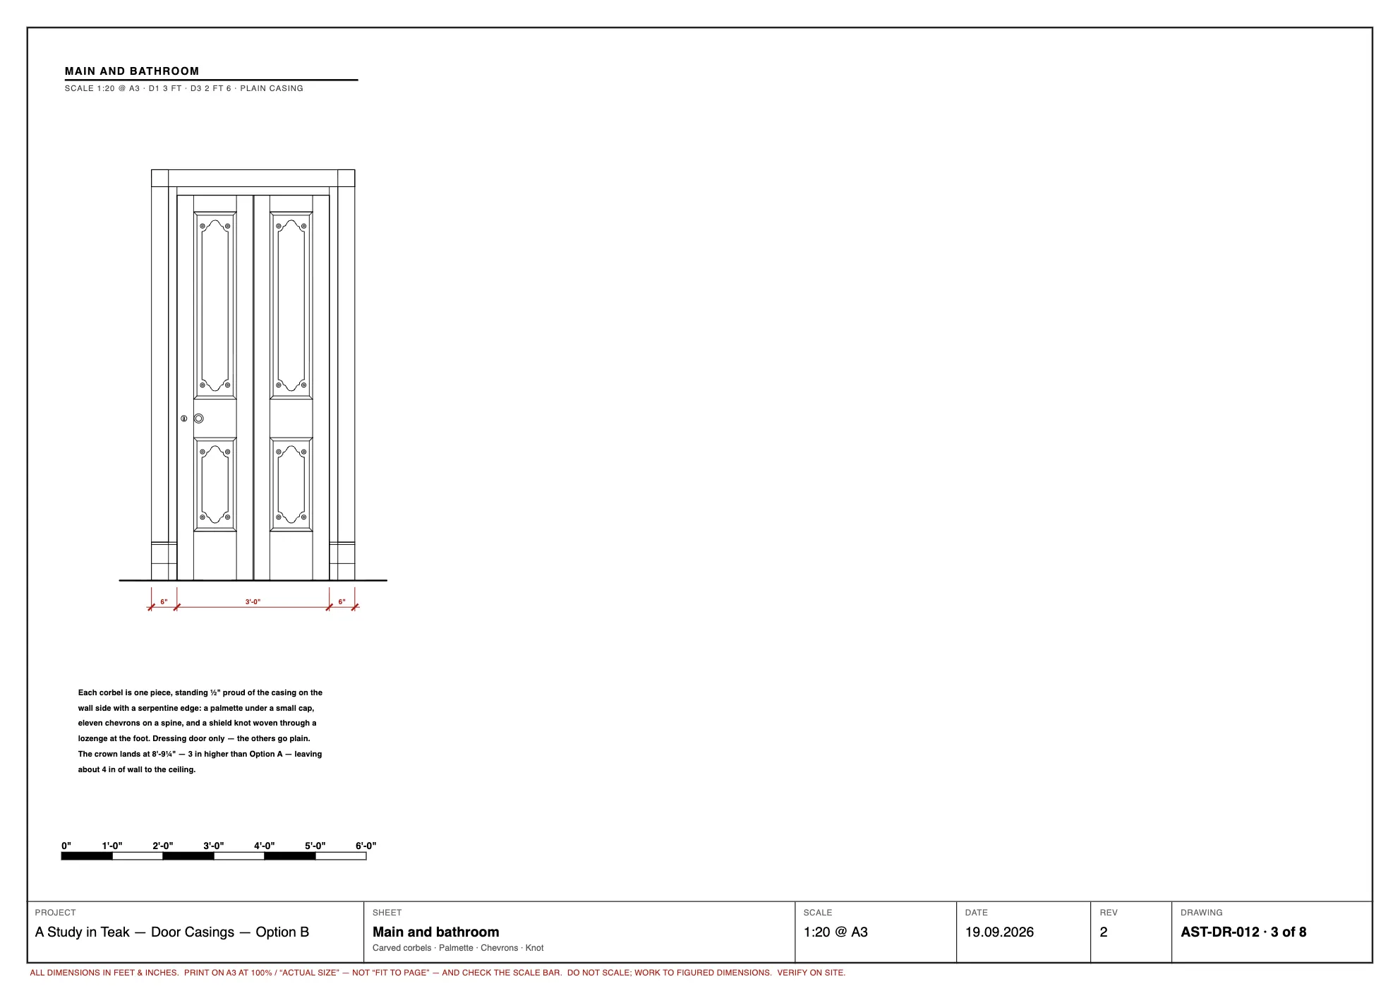
cad/print/casingb-03.webp
