sakshampan733-cloud/a-study-in-teak/cad/print/casingb-06.webp

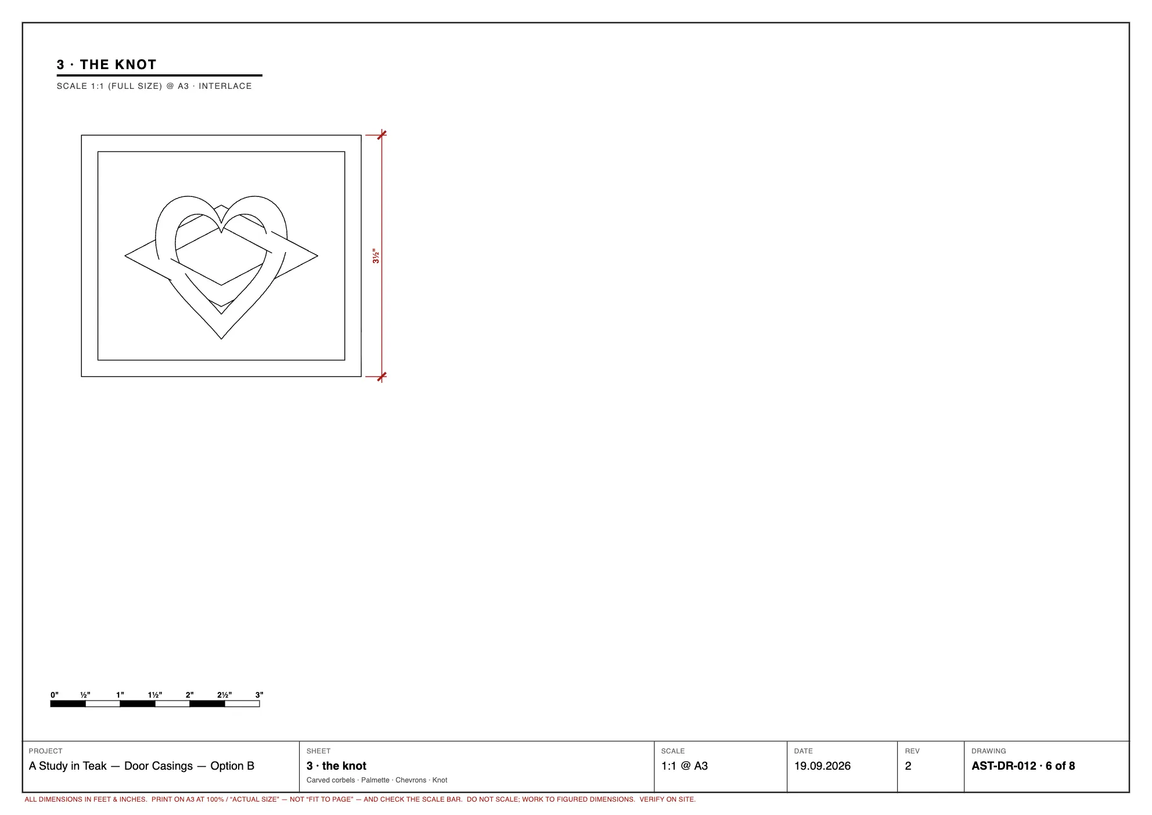
cad/print/casingb-06.webp
