sakshampan733-cloud/a-study-in-teak/cad/print/casingb-07.webp

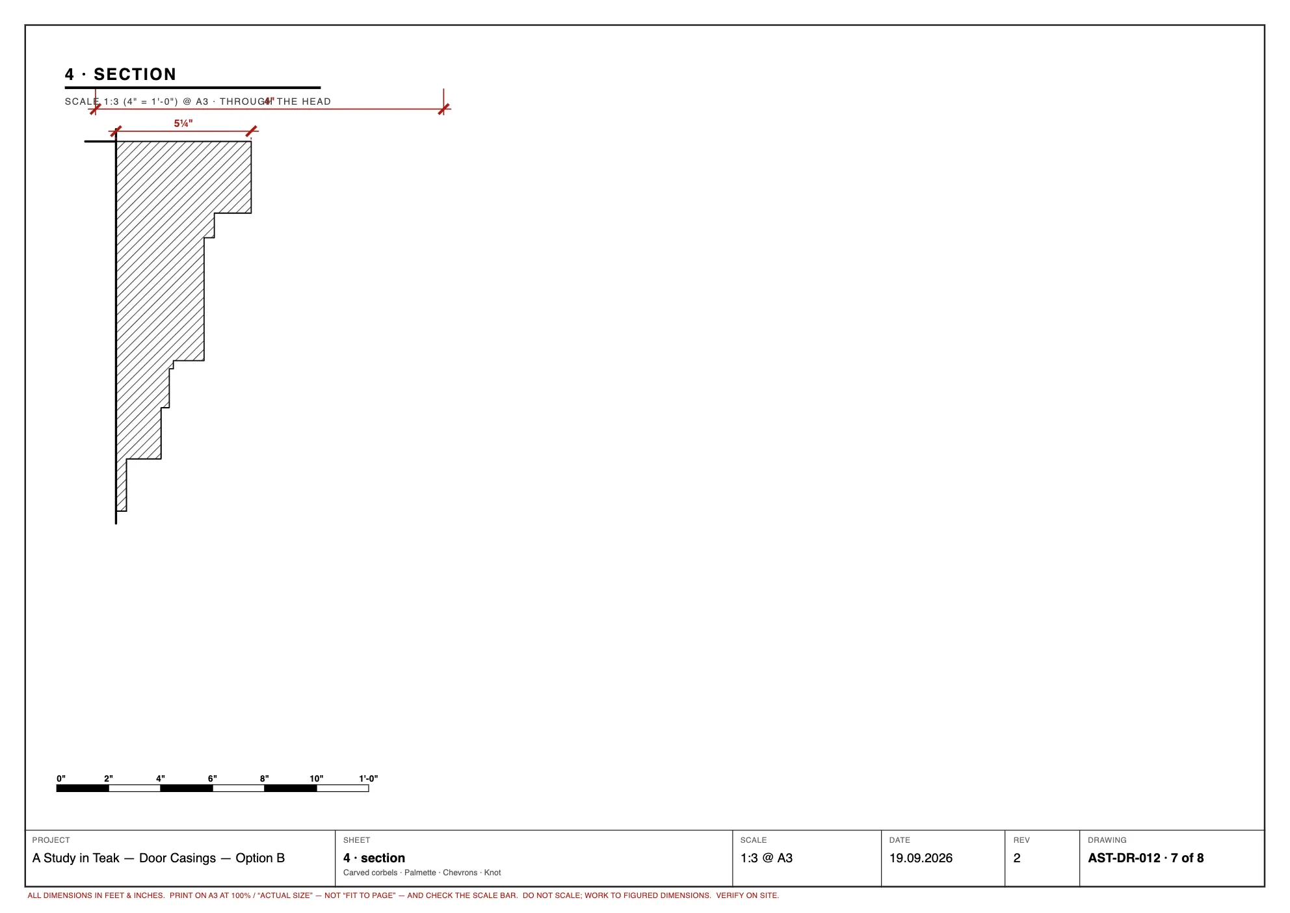
cad/print/casingb-07.webp
