sakshampan733-cloud/a-study-in-teak/cad/print/casingb-08.webp

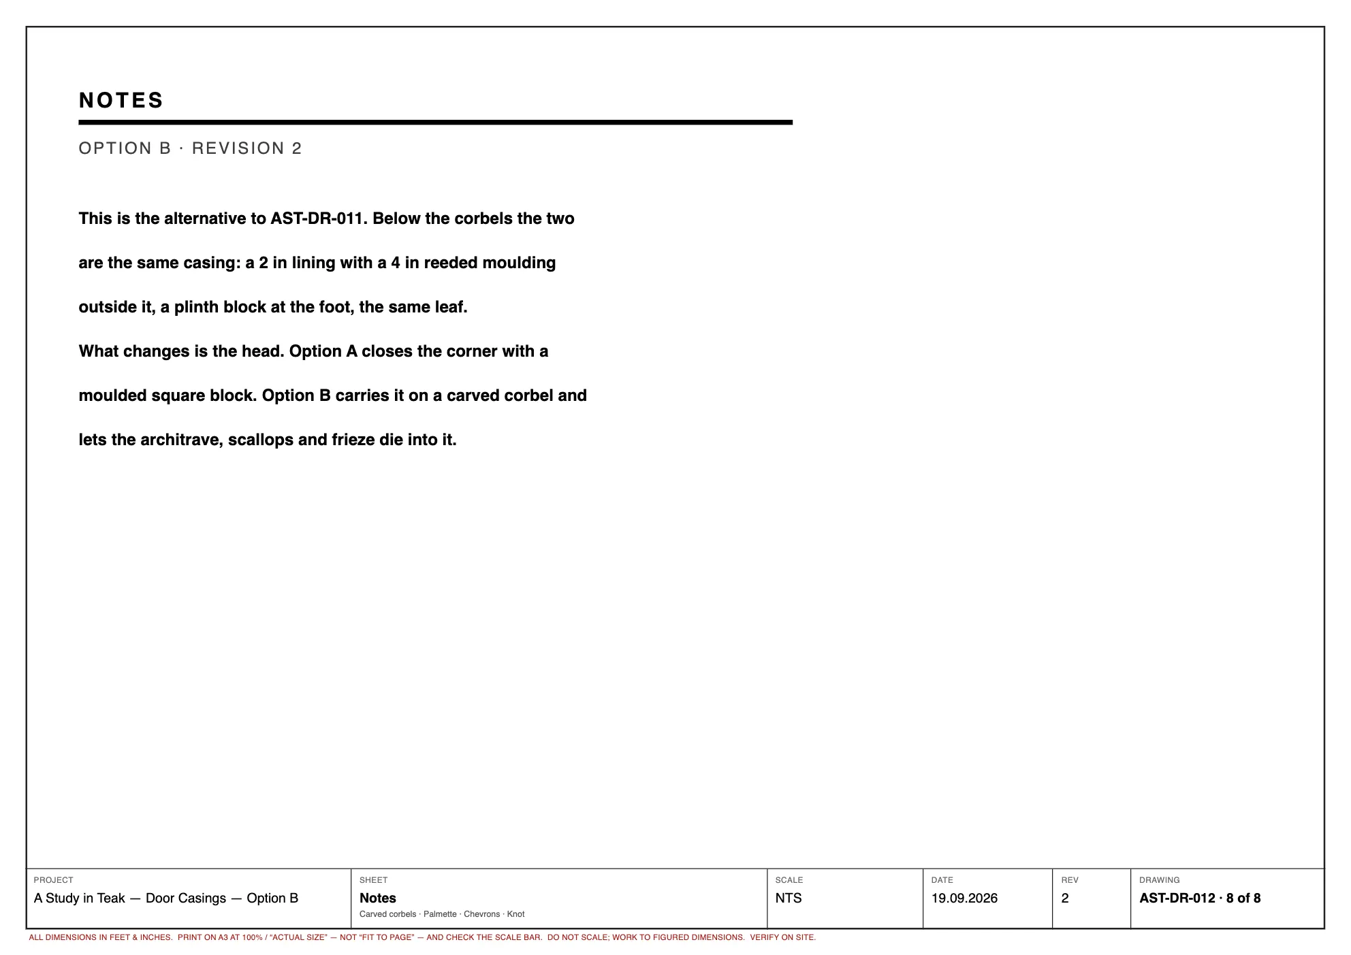
cad/print/casingb-08.webp
