sakshampan733-cloud/a-study-in-teak/cad/print/desk-01.webp

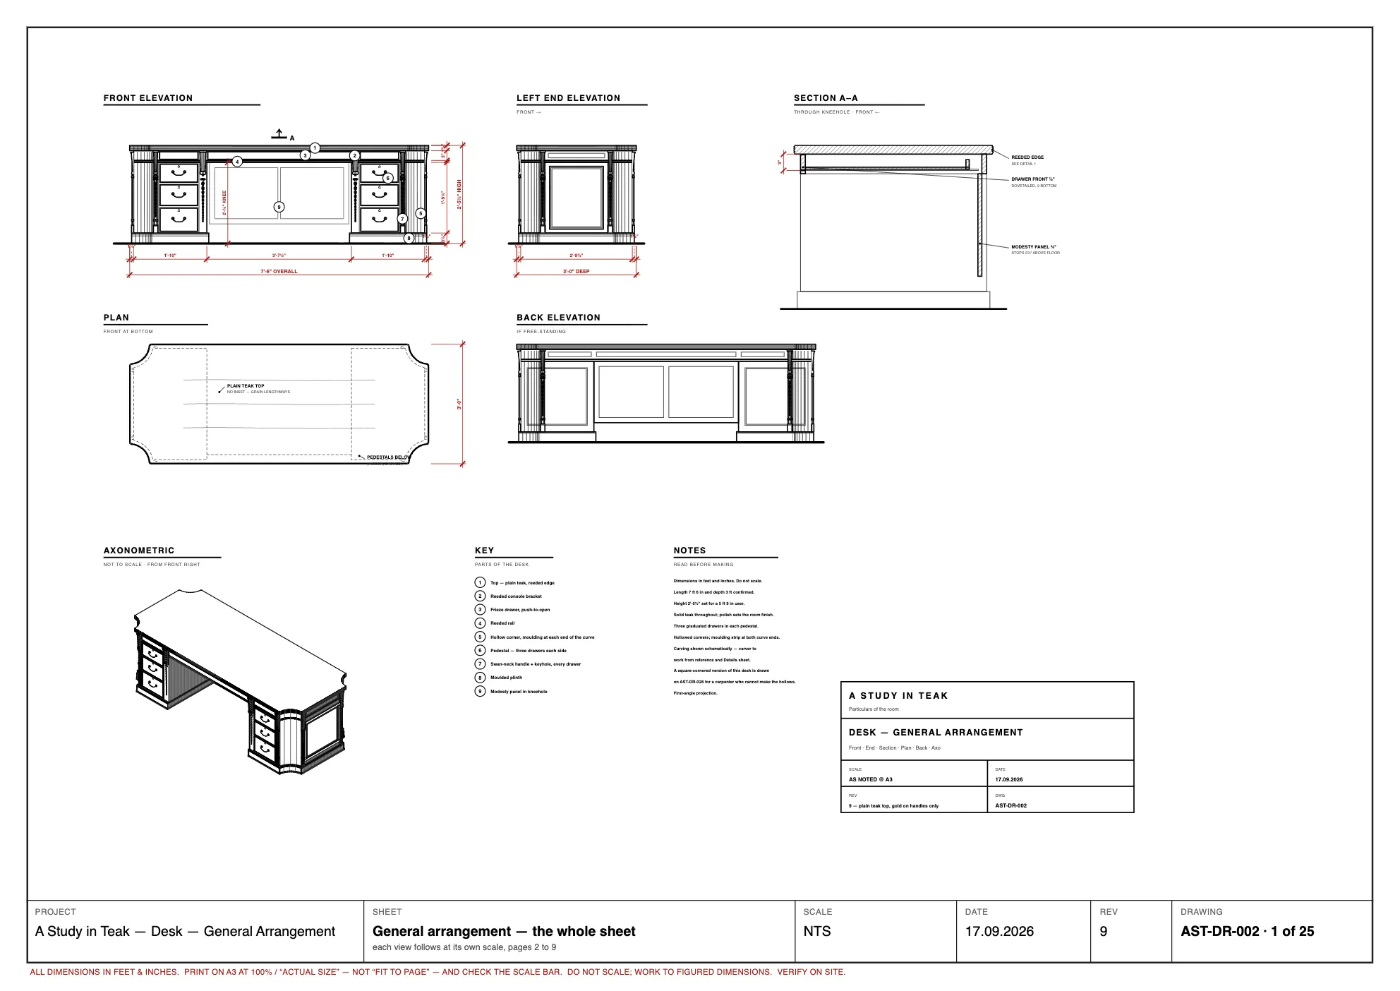
cad/print/desk-01.webp
