sakshampan733-cloud/a-study-in-teak/cad/print/desk-02.webp

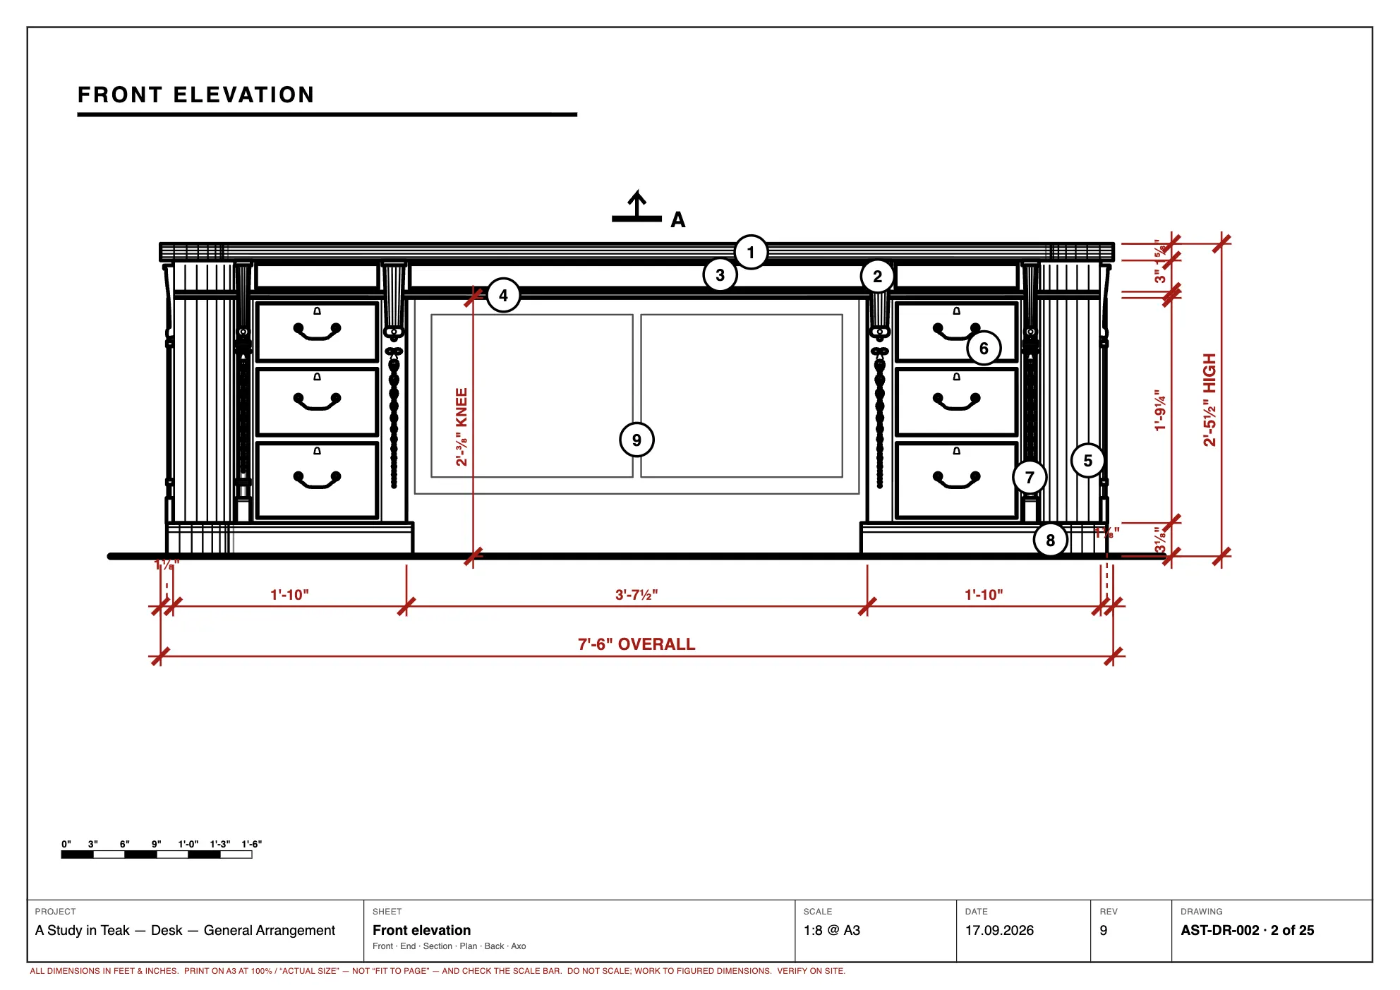
cad/print/desk-02.webp
