sakshampan733-cloud/a-study-in-teak/cad/print/desk-04.webp

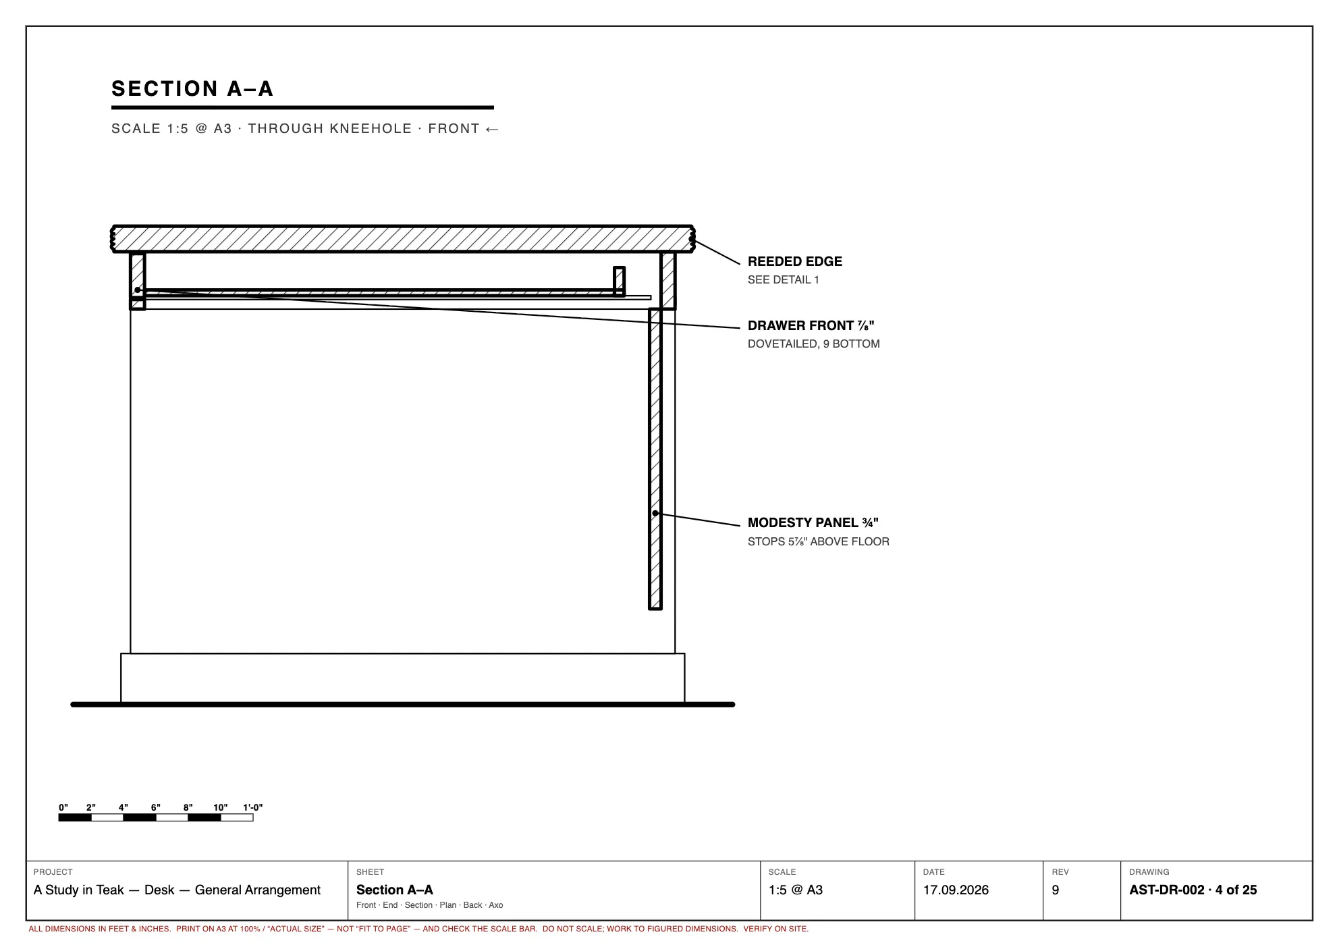
cad/print/desk-04.webp
