sakshampan733-cloud/a-study-in-teak/cad/print/desk-05.webp

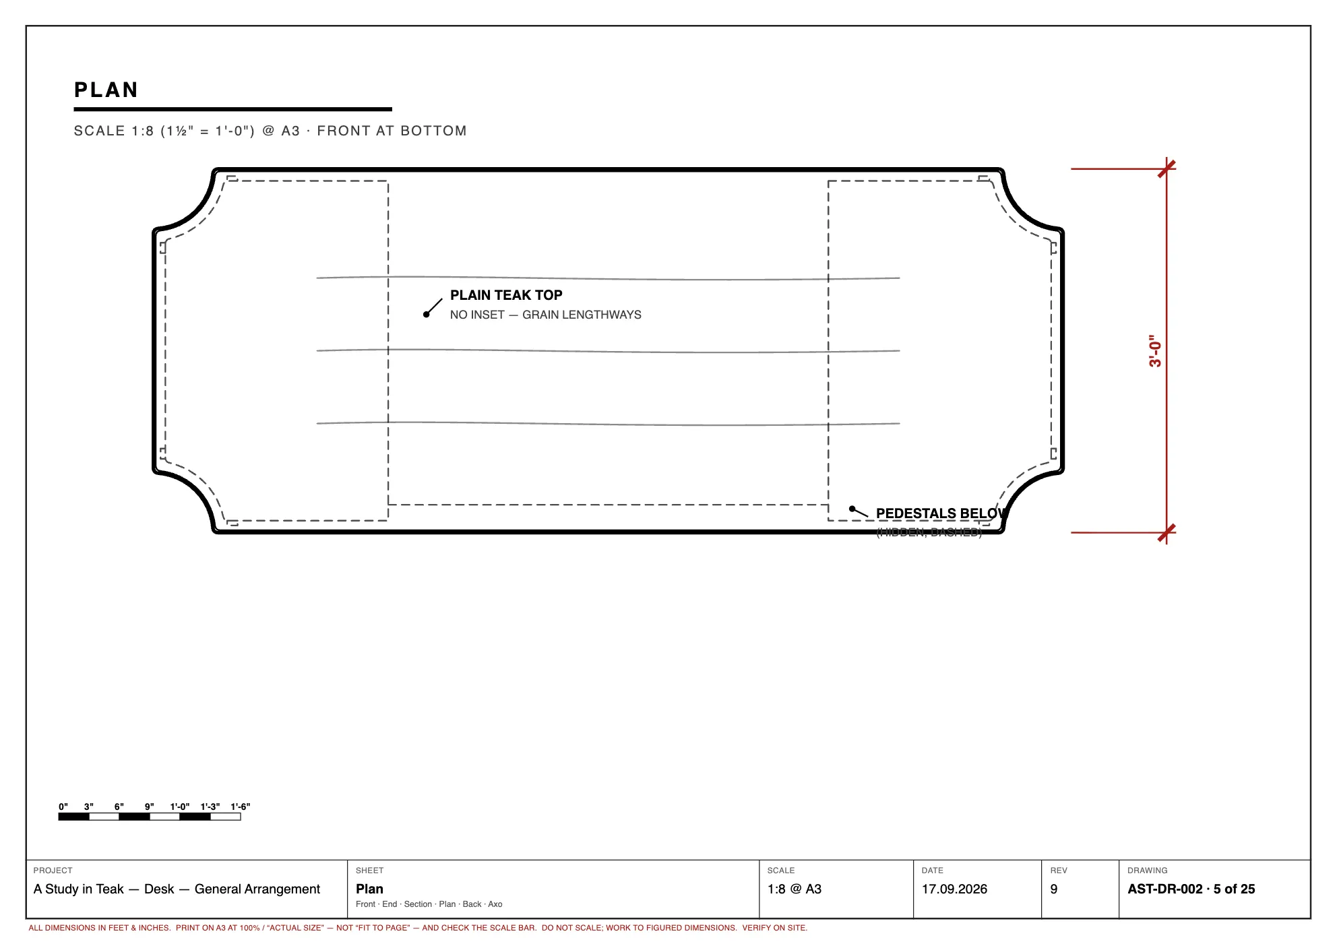
cad/print/desk-05.webp
