sakshampan733-cloud/a-study-in-teak/cad/print/desk-06.webp

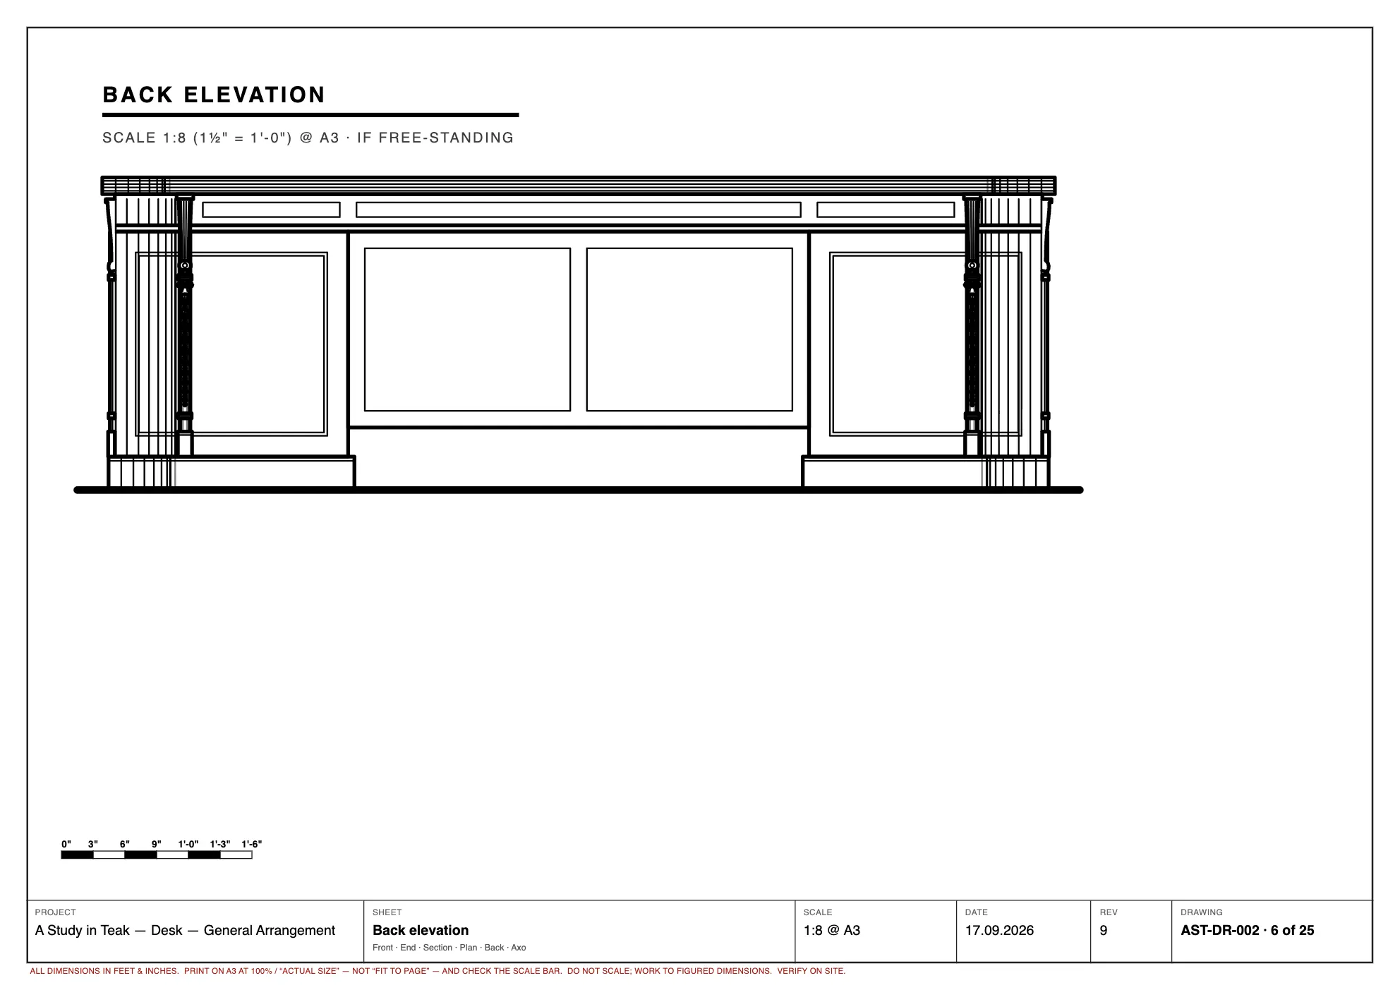
cad/print/desk-06.webp
