sakshampan733-cloud/a-study-in-teak/cad/print/desk-07.webp

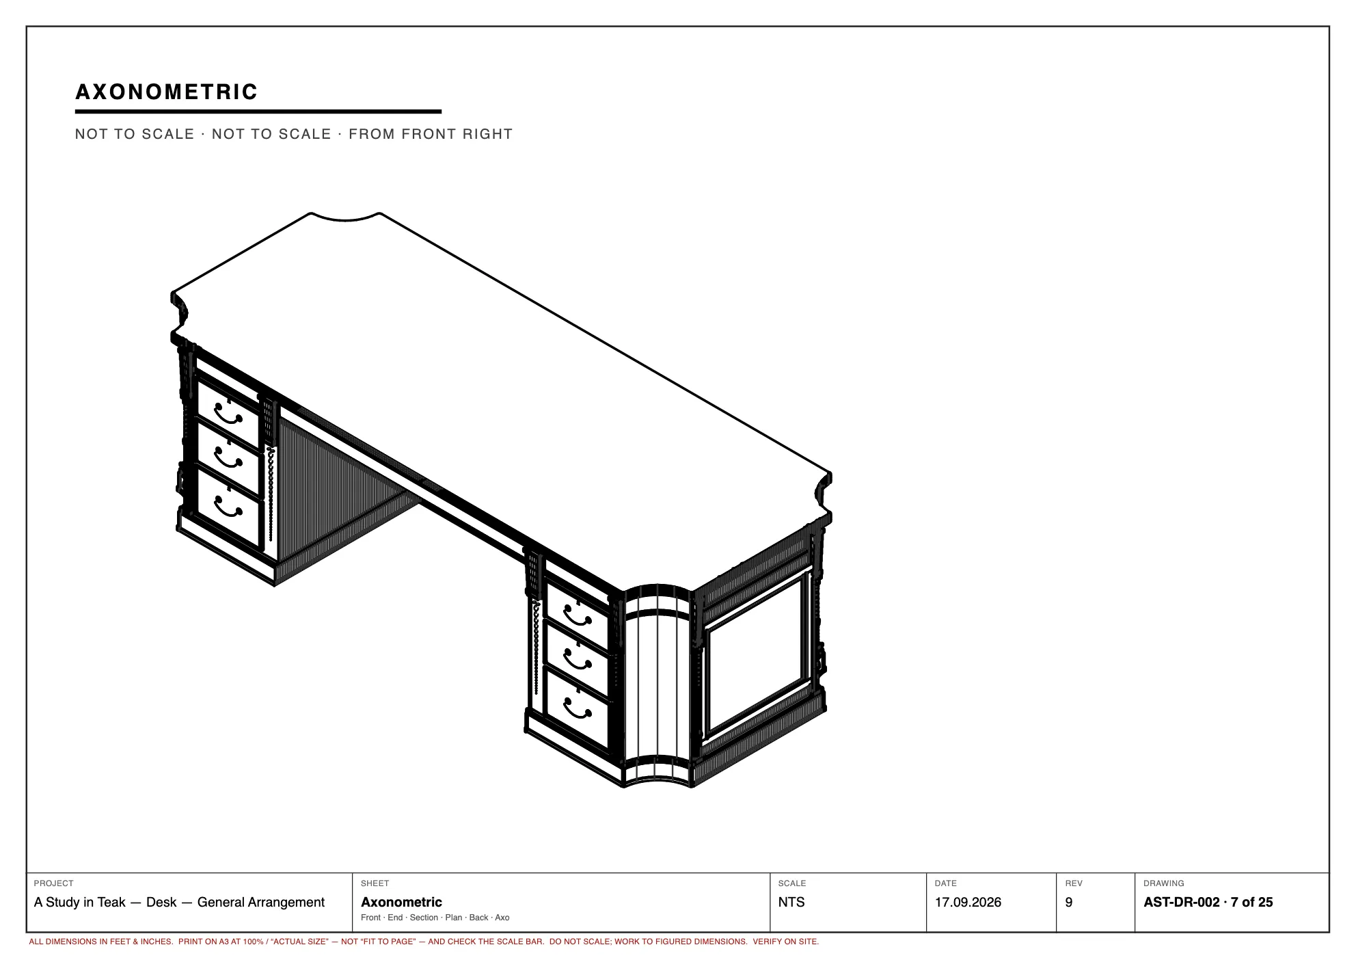
cad/print/desk-07.webp
