sakshampan733-cloud/a-study-in-teak/cad/print/desk-08.webp

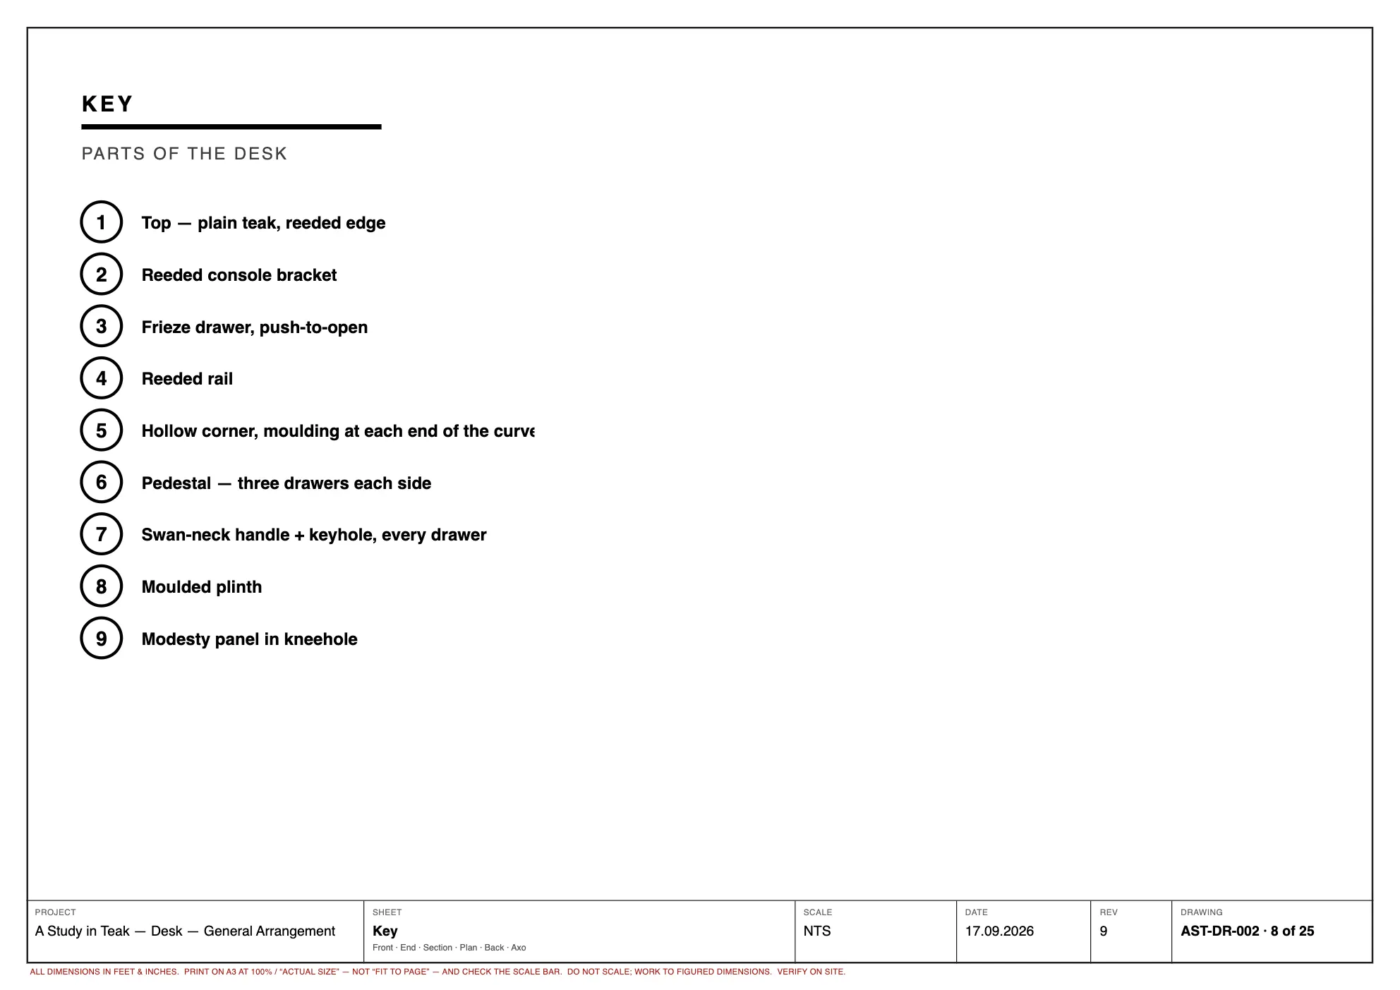
cad/print/desk-08.webp
