sakshampan733-cloud/a-study-in-teak/cad/print/desk-09.webp

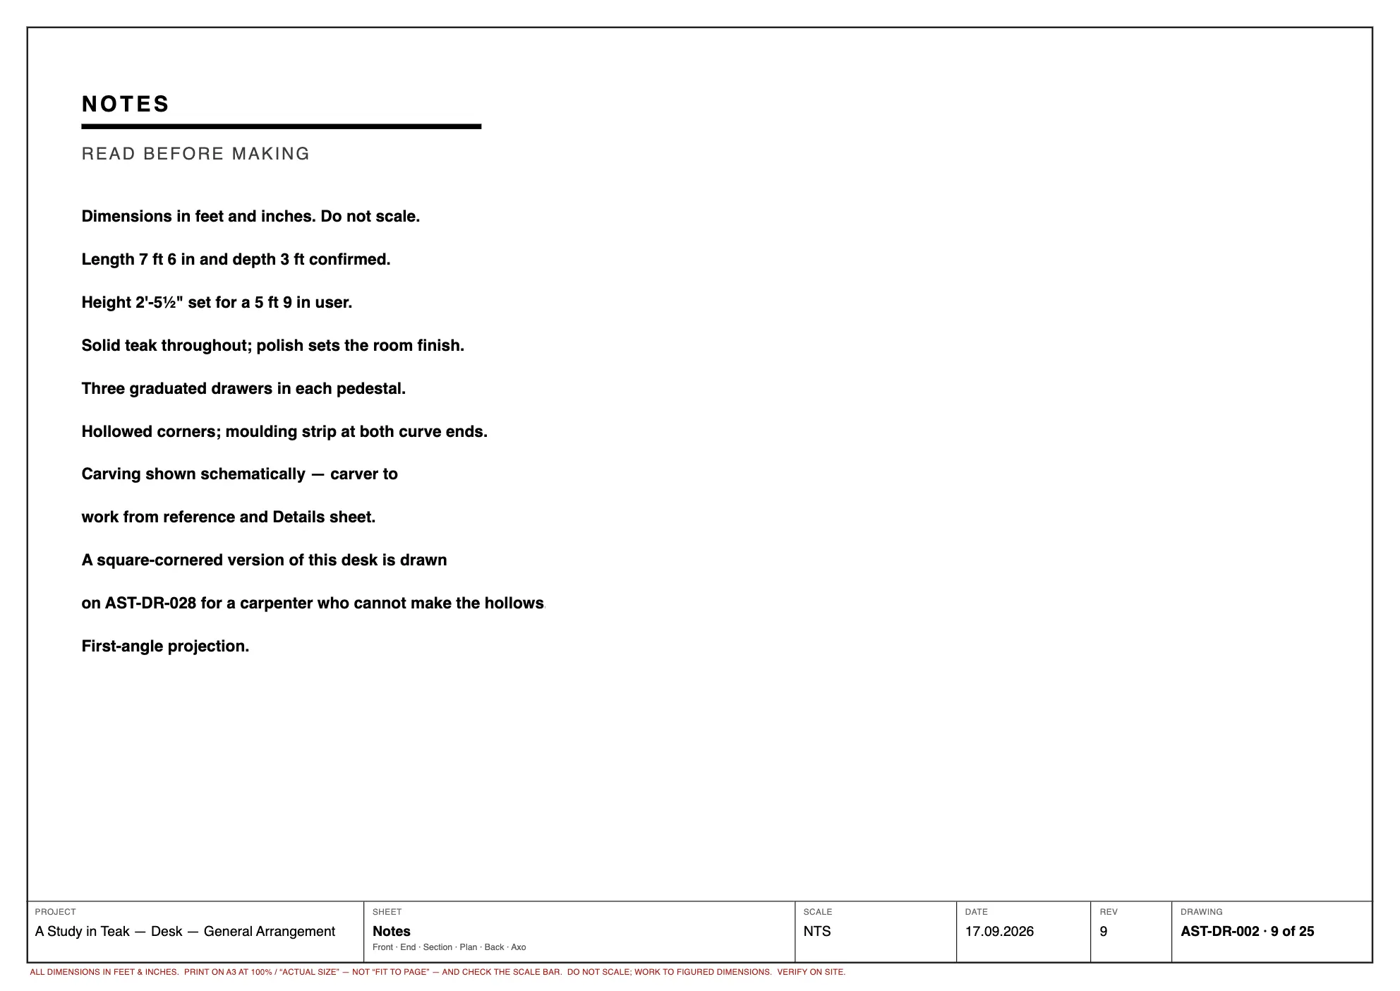
cad/print/desk-09.webp
