sakshampan733-cloud/a-study-in-teak/cad/print/desk-10.webp

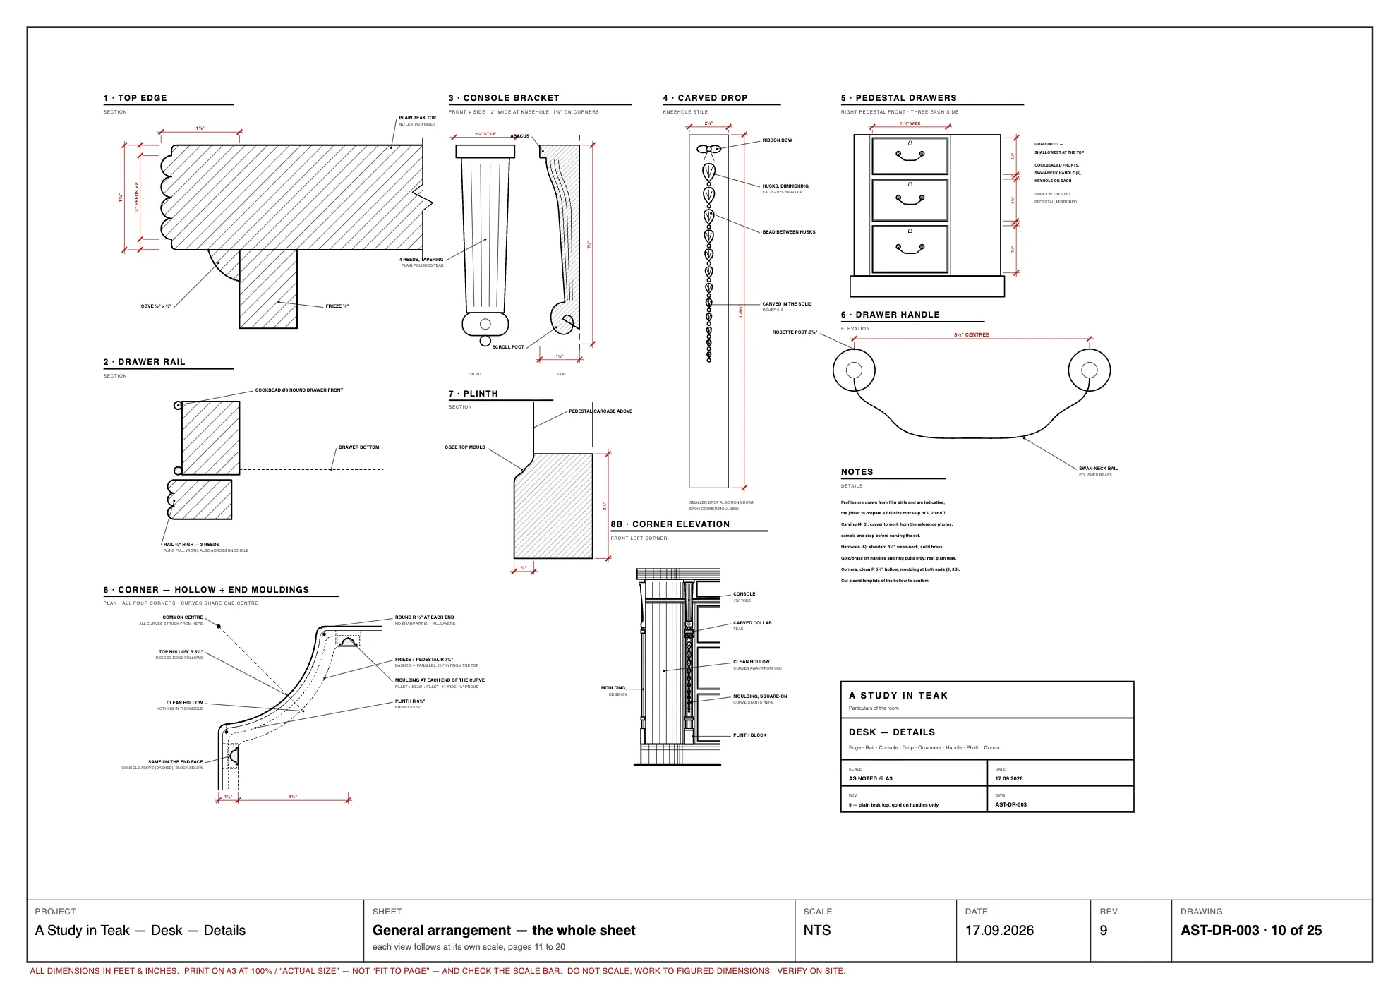
cad/print/desk-10.webp
