sakshampan733-cloud/a-study-in-teak/cad/print/desk-11.webp

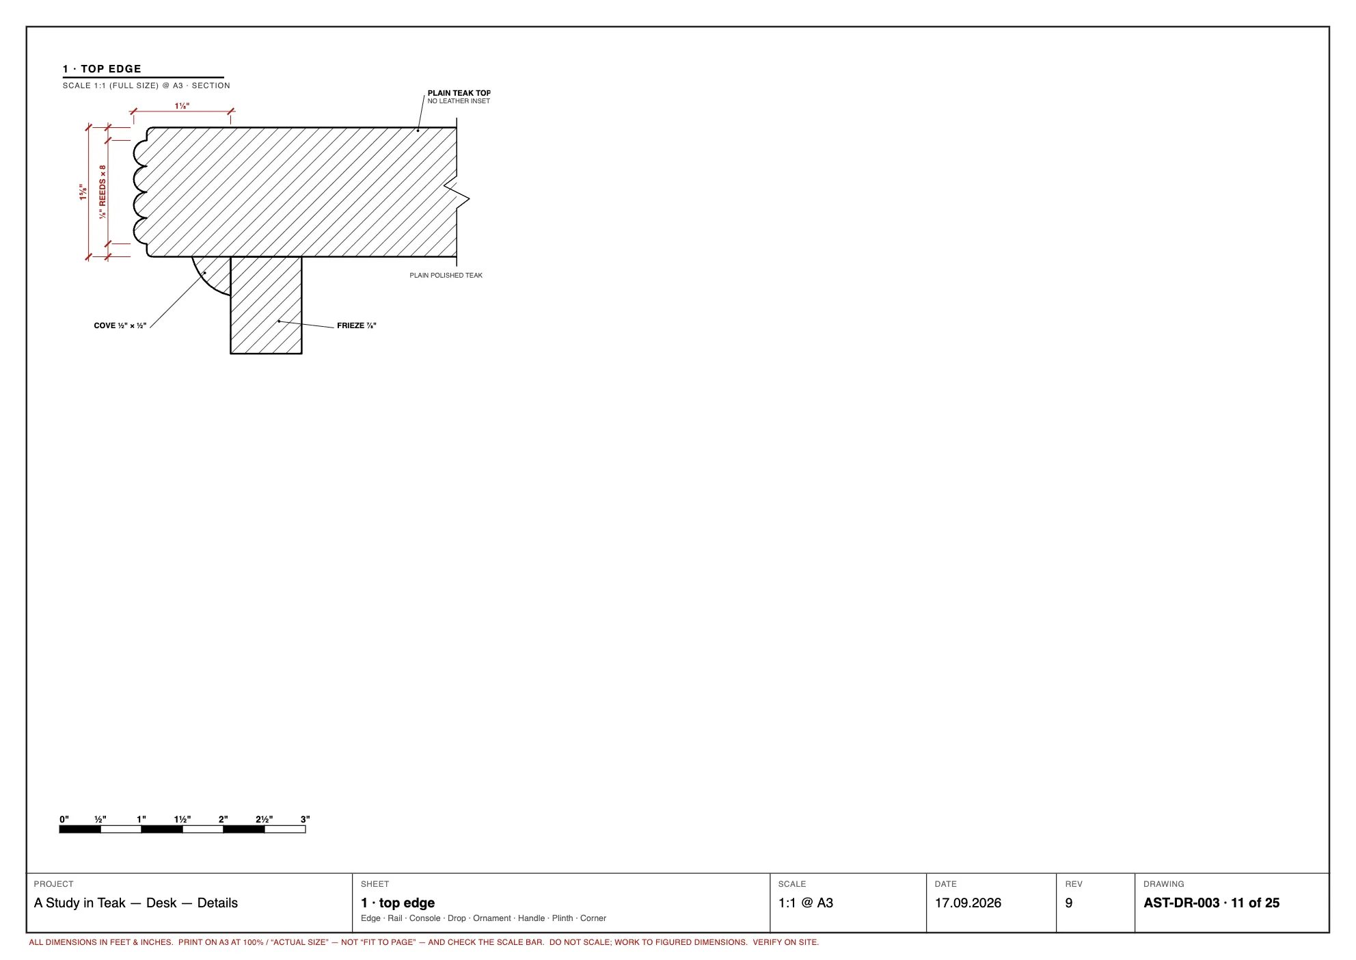
cad/print/desk-11.webp
