sakshampan733-cloud/a-study-in-teak/cad/print/desk-12.webp

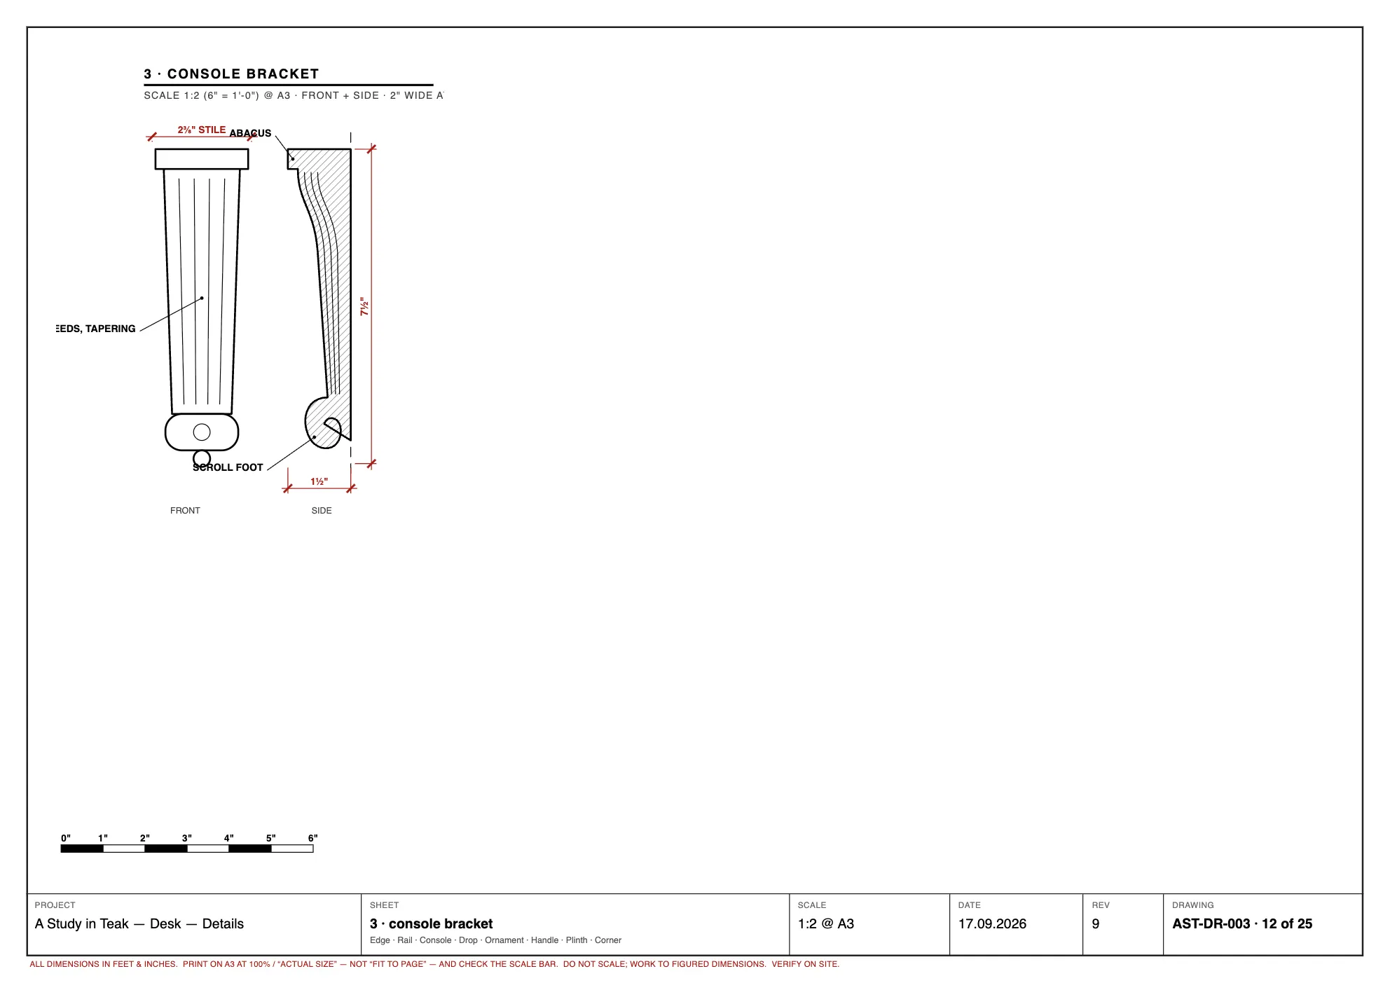
cad/print/desk-12.webp
