sakshampan733-cloud/a-study-in-teak/cad/print/desk-13.webp

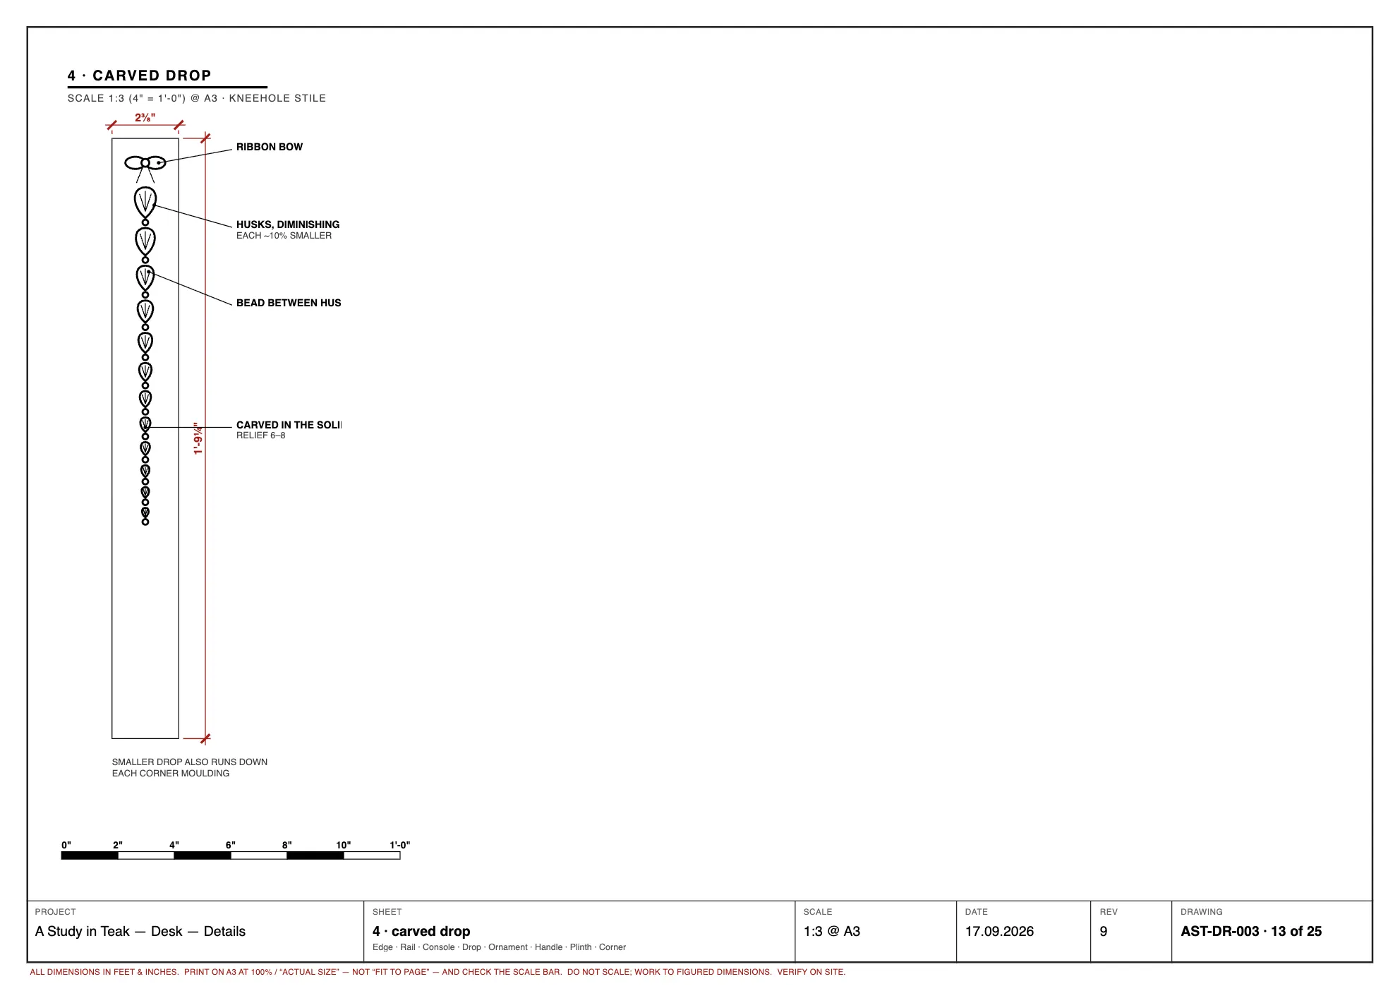
cad/print/desk-13.webp
