sakshampan733-cloud/a-study-in-teak/cad/print/desk-14.webp

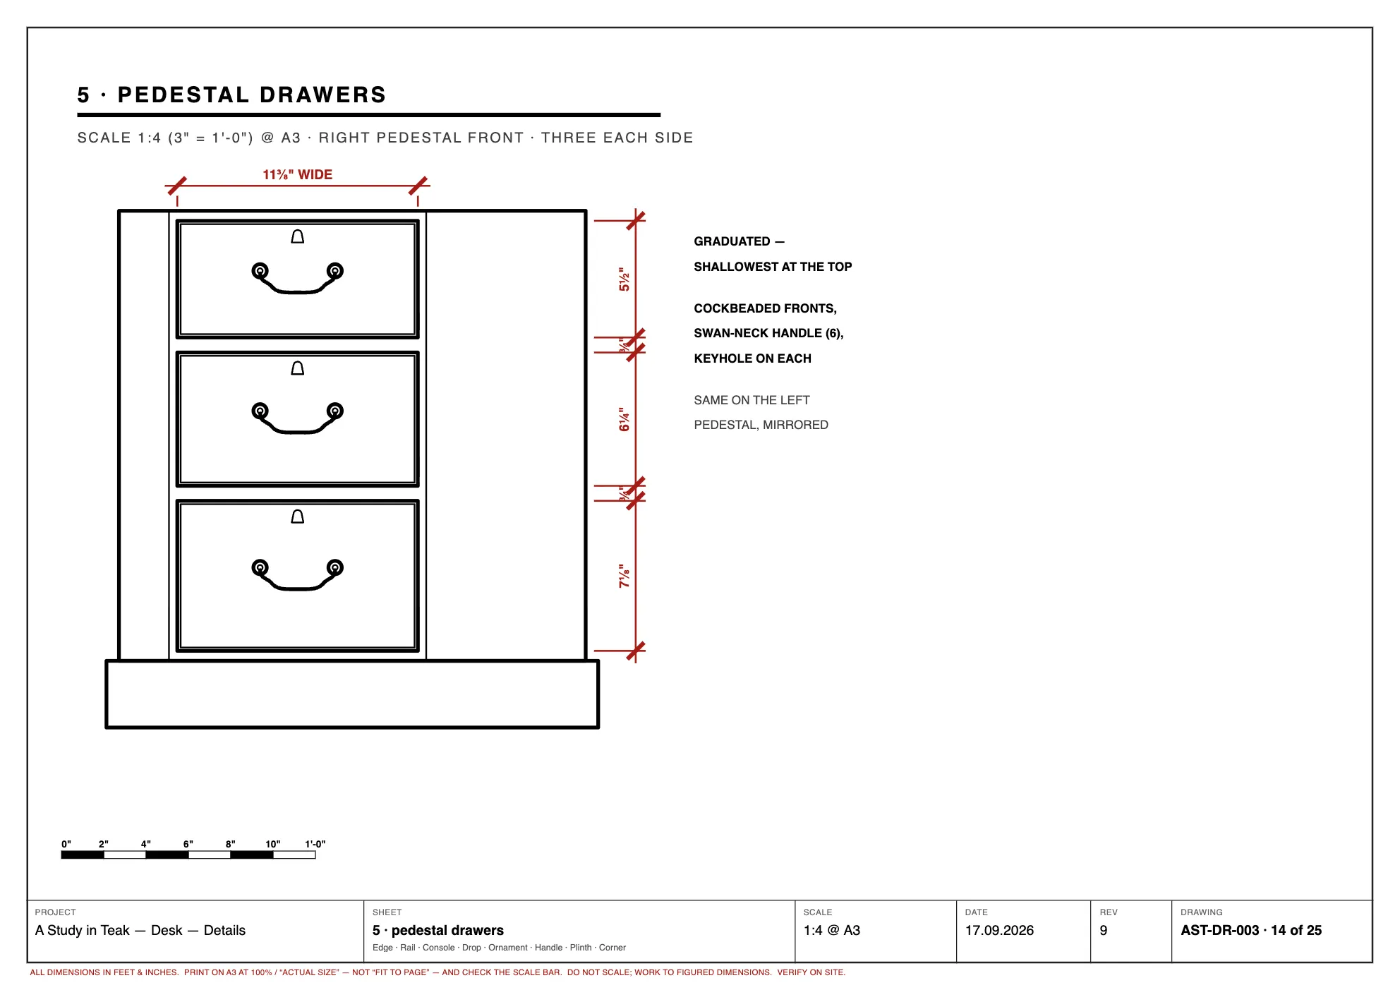
cad/print/desk-14.webp
