sakshampan733-cloud/a-study-in-teak/cad/print/desk-16.webp

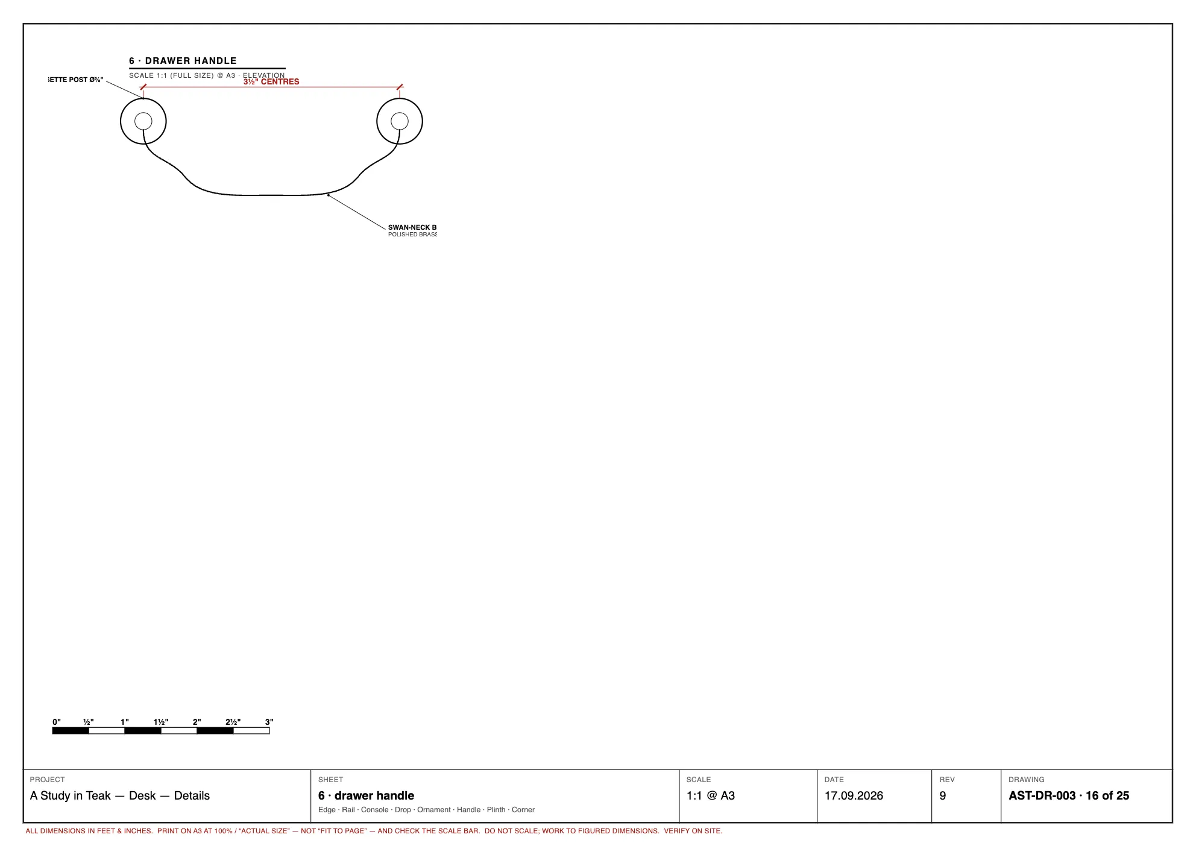
cad/print/desk-16.webp
