sakshampan733-cloud/a-study-in-teak/cad/print/desk-17.webp

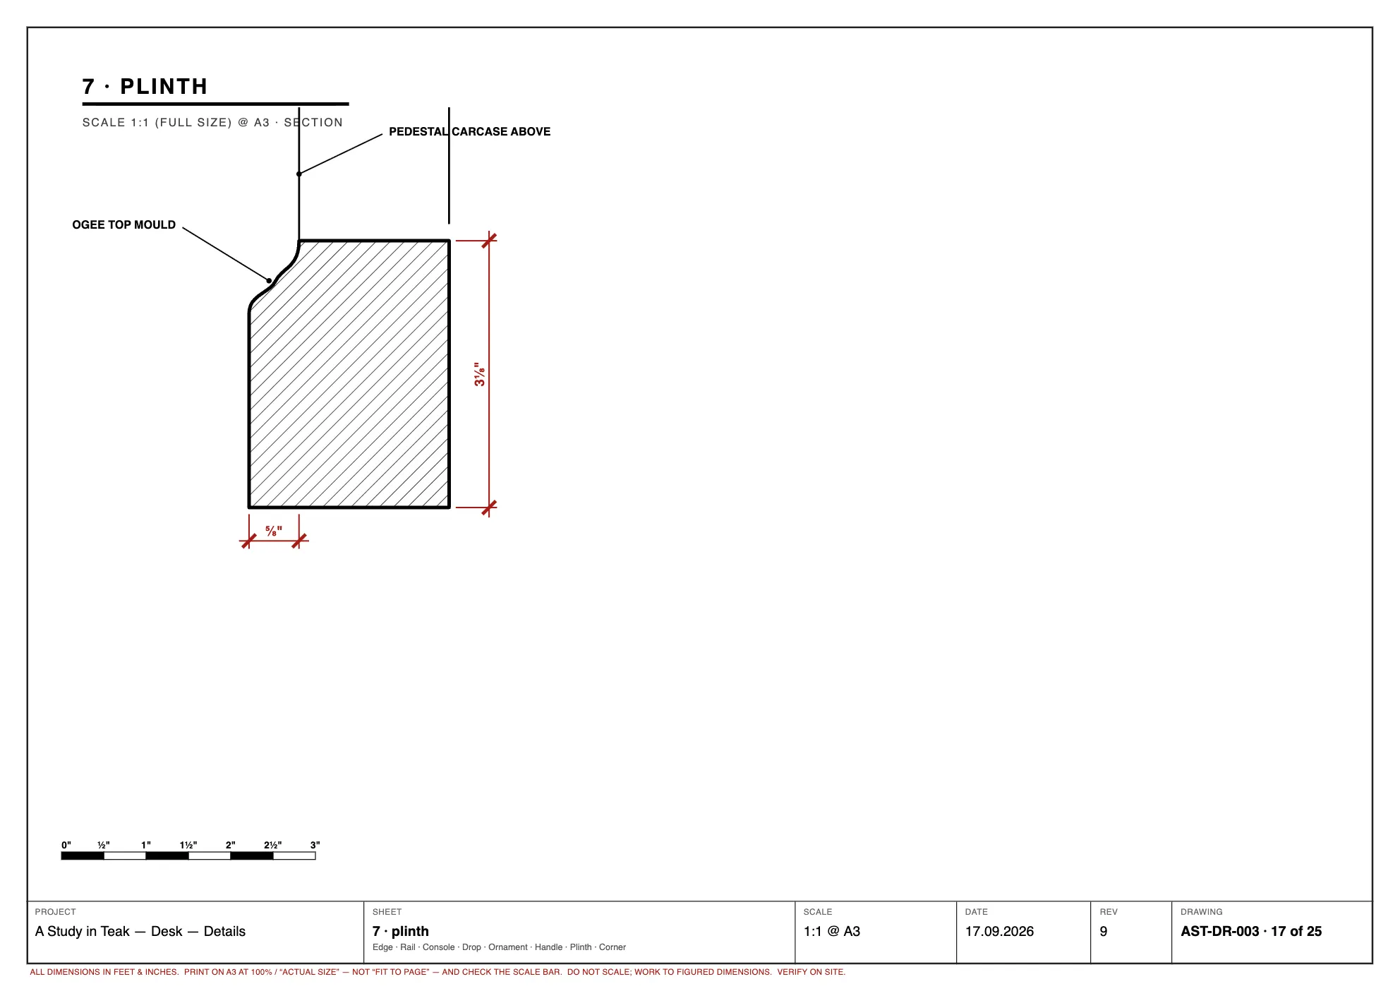
cad/print/desk-17.webp
