sakshampan733-cloud/a-study-in-teak/cad/print/desk-18.webp

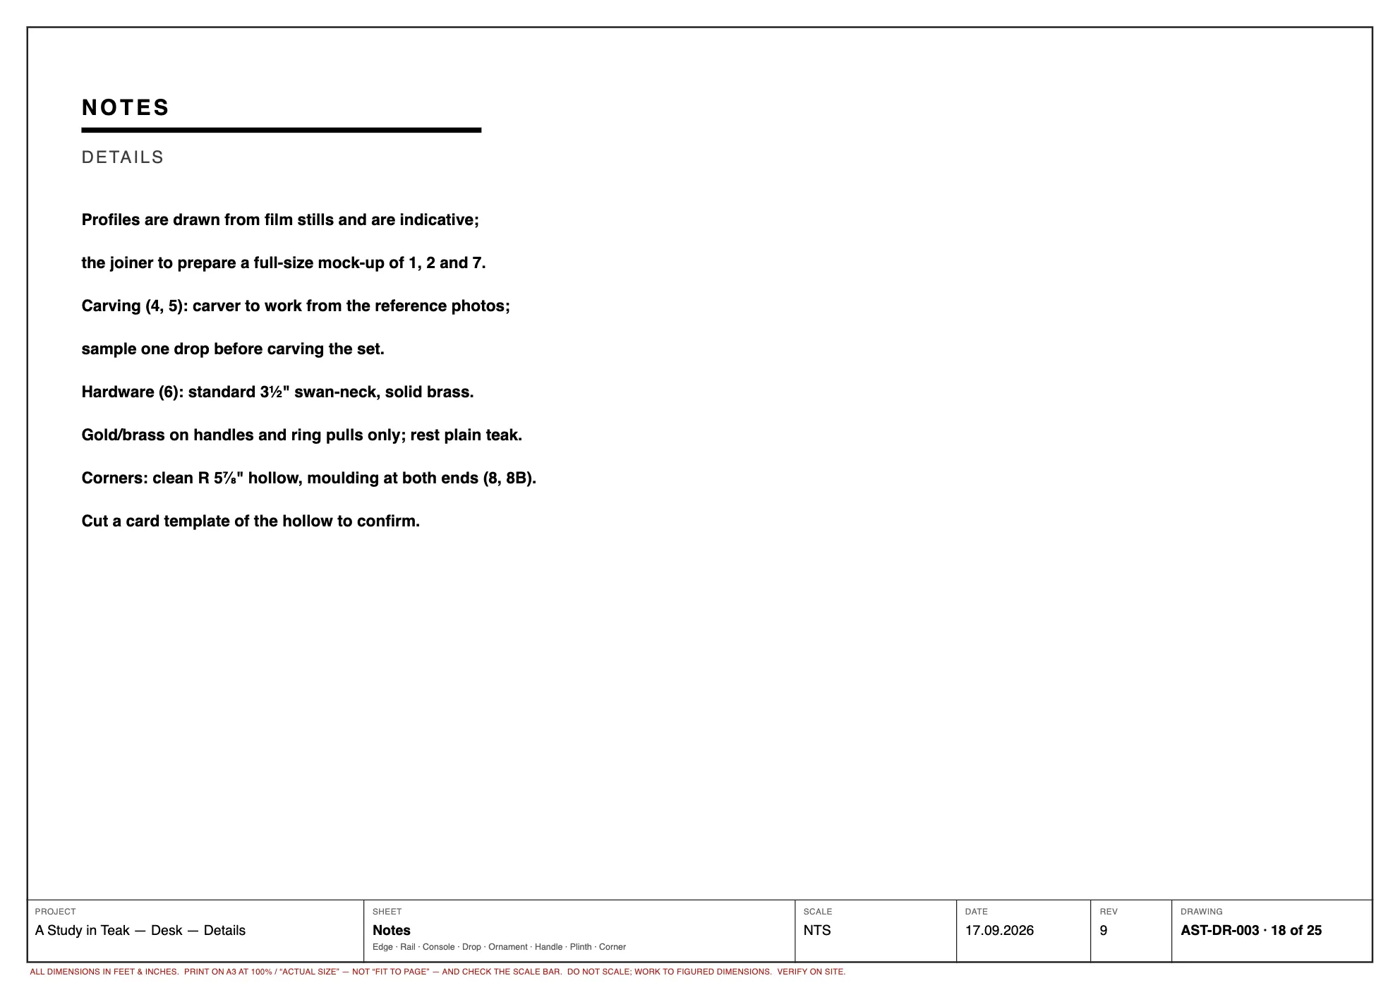
cad/print/desk-18.webp
