sakshampan733-cloud/a-study-in-teak/cad/print/desk-19.webp

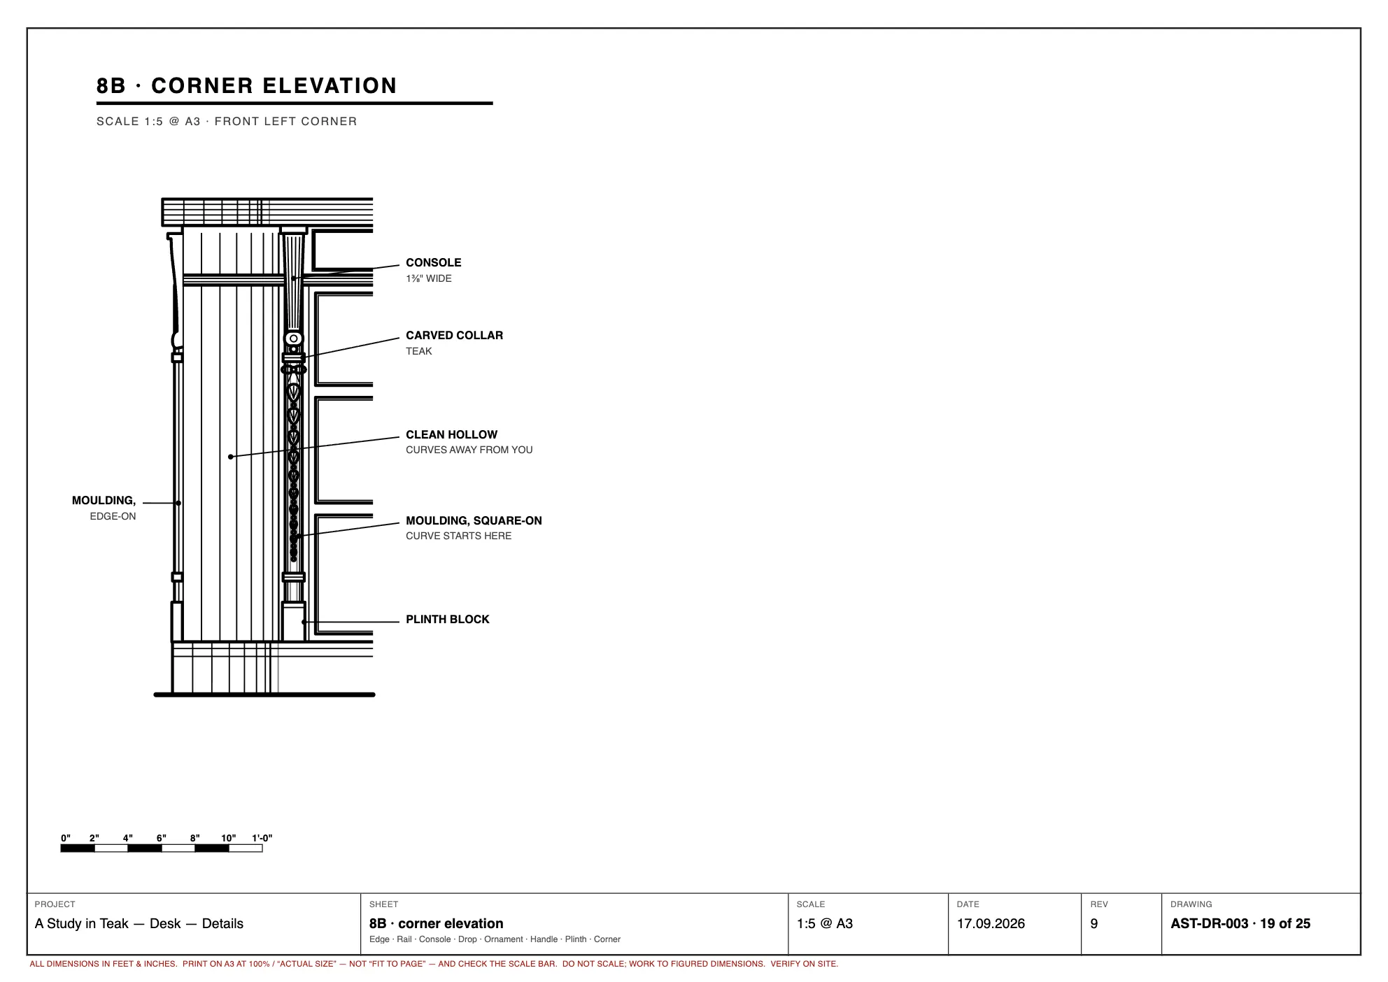
cad/print/desk-19.webp
