sakshampan733-cloud/a-study-in-teak/cad/print/desk-20.webp

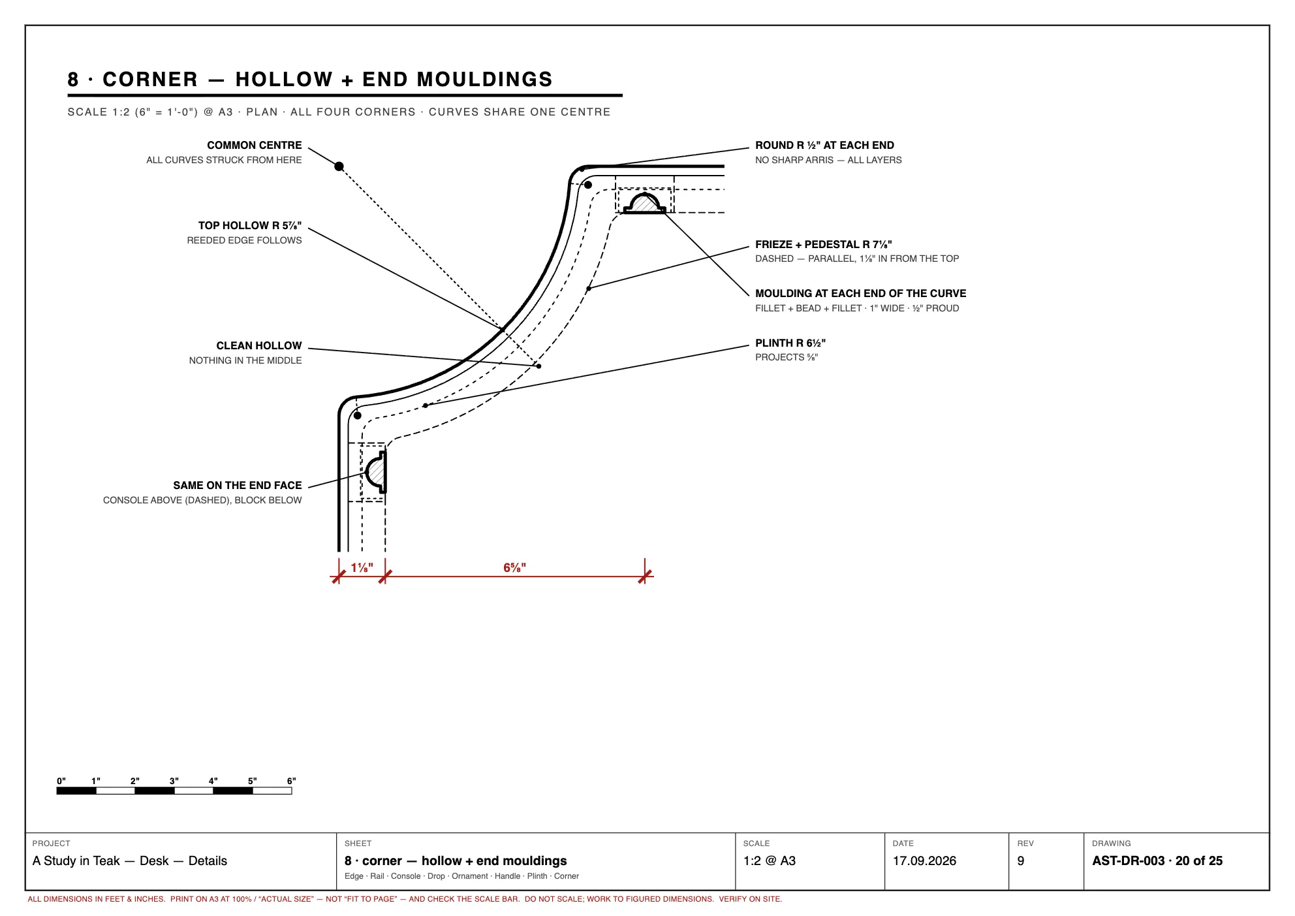
cad/print/desk-20.webp
