sakshampan733-cloud/a-study-in-teak/cad/print/desk-21.webp

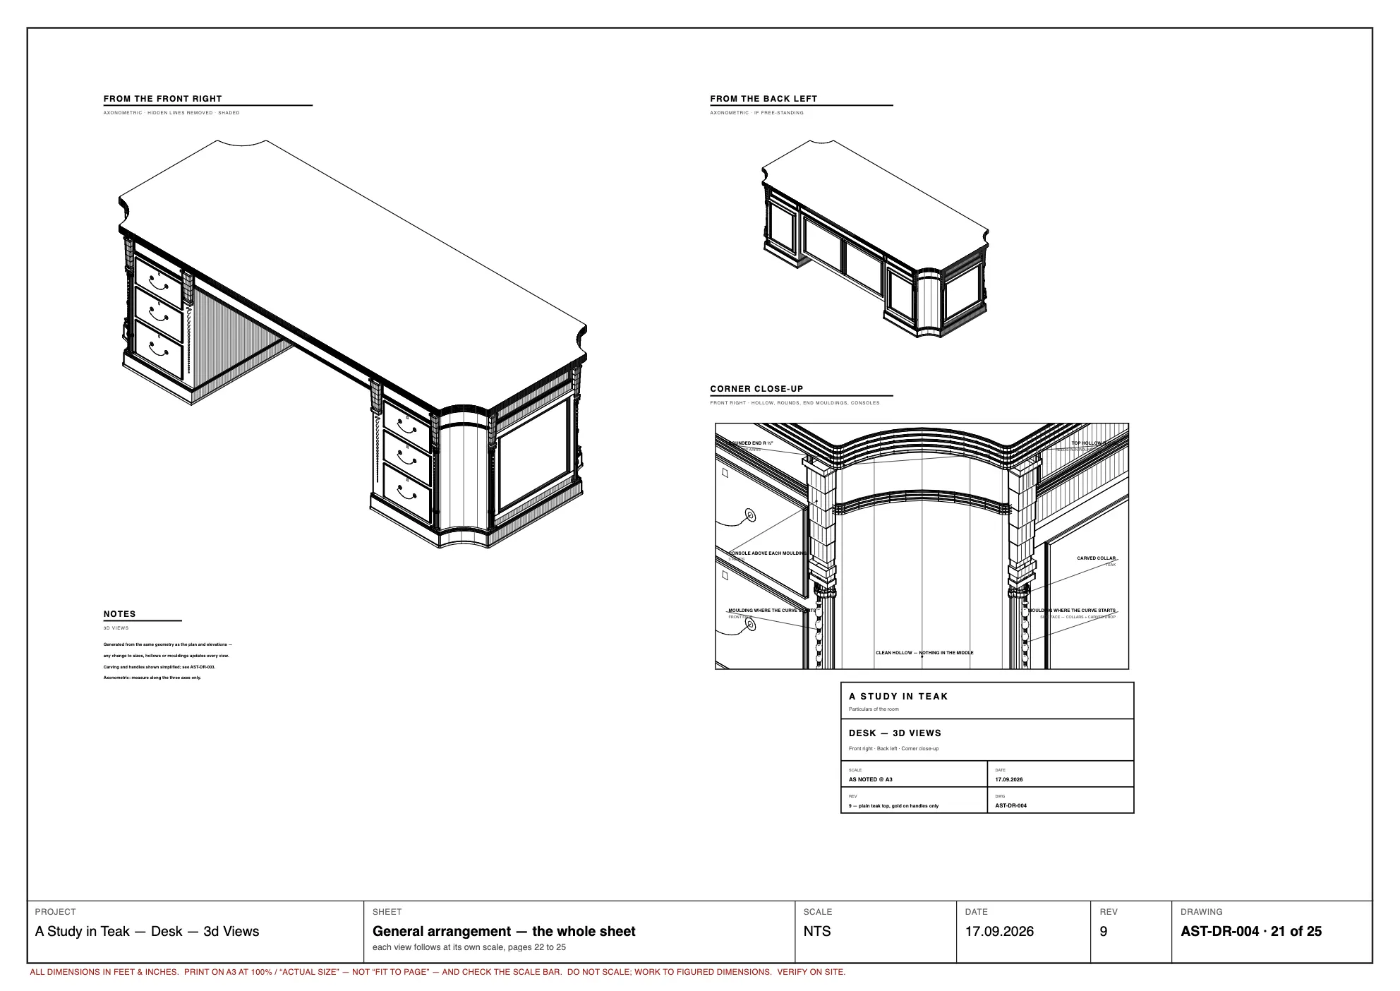
cad/print/desk-21.webp
