sakshampan733-cloud/a-study-in-teak/cad/print/desk-24.webp

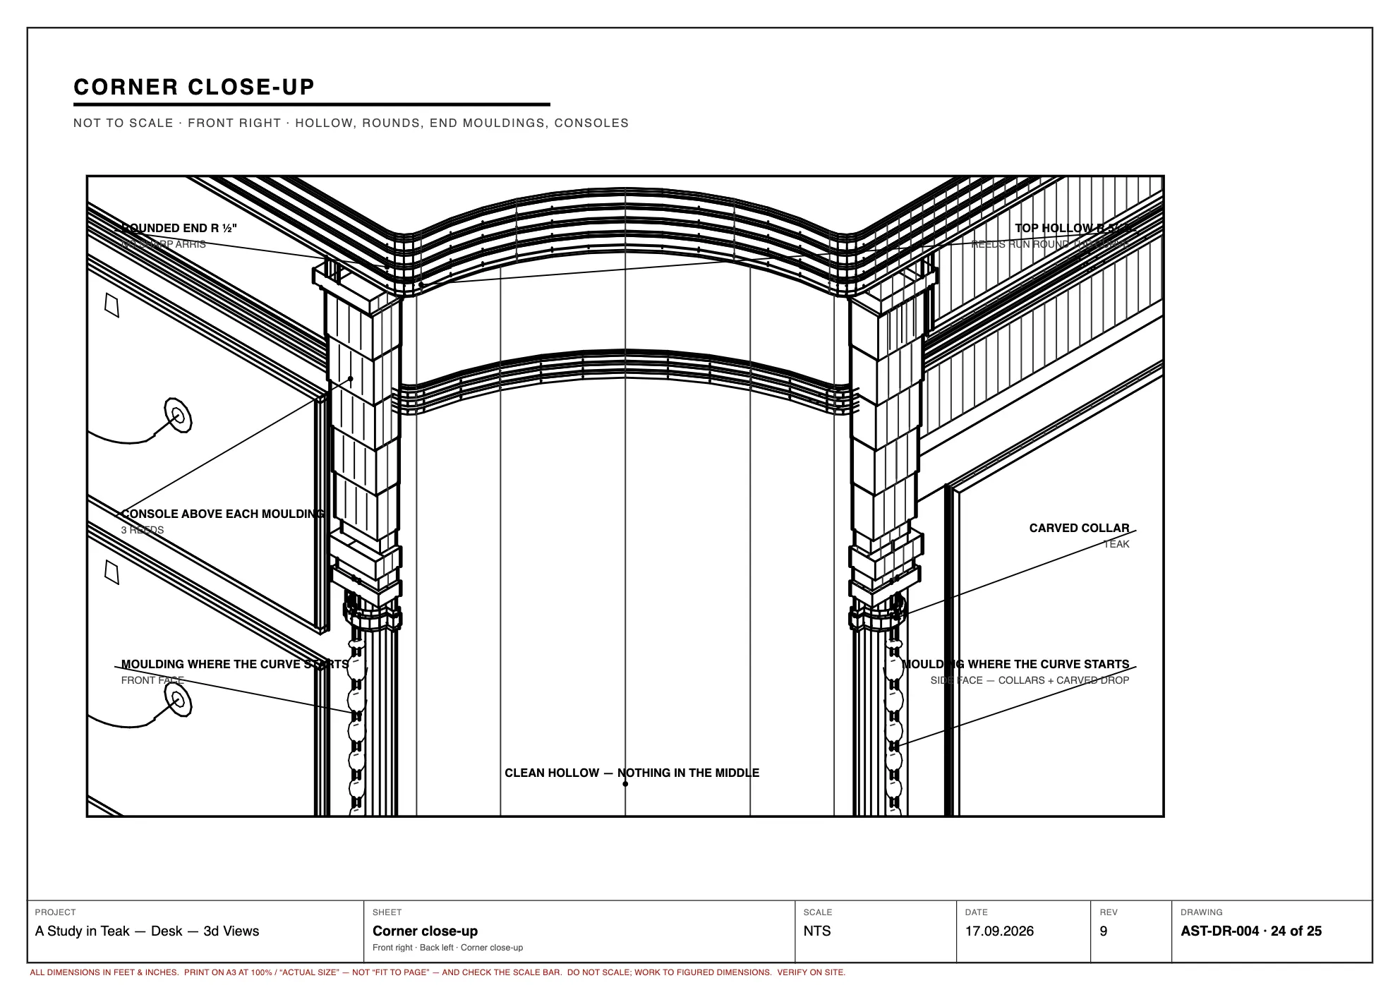
cad/print/desk-24.webp
