sakshampan733-cloud/a-study-in-teak/cad/print/desk-25.webp

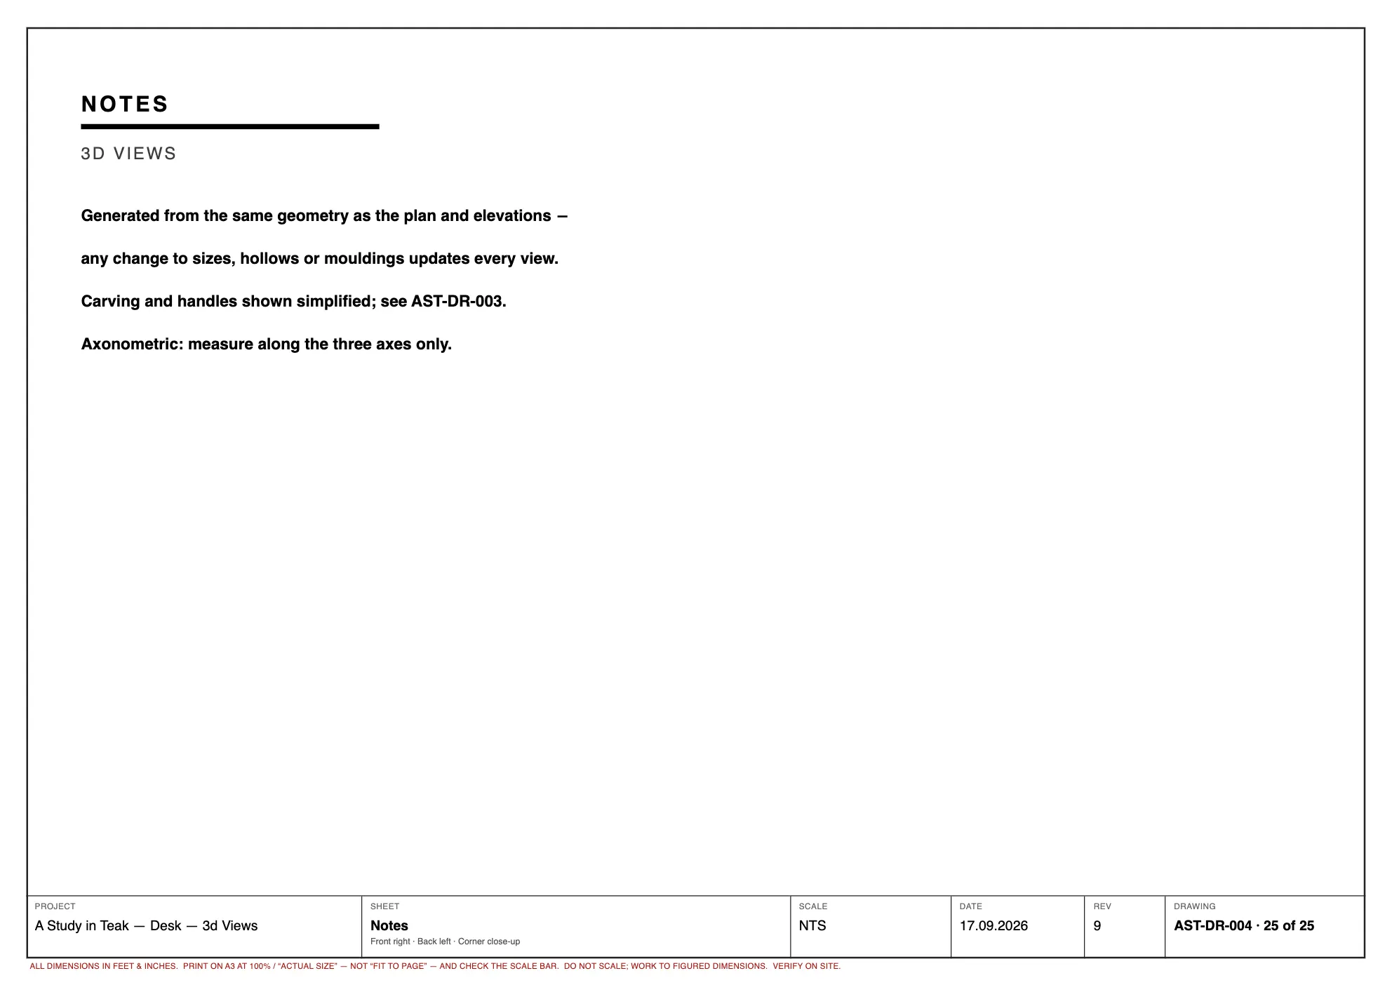
cad/print/desk-25.webp
