sakshampan733-cloud/a-study-in-teak/cad/print/desk-curved-14.webp

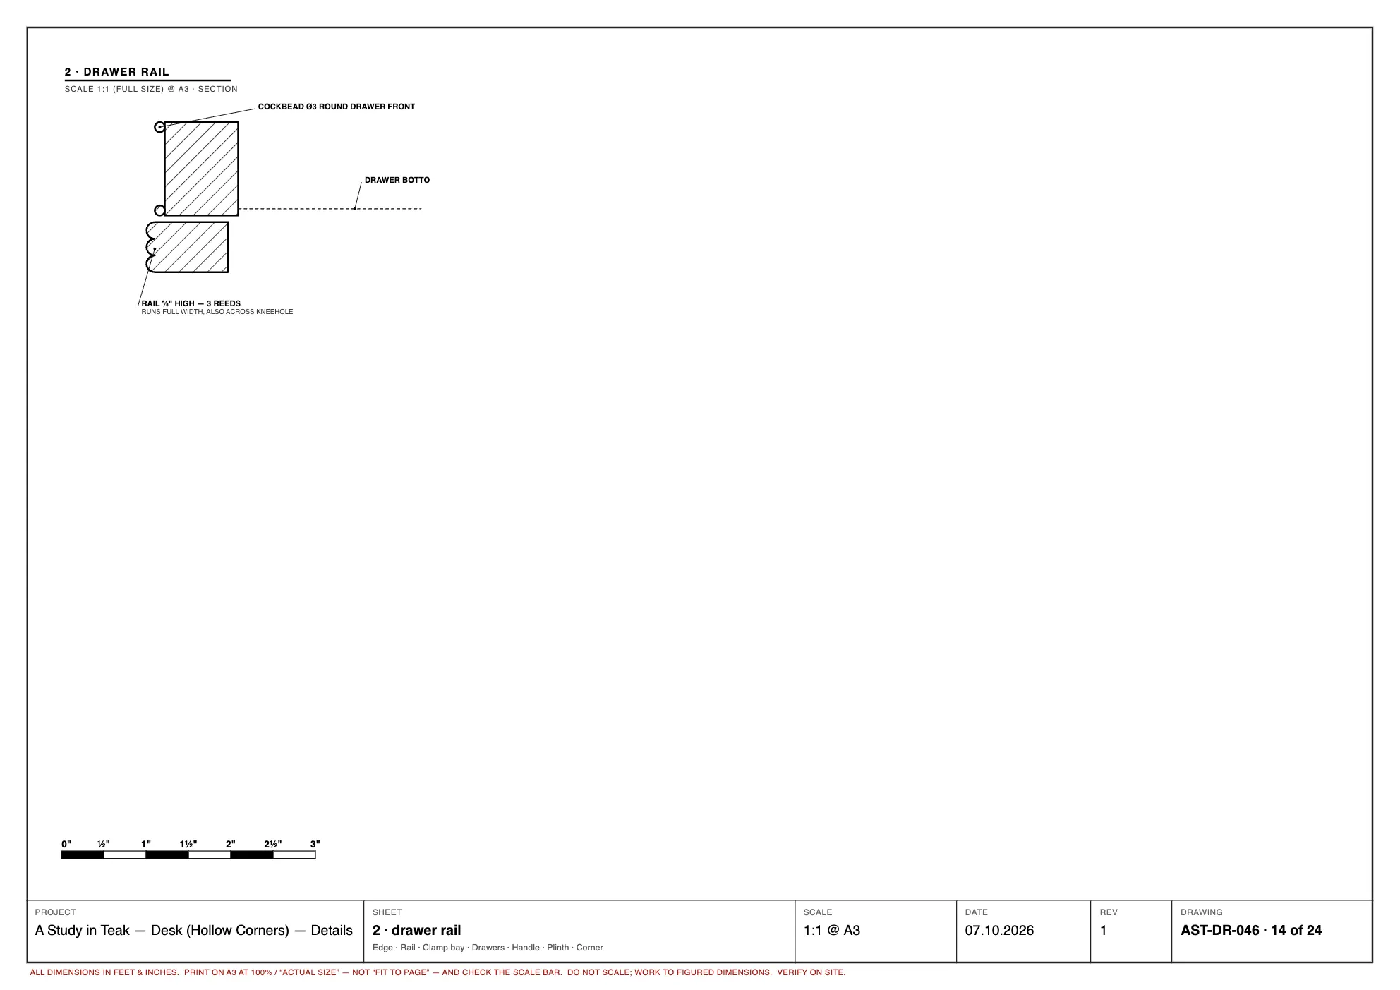
cad/print/desk-curved-14.webp
