sakshampan733-cloud/a-study-in-teak/cad/print/desk-curved-18.webp

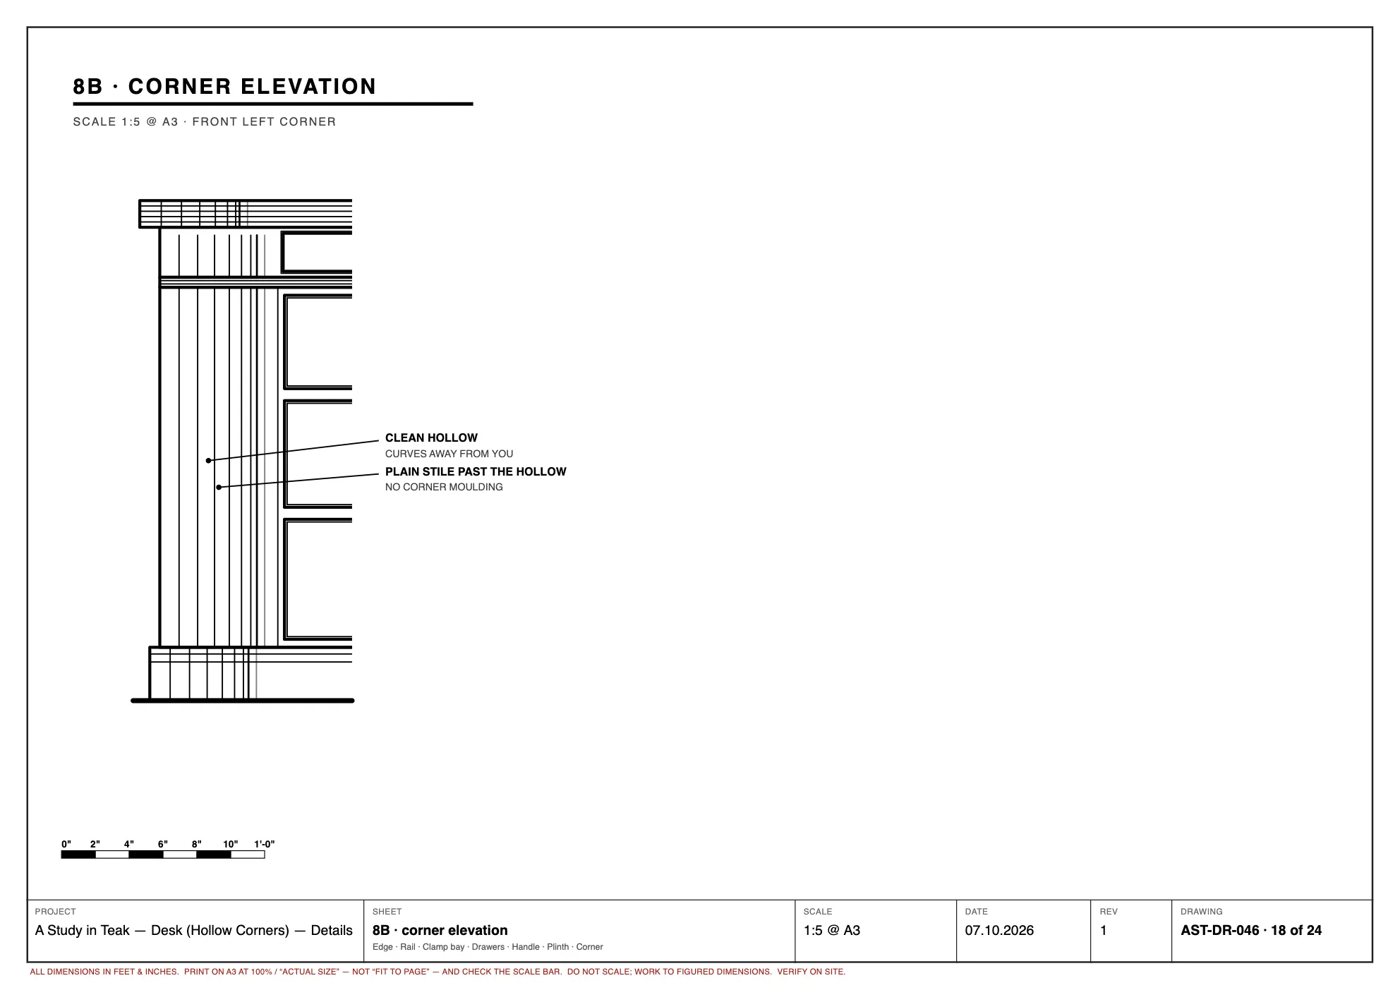
cad/print/desk-curved-18.webp
