sakshampan733-cloud/a-study-in-teak/cad/print/desk-curved-19.webp

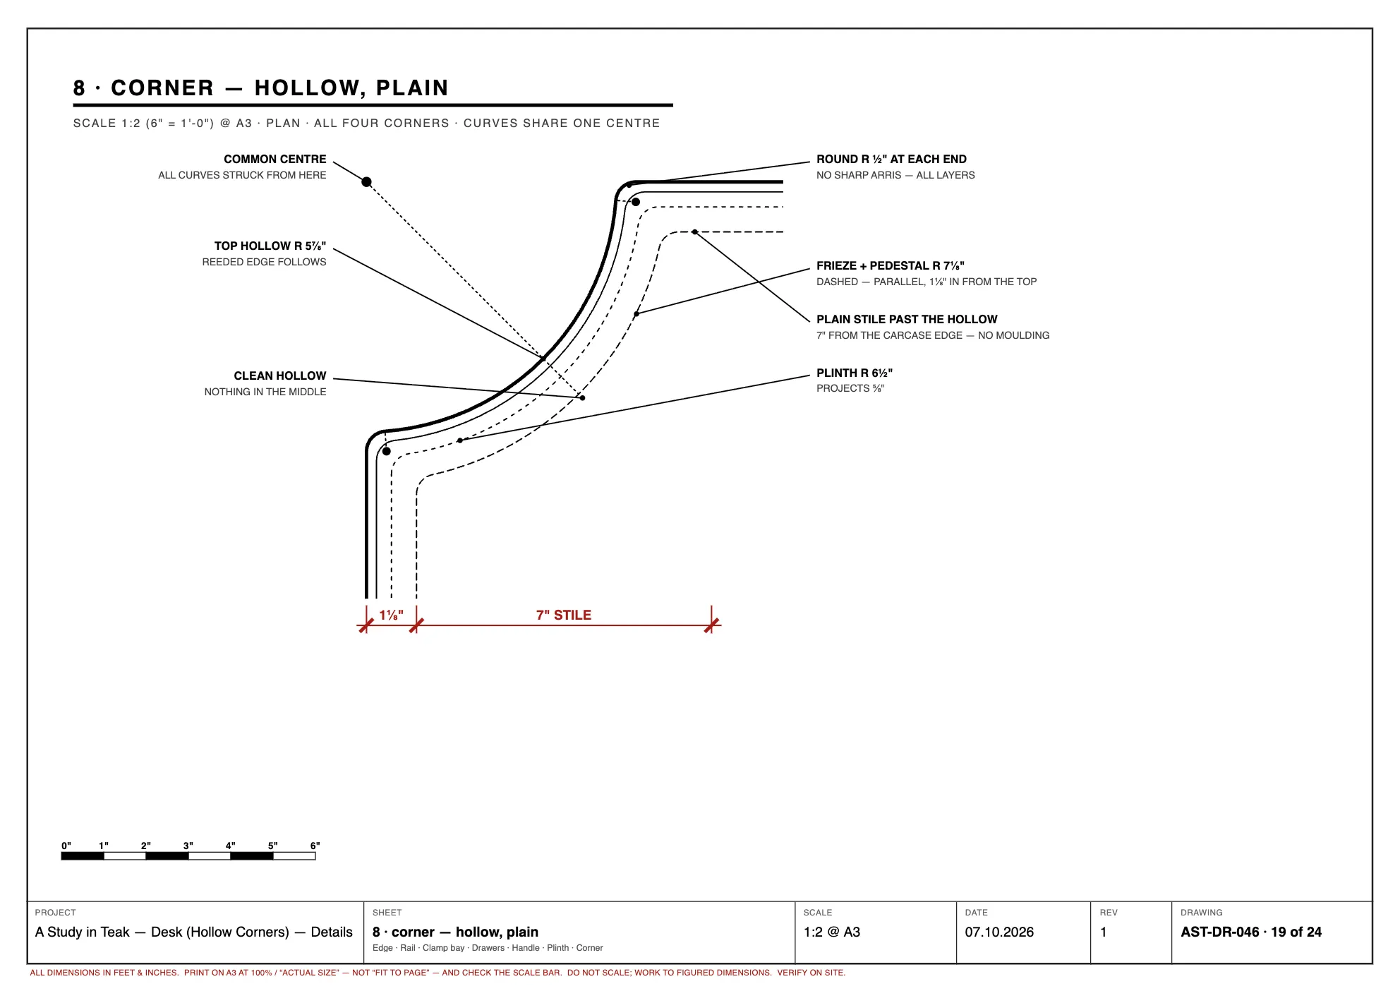
cad/print/desk-curved-19.webp
