sakshampan733-cloud/a-study-in-teak/cad/print/desk-curved-23.webp

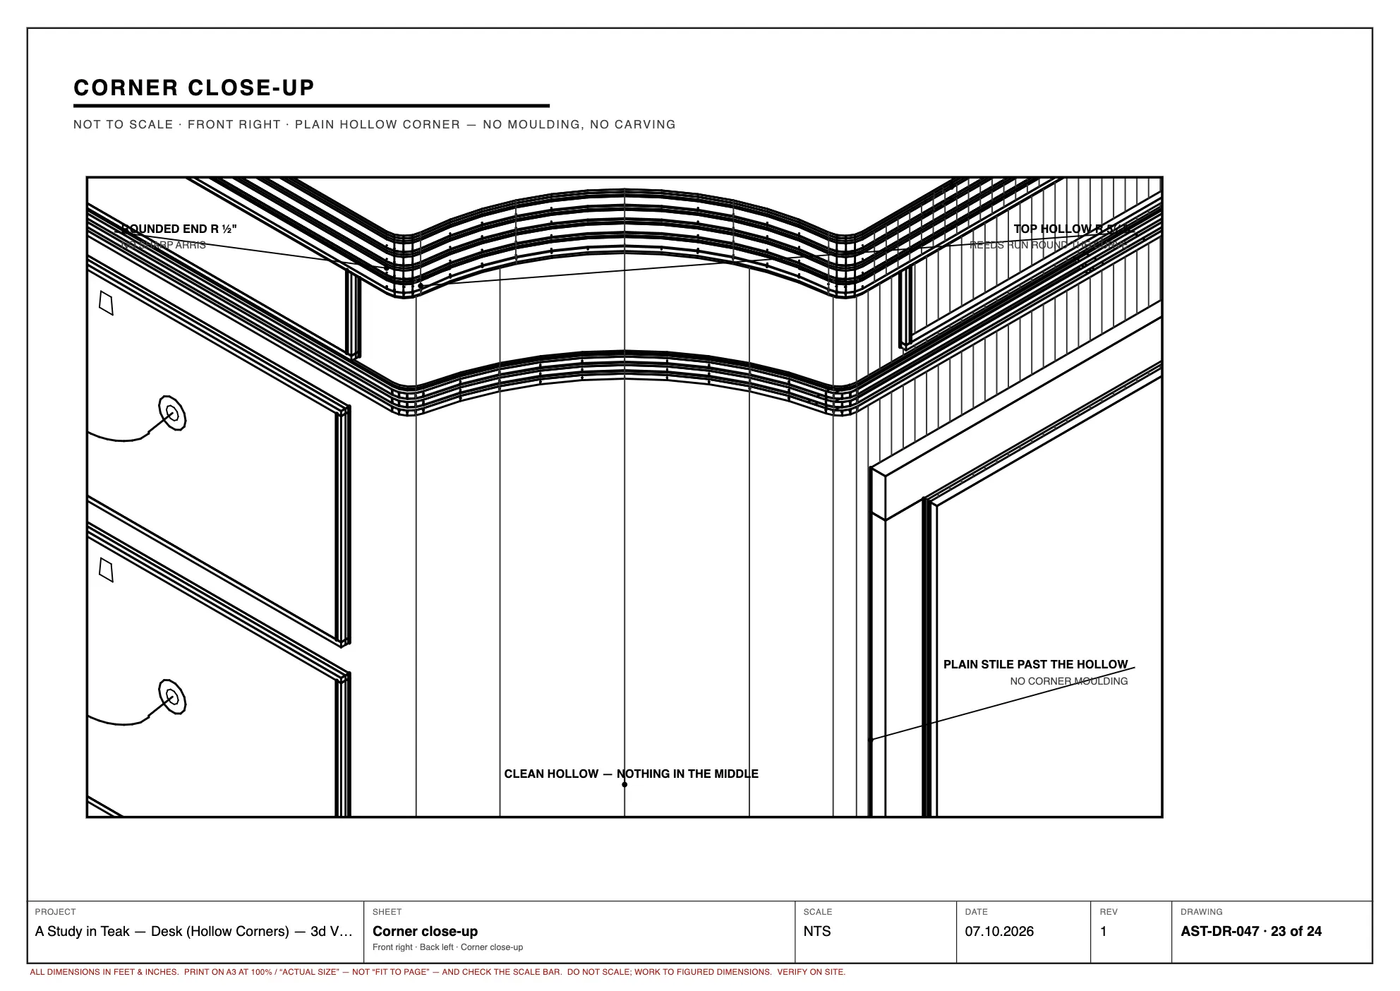
cad/print/desk-curved-23.webp
