sakshampan733-cloud/a-study-in-teak/cad/print/desk-plain-10.webp

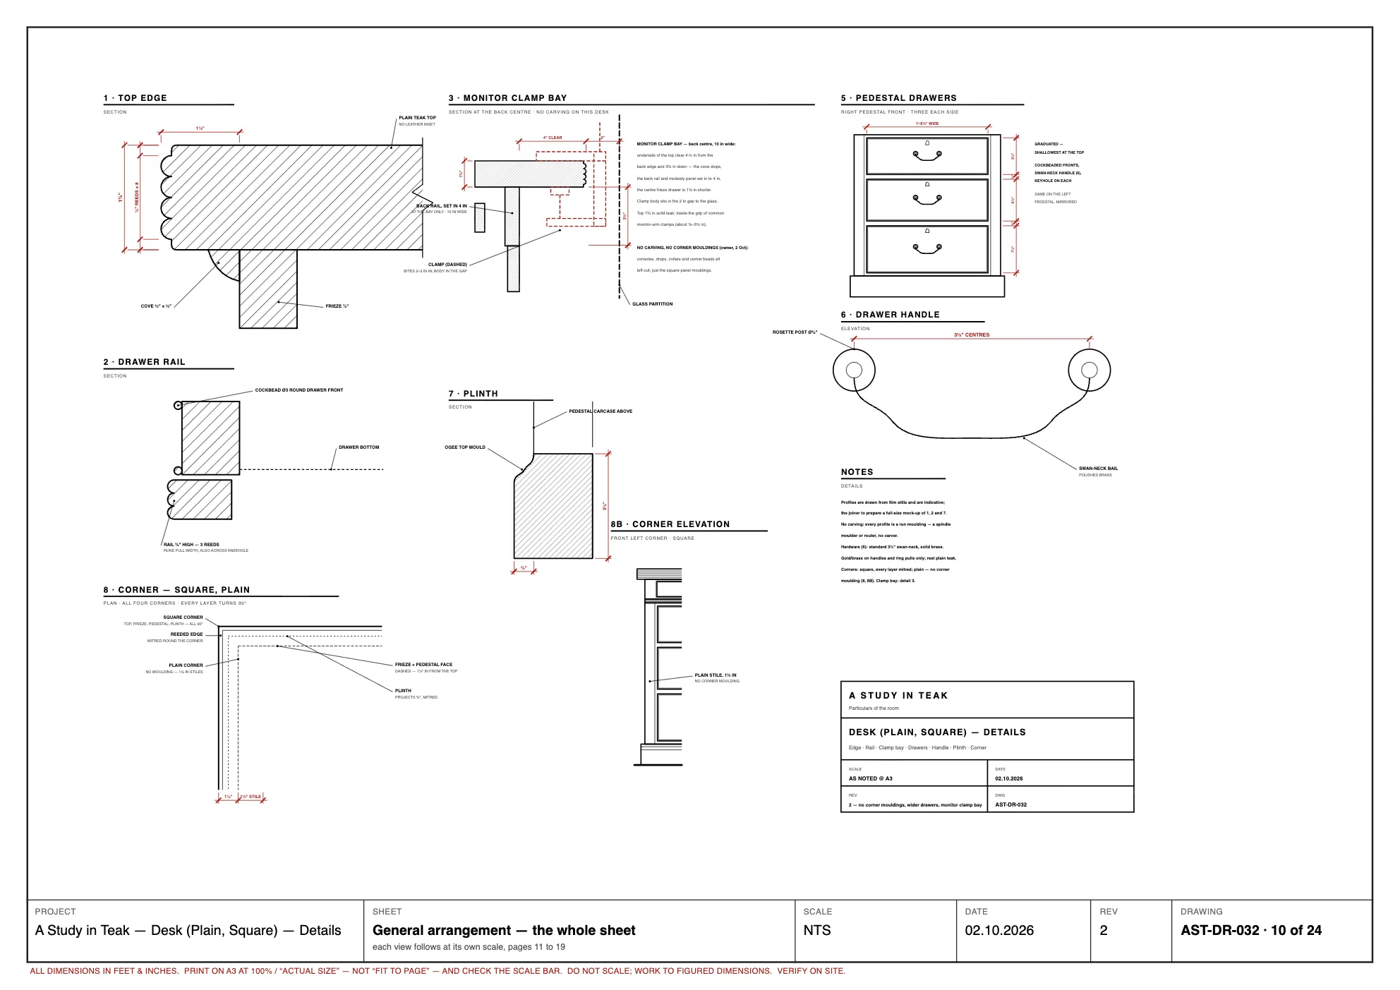
cad/print/desk-plain-10.webp
