sakshampan733-cloud/a-study-in-teak/cad/print/desk-plain-13.webp

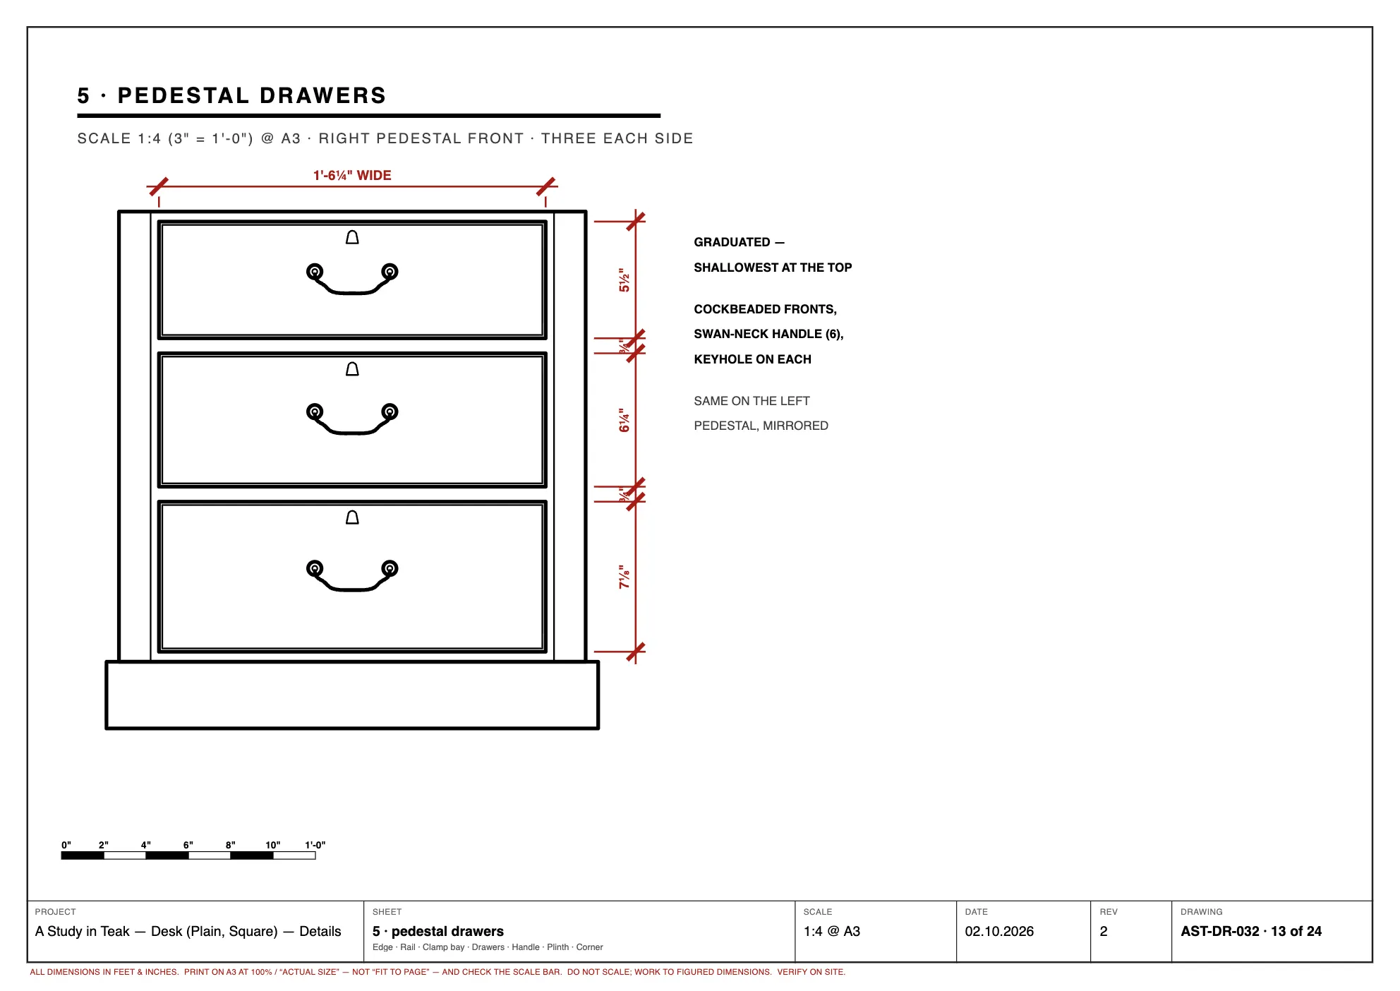
cad/print/desk-plain-13.webp
