sakshampan733-cloud/a-study-in-teak/cad/print/desk-plain-18.webp

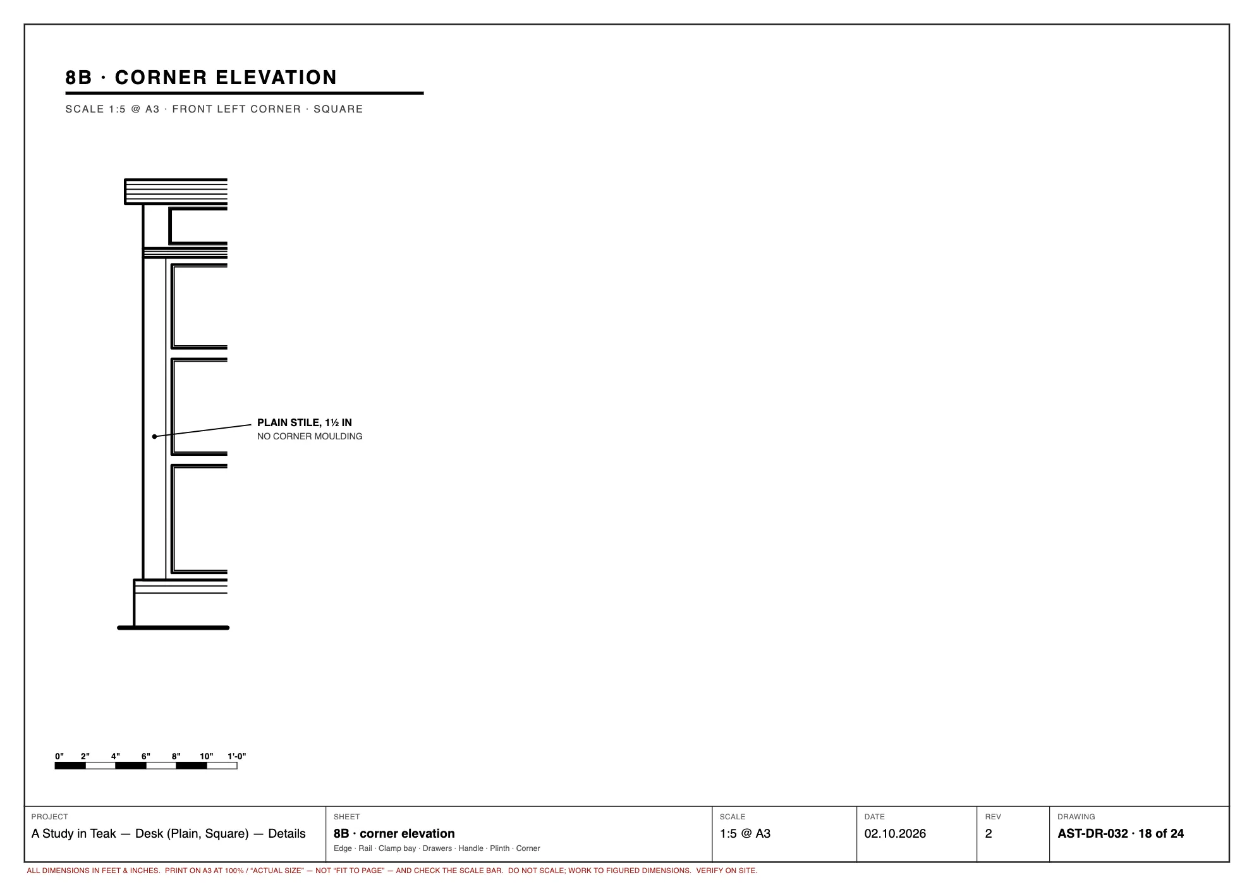
cad/print/desk-plain-18.webp
