sakshampan733-cloud/a-study-in-teak/cad/print/desk-plain-19.webp

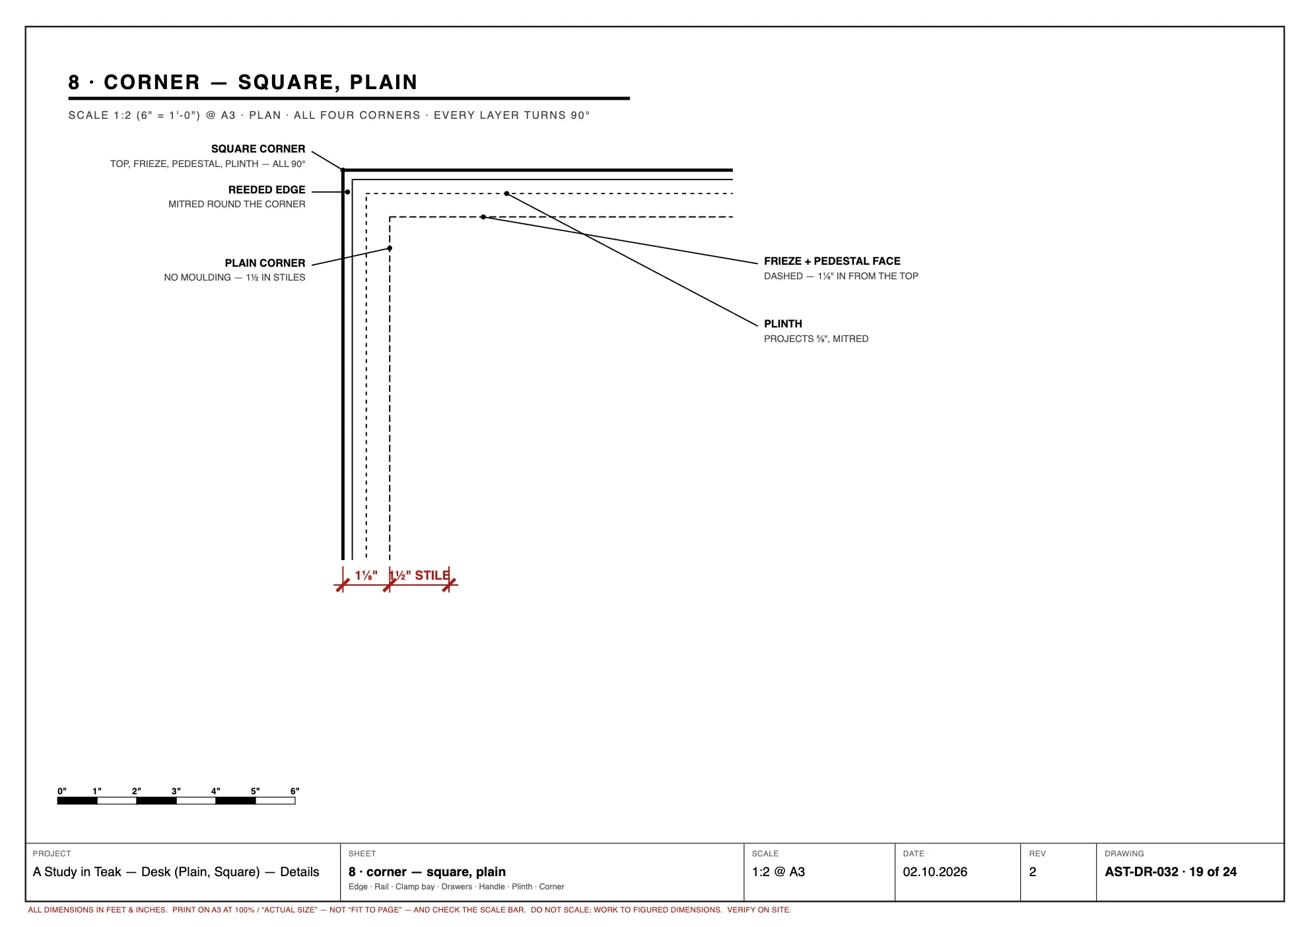
cad/print/desk-plain-19.webp
