sakshampan733-cloud/a-study-in-teak/cad/print/desk-square-01.webp

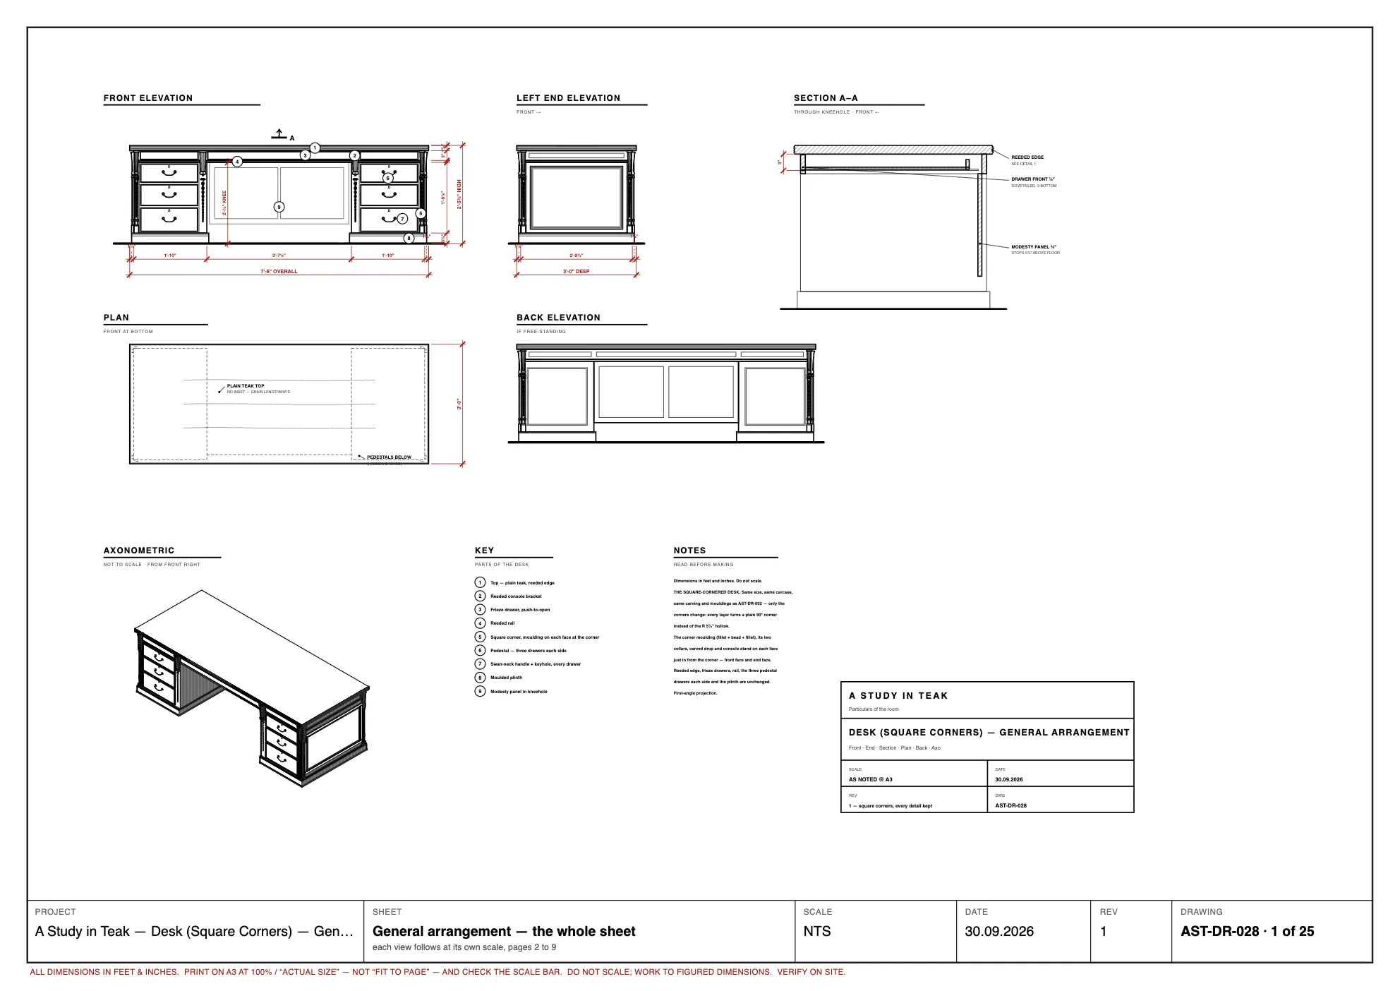
cad/print/desk-square-01.webp
