sakshampan733-cloud/a-study-in-teak/cad/print/door-03.webp

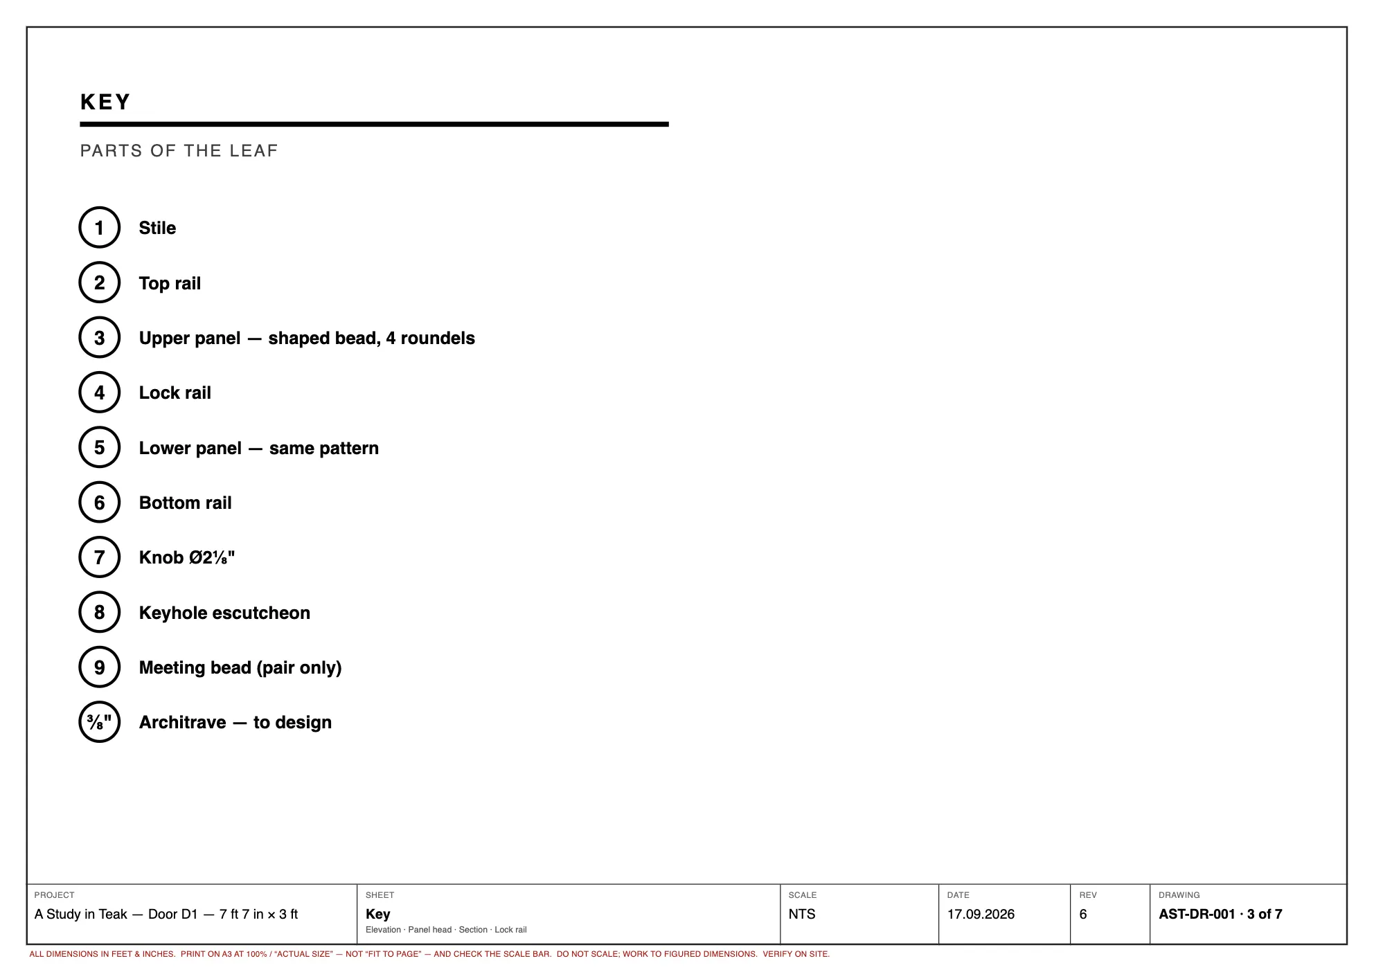
cad/print/door-03.webp
