sakshampan733-cloud/a-study-in-teak/cad/print/door-04.webp

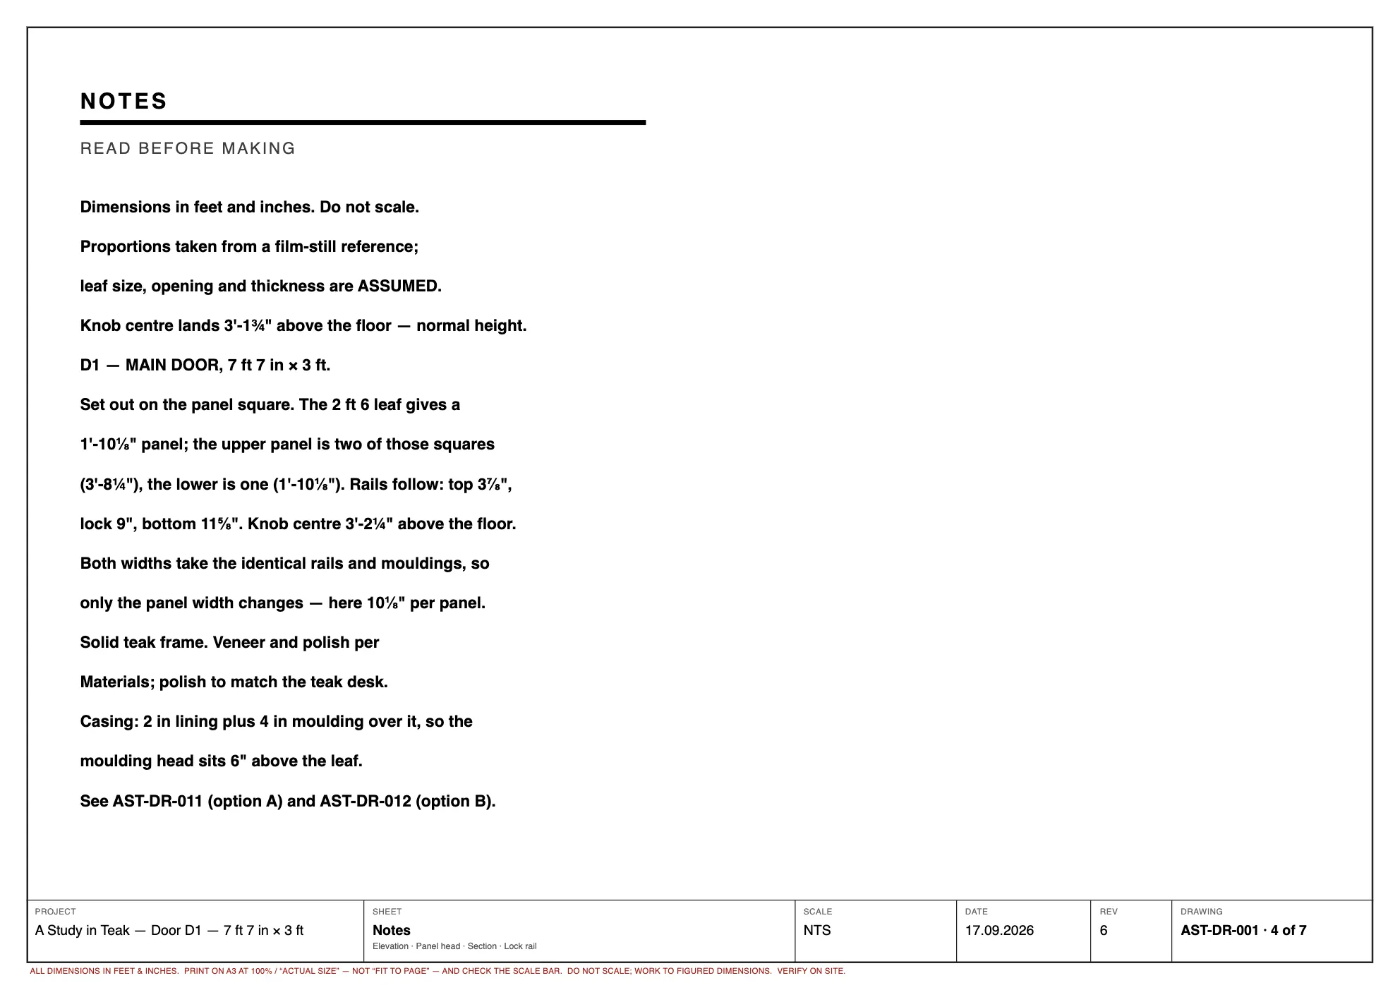
cad/print/door-04.webp
