sakshampan733-cloud/a-study-in-teak/cad/print/door-06.webp

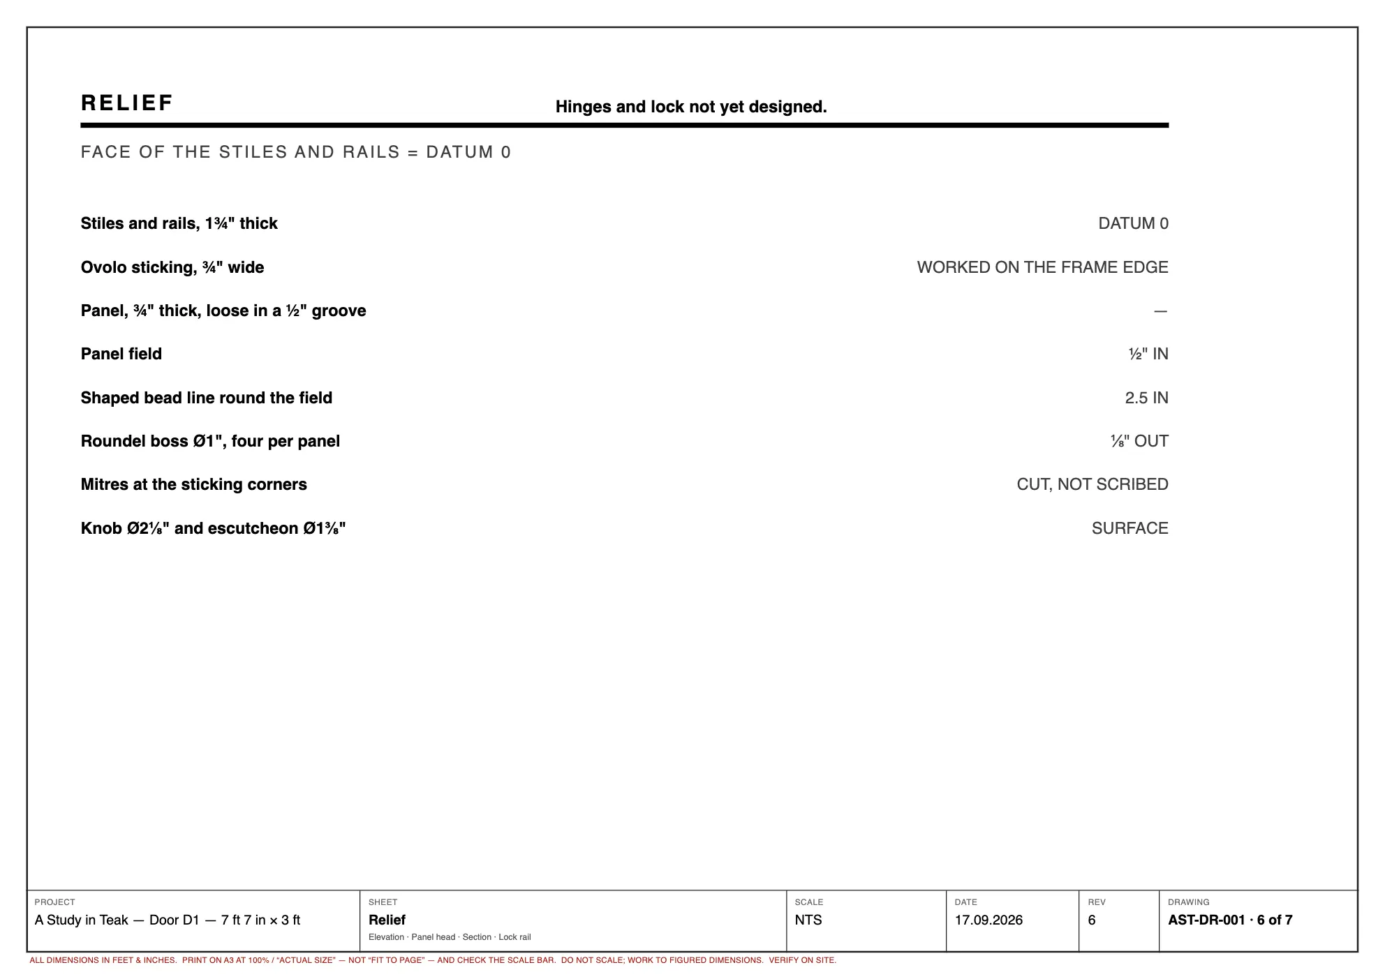
cad/print/door-06.webp
