sakshampan733-cloud/a-study-in-teak/cad/print/door-narrow-01.webp

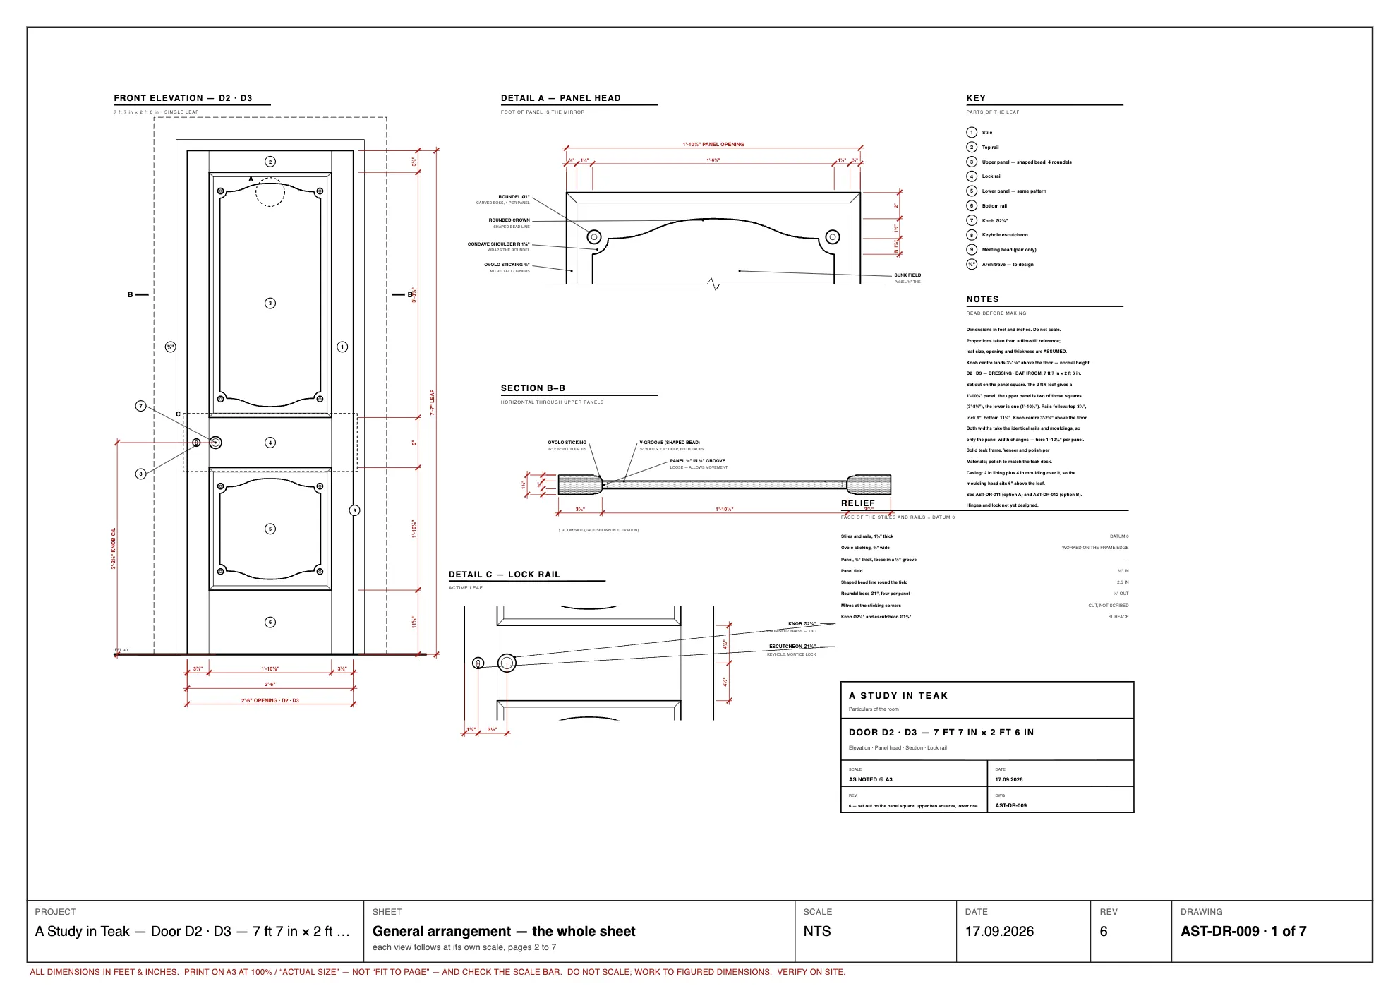
cad/print/door-narrow-01.webp
