sakshampan733-cloud/a-study-in-teak/cad/print/door-narrow-02.webp

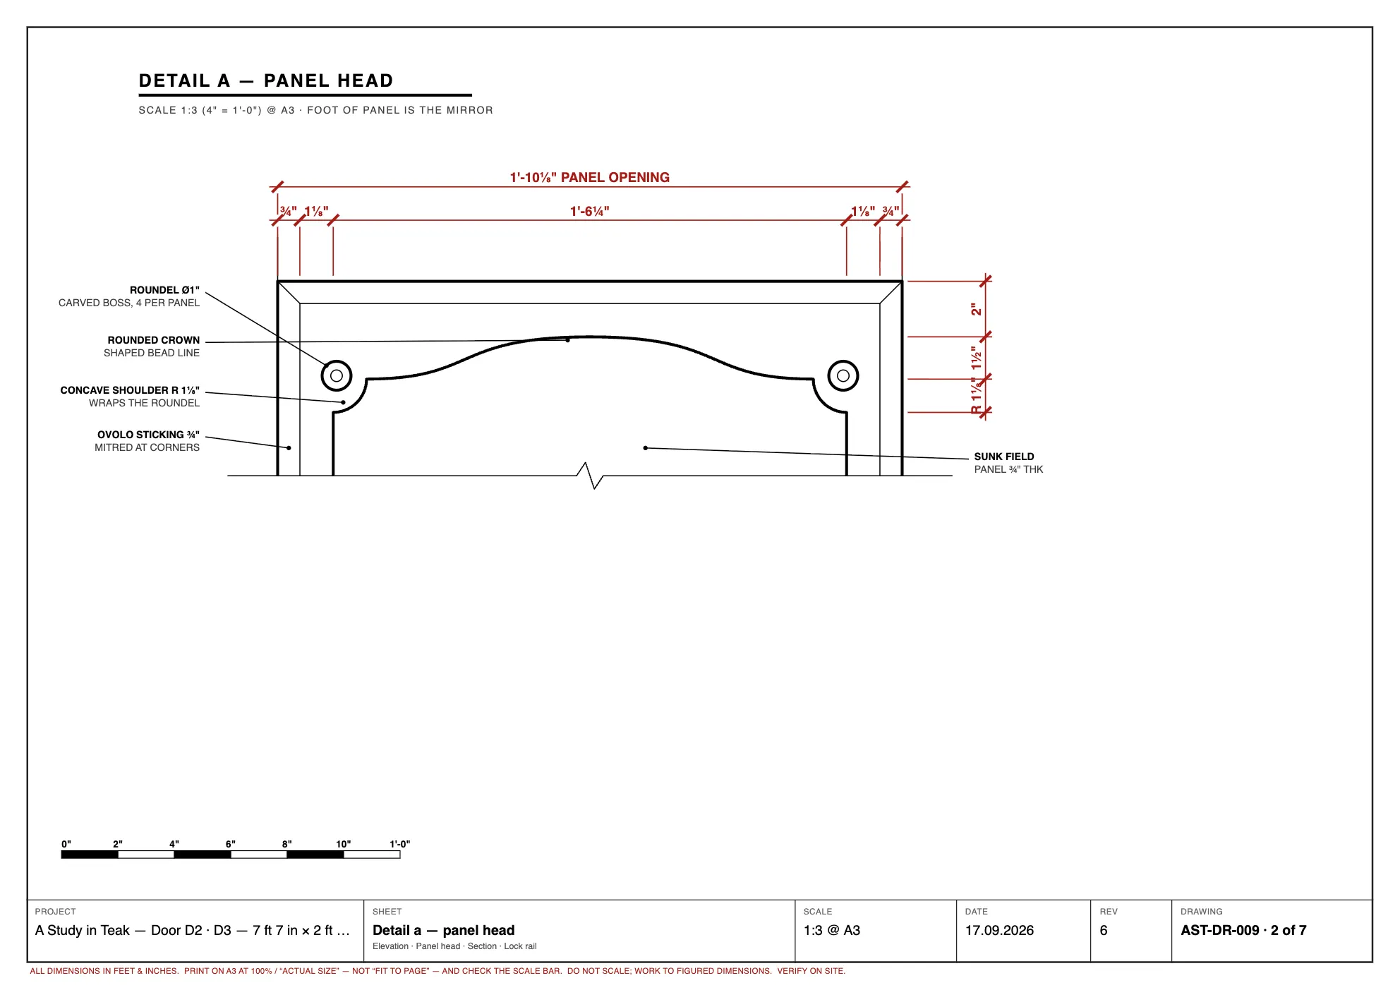
cad/print/door-narrow-02.webp
