sakshampan733-cloud/a-study-in-teak/cad/print/door-narrow-07.webp

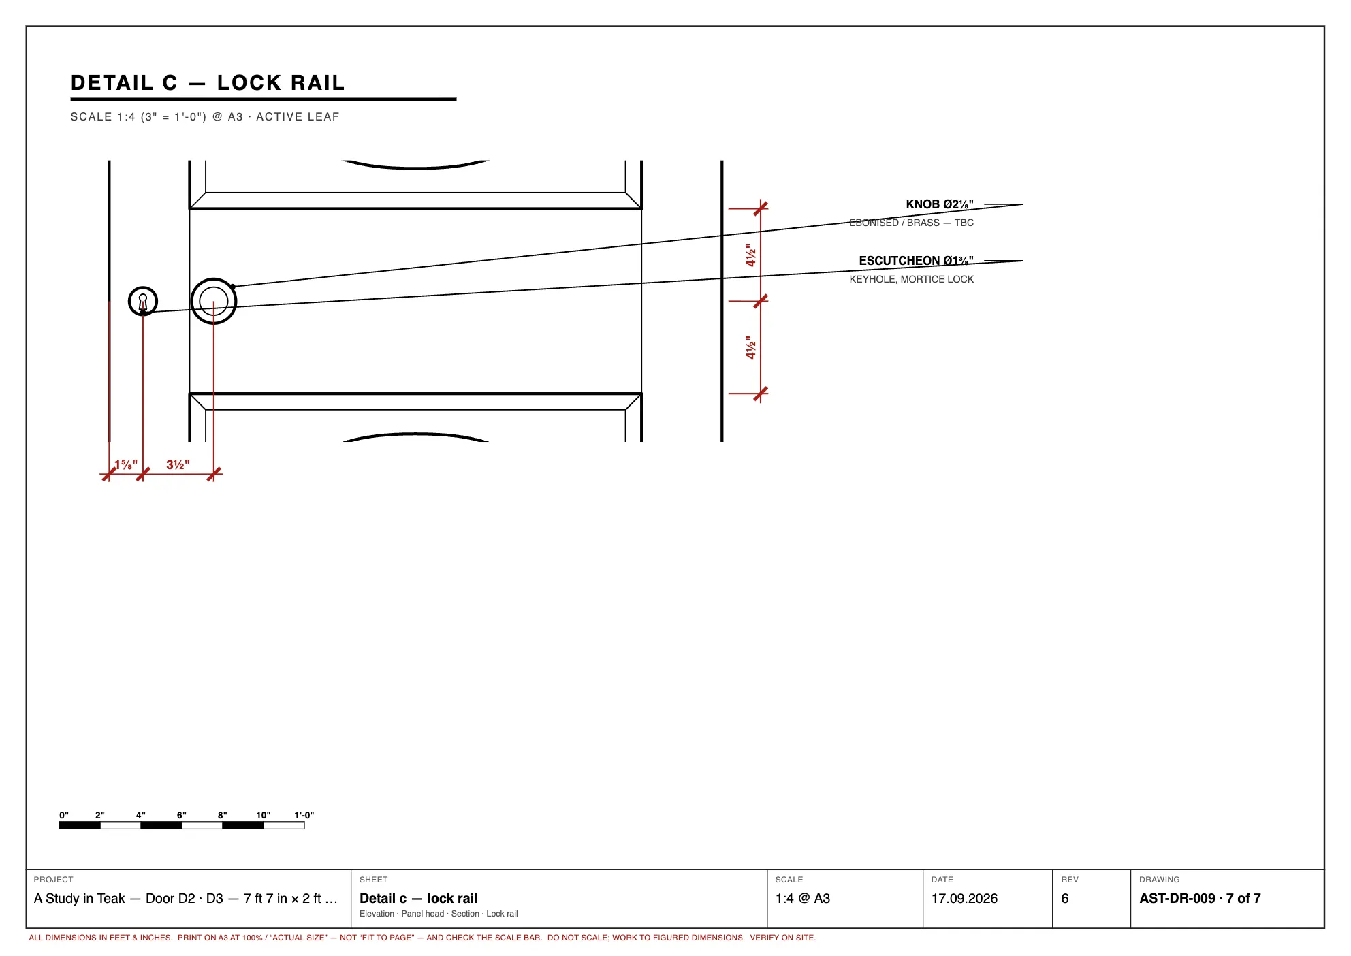
cad/print/door-narrow-07.webp
