sakshampan733-cloud/a-study-in-teak/cad/print/doorveneer-01.webp

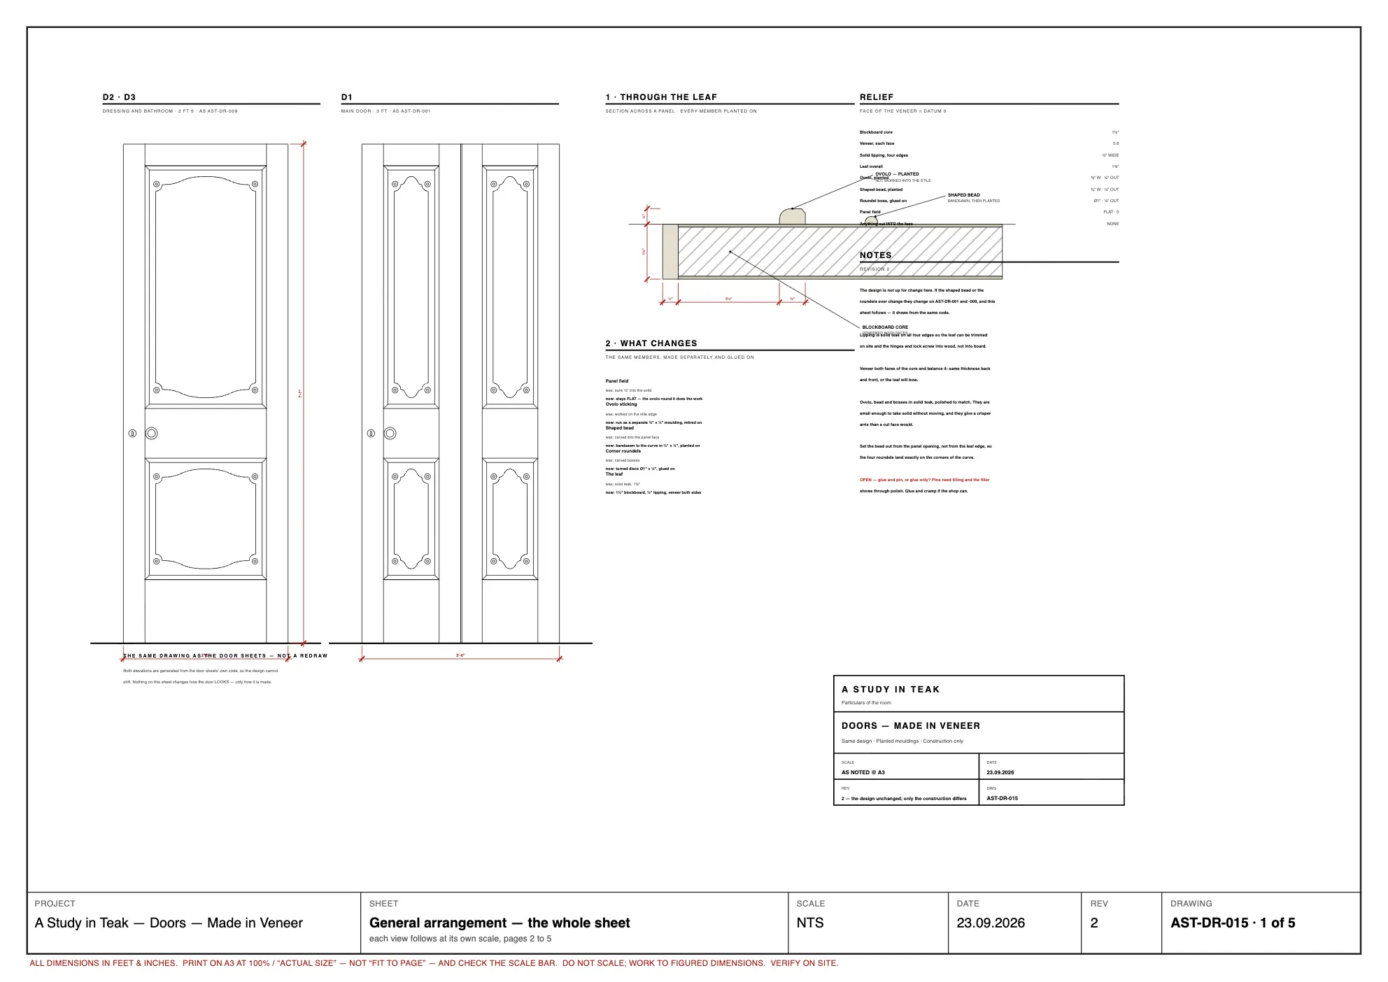
cad/print/doorveneer-01.webp
