sakshampan733-cloud/a-study-in-teak/cad/print/doorveneer-02.webp

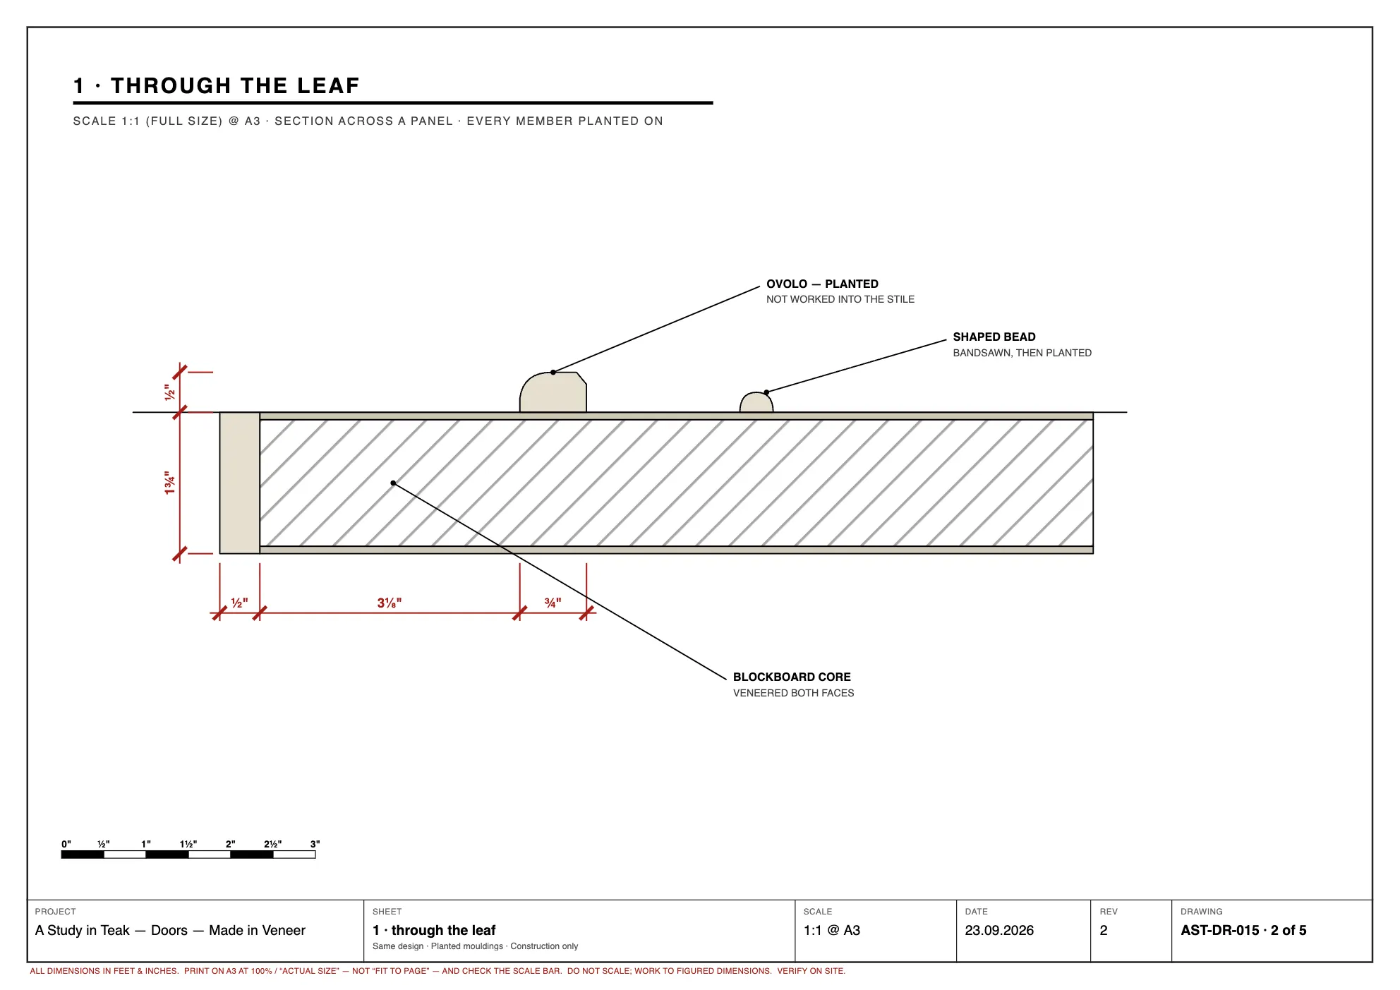
cad/print/doorveneer-02.webp
