sakshampan733-cloud/a-study-in-teak/cad/print/doorveneer-03.webp

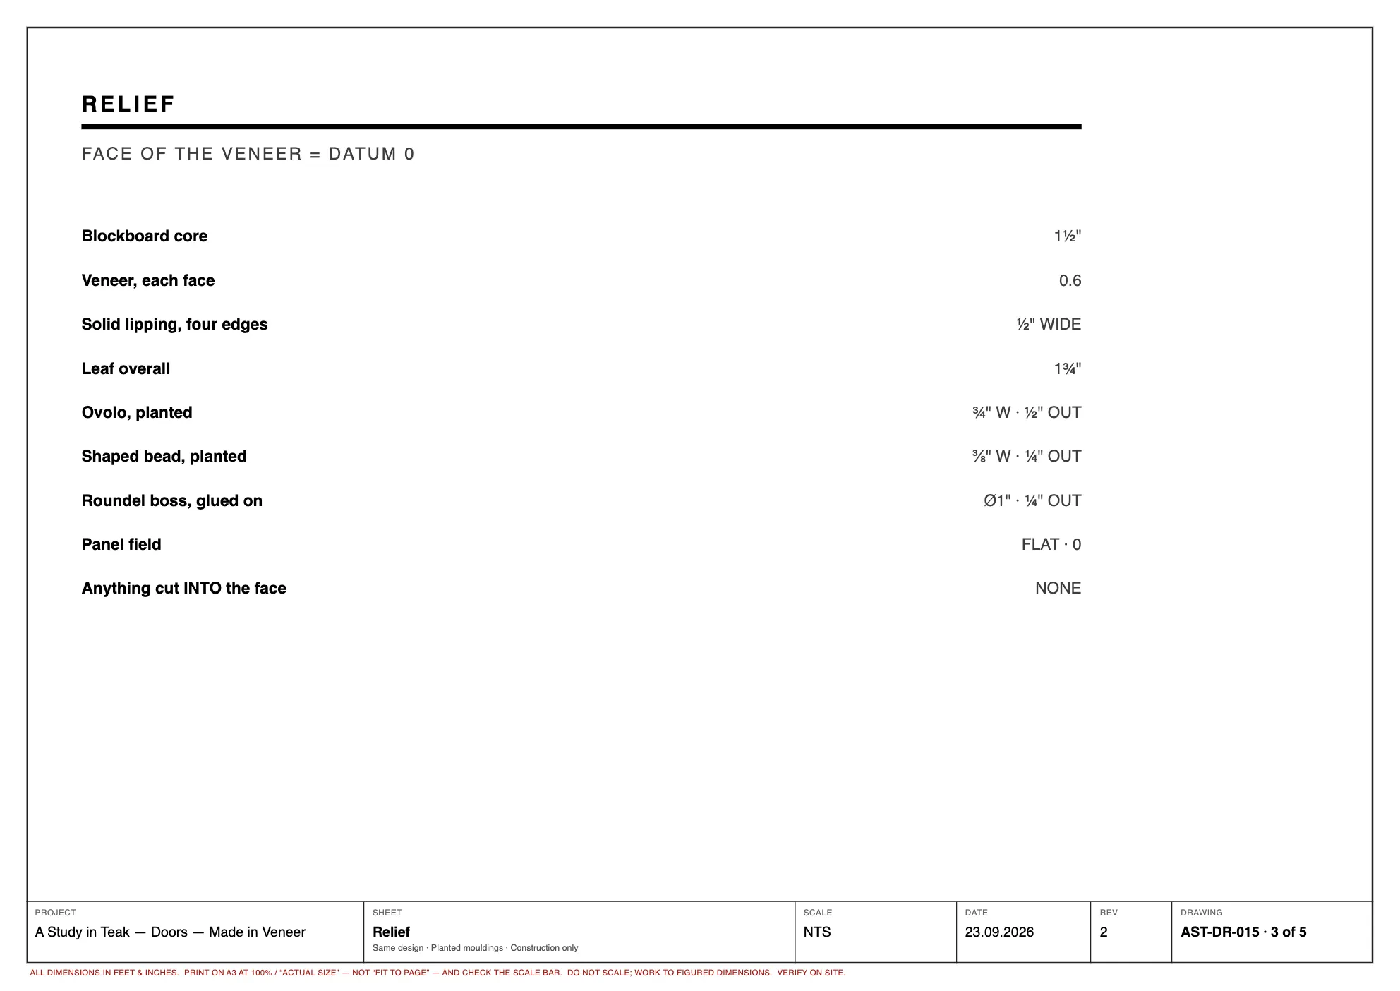
cad/print/doorveneer-03.webp
