sakshampan733-cloud/a-study-in-teak/cad/print/doorveneer-04.webp

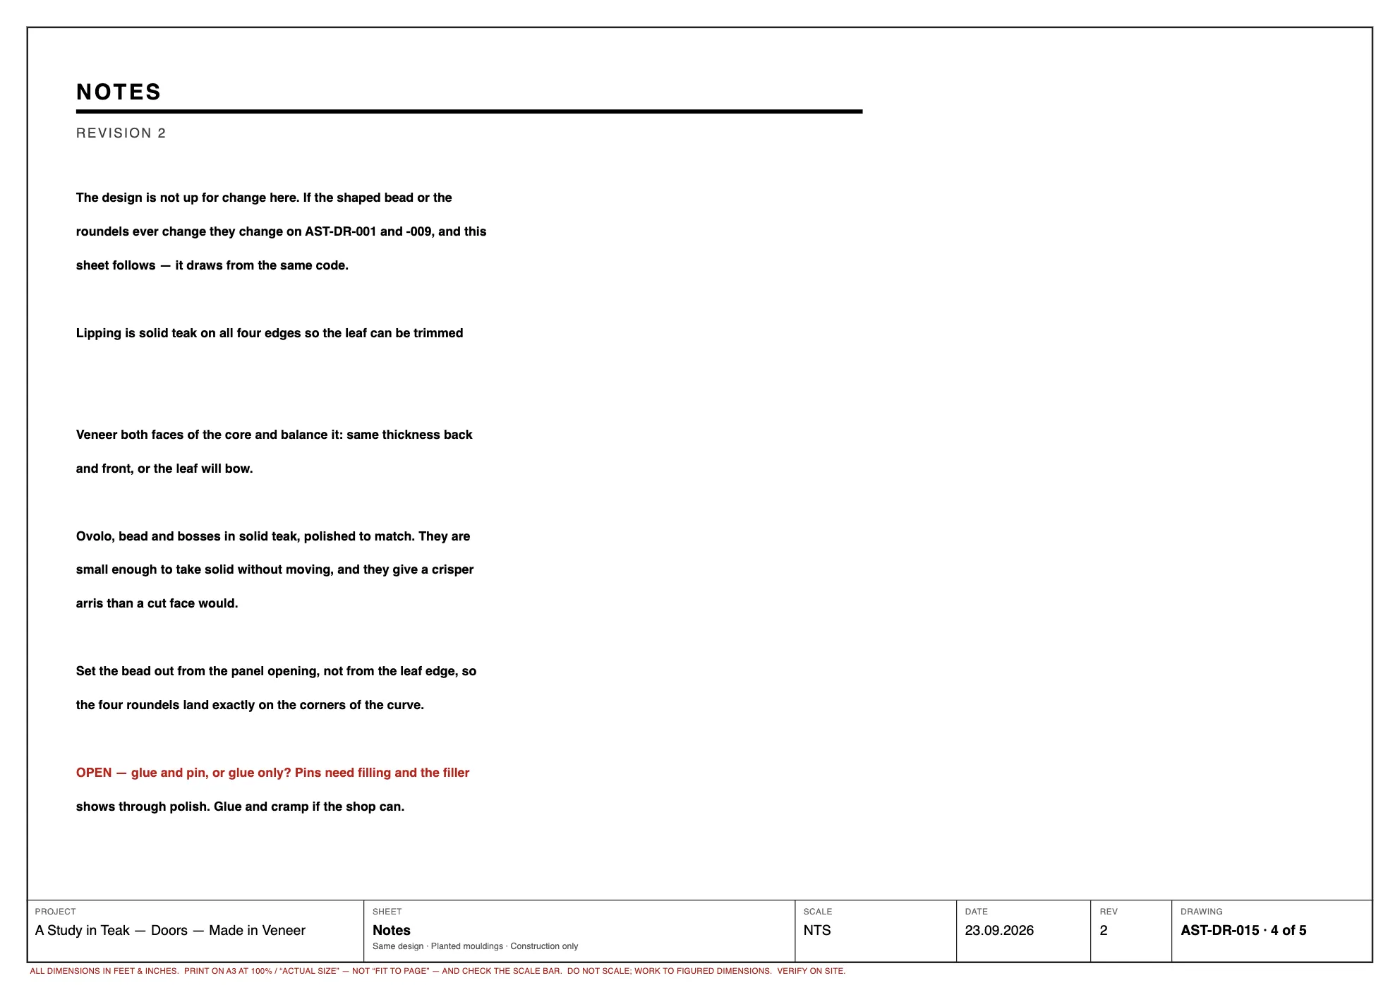
cad/print/doorveneer-04.webp
