sakshampan733-cloud/a-study-in-teak/cad/print/doorveneer-05.webp

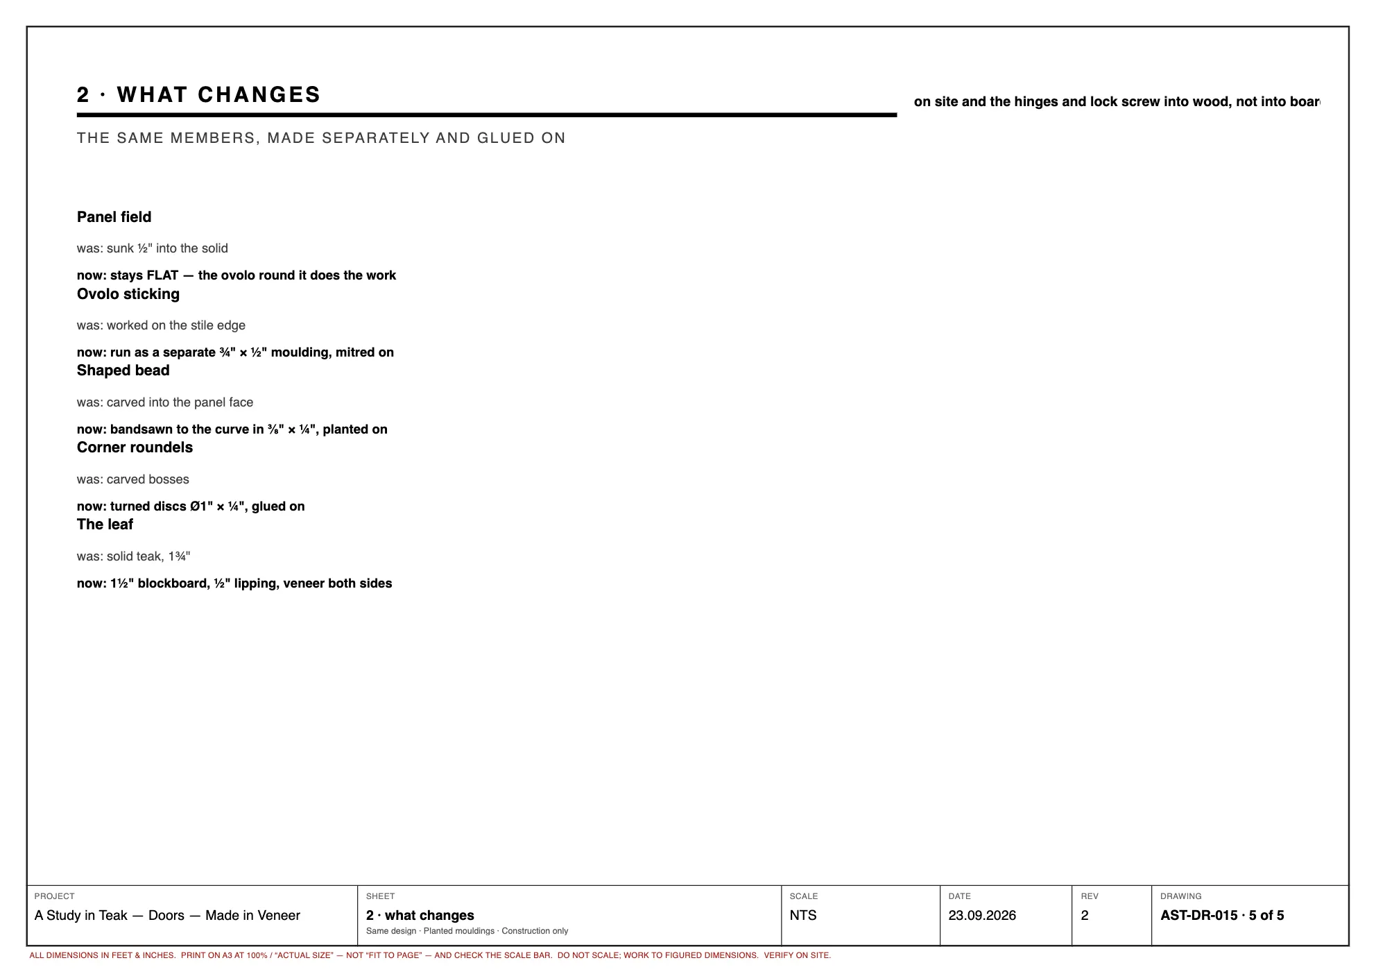
cad/print/doorveneer-05.webp
