sakshampan733-cloud/a-study-in-teak/cad/print/dressingshell-01.webp

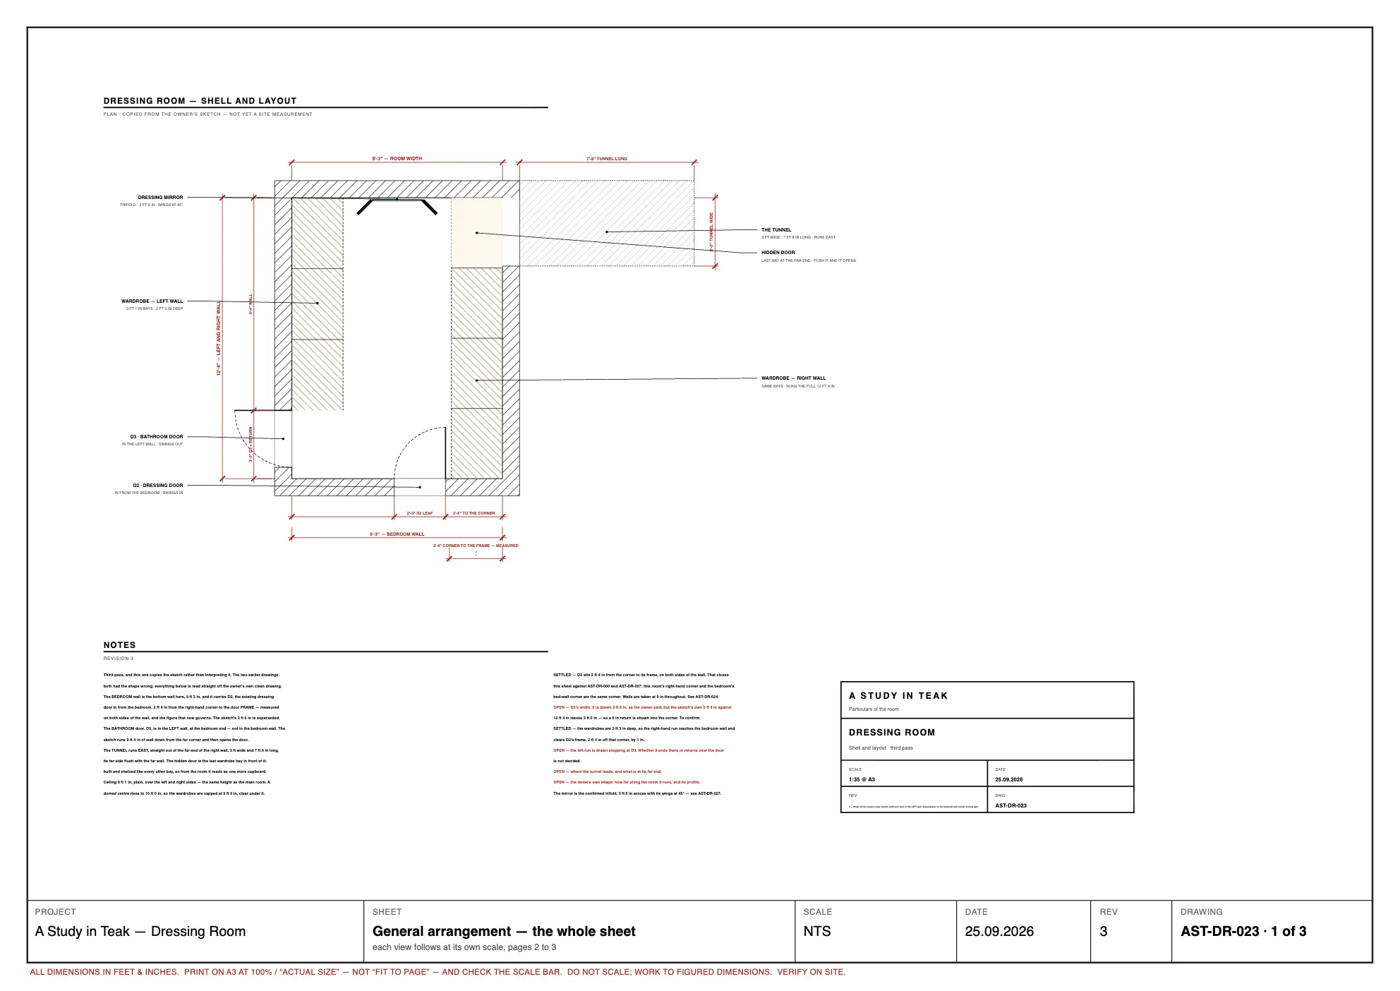
cad/print/dressingshell-01.webp
