sakshampan733-cloud/a-study-in-teak/cad/print/dressingshell-02.webp

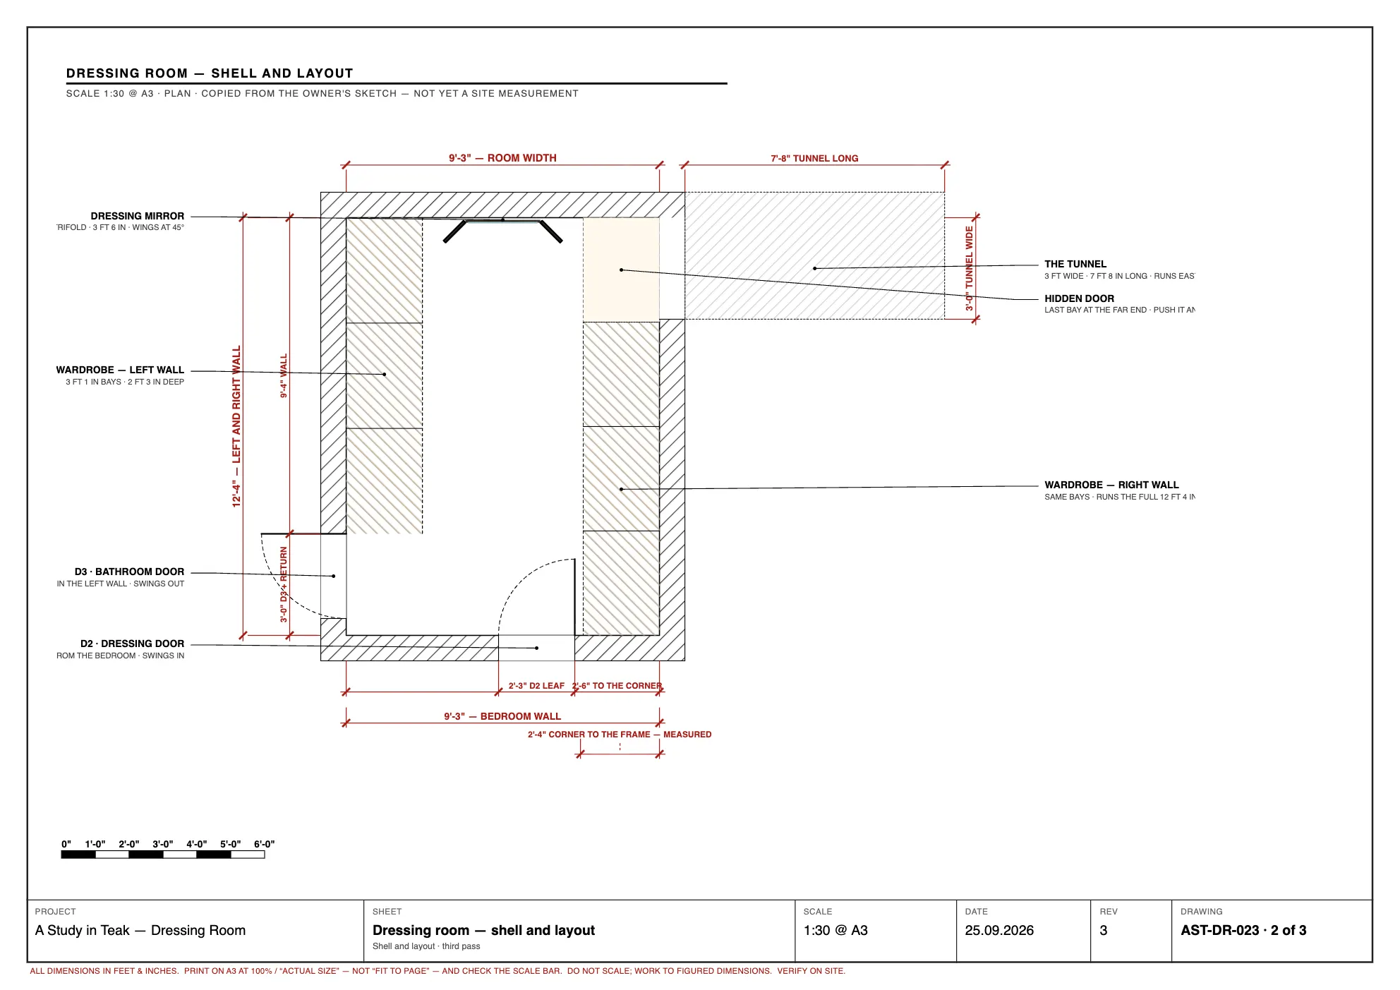
cad/print/dressingshell-02.webp
