sakshampan733-cloud/a-study-in-teak/cad/print/dressingshell-03.webp

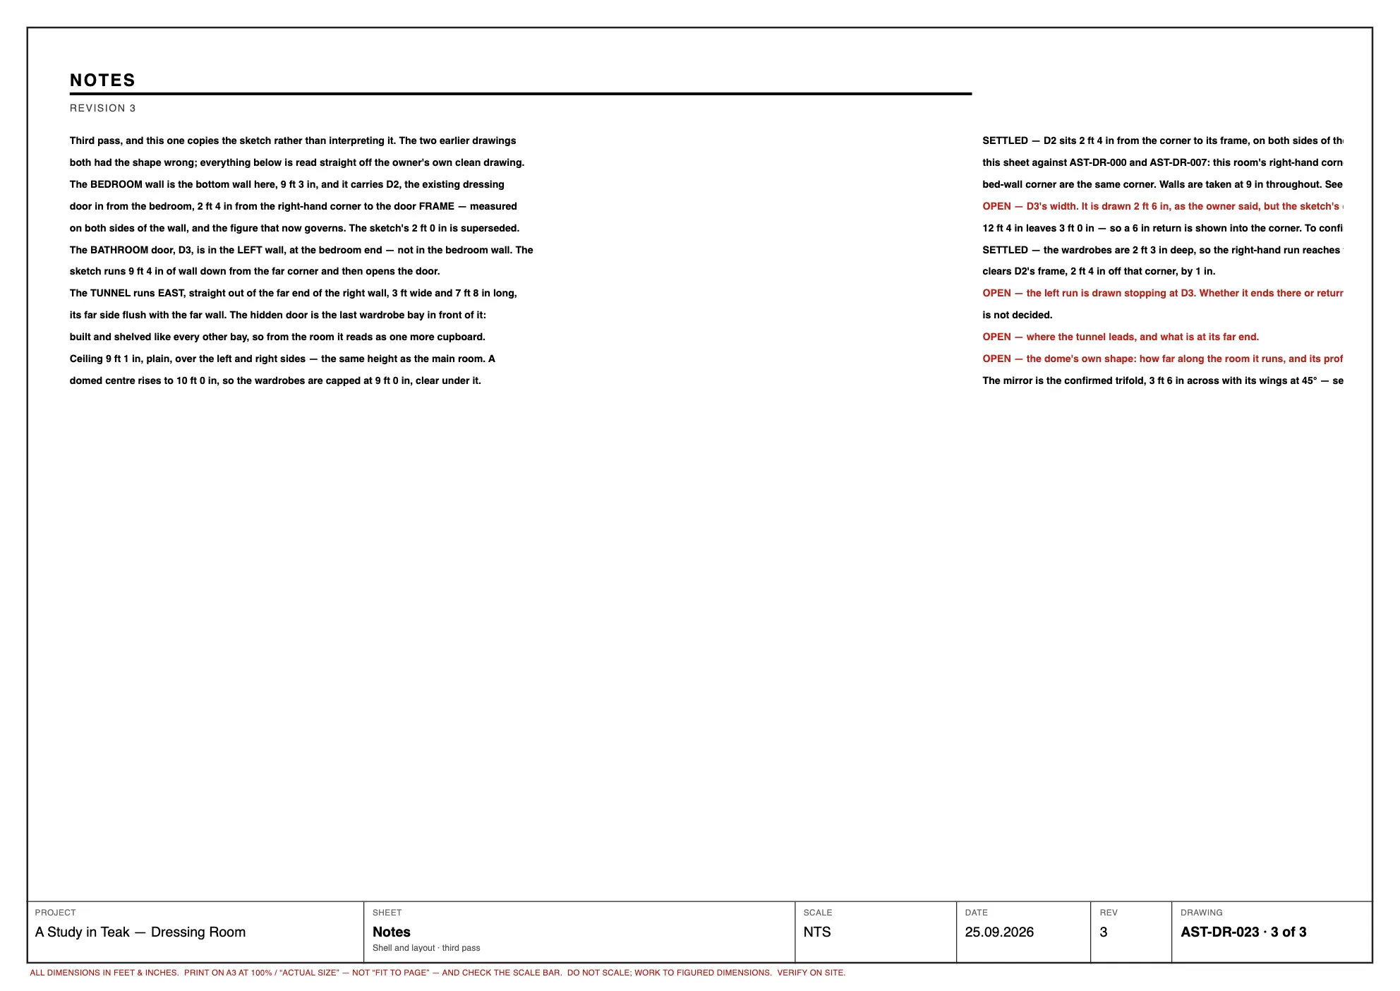
cad/print/dressingshell-03.webp
