sakshampan733-cloud/a-study-in-teak/cad/print/foldslide-01.webp

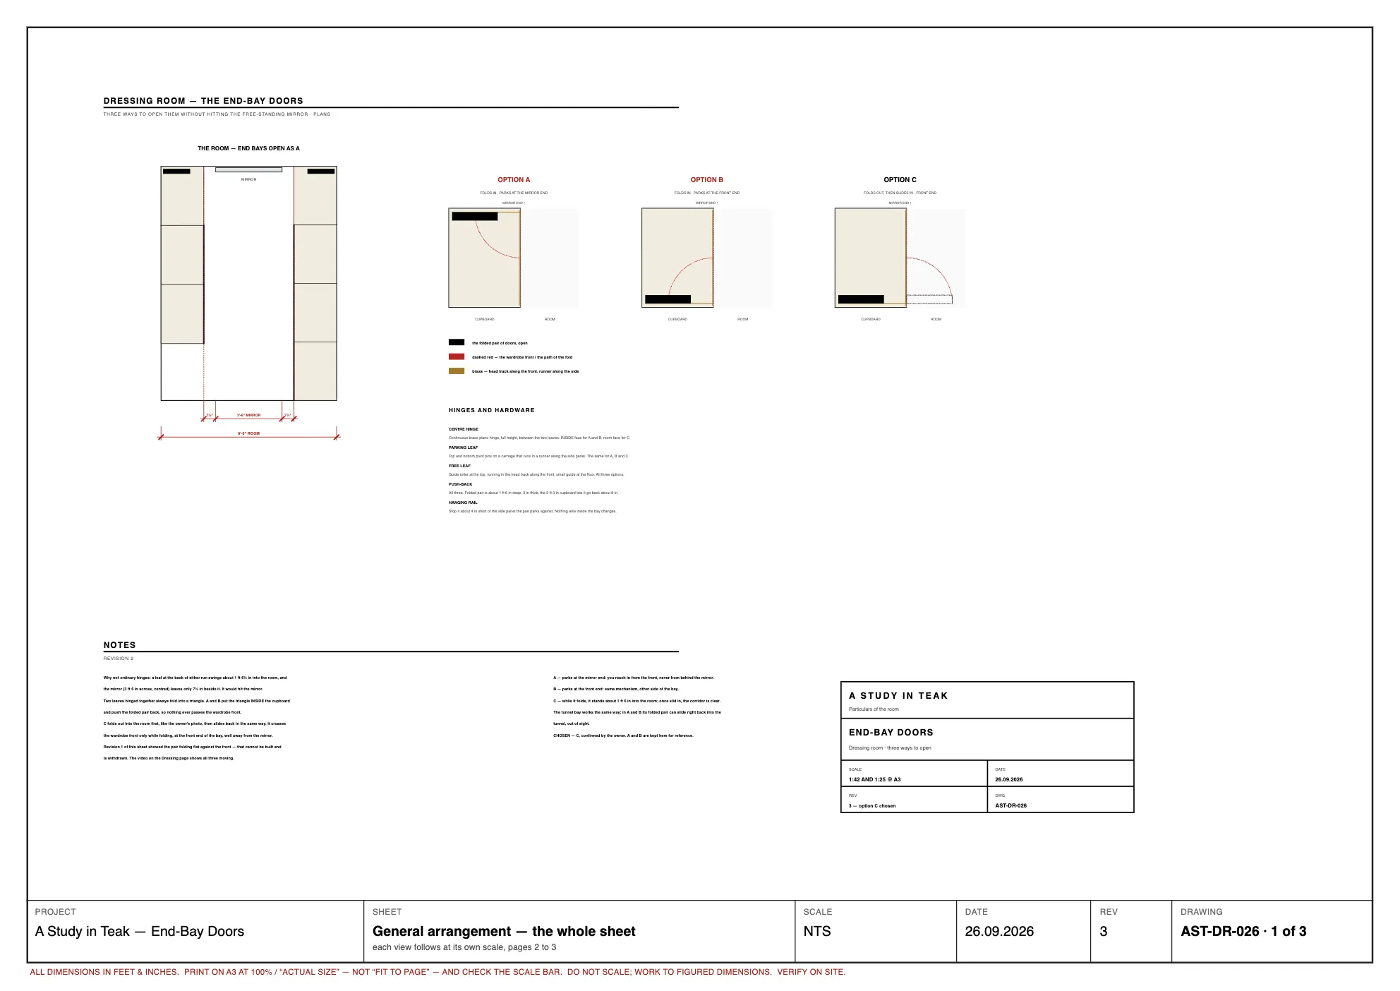
cad/print/foldslide-01.webp
