sakshampan733-cloud/a-study-in-teak/cad/print/foldslide-02.webp

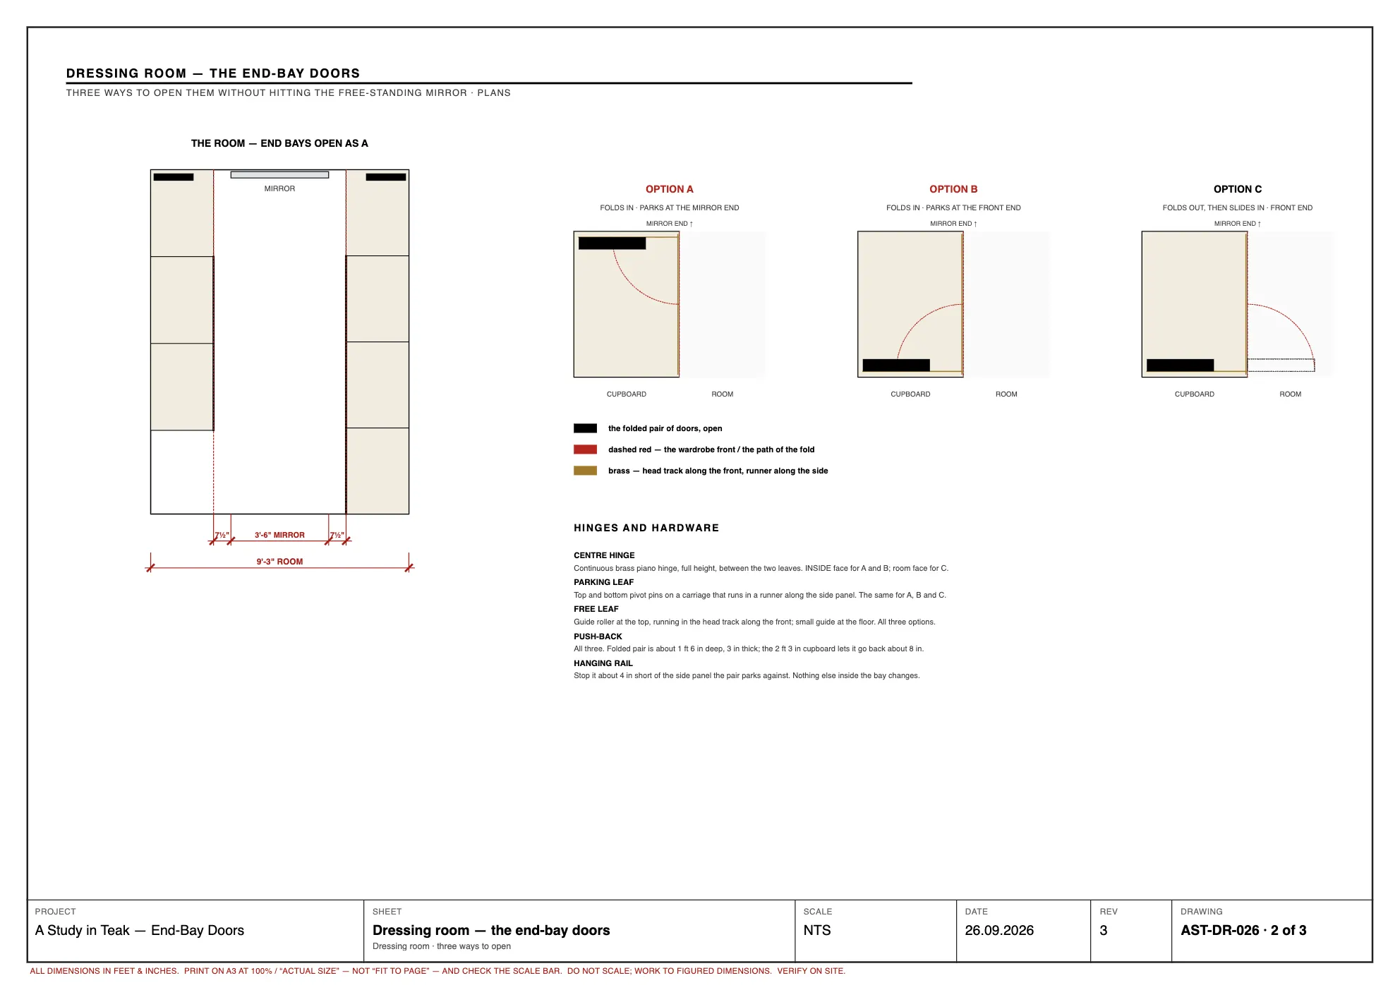
cad/print/foldslide-02.webp
