sakshampan733-cloud/a-study-in-teak/cad/print/foldslide-03.webp

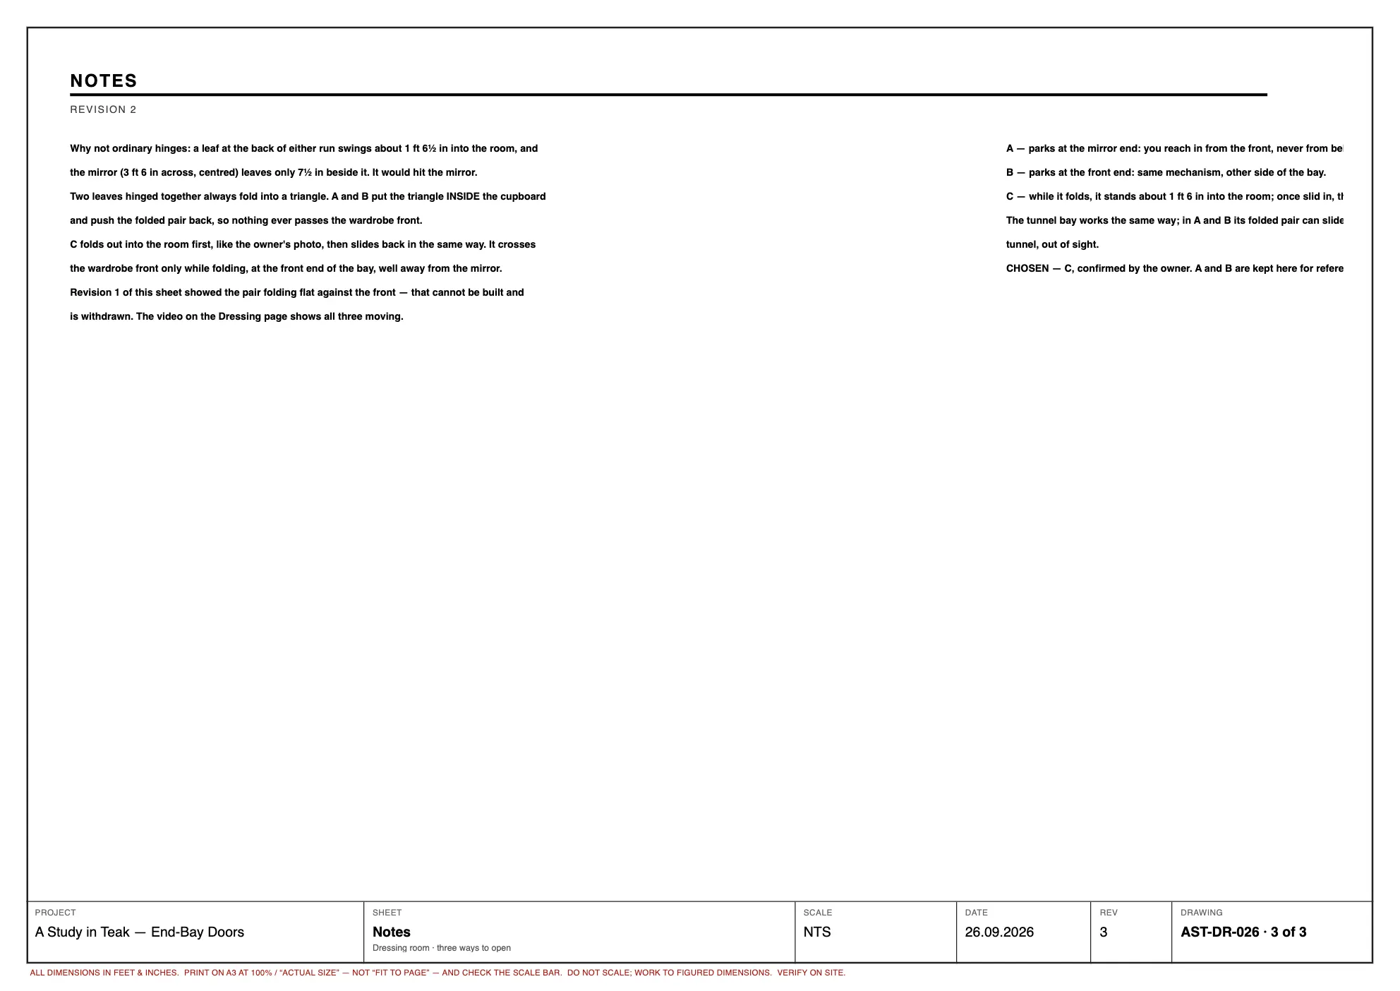
cad/print/foldslide-03.webp
