sakshampan733-cloud/a-study-in-teak/cad/print/leftwall-01.webp

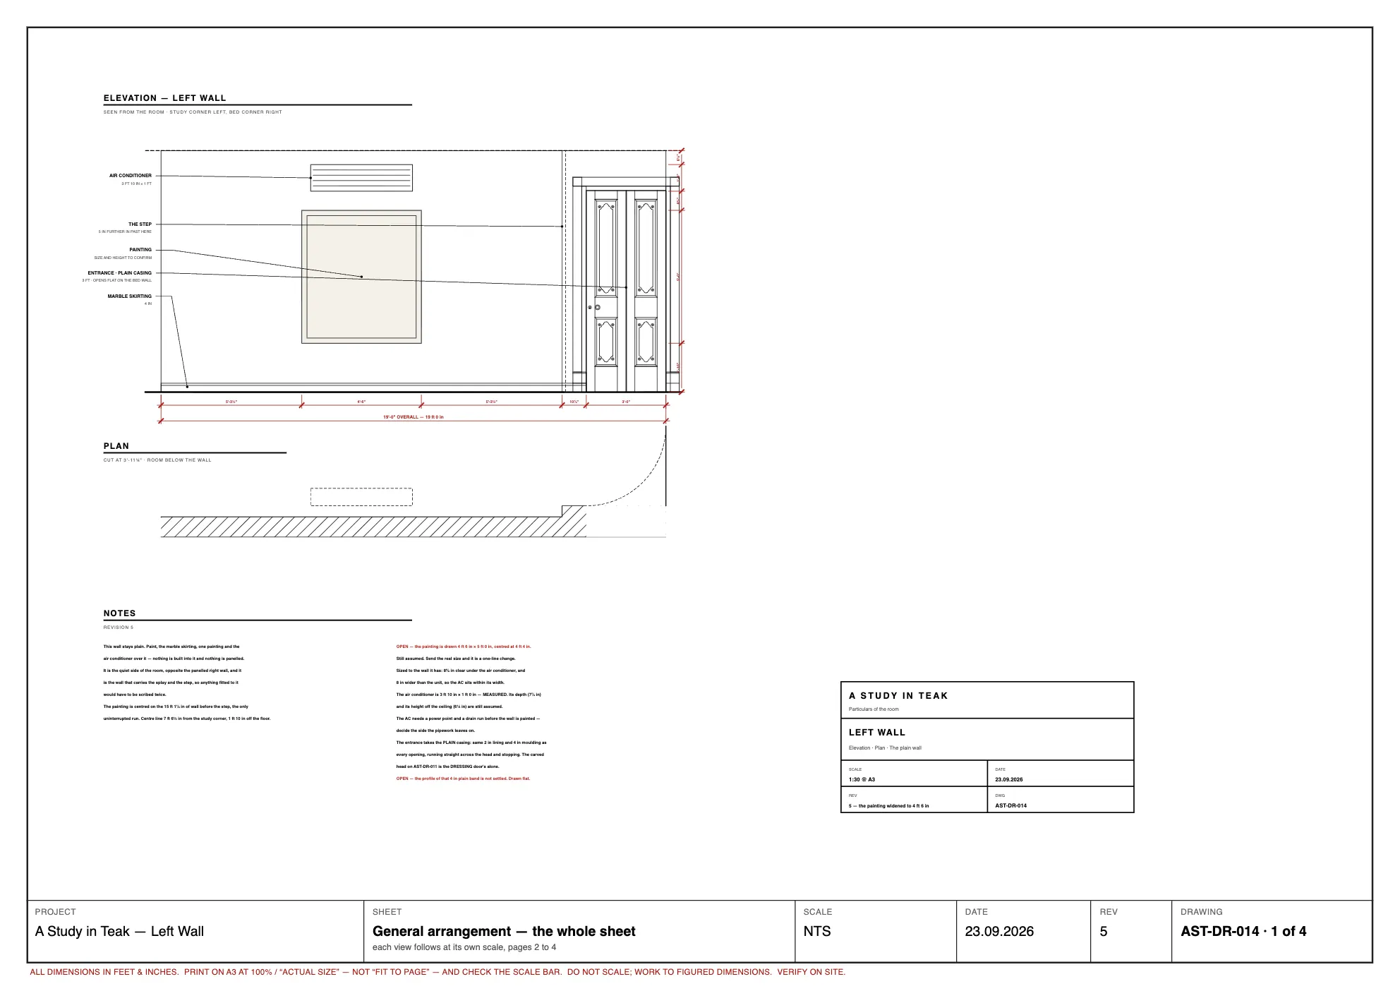
cad/print/leftwall-01.webp
