sakshampan733-cloud/a-study-in-teak/cad/print/leftwall-04.webp

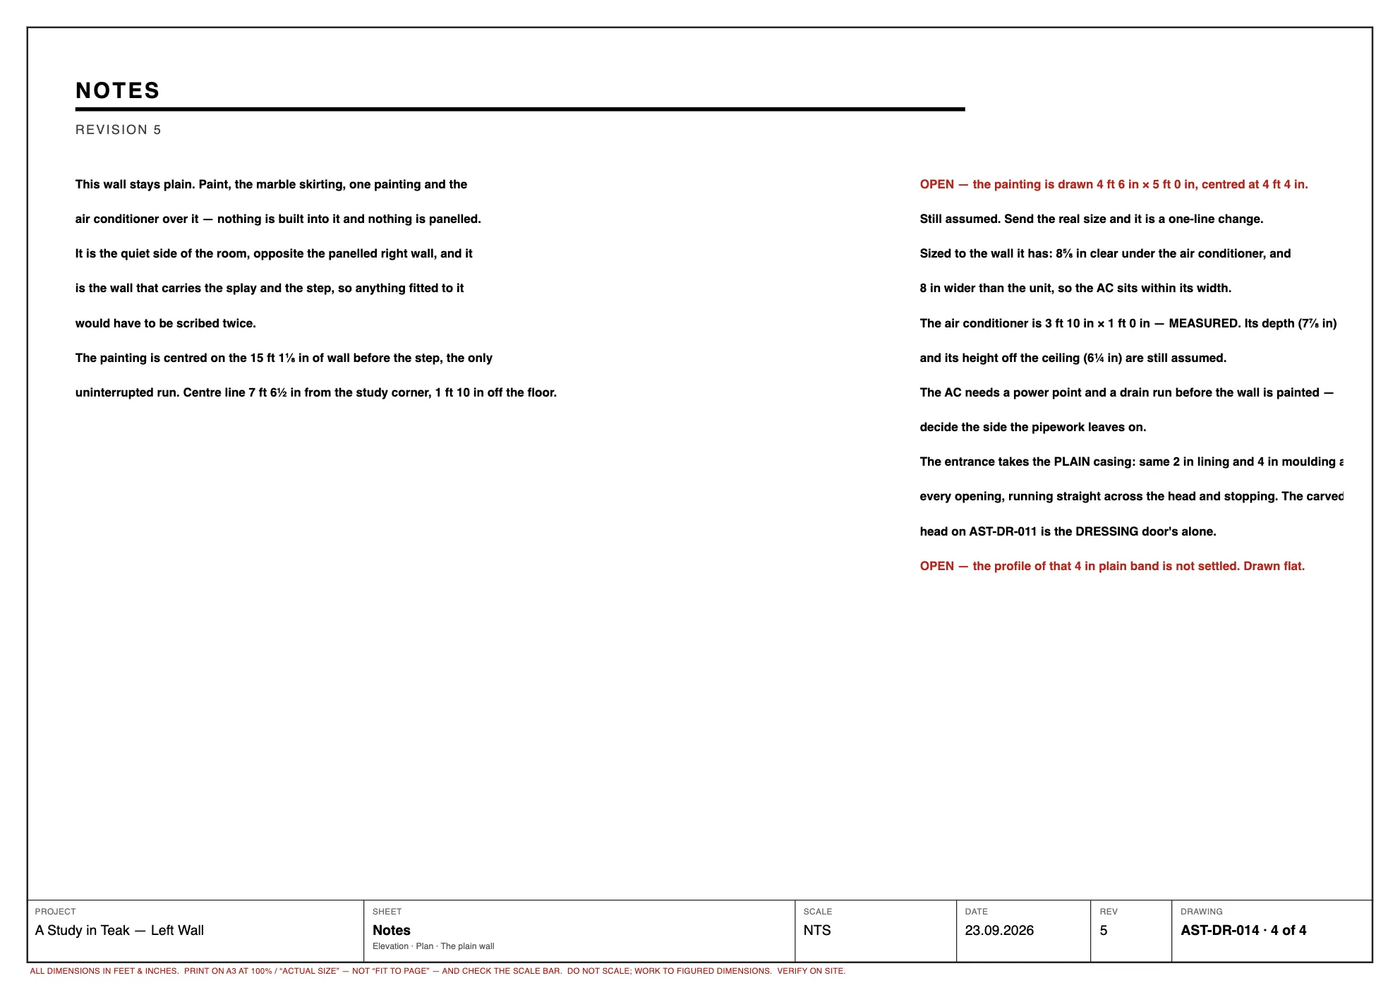
cad/print/leftwall-04.webp
