sakshampan733-cloud/a-study-in-teak/cad/print/mirror-01.webp

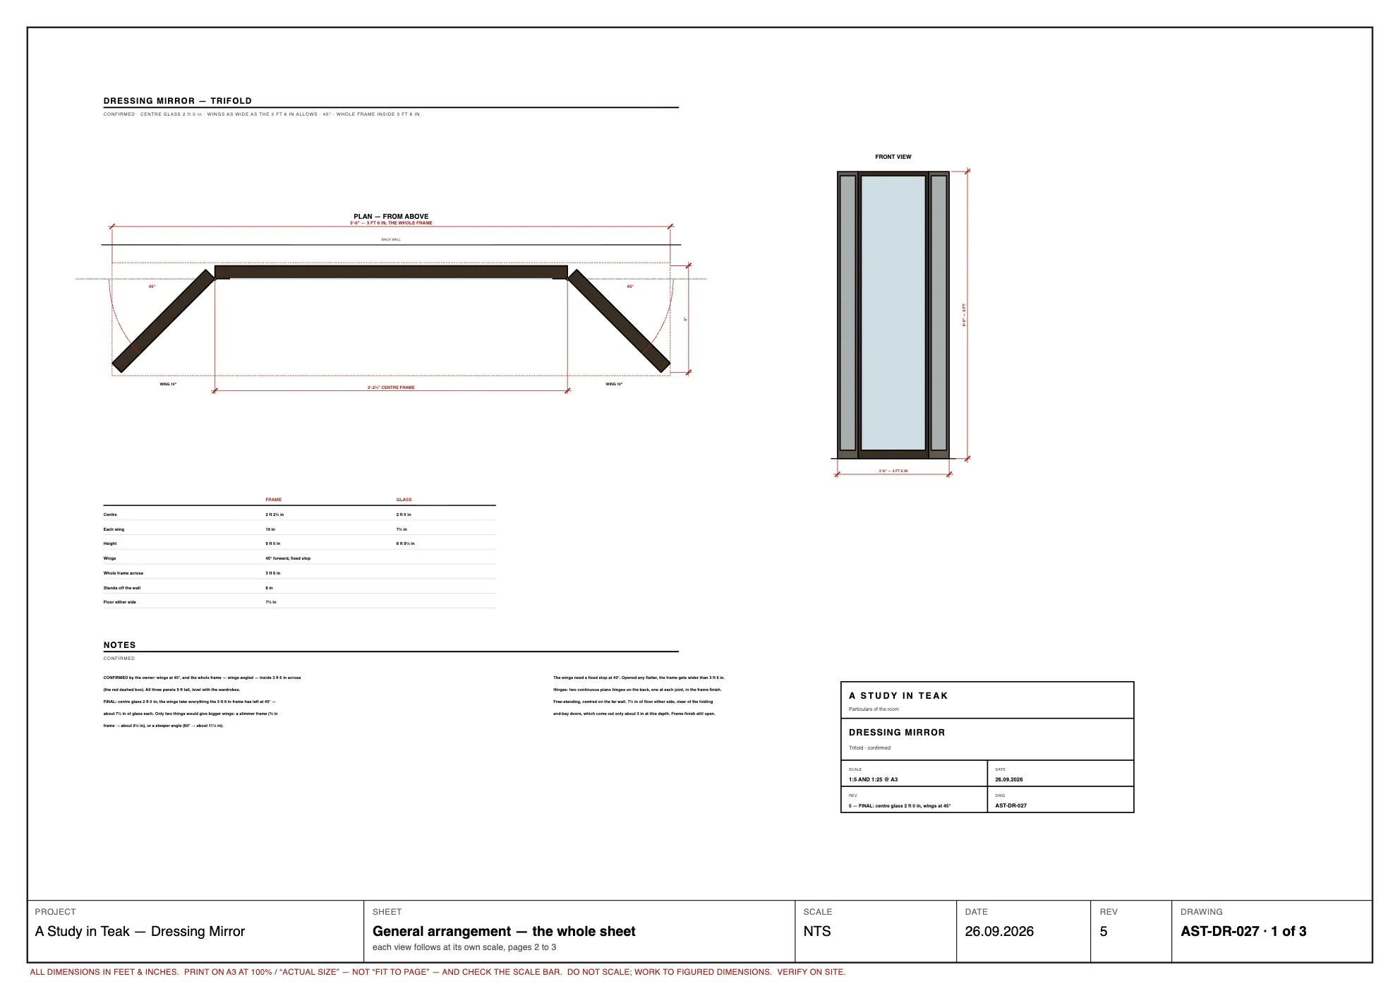
cad/print/mirror-01.webp
