sakshampan733-cloud/a-study-in-teak/cad/print/rightwall-01.webp

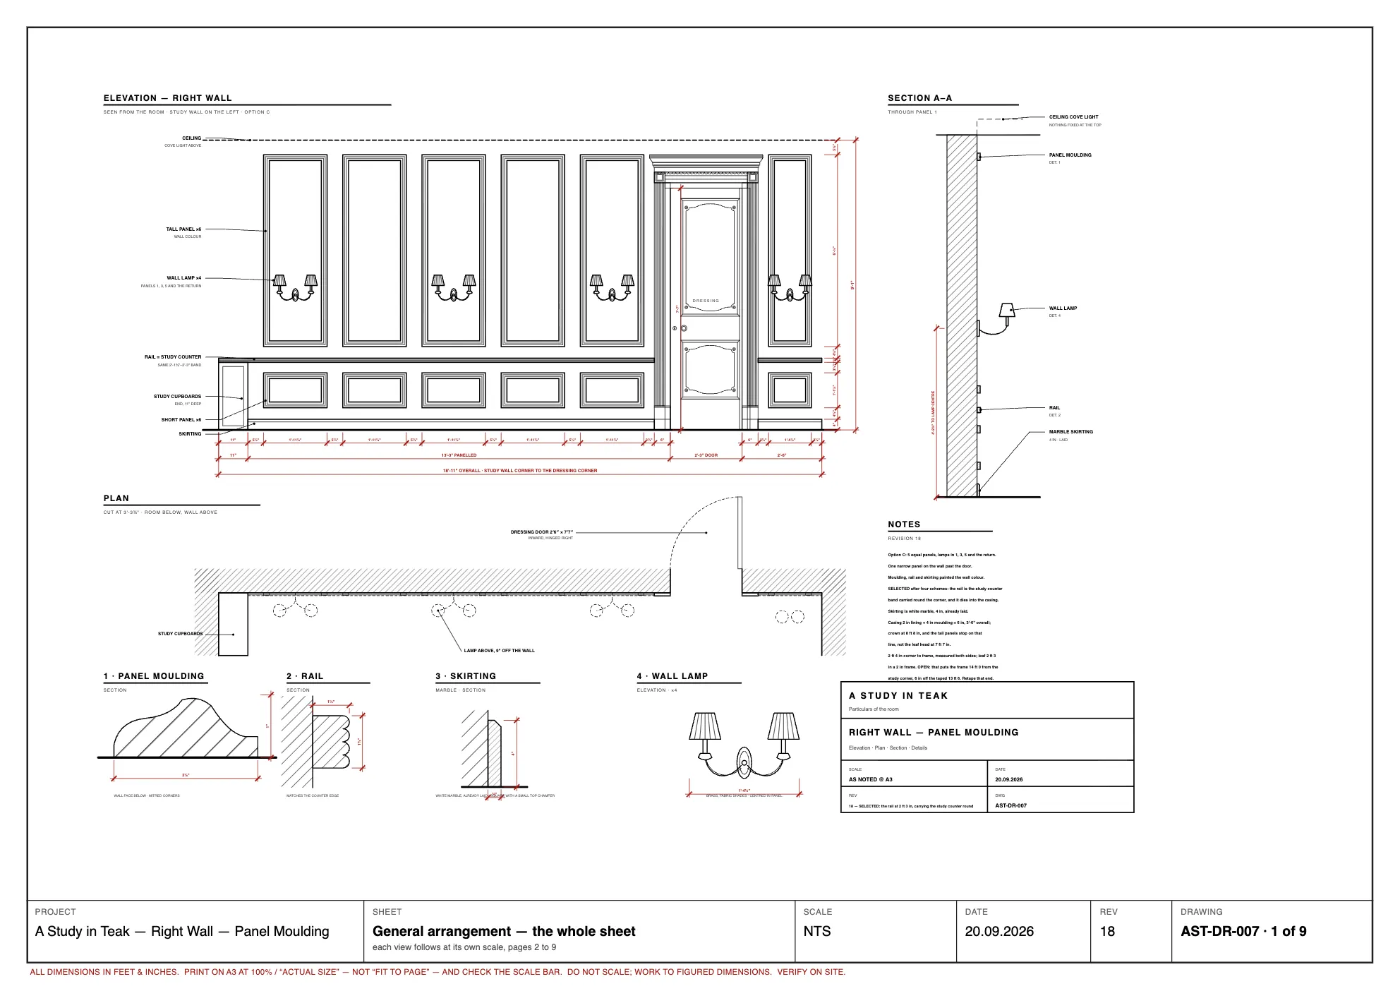
cad/print/rightwall-01.webp
