sakshampan733-cloud/a-study-in-teak/cad/print/rightwall-02.webp

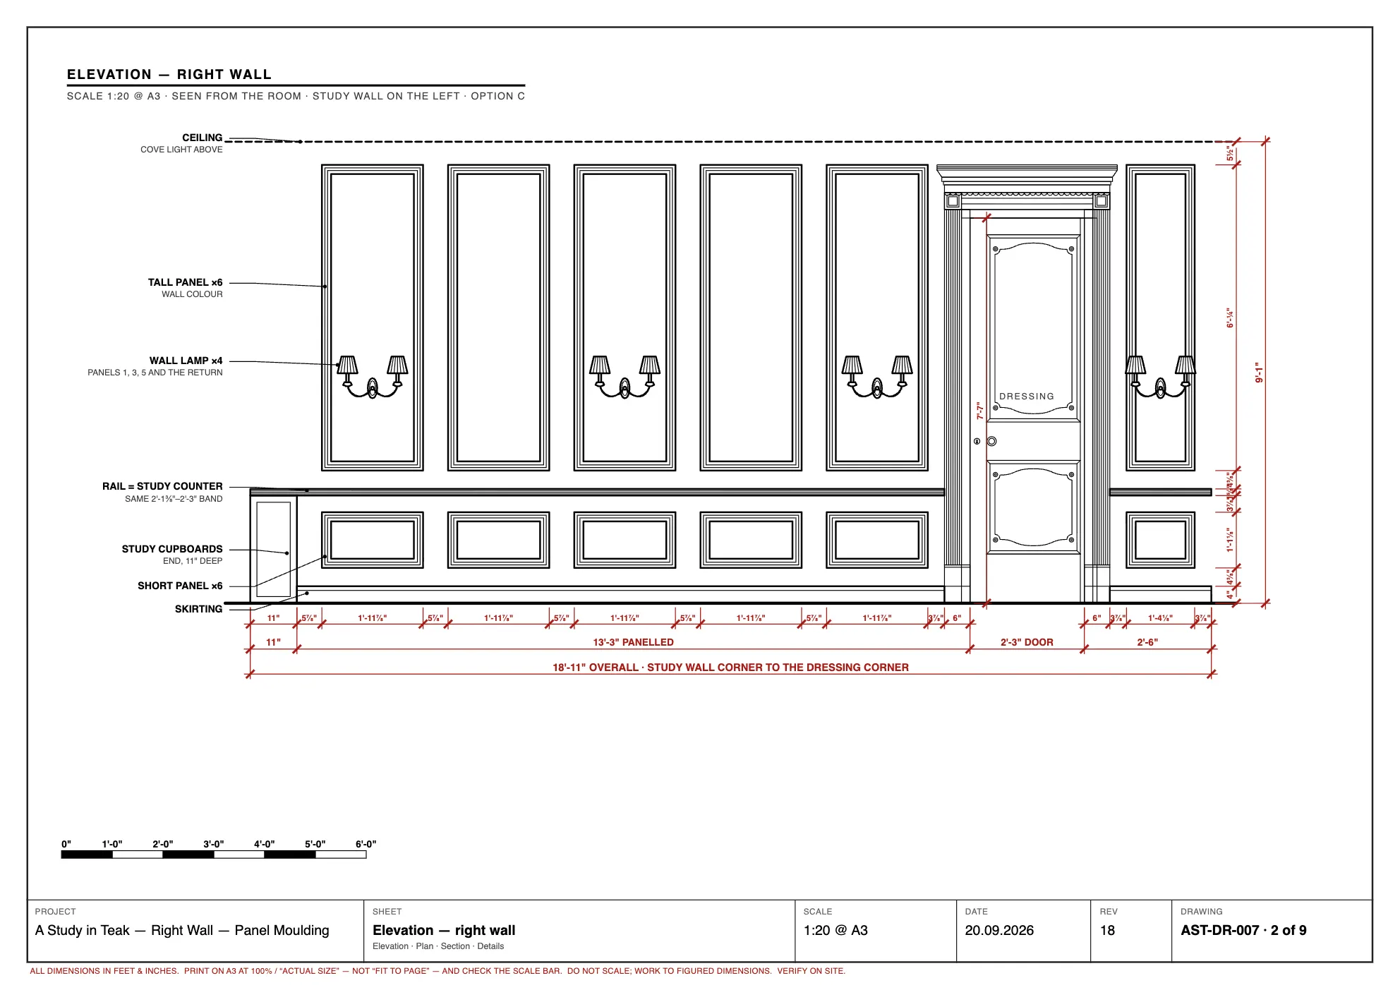
cad/print/rightwall-02.webp
