sakshampan733-cloud/a-study-in-teak/cad/print/rightwall-04.webp

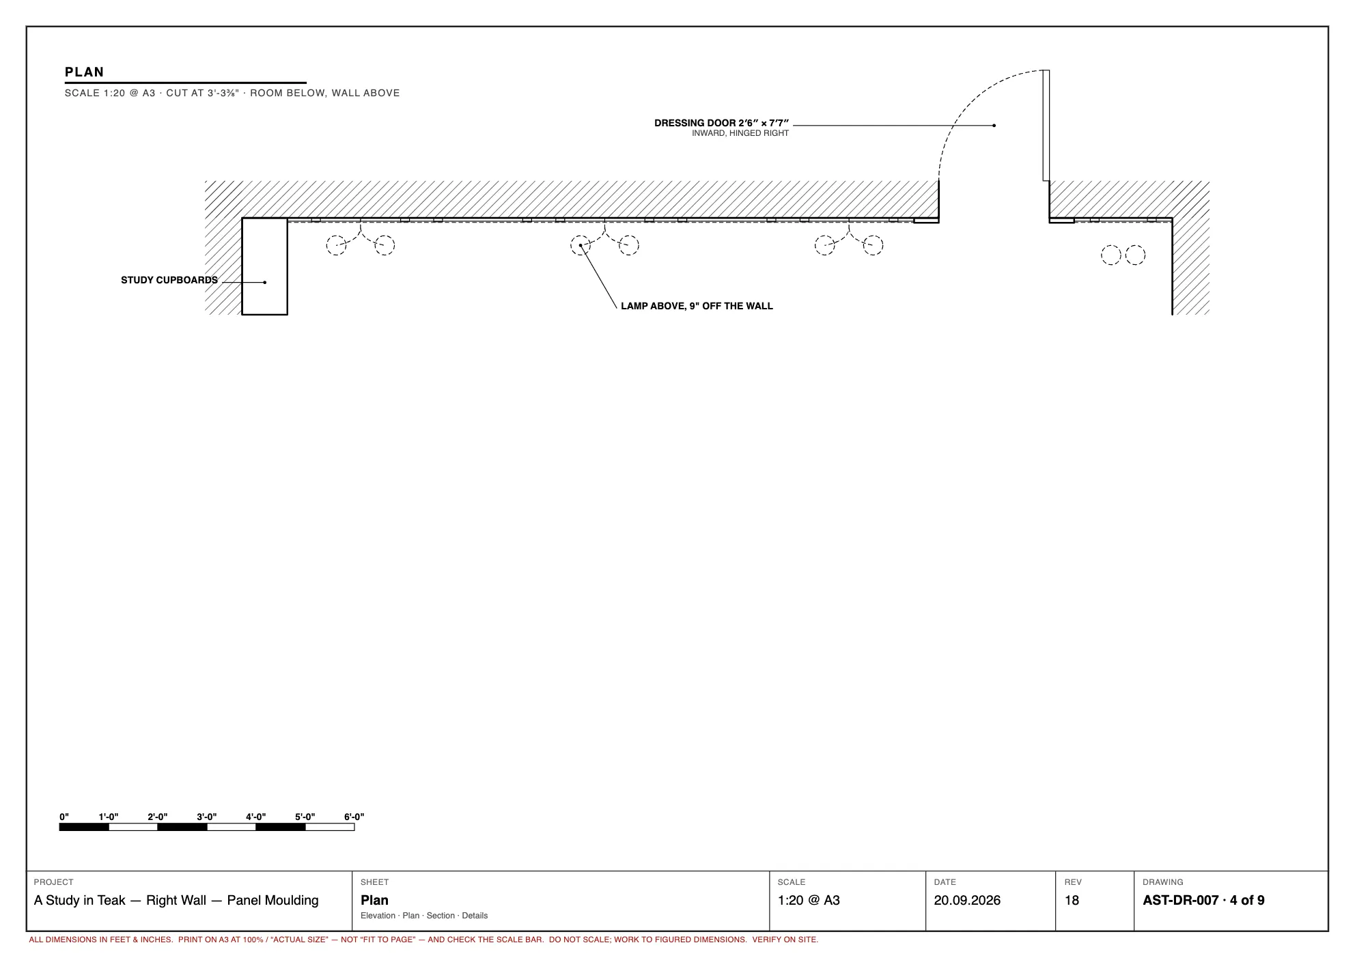
cad/print/rightwall-04.webp
