sakshampan733-cloud/a-study-in-teak/cad/print/rightwall-05.webp

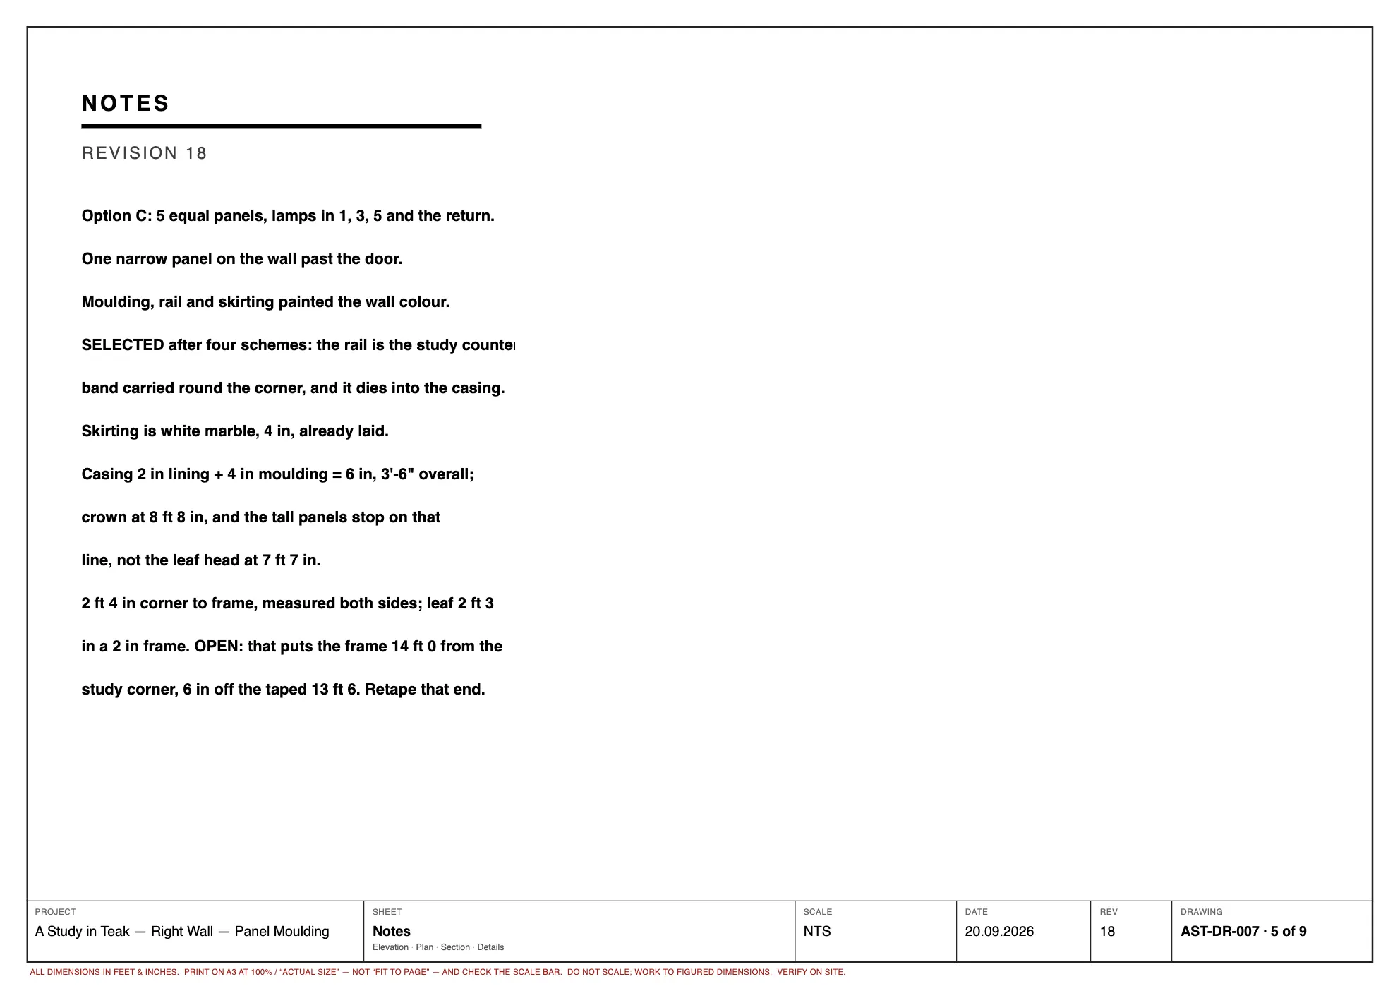
cad/print/rightwall-05.webp
