sakshampan733-cloud/a-study-in-teak/cad/print/rightwall-06.webp

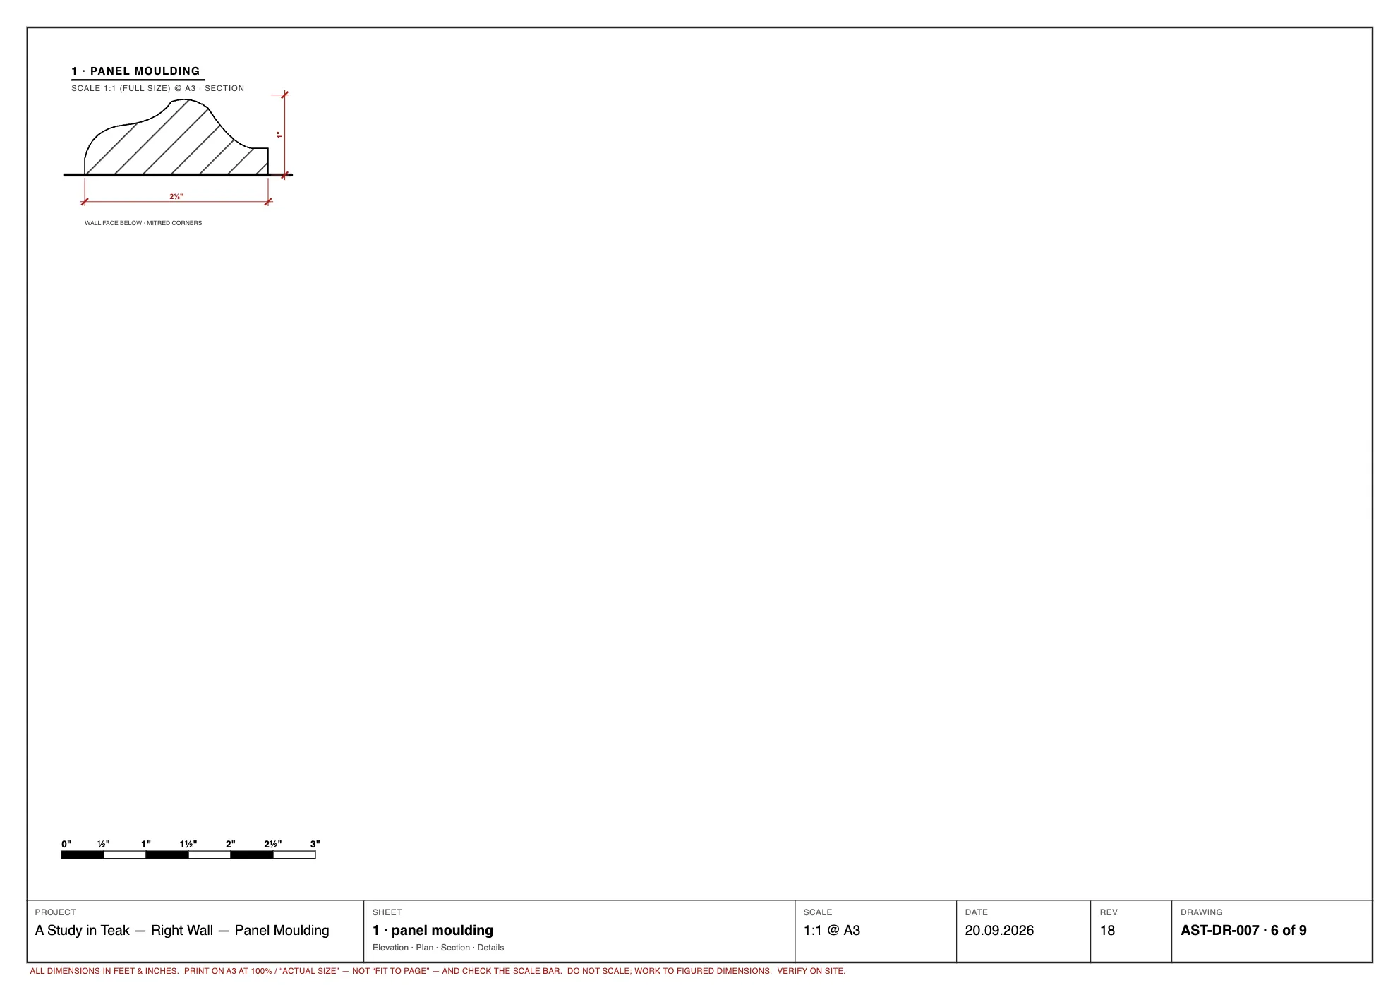
cad/print/rightwall-06.webp
