sakshampan733-cloud/a-study-in-teak/cad/print/rightwall-07.webp

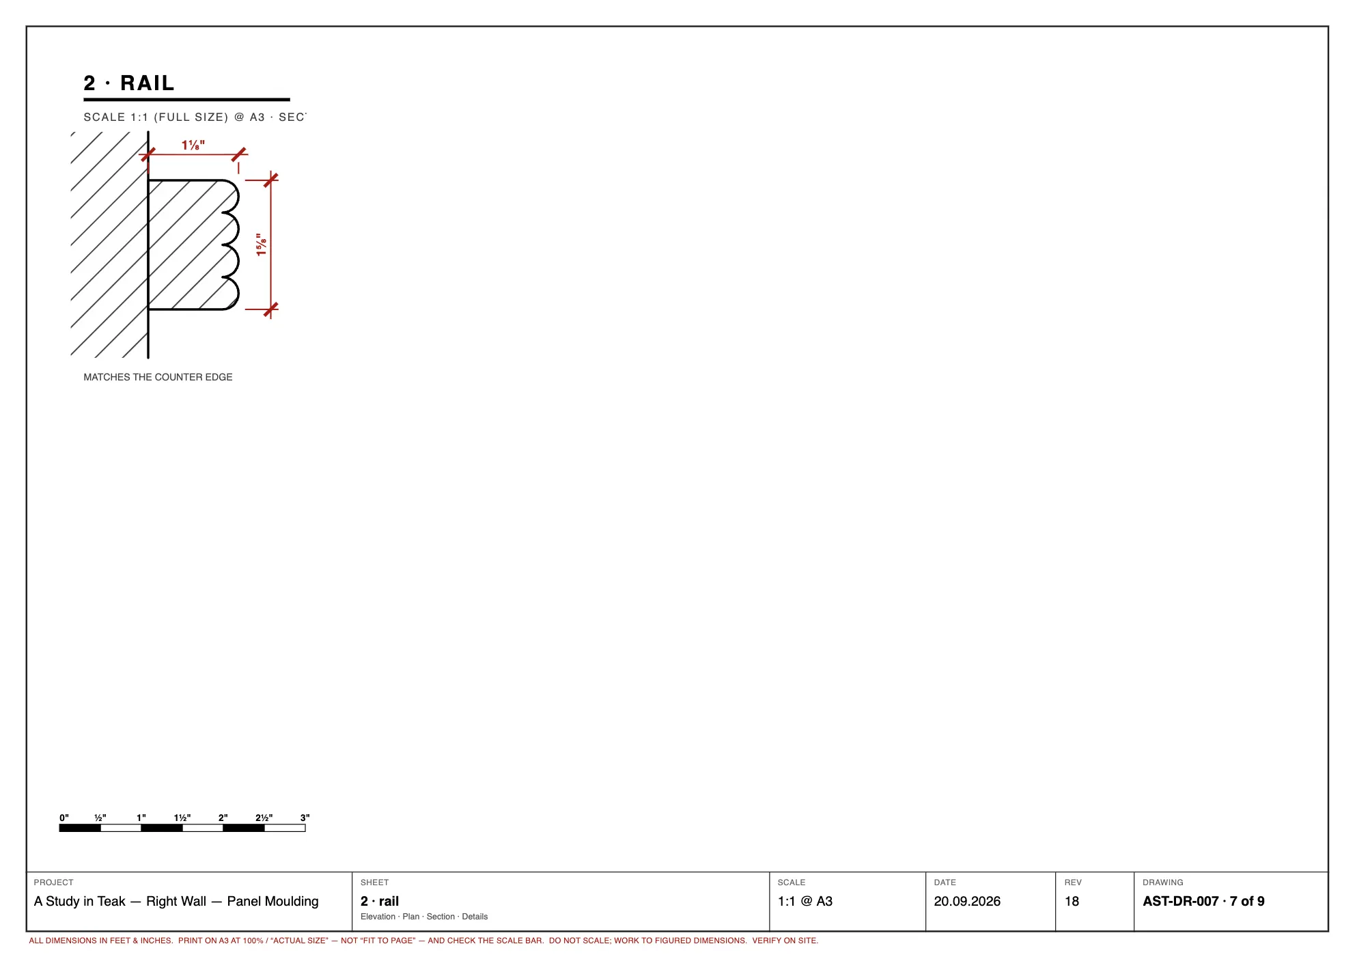
cad/print/rightwall-07.webp
