sakshampan733-cloud/a-study-in-teak/cad/print/rightwall-09.webp

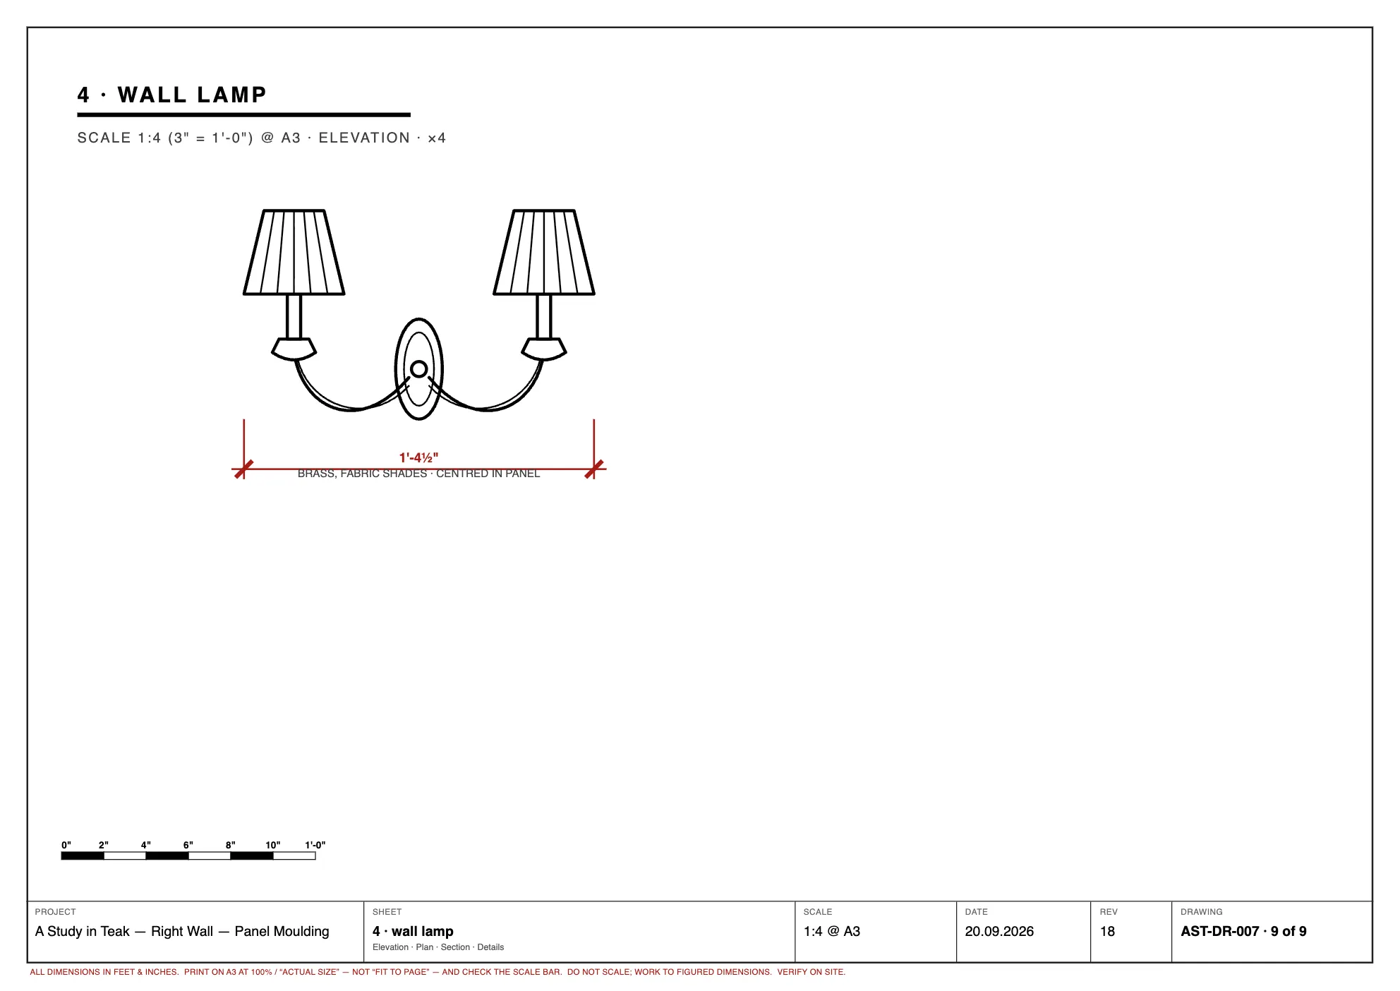
cad/print/rightwall-09.webp
