sakshampan733-cloud/a-study-in-teak/cad/print/roomshell-01.webp

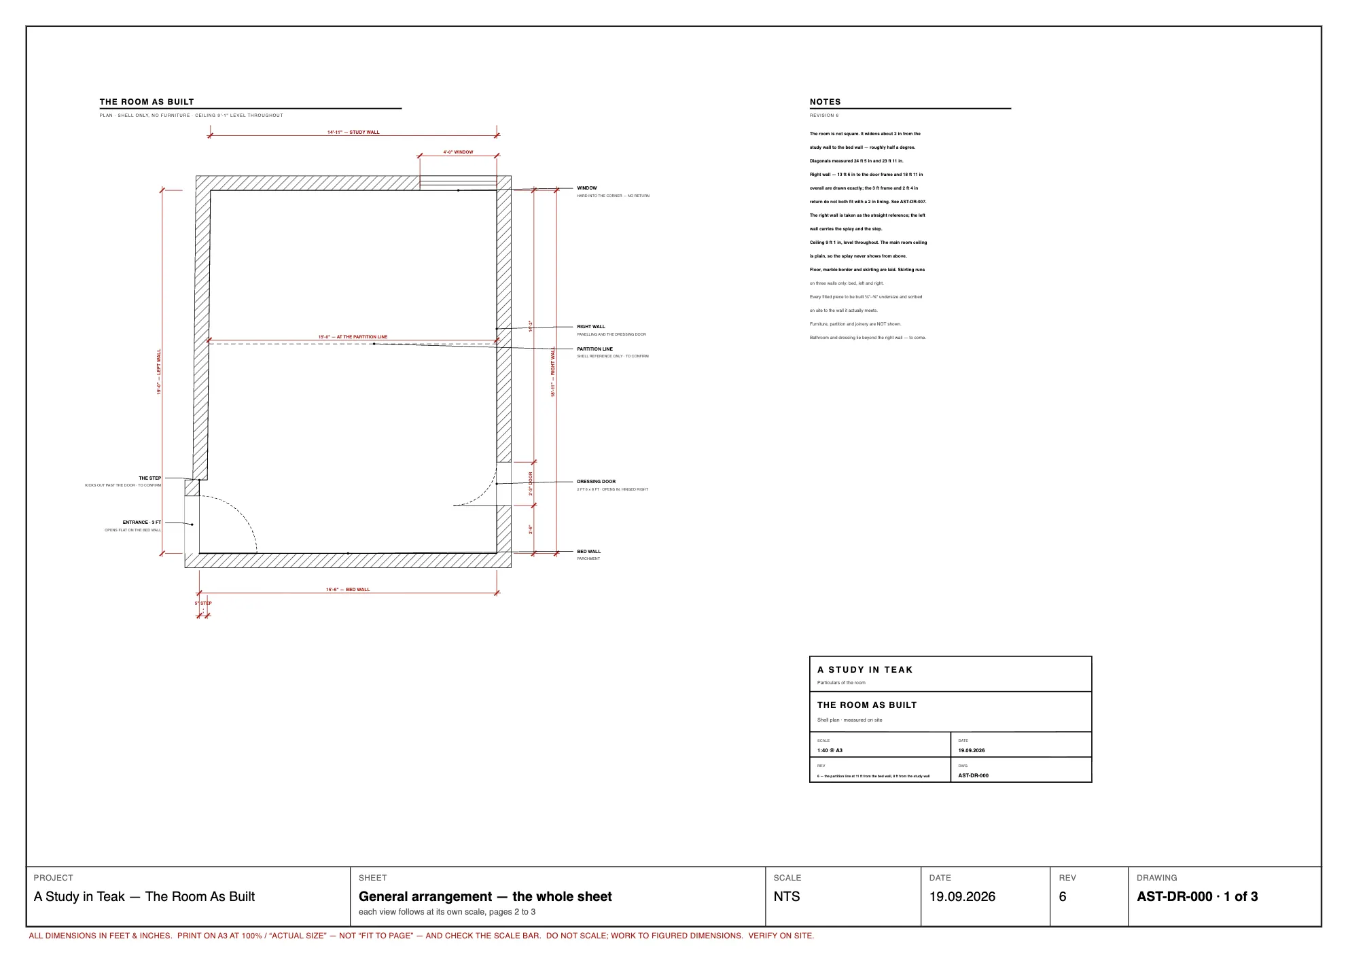
cad/print/roomshell-01.webp
