sakshampan733-cloud/a-study-in-teak/cad/print/roomshell-02.webp

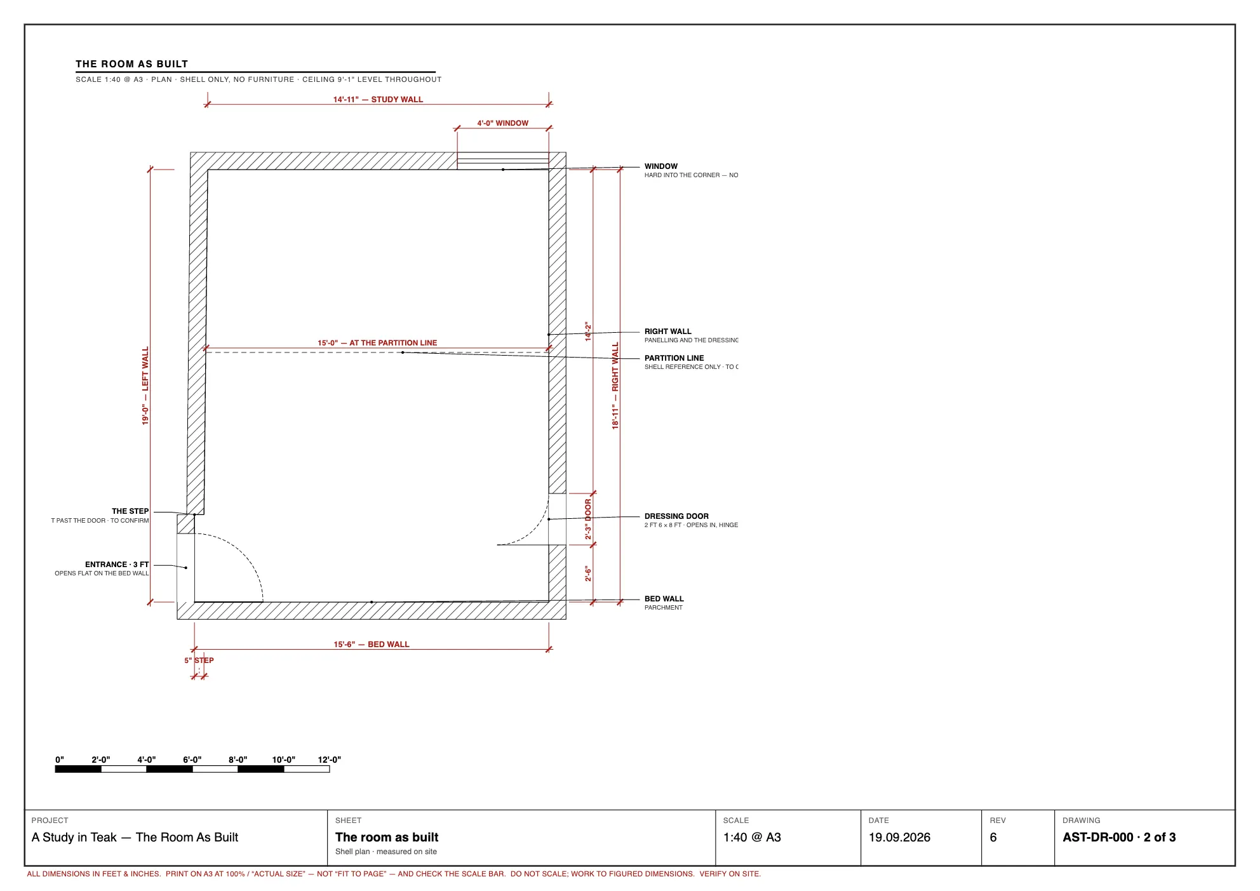
cad/print/roomshell-02.webp
