sakshampan733-cloud/a-study-in-teak/cad/print/roomshell-03.webp

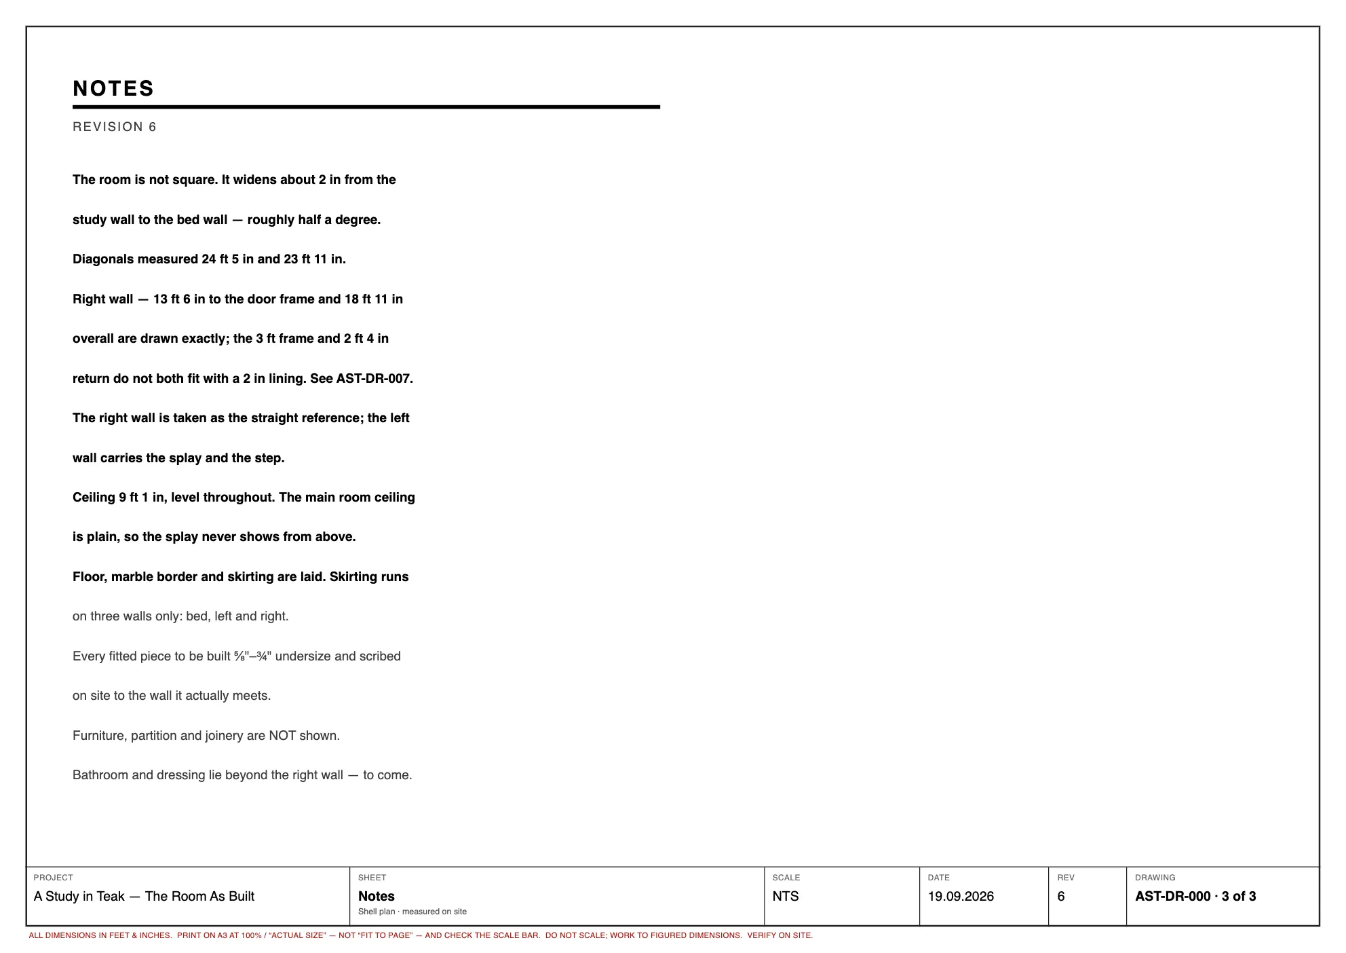
cad/print/roomshell-03.webp
