sakshampan733-cloud/a-study-in-teak/cad/print/sidetable-01.webp

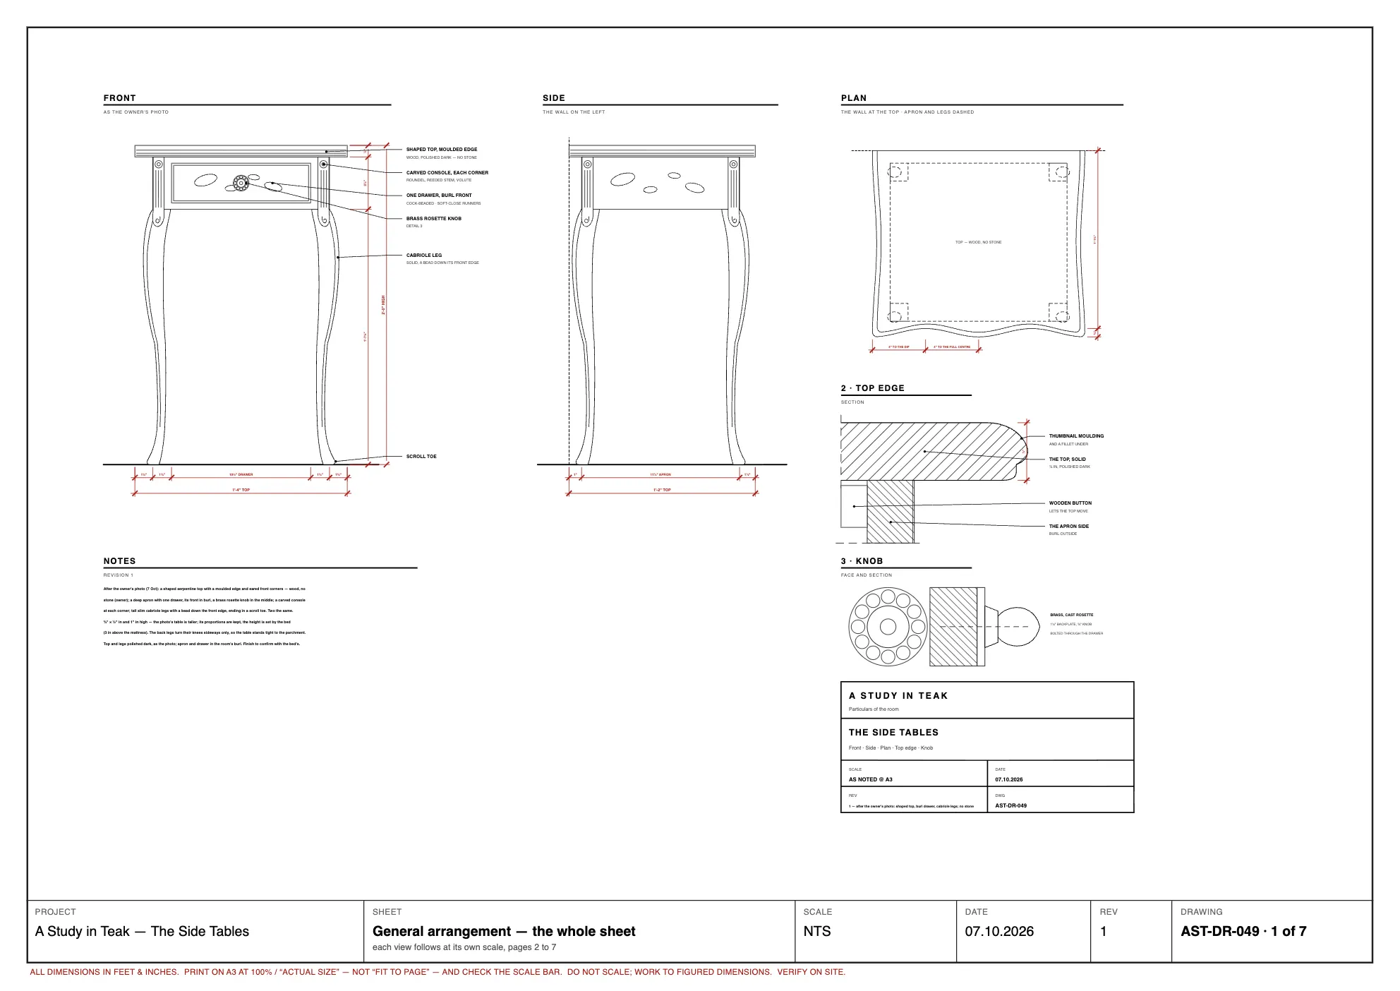
cad/print/sidetable-01.webp
