sakshampan733-cloud/a-study-in-teak/cad/print/sidetable-02.webp

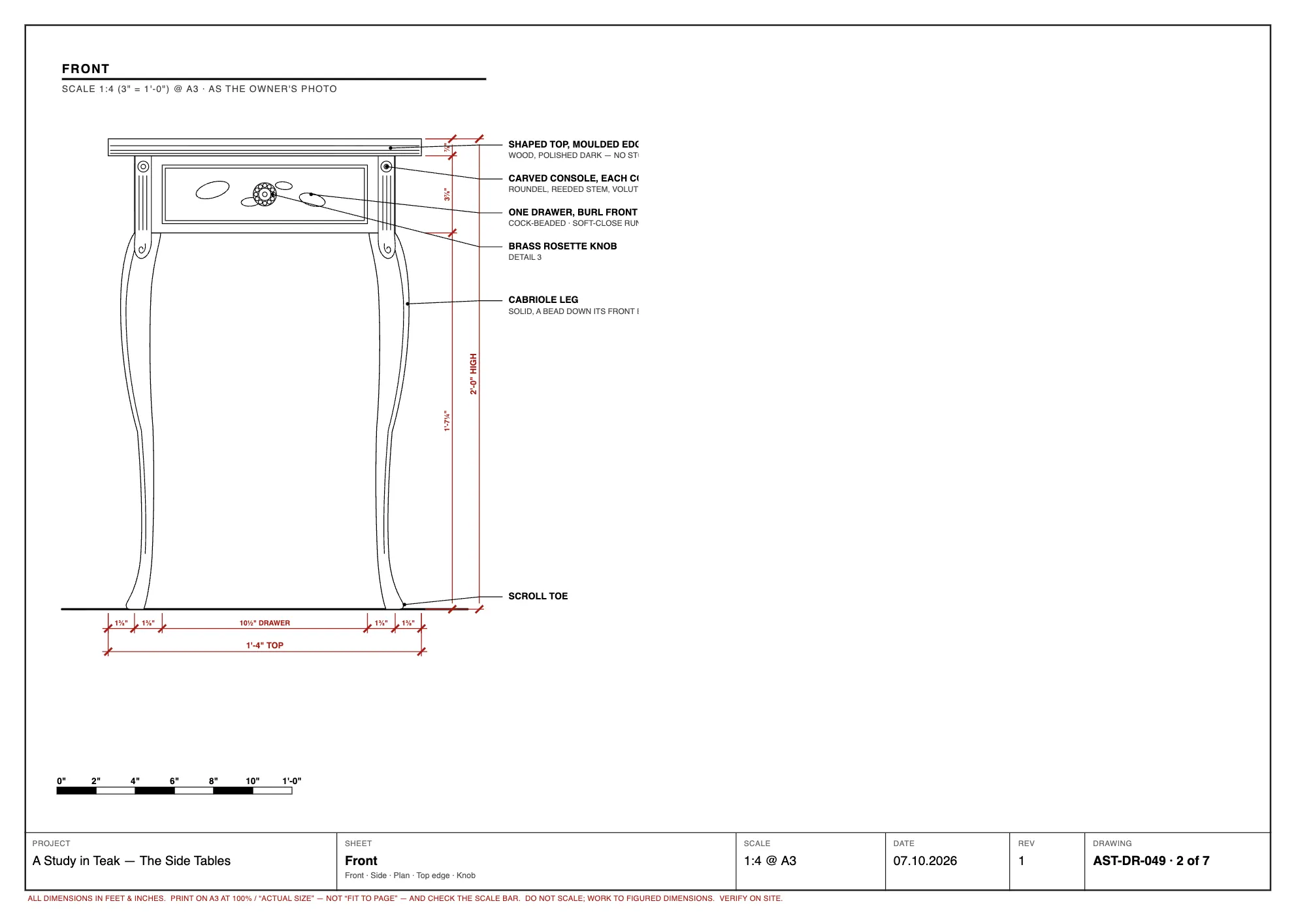
cad/print/sidetable-02.webp
