sakshampan733-cloud/a-study-in-teak/cad/print/sidetable-03.webp

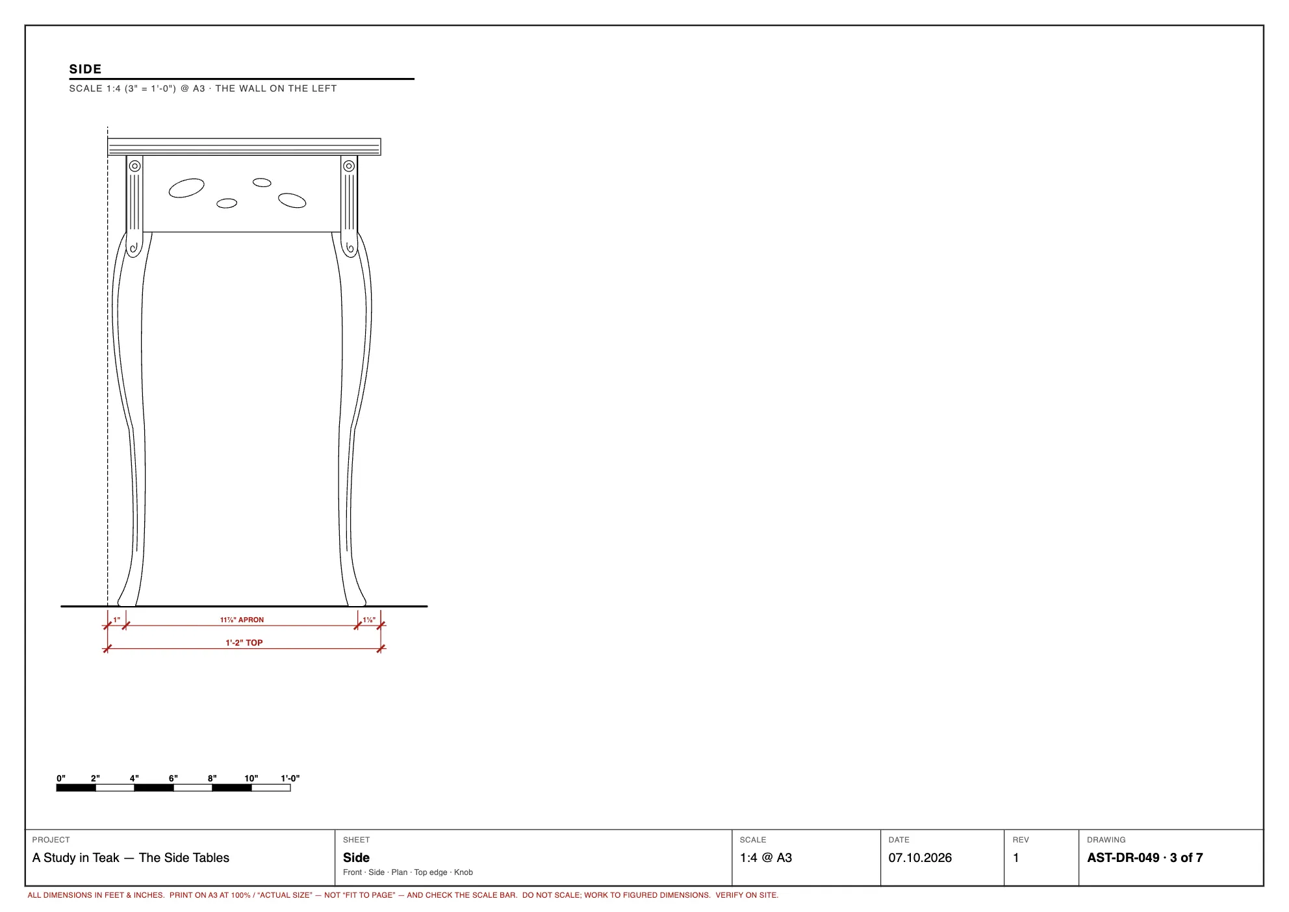
cad/print/sidetable-03.webp
