sakshampan733-cloud/a-study-in-teak/cad/print/sidetable-05.webp

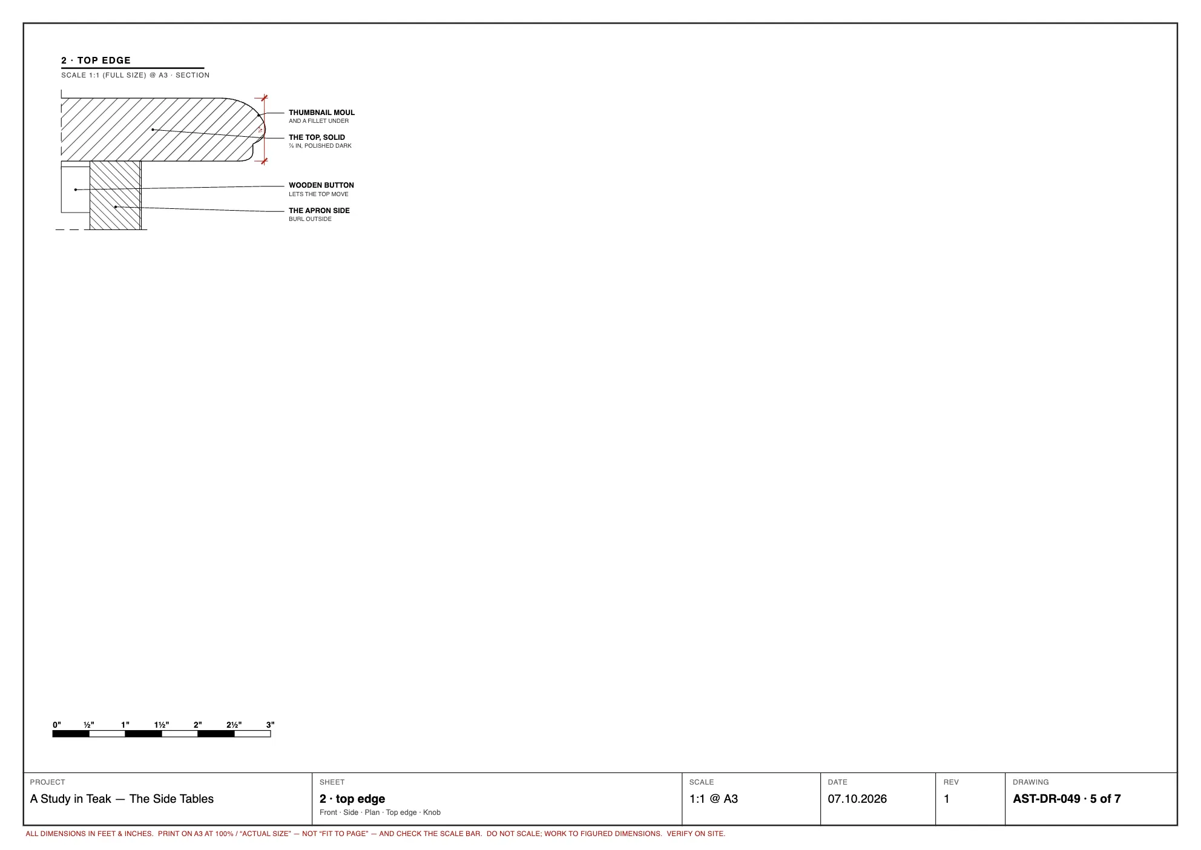
cad/print/sidetable-05.webp
