sakshampan733-cloud/a-study-in-teak/cad/print/sidetable-06.webp

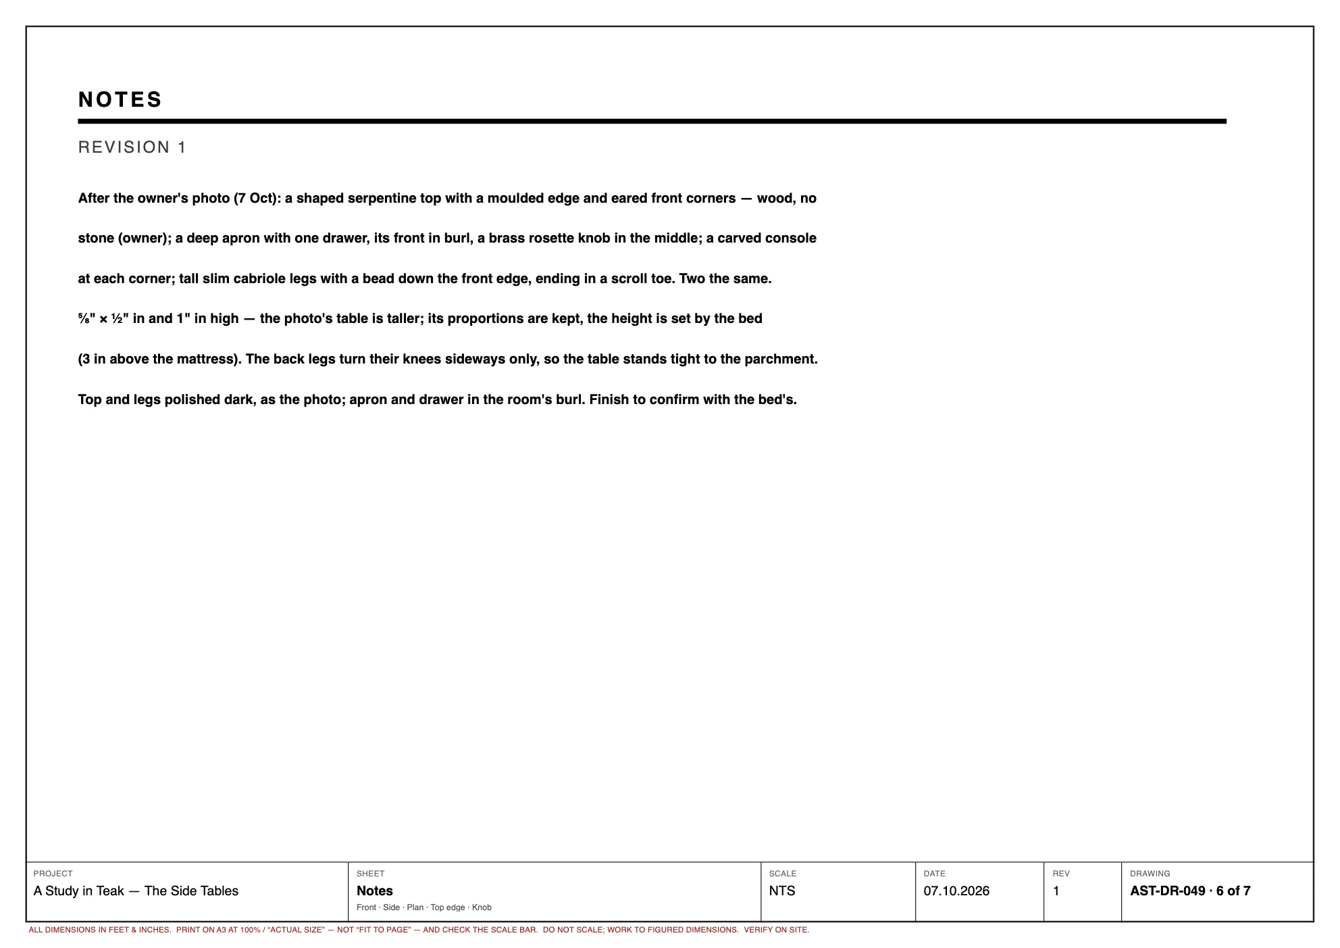
cad/print/sidetable-06.webp
