sakshampan733-cloud/a-study-in-teak/cad/print/studywall-01.webp

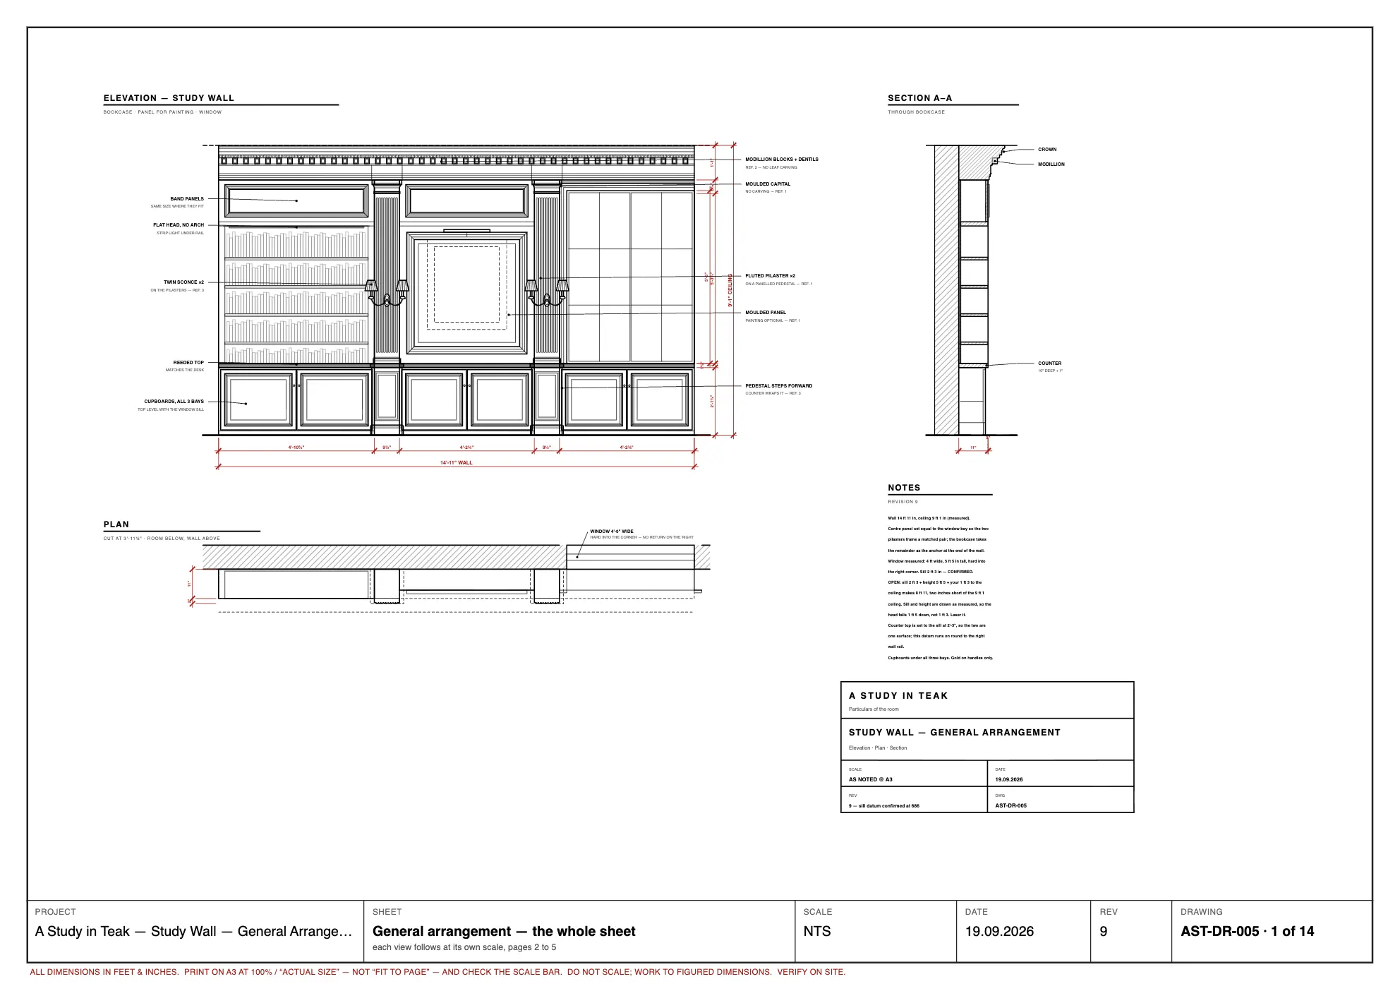
cad/print/studywall-01.webp
