sakshampan733-cloud/a-study-in-teak/cad/print/studywall-02.webp

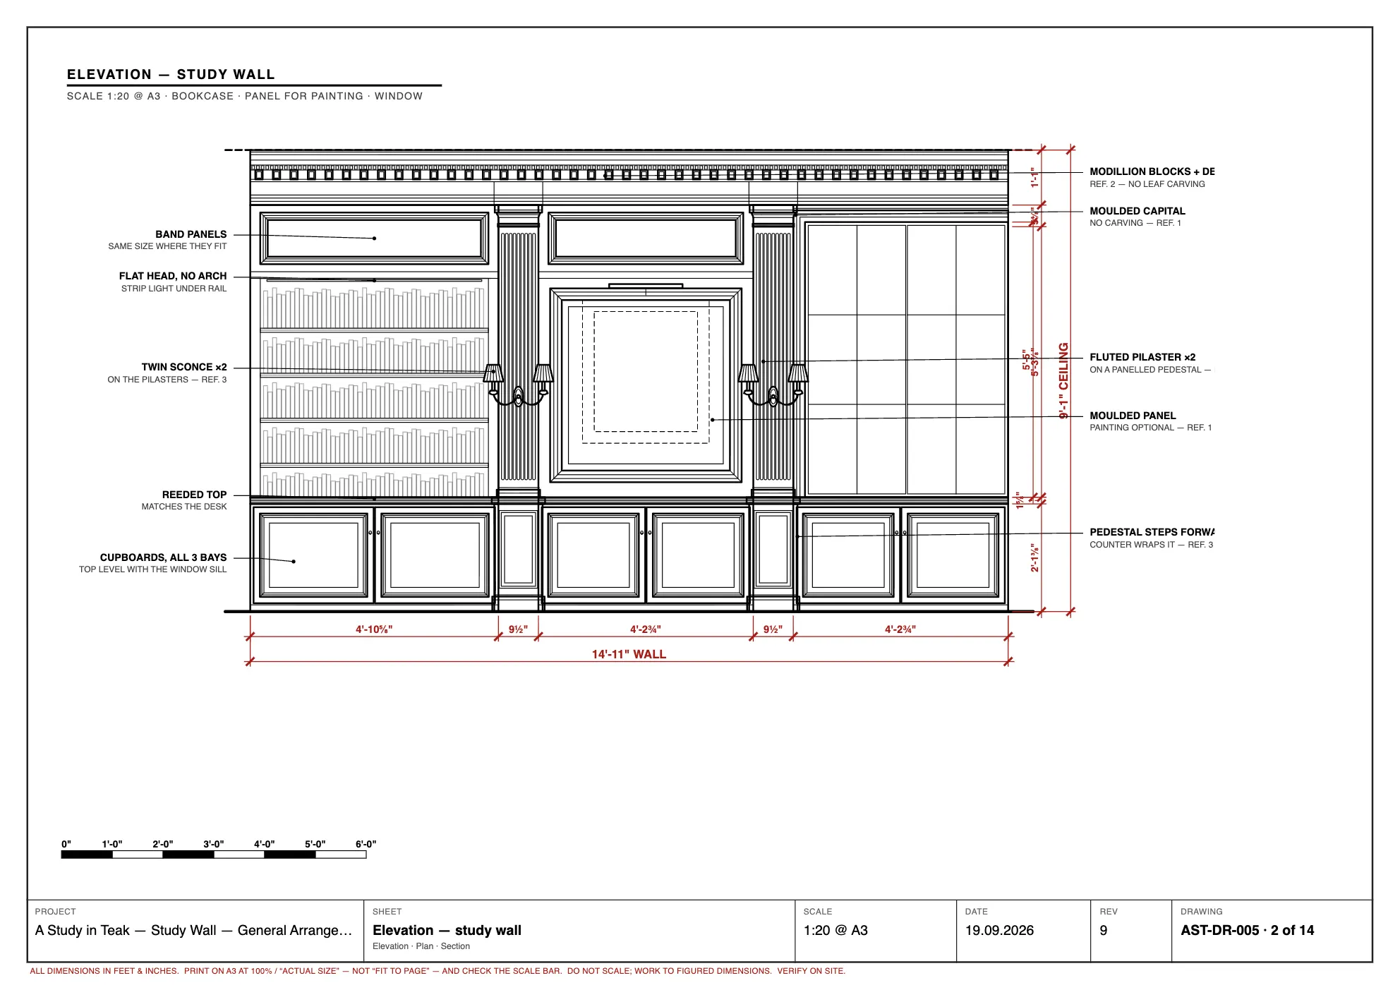
cad/print/studywall-02.webp
