sakshampan733-cloud/a-study-in-teak/cad/print/studywall-04.webp

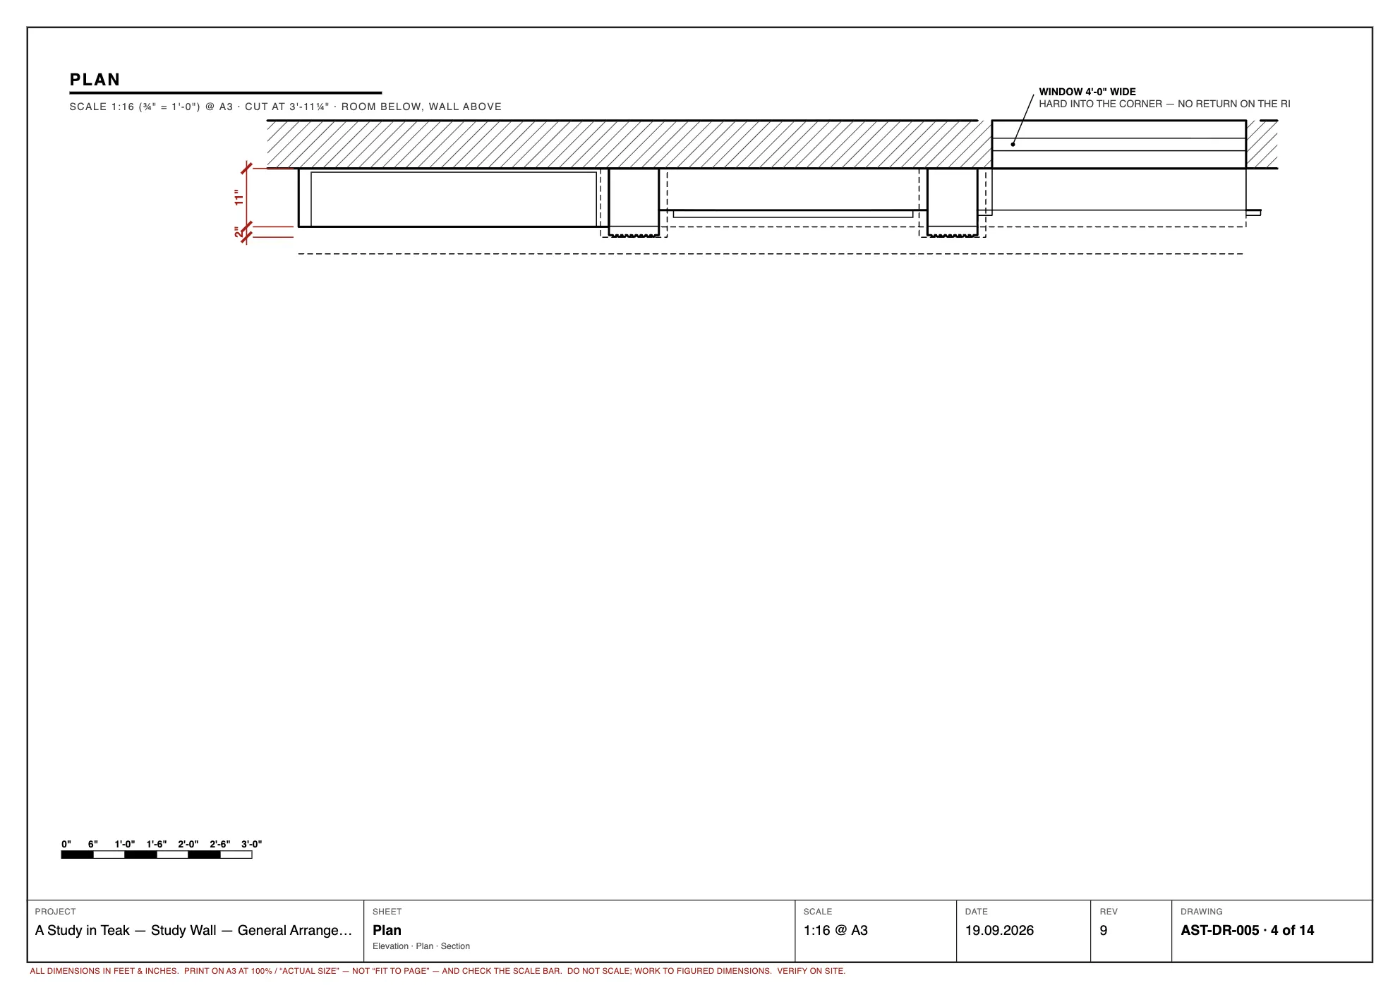
cad/print/studywall-04.webp
