sakshampan733-cloud/a-study-in-teak/cad/print/studywall-05.webp

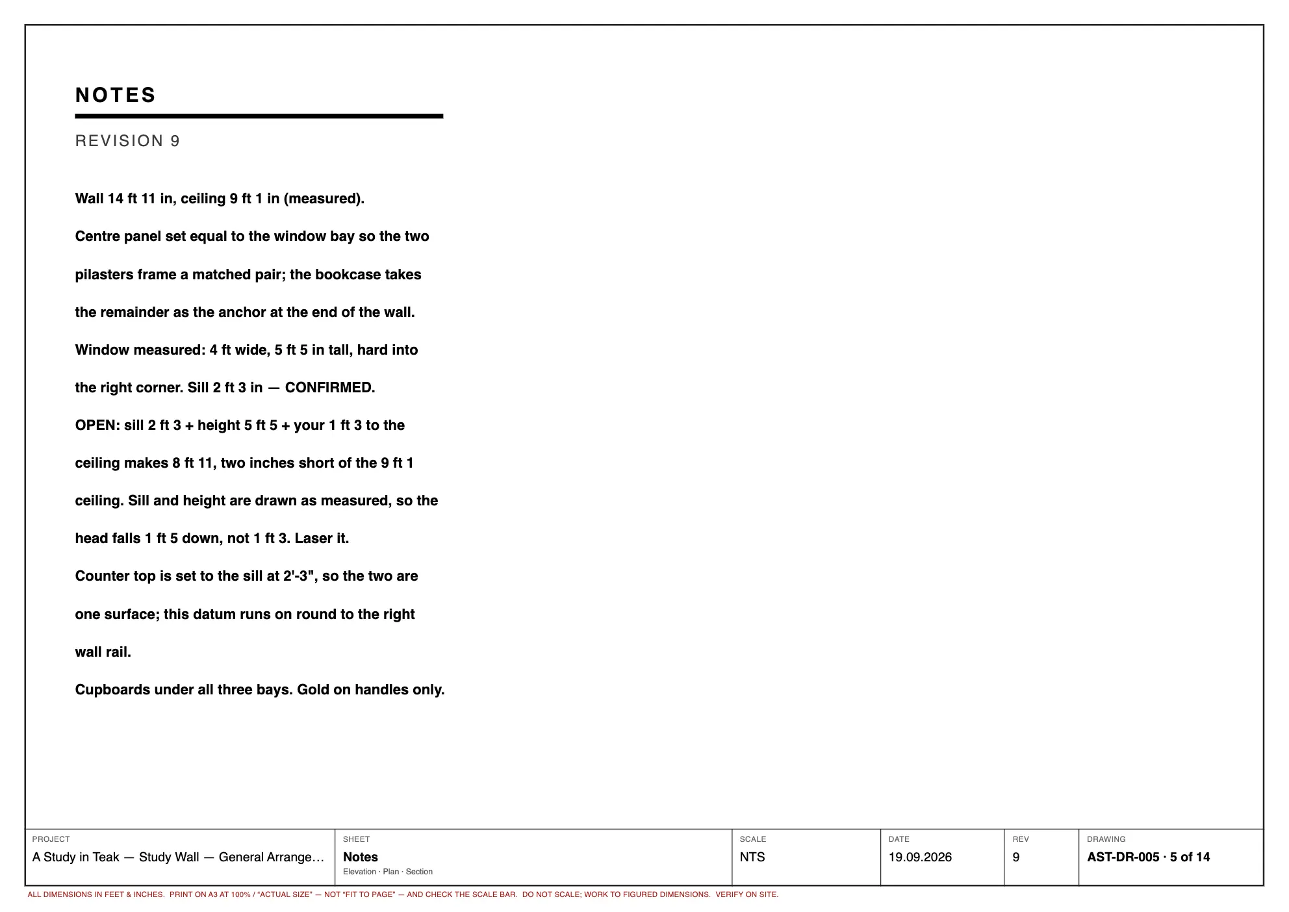
cad/print/studywall-05.webp
