sakshampan733-cloud/a-study-in-teak/cad/print/studywall-06.webp

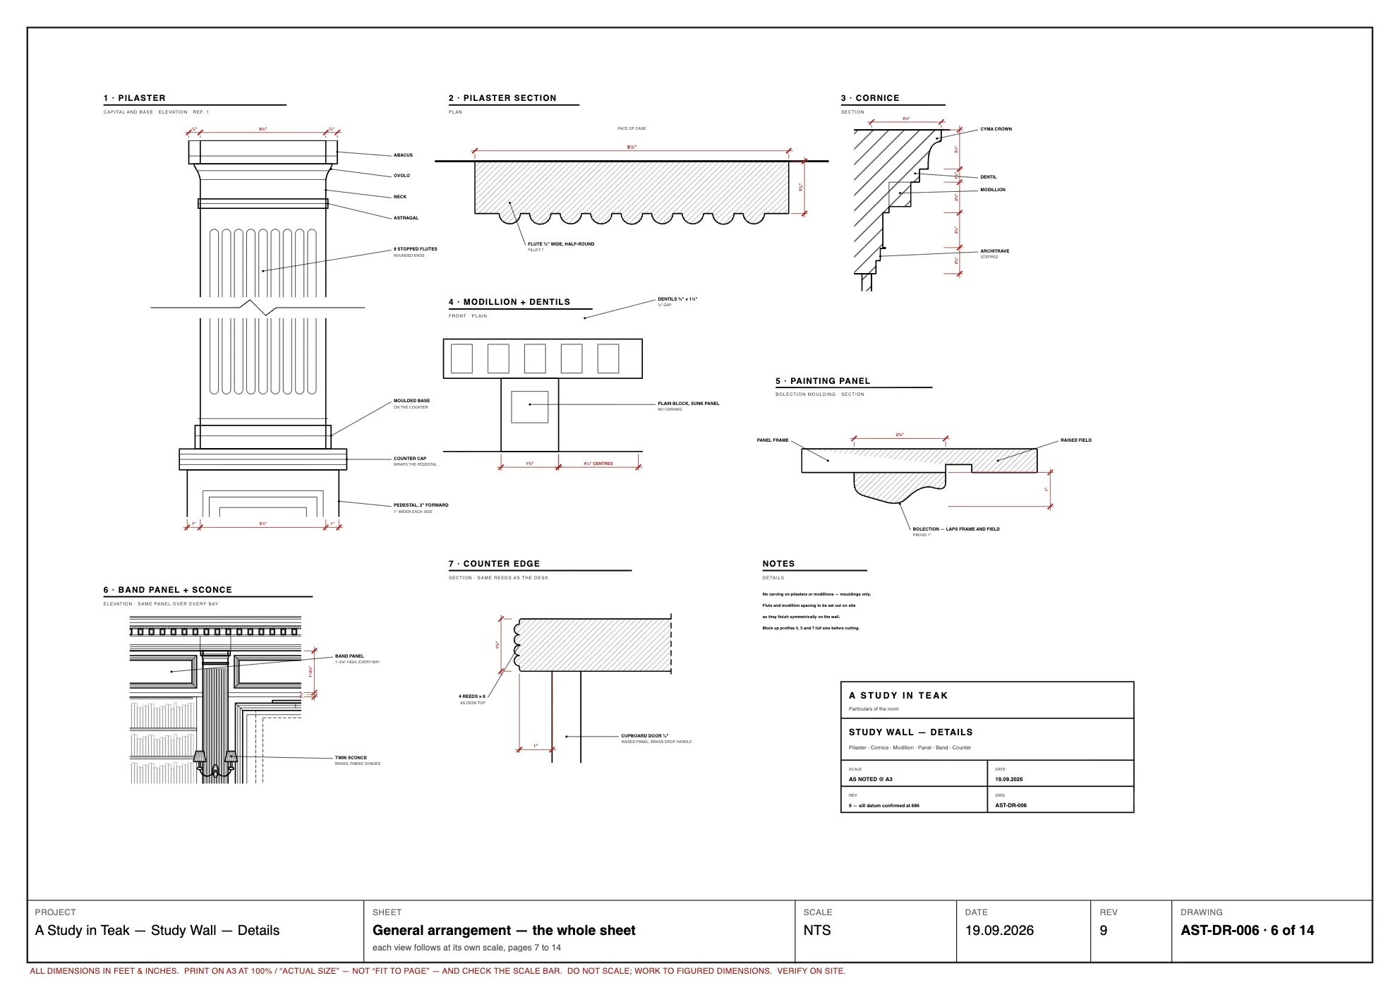
cad/print/studywall-06.webp
