sakshampan733-cloud/a-study-in-teak/cad/print/studywall-07.webp

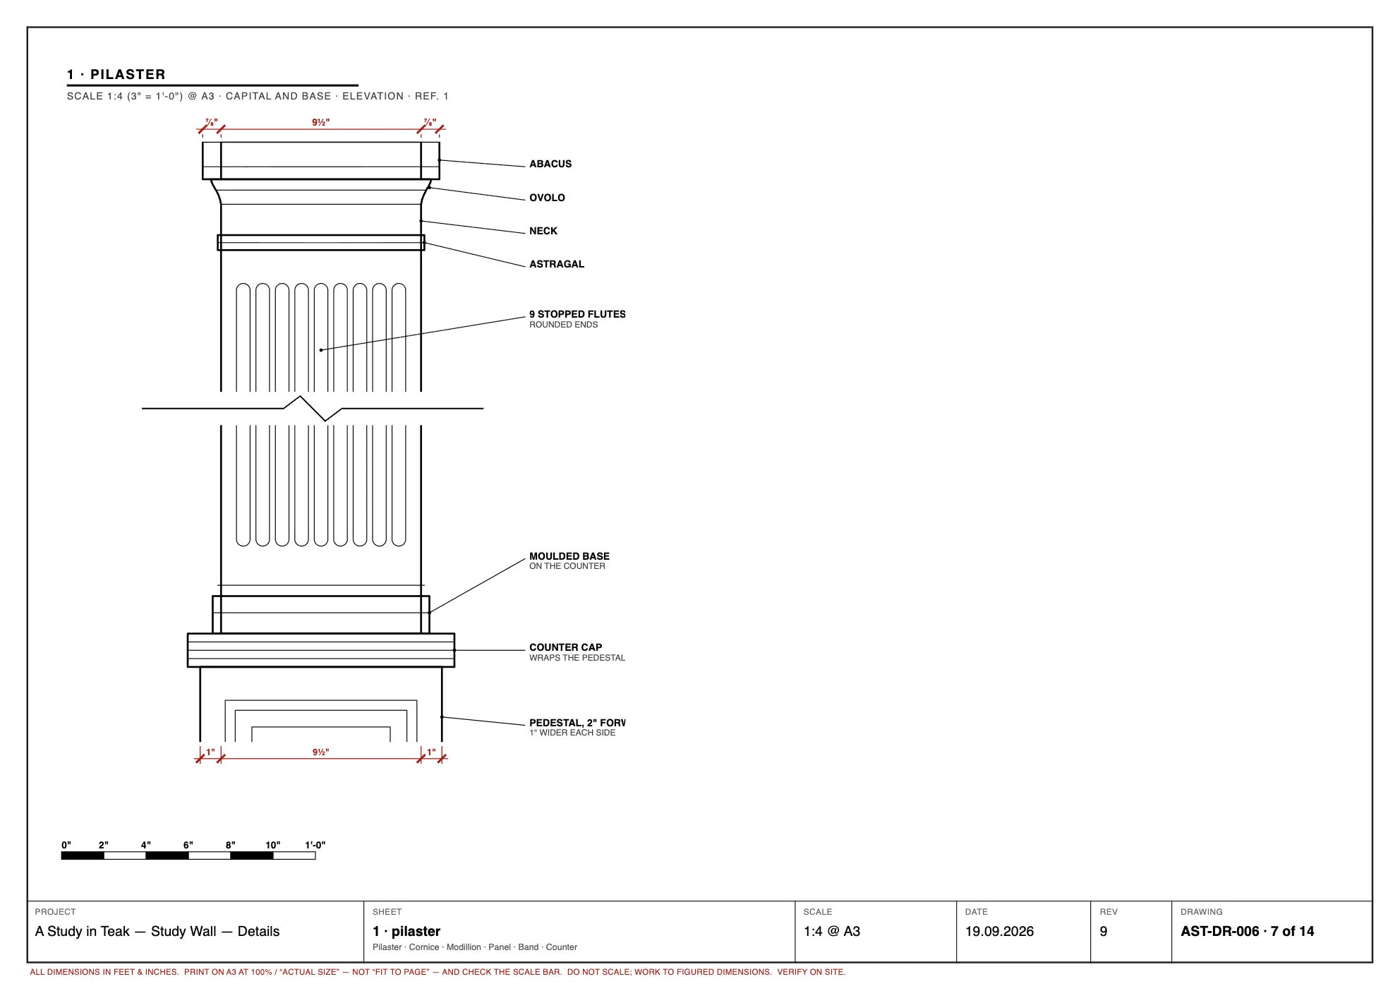
cad/print/studywall-07.webp
