sakshampan733-cloud/a-study-in-teak/cad/print/studywall-08.webp

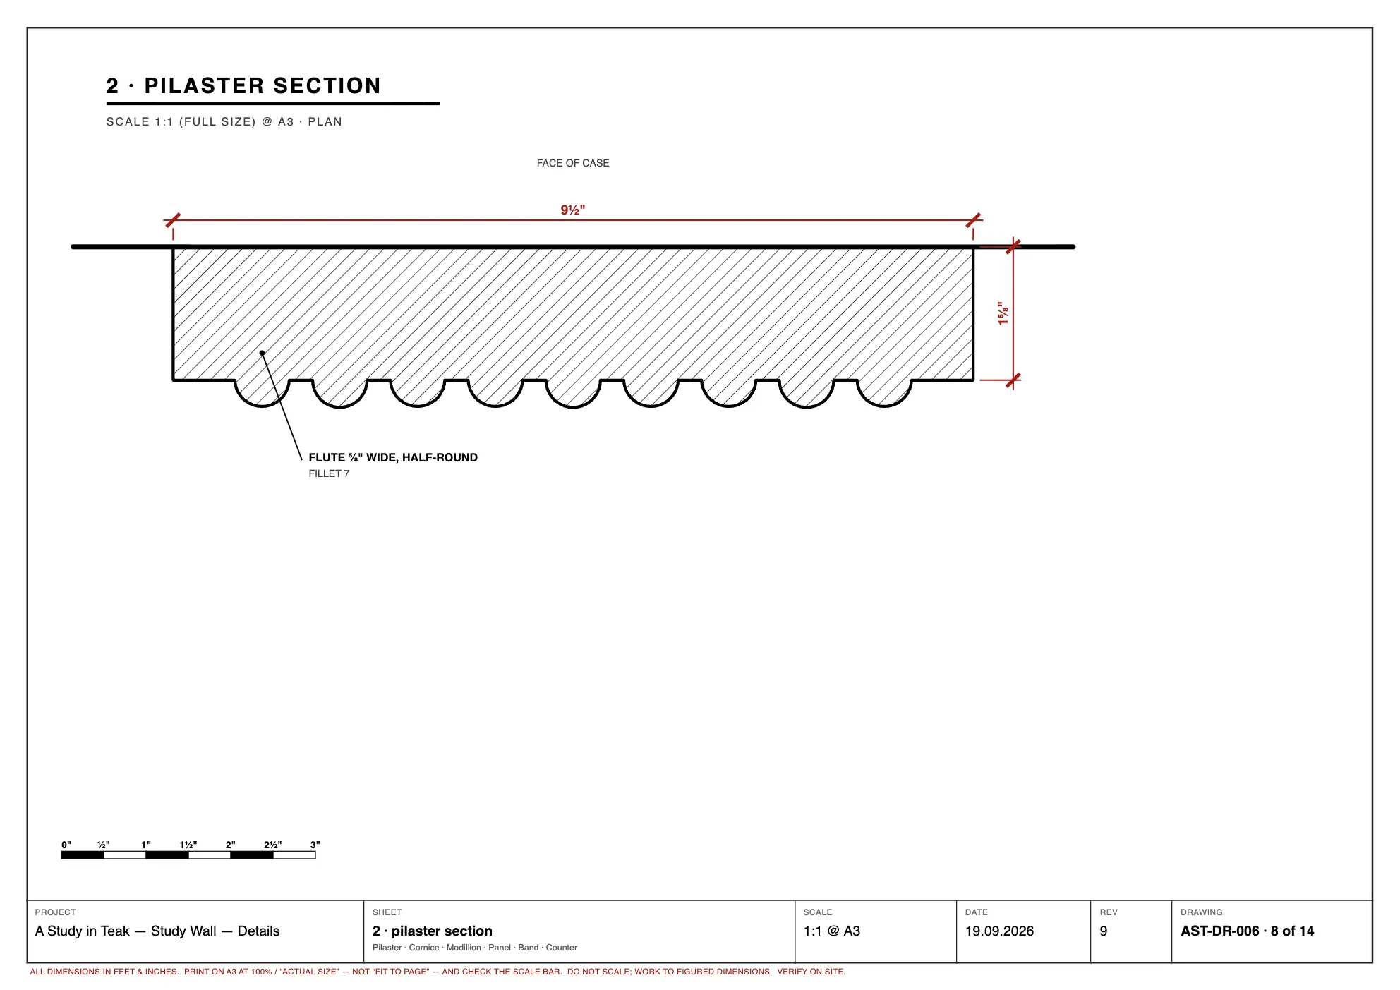
cad/print/studywall-08.webp
