sakshampan733-cloud/a-study-in-teak/cad/print/studywall-09.webp

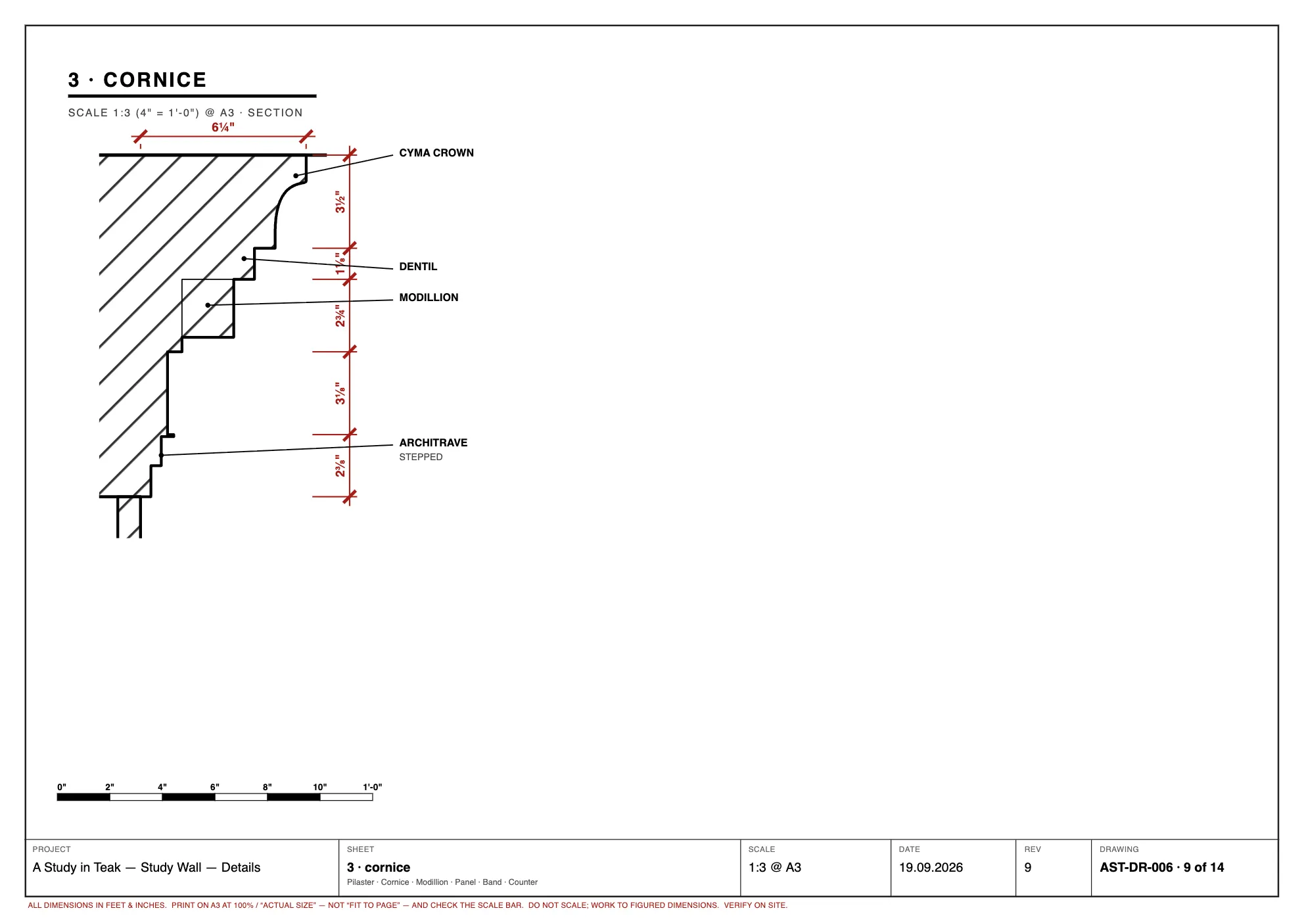
cad/print/studywall-09.webp
