sakshampan733-cloud/a-study-in-teak/cad/print/studywall-10.webp

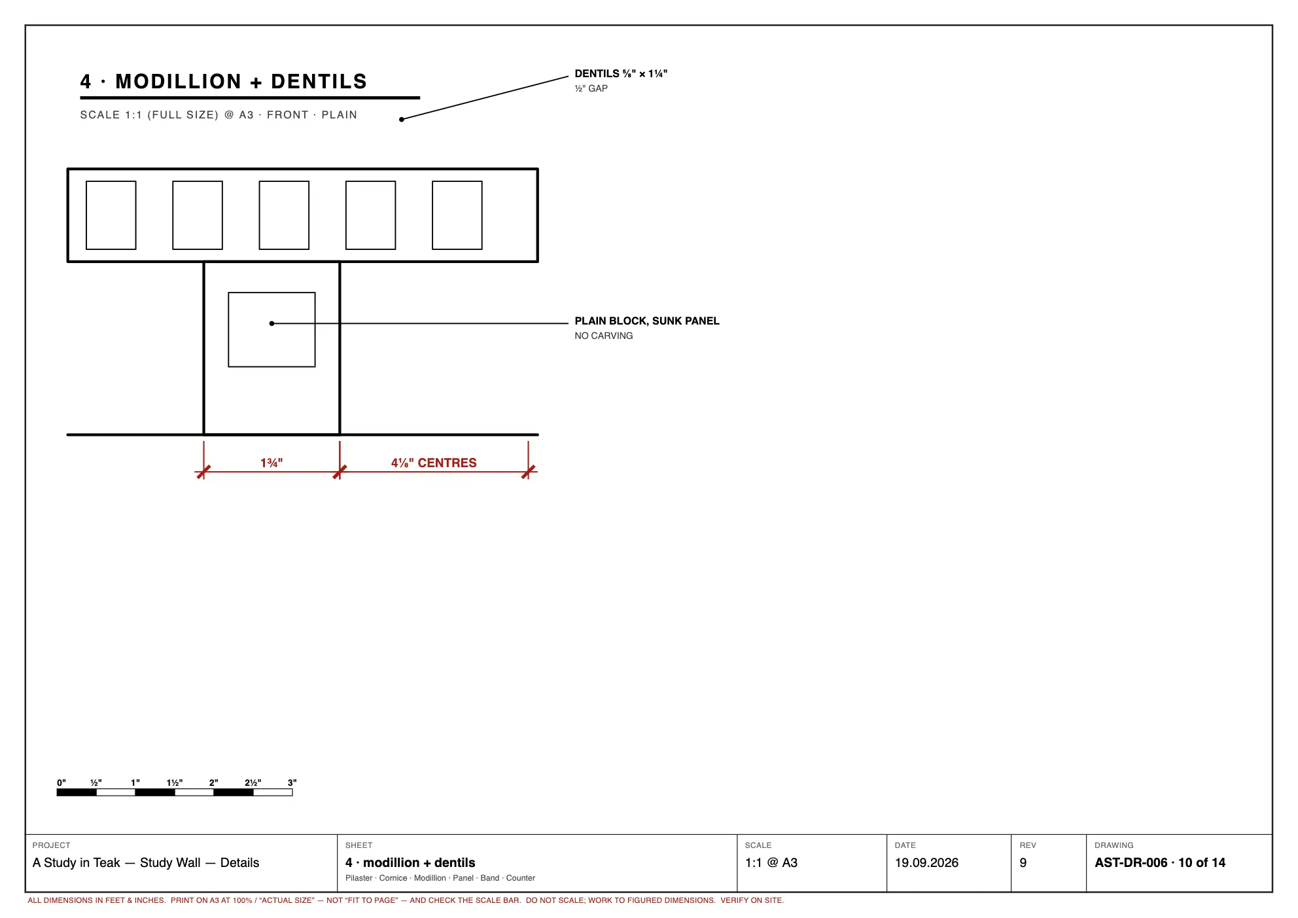
cad/print/studywall-10.webp
