sakshampan733-cloud/a-study-in-teak/cad/print/studywall-11.webp

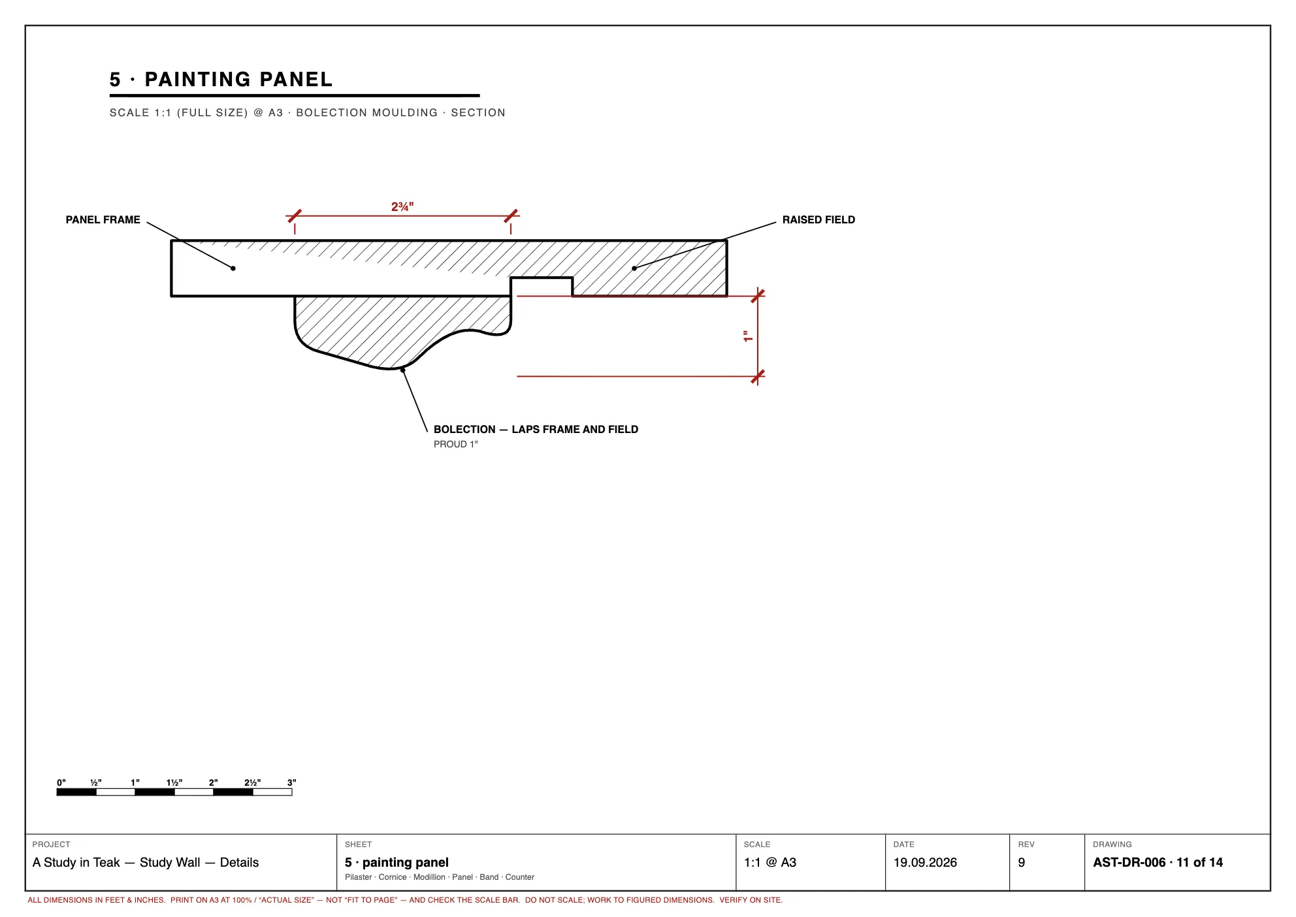
cad/print/studywall-11.webp
