sakshampan733-cloud/a-study-in-teak/cad/print/studywall-12.webp

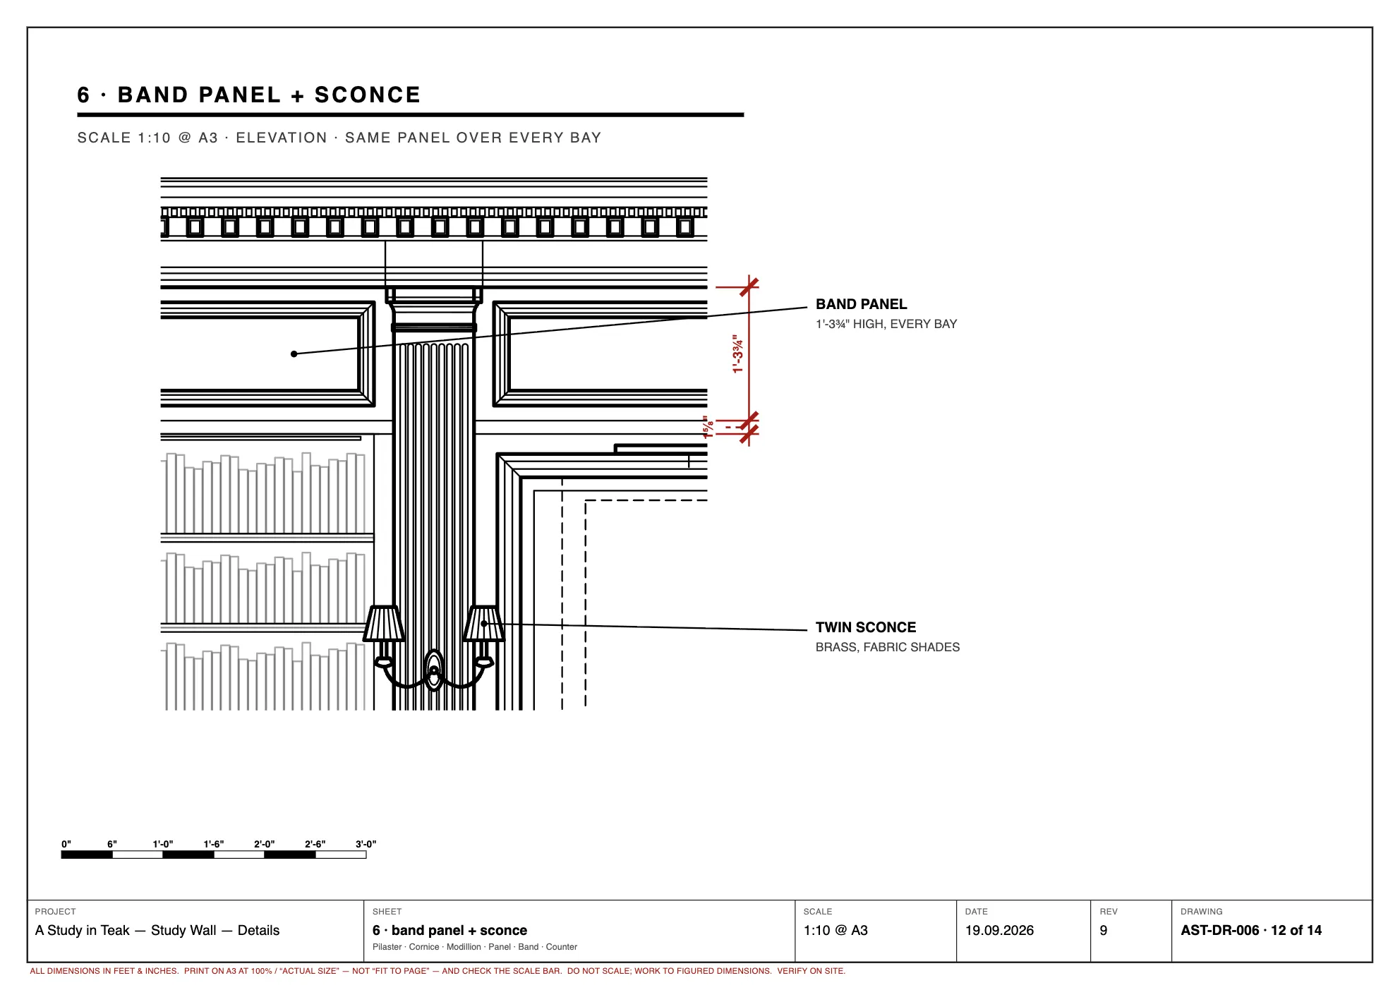
cad/print/studywall-12.webp
