sakshampan733-cloud/a-study-in-teak/cad/print/studywall-13.webp

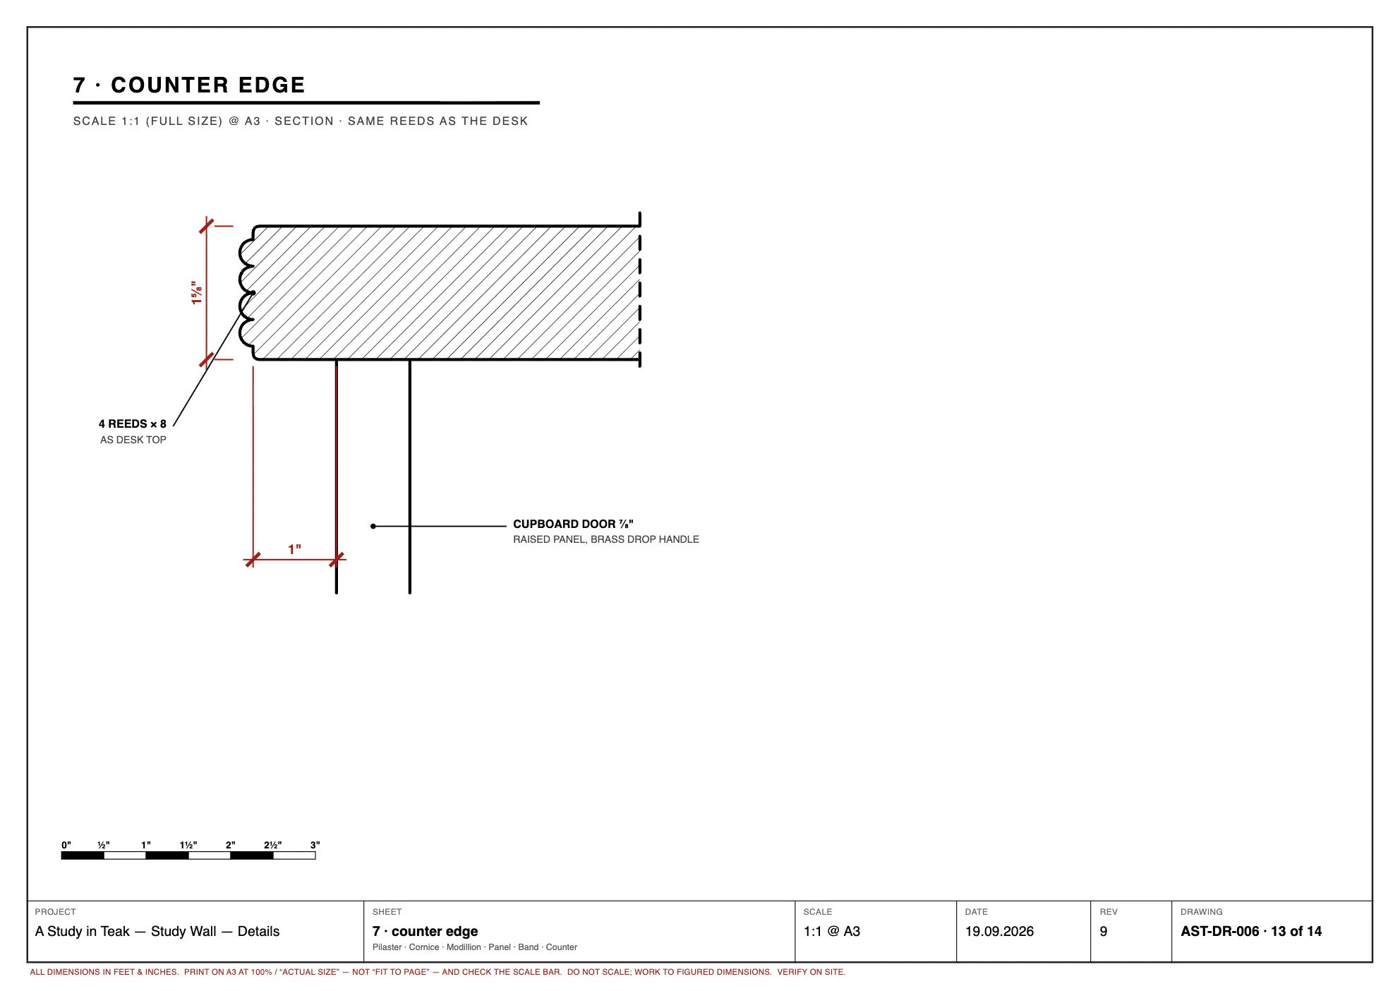
cad/print/studywall-13.webp
