sakshampan733-cloud/a-study-in-teak/cad/print/studywall-arch-10.webp

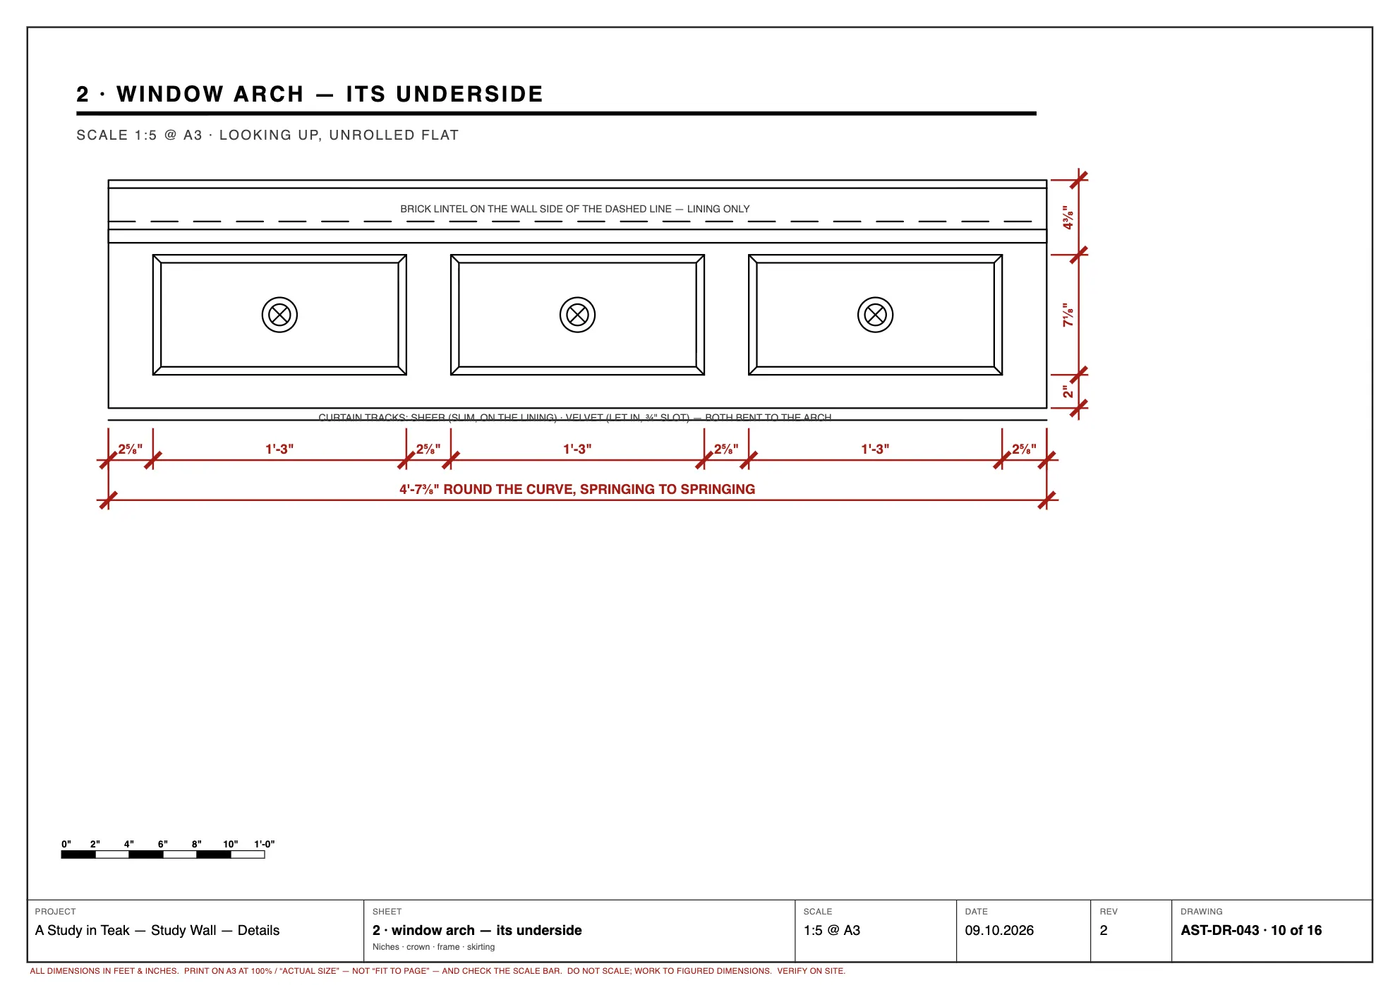
cad/print/studywall-arch-10.webp
