sakshampan733-cloud/a-study-in-teak/cad/print/studywall-arch-15.webp

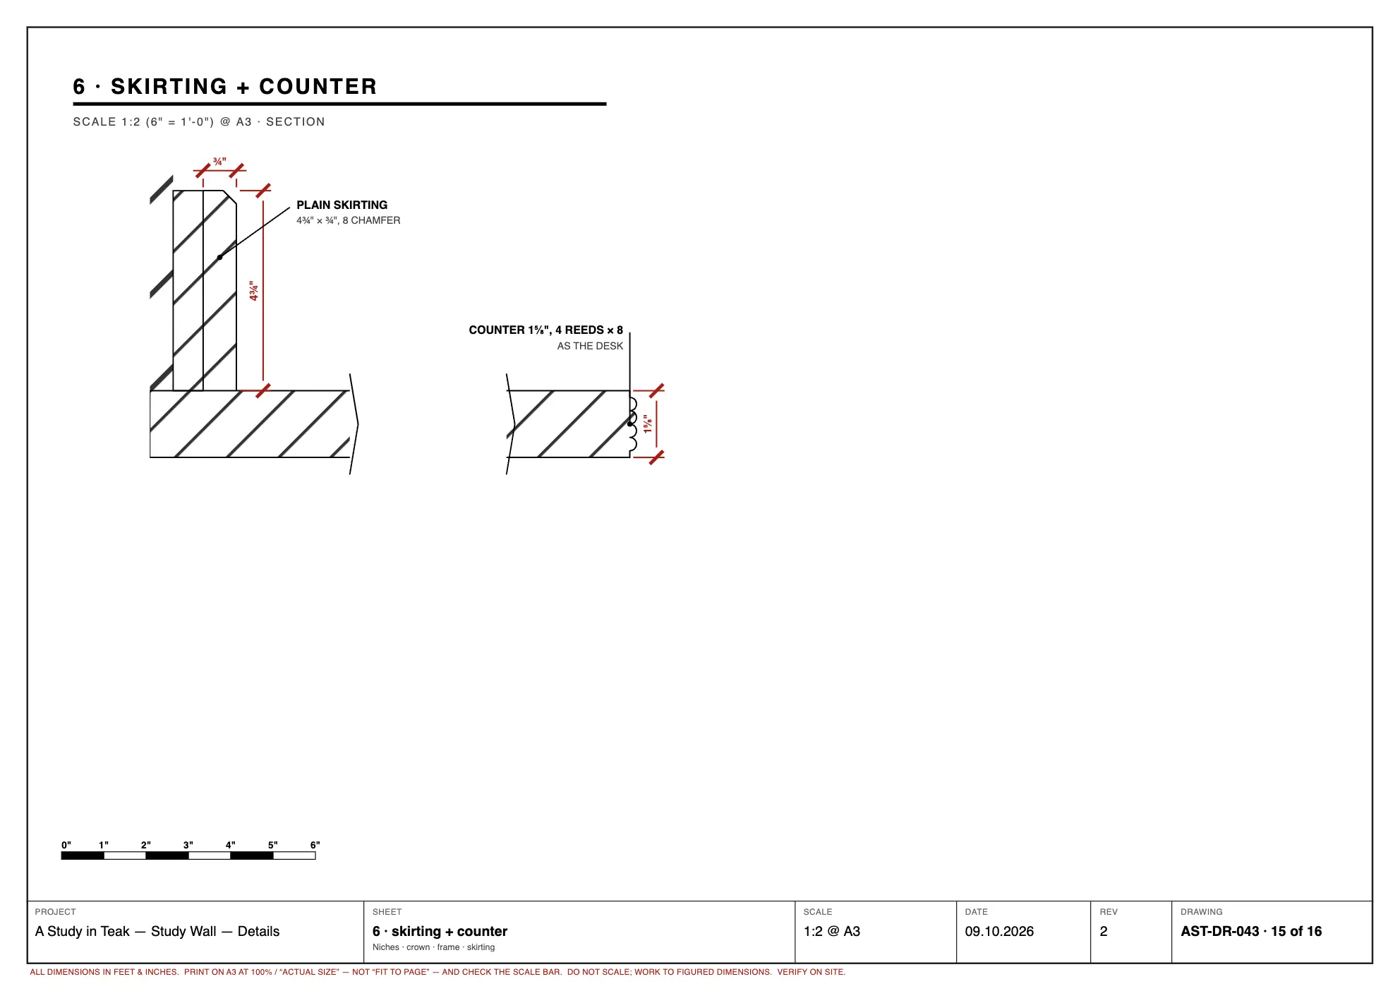
cad/print/studywall-arch-15.webp
