sakshampan733-cloud/a-study-in-teak/cad/print/tvunit-01.webp

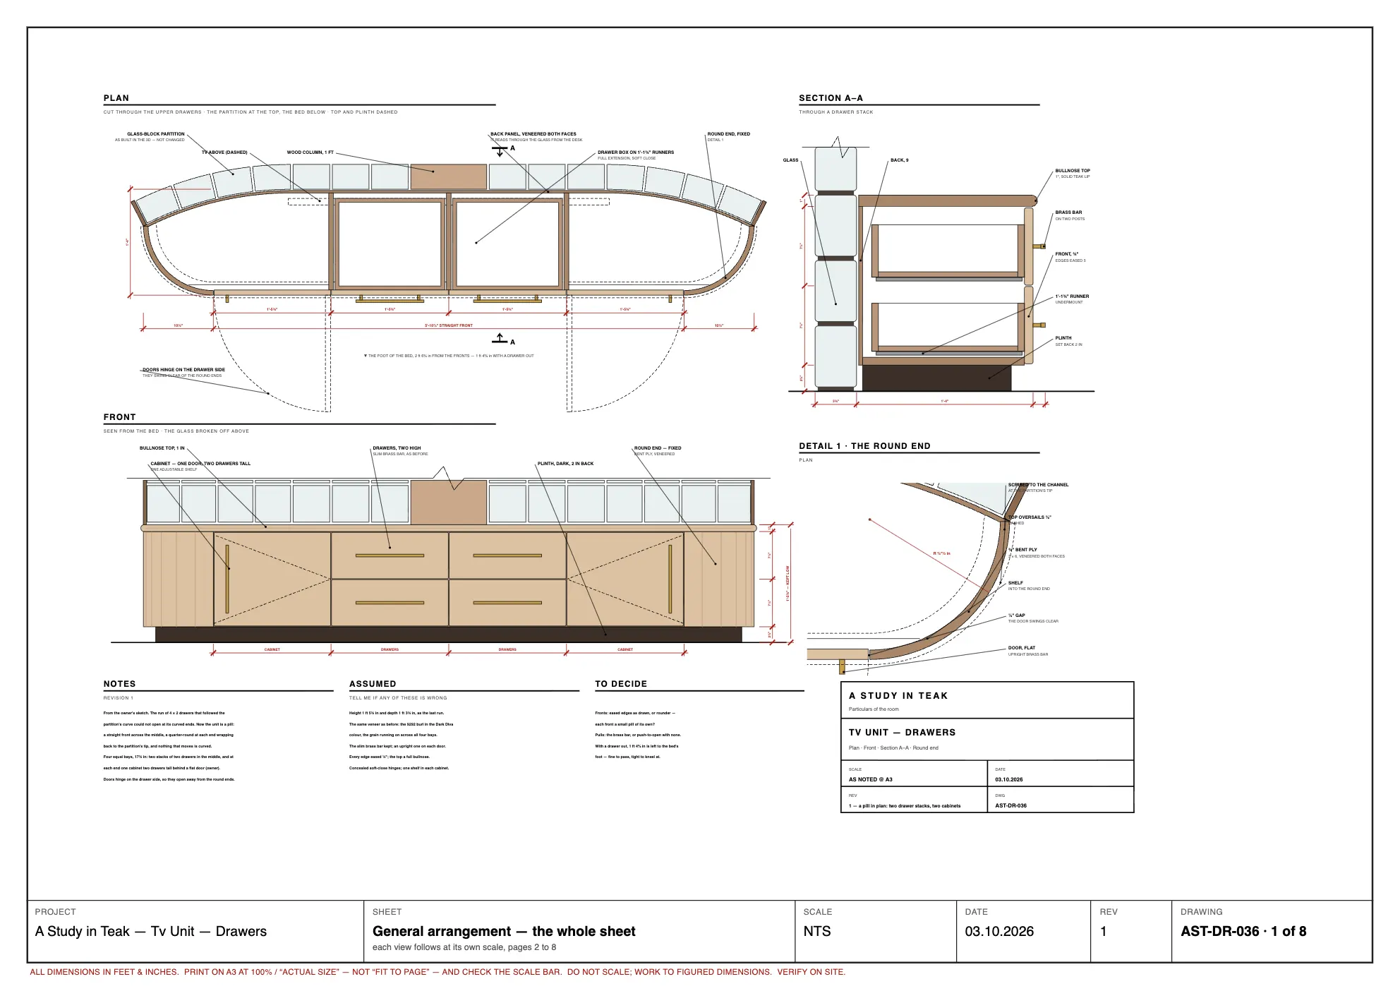
cad/print/tvunit-01.webp
