sakshampan733-cloud/a-study-in-teak/cad/print/tvunit-02.webp

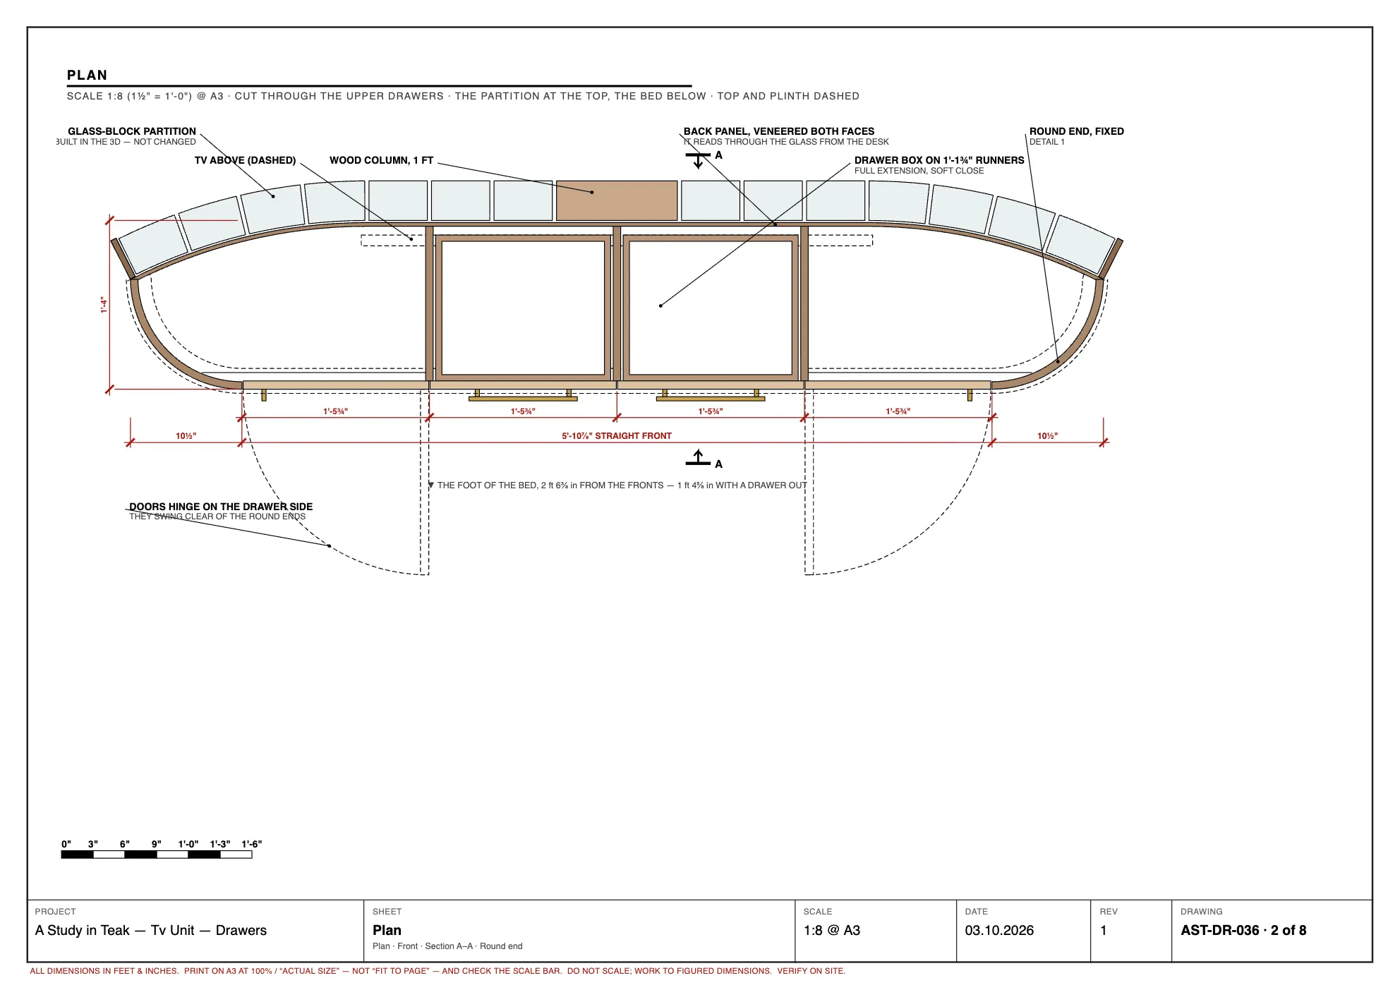
cad/print/tvunit-02.webp
