sakshampan733-cloud/a-study-in-teak/cad/print/tvunit-03.webp

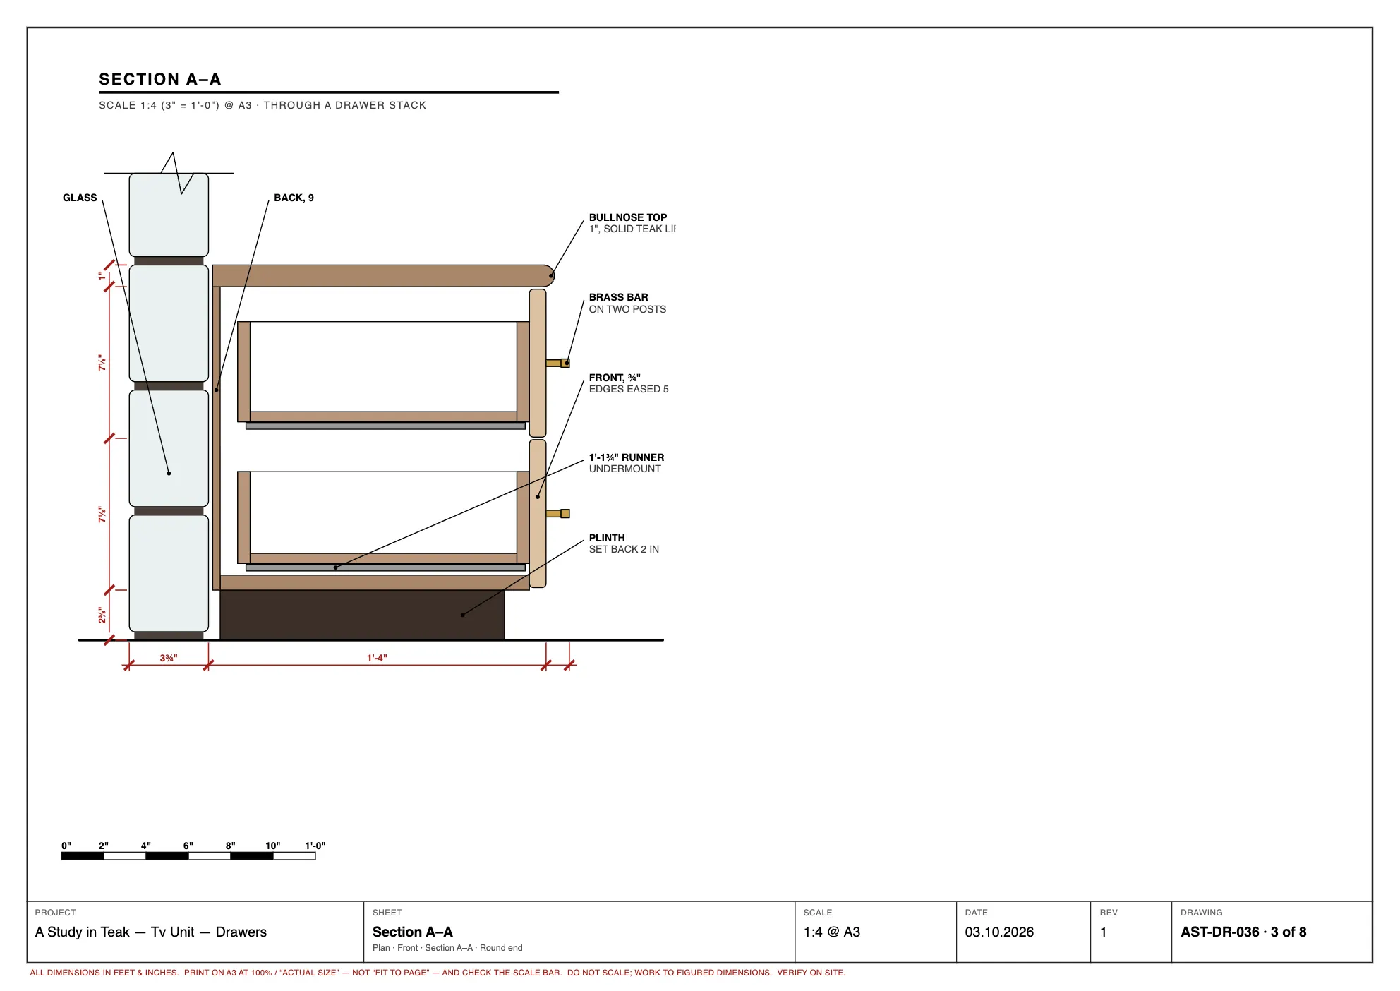
cad/print/tvunit-03.webp
