sakshampan733-cloud/a-study-in-teak/cad/print/tvunit-05.webp

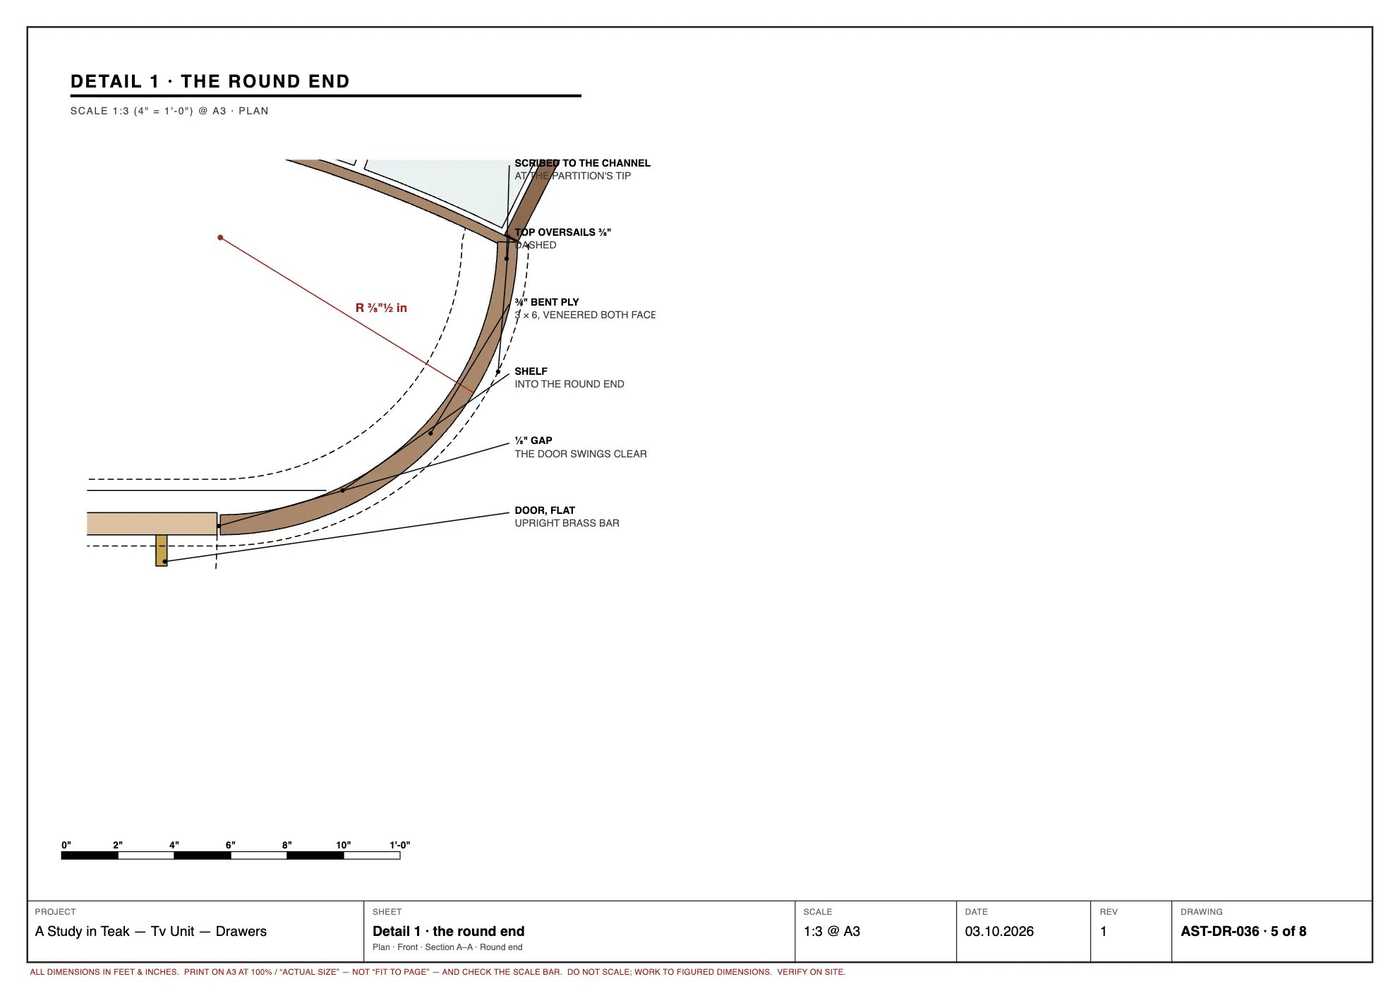
cad/print/tvunit-05.webp
