sakshampan733-cloud/a-study-in-teak/cad/print/tvunit-07.webp

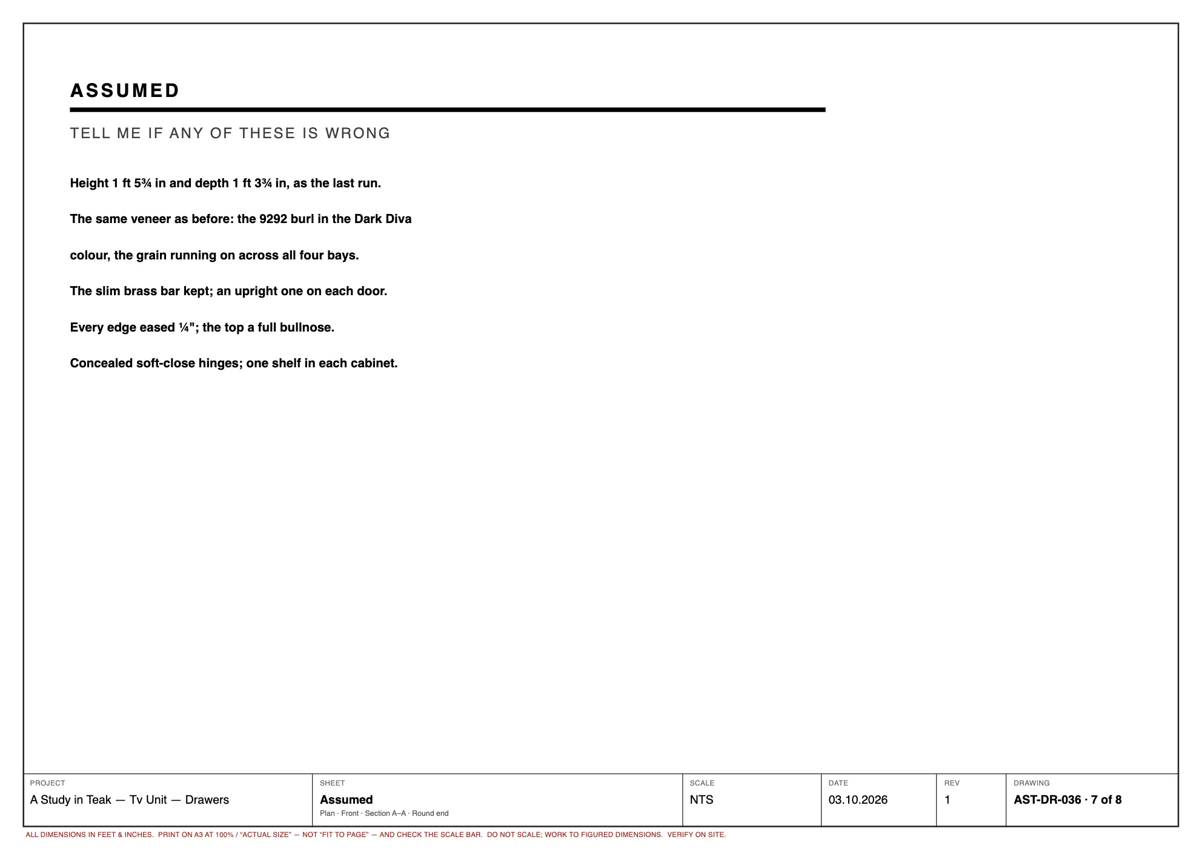
cad/print/tvunit-07.webp
