sakshampan733-cloud/a-study-in-teak/cad/print/vanity-01.webp

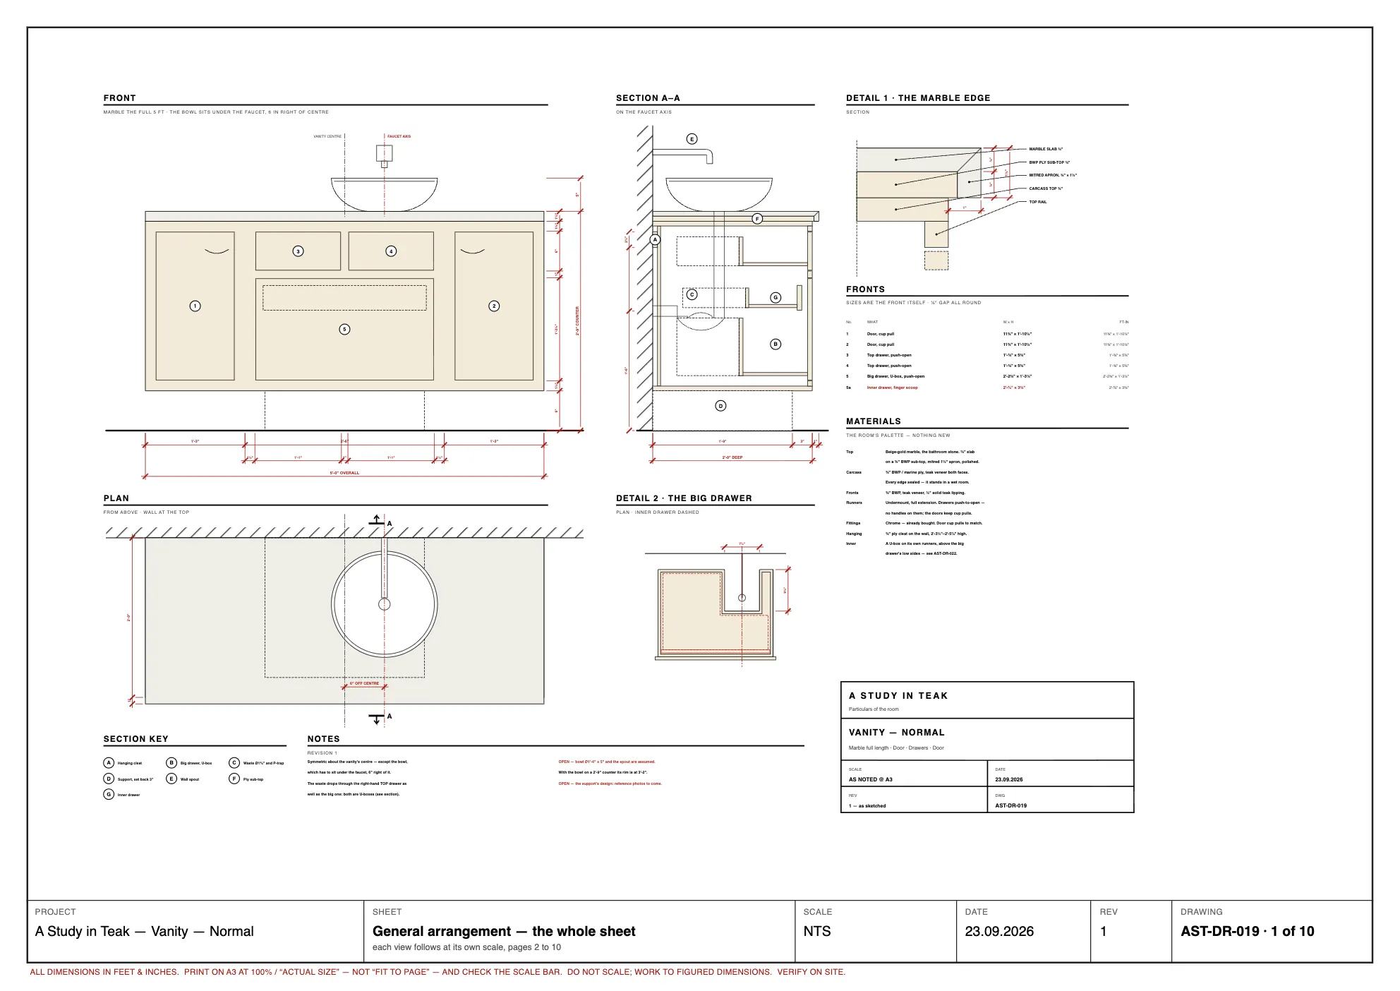
cad/print/vanity-01.webp
