sakshampan733-cloud/a-study-in-teak/cad/print/vanity-02.webp

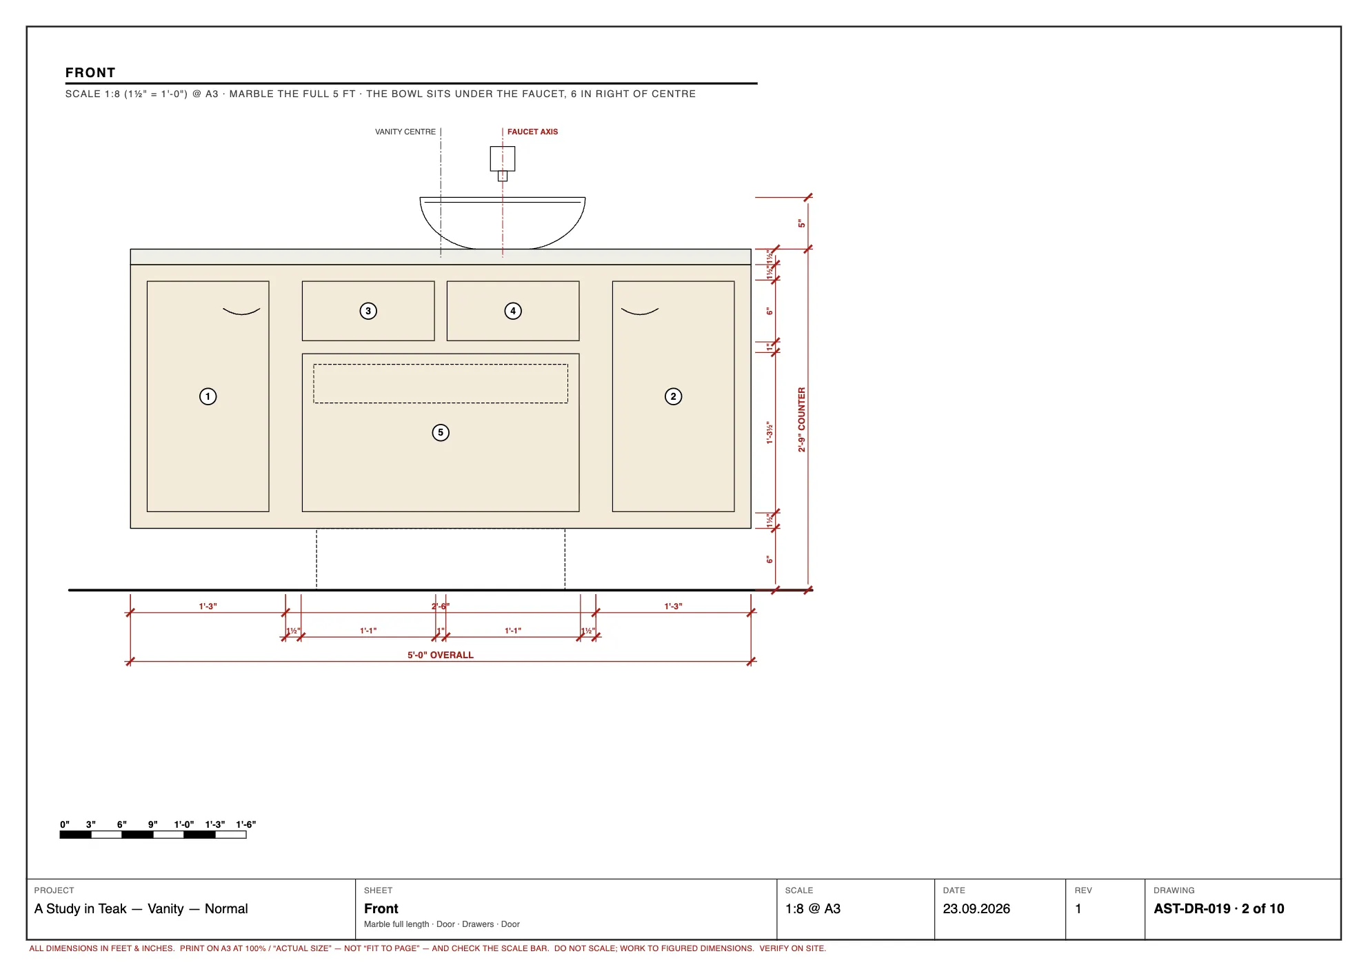
cad/print/vanity-02.webp
