sakshampan733-cloud/a-study-in-teak/cad/print/vanity-03.webp

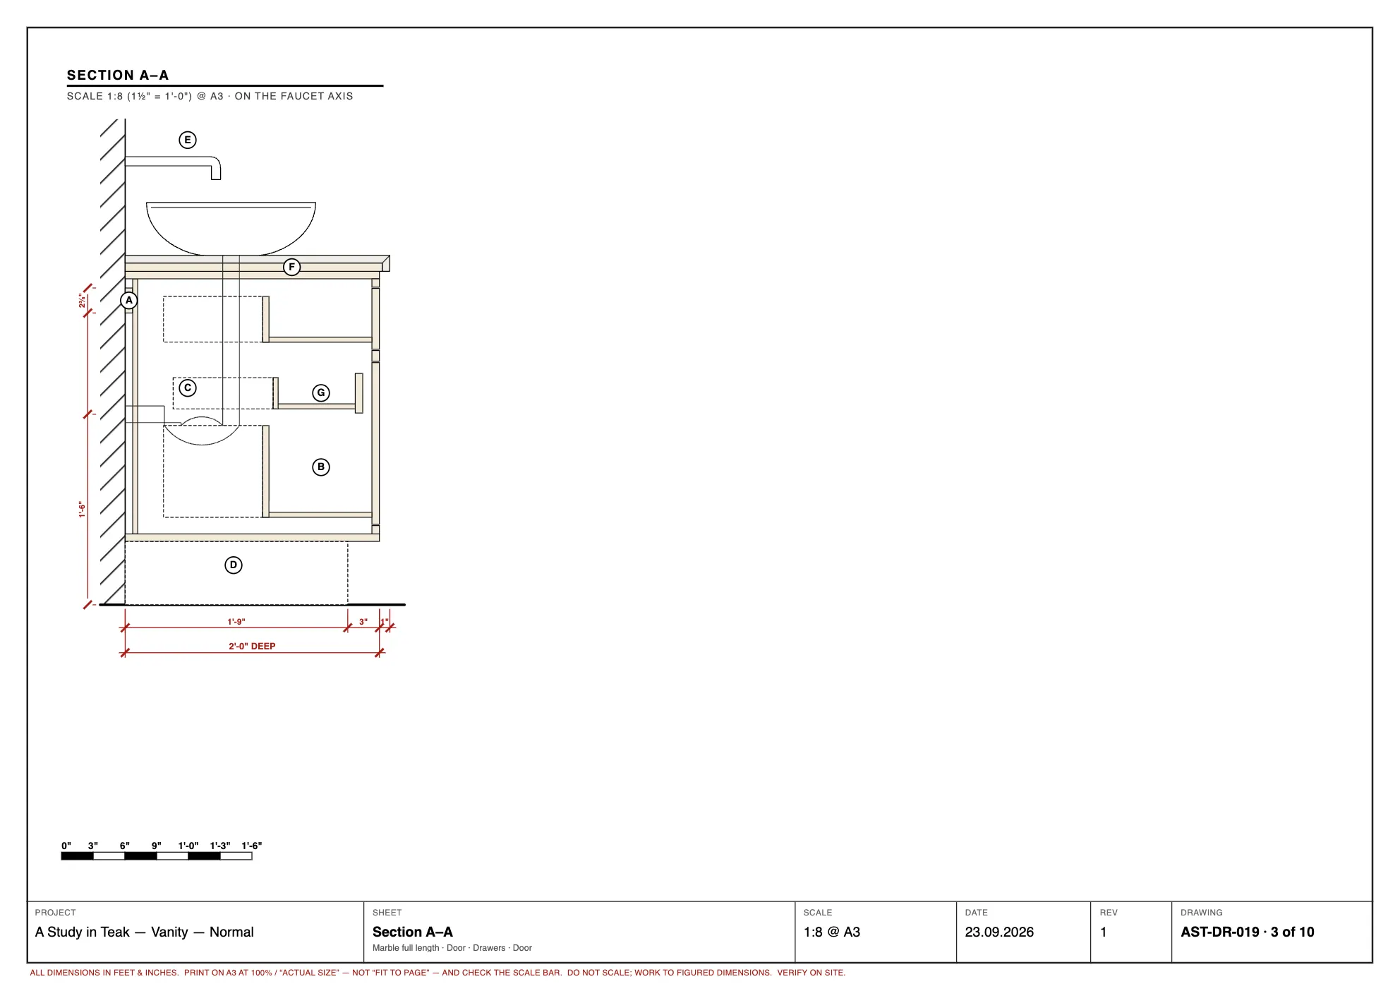
cad/print/vanity-03.webp
