sakshampan733-cloud/a-study-in-teak/cad/print/vanity-04.webp

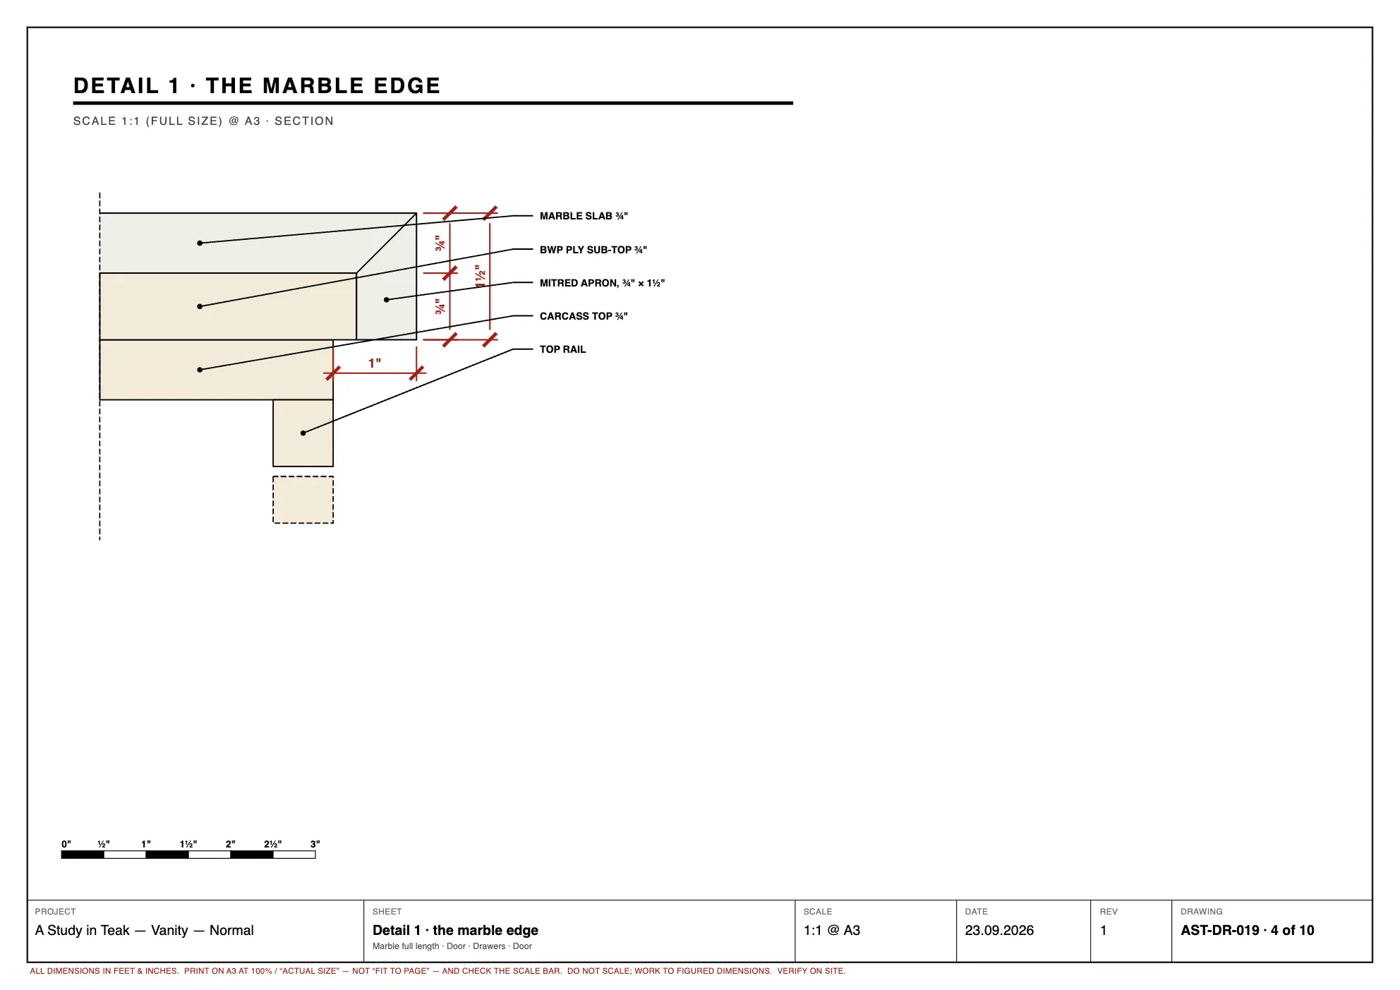
cad/print/vanity-04.webp
