sakshampan733-cloud/a-study-in-teak/cad/print/vanity-05.webp

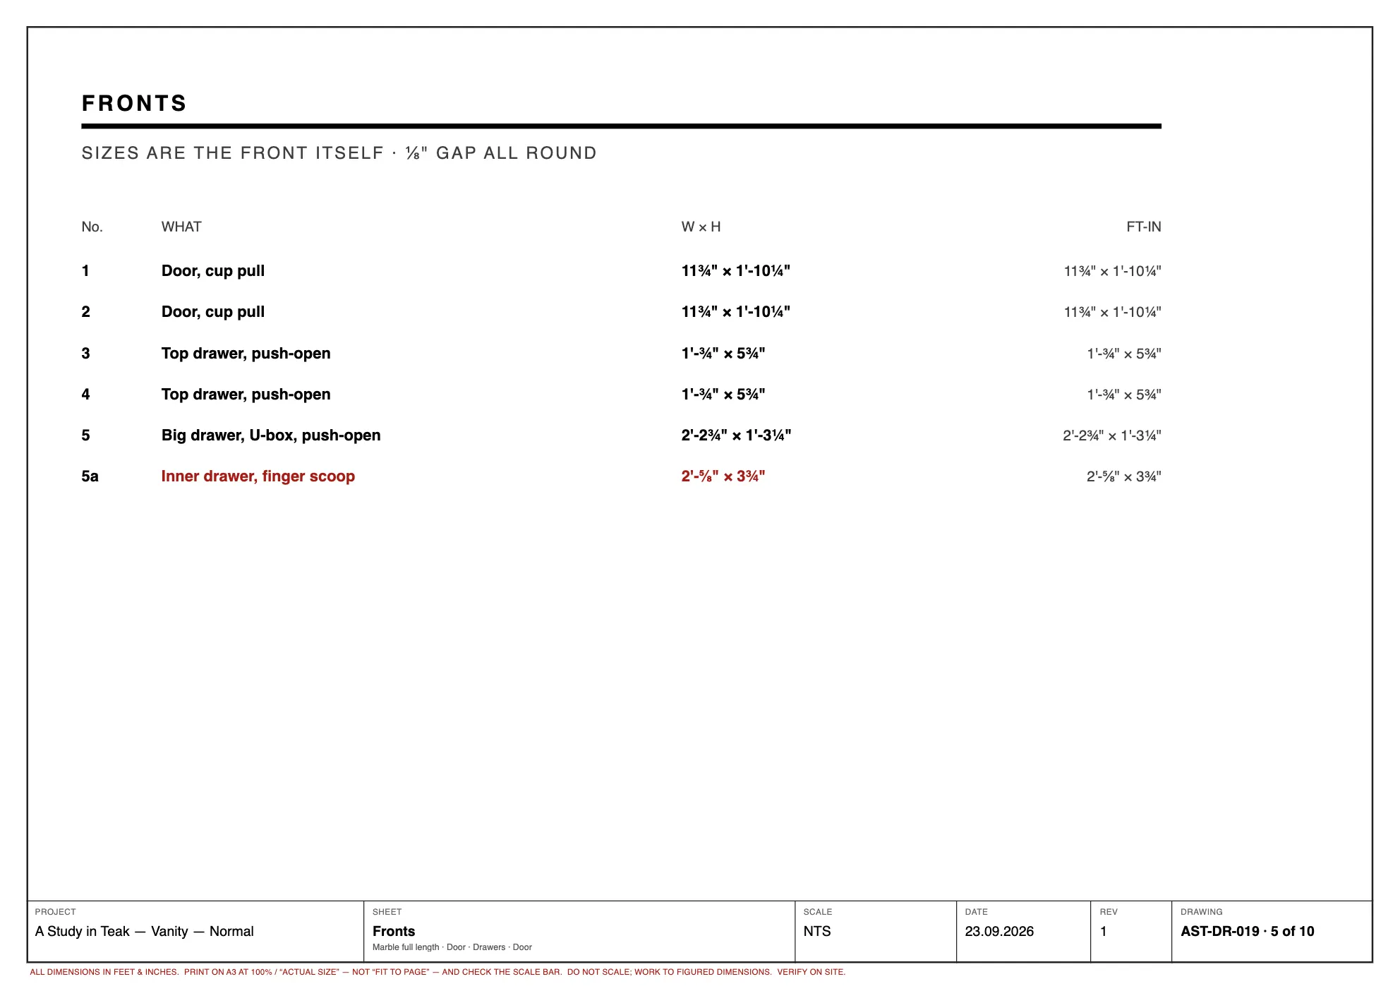
cad/print/vanity-05.webp
