sakshampan733-cloud/a-study-in-teak/cad/print/vanity-06.webp

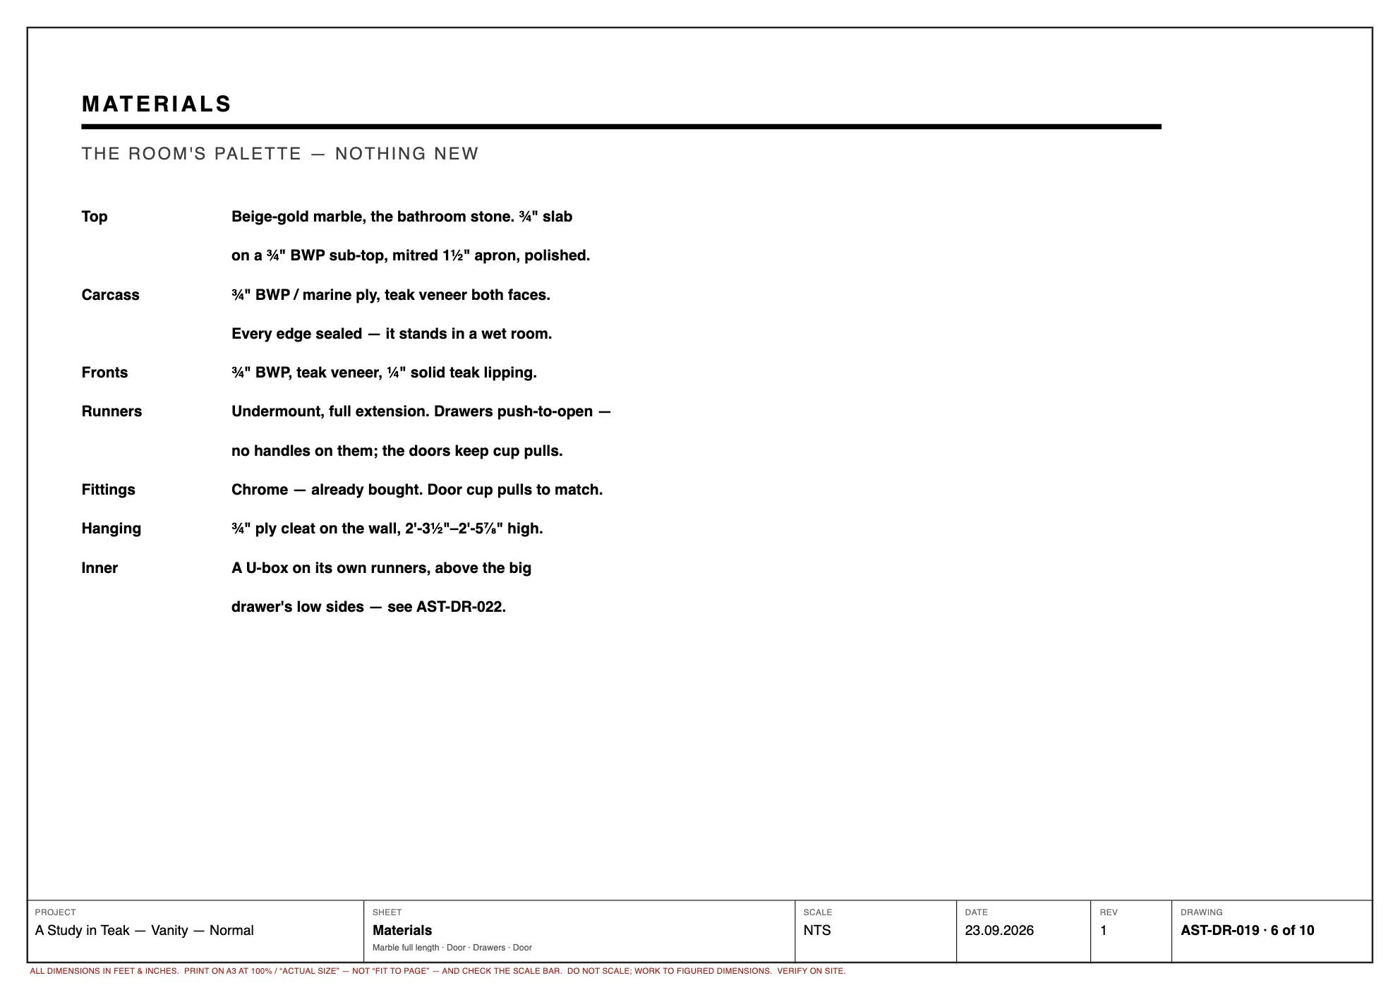
cad/print/vanity-06.webp
