sakshampan733-cloud/a-study-in-teak/cad/print/vanity-07.webp

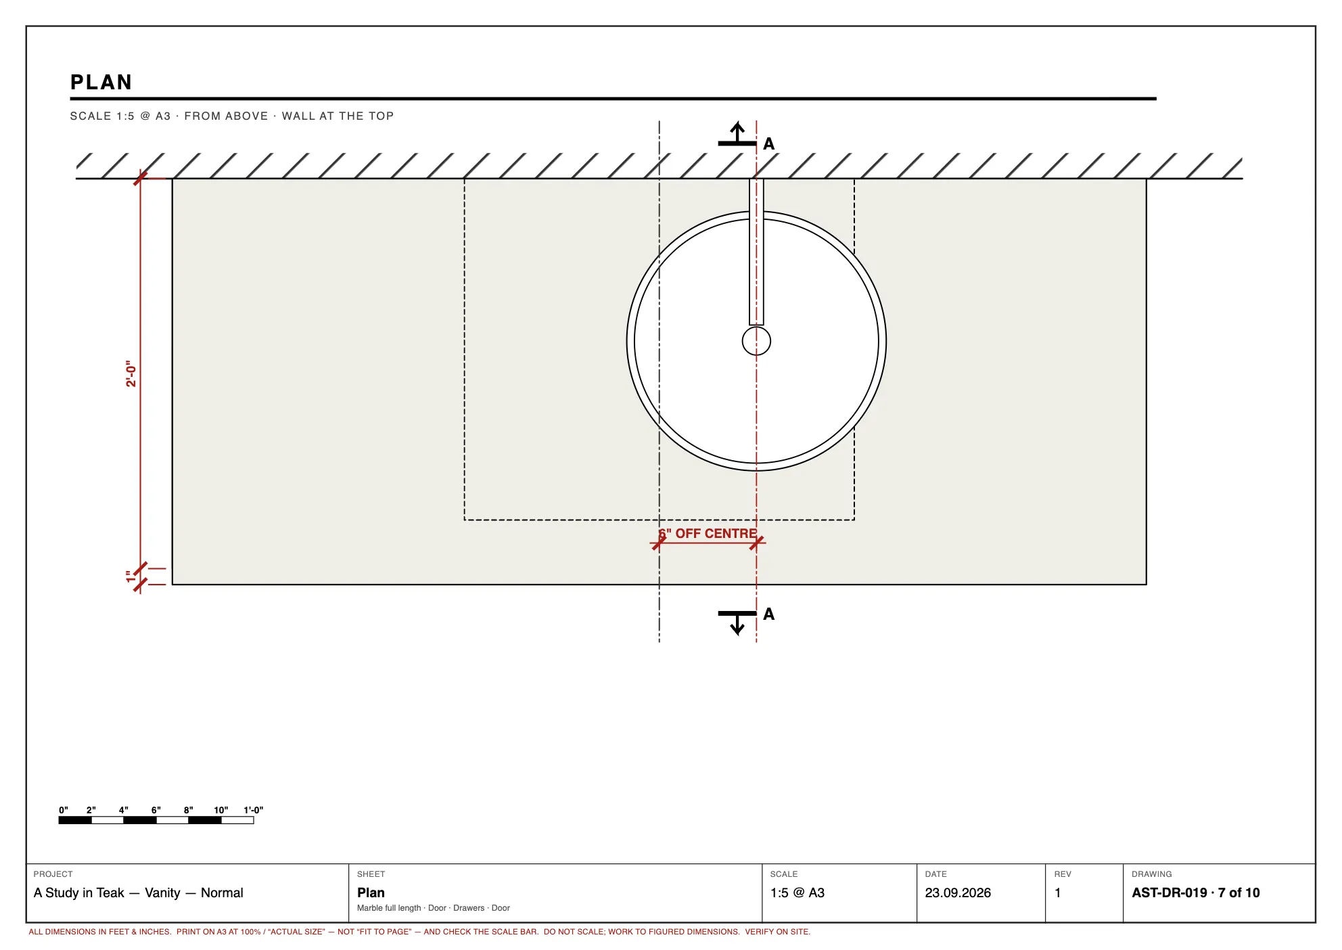
cad/print/vanity-07.webp
