sakshampan733-cloud/a-study-in-teak/cad/print/vanity-08.webp

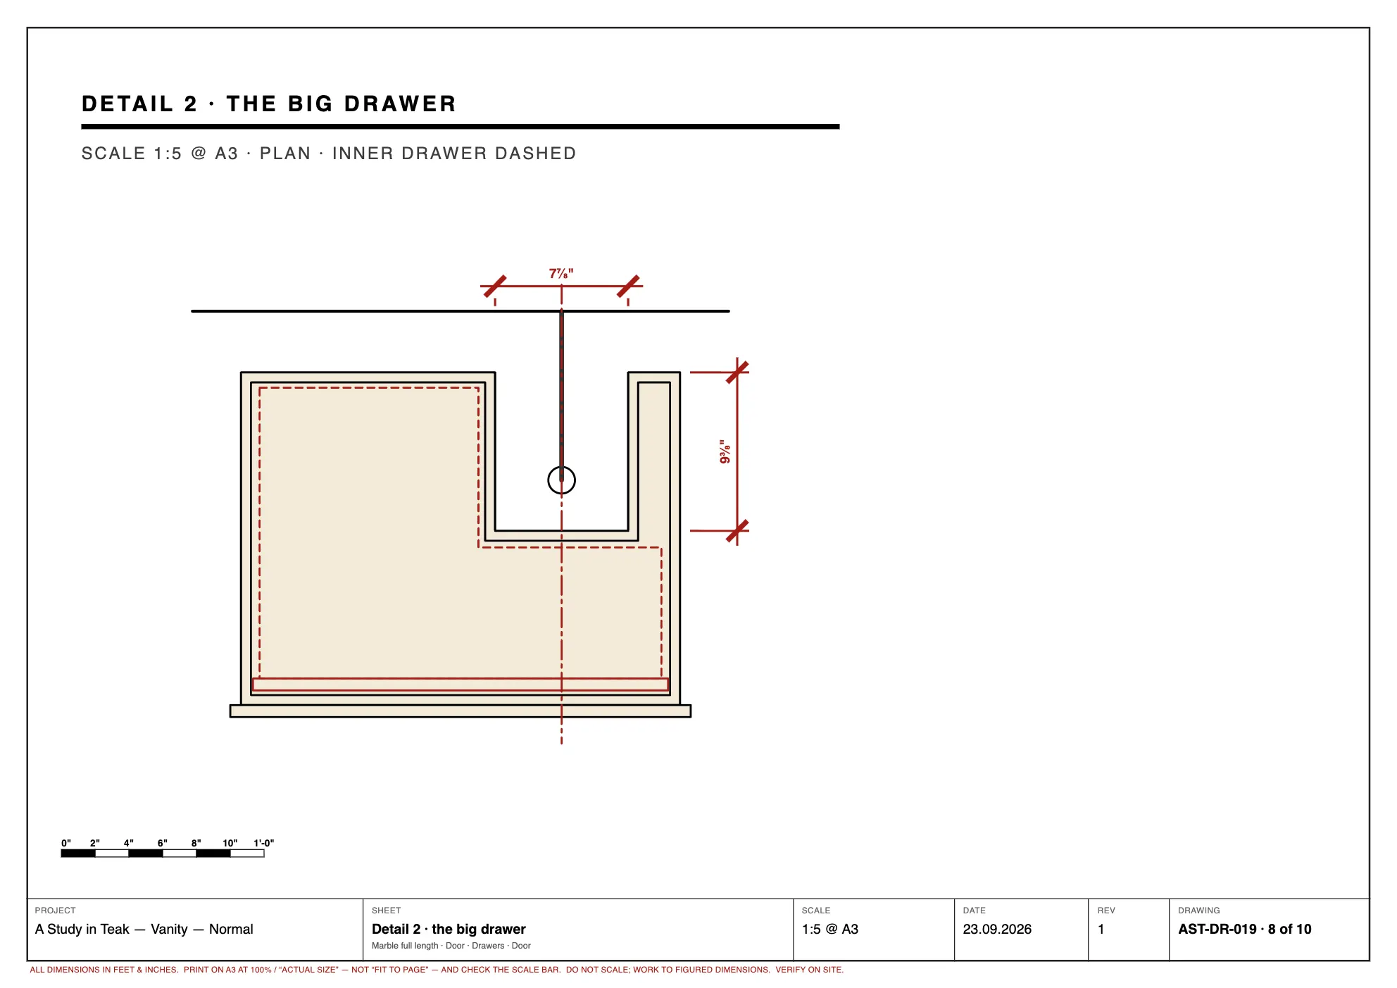
cad/print/vanity-08.webp
