sakshampan733-cloud/a-study-in-teak/cad/print/vanity-09.webp

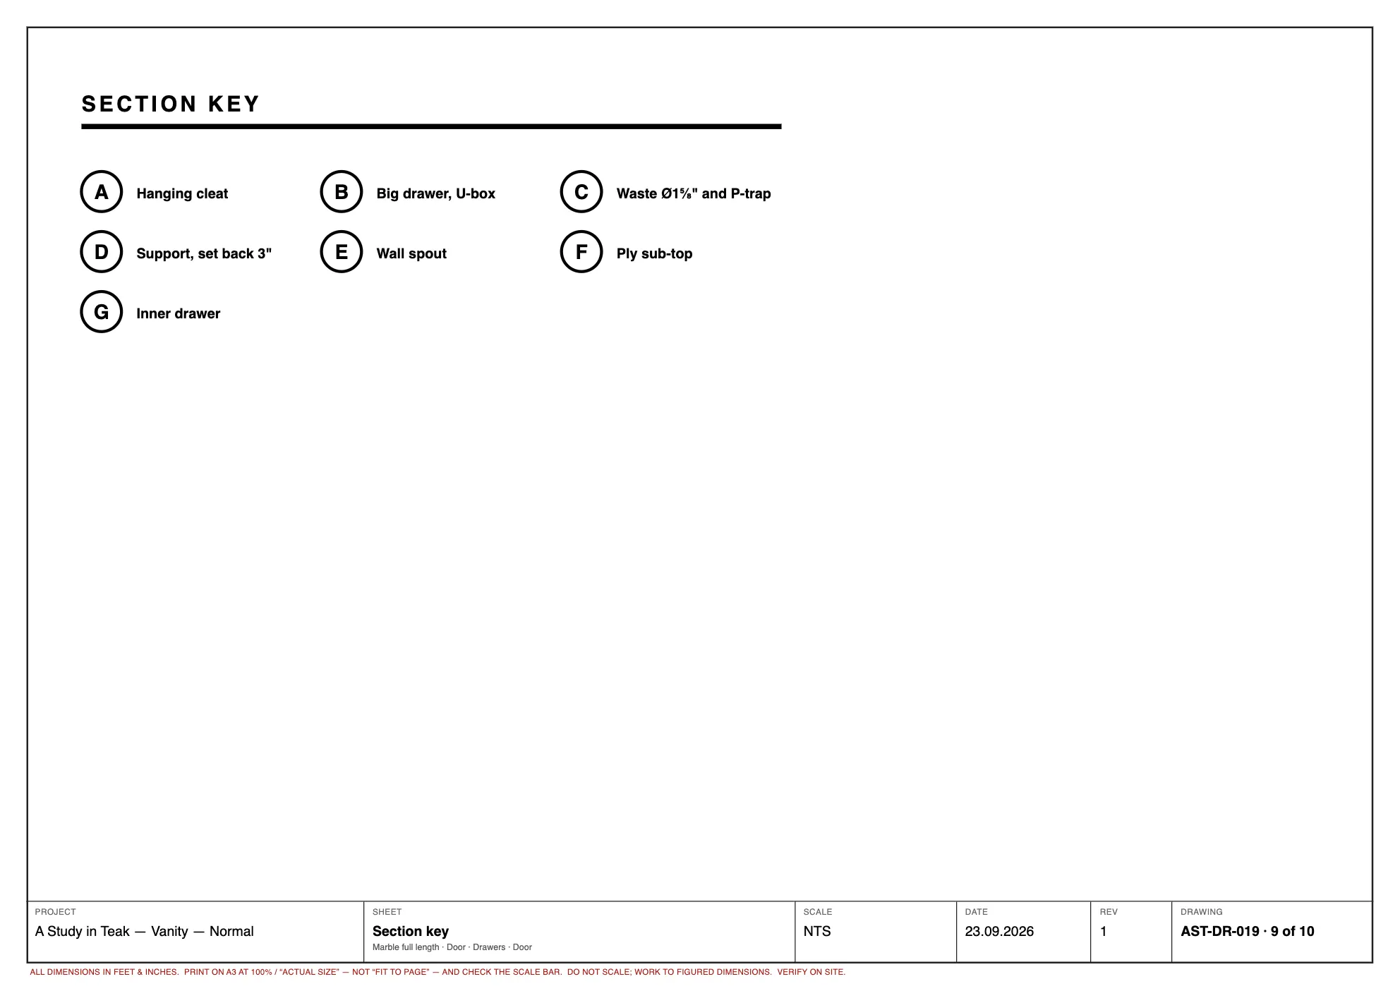
cad/print/vanity-09.webp
