sakshampan733-cloud/a-study-in-teak/cad/print/vanity-10.webp

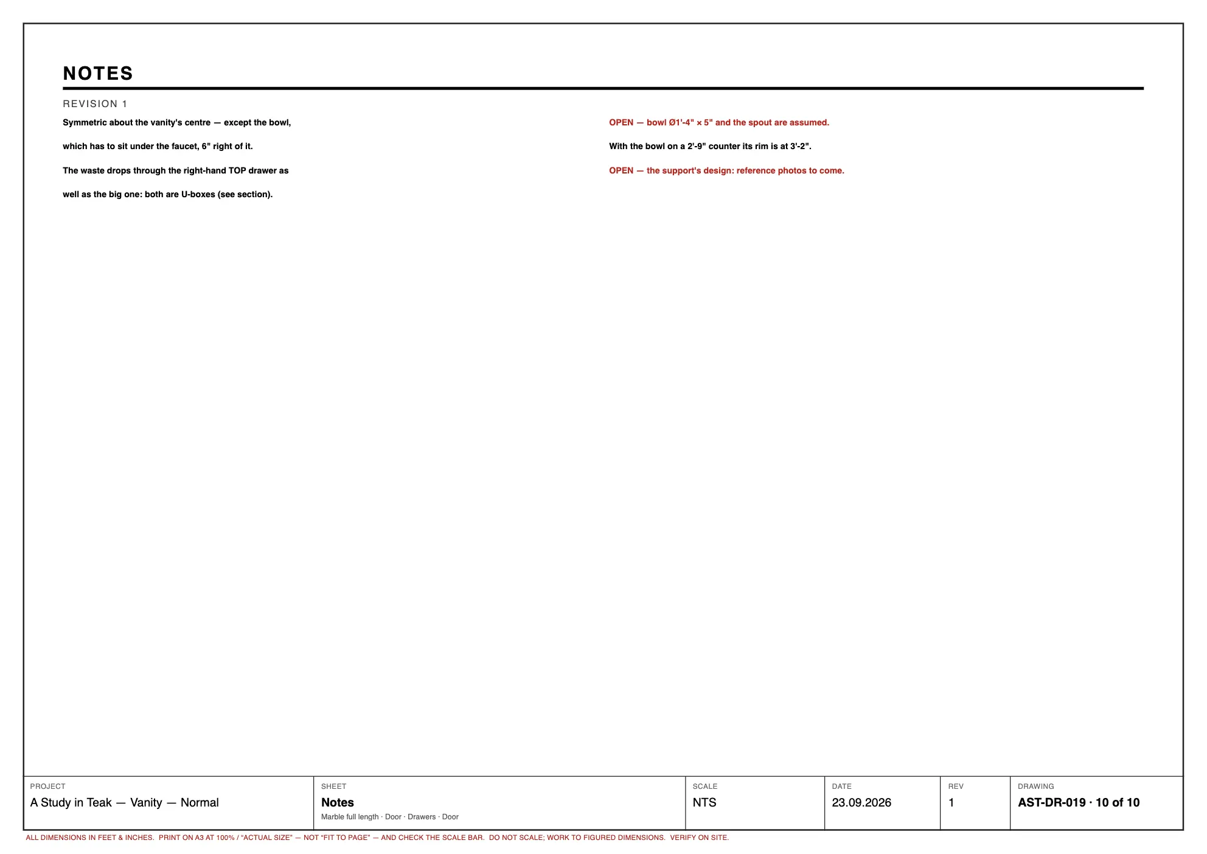
cad/print/vanity-10.webp
