sakshampan733-cloud/a-study-in-teak/cad/print/vanity-b-01.webp

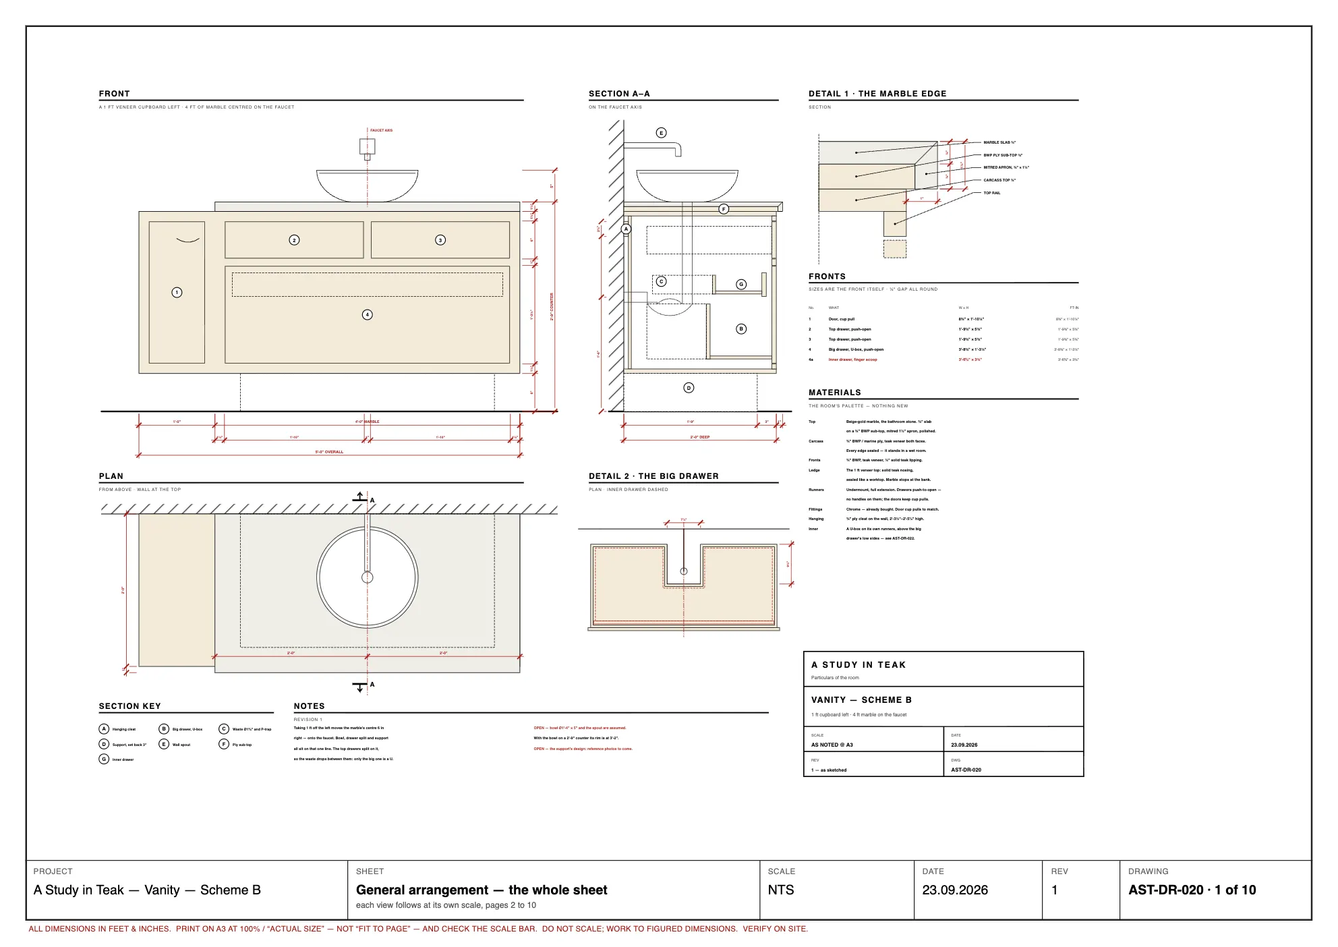
cad/print/vanity-b-01.webp
