sakshampan733-cloud/a-study-in-teak/cad/print/vanity-b-02.webp

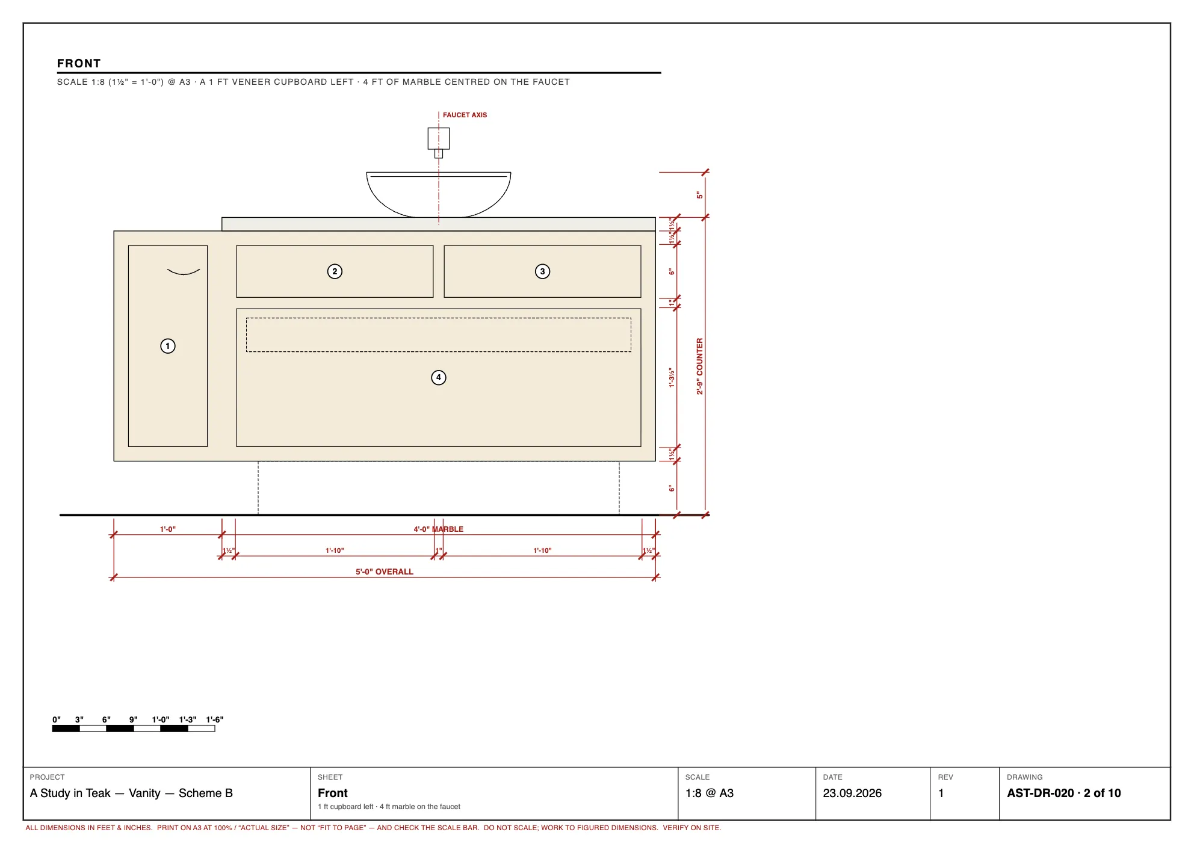
cad/print/vanity-b-02.webp
