sakshampan733-cloud/a-study-in-teak/cad/print/vanity-b-07.webp

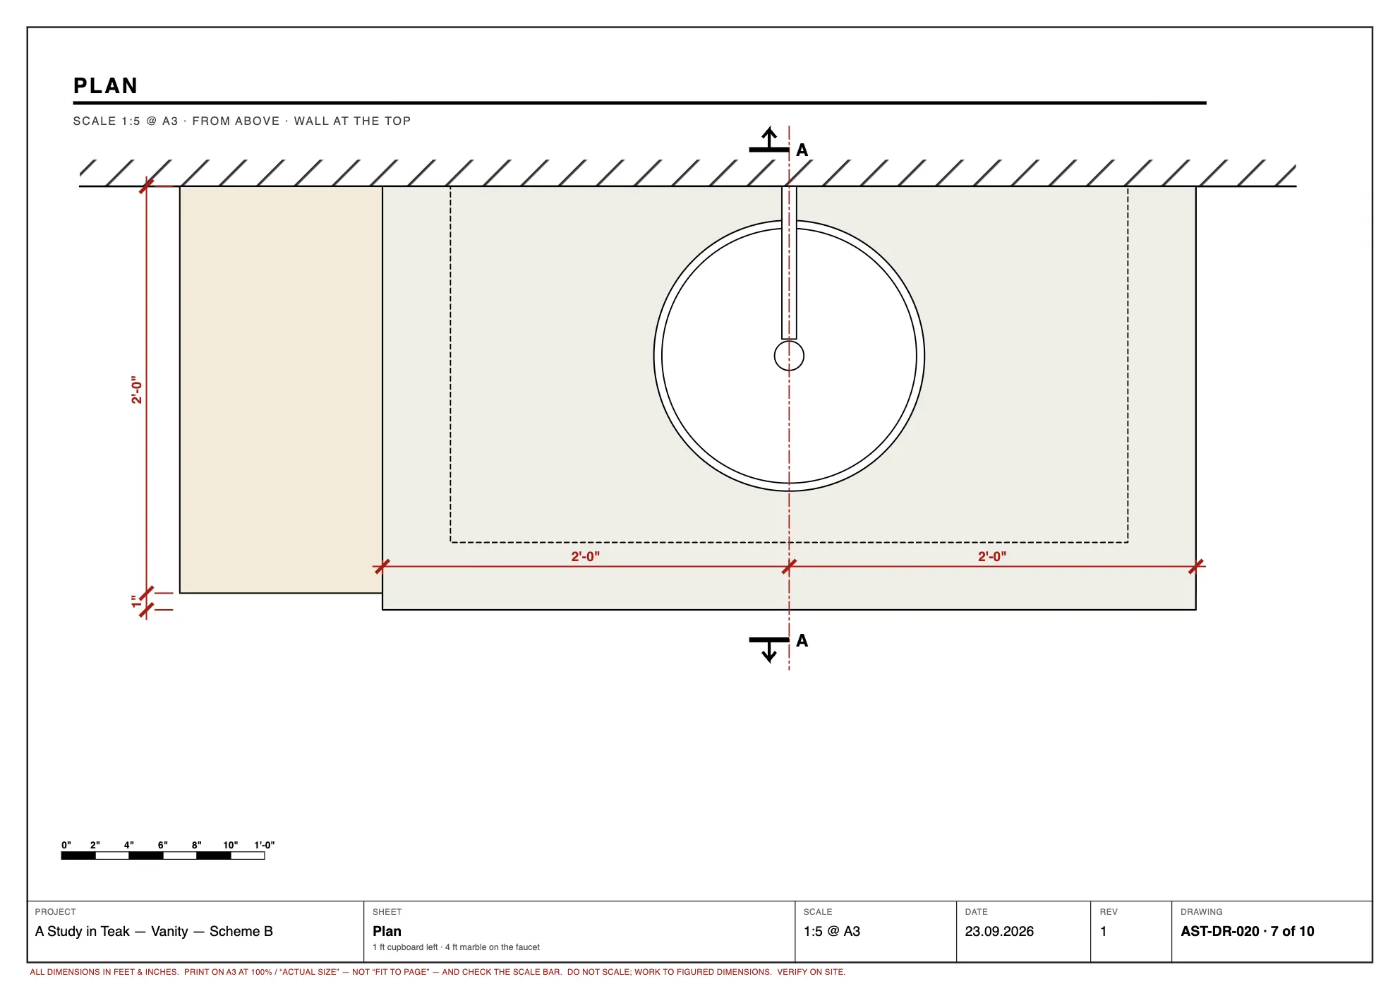
cad/print/vanity-b-07.webp
