sakshampan733-cloud/a-study-in-teak/cad/print/vanity-b-08.webp

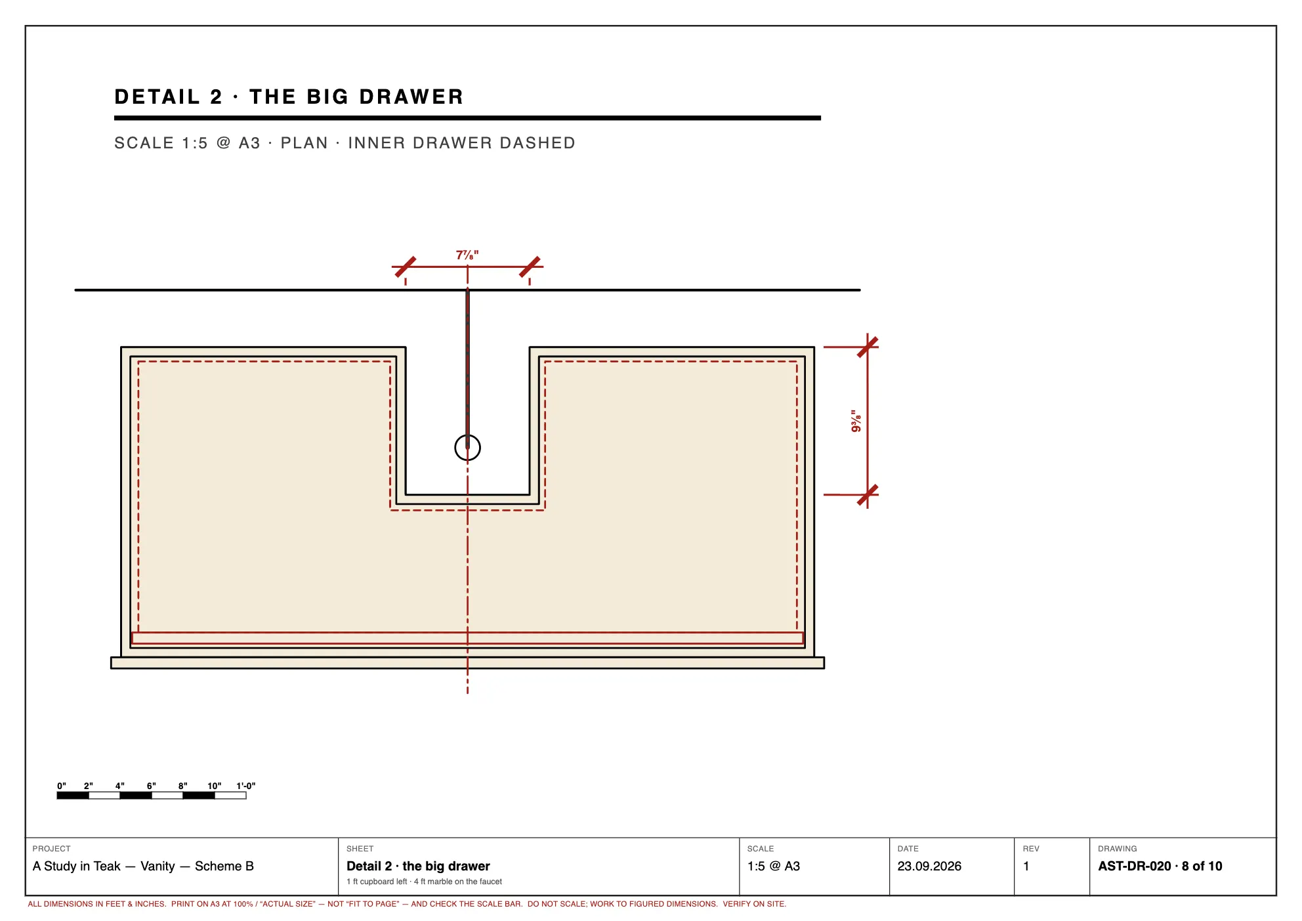
cad/print/vanity-b-08.webp
