sakshampan733-cloud/a-study-in-teak/cad/print/vanity-c-04.webp

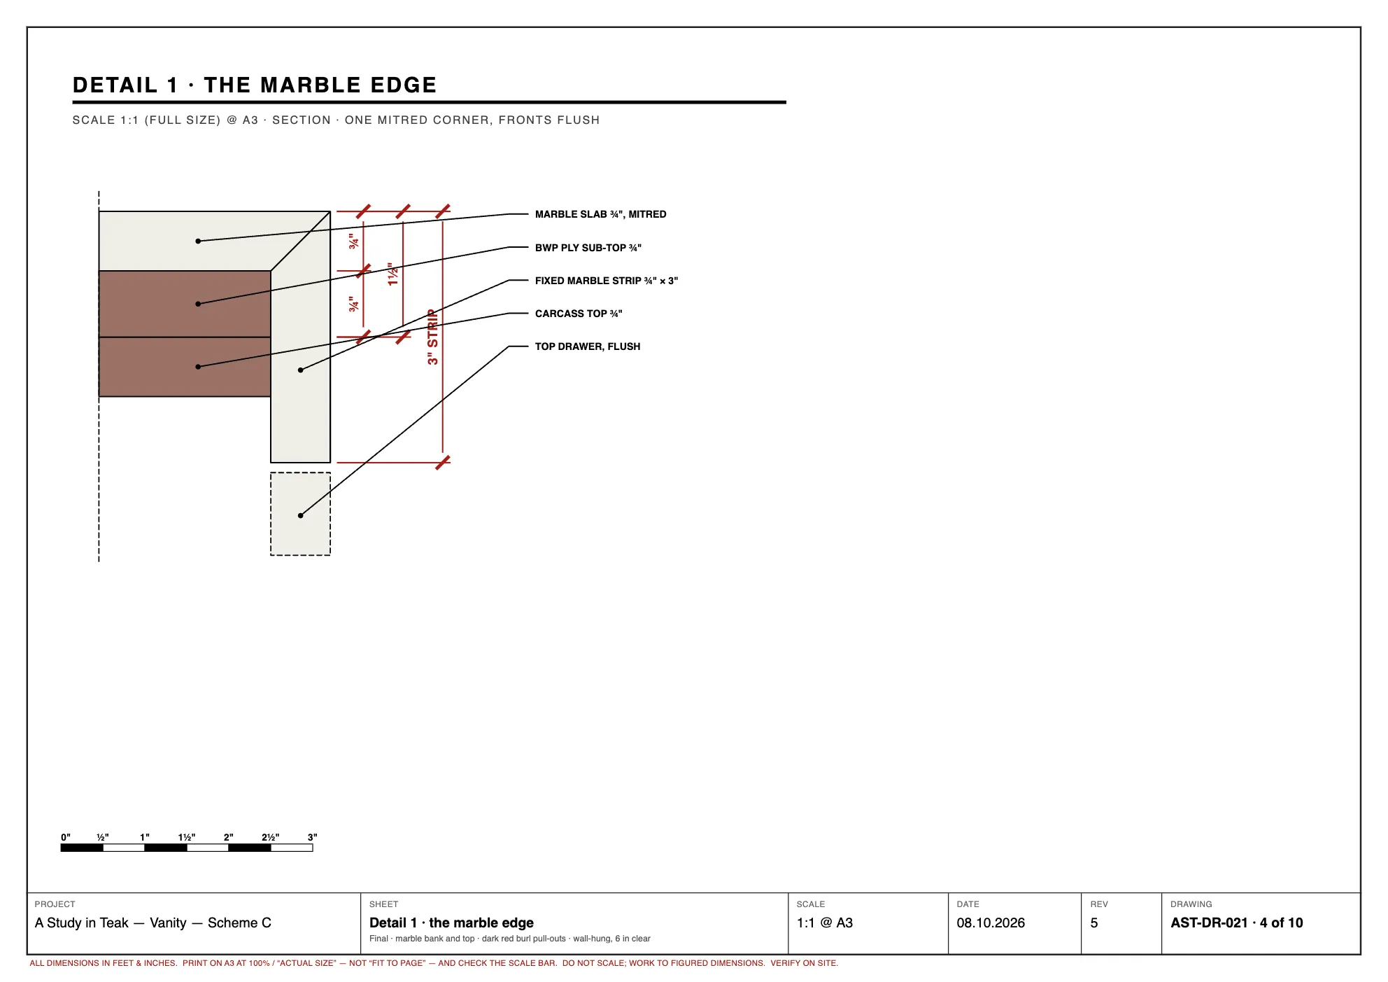
cad/print/vanity-c-04.webp
