sakshampan733-cloud/a-study-in-teak/cad/print/vanity-c-06.webp

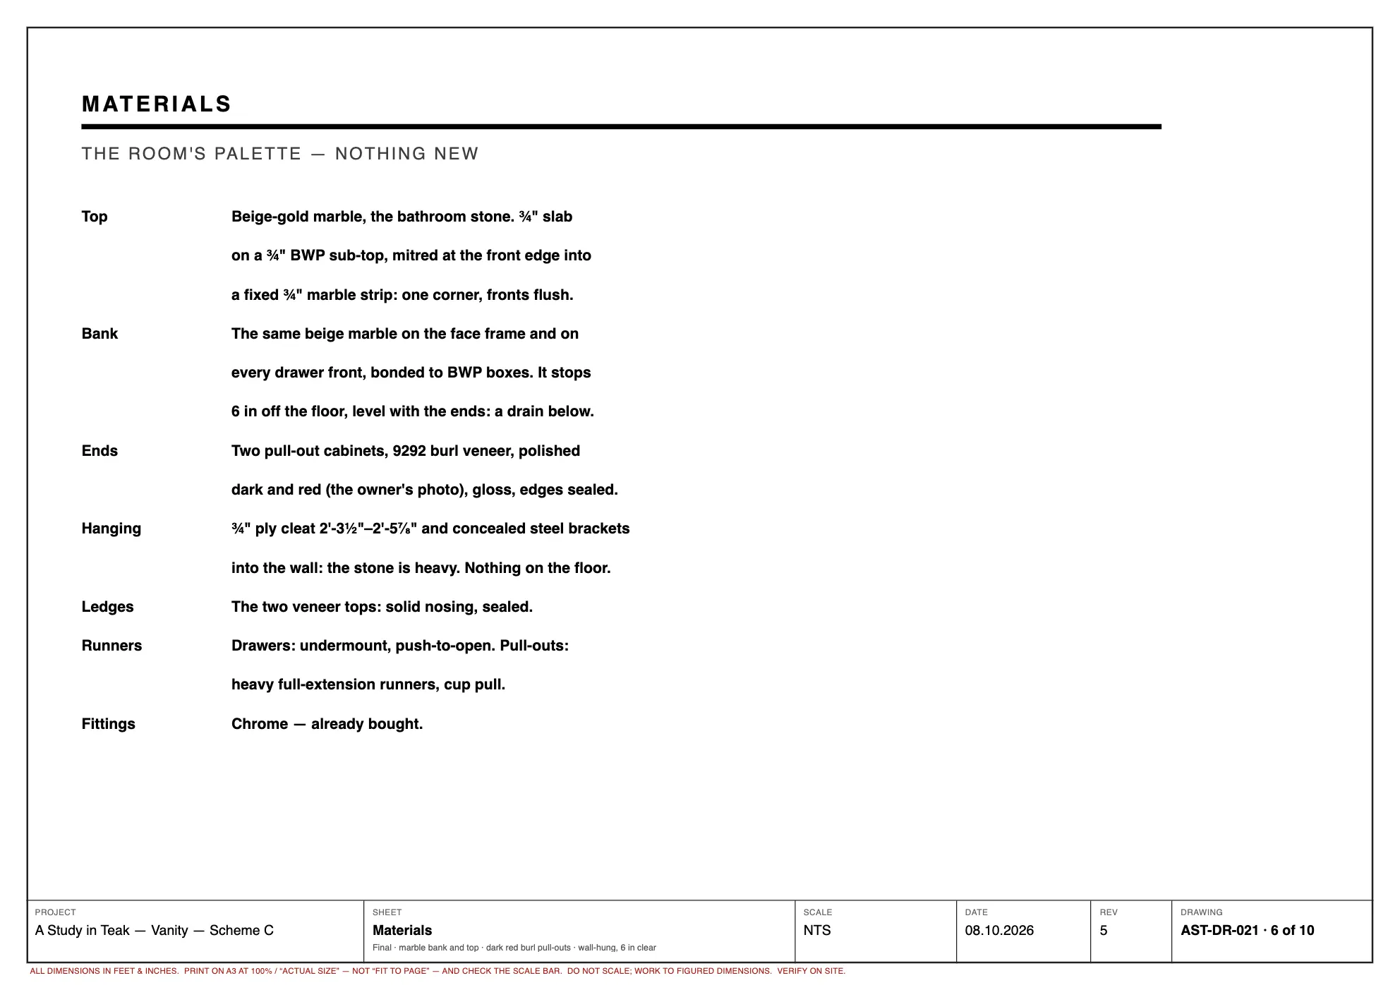
cad/print/vanity-c-06.webp
