sakshampan733-cloud/a-study-in-teak/cad/print/wardrobe-interiors-01.webp

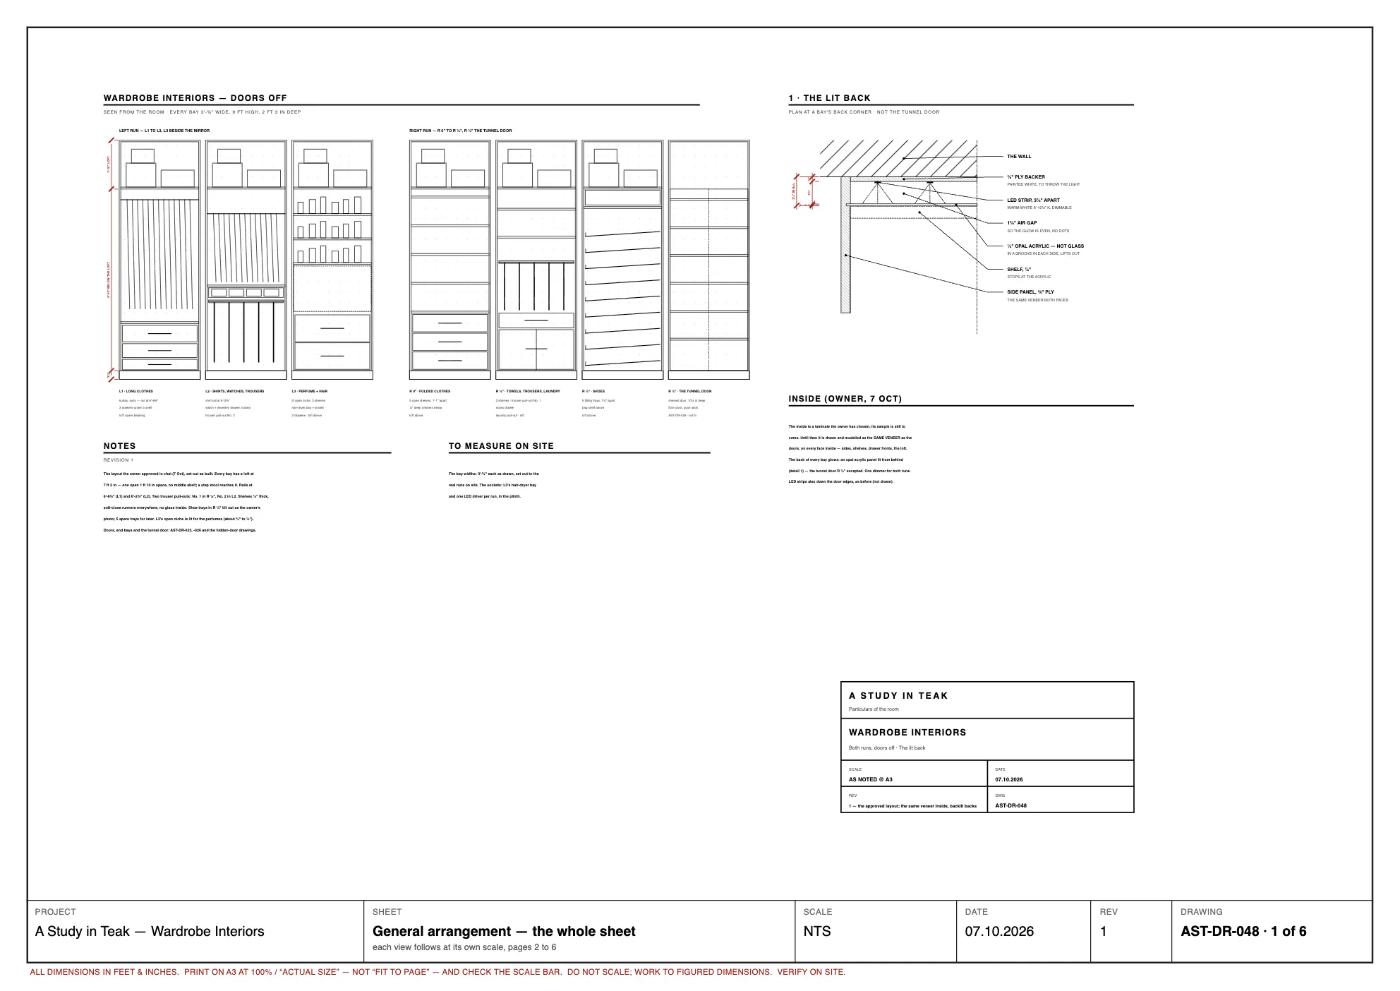
cad/print/wardrobe-interiors-01.webp
