sakshampan733-cloud/a-study-in-teak/cad/print/wardrobe-interiors-02.webp

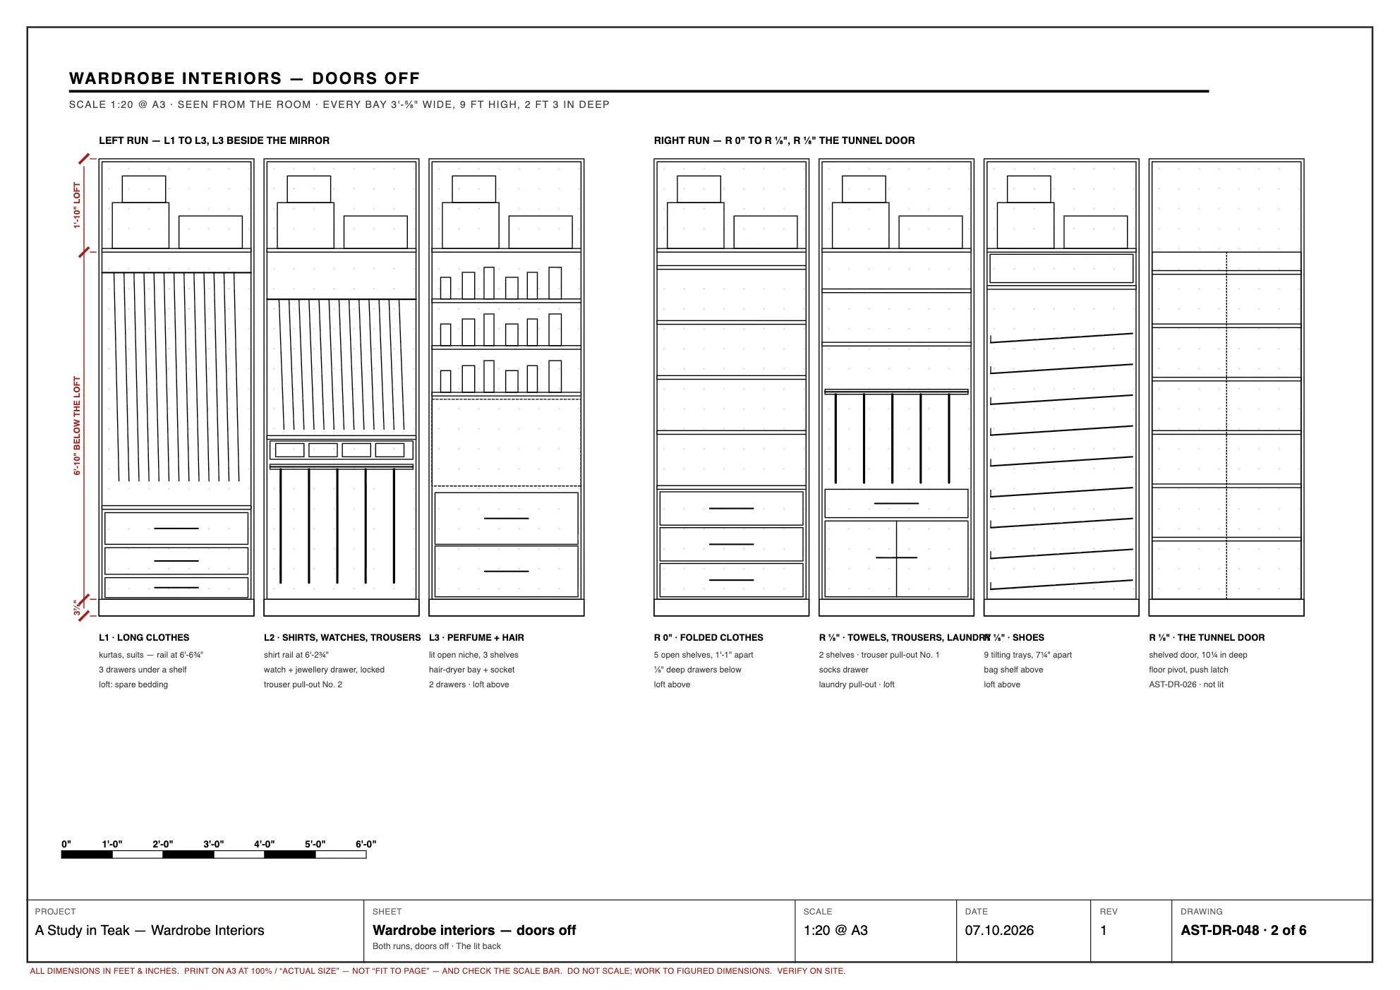
cad/print/wardrobe-interiors-02.webp
