sakshampan733-cloud/a-study-in-teak/cad/print/wardrobe-interiors-04.webp

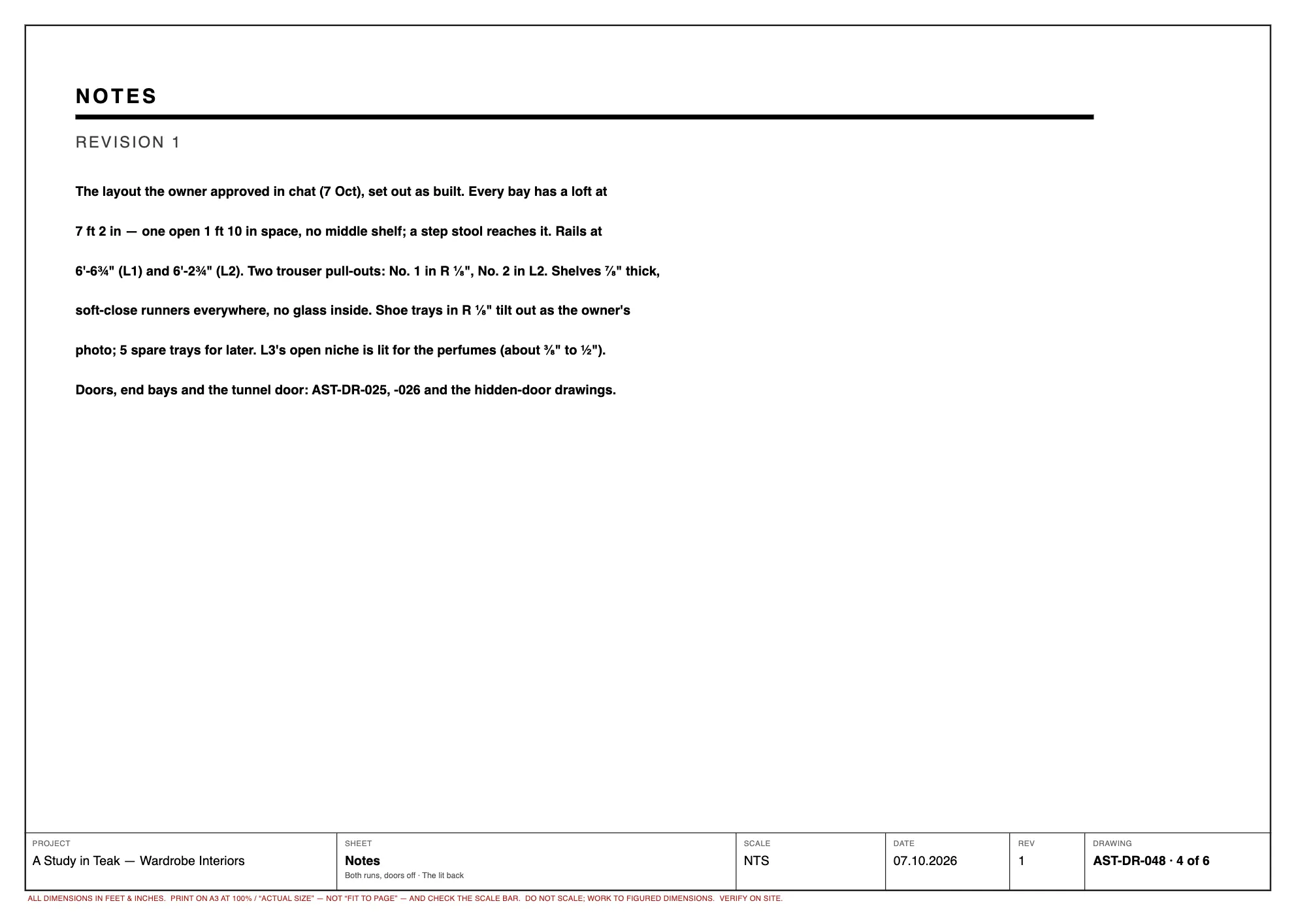
cad/print/wardrobe-interiors-04.webp
