sakshampan733-cloud/a-study-in-teak/cad/print/wardrobe-interiors-05.webp

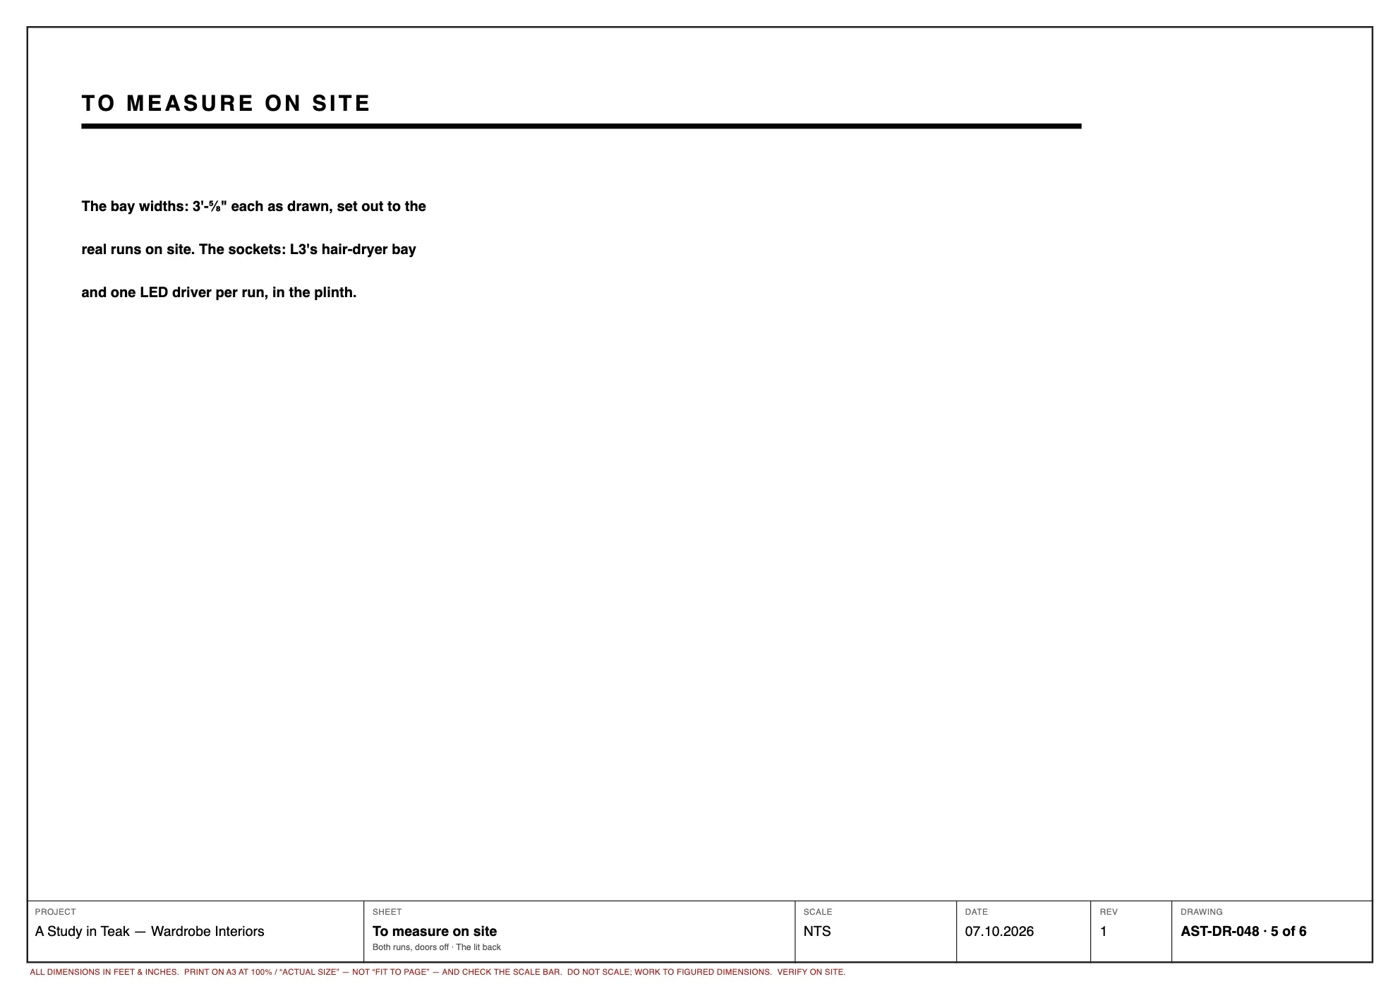
cad/print/wardrobe-interiors-05.webp
