sakshampan733-cloud/a-study-in-teak/cad/print/wardrobes-01.webp

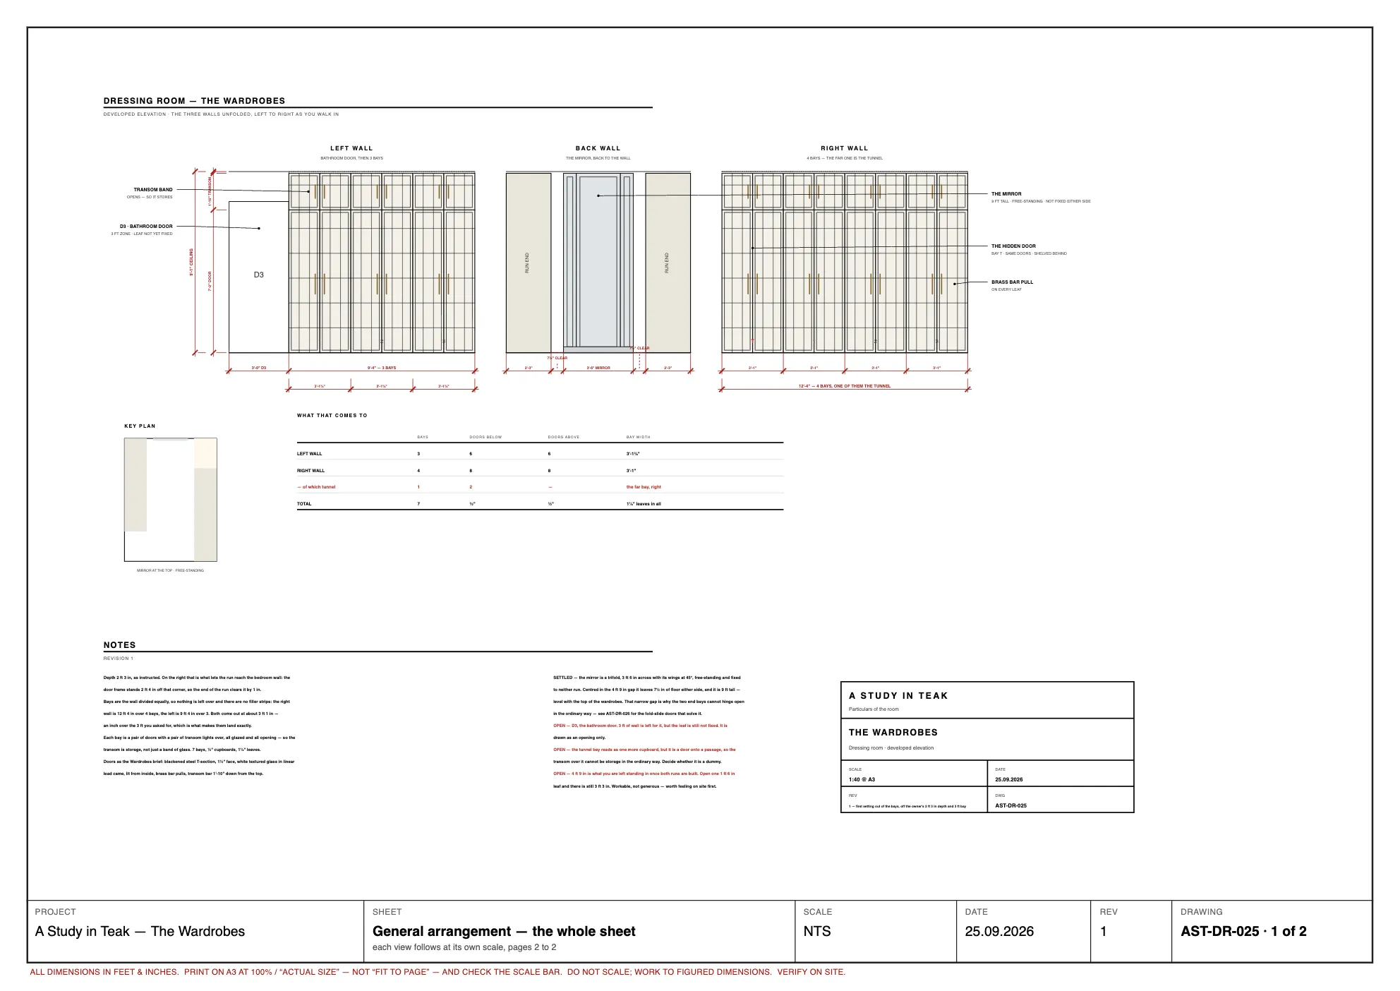
cad/print/wardrobes-01.webp
